smkent/pcb/dev/stackable/power-18650-holder/fab/jlcpcb/power-18650-holder-bom.csv

Comment | Designator | Footprint | LCSC
5K1 | R1,R2 | custom:R_0603_1608Metric_Pad0.98x0.95mm_HandSolder_simple | C25905
JST XH/PH | J1,J2 | custom:Conn_Combo_JST-1x02-XH_PH-THT-pad2gnd
Screw_Terminal_01x02 | J3,J4 | custom:Conn_Combo_TerminalBlock_P3.5-P5.08_1x02_pad2gnd
Battery_Cell | BT1 | custom:BAT-TH_18650-A5BJ001_large_vias
Red | LED1,LED2 | custom:LED_0603_1608Metric_Pad1.05x0.95mm_HandSolder_simple | C2286
