smkent/pcb/pcb/jigs/level-shifter/fab/jlcpcb/level-shifter-bom.csv

Comment | Designator | Footprint | LCSC
Pin headers | J1,J2 | custom:PinHeader_1x06_P2.54mm_Vertical_simple_pad1gnd
2N7002DW | Q1,Q2 | custom:SOT-363_SC-70-6_simple | C5190214
100R | RN3 | Resistor_SMD:R_Array_Convex_4x0603
10K | RN1,RN2 | Resistor_SMD:R_Array_Convex_4x0603
22u | C1,C2 | custom:C_0603_1608Metric_Pad1.08x0.95mm_HandSolder
