smkent/pcb/pcb/jigs/neopixel-micro/fab/jlcpcb/neopixel-micro-bom.csv

Comment | Designator | Footprint | LCSC
10u | C1,C2 | custom:C_0603_1608Metric_Pad1.08x0.95mm_HandSolder
Conn_01x01 | J3,J4 | custom:PinHeader_1x01_P2.54mm_simple
WS2812B-2020 | LED1,LED2,LED3,LED4,LED5,LED6,LED7,LED8 | lcsc:LED-SMD_4P-L2.0-W2.0-BR-1
WS2812B | D1,D2 | custom:LED_WS2812B_PLCC4_5.0x5.0mm_P3.2mm_simple_small_courtyard
Conn_01x02 | J1,J2 | custom:PinHeader_1x02_P2.54mm_Vertical_simple
100R | R1,R2 | Resistor_SMD:R_0603_1608Metric_Pad0.98x0.95mm_HandSolder
