smkent/pcb/pcb/power/microbuck/fab/jlcpcb/microbuck-bom.csv

Comment | Designator | Footprint | LCSC
10K | R0,R1,R3,R4,R6,R7 | Resistor_SMD:R_0603_1608Metric_Pad0.98x0.95mm_HandSolder
0u1 | C3,C6,C7,C10 | custom:C_0603_1608Metric_Pad1.08x0.95mm_HandSolder
TPS563200 | U1,U2 | custom:SOT-23-6_Handsoldering_simple
LED_Small | LED1,LED2 | custom:LED_0603_1608Metric_Pad1.05x0.95mm_HandSolder_simple
56K | R2,R5 | Resistor_SMD:R_0603_1608Metric_Pad0.98x0.95mm_HandSolder
22u | C8,C9,C11,C12 | custom:C_0603_1608Metric_Pad1.08x0.95mm_HandSolder
Pin headers | J1,J2 | custom:PinHeader_1x04_P2.54mm_Vertical_simple_pad3,4gnd
4u7 | L1,L2 | lcsc:IND-SMD_L2.5-W2.0_MHCHL2520
10u | C1,C2,C4,C5 | custom:C_0603_1608Metric_Pad1.08x0.95mm_HandSolder
