smkent/pcb/pcb/stackable3/esp-doorbell-dev/fab/esp-doorbell-dev-schematic.pdf

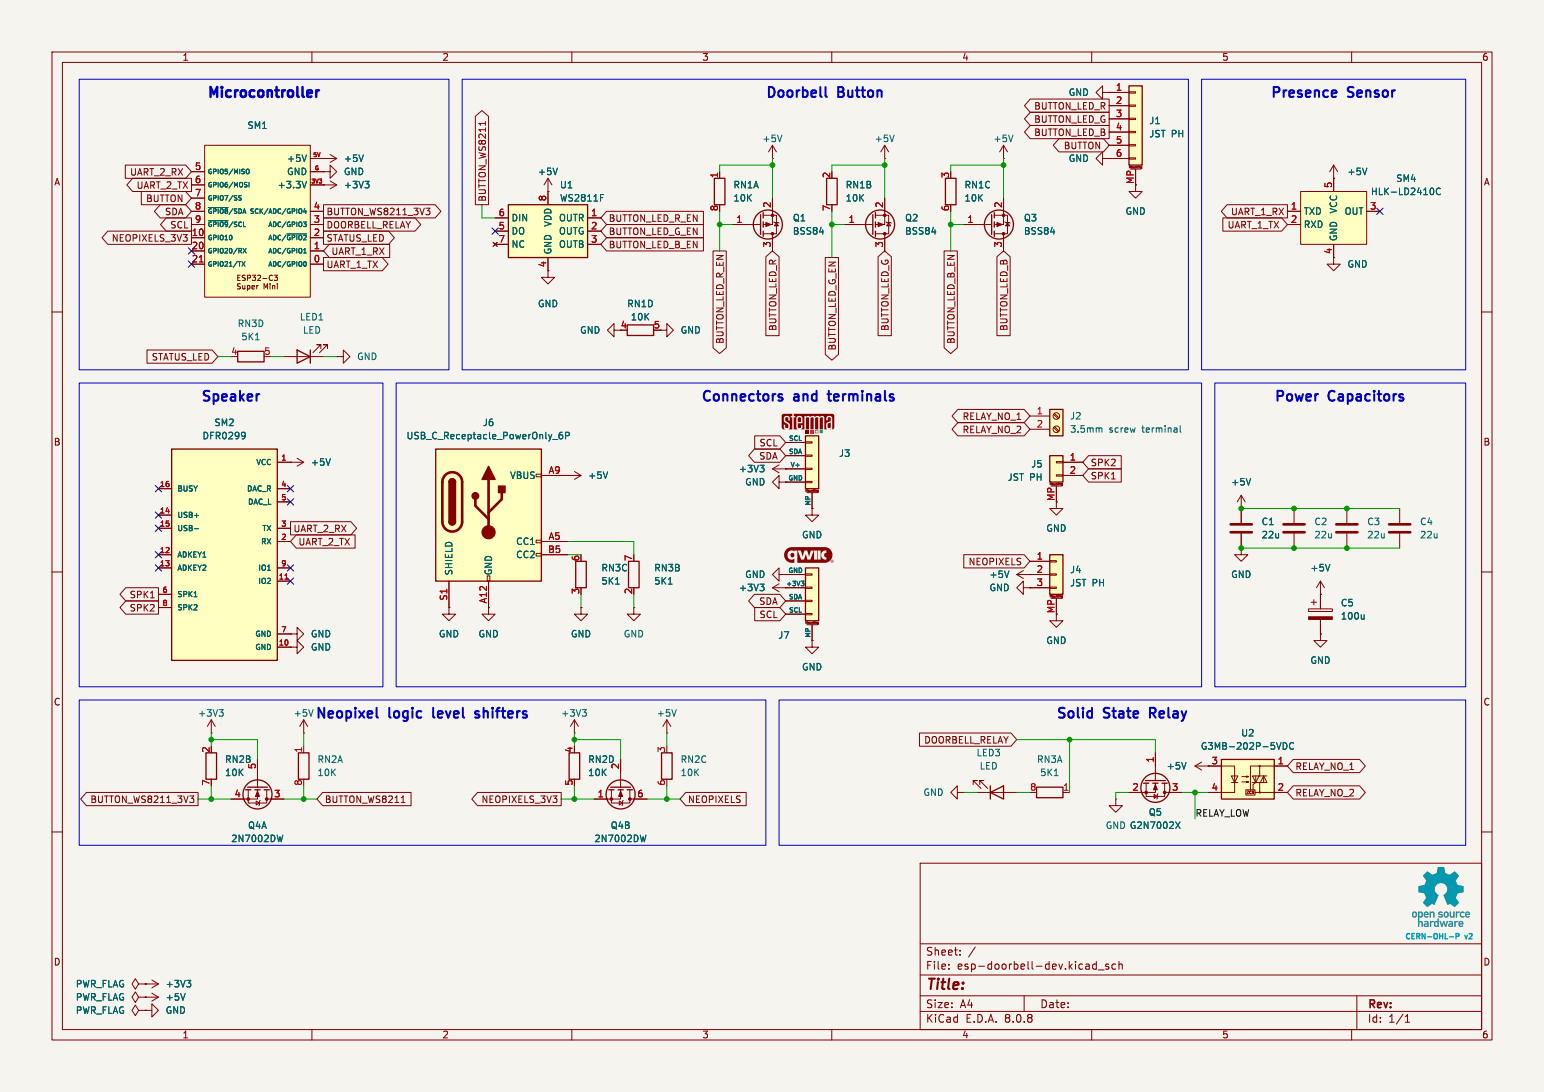
[picture p19: page 1]

4 DO 5 DIN 6 NC 7 VDD

2 3 Q2 BSS84 TXD 1 RXD 2 OUT 3 GND

3.5mm screw terminal Mounting SCL SDA
SCL SDA
+3V3 GND
