smkent/pcb/pcb/stackable3/power-selector-dev/fab/power-selector-dev-schematic.pdf

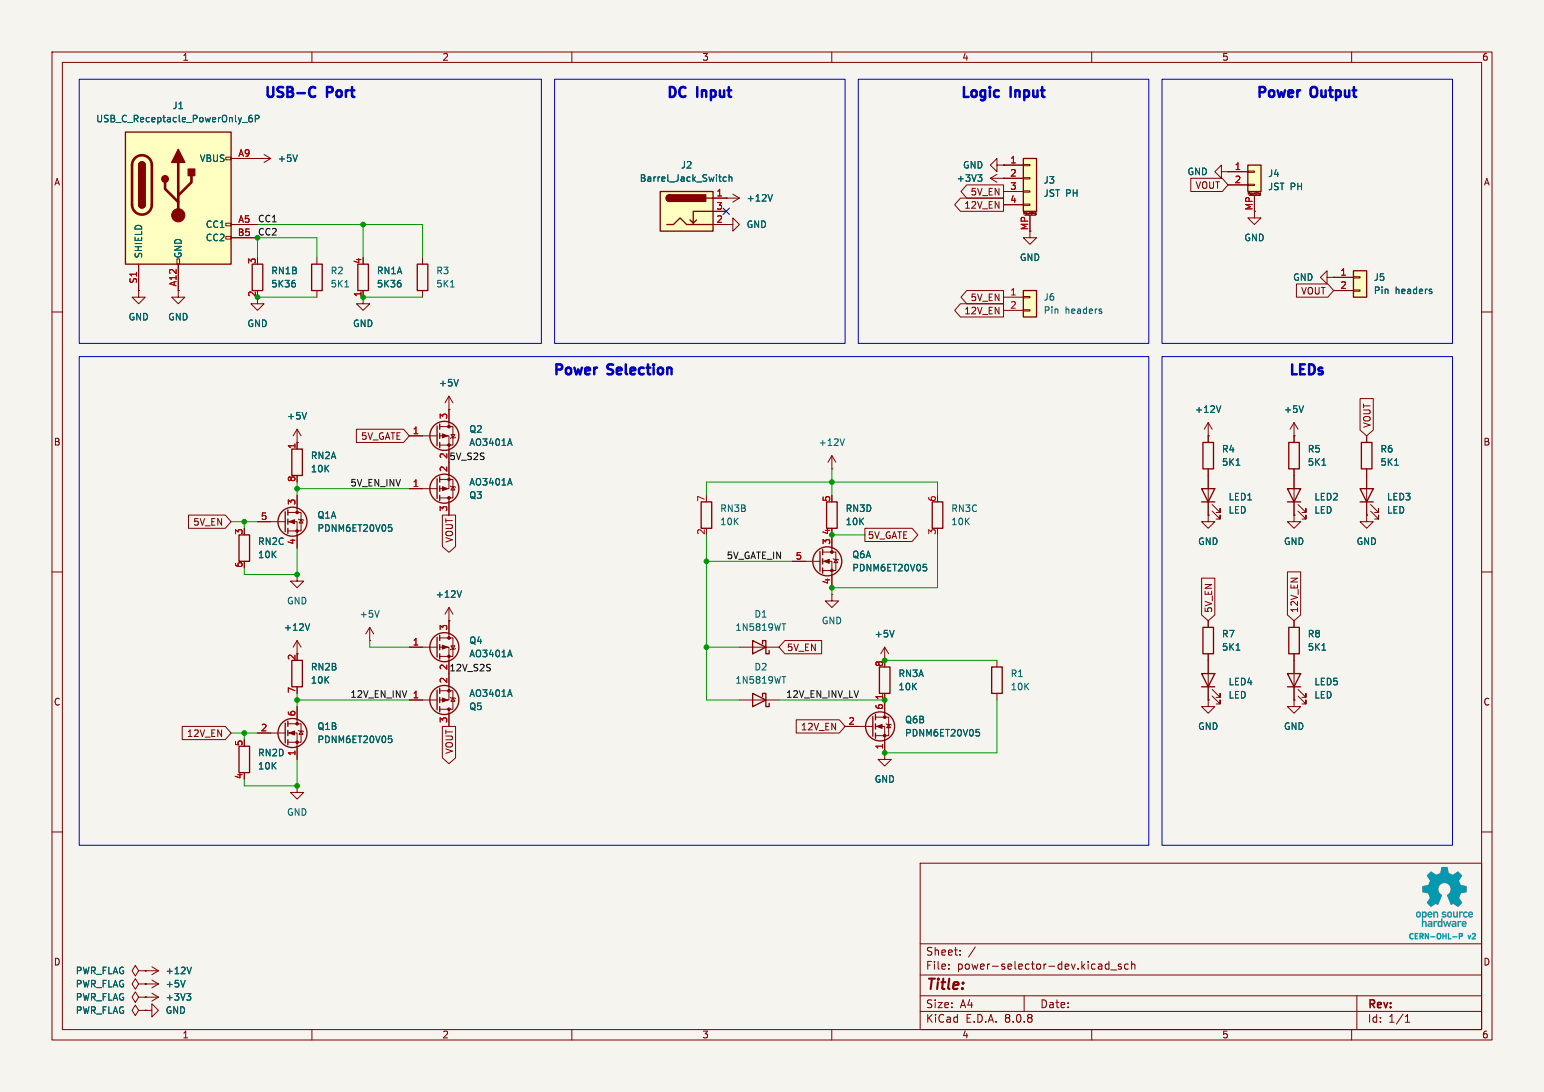
[picture p20: page 1]

Id: 1/1 Title: File: power-selector-dev.kicad_sch Sheet: /
