smkent/pcb/dev/misc/relay-module-5v/fab/relay-module-5v-schematic.pdf

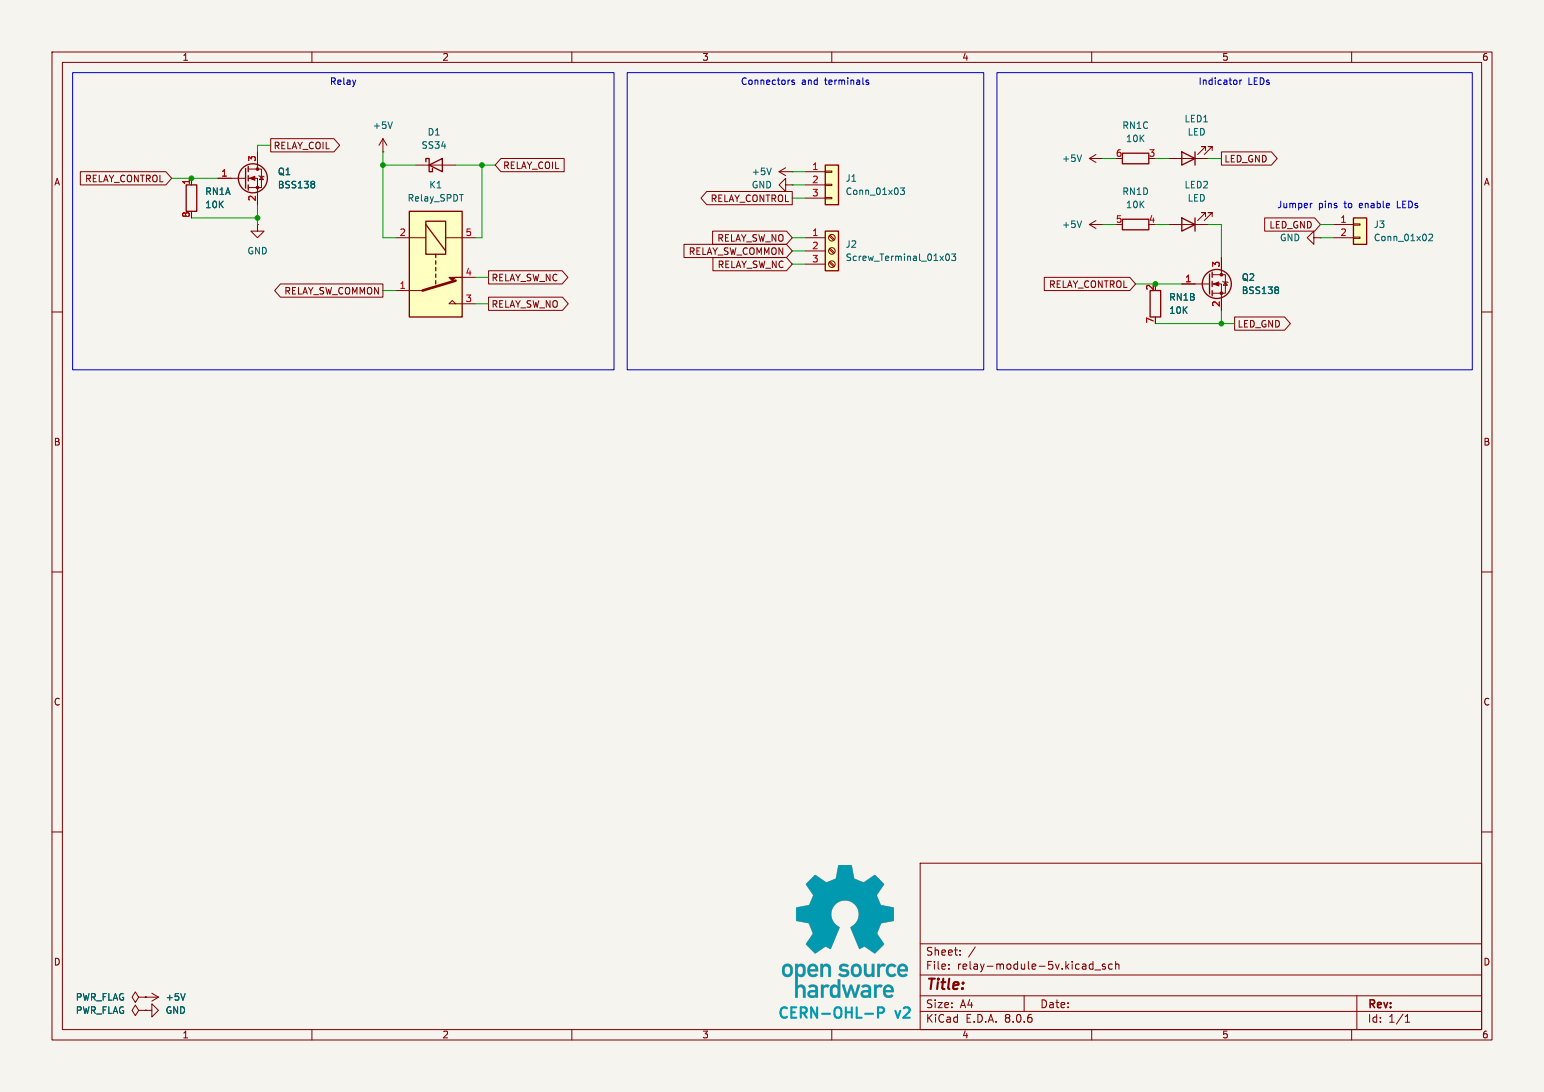
[picture p21: page 1]

Id: 1/1 Title: File: relay-module-5v.kicad_sch Sheet: /
