smkent/pcb/dev/power/battery-eta9740/fab/battery-eta9740-schematic.pdf

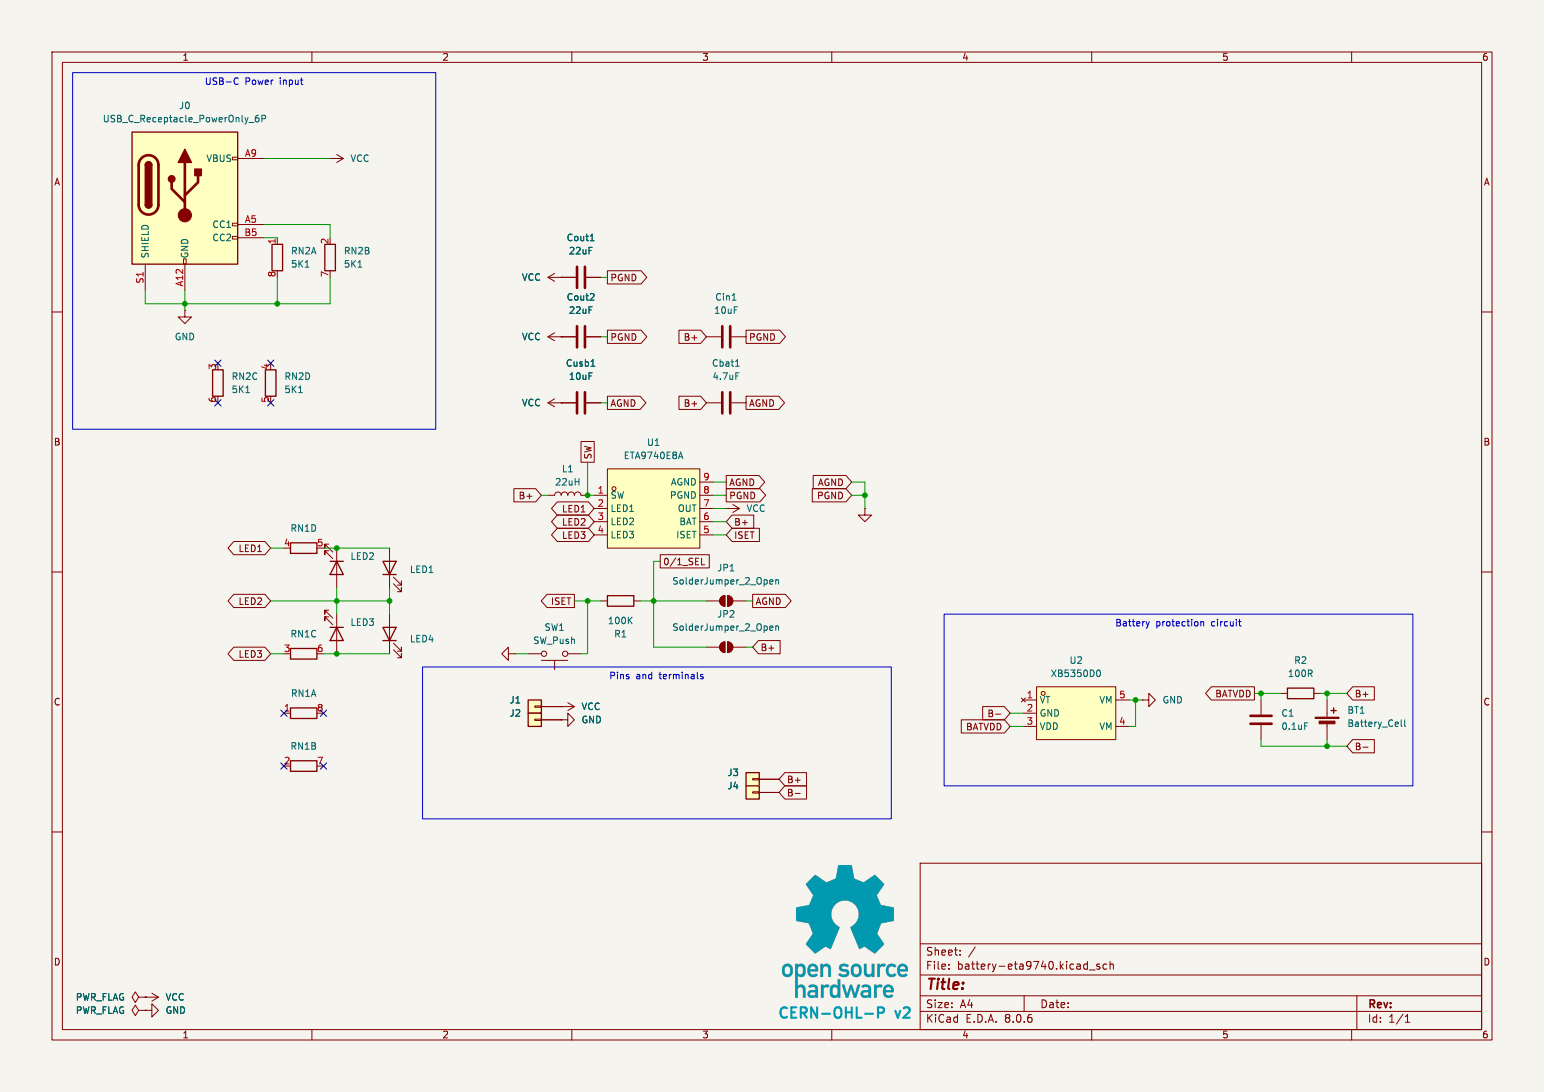
[picture p22: page 1]

Id: 1/1 Title: File: battery-eta9740.kicad_sch Sheet: / PWR_FLAG
