smkent/pcb/dev/power/battery-tp5400/fab/battery-tp5400-schematic.pdf

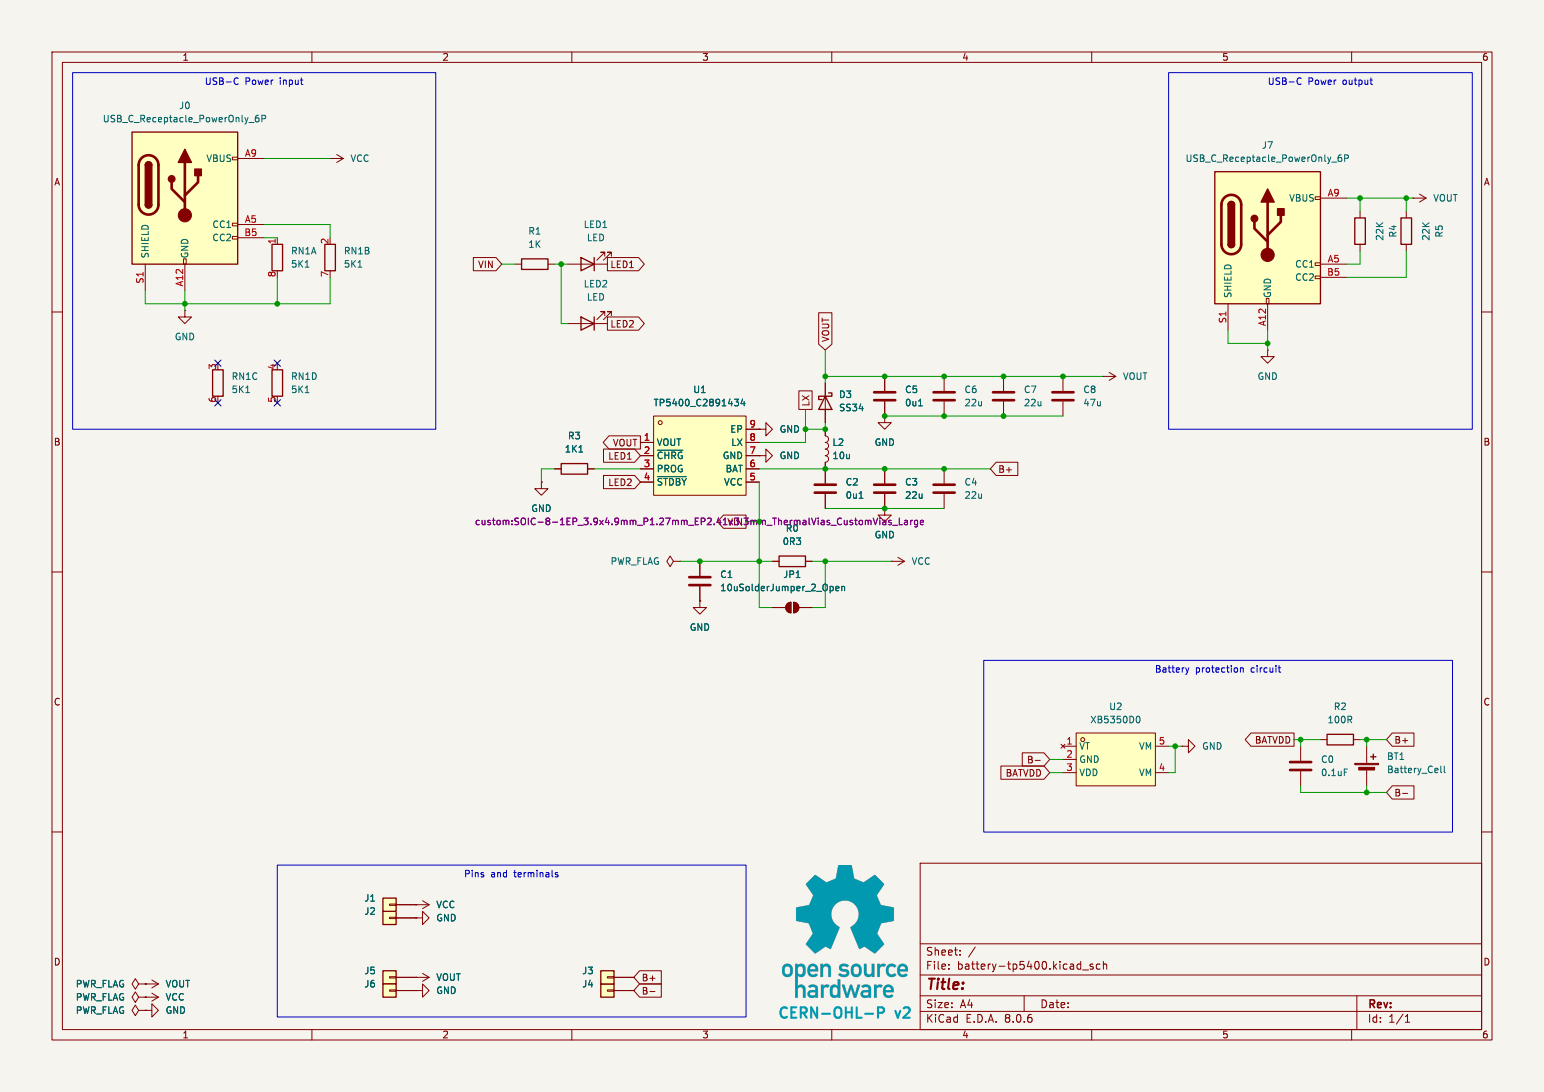
[picture p23: page 1]

Id: 1/1 Title: File: battery-tp5400.kicad_sch Sheet: /
