smkent/pcb/dev/power/boost-mt3608/fab/boost-mt3608-schematic.pdf

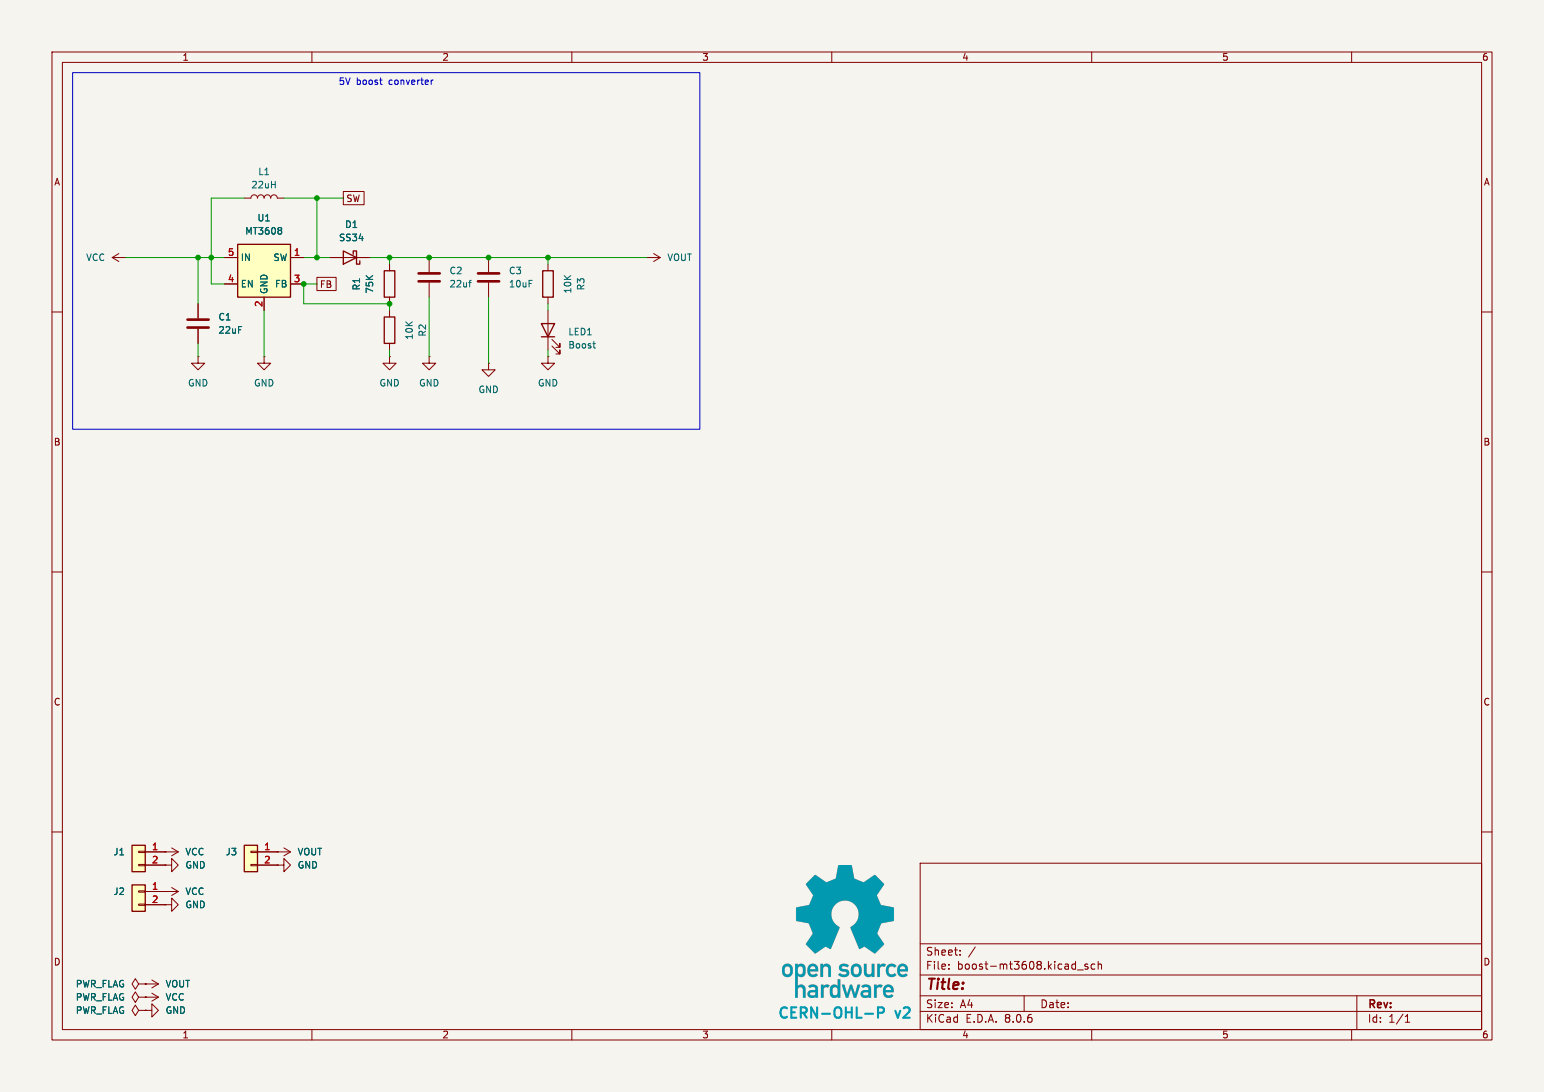
[picture p24: page 1]

Id: 1/1 Title: File: boost-mt3608.kicad_sch Sheet: / VOUT
