smkent/pcb/dev/power/buck-tps54202-compact/fab/buck-tps54202-compact-schematic.pdf

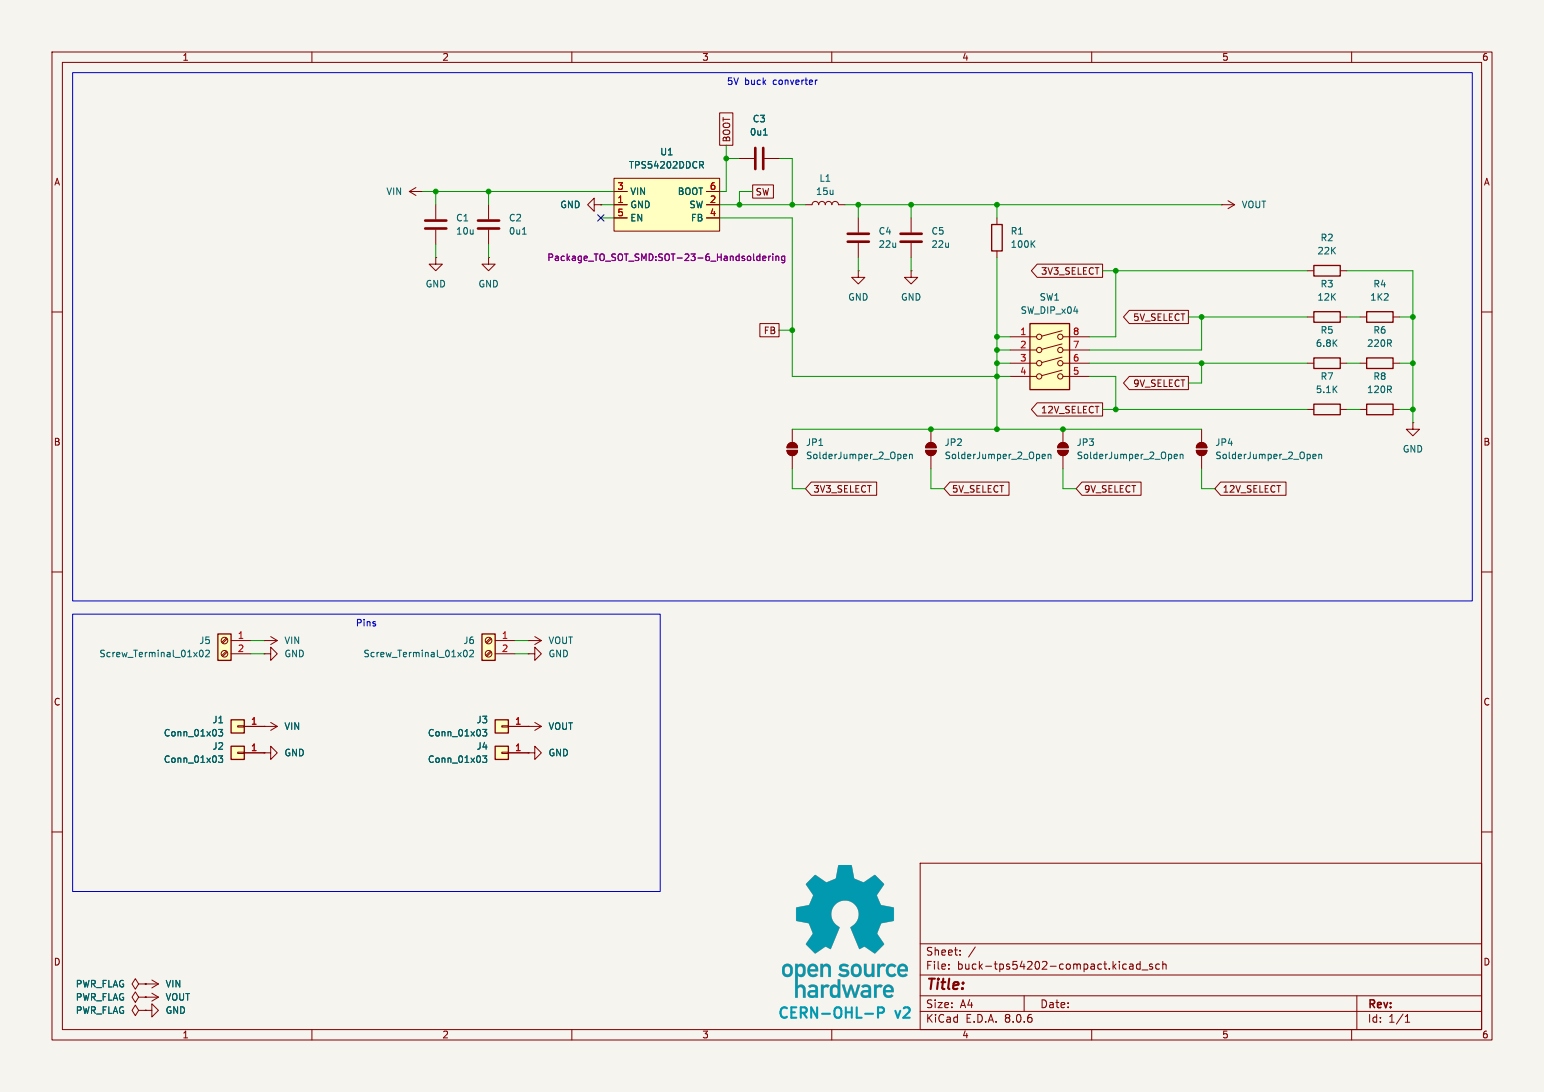
[picture p25: page 1]

Id: 1/1 Title: File: buck-tps54202-compact.kicad_sch Sheet: / GND
