smkent/pcb/dev/power/buck-tps54202/fab/buck-tps54202-schematic.pdf

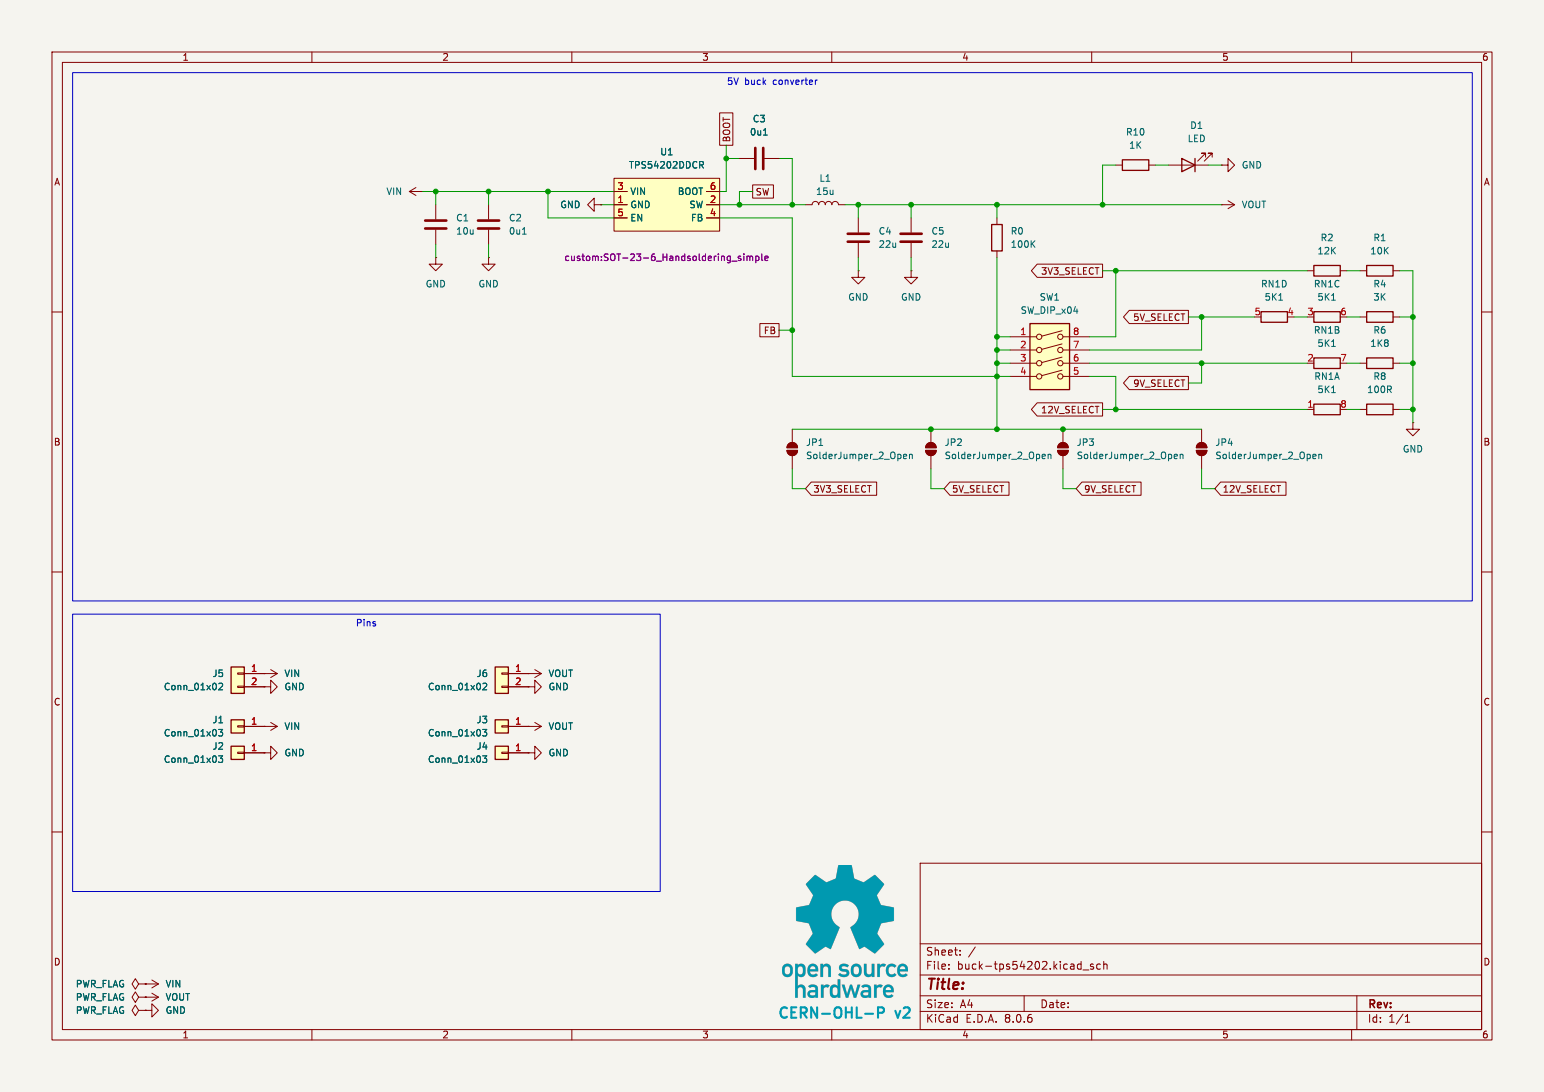
[picture p26: page 1]

Id: 1/1 Title: File: buck-tps54202.kicad_sch Sheet: /
