smkent/pcb/dev/power/ip5209-ups/fab/ip5209-ups-schematic.pdf

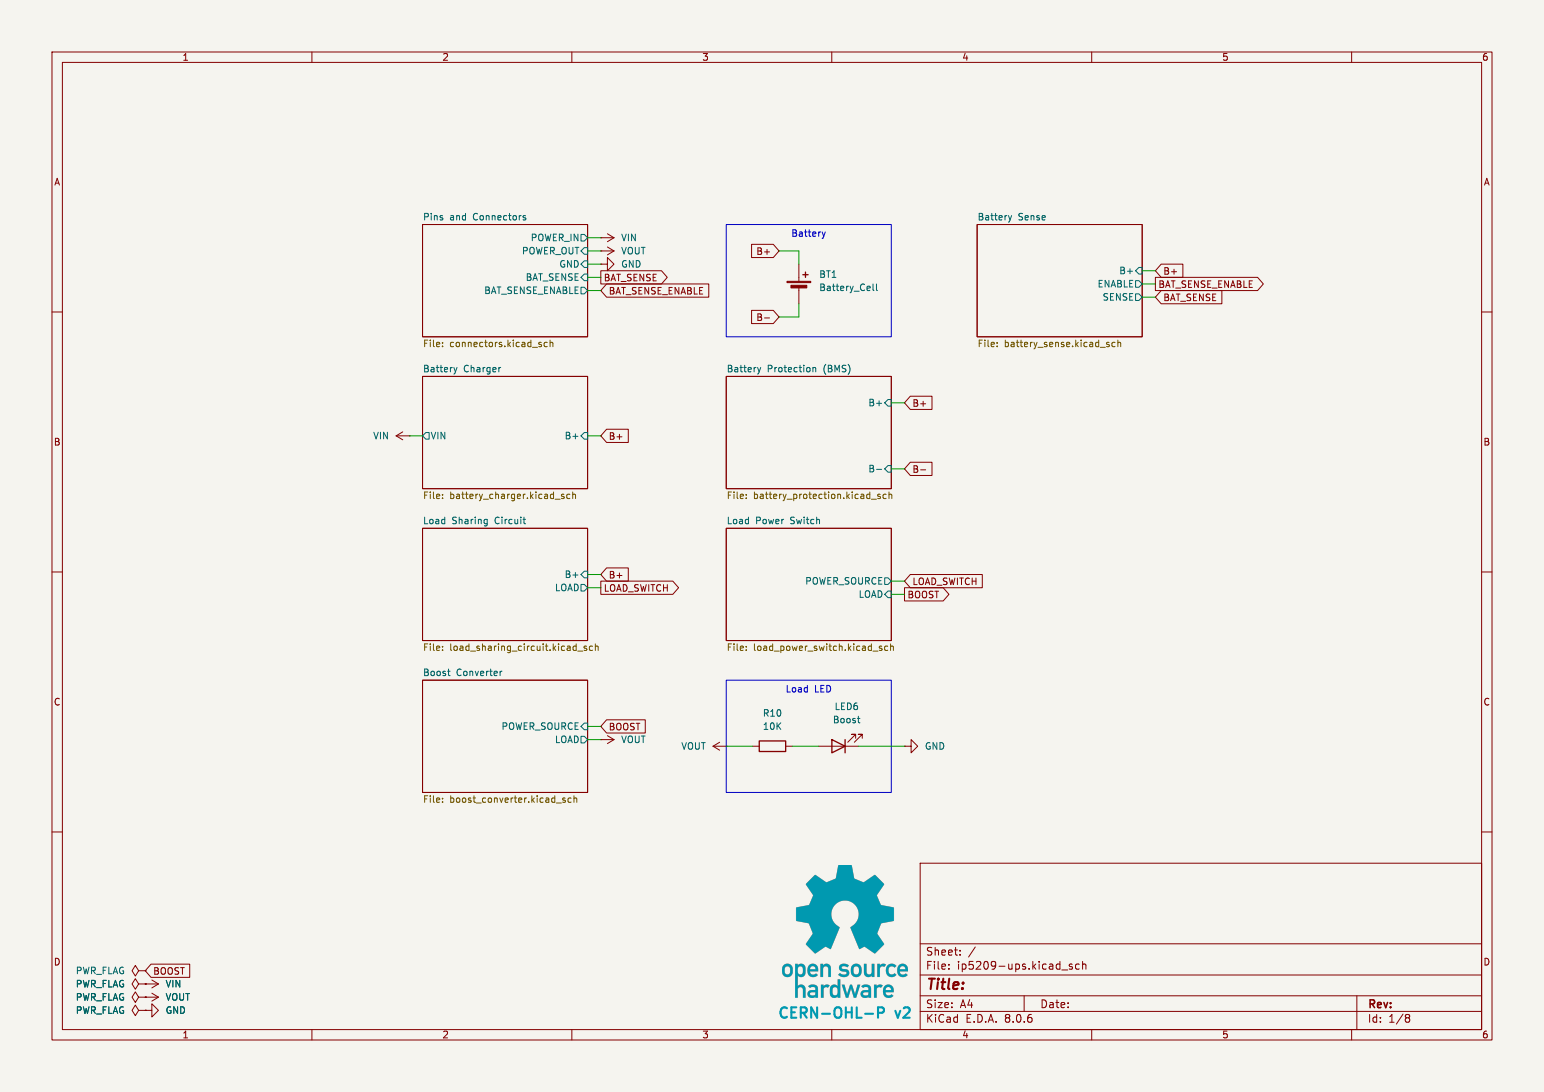
[picture p27: page 1]

Load Sharing Circuit File: load_sharing_circuit.kicad_sch

Id: 1/8 Title: File: ip5209-ups.kicad_sch Sheet: /

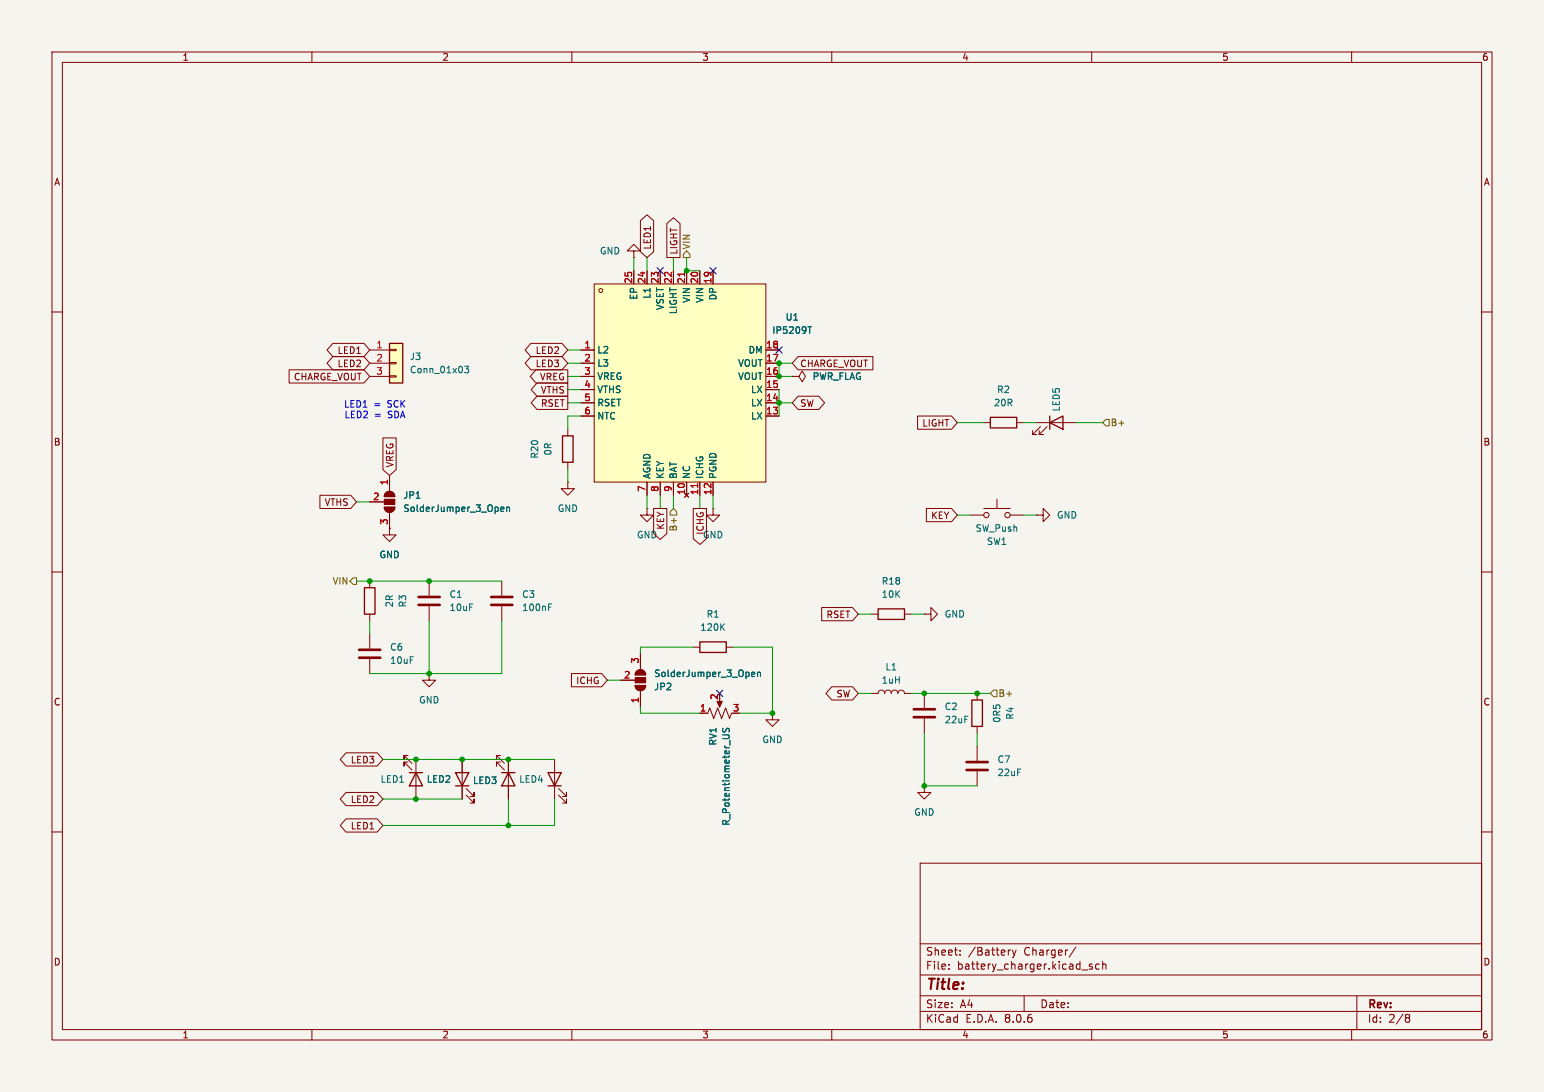
[picture p28: page 2]

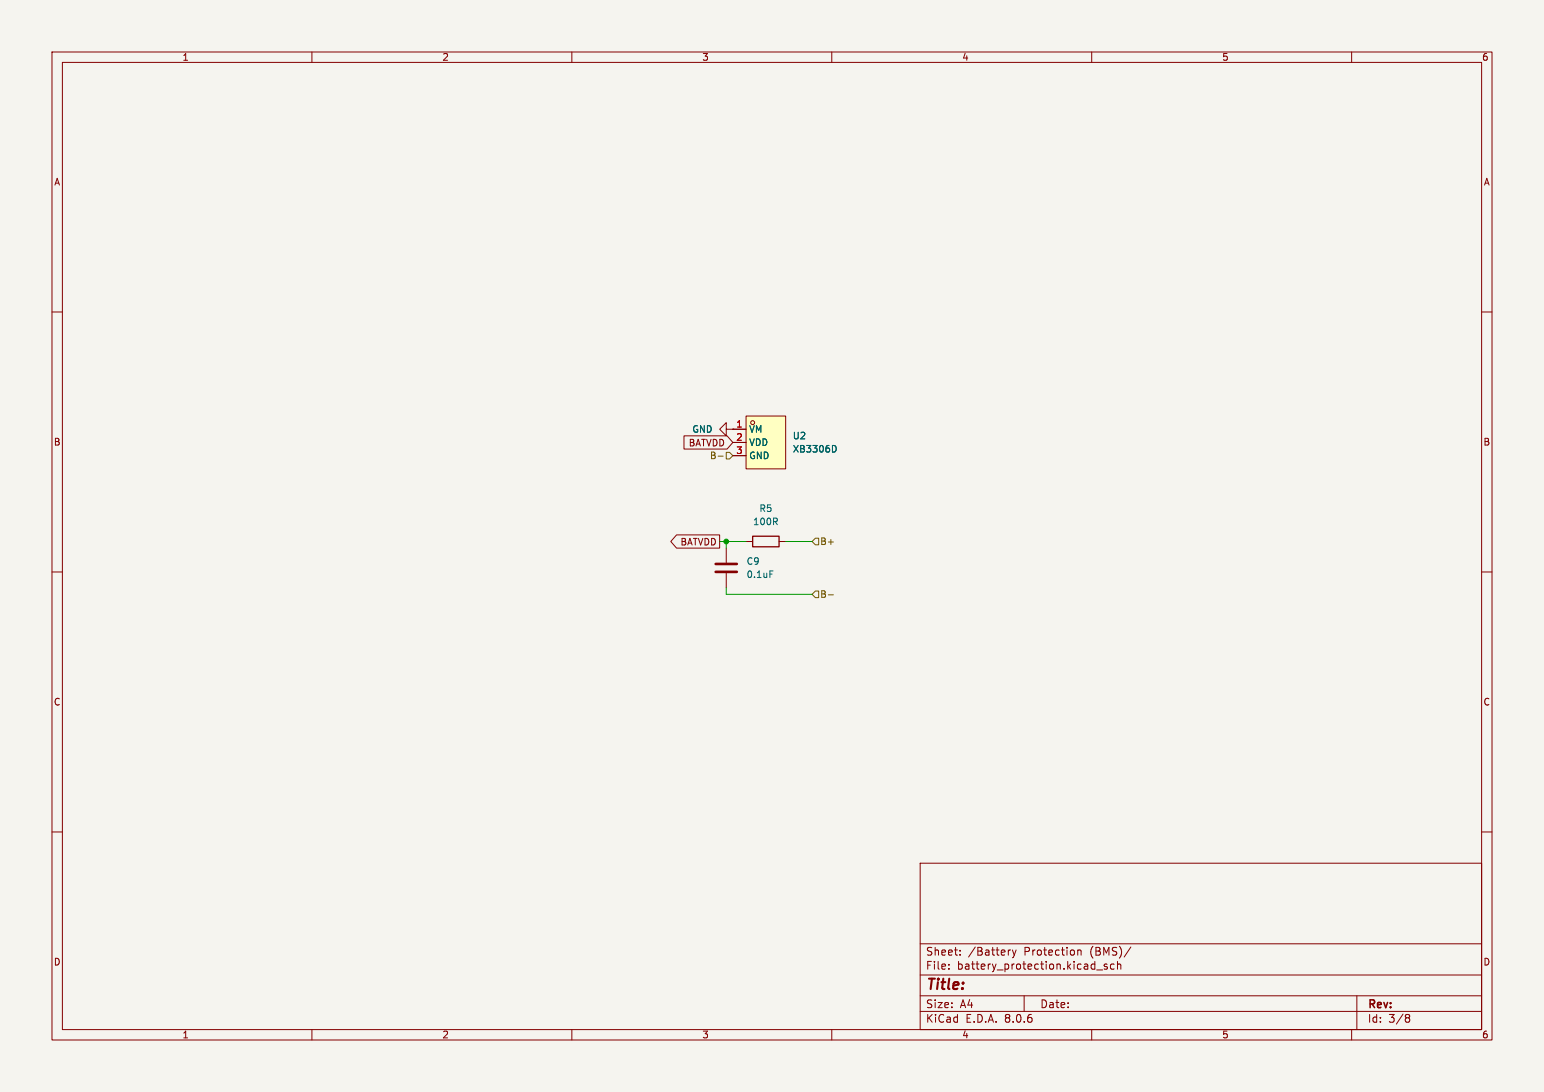
[picture p29: page 3]

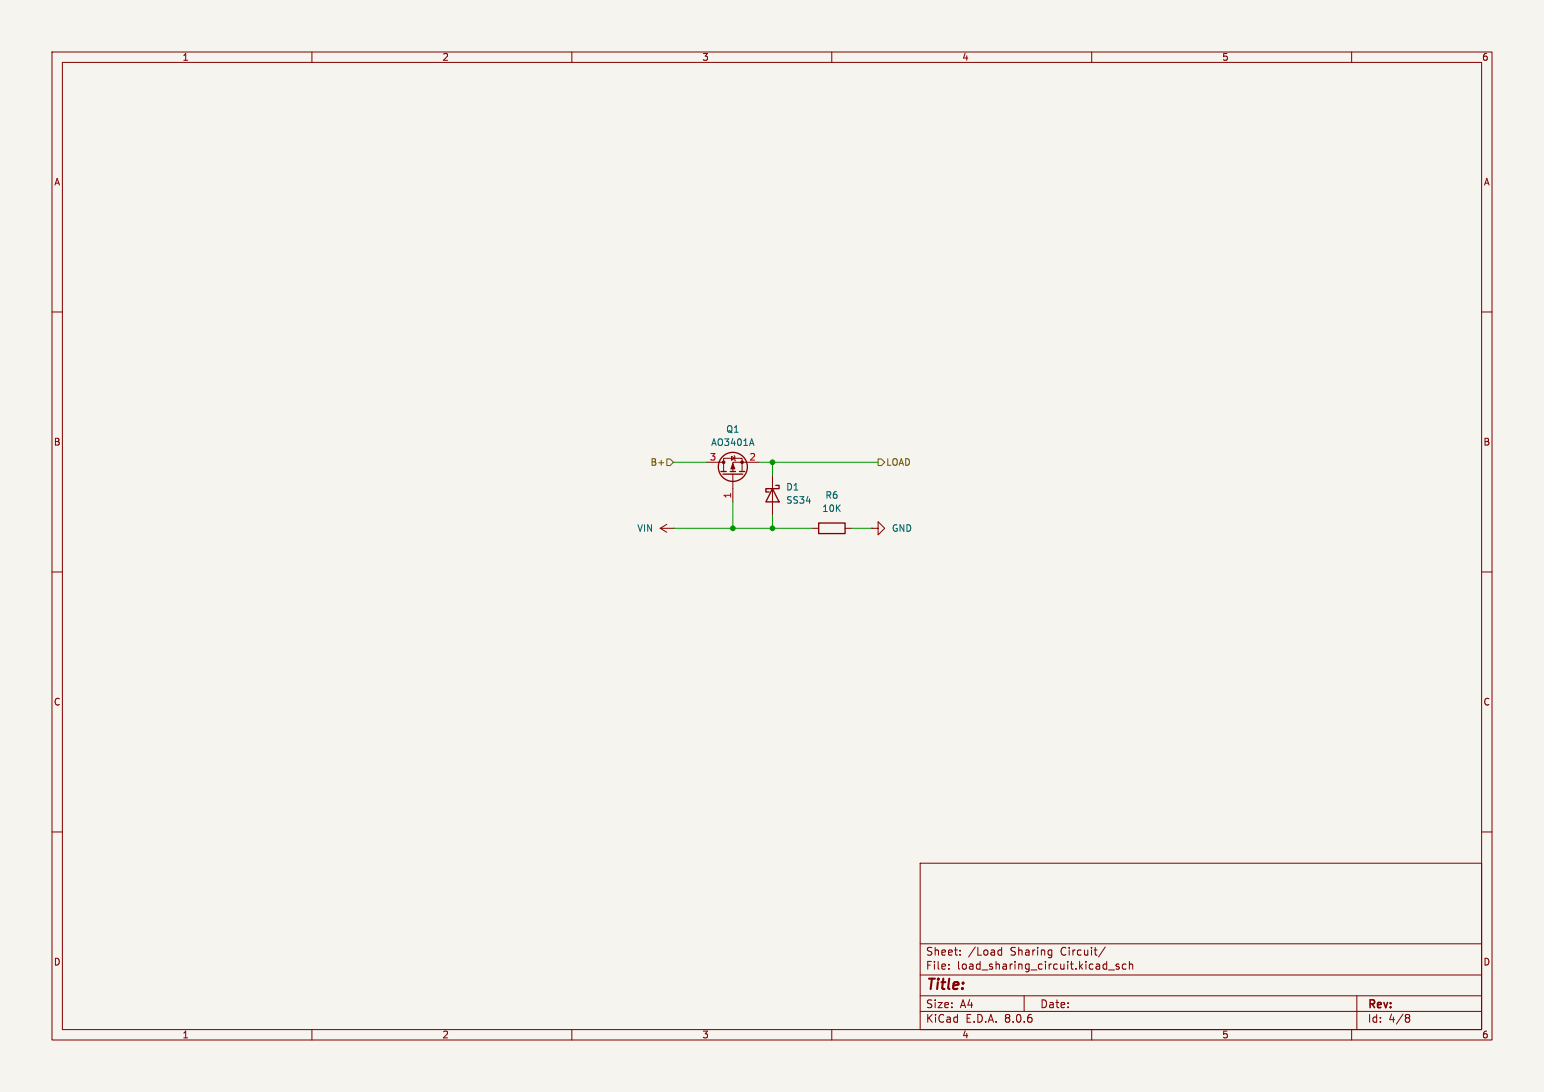
[picture p30: page 4]

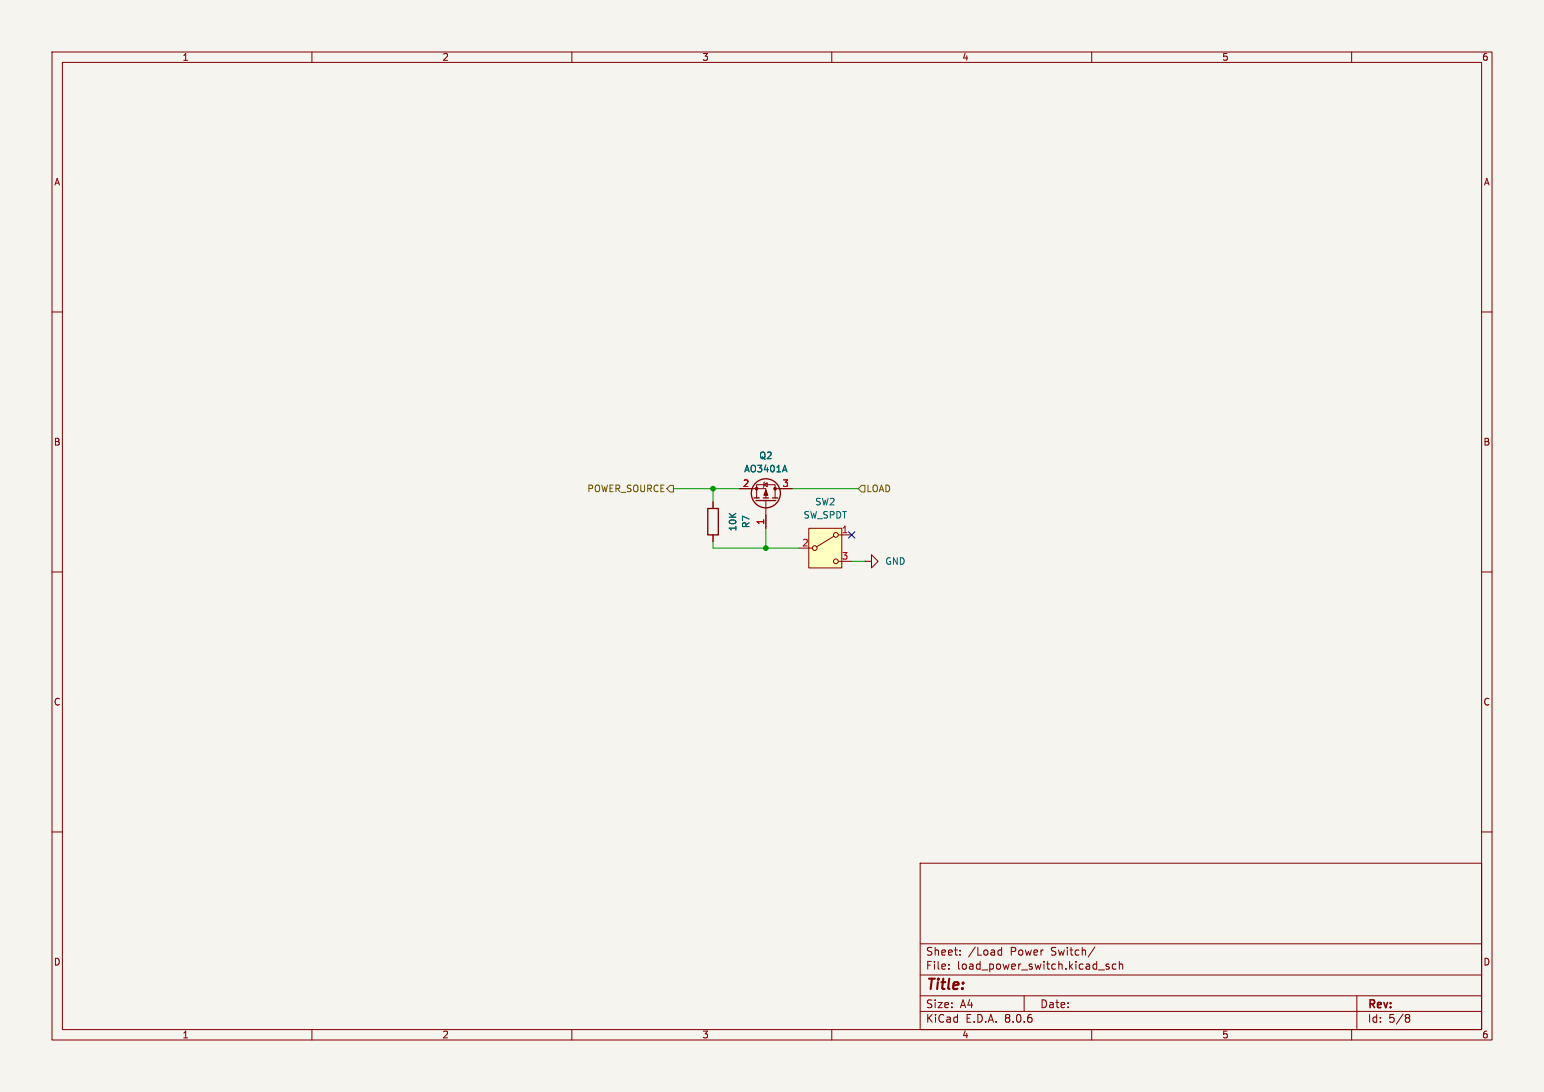
[picture p31: page 5]

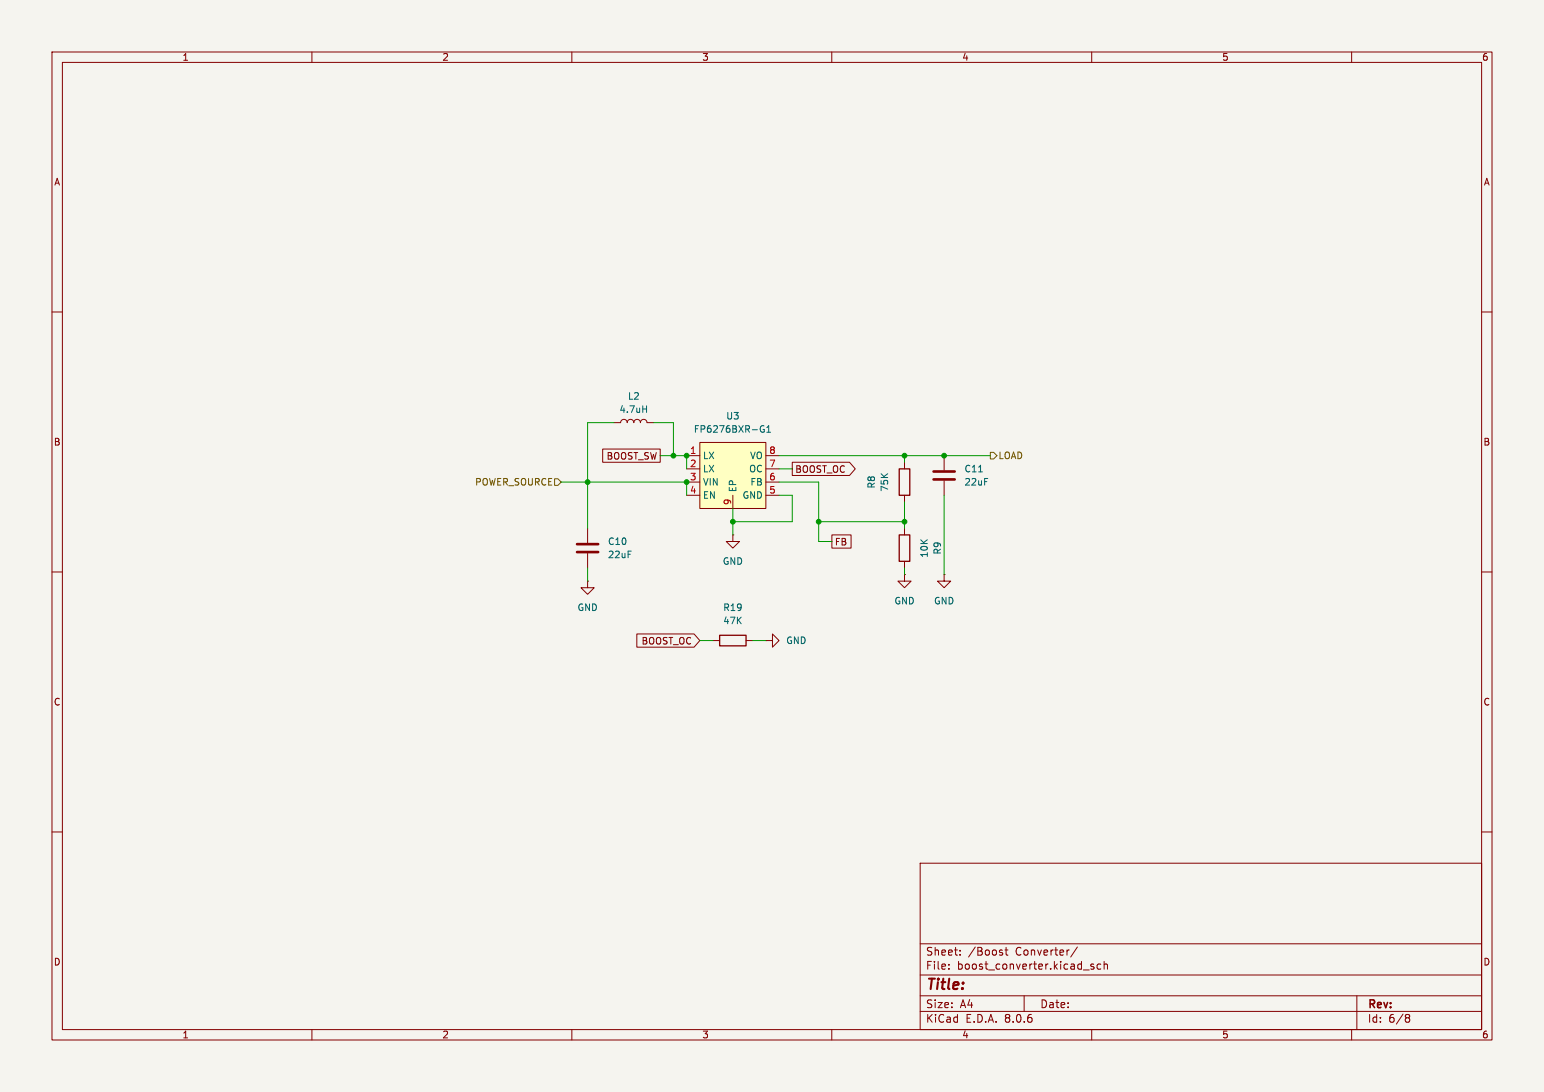
[picture p32: page 6]

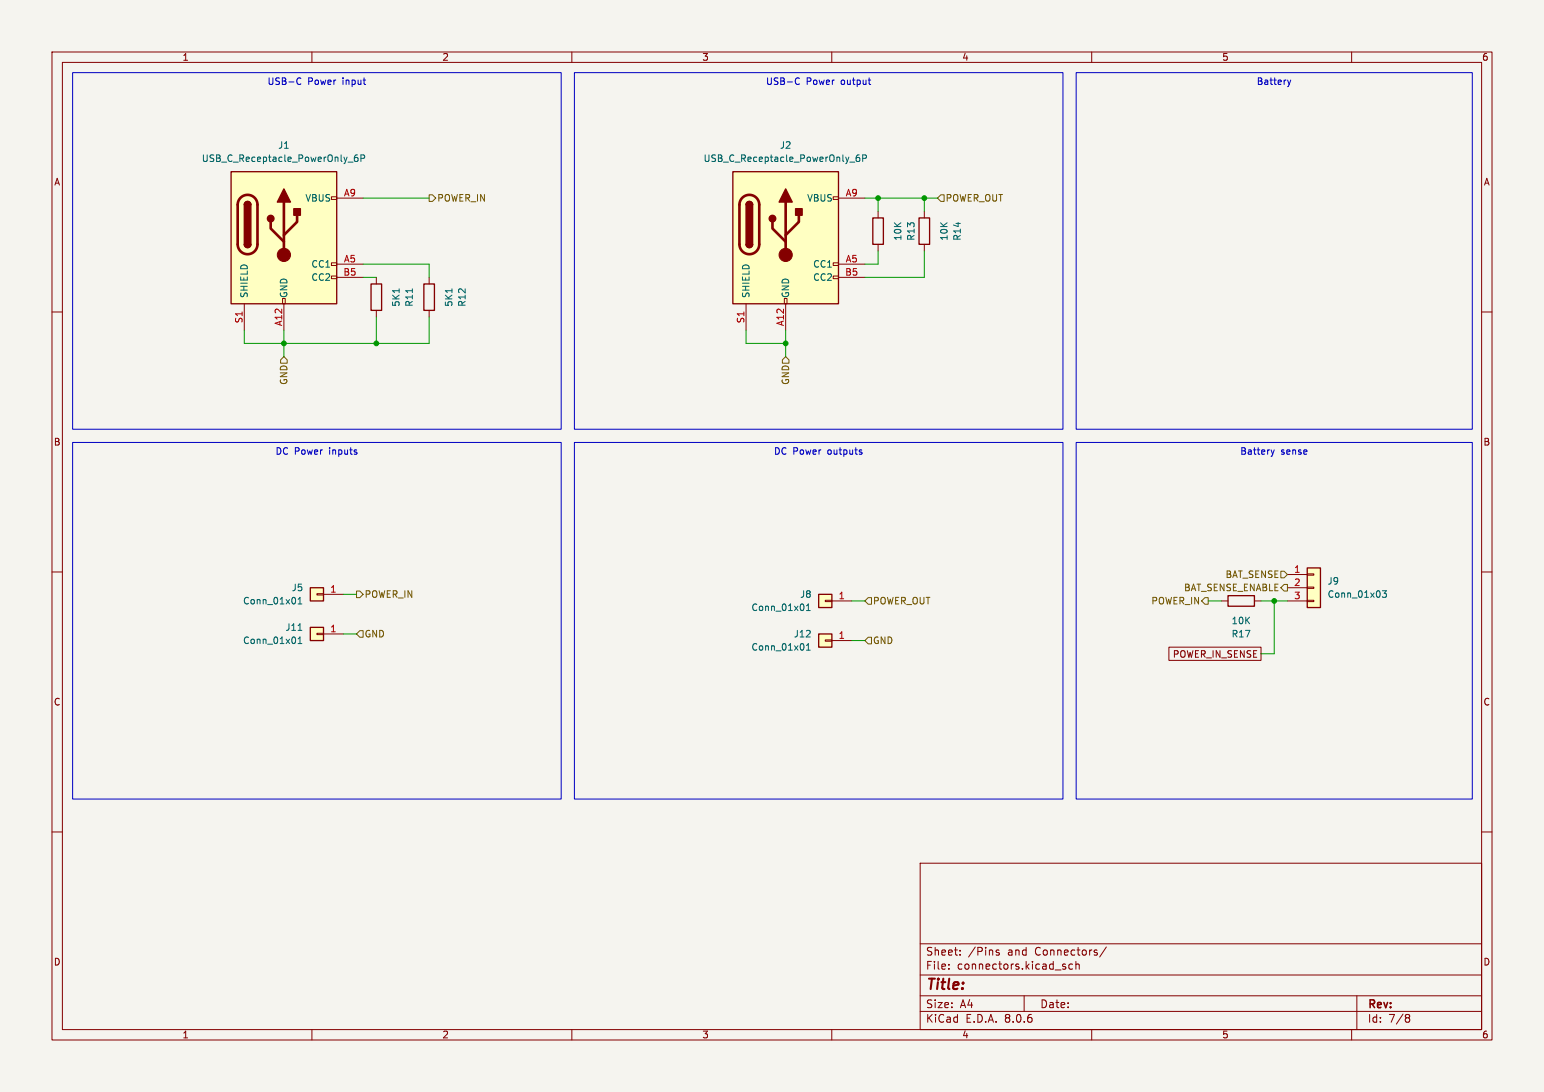
[picture p33: page 7]

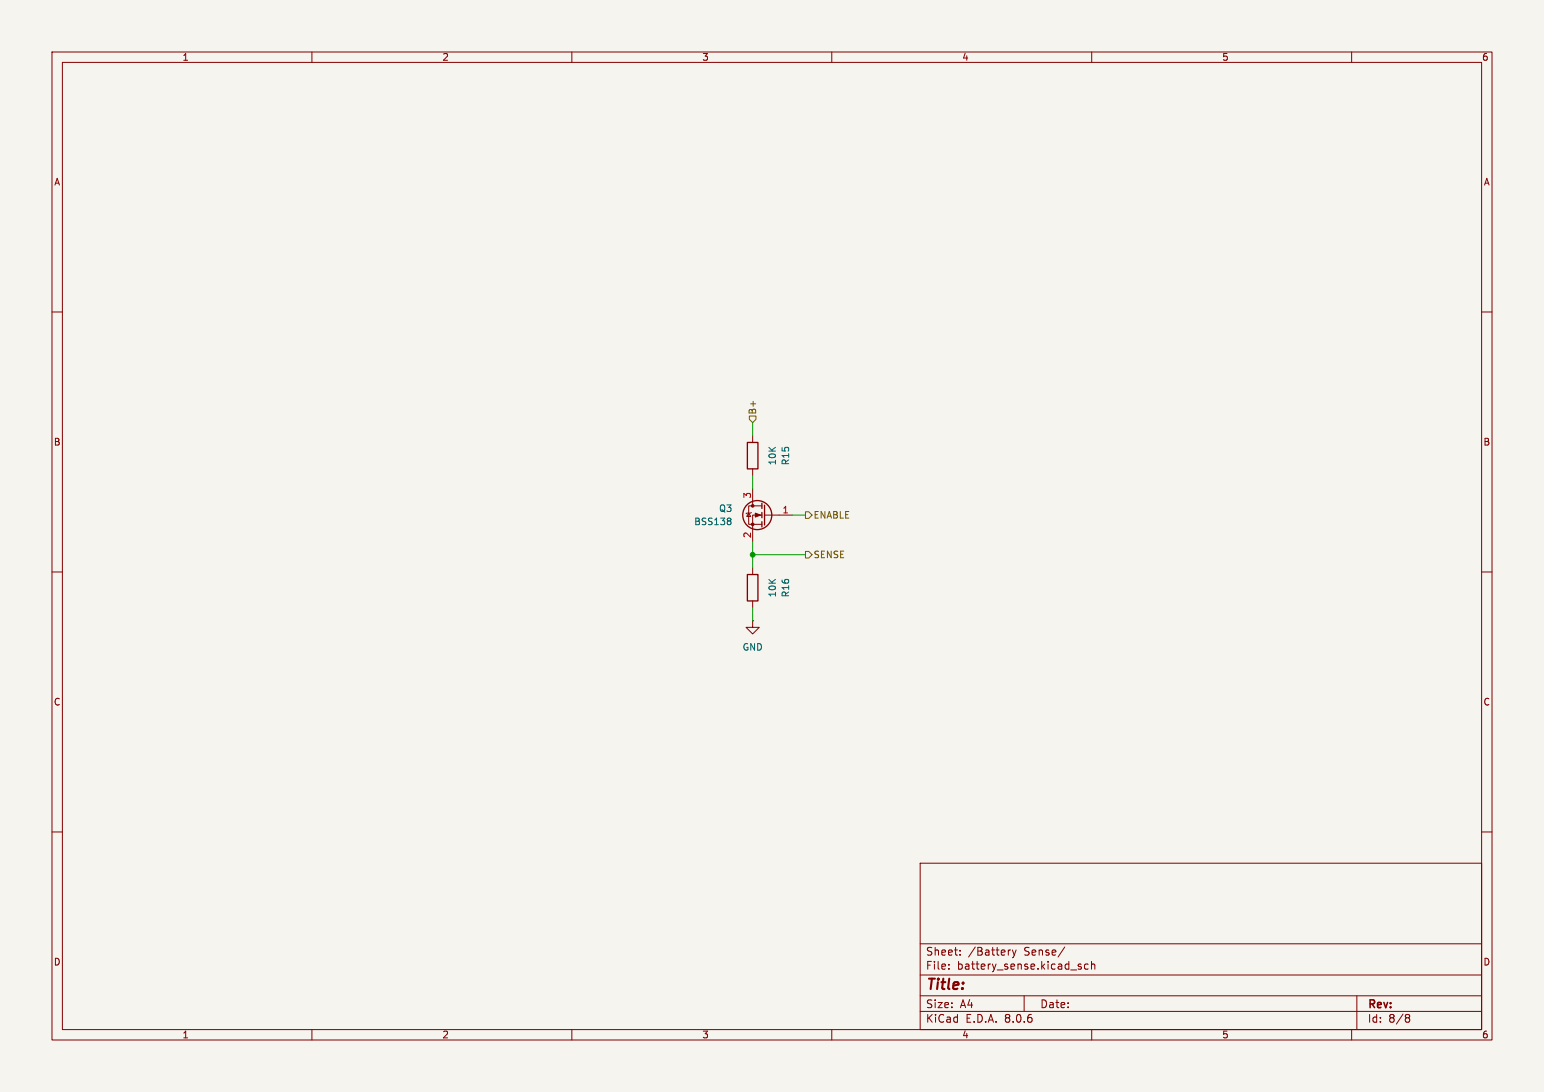
[picture p34: page 8]
