smkent/pcb/dev/power/ip5306-ups/fab/ip5306-ups-schematic.pdf

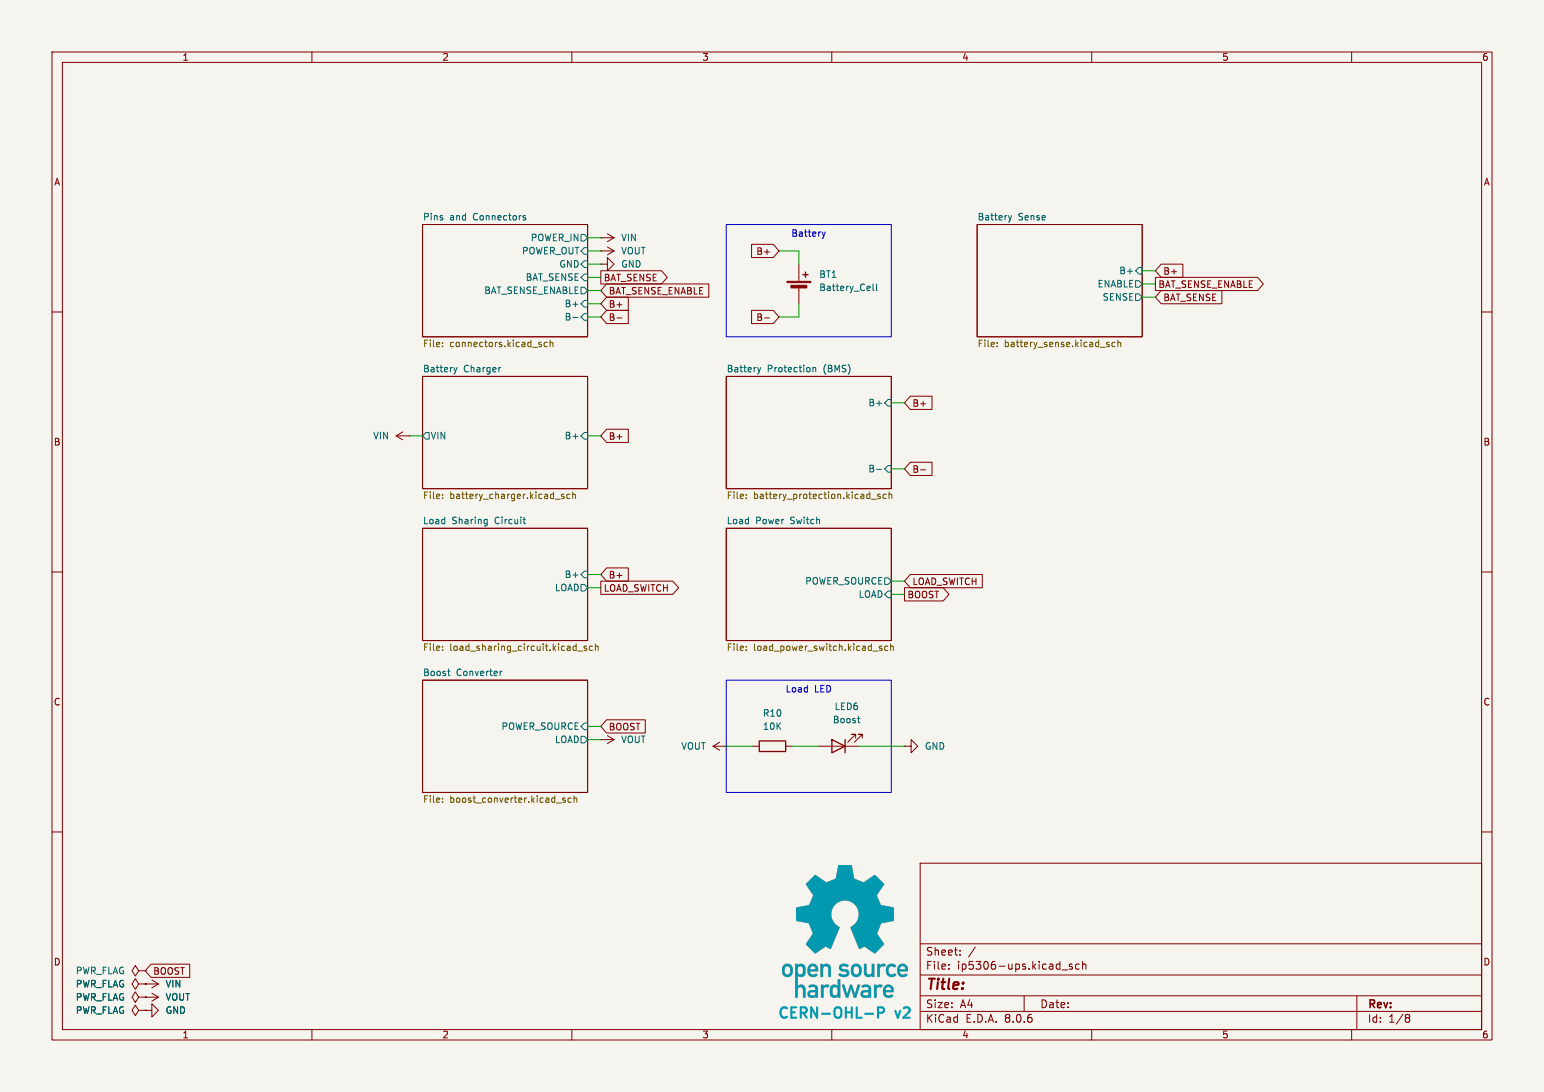
[picture p35: page 1]

Load Power Switch File: load_power_switch.kicad_sch POWER_SOURCE

Id: 1/8 Title: File: ip5306-ups.kicad_sch Sheet: /

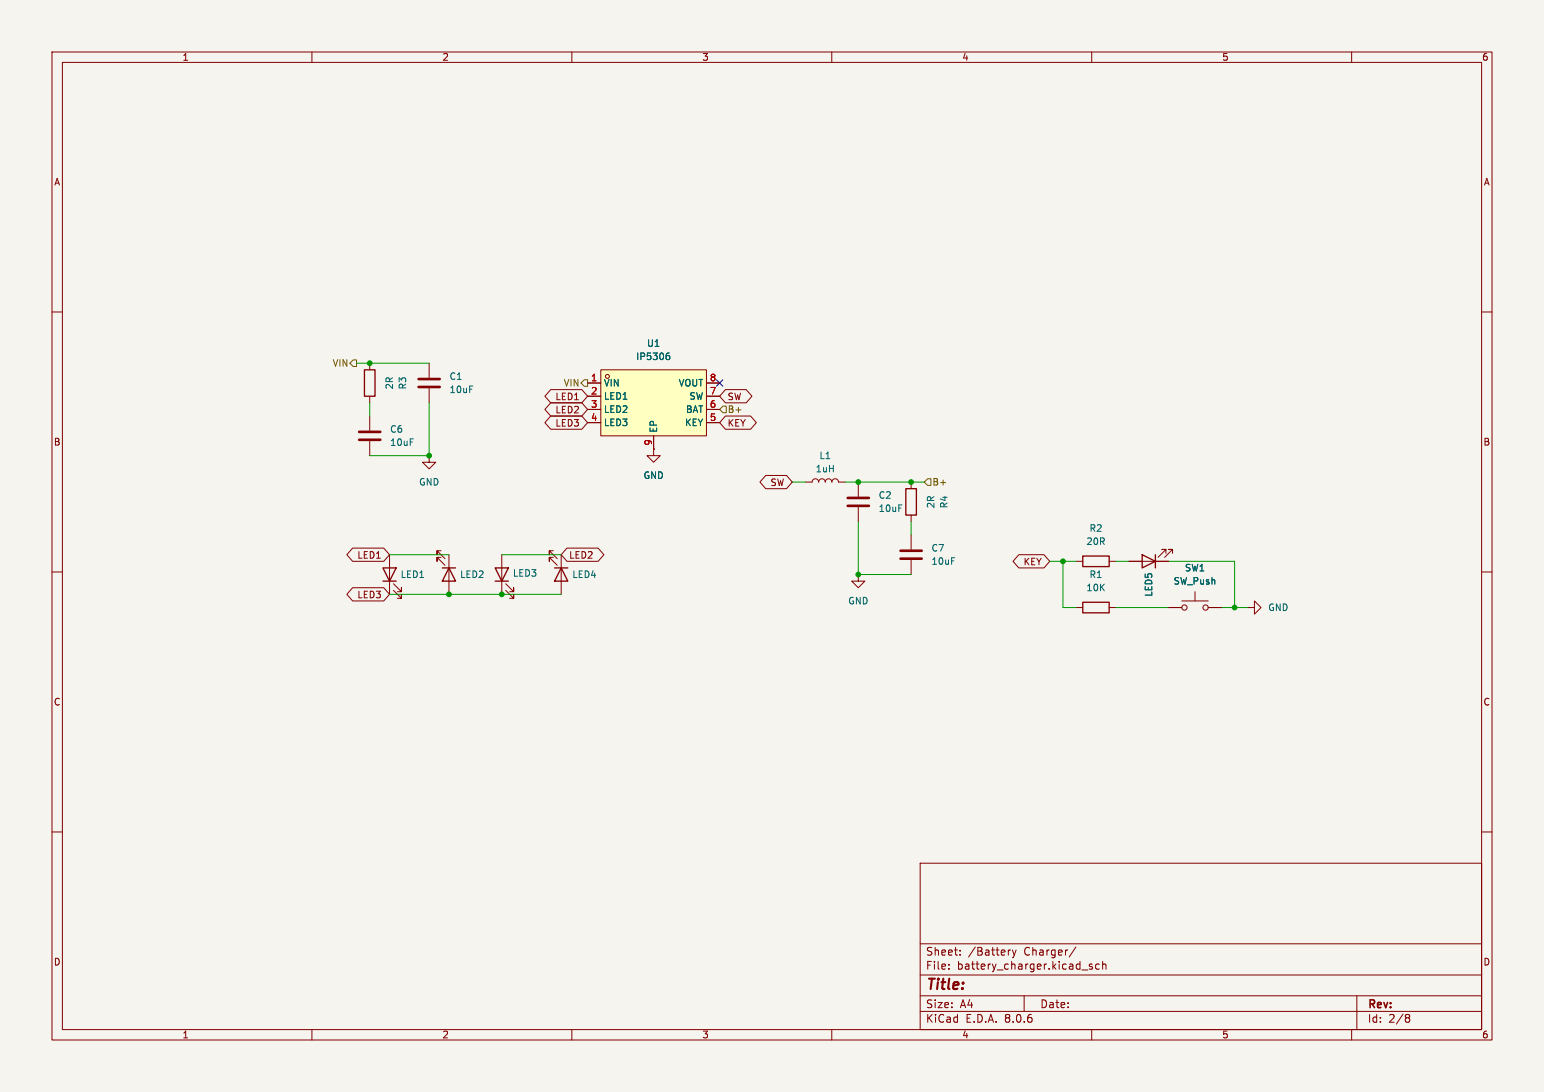
[picture p36: page 2]

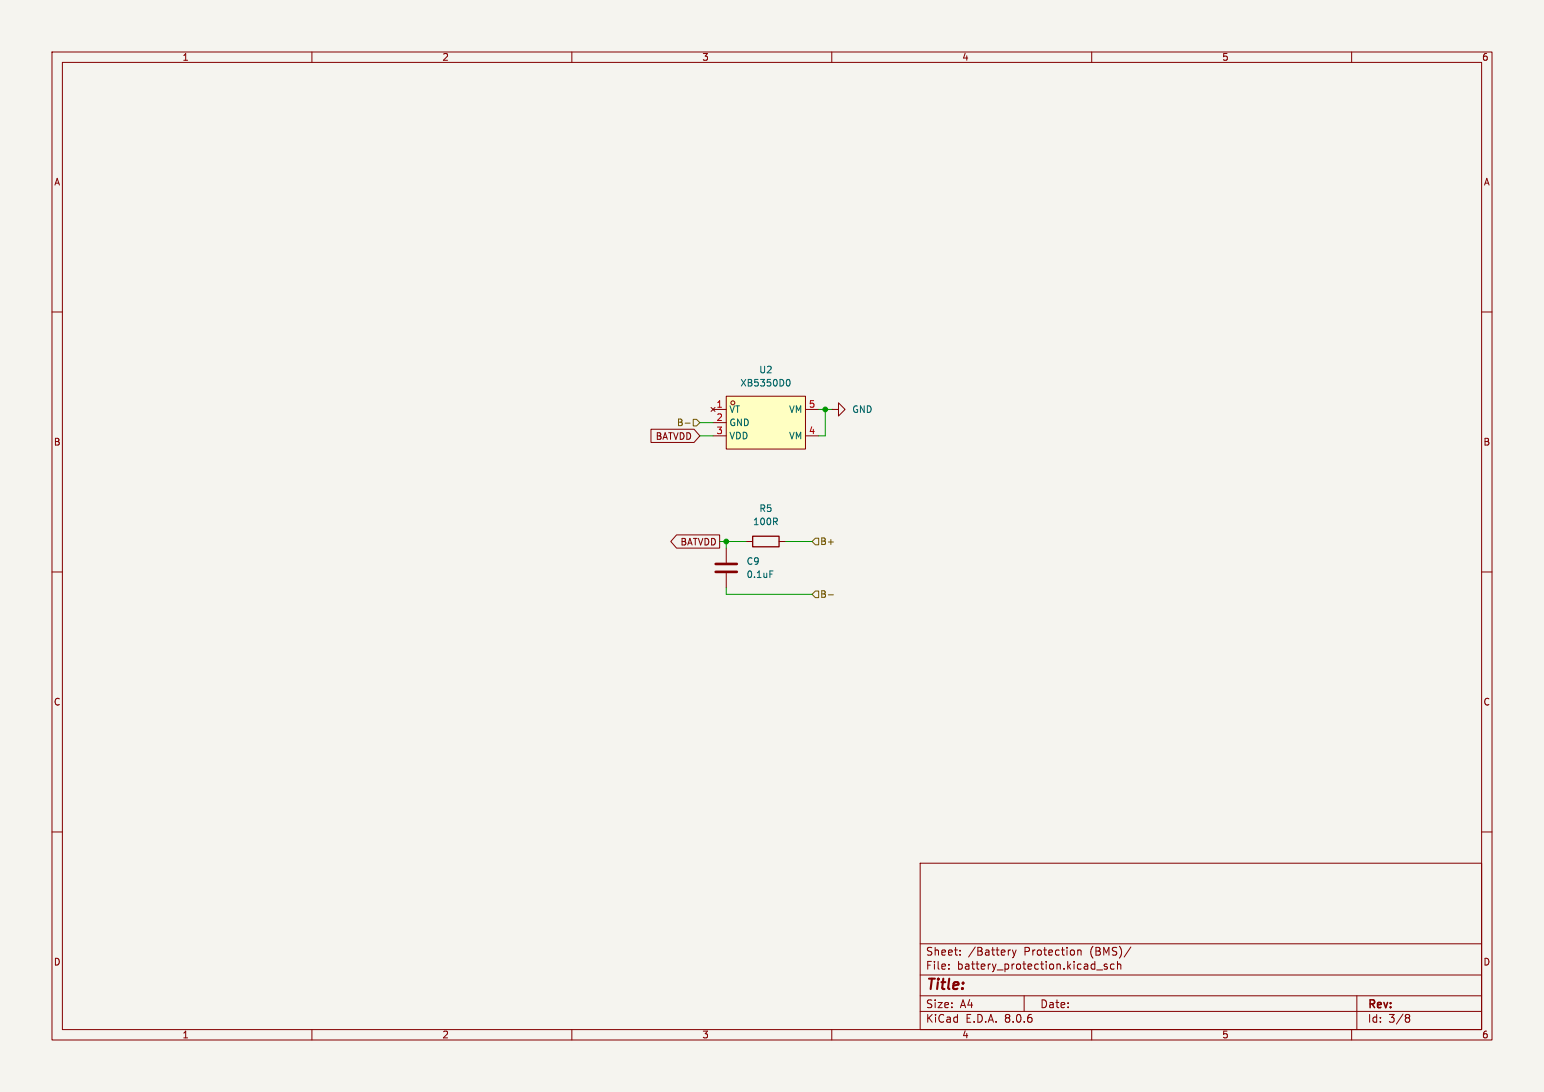
[picture p37: page 3]



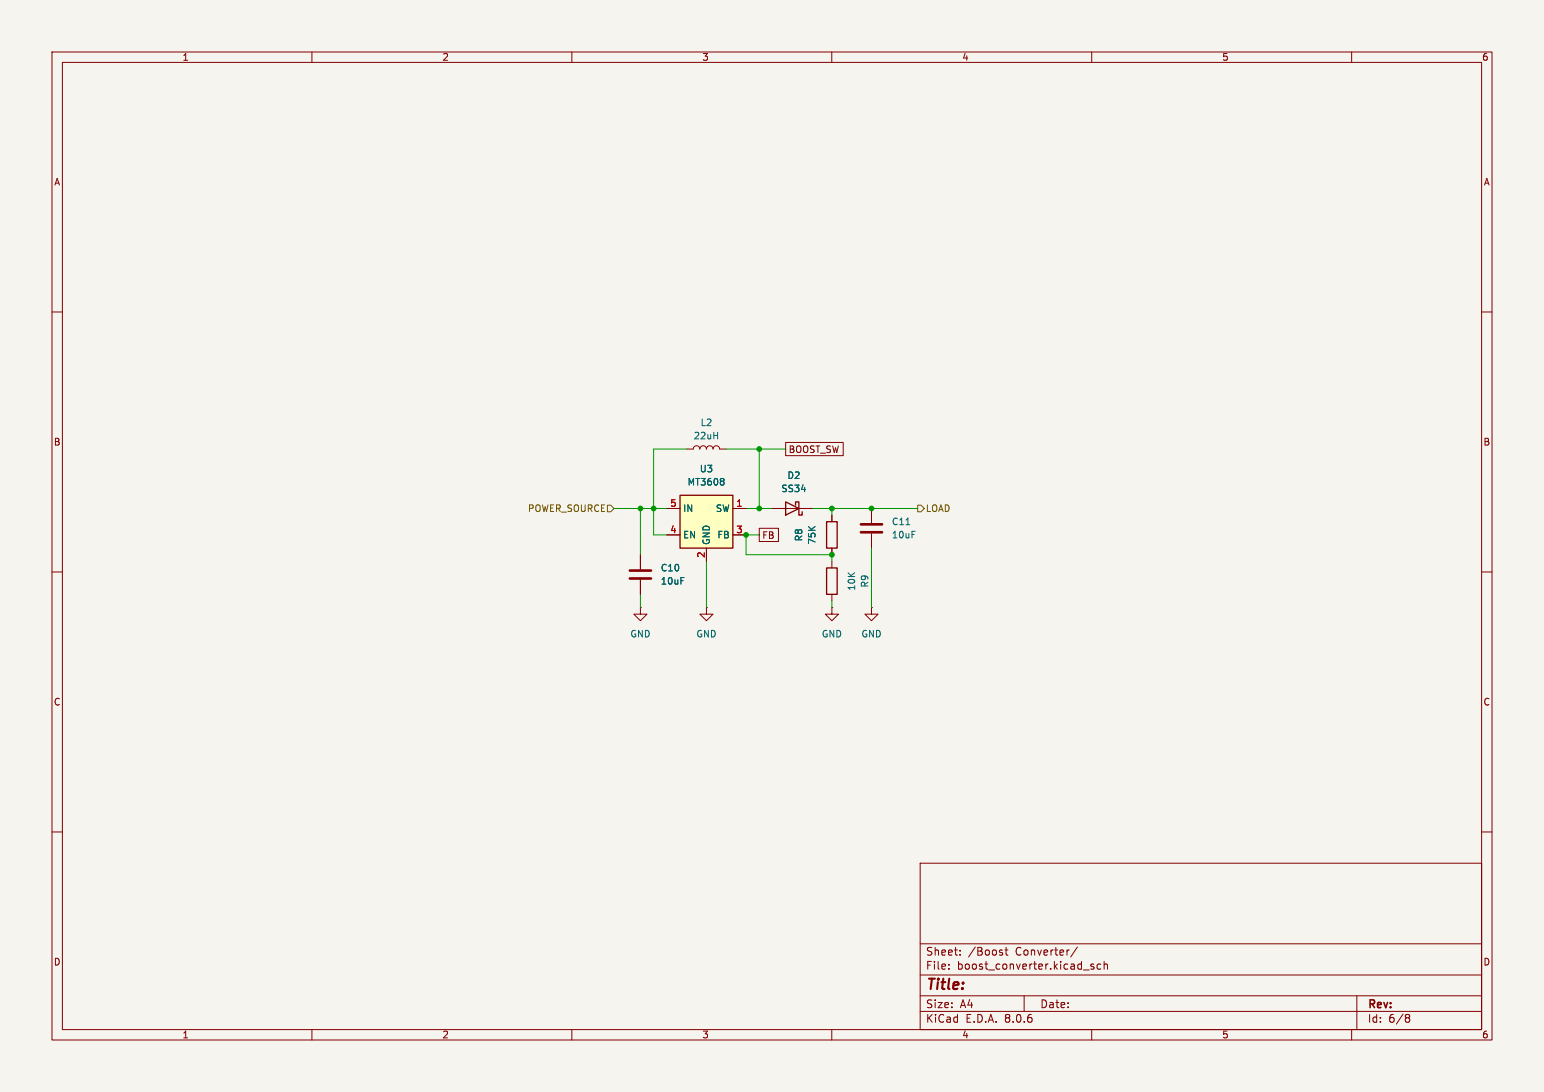
[picture p38: page 6]

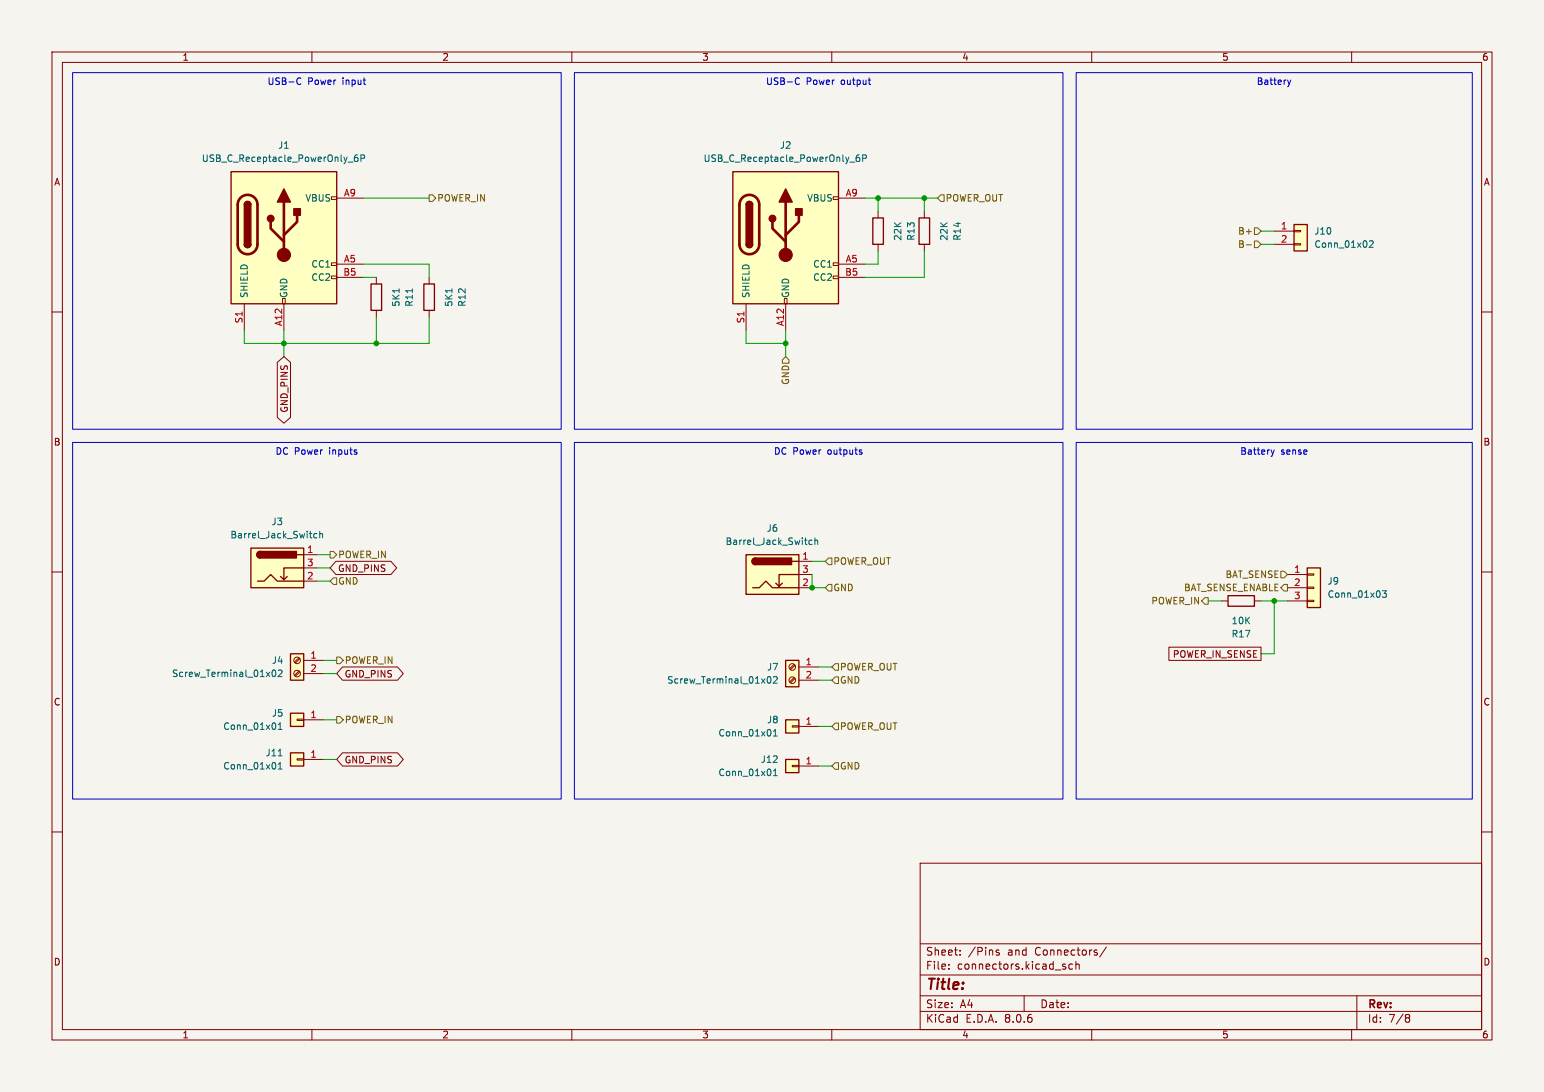
[picture p39: page 7]

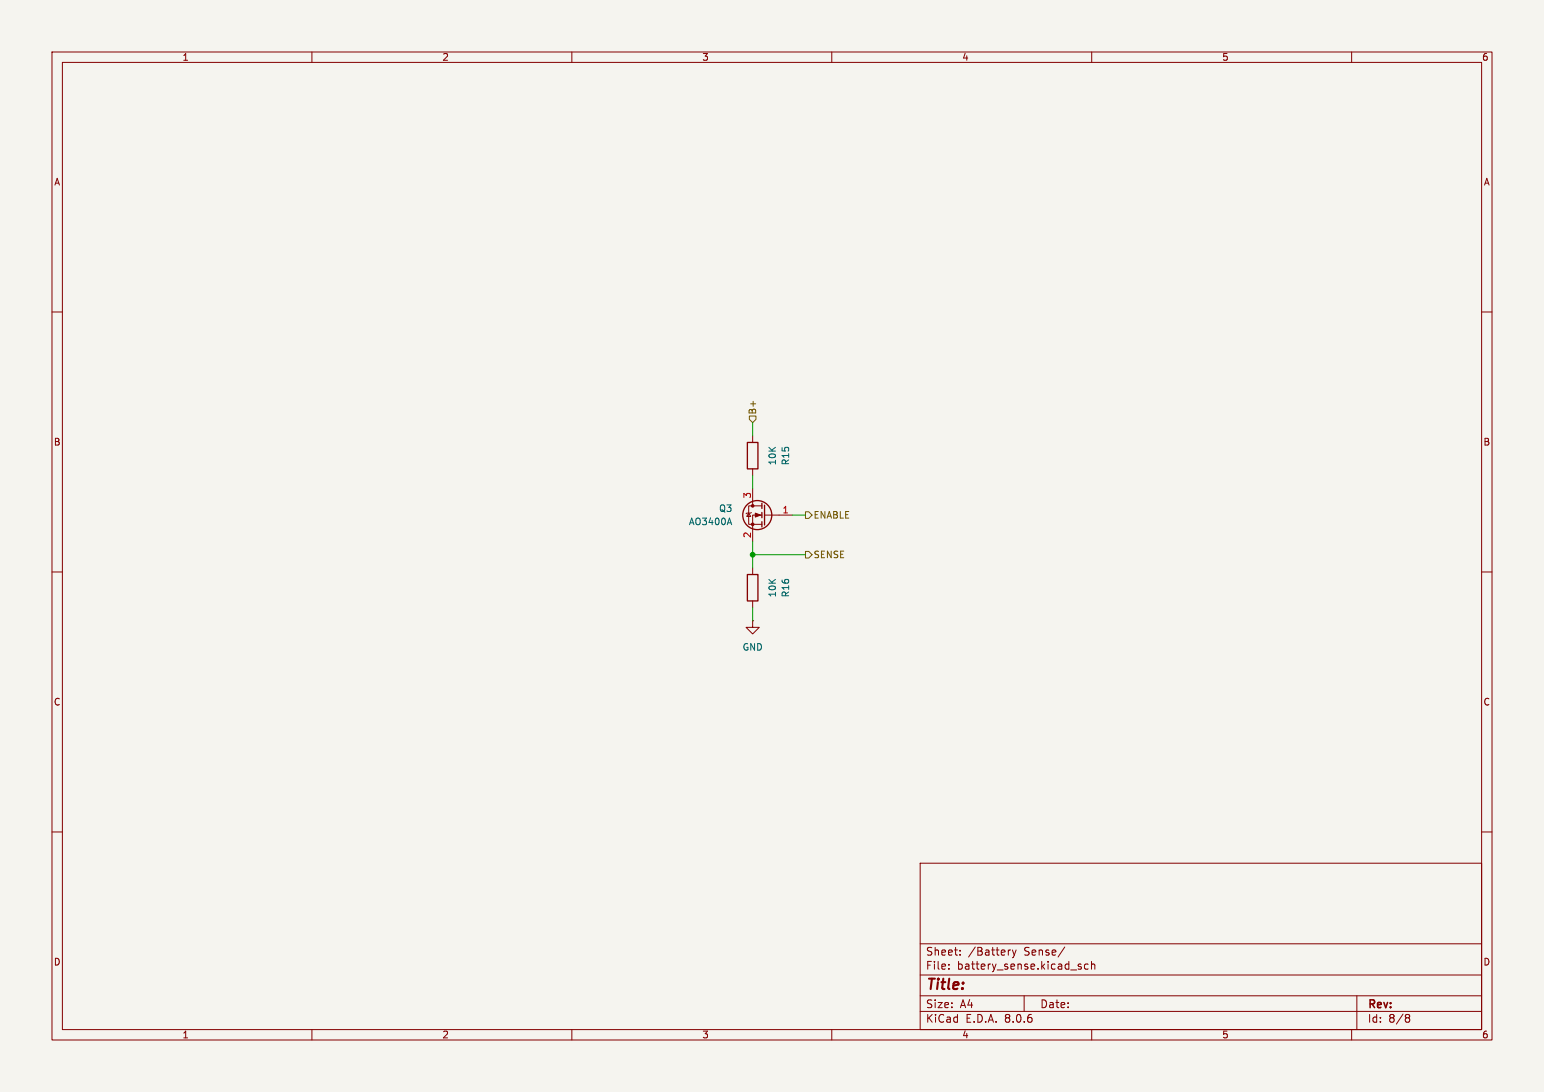
[picture p40: page 8]
