smkent/pcb/dev/power/tp4056-ls-boost/fab/tp4056-ls-boost-schematic.pdf

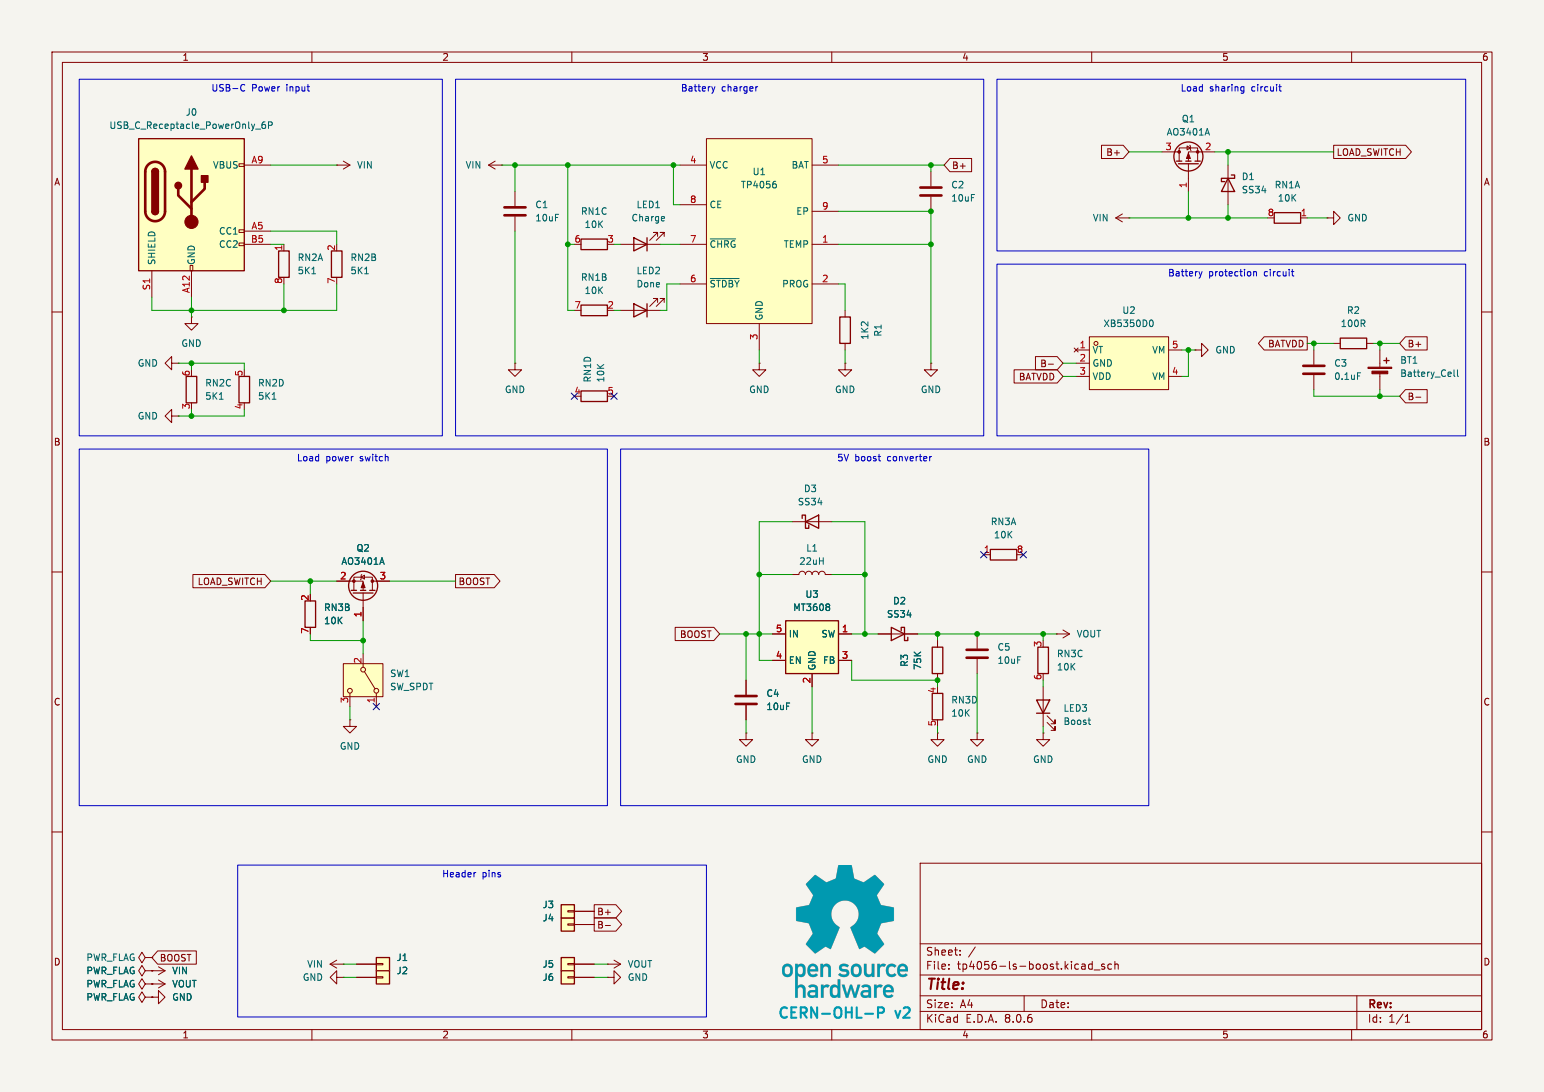
[picture p41: page 1]

Load sharing circuit 5V boost converter C4

3 VCC 4 BAT 5 ~{STDBY} 6 ~{CHRG} 7 CE 8 EP 9 U1 TP4056 GND R1 1K2 GND GND

Id: 1/1 Title: File: tp4056-ls-boost.kicad_sch Sheet: /
