smkent/pcb/dev/power/tp4056-ls/fab/tp4056-ls-schematic.pdf

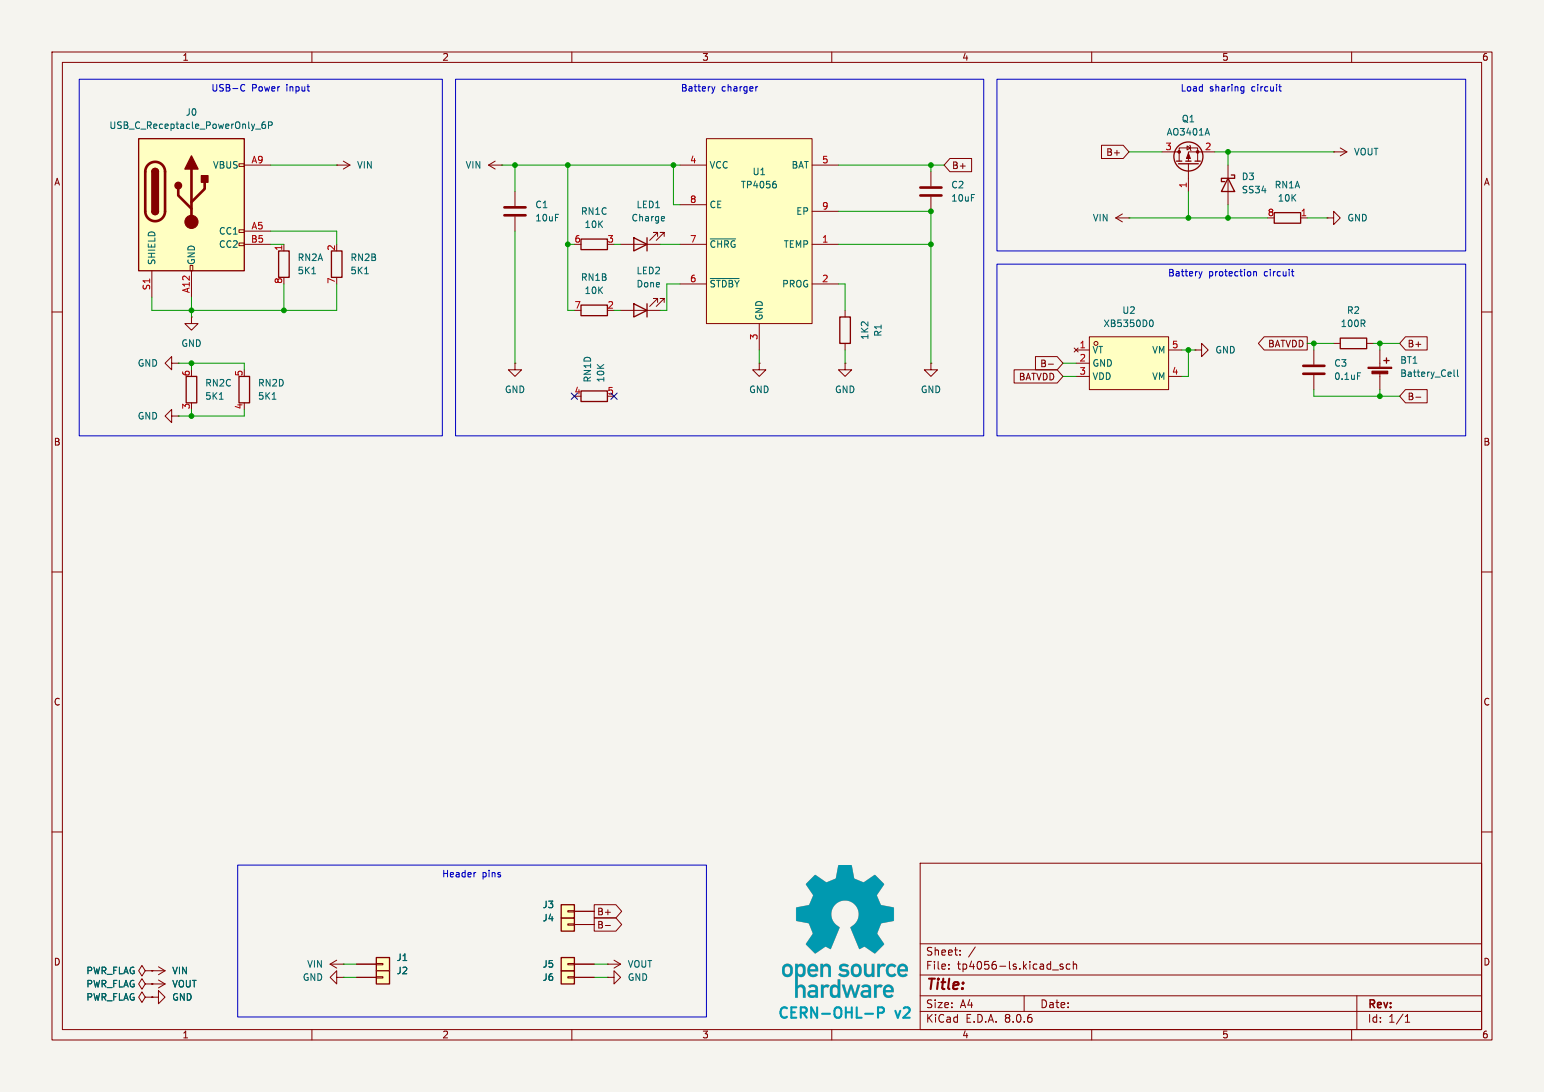
[picture p42: page 1]

3 VCC 4 BAT 5 ~{STDBY} 6 ~{CHRG} 7 CE 8 EP 9 U1 TP4056

Id: 1/1 Title: File: tp4056-ls.kicad_sch Sheet: /
