smkent/pcb/dev/stackable/esp-sensors/fab/esp-sensors-schematic.pdf

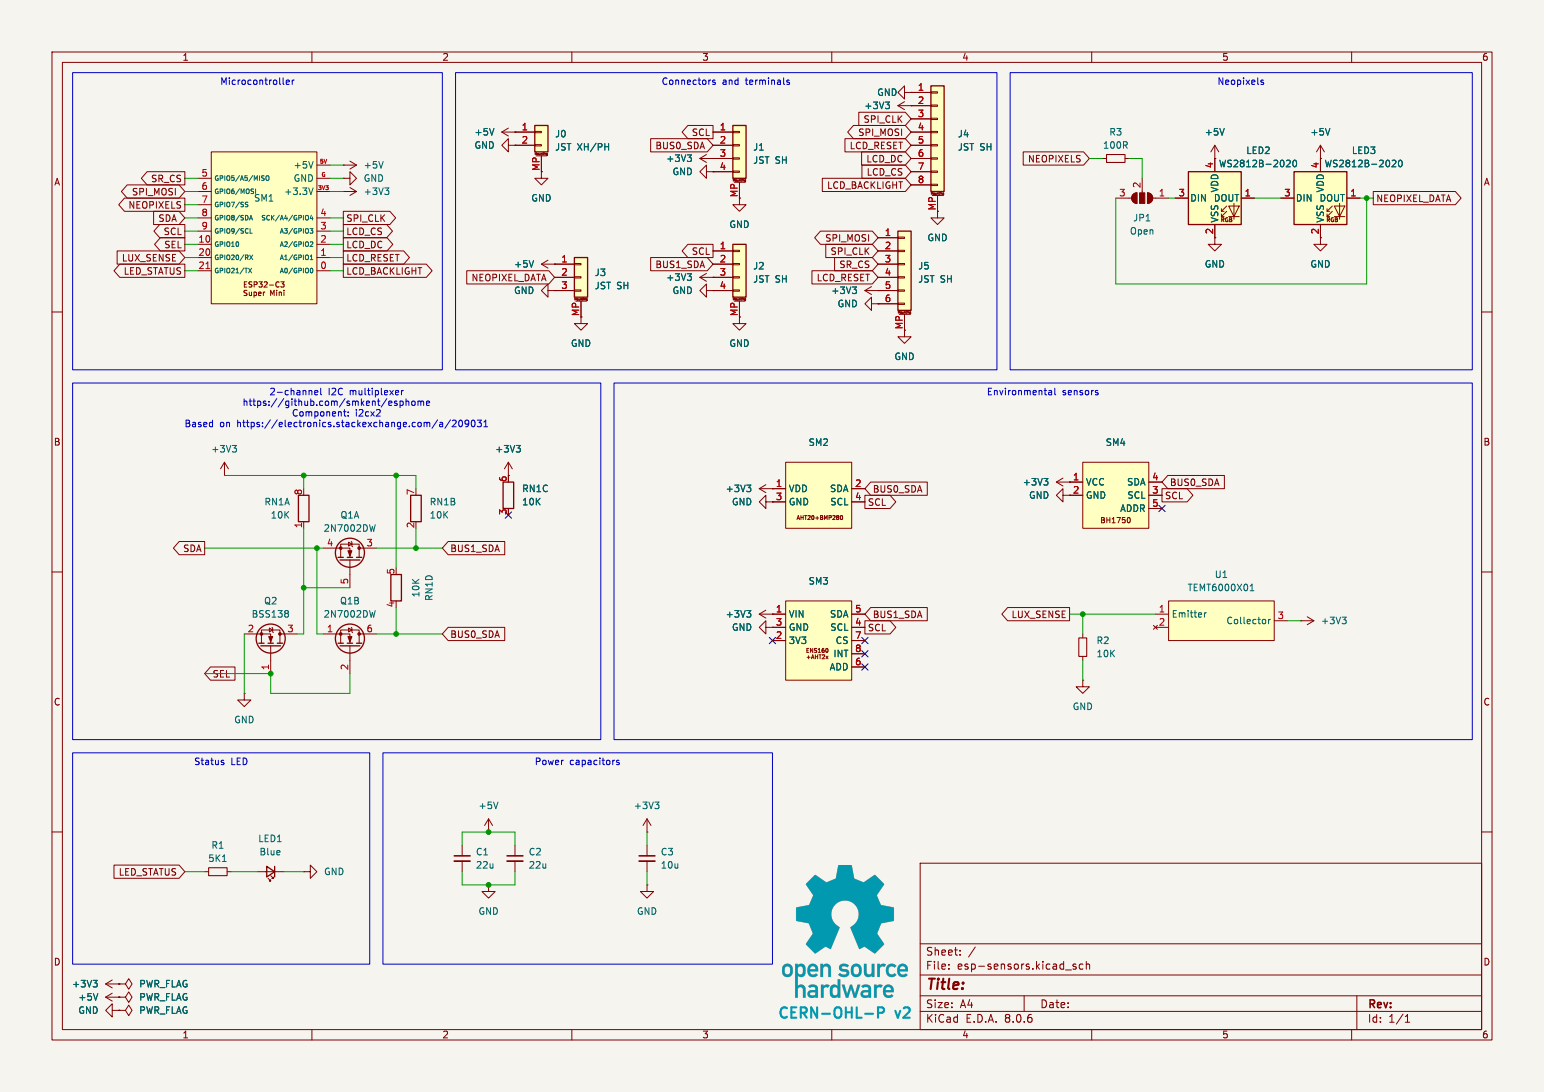
[picture p43: page 1]

Id: 1/1 Title: File: esp-sensors.kicad_sch Sheet: /
