smkent/pcb/dev/stackable/power-18650-holder/fab/power-18650-holder-schematic.pdf

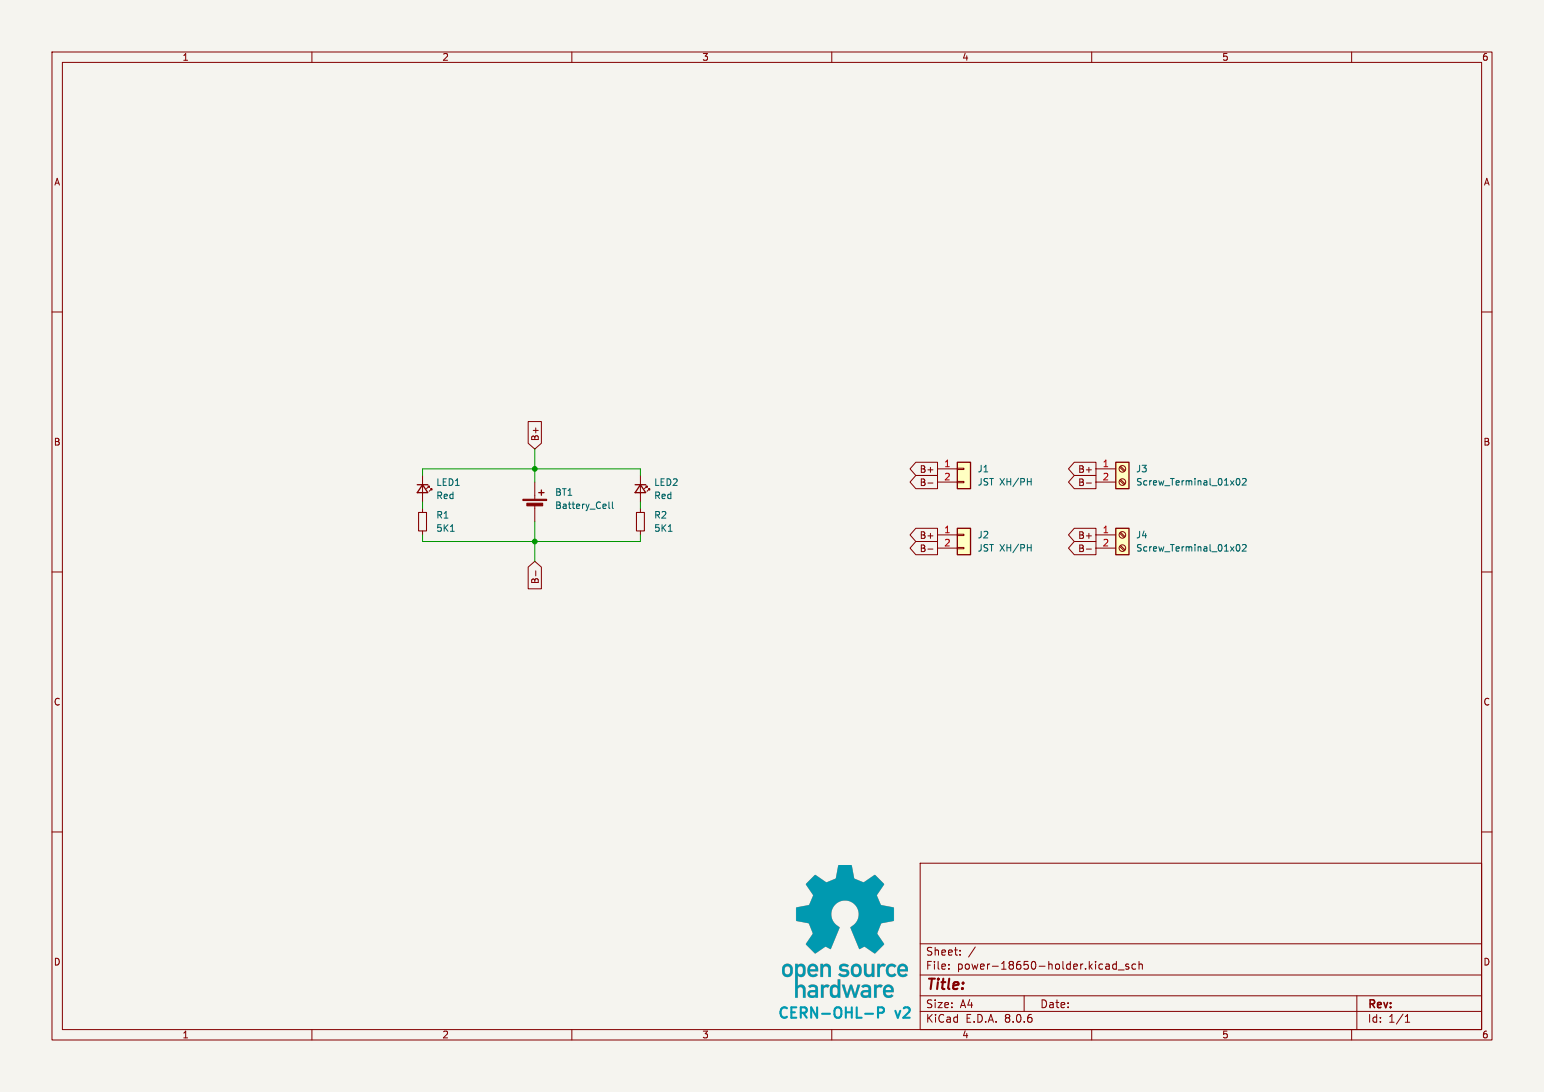
[picture p44: page 1]

Id: 1/1 Title: File: power-18650-holder.kicad_sch Sheet: /
