smkent/pcb/dev/stackable/power-eta6003-5v-ups/fab/power-eta6003-5v-ups-schematic.pdf

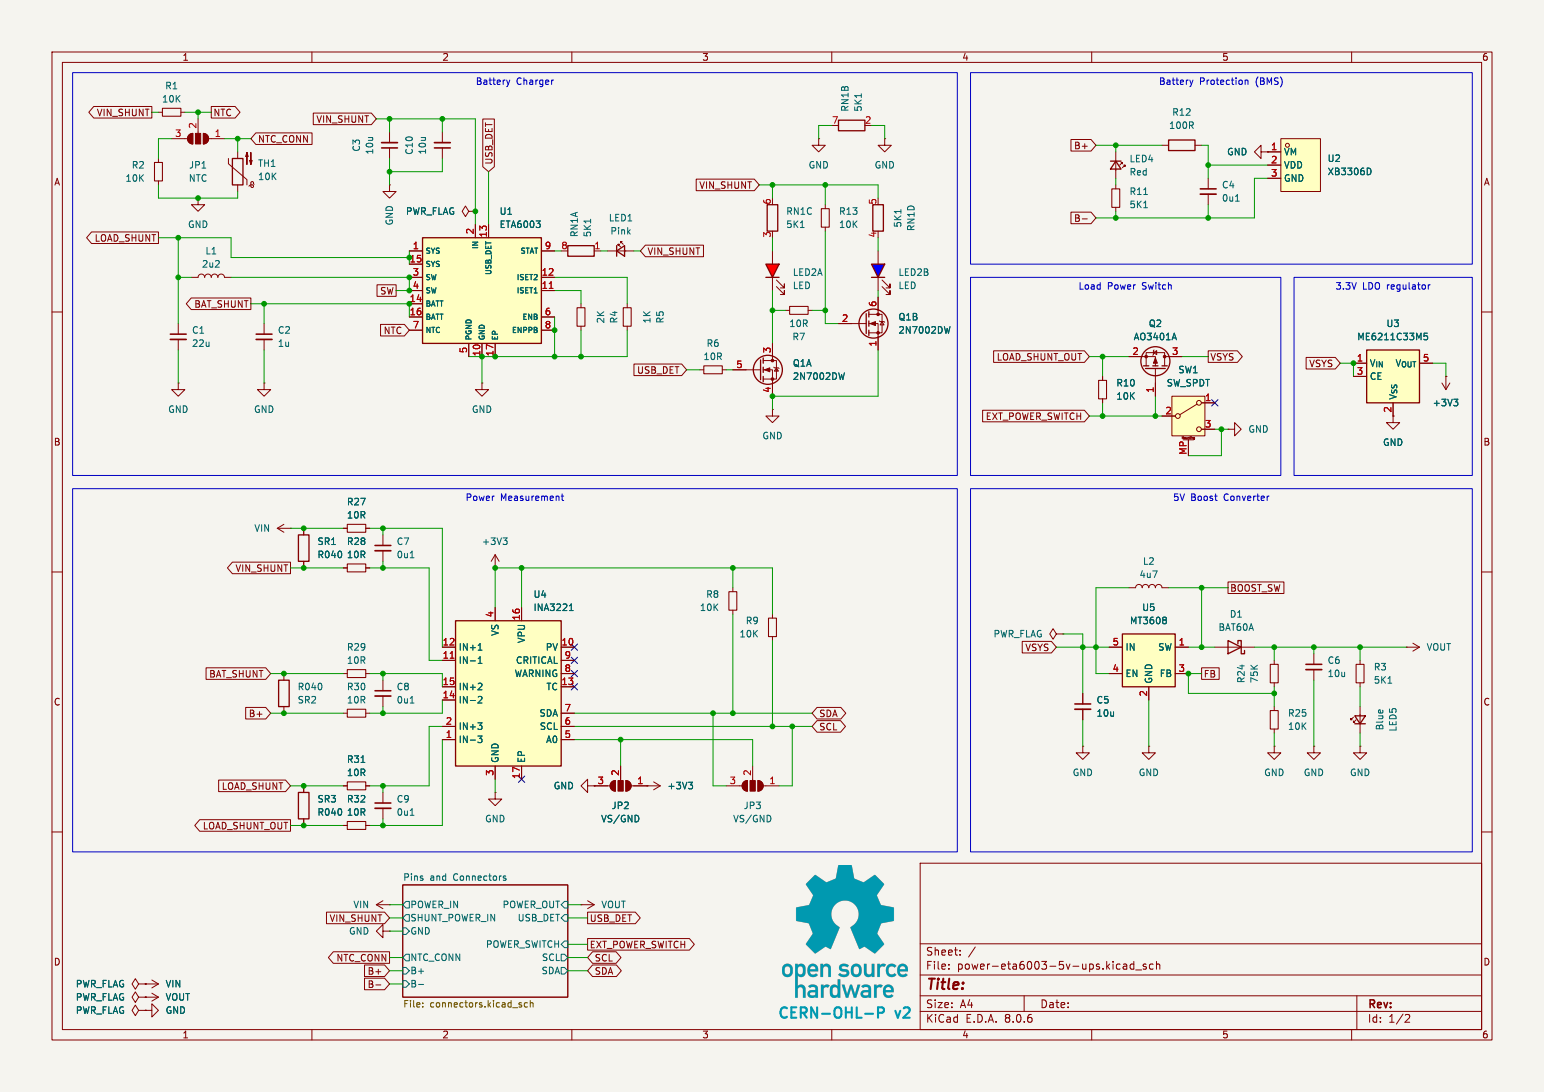
[picture p45: page 1]

VM 1 VDD 2 GND 3 GND Q1B

4 A0 5 SCL 6 SDA 7 WARNING 8 CRITICAL 9 R28

4 A0 5 SCL 6 SDA 7 WARNING 8 CRITICAL 9 U4

Pins and Connectors File: connectors.kicad_sch

Id: 1/2 Title: File: power-eta6003-5v-ups.kicad_sch Sheet: / POWER_OUT GND

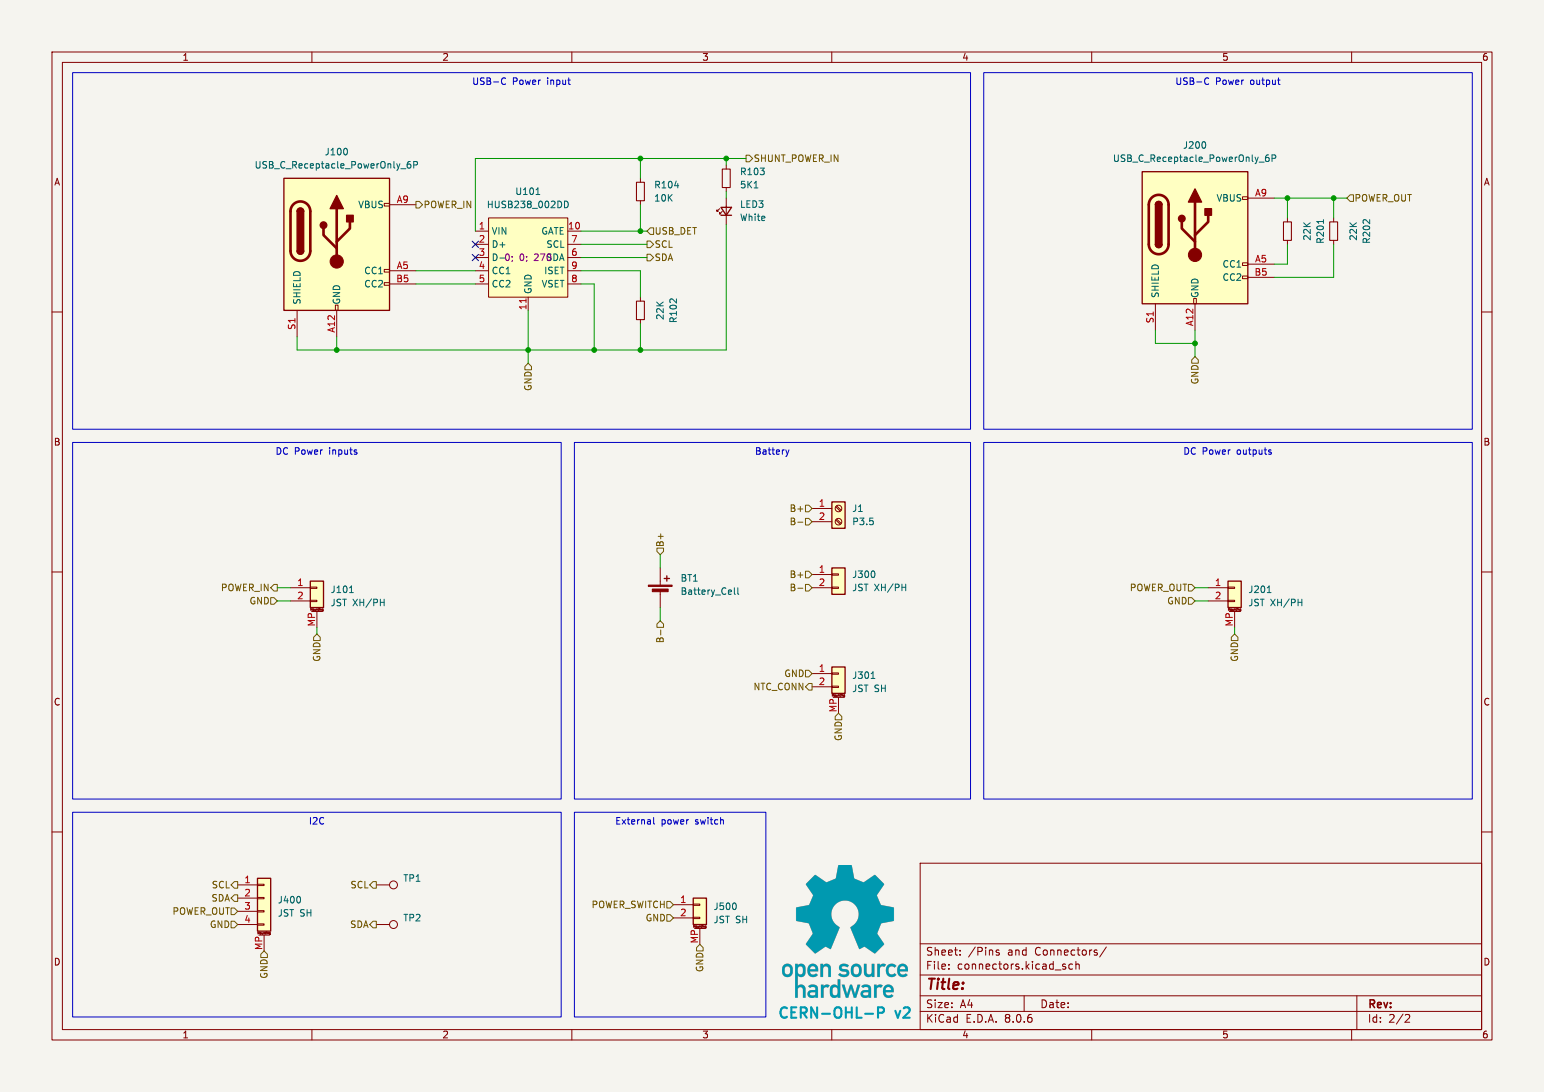
[picture p46: page 2]

USB-C Power output Battery
