smkent/pcb/dev/stackable/relay-module-5v-half/fab/relay-module-5v-half-schematic.pdf

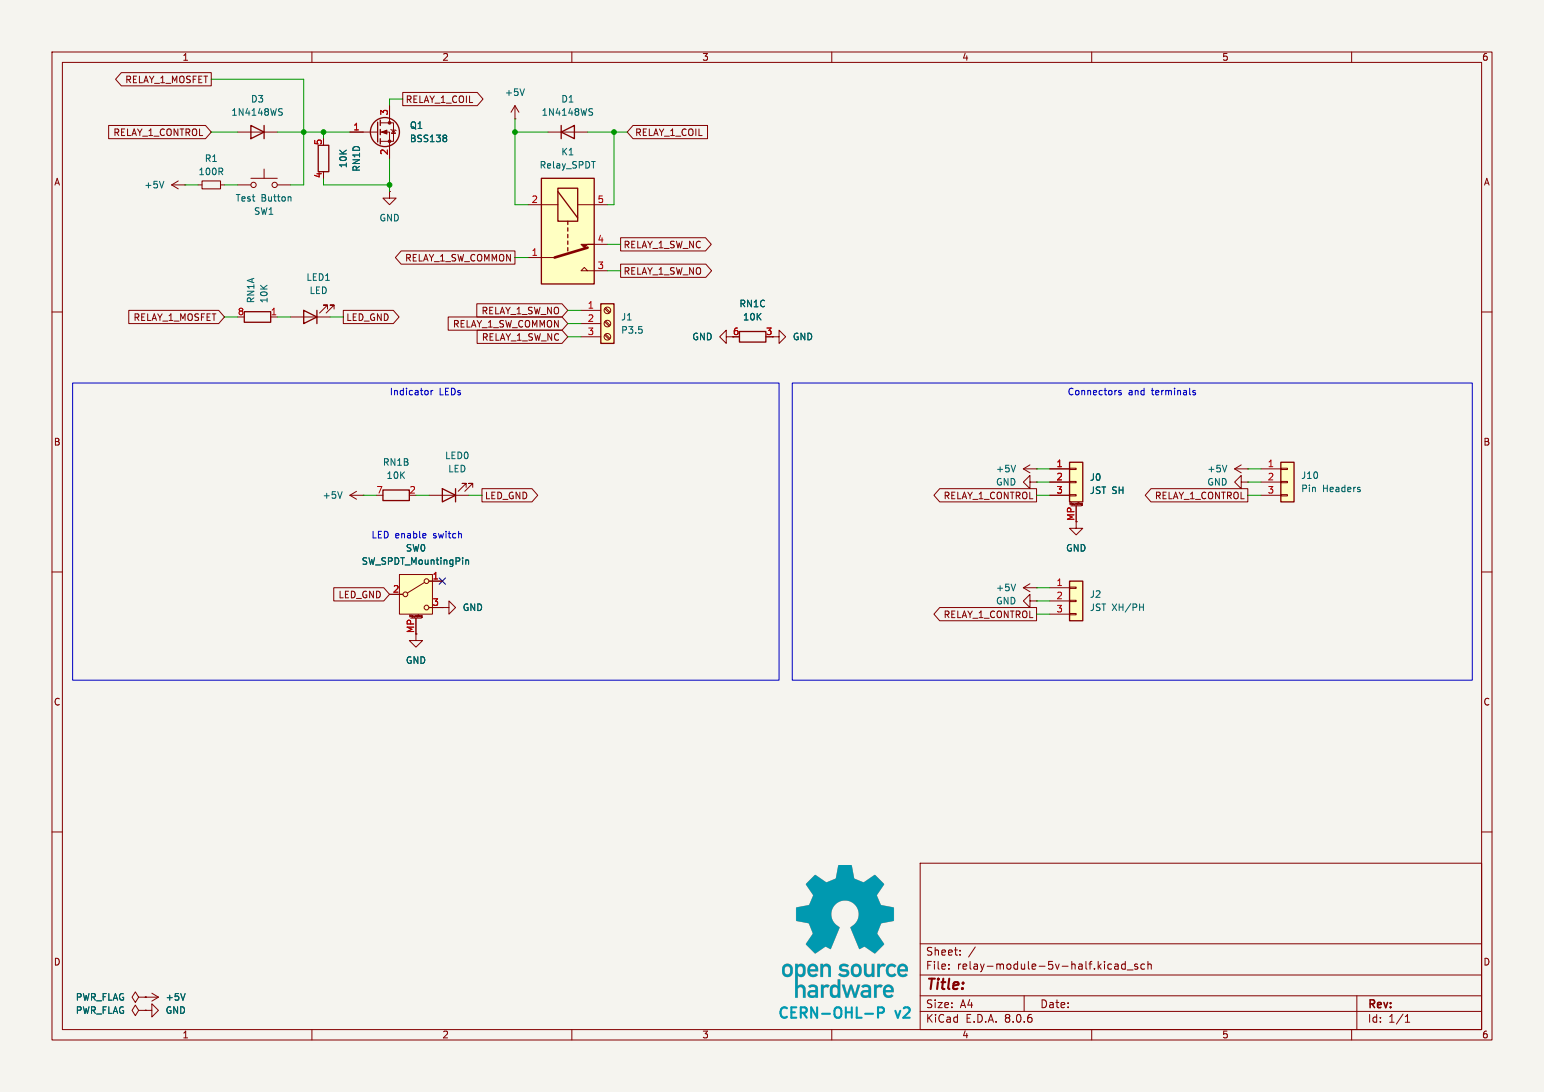
[picture p47: page 1]

JST XH/PH GND
