smkent/pcb/dev/stackable/shift-register-ring/fab/shift-register-ring-schematic.pdf

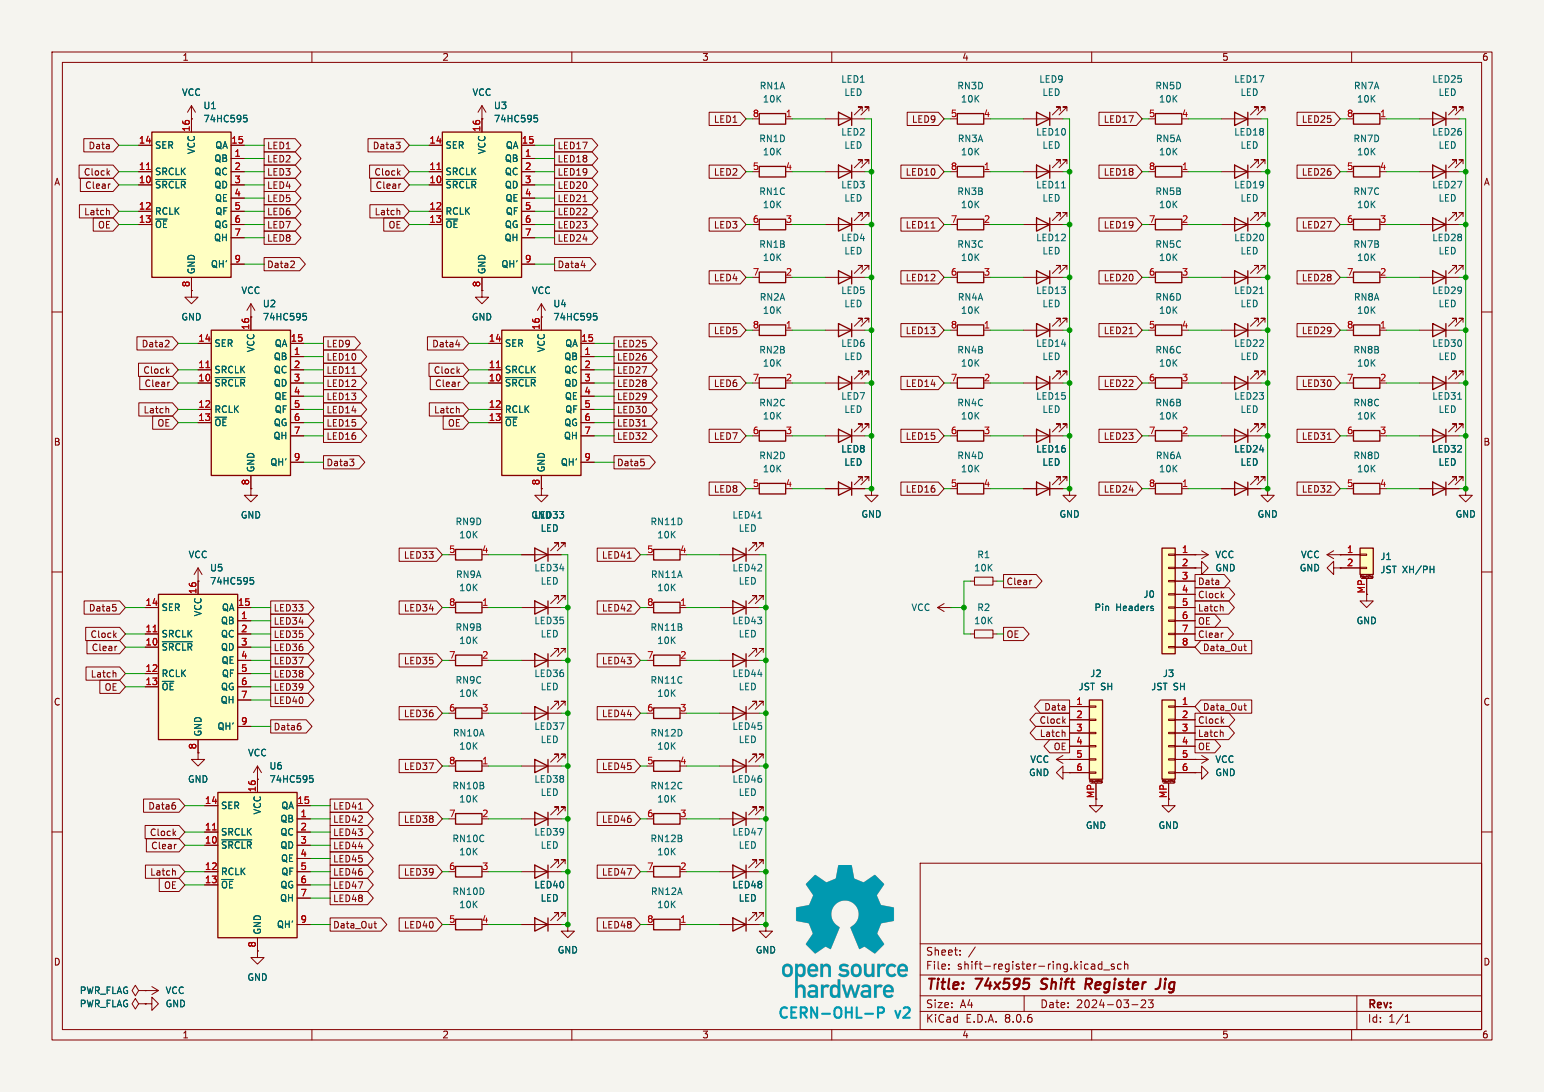
[picture p48: page 1]

JST XH/PH GND GND GND

2 MP GND GND GND

File: shift-register-ring.kicad_sch Sheet: /
