smkent/pcb/pcb/esphome/garage-door-control/fab/garage-door-control-schematic.pdf

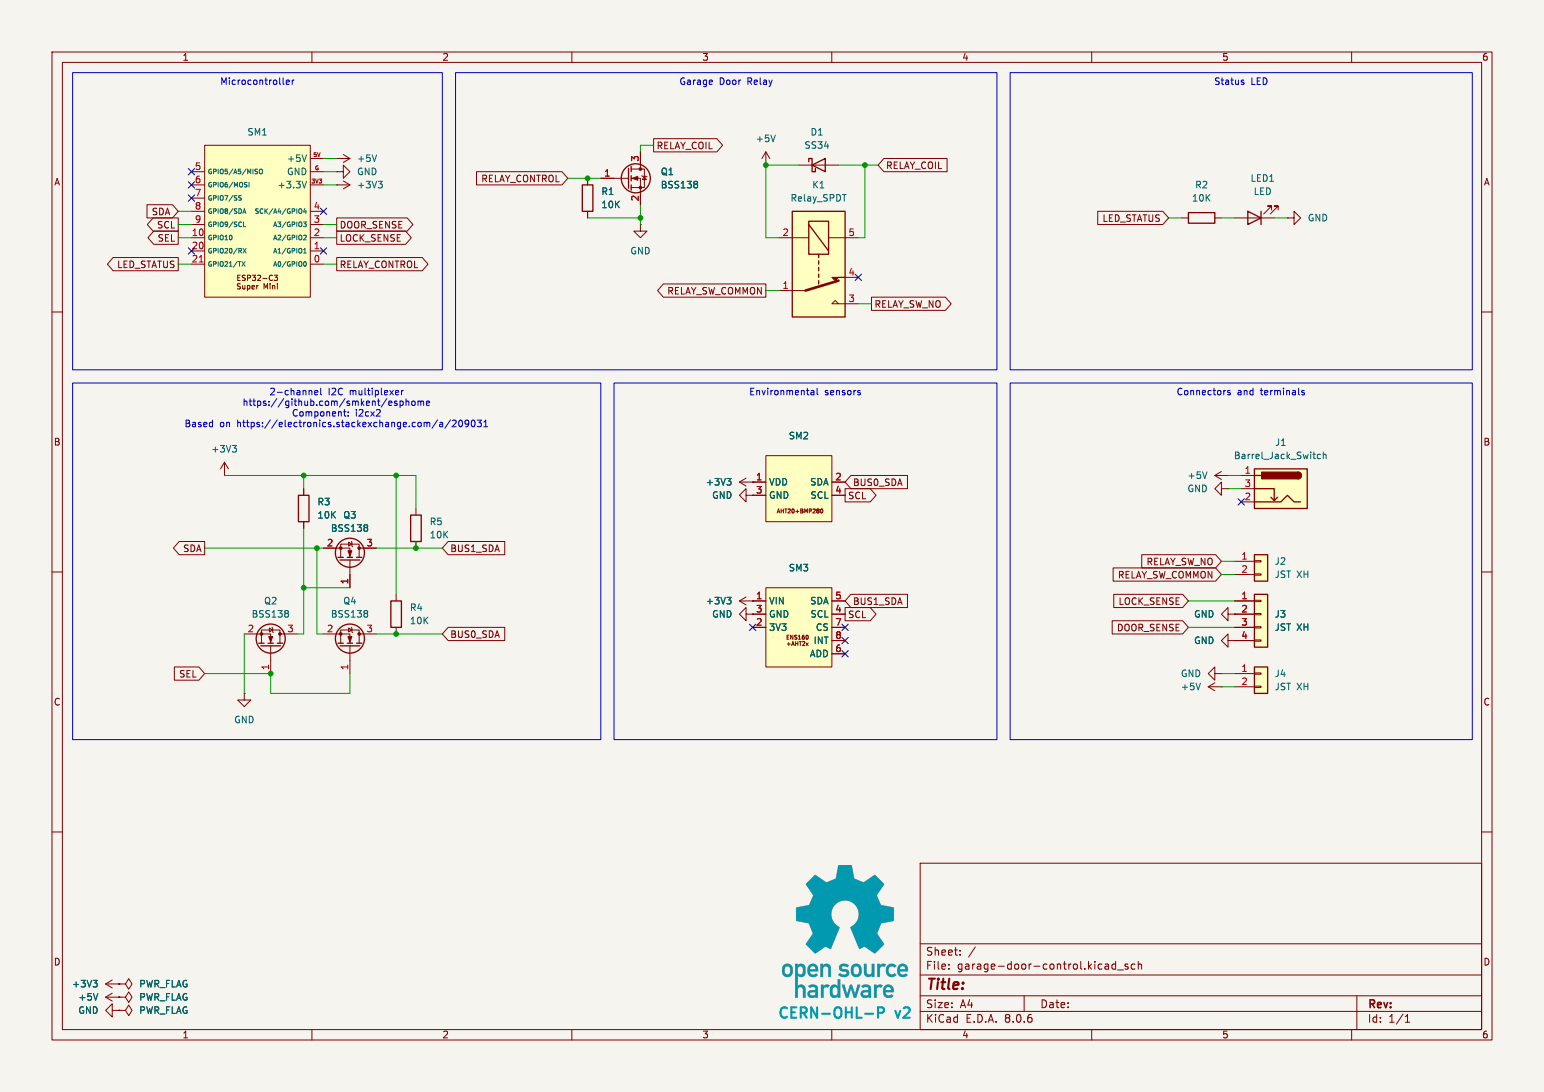
[picture p49: page 1]

https://github.com/smkent/esphome

Id: 1/1 Title: File: garage-door-control.kicad_sch Sheet: / PWR_FLAG
