smkent/pcb/pcb/jigs/breadboard-power-microcontroller/fab/breadboard-power-microcontroller-schematic.pdf

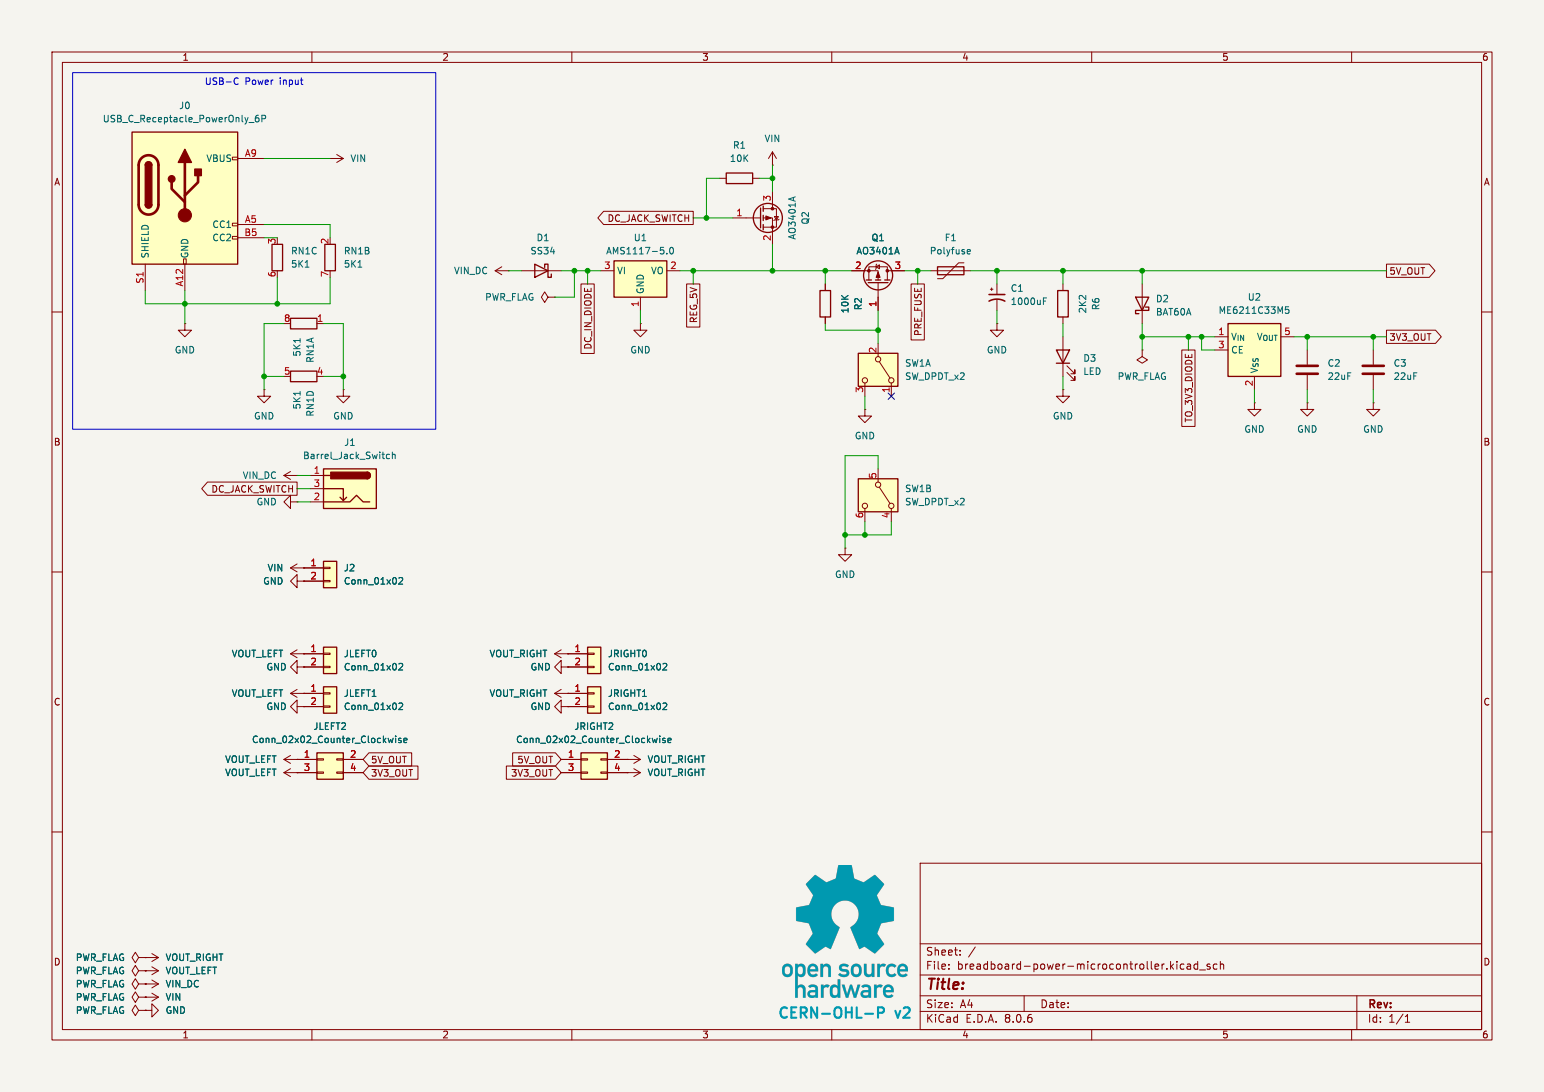
[picture p50: page 1]

Id: 1/1 Title: File: breadboard-power-microcontroller.kicad_sch Sheet: /
