smkent/pcb/pcb/jigs/breadboard-power/fab/breadboard-power-schematic.pdf

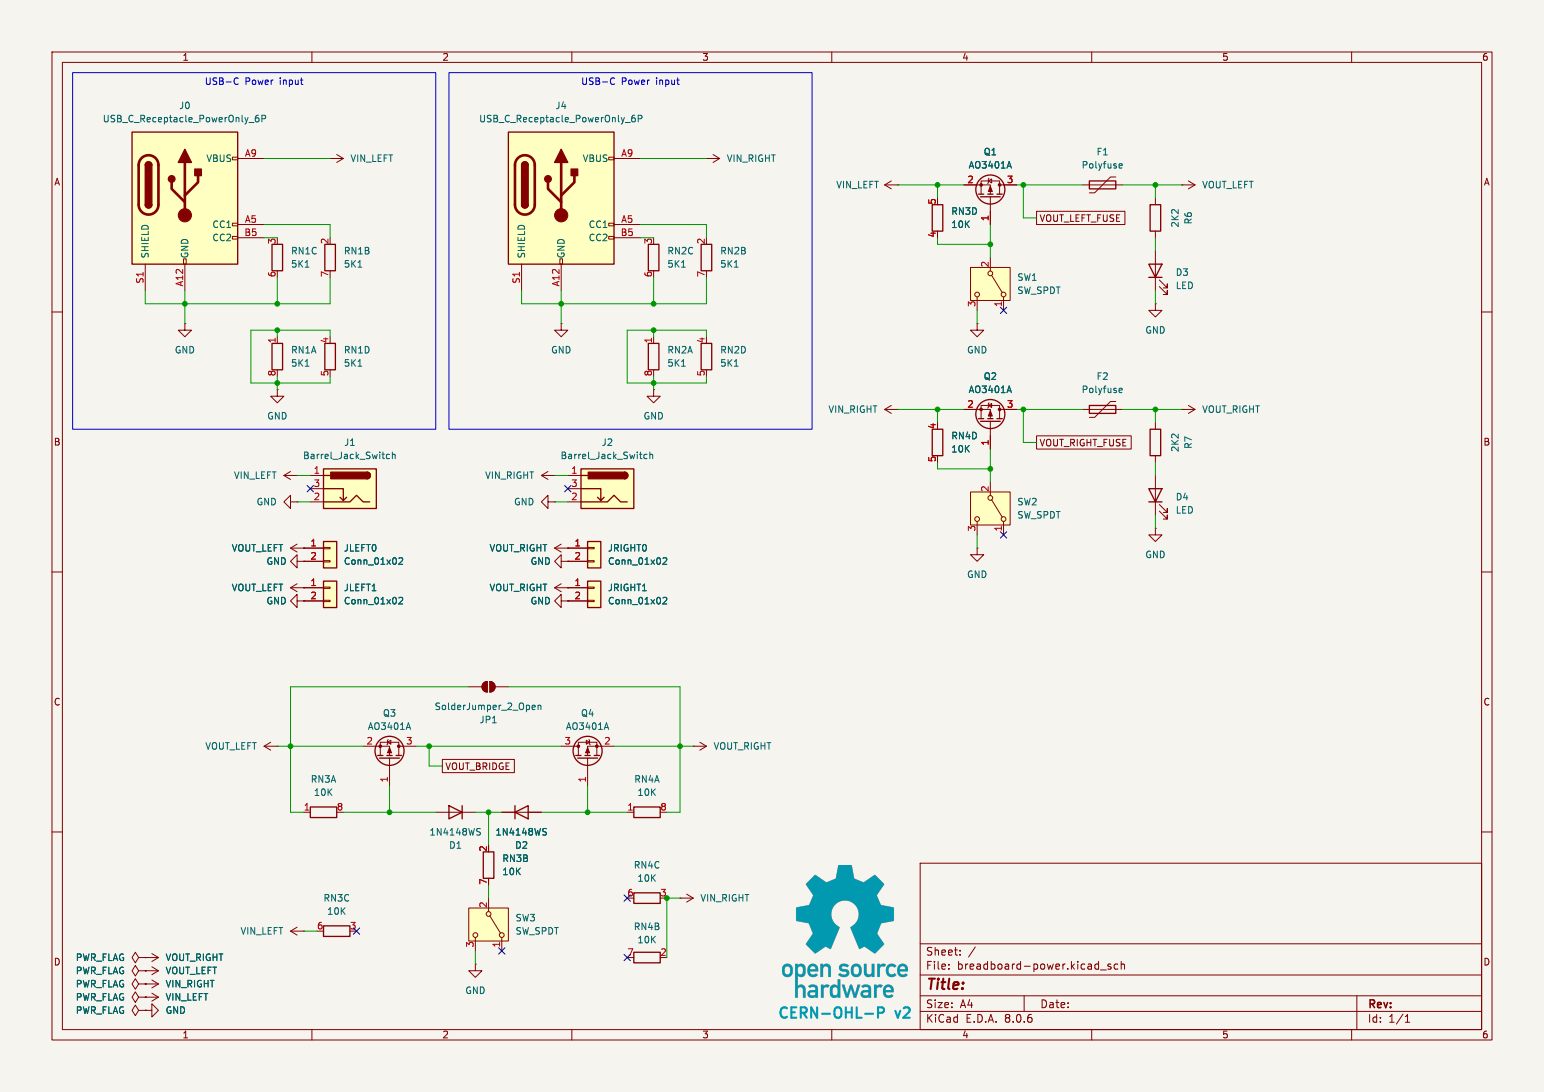
[picture p51: page 1]

Id: 1/1 Title: File: breadboard-power.kicad_sch Sheet: /
