smkent/pcb/pcb/jigs/dip-adapters/fab/dip-adapters-schematic.pdf

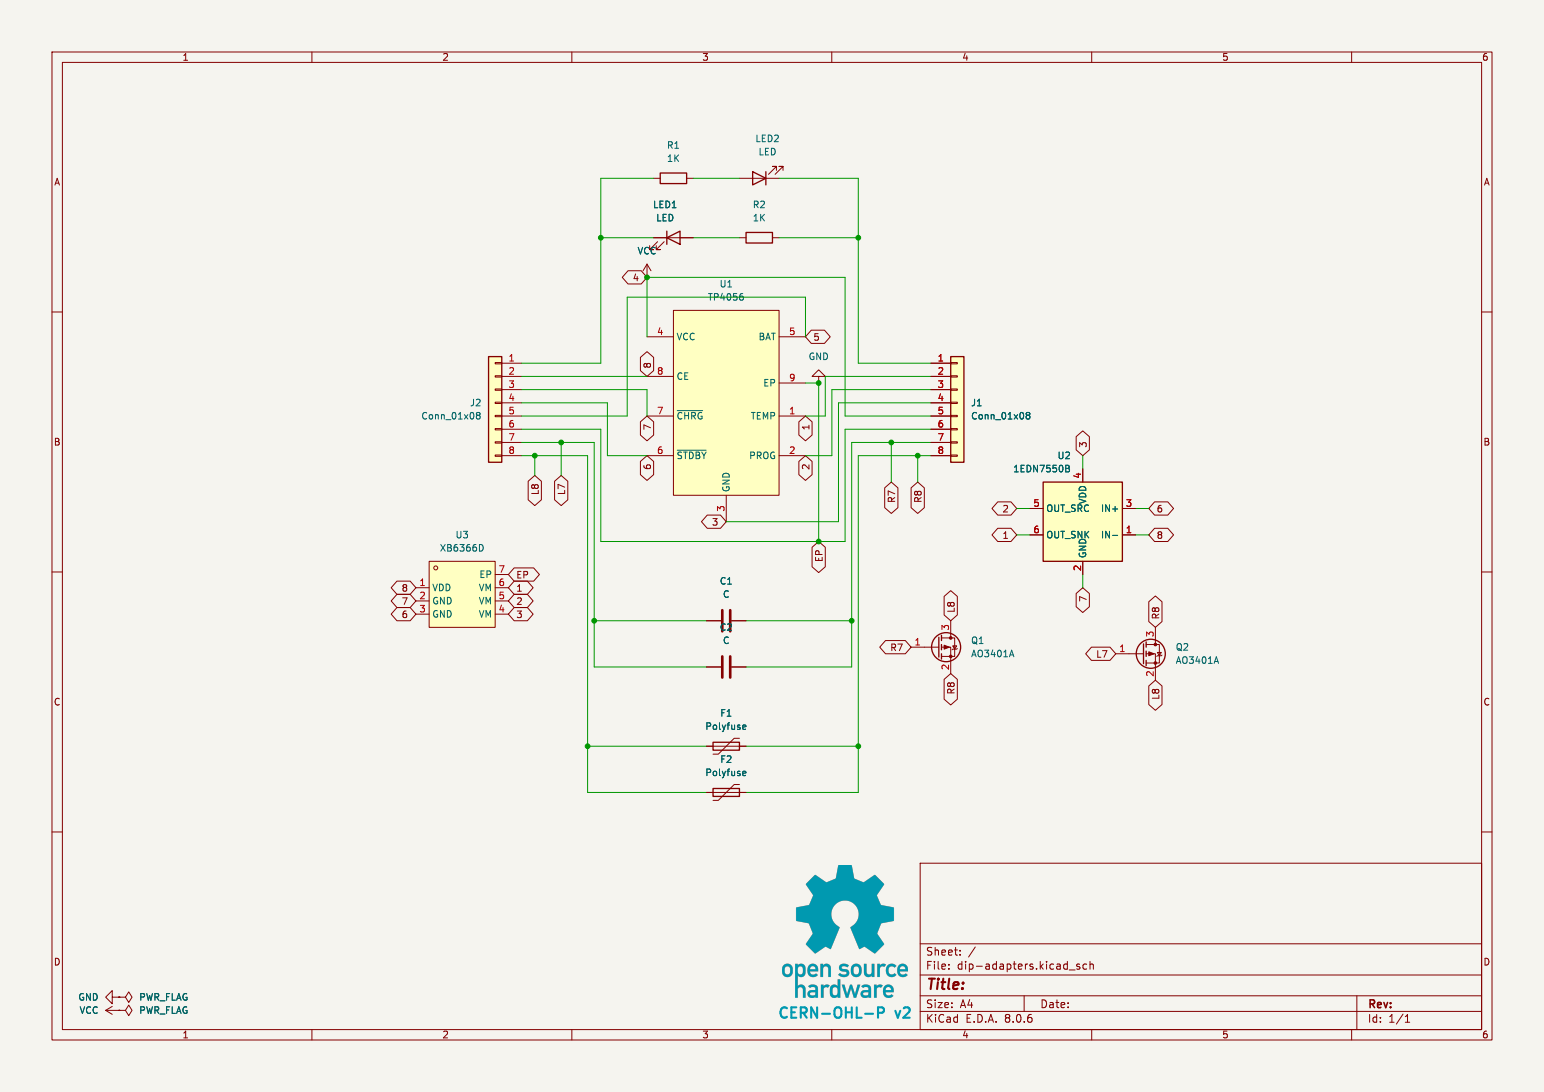
[picture p52: page 1]

3 VCC 4 BAT 5 ~{STDBY} 6 ~{CHRG} 7 CE 8 EP 9 U1 TP4056 VDD 1 GND 2 GND 3 VM 4 VM 5 VM 6 EP 7 U3 XB6366D

Id: 1/1 Title: File: dip-adapters.kicad_sch Sheet: /
