smkent/pcb/pcb/jigs/esp-doorbell-button/fab/esp-doorbell-button-schematic.pdf

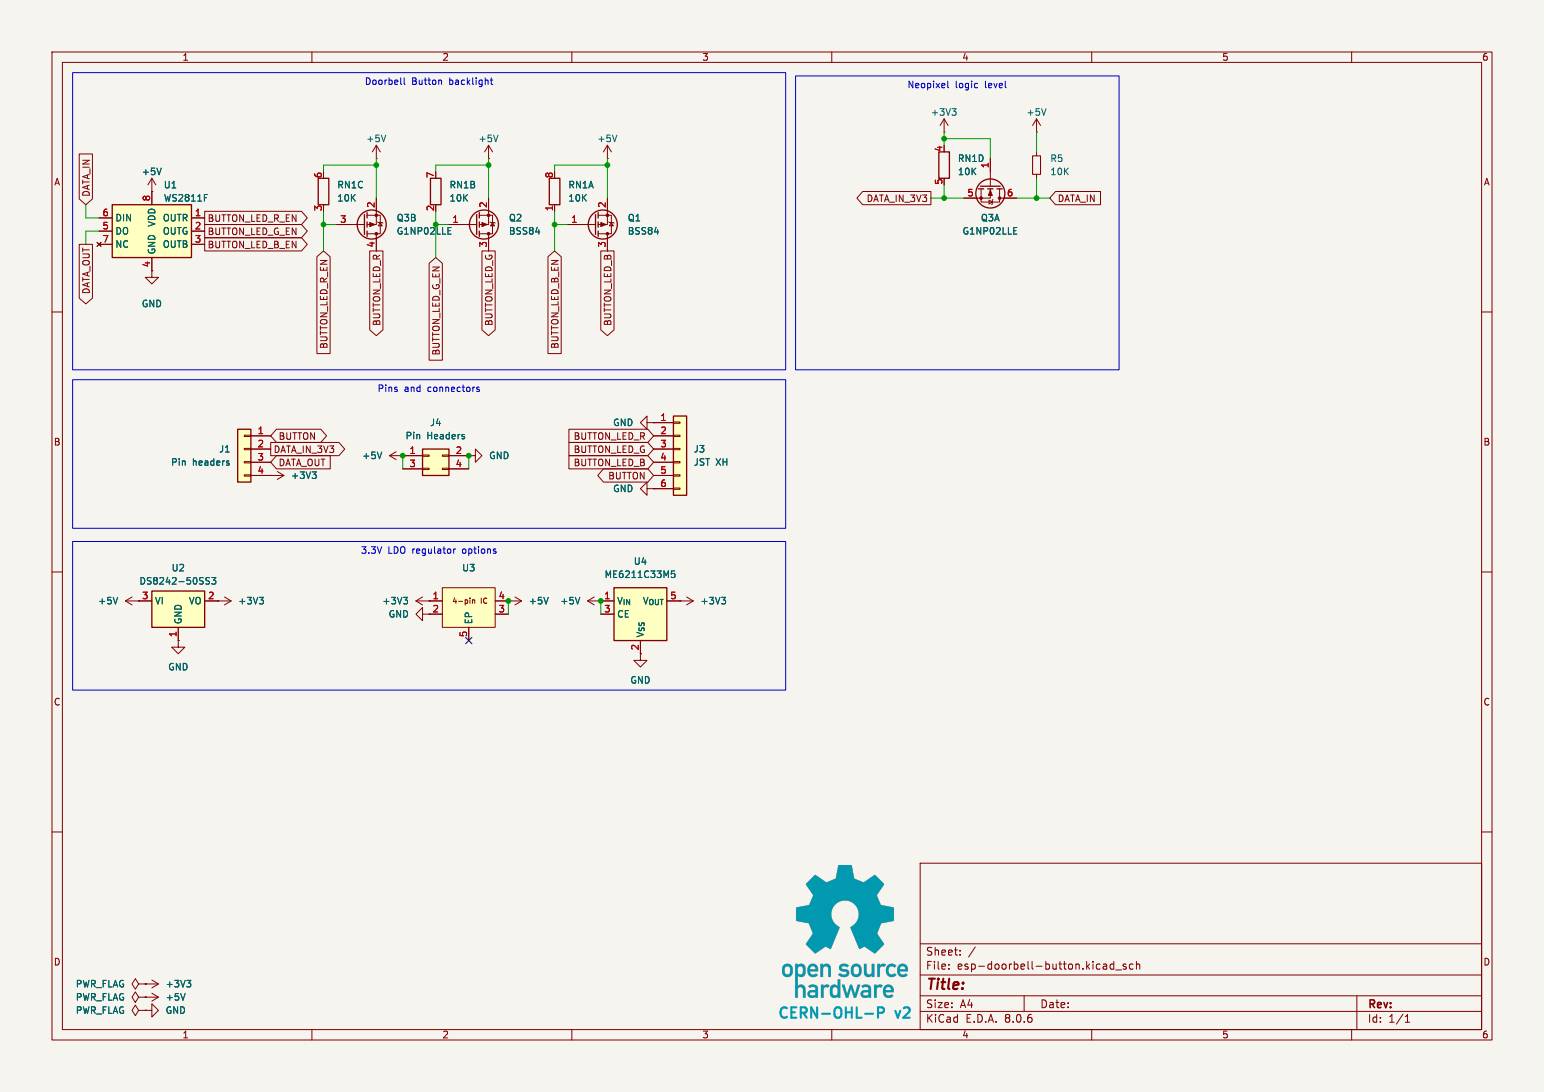
[picture p53: page 1]

4 DO 5 DIN 6 NC 7 VDD

Id: 1/1 Title: File: esp-doorbell-button.kicad_sch Sheet: /
