smkent/pcb/pcb/jigs/led-jig/fab/led-jig-schematic.pdf

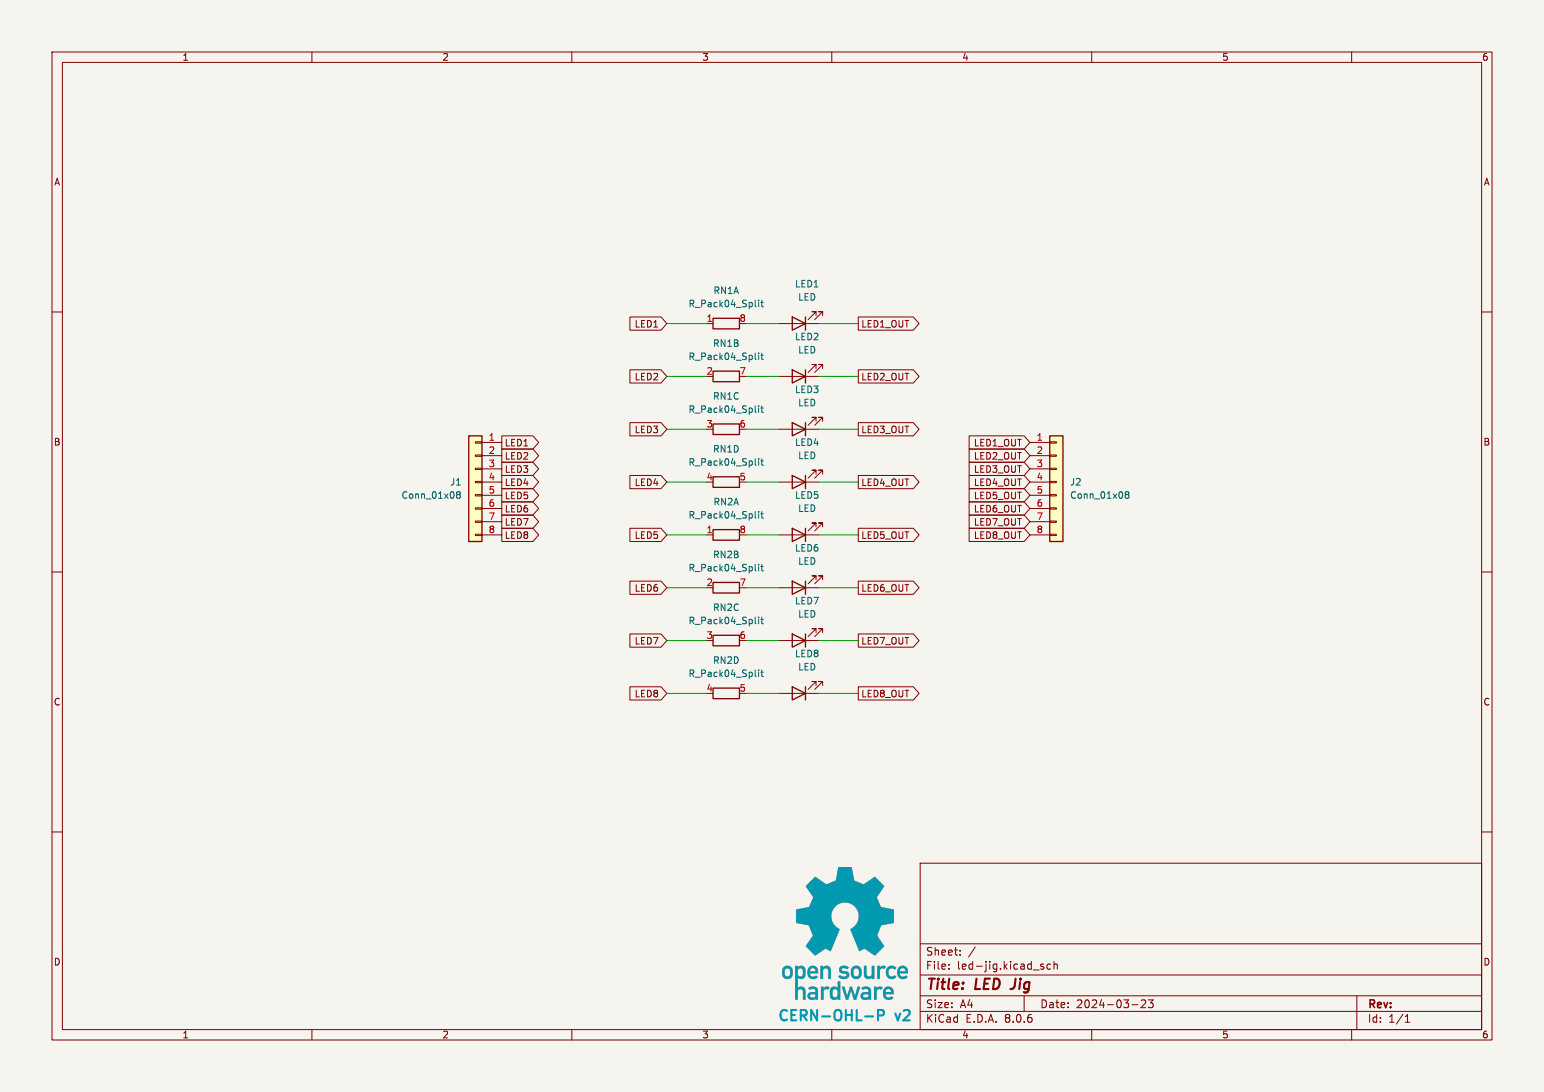
[picture p54: page 1]

File: led-jig.kicad_sch Sheet: /
Id: 1/1 Title: LED Jig
