smkent/pcb/pcb/jigs/led-micro/fab/led-micro-schematic.pdf

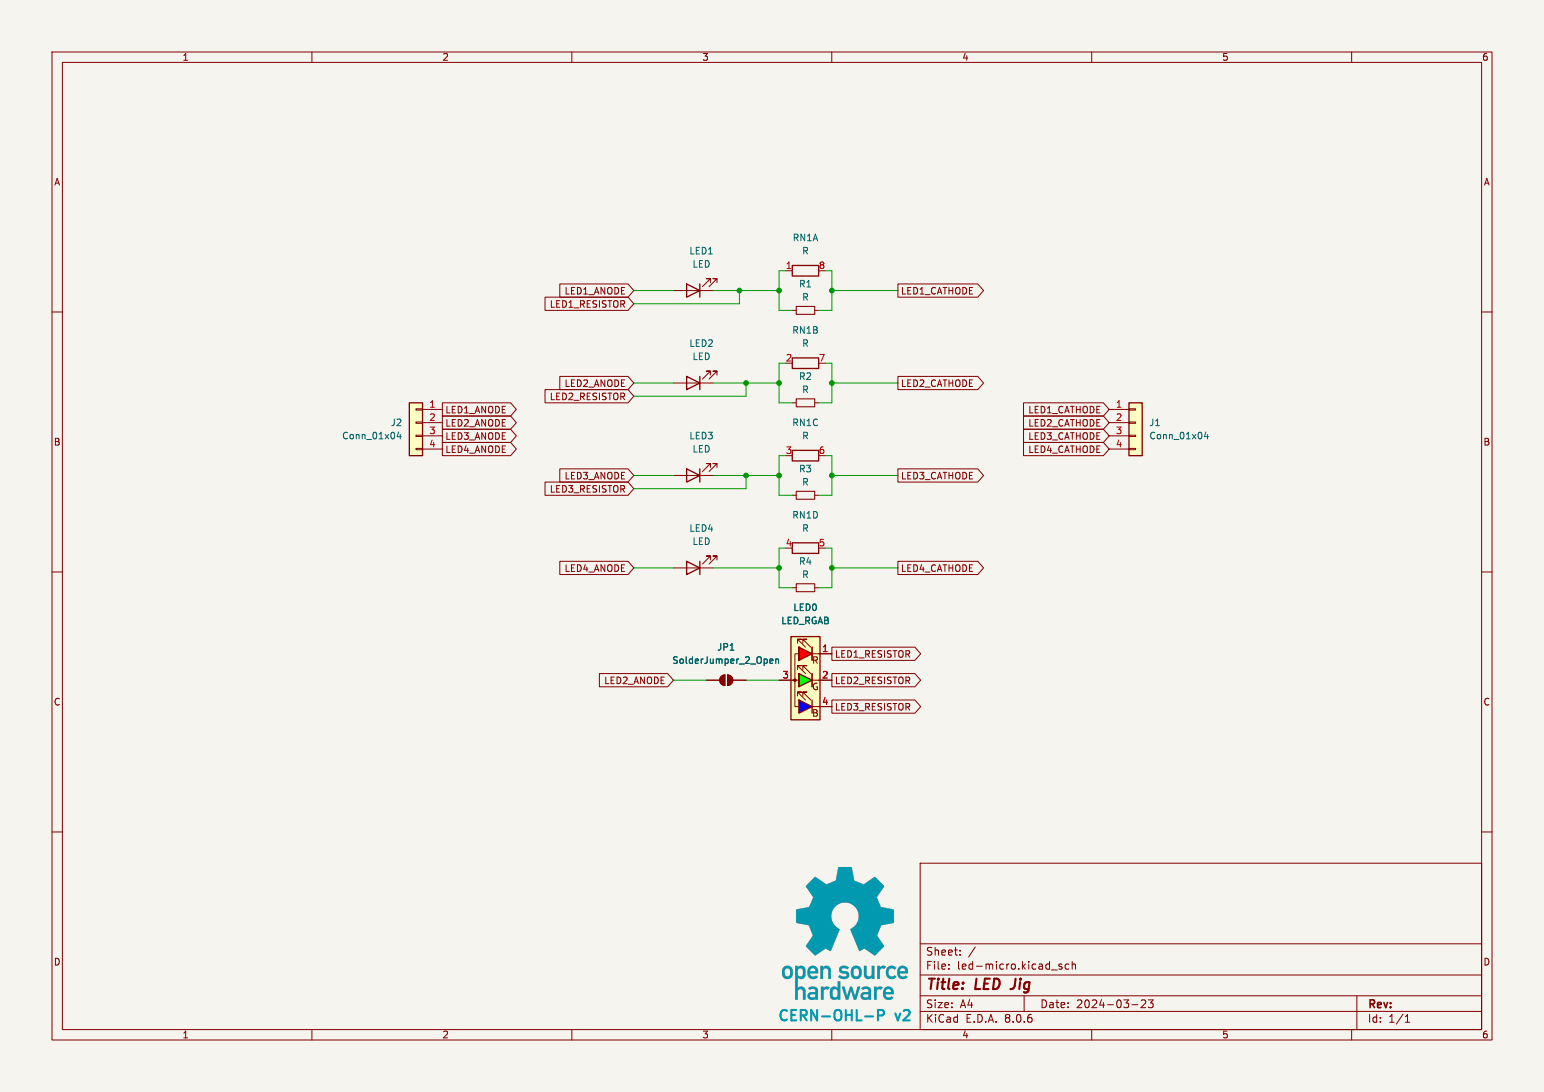
[picture p55: page 1]

File: led-micro.kicad_sch Sheet: /
Id: 1/1 Title: LED Jig
