smkent/pcb/pcb/jigs/level-shifter/fab/level-shifter-schematic.pdf

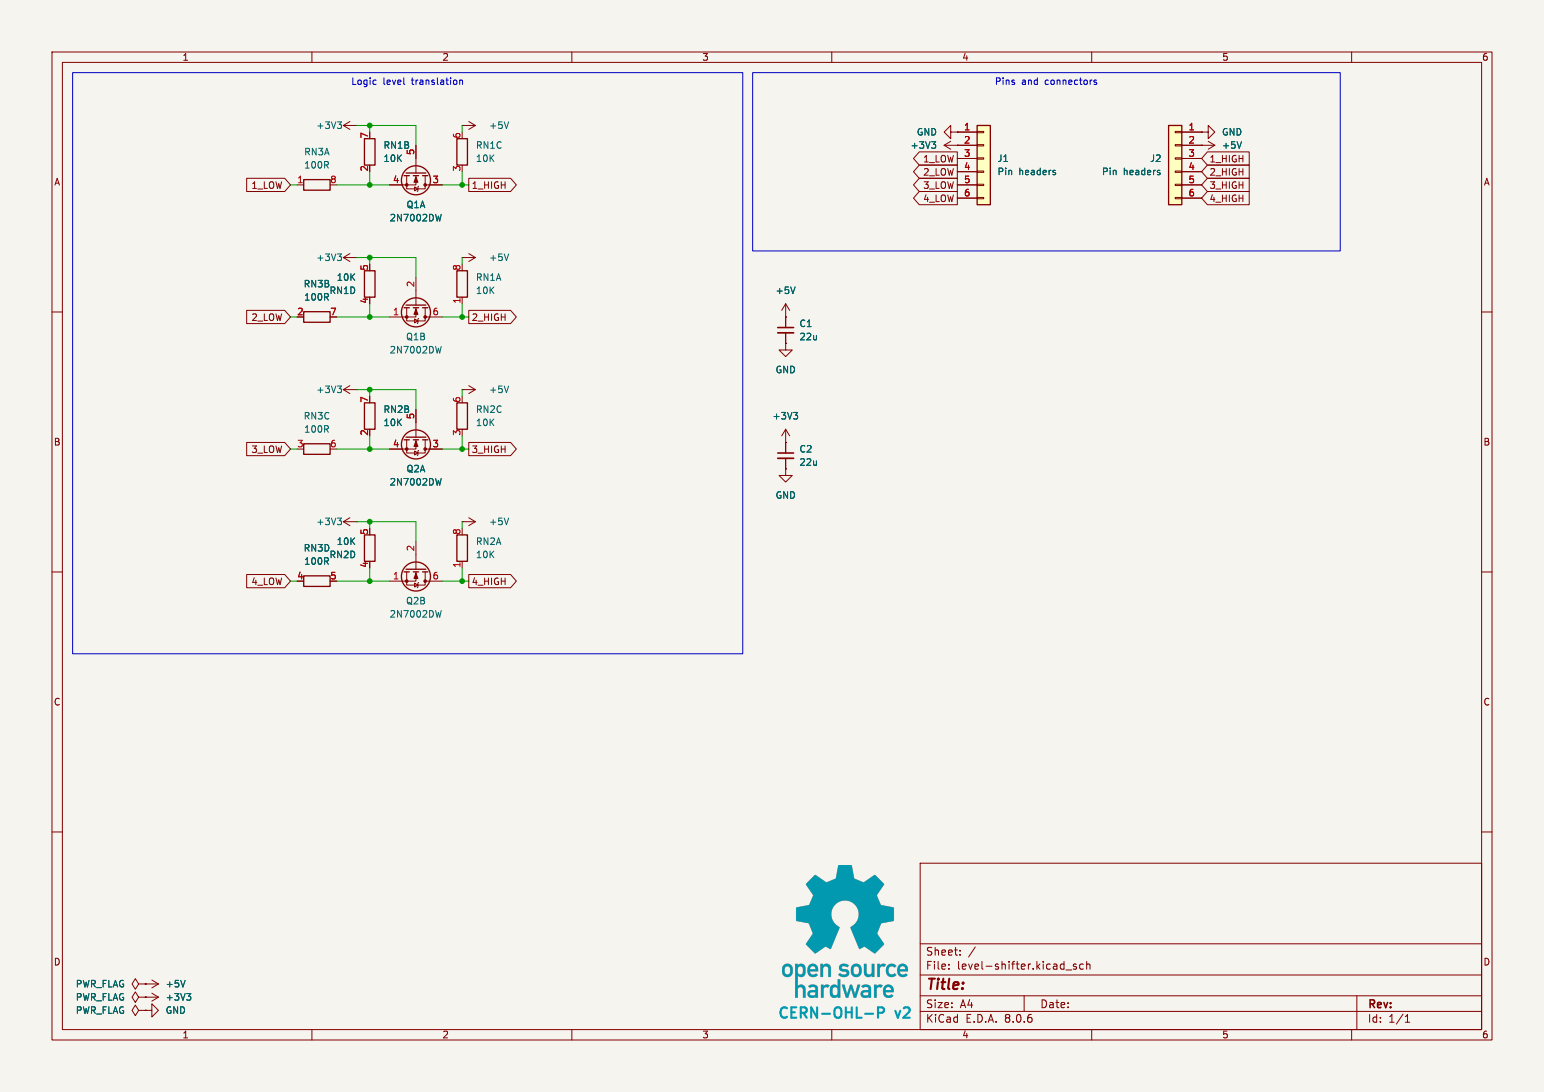
[picture p56: page 1]

Id: 1/1 Title: File: level-shifter.kicad_sch Sheet: /
