smkent/pcb/pcb/jigs/logic-led-jig/fab/logic-led-jig-schematic.pdf

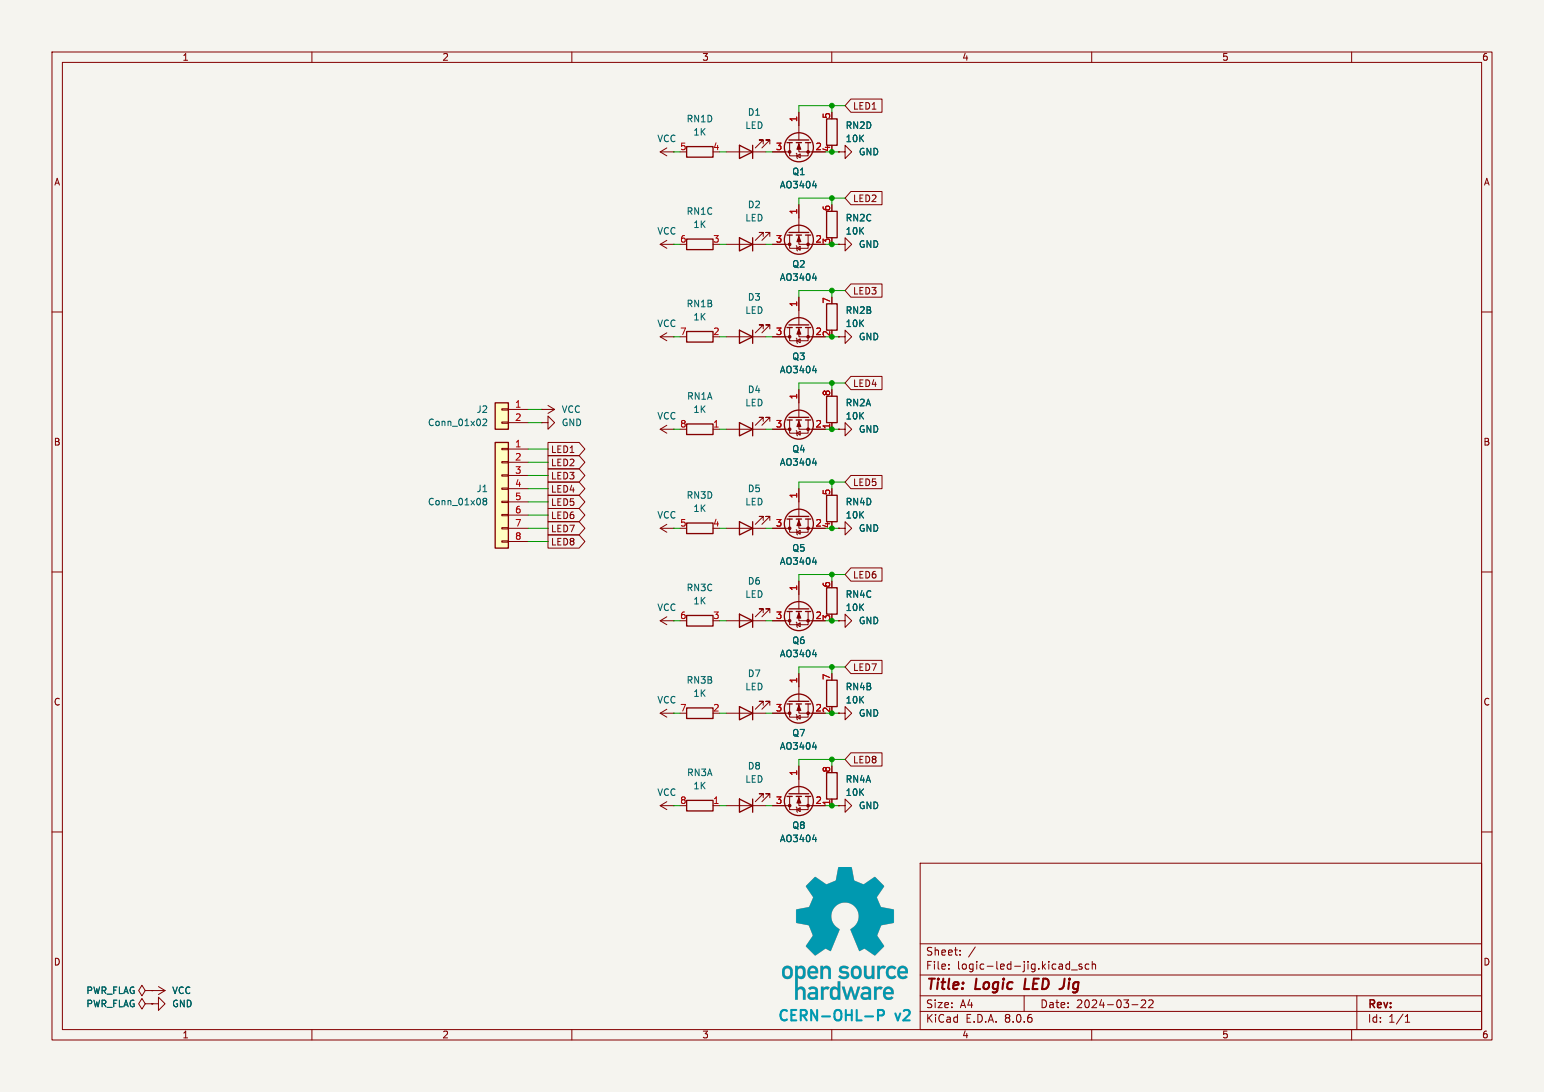
[picture p57: page 1]

Id: 1/1 Title: Logic LED Jig
