smkent/pcb/pcb/jigs/neopixel-micro/fab/neopixel-micro-schematic.pdf

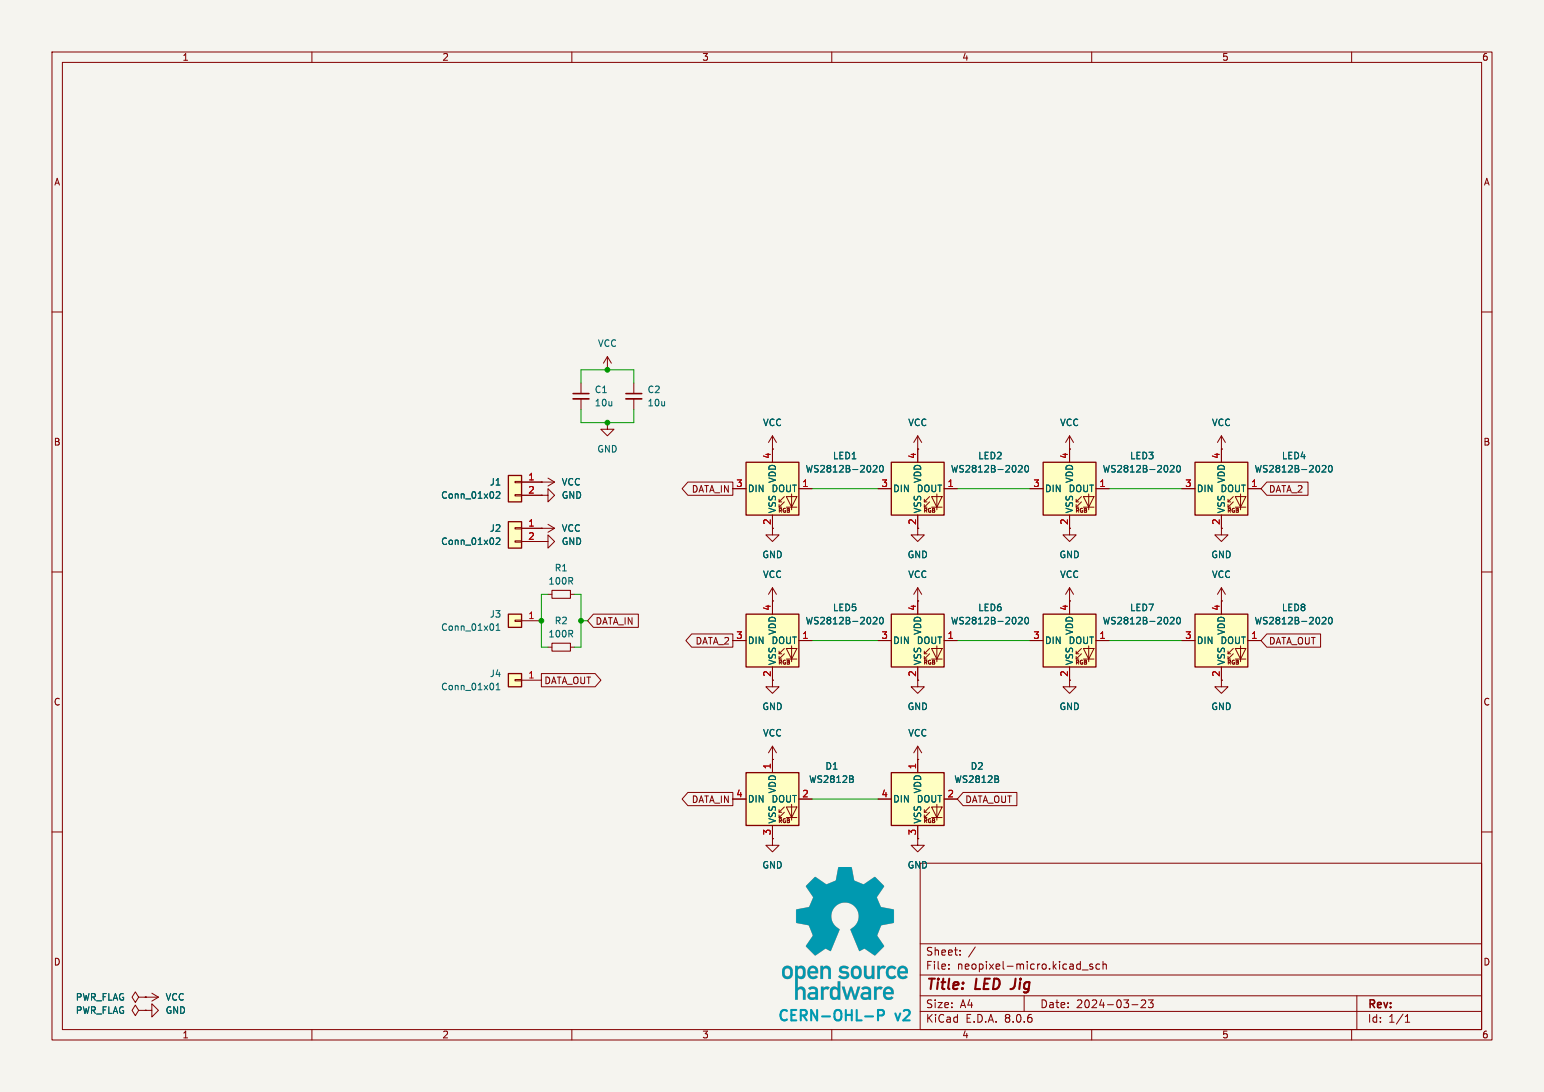
[picture p58: page 1]

File: neopixel-micro.kicad_sch Sheet: / GND

Id: 1/1 Title: LED Jig
