smkent/pcb/pcb/jigs/reflow-mini/fab/reflow-mini-schematic.pdf

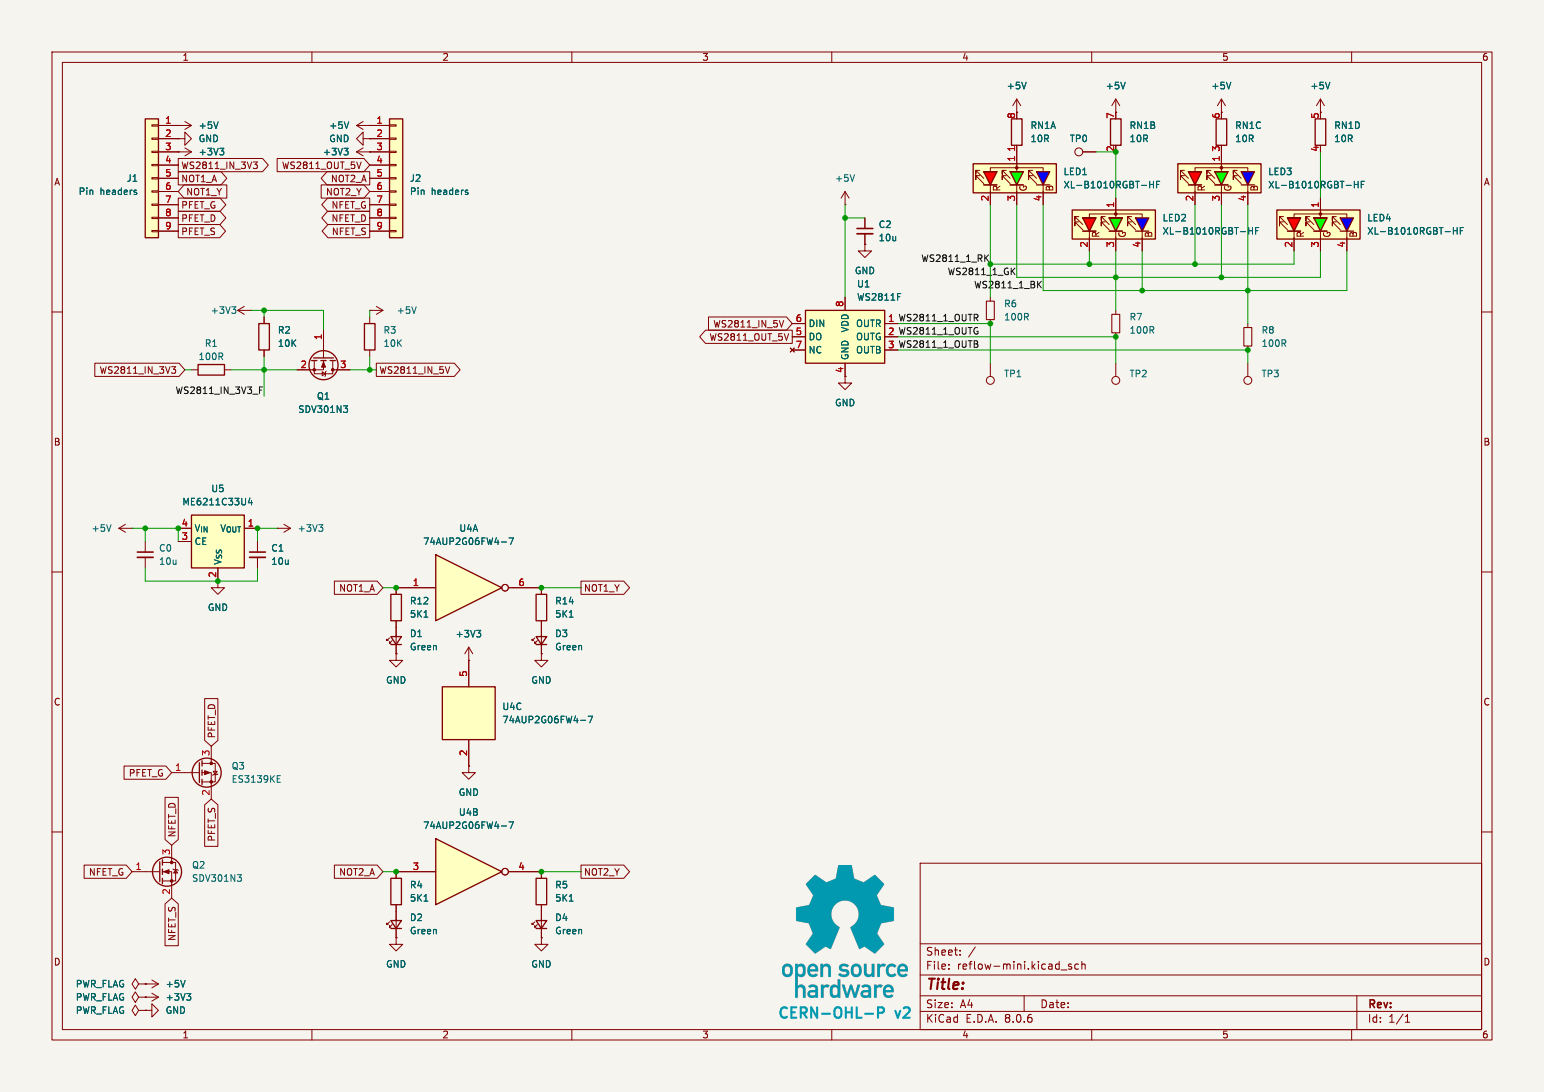
[picture p59: page 1]

4 DO 5 DIN 6 NC 7 VDD

Id: 1/1 Title: File: reflow-mini.kicad_sch Sheet: / R4
