smkent/pcb/pcb/jigs/shift-register-jig/fab/shift-register-jig-schematic.pdf

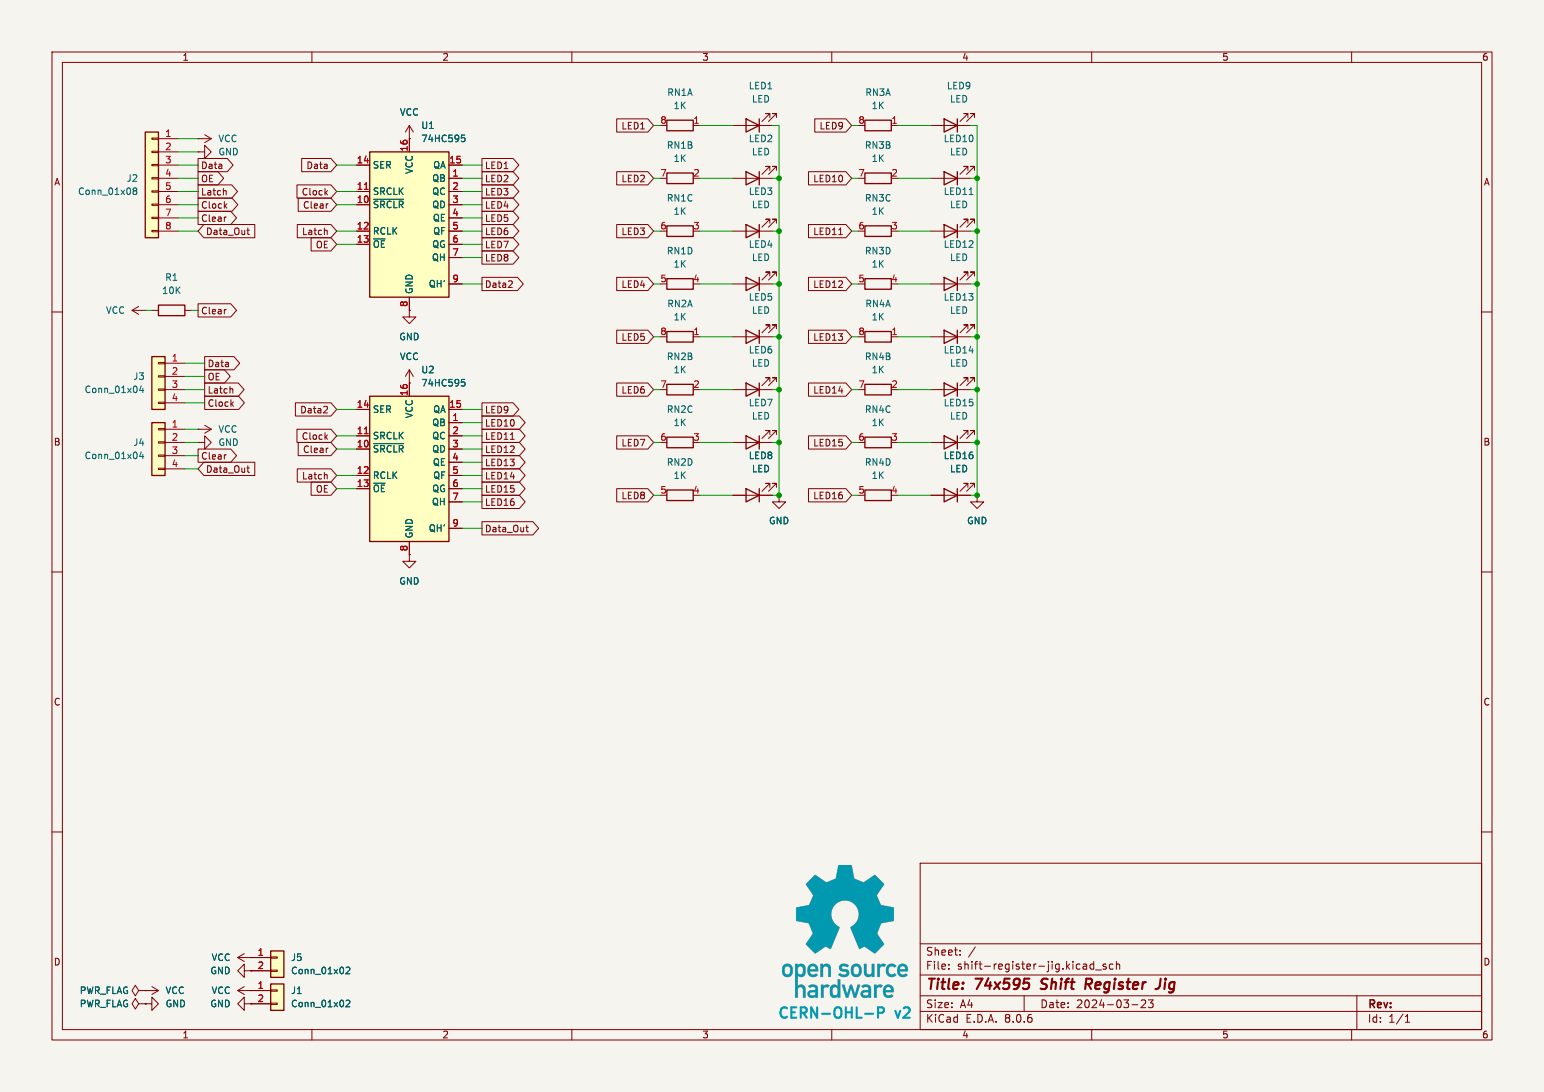
[picture p60: page 1]

8 QH' 9 VCC GND GND

File: shift-register-jig.kicad_sch Sheet: / PWR_FLAG
