smkent/pcb/pcb/misc/gr6408/fab/gr6408-schematic.pdf

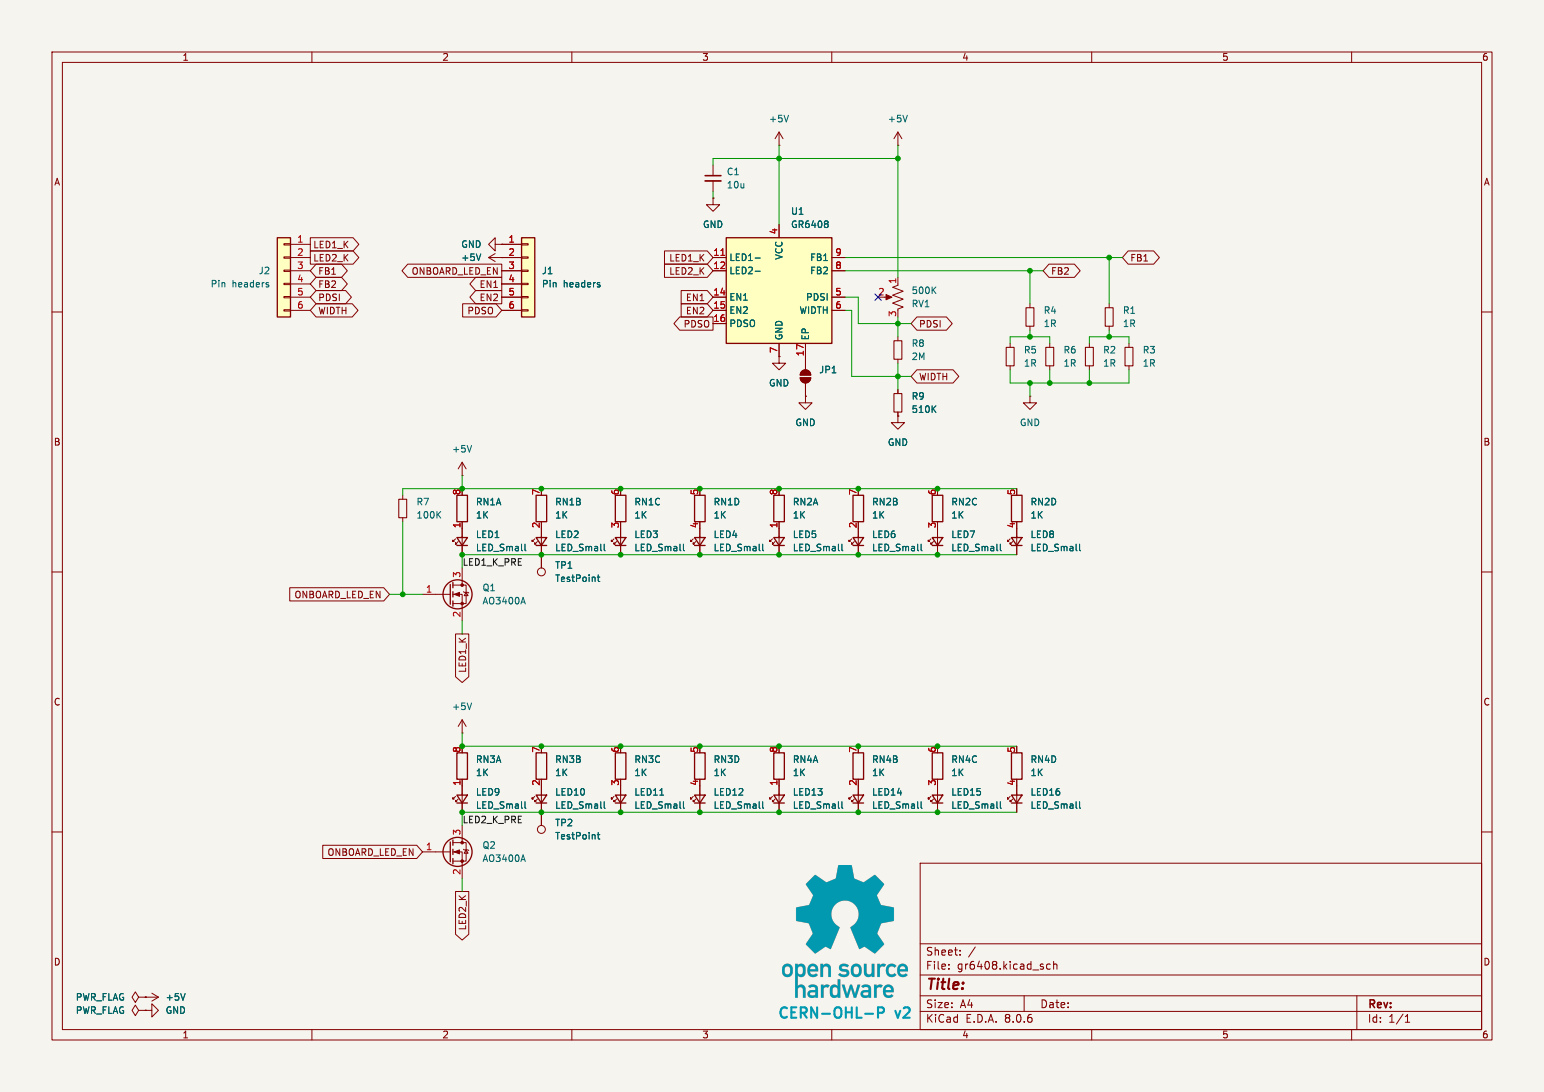
[picture p61: page 1]

Id: 1/1 Title: File: gr6408.kicad_sch Sheet: /
