smkent/pcb/pcb/misc/usb-pd-decoy-husb238/fab/usb-pd-decoy-husb238-schematic.pdf

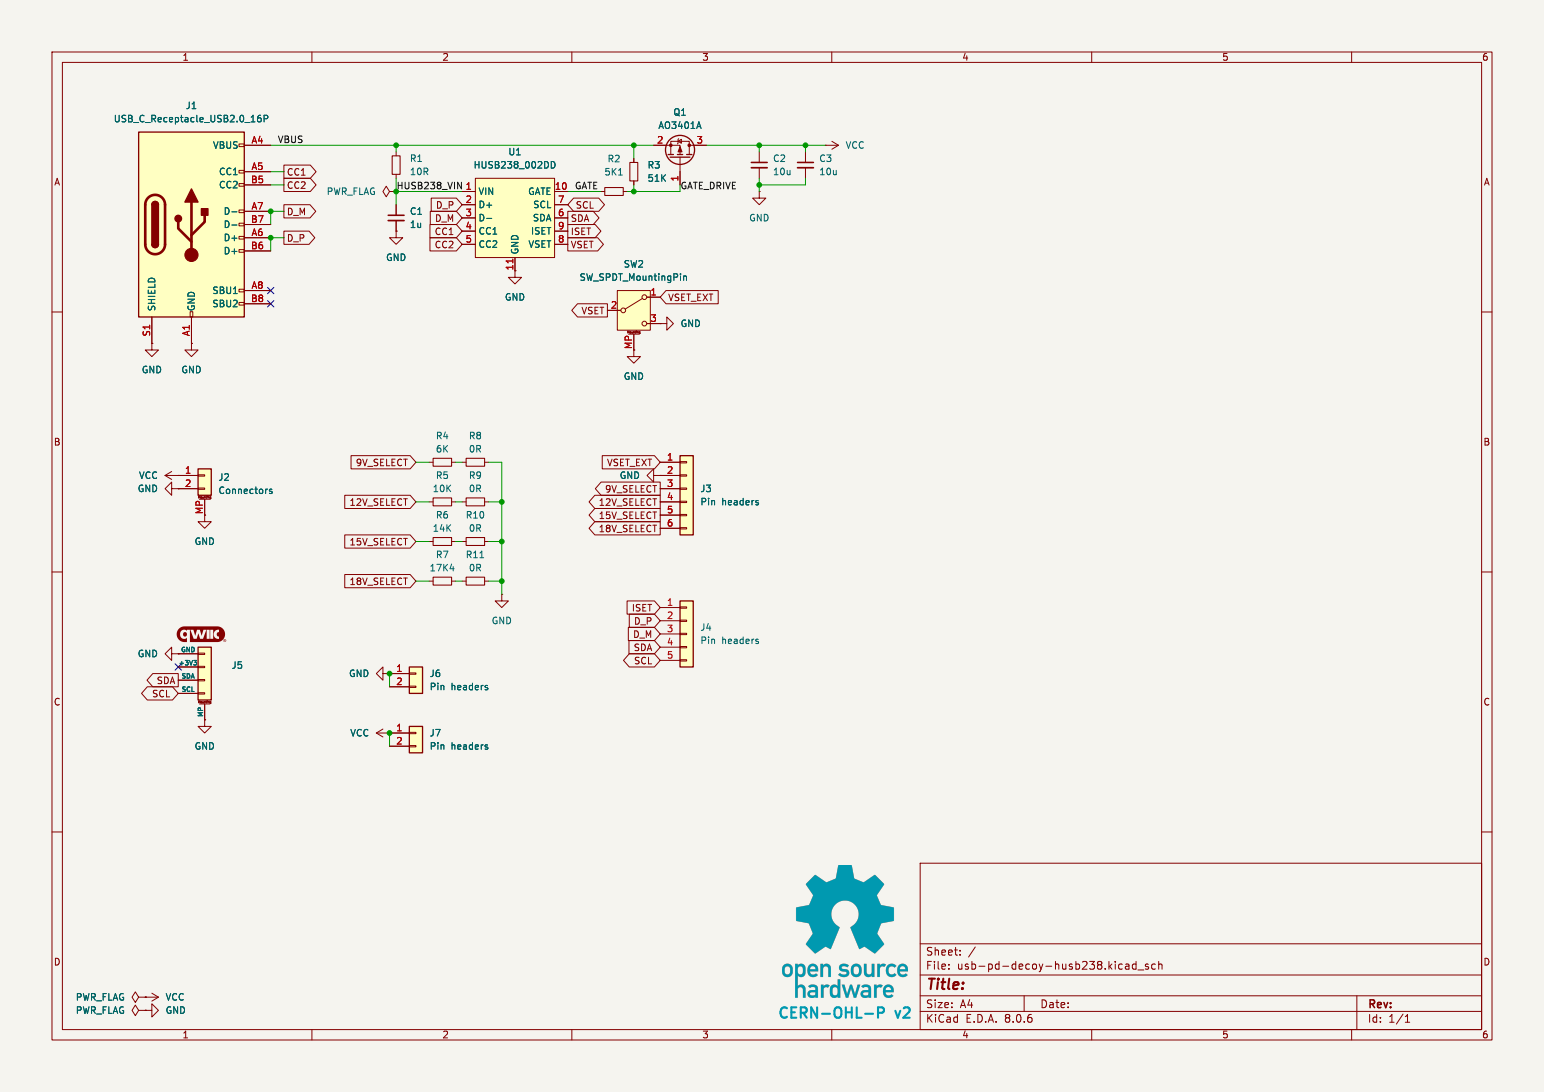
[picture p62: page 1]

Id: 1/1 Title: File: usb-pd-decoy-husb238.kicad_sch Sheet: /
