smkent/pcb/pcb/power/buck-tps563201/fab/buck-tps563201-schematic.pdf

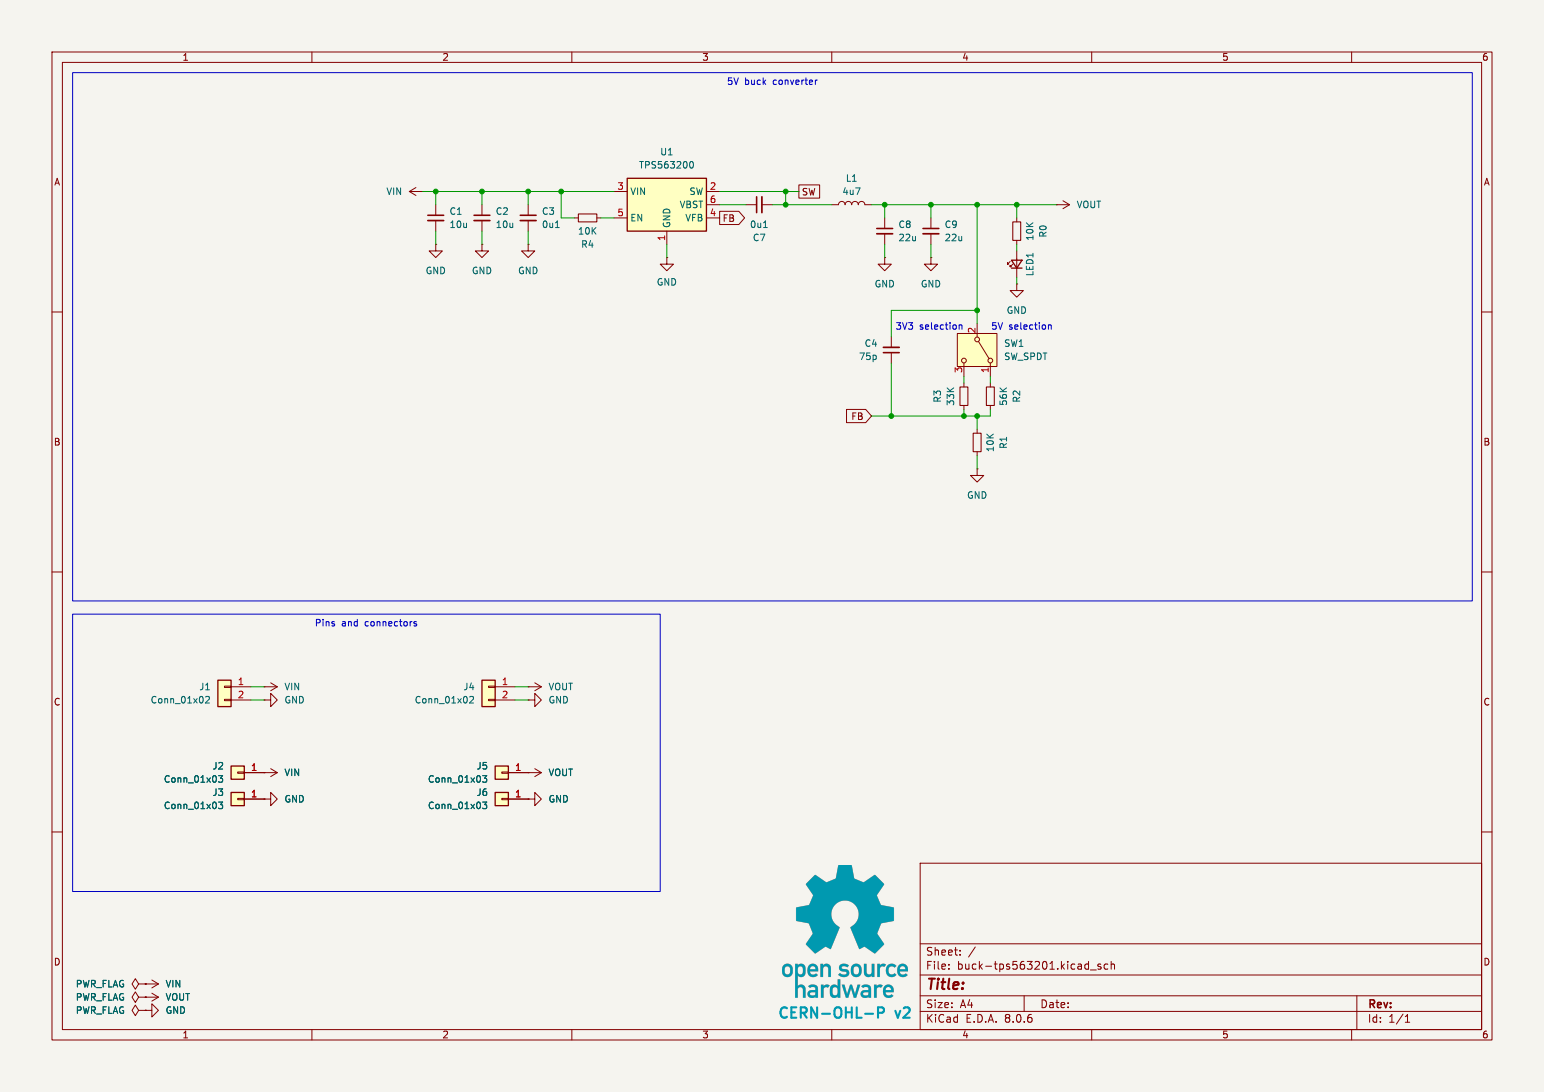
[picture p63: page 1]

1 SW 2 VIN 3 VFB 4 EN 5 VBST 6 U1 TPS563200 VIN

3V3 selection Pins and connectors

Id: 1/1 Title: File: buck-tps563201.kicad_sch Sheet: /
