smkent/pcb/pcb/power/eta6003/fab/eta6003-schematic.pdf

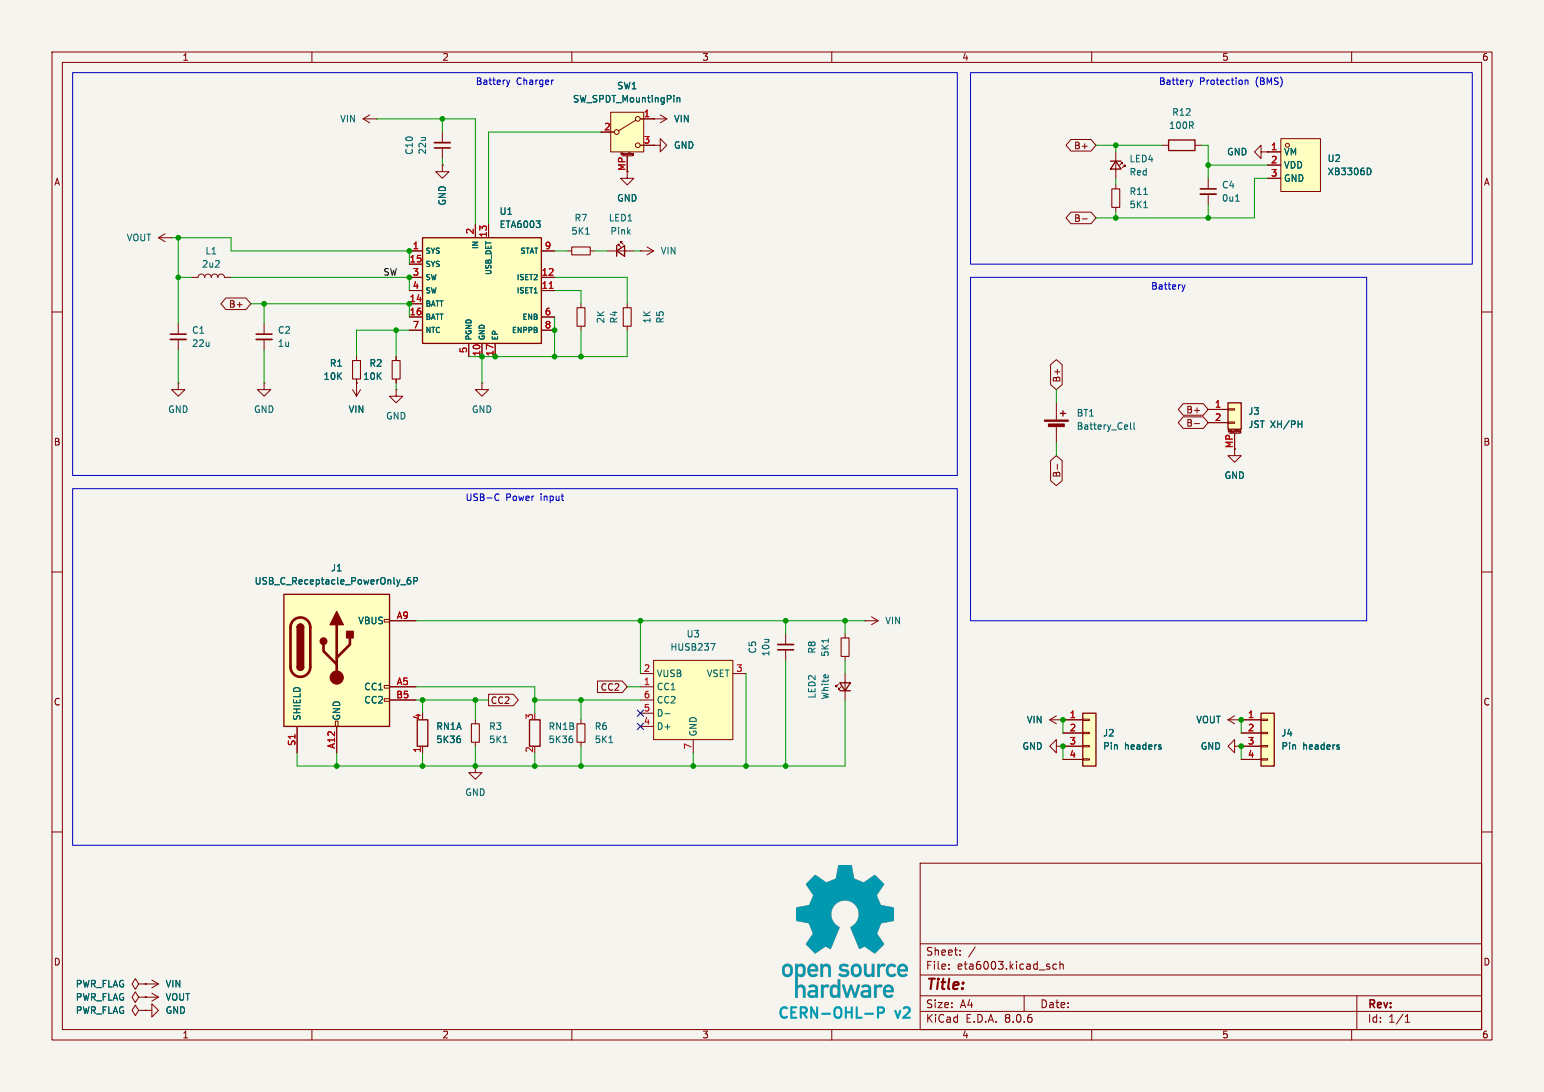
[picture p64: page 1]

Battery USB-C Power input

Id: 1/1 Title: File: eta6003.kicad_sch Sheet: /
