smkent/pcb/pcb/power/max17048/fab/max17048-schematic.pdf

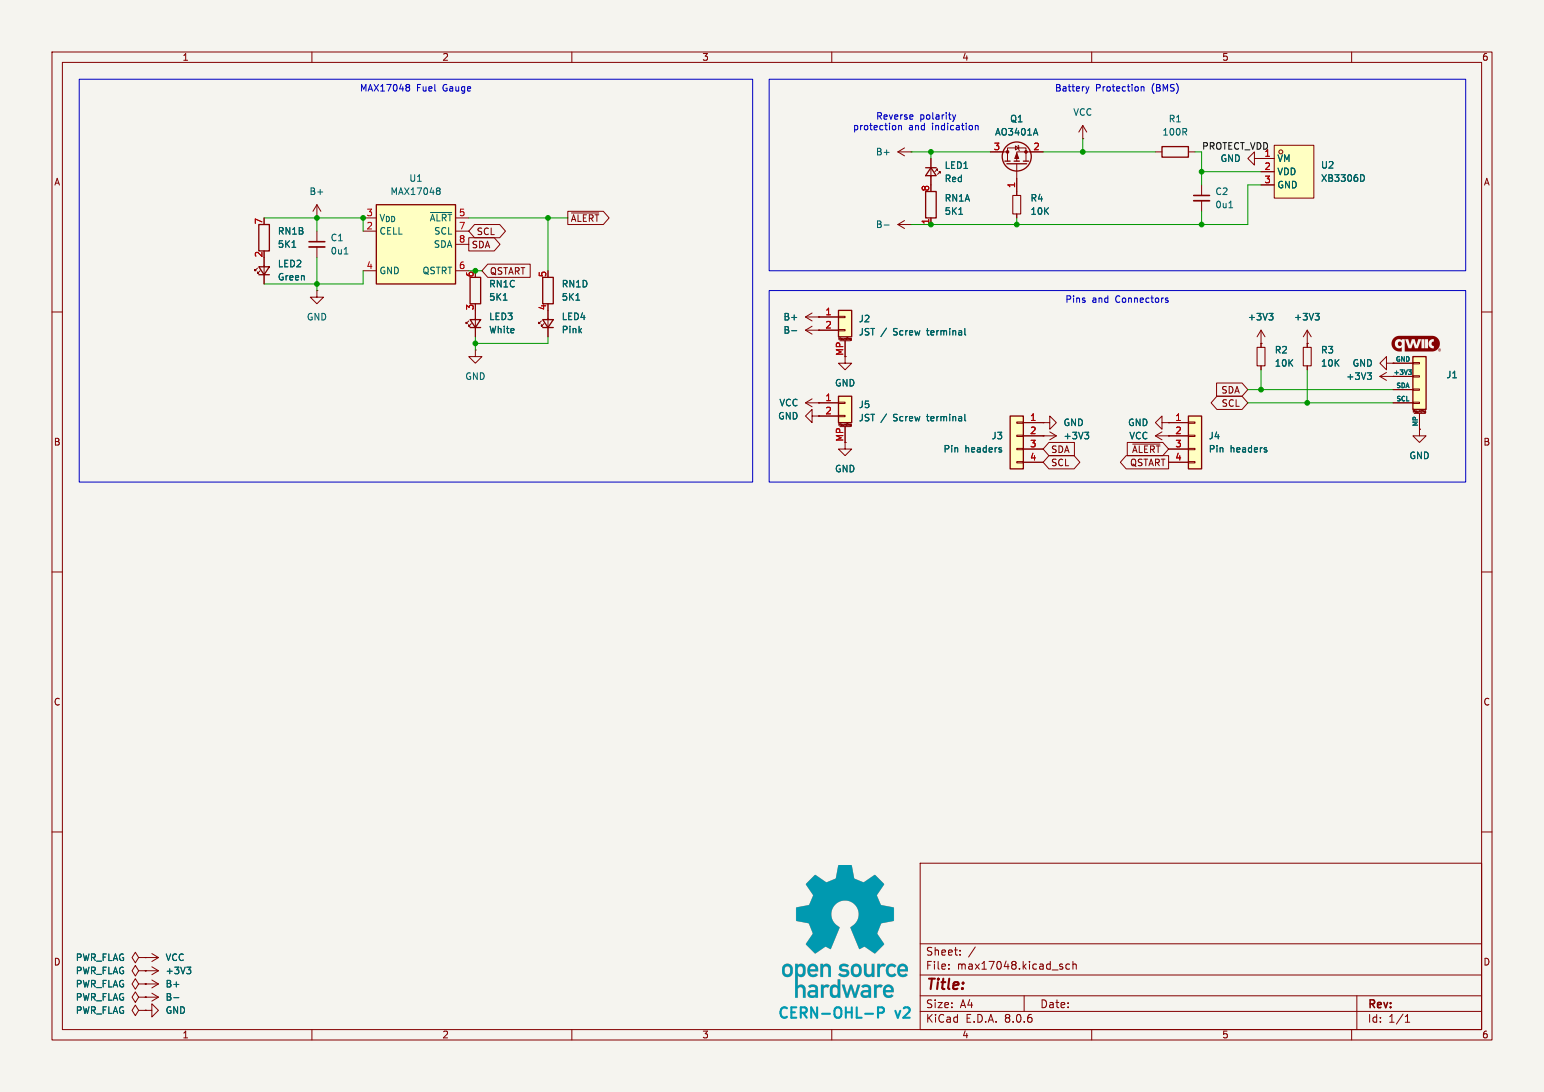
[picture p65: page 1]

Id: 1/1 Title: File: max17048.kicad_sch Sheet: /
