smkent/pcb/pcb/power/microbuck/fab/microbuck-schematic.pdf

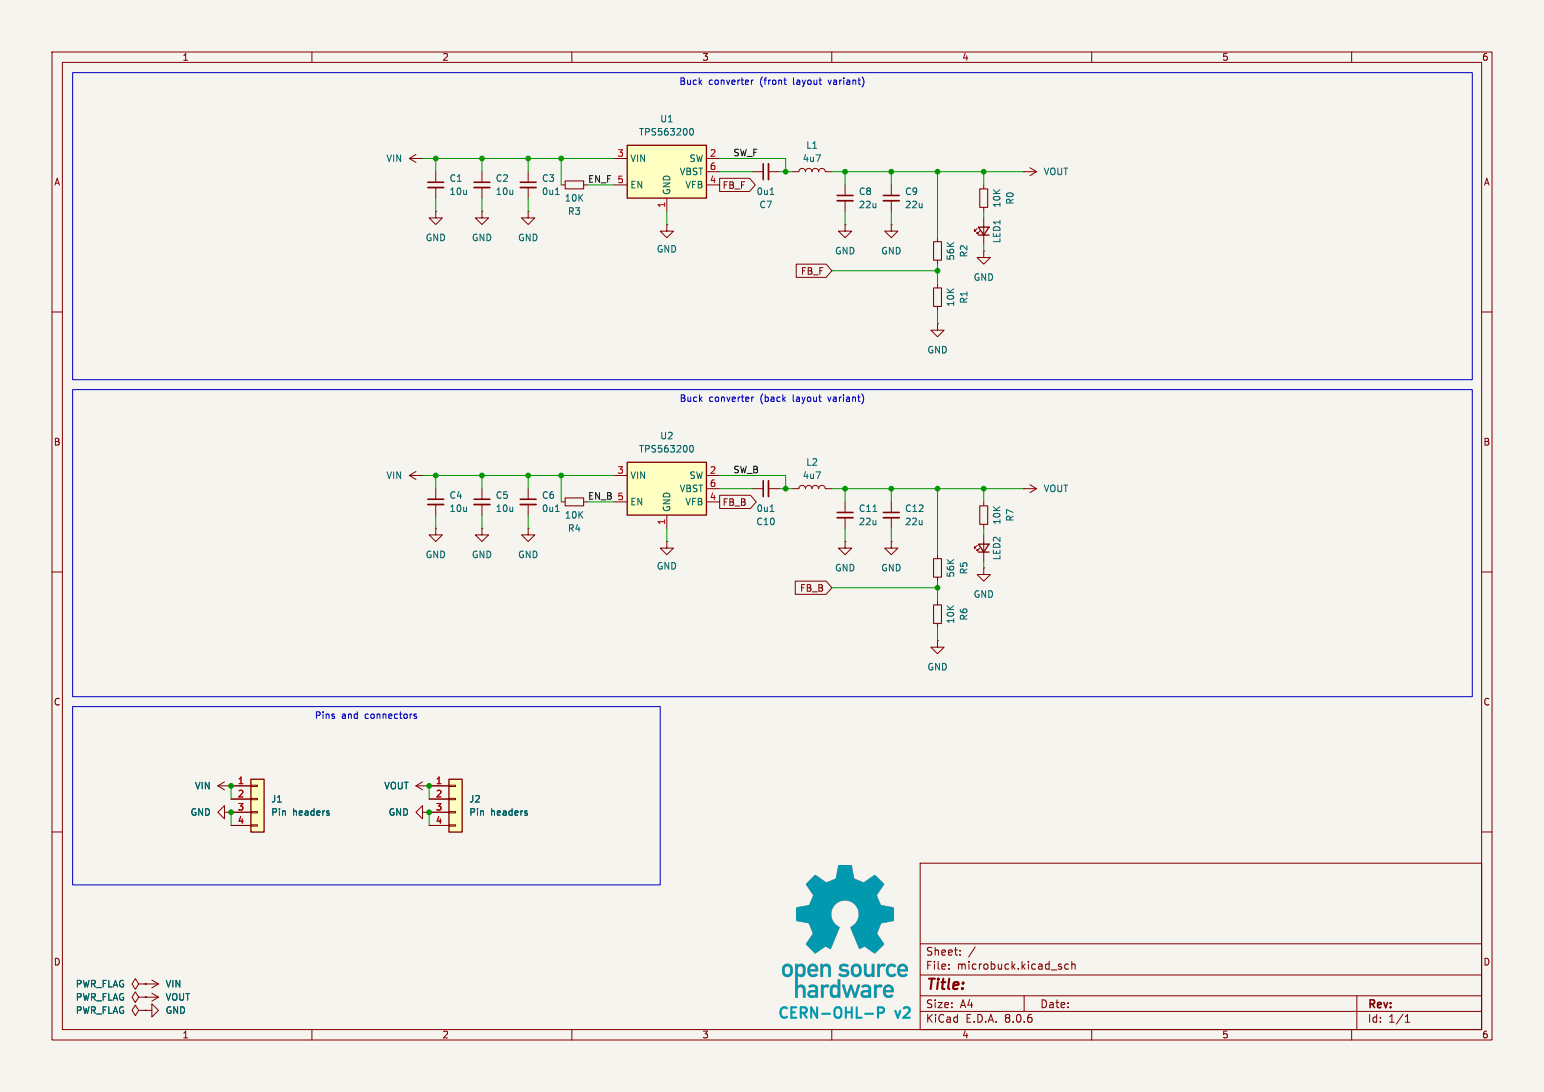
[picture p66: page 1]

1 SW 2 VIN 3 VFB 4 EN 5 VBST 6 U1 TPS563200 GND

1 SW 2 VIN 3 VFB 4 EN 5 VBST 6 U2 TPS563200 GND GND GND
