smkent/pcb/pcb/stackable2/esp-lcd-dev/fab/esp-lcd-dev-schematic.pdf

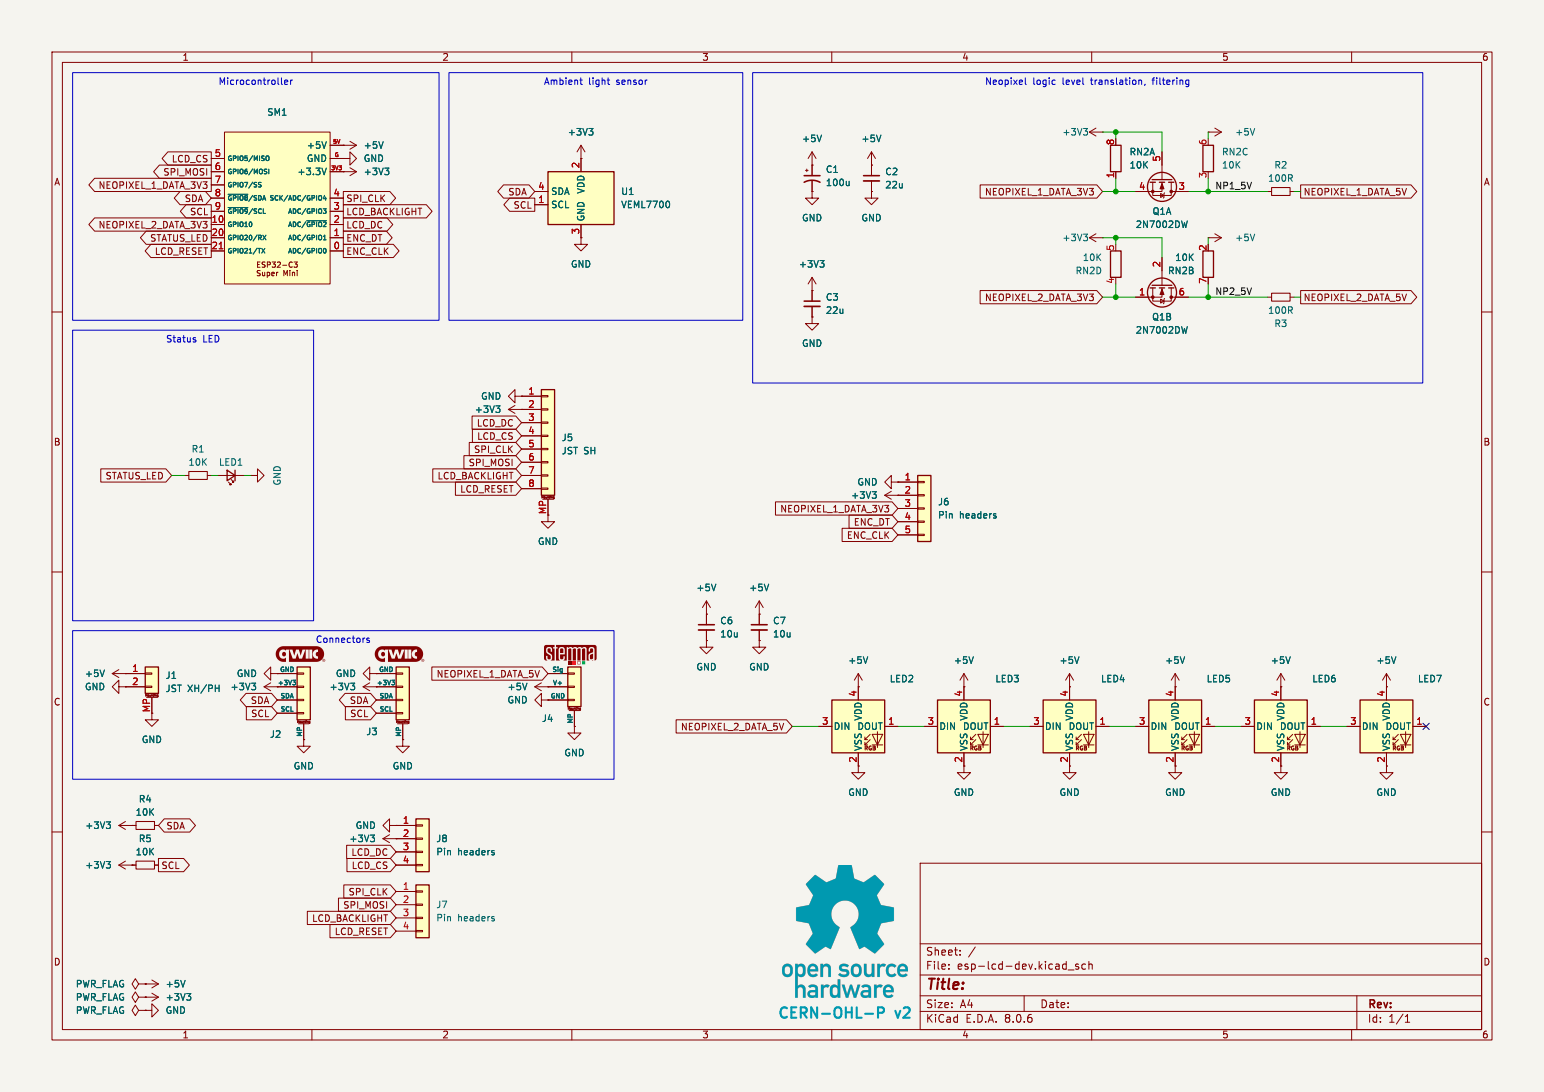
[picture p67: page 1]

10u GND GND
Sig V+ GND MP GND
