smkent/pcb/pcb/stackable2/lcd-round/fab/lcd-round-schematic.pdf

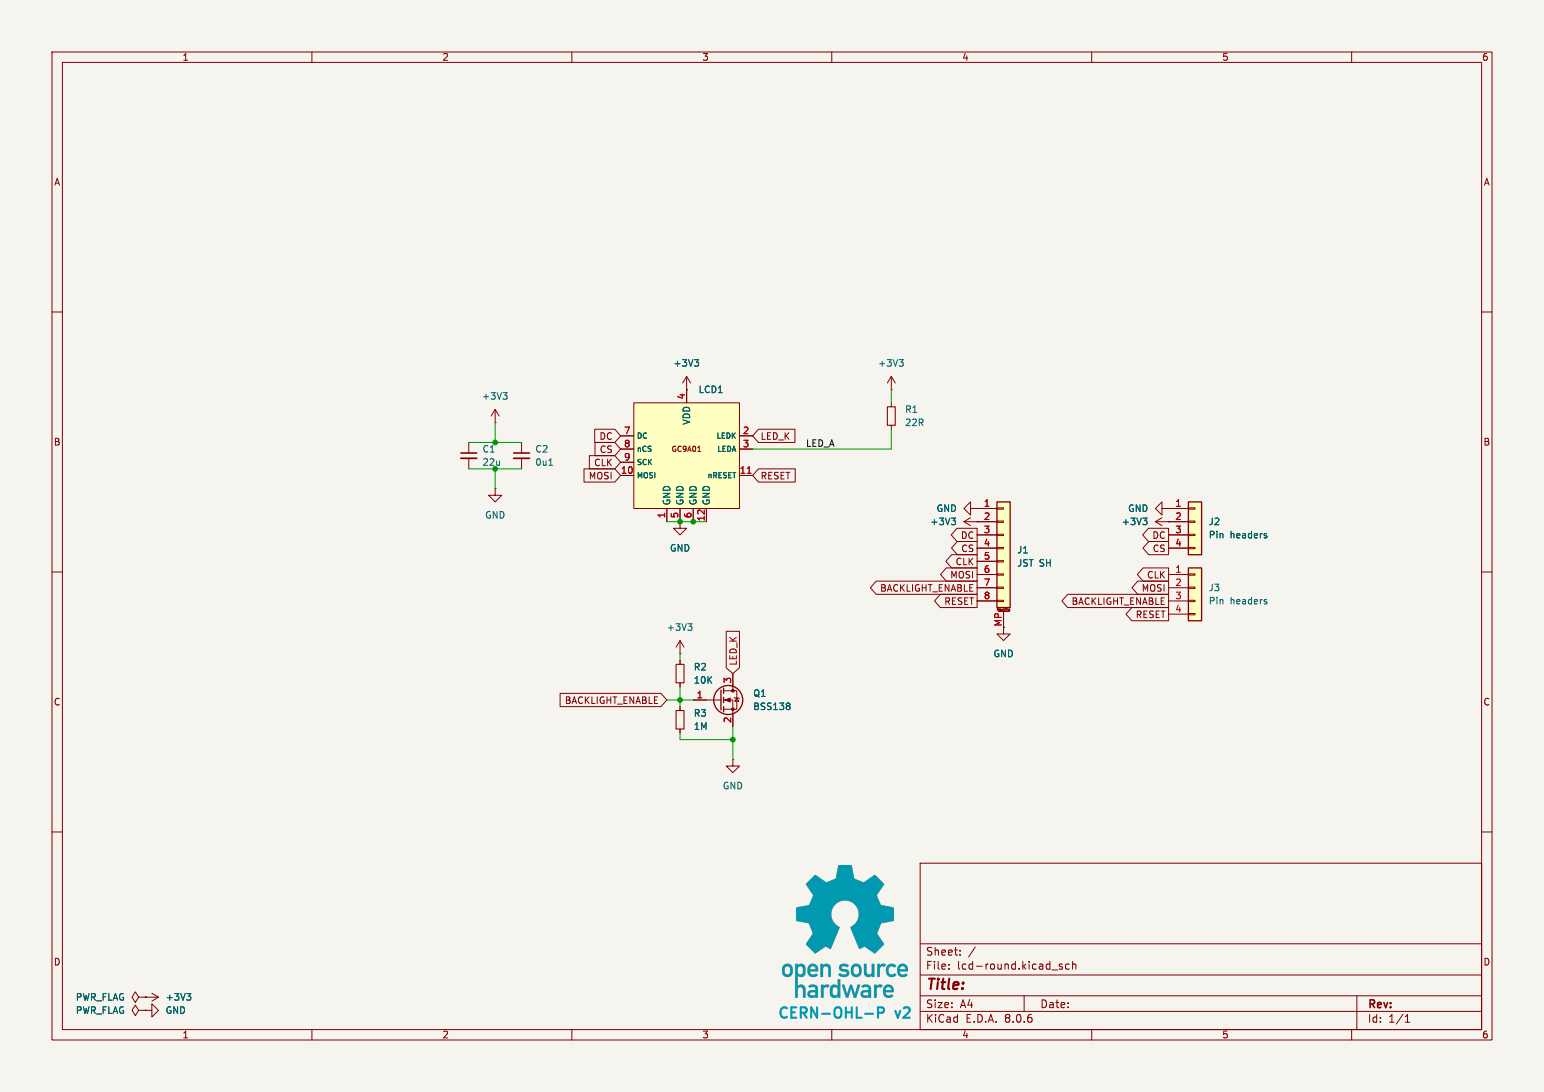
[picture p68: page 1]

Id: 1/1 Title: File: lcd-round.kicad_sch Sheet: / GND
