smkent/pcb/pcb/jigs/555-timer/fab/555-timer-schematic.pdf

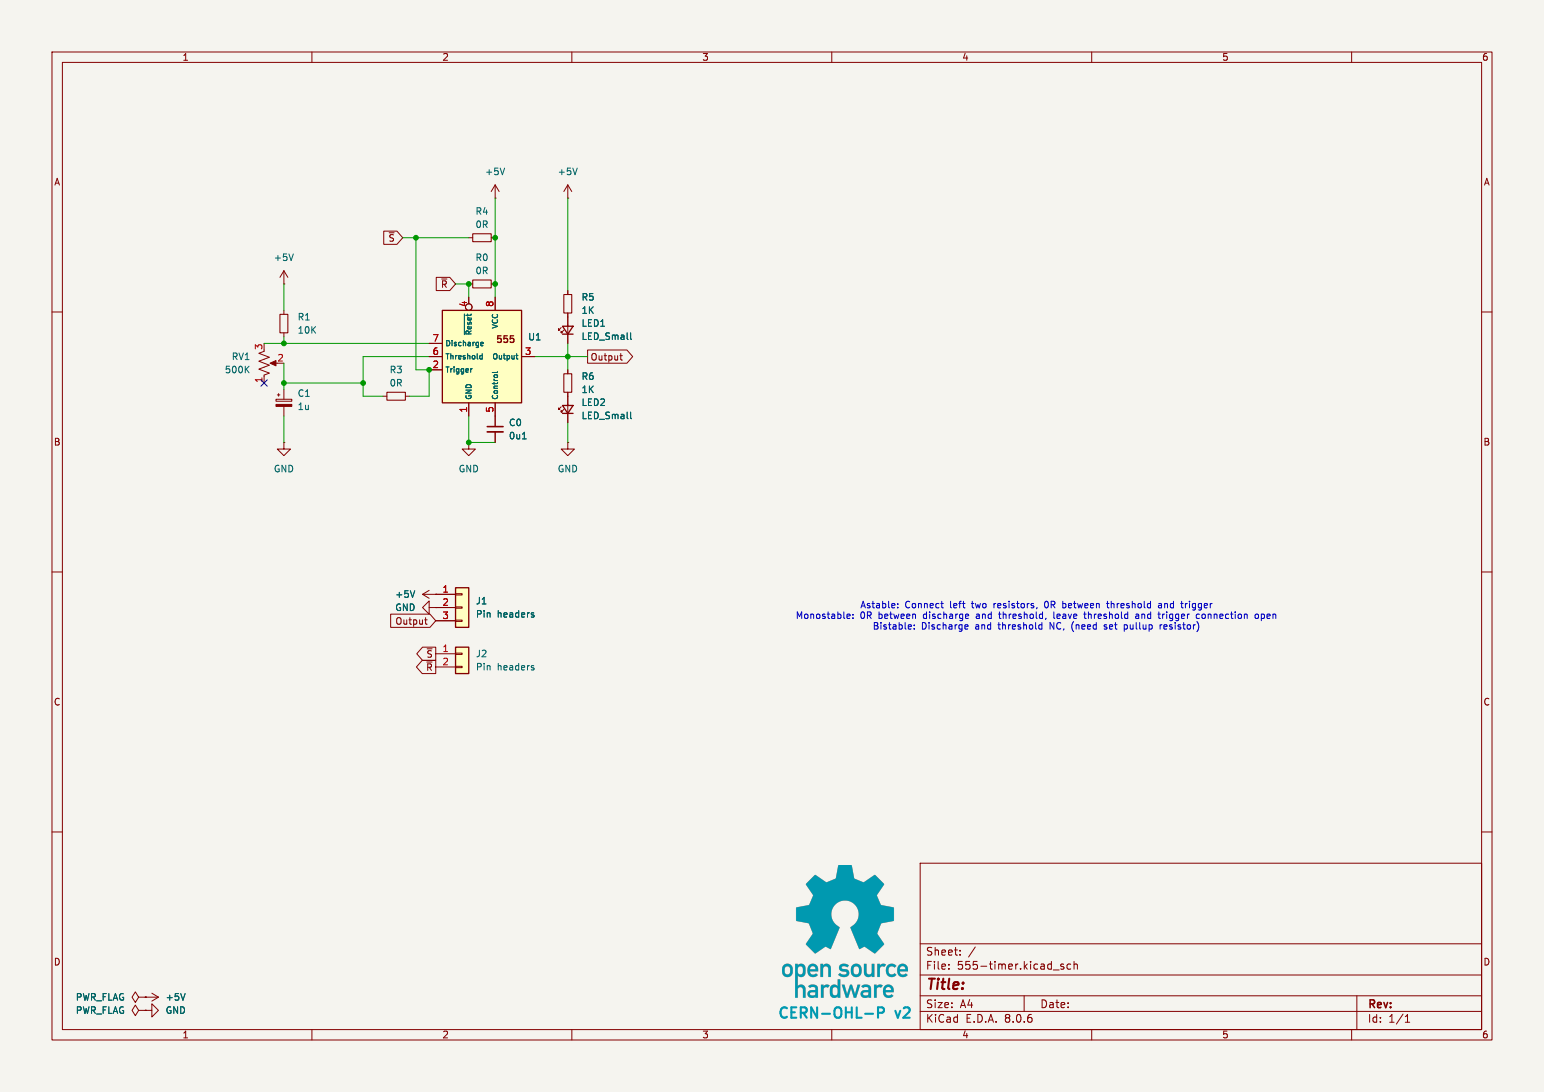
[picture p70: page 1]
