smkent/pcb/dev/power/tp4056-5v-ups/fab/tp4056-5v-ups-schematic.pdf

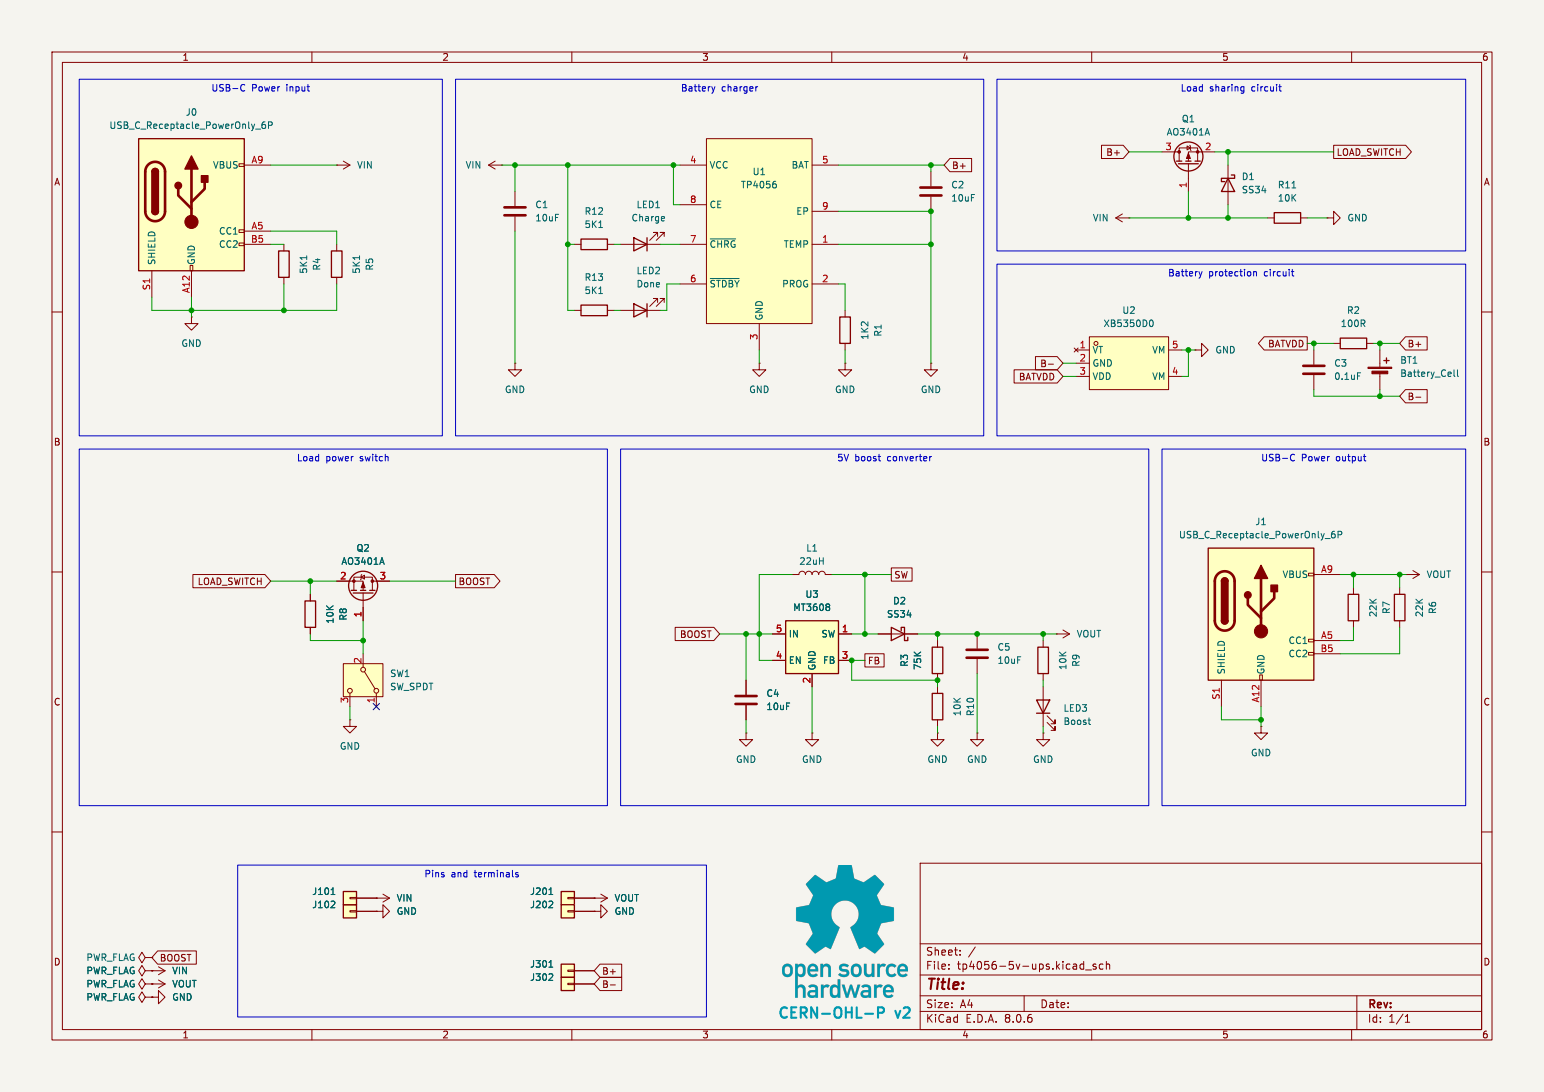
[picture p71: page 1]

3 VCC 4 BAT 5 ~{STDBY} 6 ~{CHRG} 7 CE 8 EP 9 U1 TP4056
