smkent/pcb/dev/stackable/relay-module-5v-x2/fab/relay-module-5v-x2-schematic.pdf

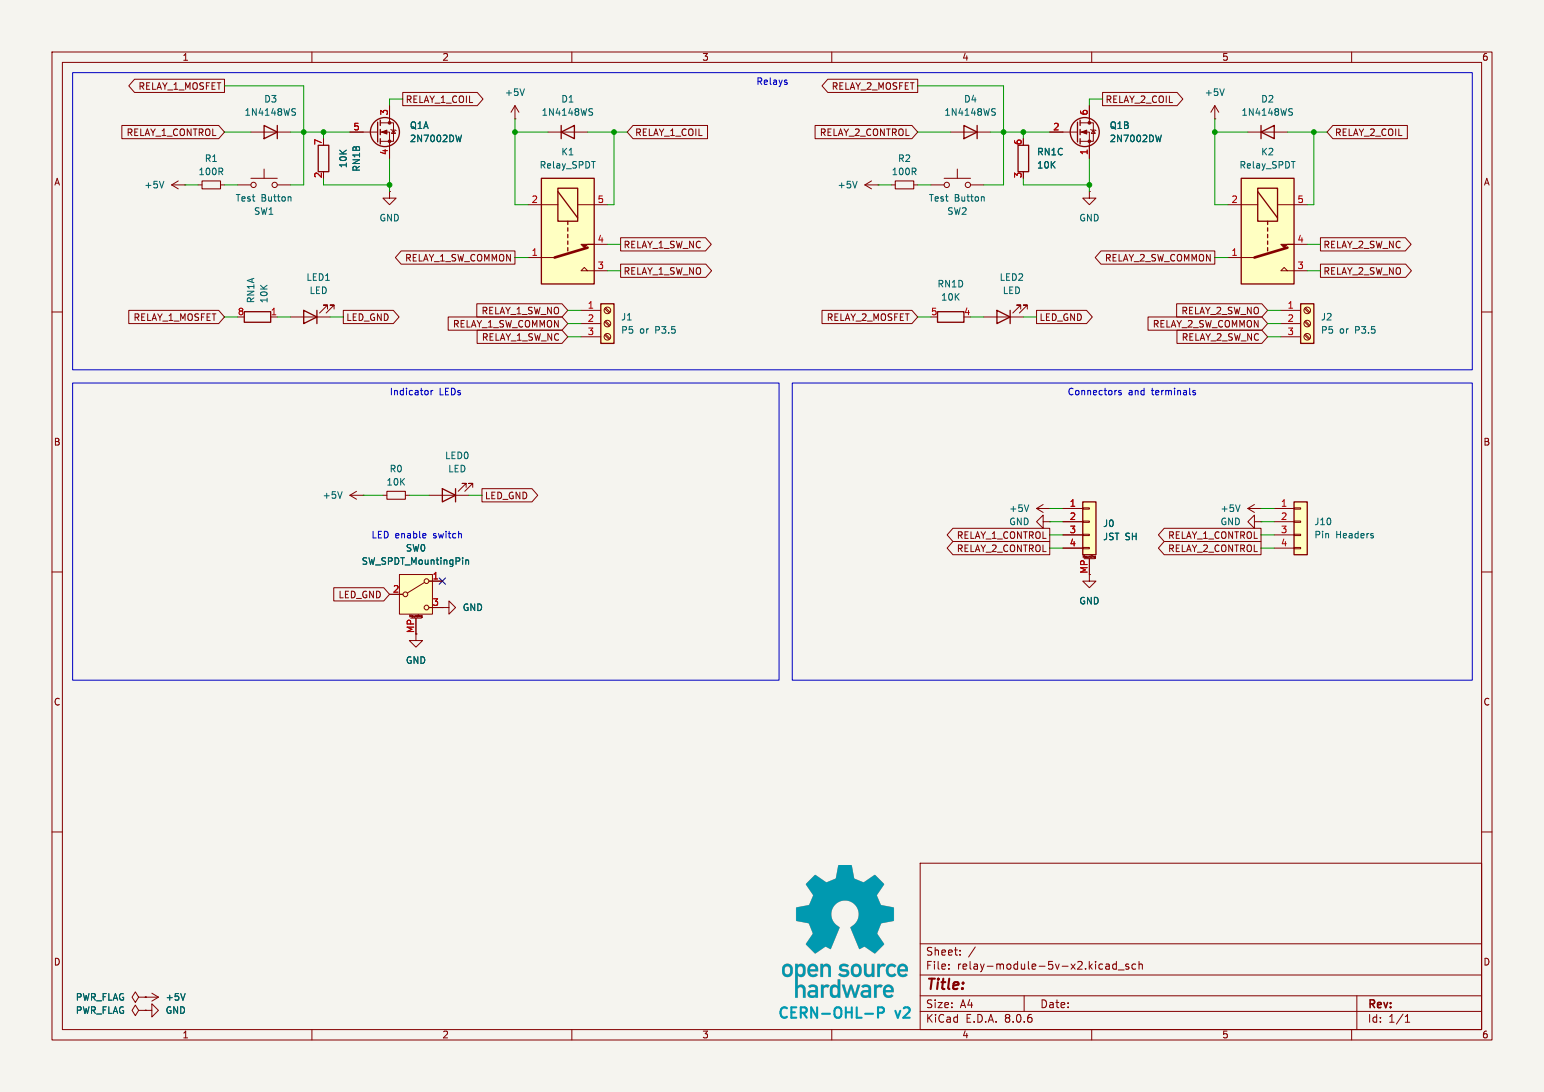
[picture p72: page 1]
