smkent/pcb/pcb/jigs/smd-mosfet/fab/smd-mosfet-schematic.pdf

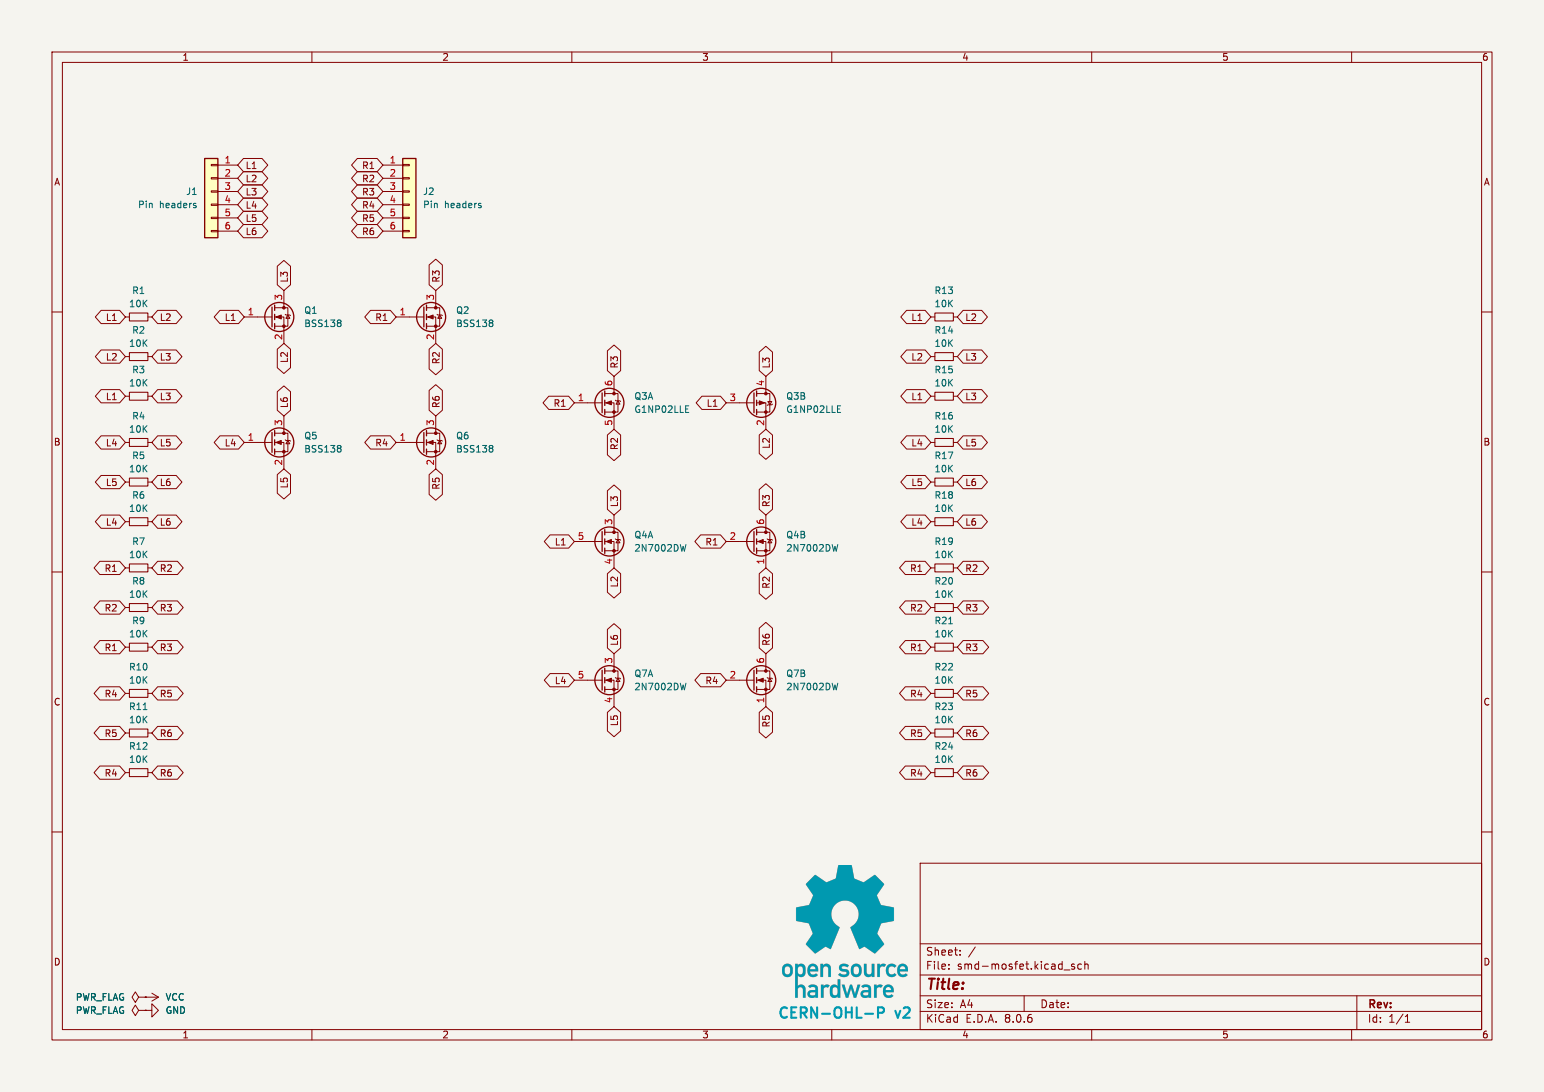
[picture p73: page 1]
