smkent/pcb/pcb/misc/usb-pd-decoy-husb237/fab/usb-pd-decoy-husb237-schematic.pdf

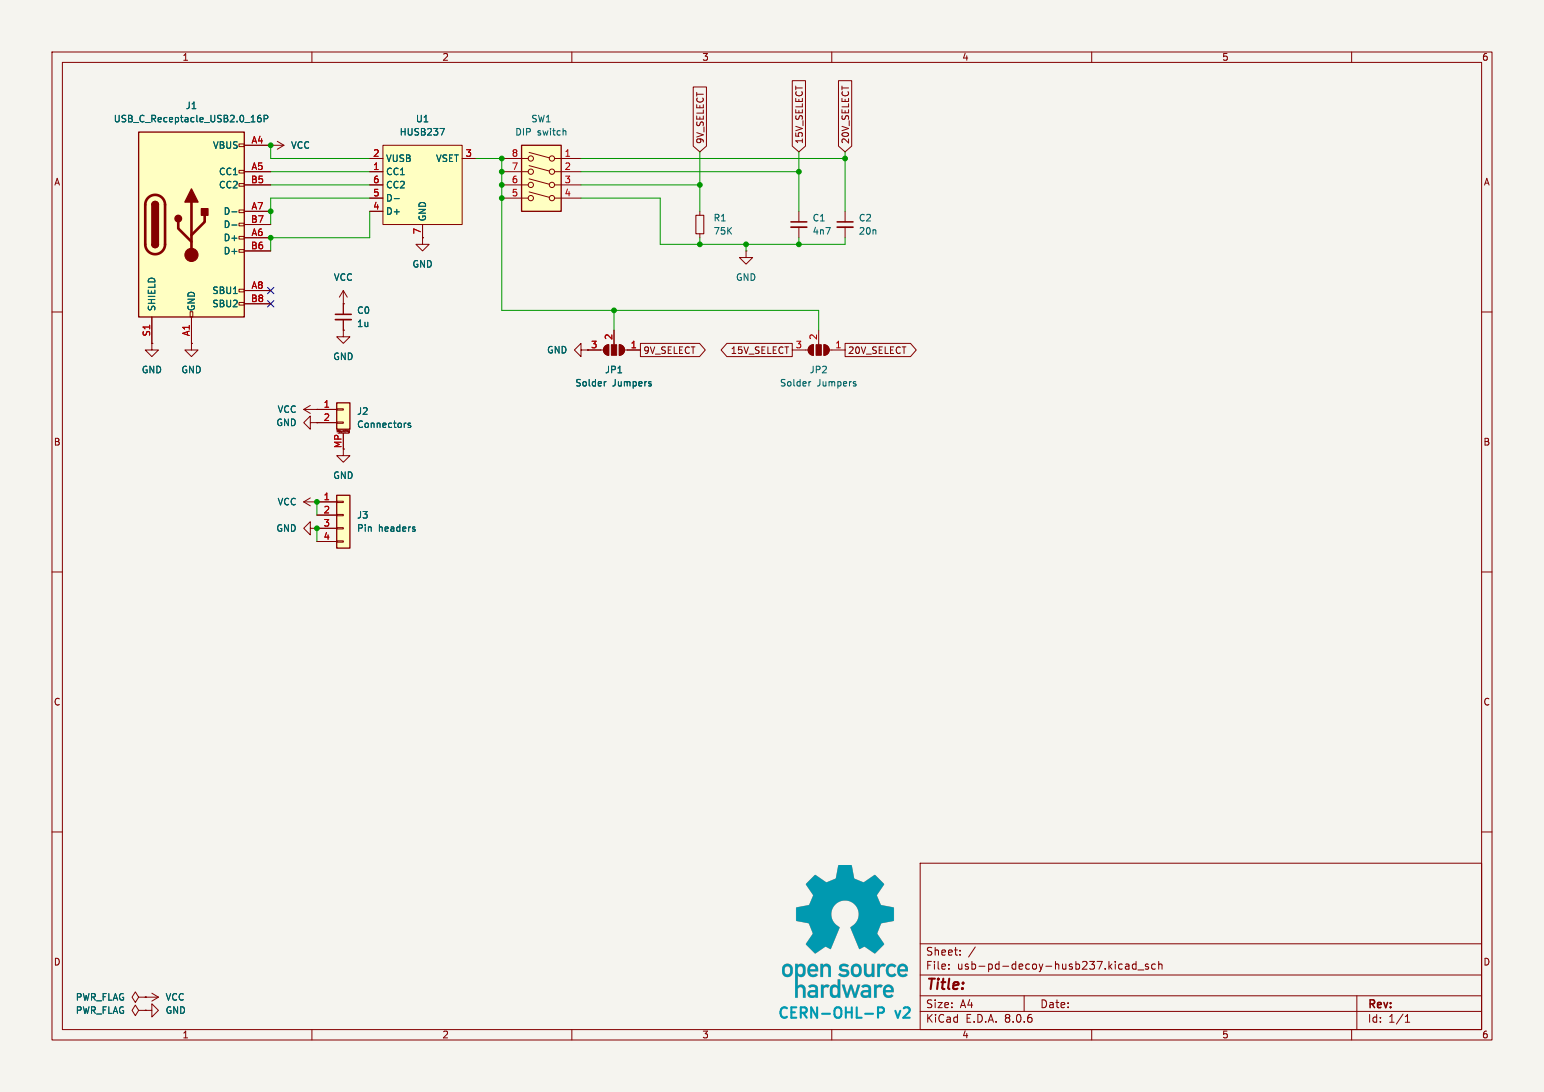
[picture p74: page 1]
