smkent/pcb/pcb/power/eta-buck/fab/eta-buck-schematic.pdf

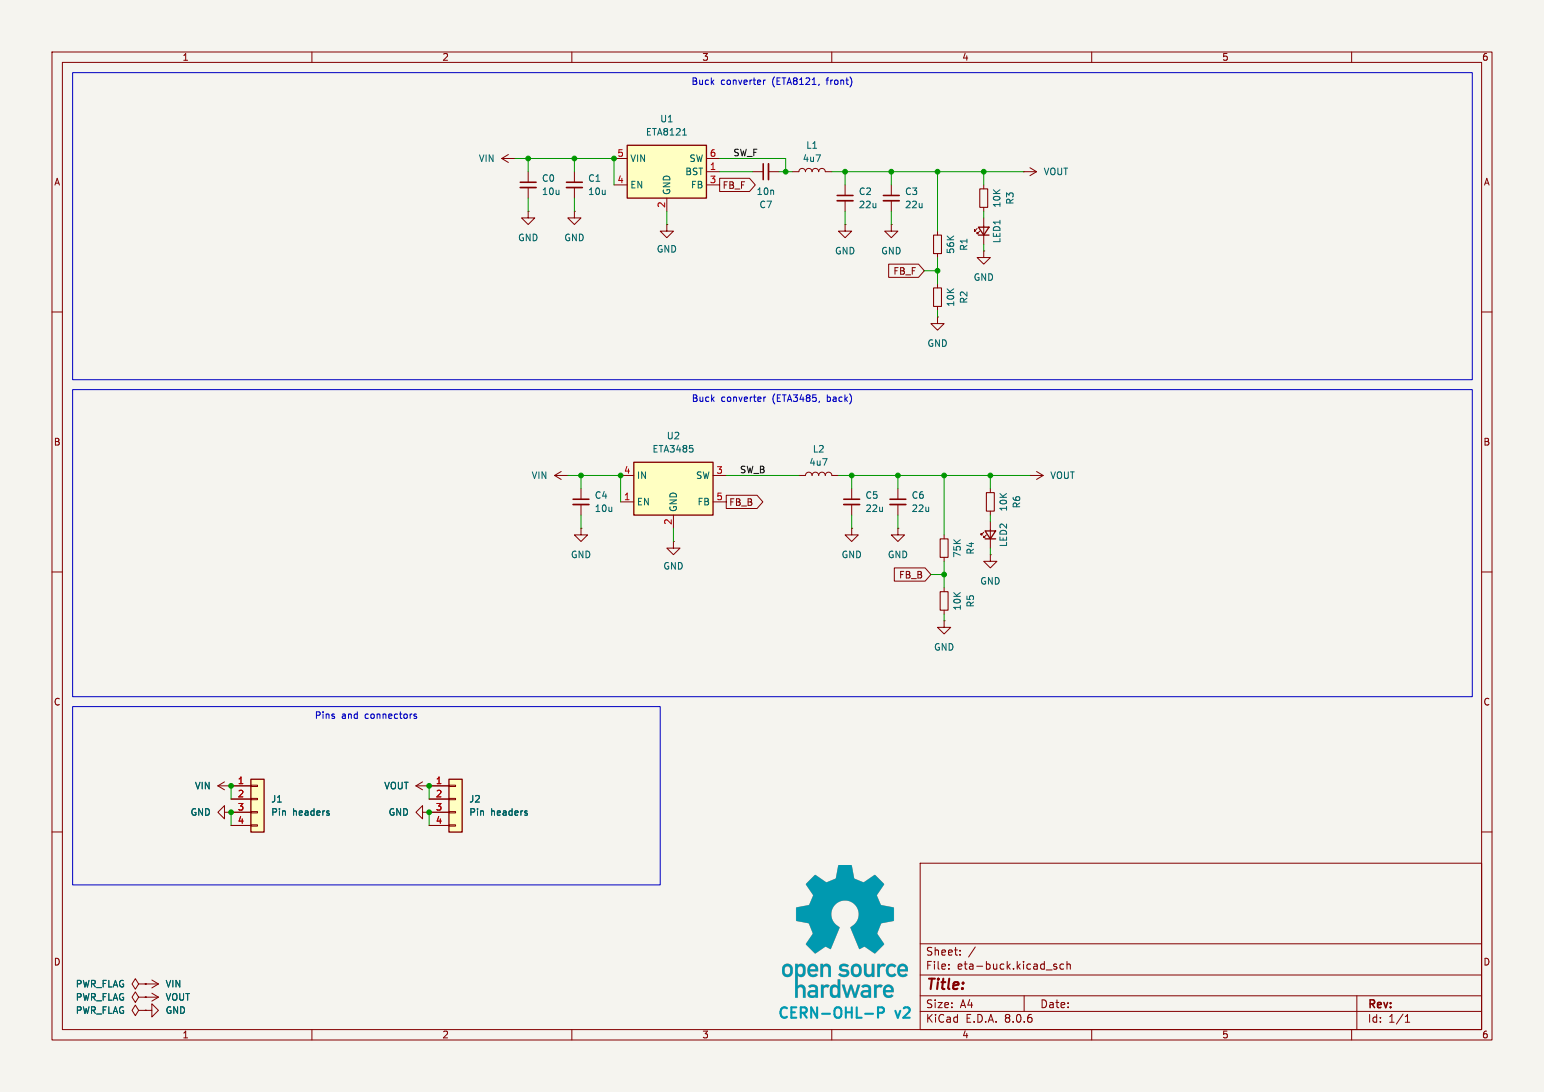
[picture p75: page 1]

2 FB 3 EN 4 VIN 5 SW 6 U1 ETA8121 R2 10K
