smkent/pcb/pcb/power/microboost/fab/microboost-schematic.pdf

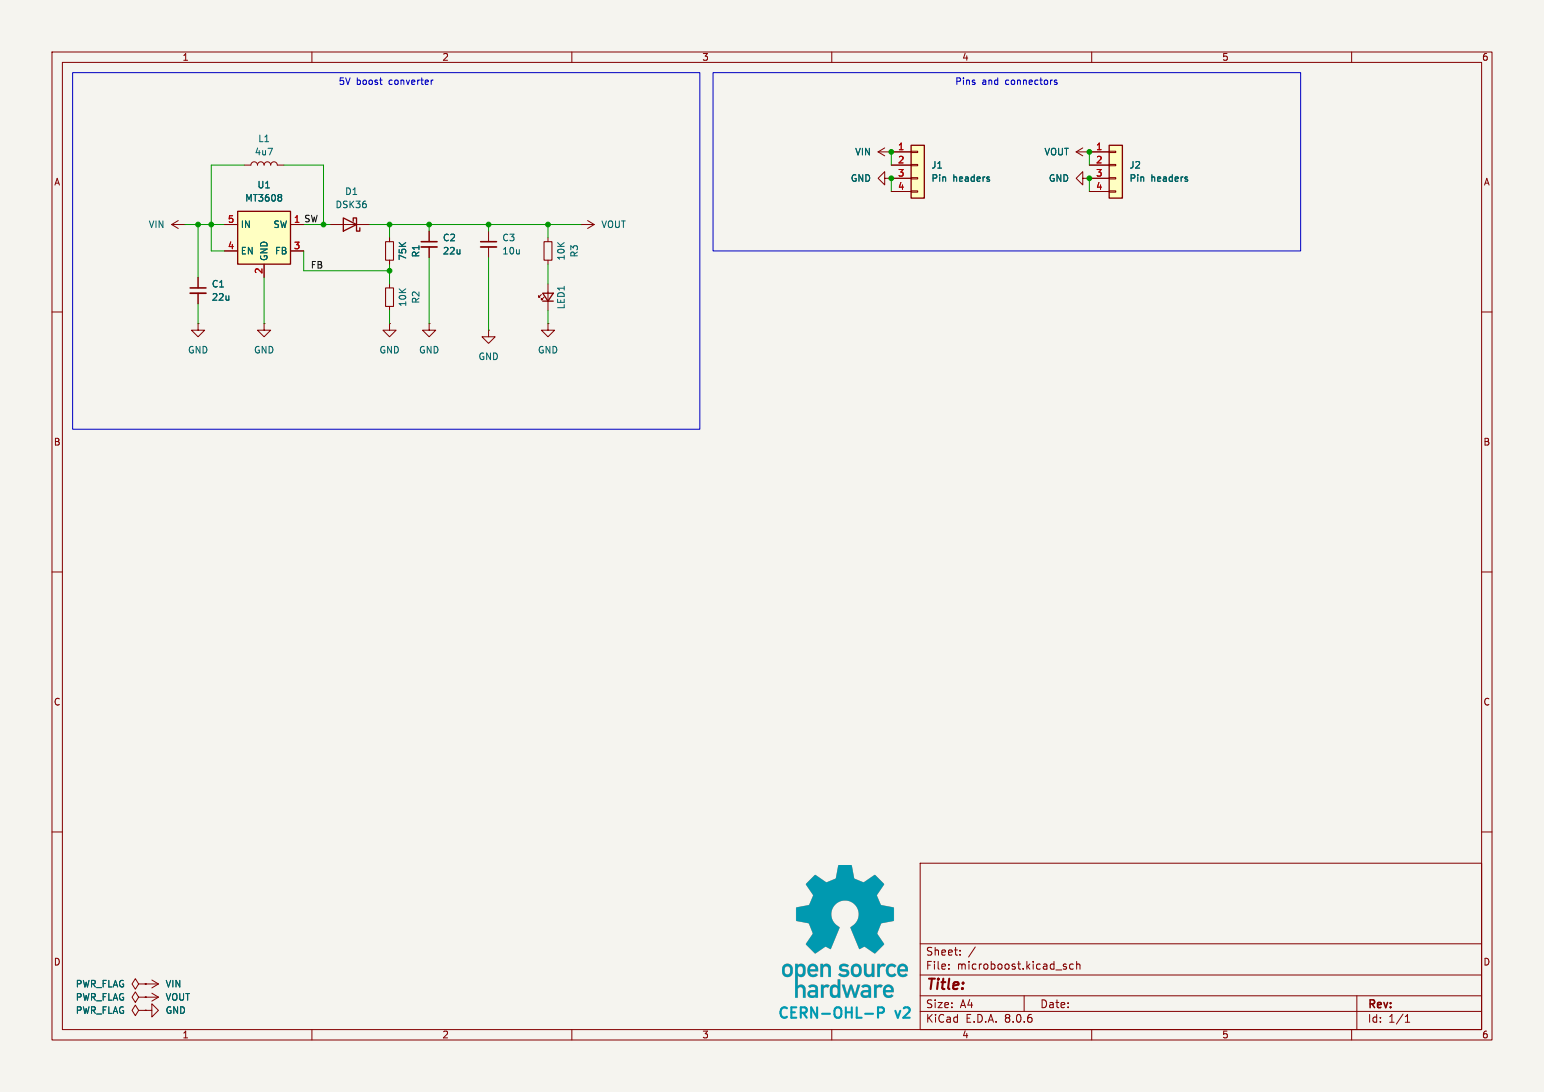
[picture p76: page 1]
