smkent/pcb/pcb-archived/stackable2/esp-neopixel-driver/fab/esp-neopixel-driver-schematic.pdf

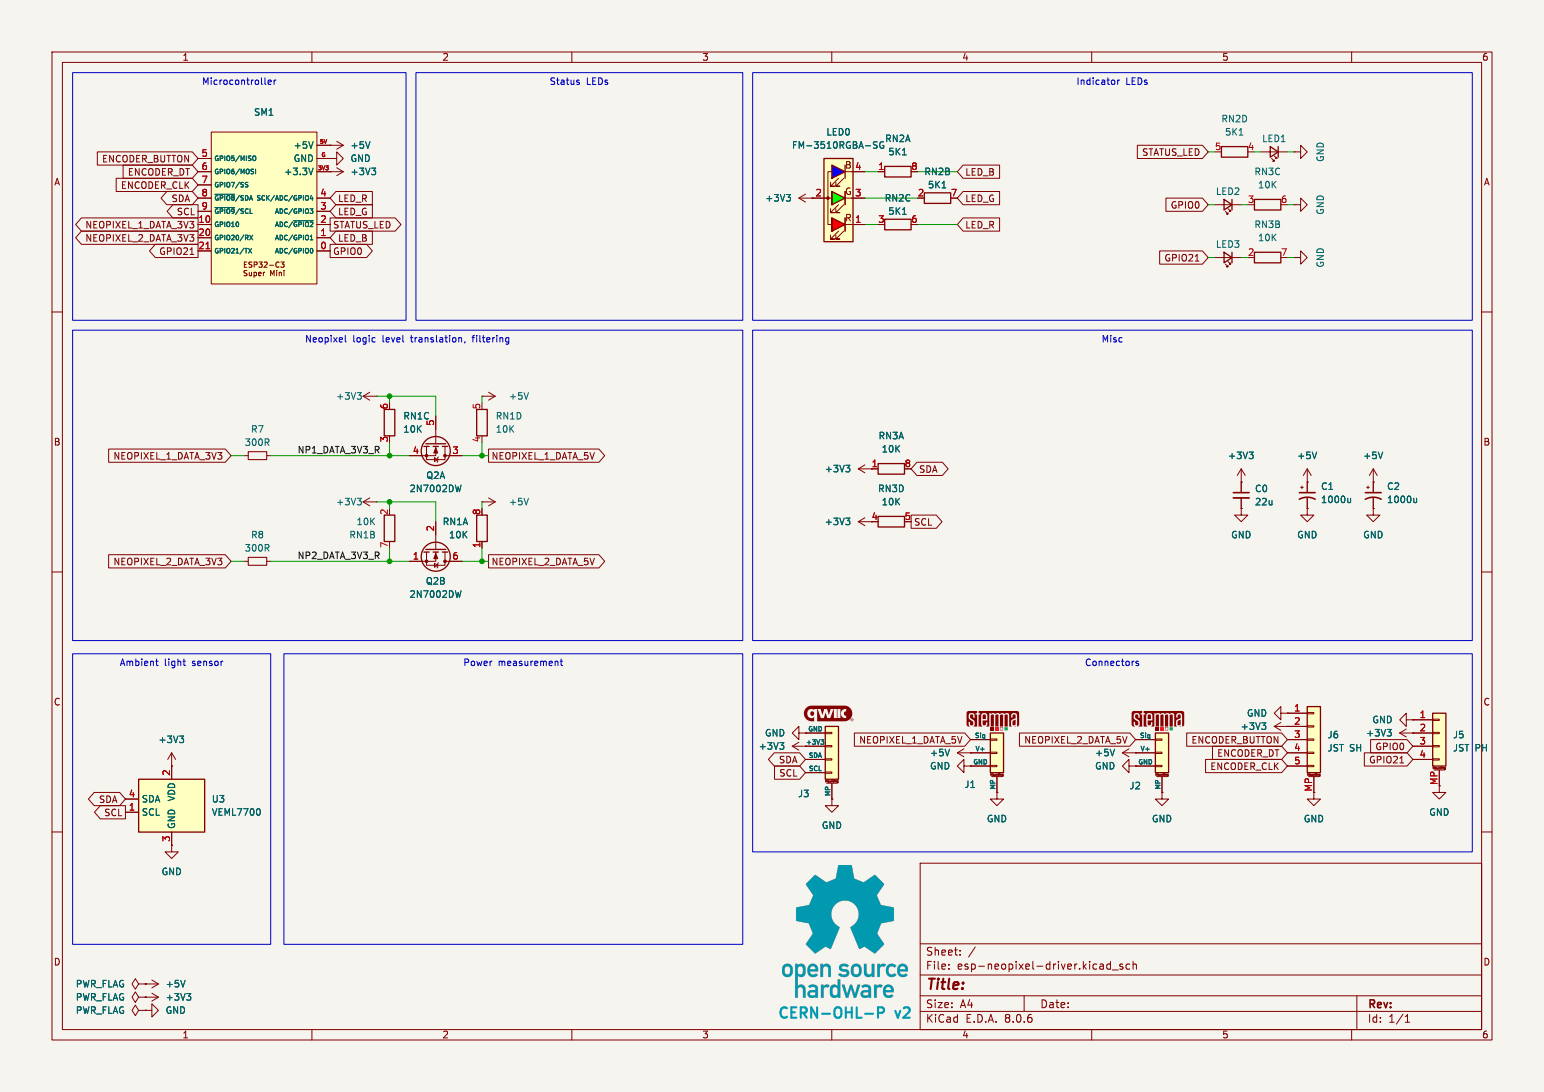
[picture p77: page 1]

Id: 1/1 Title: File: esp-neopixel-driver.kicad_sch Sheet: /
