smkent/pcb/pcb-archived/stackable2/esp-rgb-driver/fab/esp-rgb-driver-schematic.pdf

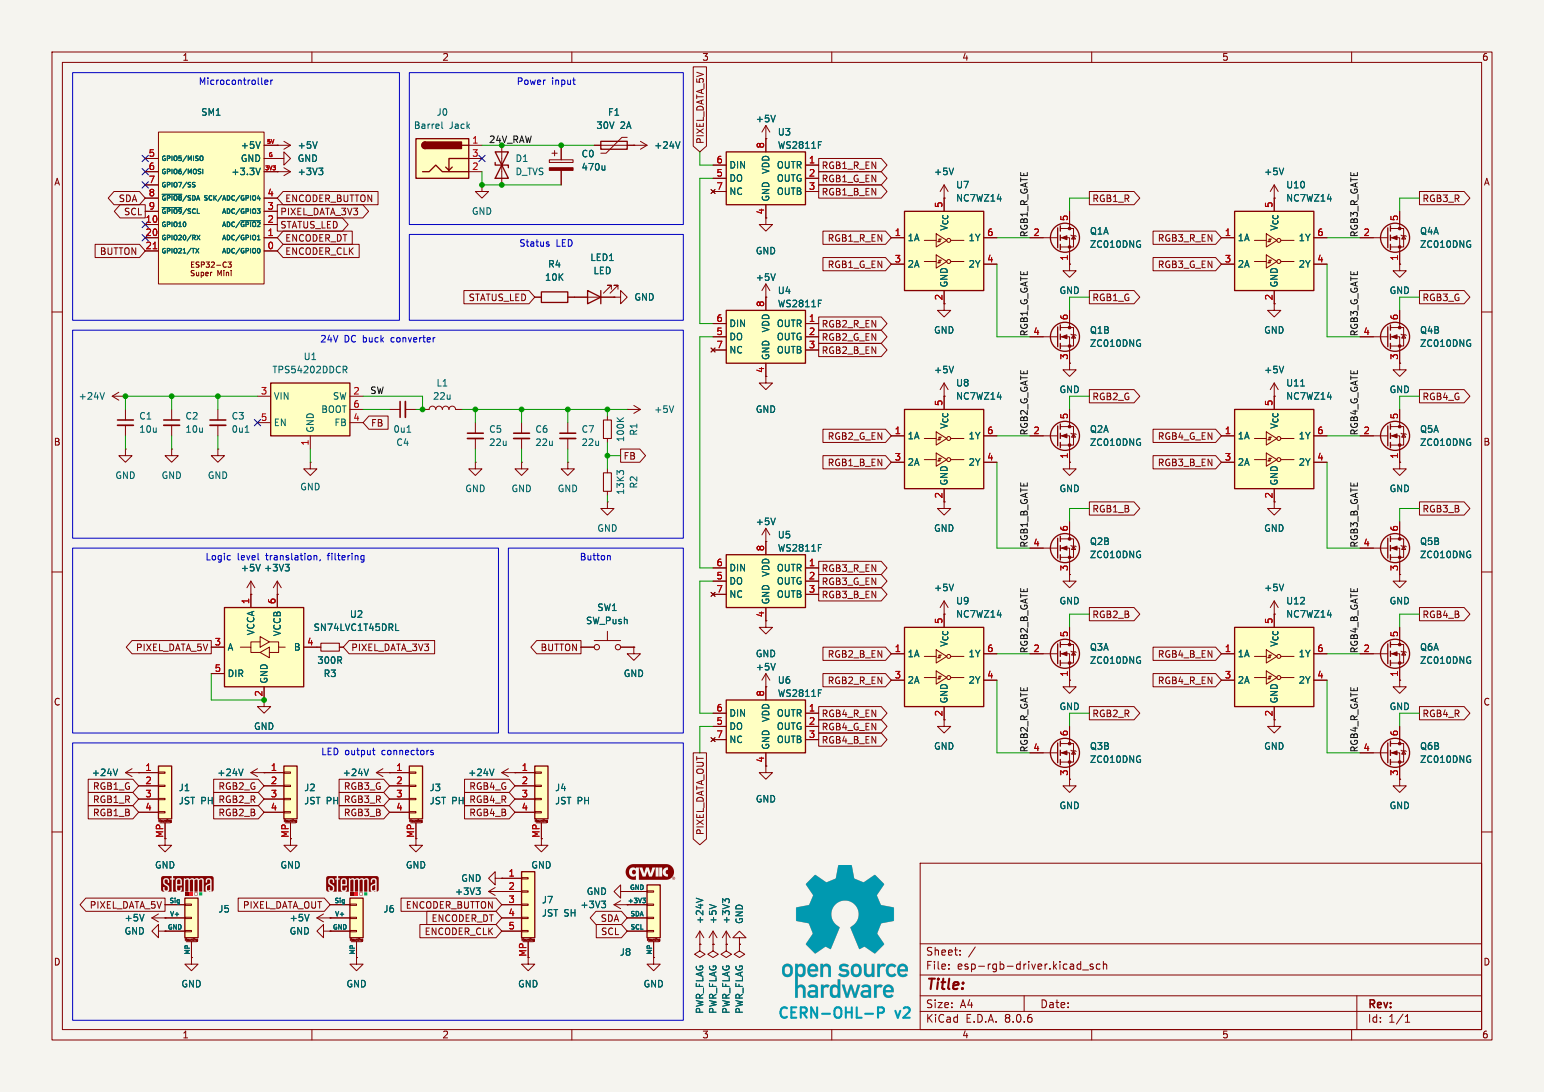
[picture p78: page 1]

4 DO 5 DIN 6 NC 7 VDD

1 SW 2 VIN 3 FB 4 EN 5 BOOT 6 U1 TPS54202DDCR GND

U5 WS2811F OUTR 1 OUTG 2 OUTB 3 GND

8 GND
+5V OUTR 1 OUTG 2 OUTB 3 GND

+5V U6 WS2811F OUTR 1 OUTG 2 OUTB 3 GND

Sig V+ GND MP GND

Id: 1/1 Title: File: esp-rgb-driver.kicad_sch Sheet: /
