smkent/pcb/pcb-archived/stackable2/esp-cwww/fab/esp-cwww-schematic.pdf

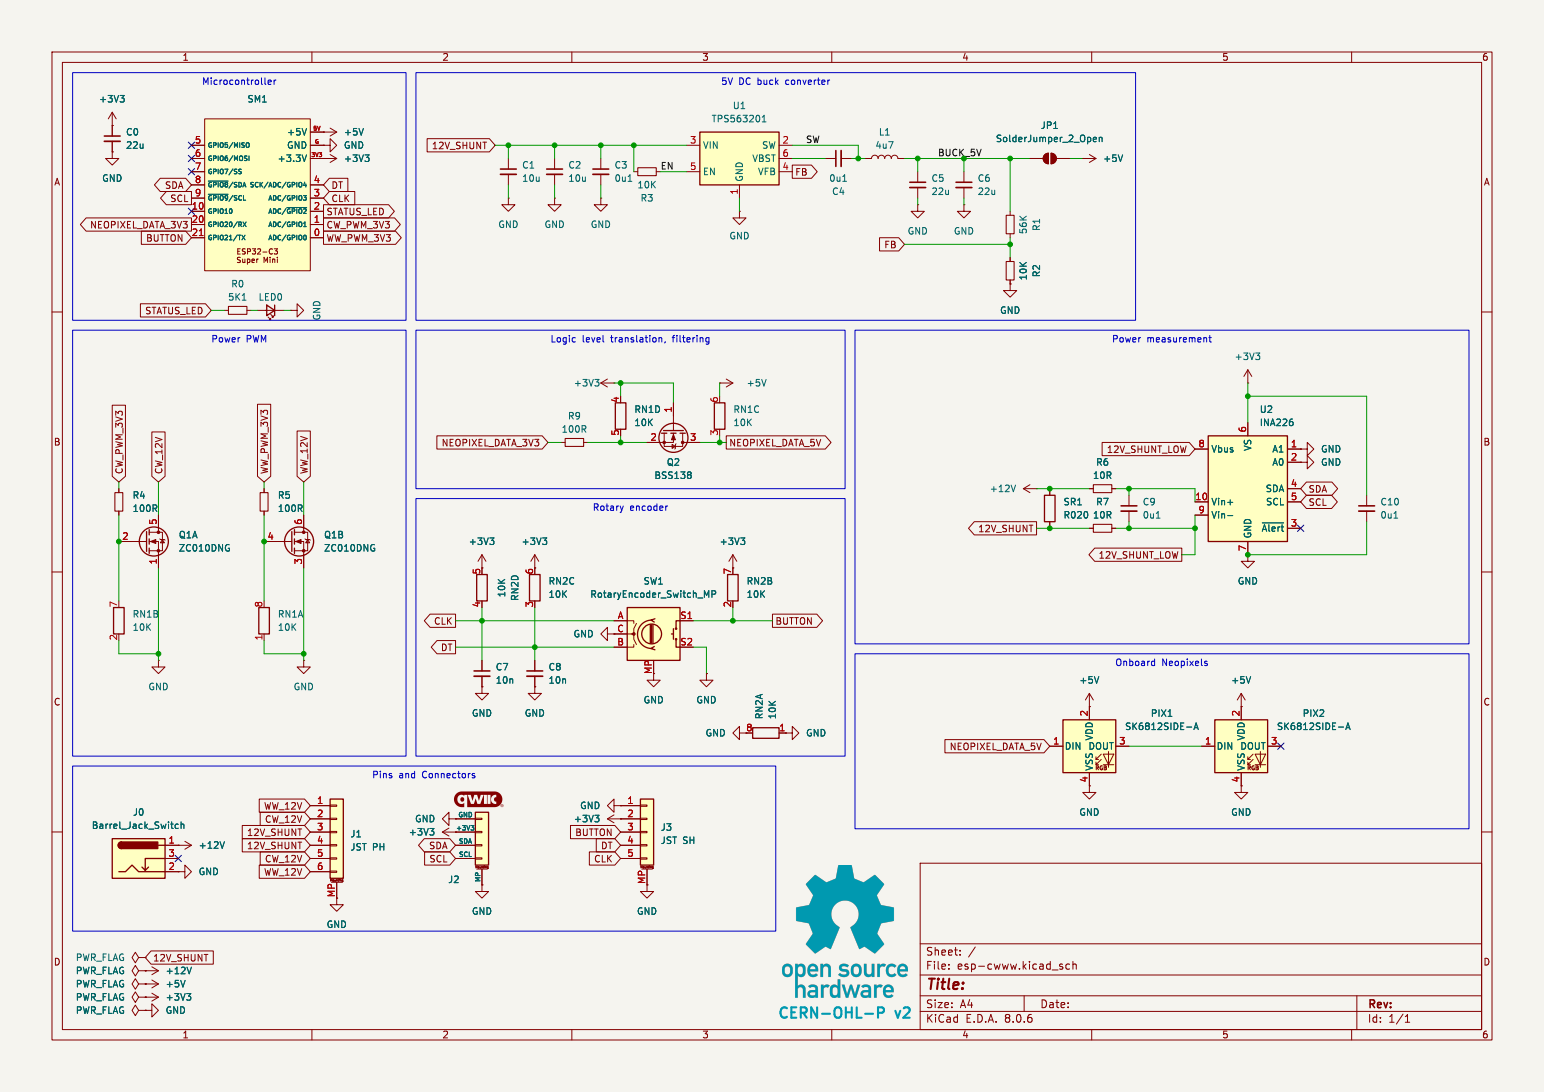
[picture p79: page 1]

1 SW 2 VIN 3 VFB 4 EN 5 VBST 6 U1 TPS563201 C3
