smkent/pcb/pcb-archived/stackable2/esp-rgb-driver/esp-rgb-driver.kicad_pcb

## KiCad design pcb-archived/stackable2/esp-rgb-driver/esp-rgb-driver.kicad_pcb (2025-01-20, an earlier design)

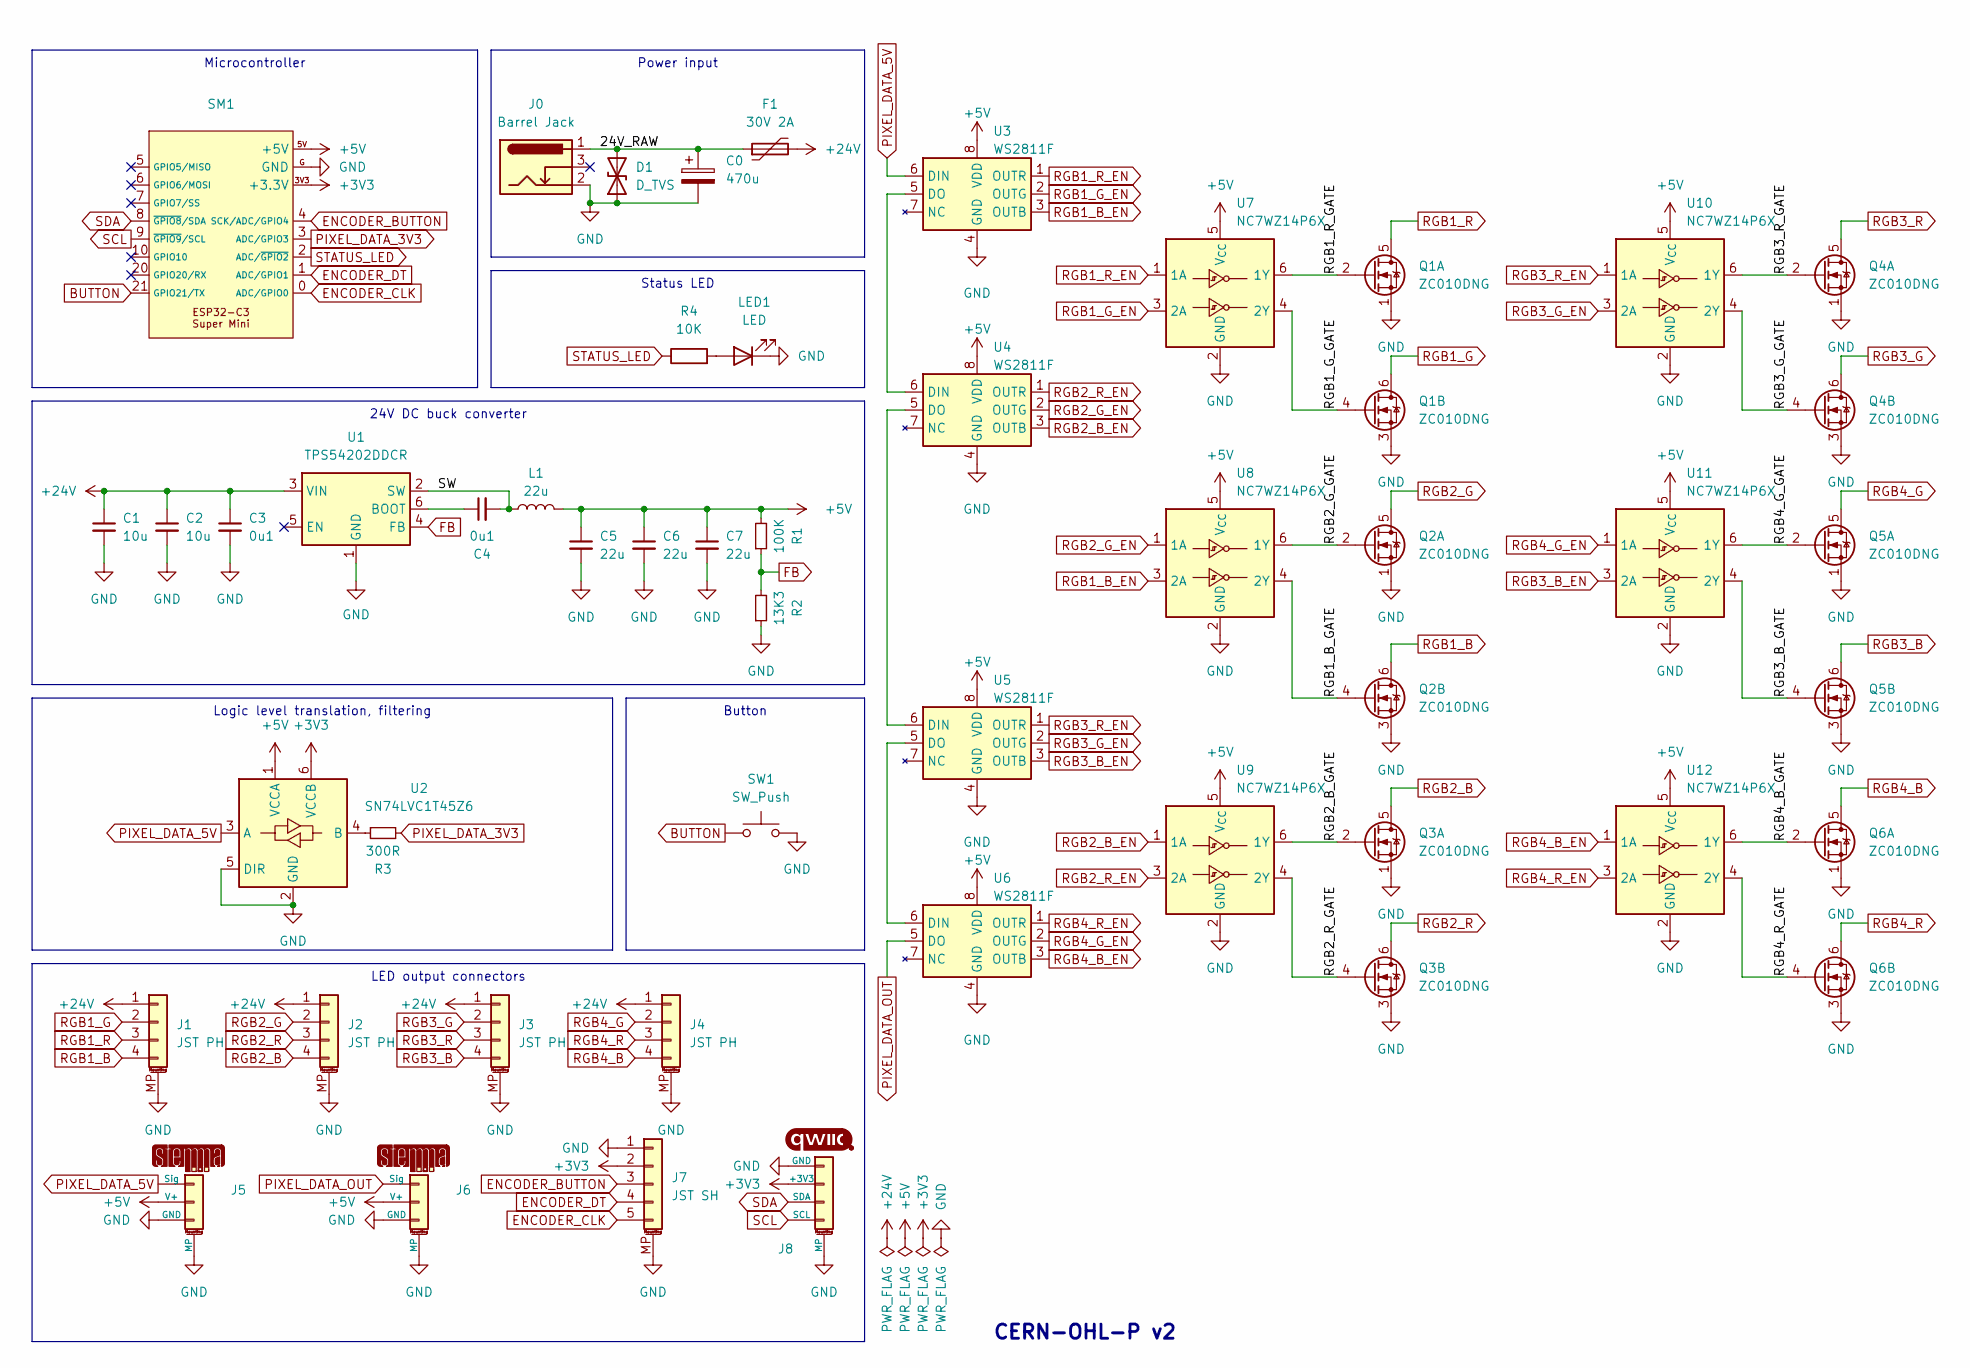
[picture p117: schematic esp-rgb-driver.kicad_sch]

Parts:
C0: 470u; CP_Elec_8x10
C1, C2: 10u; C_0603_1608Metric_Pad1.08x0.95mm_HandSolder
C3, C4: 0u1; C_0402_1005Metric
C5, C6, C7: 22u; C_0805_2012Metric_Pad1.18x1.45mm_HandSolder
D1: D_TVS; D_SOD-123F
F1: 30V 2A; Fuse_1812_4532Metric
J0: Barrel Jack; BarrelJack_DC-050_SMT_Horizontal
J1, J2, J3, J4: JST PH; JST_PH_S4B-PH-SM4-TB_1x04-1MP_P2.00mm_Horizontal
J5, J6: STEMMA-Signal; STEMMA-Signal-SMD-horizontal
J7: JST SH; JST_SH_SM05B-SRSS-TB_1x05-1MP_P1.00mm_Horizontal
J8: Qwiic; Qwiic-SMD-horizontal-logo
L1: 22u; L_Power_7.0x6.6mm_0630
LED1: LED; LED_0402_1005Metric
Q1, Q2, Q3, Q4, Q5, Q6: ZC010DNG; PDFN-8_L3.2-W3.1-P0.65-LS3.4-BL-EP2; LCSC Part C36499170
R1: 100K; R_0603_1608Metric_Pad0.98x0.95mm_HandSolder
R2: 13K3; R_0603_1608Metric_Pad0.98x0.95mm_HandSolder
R3: 300R; R_0402_1005Metric
R4: 10K; R_0402_1005Metric
SM1: ESP32-C3-Super-Mini-Castellated-SMD-only
SW1: SW_Push; SW_SPST_PTS647_Sx50
U1: TPS54202DDCR; SOT-23-6; LCSC Part C191884
U2: SN74LVC1T45Z6; SOT-563; LCSC Part C441819
U3, U4, U5, U6: WS2811F; FSOP-8_3.3x1.7mm_P0.80mm; LCSC Part C5446692
U7, U8, U9, U10, U11, U12: NC7WZ14P6X; SOT-363_SC-70-6_HandSolder; LCSC Part C5207816

Connections:
+3V3: J7.2, J8.2 (+3V3), SM1.3V3 (+3.3V), U2.6 (VCCB)
+5V: C5.1, C6.1, C7.1, J5.2 (V+), J6.2 (V+), L1.2, R1.2, SM1.5V (+5V), U2.1 (VCCA), U3.8 (VDD), U4.8 (VDD), U5.8 (VDD), U6.8 (VDD), U7.5 (V_{CC}), U8.5 (V_{CC}), U9.5 (V_{CC}), U10.5 (V_{CC}), U11.5 (V_{CC}), U12.5 (V_{CC})
+24V: C1.1, C2.1, C3.1, F1.2, J1.1, J2.1, J3.1, J4.1, U1.3 (VIN)
/24V_RAW: C0.1, D1.2 (A2), F1.1, J0.1
/RGB1_B_GATE: Q2.4 (G), U8.4 (2Y)
/RGB1_G_GATE: Q1.4 (G), U7.4 (2Y)
/RGB1_R_GATE: Q1.2 (G), U7.6 (1Y)
/RGB2_B_GATE: Q3.2 (G), U9.6 (1Y)
/RGB2_G_GATE: Q2.2 (G), U8.6 (1Y)
/RGB2_R_GATE: Q3.4 (G), U9.4 (2Y)
/RGB3_B_GATE: Q5.4 (G), U11.4 (2Y)
/RGB3_G_GATE: Q4.4 (G), U10.4 (2Y)
/RGB3_R_GATE: Q4.2 (G), U10.6 (1Y)
/RGB4_B_GATE: Q6.2 (G), U12.6 (1Y)
/RGB4_G_GATE: Q5.2 (G), U11.6 (1Y)
/RGB4_R_GATE: Q6.4 (G), U12.4 (2Y)
/SW: C4.2, L1.1, U1.2 (SW)
BUTTON: SM1.21 (GPIO21/TX), SW1.1
ENCODER_BUTTON: J7.3, SM1.4 (SCK/ADC/GPIO4)
ENCODER_CLK: J7.5, SM1.0 (ADC/GPIO0)
ENCODER_DT: J7.4, SM1.1 (ADC/GPIO1)
FB: R1.1, R2.2, U1.4 (FB)
GND: C0.2, C1.2, C2.2, C3.2, C5.2, C6.2, C7.2, D1.1 (A1), J0.2, J1.MP (MountPin), J2.MP (MountPin), J3.MP (MountPin), J4.MP (MountPin), J5.3 (GND), J5.MP, J6.3 (GND), J6.MP, J7.1, J7.MP (MountPin), J8.1 (GND), J8.MP, LED1.1 (K), Q1.1 (S), Q1.3 (S), Q2.1 (S), Q2.3 (S), Q3.1 (S), Q3.3 (S), Q4.1 (S), Q4.3 (S), Q5.1 (S), Q5.3 (S), Q6.1 (S), Q6.3 (S), R2.1, SM1.G (GND), SW1.2, U1.1 (GND), U2.2 (GND), U2.5 (DIR), U3.4 (GND), U4.4 (GND), U5.4 (GND), U6.4 (GND), U7.2 (GND), U8.2 (GND), U9.2 (GND), U10.2 (GND), U11.2 (GND), U12.2 (GND)
unnamed: LED1.2 (A), R4.2
unnamed: C4.1, U1.6 (BOOT)
unnamed: R3.1, U2.4 (B)
unnamed: U3.5 (DO), U4.6 (DIN)
unnamed: U4.5 (DO), U5.6 (DIN)
unnamed: U5.5 (DO), U6.6 (DIN)
PIXEL_DATA_3V3: R3.2, SM1.3 (ADC/GPIO3)
PIXEL_DATA_5V: J5.1 (Sig), U2.3 (A), U3.6 (DIN)
PIXEL_DATA_OUT: J6.1 (Sig), U6.5 (DO)
RGB1_B: J1.4, Q2.6 (D)
RGB1_B_EN: U3.3 (OUTB), U8.3 (2A)
RGB1_G: J1.2, Q1.6 (D)
RGB1_G_EN: U3.2 (OUTG), U7.3 (2A)
RGB1_R: J1.3, Q1.5 (D)
RGB1_R_EN: U3.1 (OUTR), U7.1 (1A)
RGB2_B: J2.4, Q3.5 (D)
RGB2_B_EN: U4.3 (OUTB), U9.1 (1A)
RGB2_G: J2.2, Q2.5 (D)
RGB2_G_EN: U4.2 (OUTG), U8.1 (1A)
RGB2_R: J2.3, Q3.6 (D)
RGB2_R_EN: U4.1 (OUTR), U9.3 (2A)
RGB3_B: J3.4, Q5.6 (D)
RGB3_B_EN: U5.3 (OUTB), U11.3 (2A)
RGB3_G: J3.2, Q4.6 (D)
RGB3_G_EN: U5.2 (OUTG), U10.3 (2A)
RGB3_R: J3.3, Q4.5 (D)
RGB3_R_EN: U5.1 (OUTR), U10.1 (1A)
RGB4_B: J4.4, Q6.5 (D)
RGB4_B_EN: U6.3 (OUTB), U12.1 (1A)
RGB4_G: J4.2, Q5.5 (D)
RGB4_G_EN: U6.2 (OUTG), U11.1 (1A)
RGB4_R: J4.3, Q6.6 (D)
RGB4_R_EN: U6.1 (OUTR), U12.3 (2A)
SCL: J8.4 (SCL), SM1.9 (~GPIO9/SCL)
SDA: J8.3 (SDA), SM1.8 (~GPIO8/SDA)
STATUS_LED: R4.1, SM1.2 (ADC/~GPIO2)

Notes on the sheet:
24V DC buck converter
Status LED
Button
Microcontroller
Logic level translation, filtering
LED output connectors
Power input
CERN-OHL-P v2

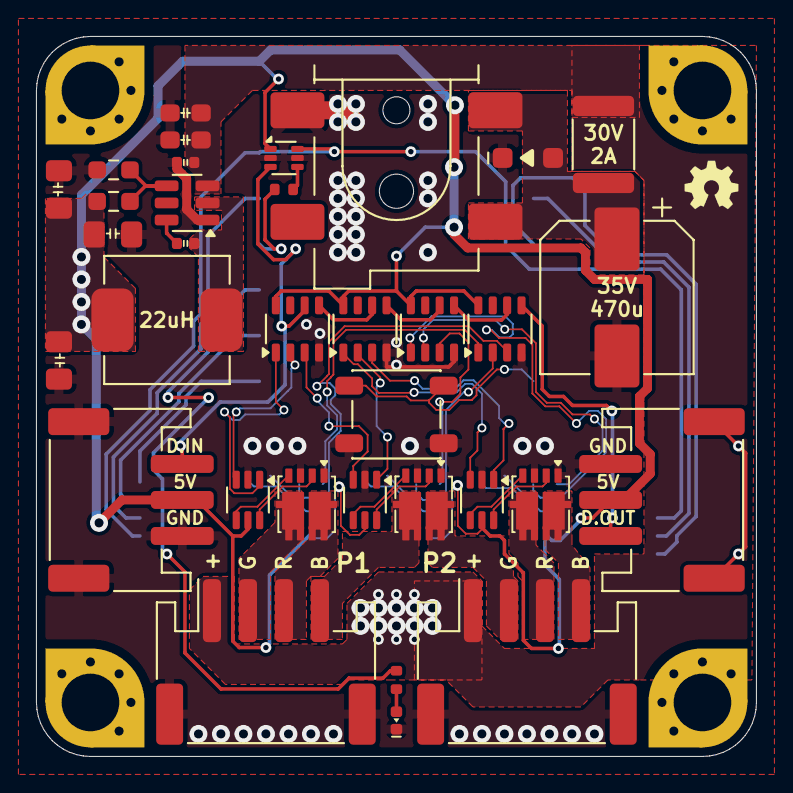
[picture p118: board pcb-archived/stackable2/esp-rgb-driver/esp-rgb-driver.kicad_pcb from above]

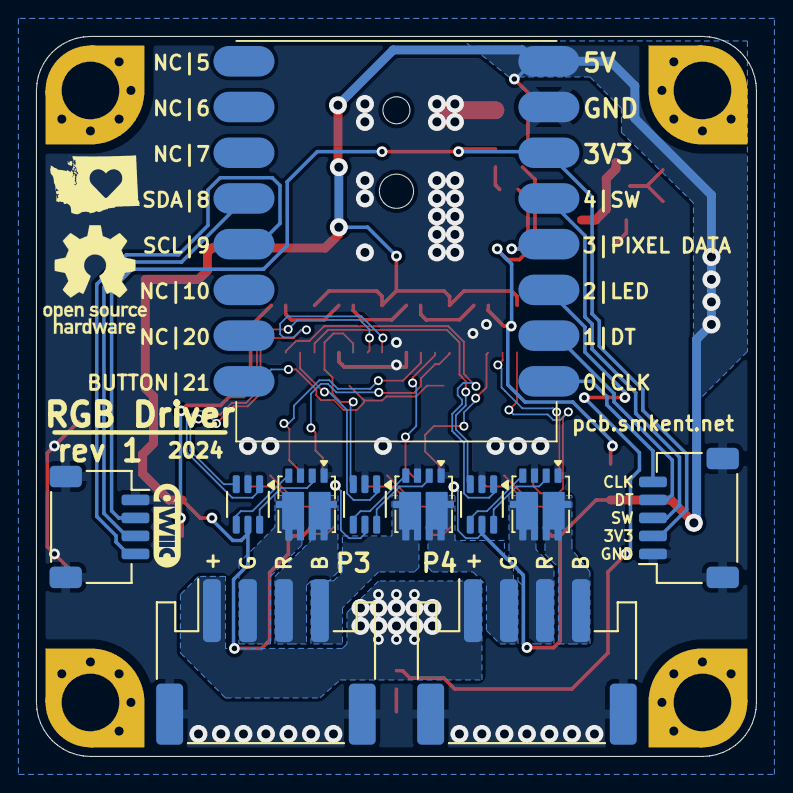
[picture p119: board pcb-archived/stackable2/esp-rgb-driver/esp-rgb-driver.kicad_pcb from below]

Board: 2 copper layers, 40.0 x 40.0 mm, 45 parts (11 on the bottom side), 59 nets.
