smkent/pcb/pcb-archived/stackable2/lcd-round/lcd-round.kicad_pcb

## KiCad design pcb-archived/stackable2/lcd-round/lcd-round.kicad_pcb (2025-02-08, an earlier design)

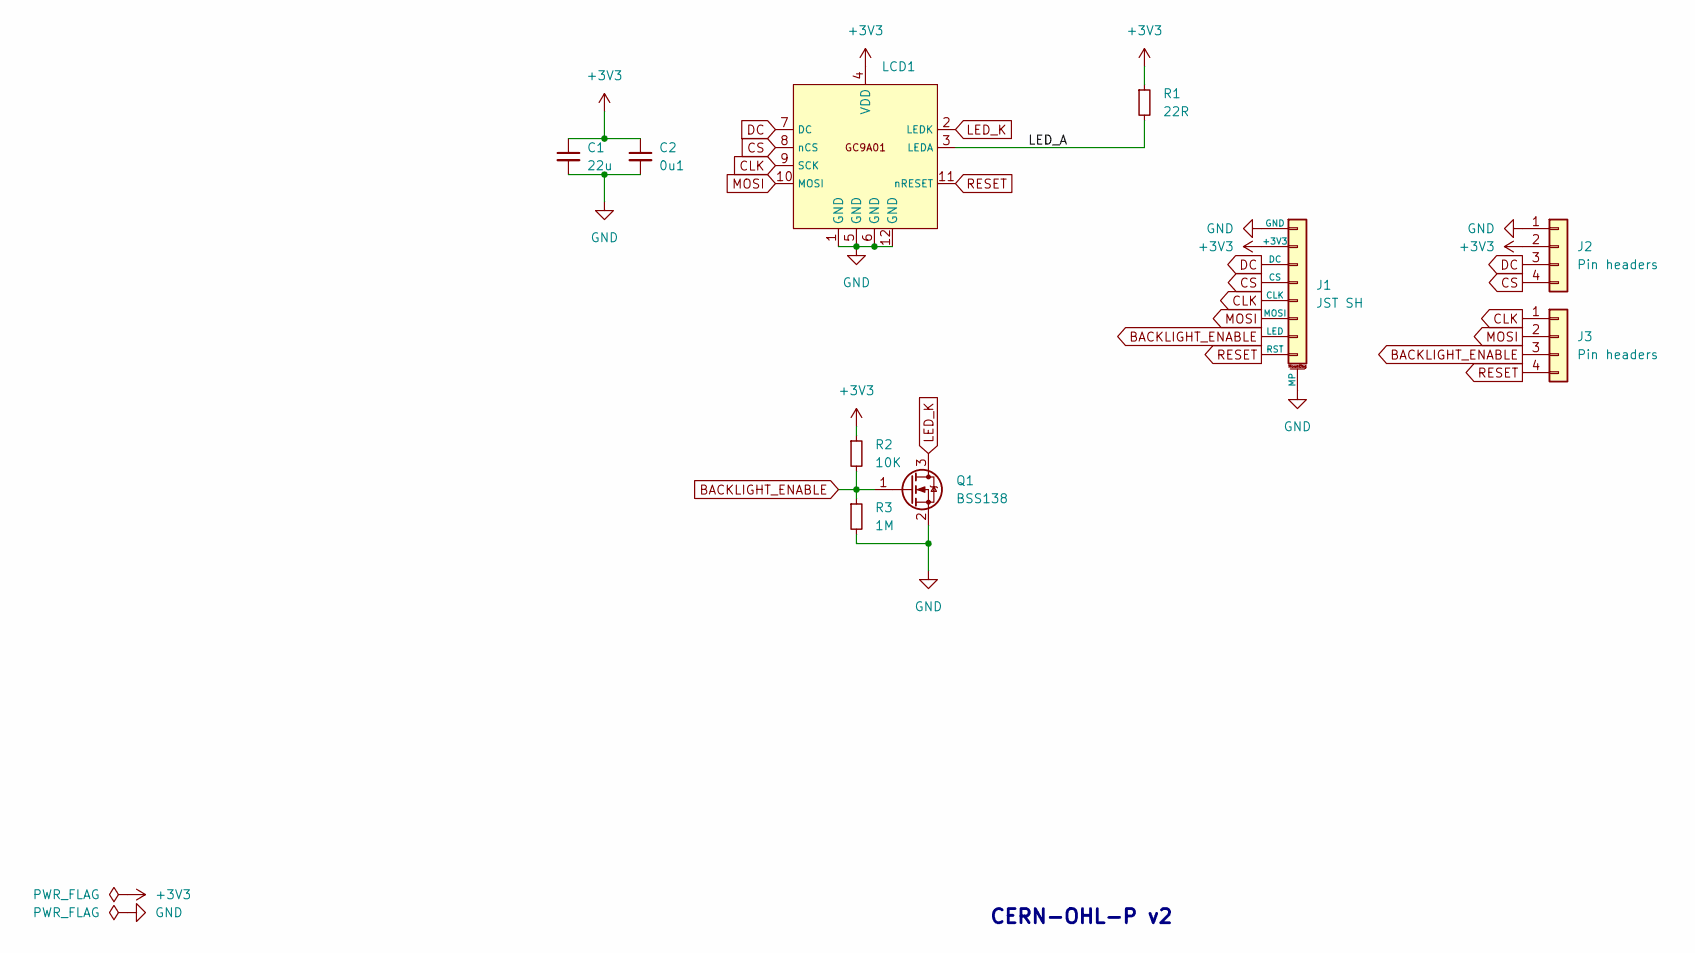
[picture p120: schematic lcd-round.kicad_sch]

Parts:
C1: 22u; C_0603_1608Metric_Pad1.08x0.95mm_HandSolder
C2: 0u1; C_0603_1608Metric_Pad1.08x0.95mm_HandSolder
J1: JST SH; JST_SH_SM08B-SRSS-TB_1x08-1MP_P1.00mm_Horizontal; LCSC Part C7433429
J2: Pin headers; PinHeader_1x04_P2.54mm_Vertical_SMD_Pin1Right
J3: Pin headers; PinHeader_1x04_P2.54mm_Vertical_SMD_Pin1Left
LCD1: GC9A01; GC9A01-screen-connector-pads
Q1: BSS138; SOT-23
R1: 22R; R_0603_1608Metric_Pad0.98x0.95mm_HandSolder
R2: 10K; R_0603_1608Metric_Pad0.98x0.95mm_HandSolder
R3: 1M; R_0603_1608Metric_Pad0.98x0.95mm_HandSolder

Connections:
+3V3: C1.1, C2.1, J1.2 (+3V3), J2.2, LCD1.4 (VDD), R1.1, R2.1
/LED_A: LCD1.3 (LEDA), R1.2
BACKLIGHT_ENABLE: J1.7 (LED), J3.3, Q1.1 (G), R2.2, R3.1
CLK: J1.5 (CLK), J3.1, LCD1.9 (SCK)
CS: J1.4 (CS), J2.4, LCD1.8 (nCS)
DC: J1.3 (DC), J2.3, LCD1.7 (DC)
GND: C1.2, C2.2, J1.1 (GND), J1.MP, J2.1, LCD1.1 (GND), LCD1.5 (GND), LCD1.6 (GND), LCD1.12 (GND), Q1.2 (S), R3.2
LED_K: LCD1.2 (LEDK), Q1.3 (D)
MOSI: J1.6 (MOSI), J3.2, LCD1.10 (MOSI)
RESET: J1.8 (RST), J3.4, LCD1.11 (nRESET)

Notes on the sheet:
CERN-OHL-P v2

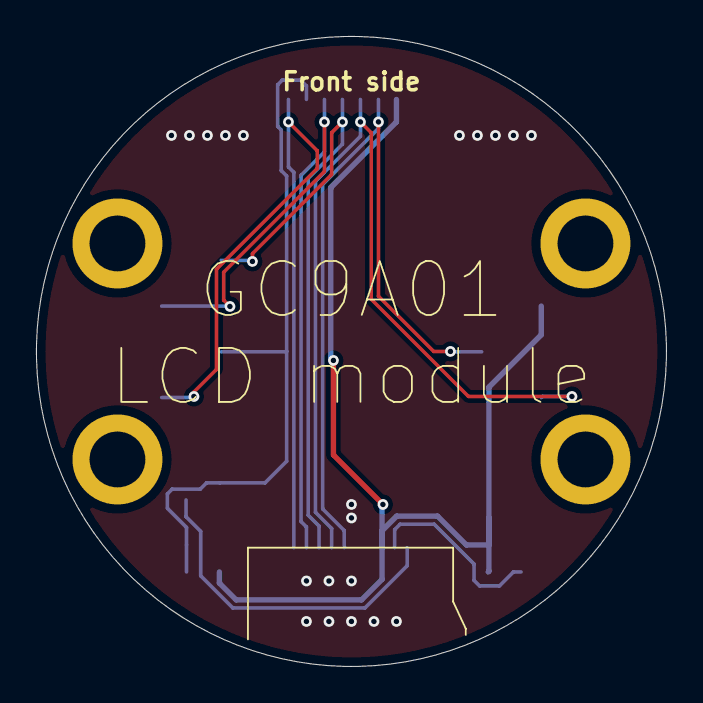
[picture p121: board lcd-round.kicad_pcb from above]

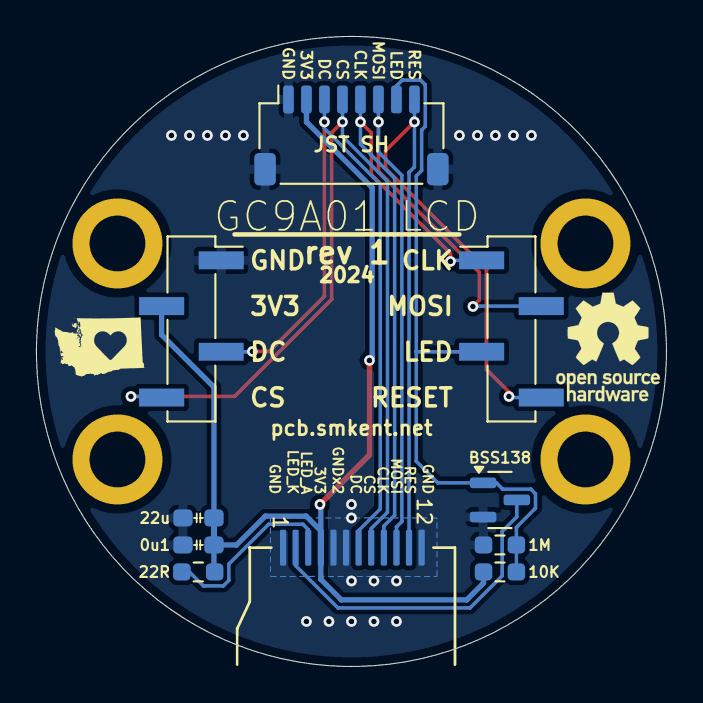
[picture p122: board lcd-round.kicad_pcb from below]

Board: 2 copper layers, 35.0 x 35.0 mm, 10 parts (10 on the bottom side), 10 nets.
