smkent/pcb/pcb/stackable3/quad-level-shifter-gt0104sc/quad-level-shifter-gt0104sc.kicad_pcb

## KiCad design pcb/stackable3/quad-level-shifter-gt0104sc/quad-level-shifter-gt0104sc.kicad_pcb (2025-03-15)

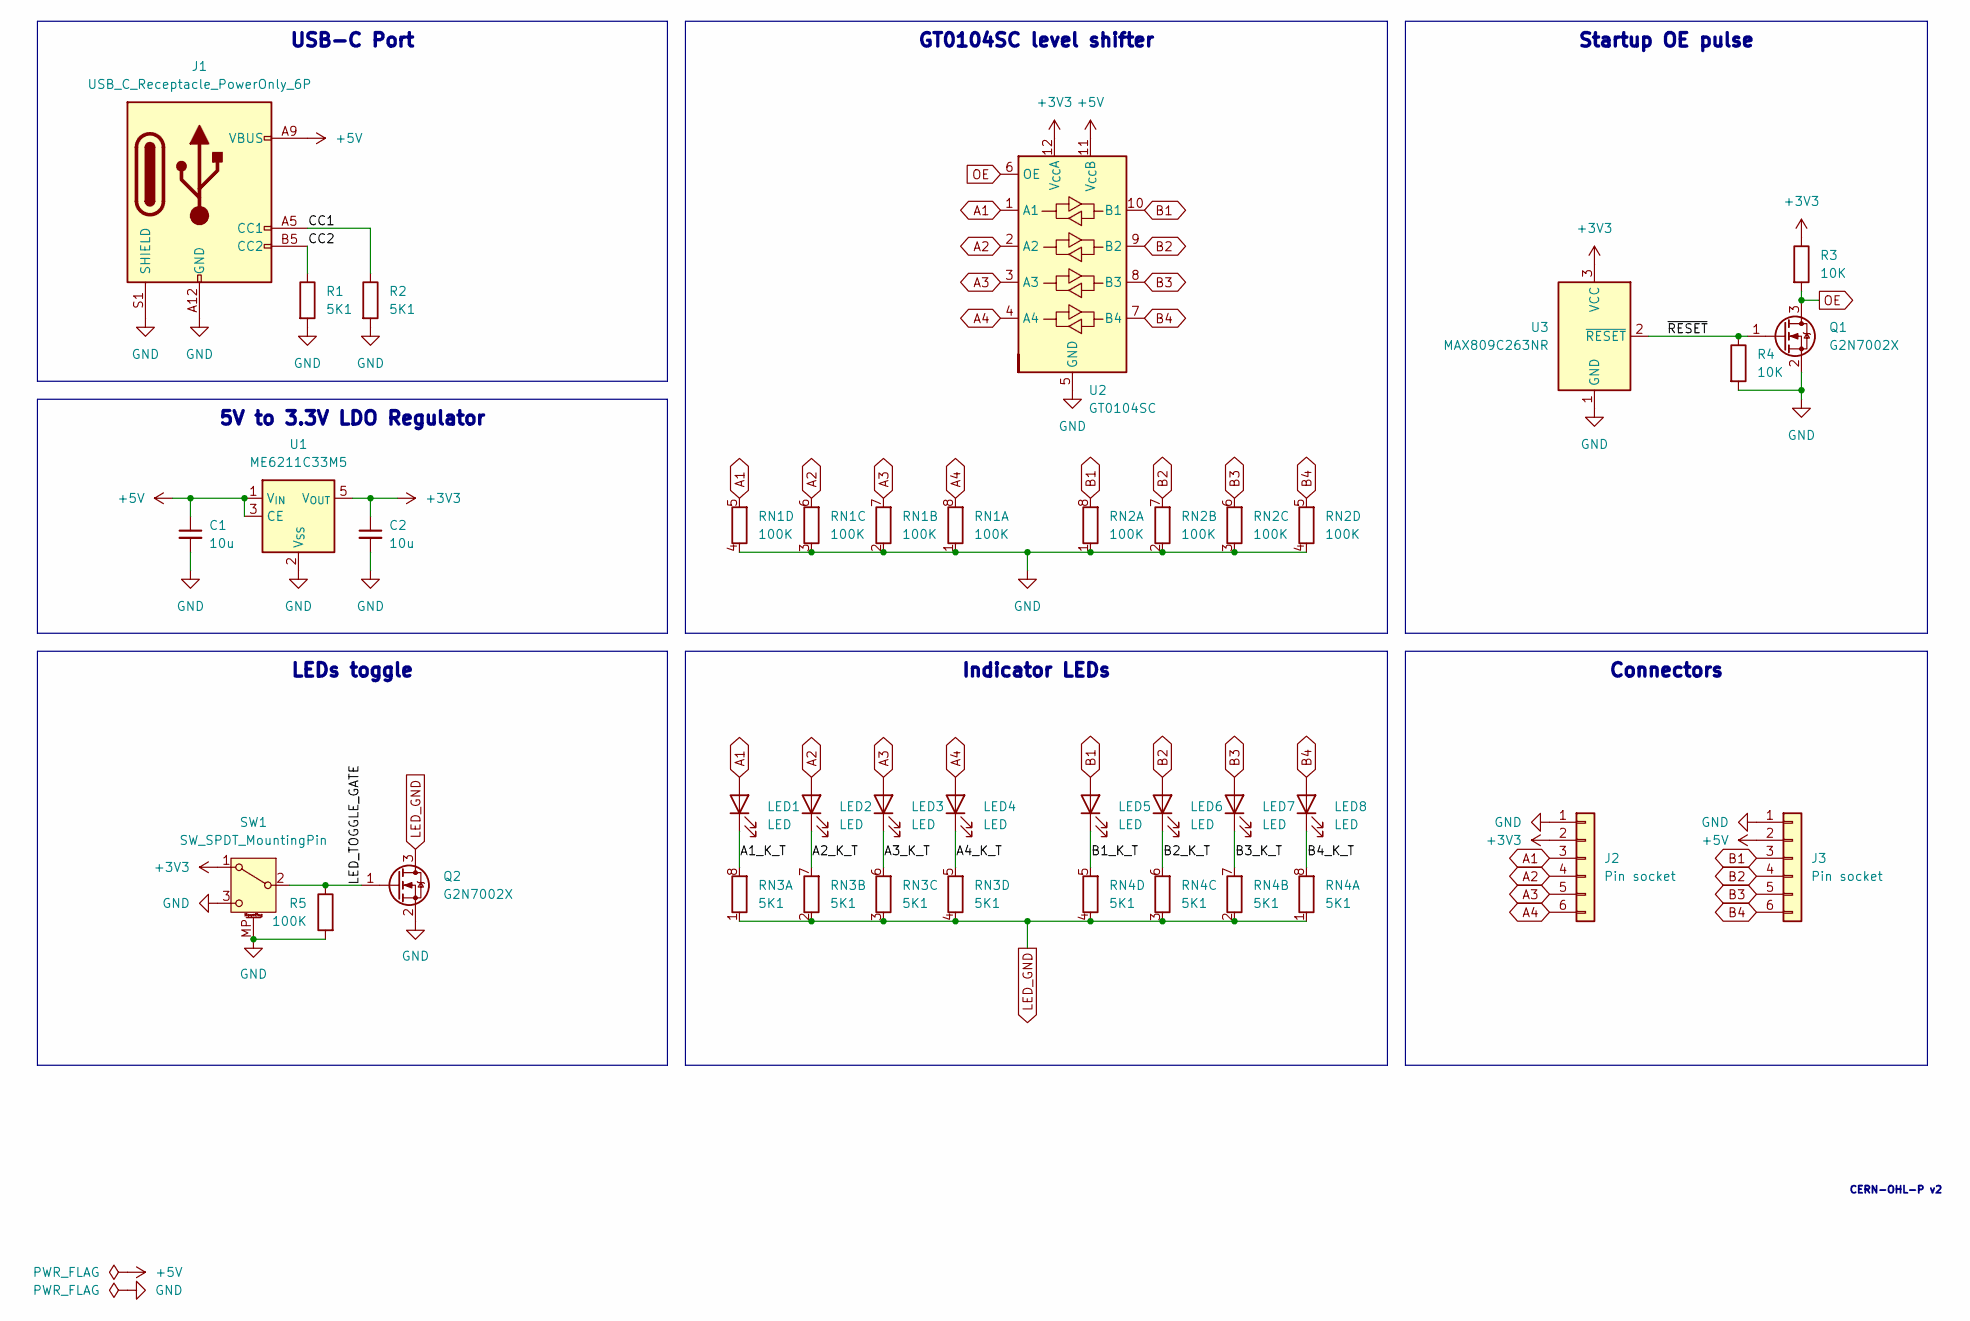
[picture p123: schematic quad-level-shifter-gt0104sc.kicad_sch]

Parts:
C1, C2: 10u; C_0402_1005Metric; LCSC Part C315248
J1: USB_C_Receptacle_PowerOnly_6P; USB_C_Receptacle_GCT_USB4125-xx-x_6P_TopMnt_Horizontal_Hand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; LCSC Part C2927029
J2, J3: Pin socket; PinSocket_1x06_P2.54mm_Vertical
LED1, LED2, LED3, LED4, LED5, LED6, LED7, LED8: LED; LED_0603_1608Metric
Q1, Q2: G2N7002X; SOT-523; LCSC Part C5258971
R1, R2: 5K1; R_0603_1608Metric; LCSC Part C23186
R3, R4: 10K; R_0402_1005Metric; LCSC Part C25744
R5: 100K; R_0402_1005Metric; LCSC Part C25741
RN1, RN2: 100K; R_Array_Convex_4x0402_HandSolder; LCSC Part C326786
RN3, RN4: 5K1; R_Array_Convex_4x0402_HandSolder; LCSC Part C425290
SW1: SW_SPDT_MountingPin; SW_SPDT_PCM12; LCSC Part C319020
U1: ME6211C33M5; SOT-23-5; LCSC Part C82942
U2: GT0104SC; QFN-12-1EP_2x2mm_P0.4mm_EP1.1x1.1mm; LCSC Part C22356898
U3: MAX809C263NR; SOT-23; LCSC Part C5223646

Connections:
+3V3: C2.1, J2.2, R3.1, SW1.1 (A), U1.5 (V_{OUT}), U2.12 (V_{CC}A), U3.3 (VCC)
+5V: C1.1, J1.A9 (VBUS), J1.B9 (VBUS), J3.2, U1.1 (V_{IN}), U1.3 (CE), U2.11 (V_{CC}B)
/A1_K_T: LED1.1 (K), RN3.8 (R1.2)
/A2_K_T: LED2.1 (K), RN3.7 (R2.2)
/A3_K_T: LED3.1 (K), RN3.6 (R3.2)
/A4_K_T: LED4.1 (K), RN3.5 (R4.2)
/B1_K_T: LED5.1 (K), RN4.5 (R4.2)
/B2_K_T: LED6.1 (K), RN4.6 (R3.2)
/B3_K_T: LED7.1 (K), RN4.7 (R2.2)
/B4_K_T: LED8.1 (K), RN4.8 (R1.2)
/CC1: J1.A5 (CC1), R2.1
/CC2: J1.B5 (CC2), R1.1
/LED_TOGGLE_GATE: Q2.1 (G), R5.1, SW1.2 (B)
/~RESET: Q1.1 (G), R4.1, U3.2 (~RESET)
A1: J2.3, LED1.2 (A), RN1.5 (R4.2), U2.1 (A1)
A2: J2.4, LED2.2 (A), RN1.6 (R3.2), U2.2 (A2)
A3: J2.5, LED3.2 (A), RN1.7 (R2.2), U2.3 (A3)
A4: J2.6, LED4.2 (A), RN1.8 (R1.2), U2.4 (A4)
B1: J3.3, LED5.2 (A), RN2.8 (R1.2), U2.10 (B1)
B2: J3.4, LED6.2 (A), RN2.7 (R2.2), U2.9 (B2)
B3: J3.5, LED7.2 (A), RN2.6 (R3.2), U2.8 (B3)
B4: J3.6, LED8.2 (A), RN2.5 (R4.2), U2.7 (B4)
GND: C1.2, C2.2, J1.A12 (GND), J1.B12 (GND), J1.S1 (SHIELD), J2.1, J3.1, Q1.2 (S), Q2.2 (S), R1.2, R2.2, R4.2, R5.2, RN1.1 (R1.1), RN1.2 (R2.1), RN1.3 (R3.1), RN1.4 (R4.1), RN2.1 (R1.1), RN2.2 (R2.1), RN2.3 (R3.1), RN2.4 (R4.1), SW1.3 (C), SW1.MP (MountPin), U1.2 (V_{SS}), U2.5 (GND), U2.13 (Pad), U3.1 (GND)
LED_GND: Q2.3 (D), RN3.1 (R1.1), RN3.2 (R2.1), RN3.3 (R3.1), RN3.4 (R4.1), RN4.1 (R1.1), RN4.2 (R2.1), RN4.3 (R3.1), RN4.4 (R4.1)
OE: Q1.3 (D), R3.2, U2.6 (OE)

Notes on the sheet:
Connectors
Indicator LEDs
GT0104SC level shifter
5V to 3.3V LDO Regulator
Startup OE pulse
LEDs toggle
USB-C Port
CERN-OHL-P v2

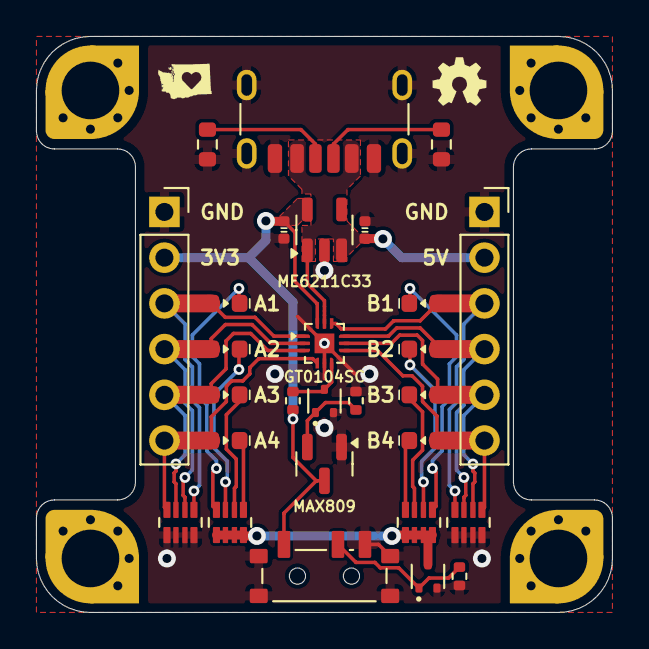
[picture p124: board quad-level-shifter-gt0104sc.kicad_pcb from above]

Board: 2 copper layers, 32.0 x 32.0 mm, 28 parts (0 on the bottom side), 25 nets.
