smkent/pcb/pcb/stackable3/shift-registers-74hc165/shift-registers-74hc165.kicad_pcb

## KiCad design pcb/stackable3/shift-registers-74hc165/shift-registers-74hc165.kicad_pcb (2025-03-08)

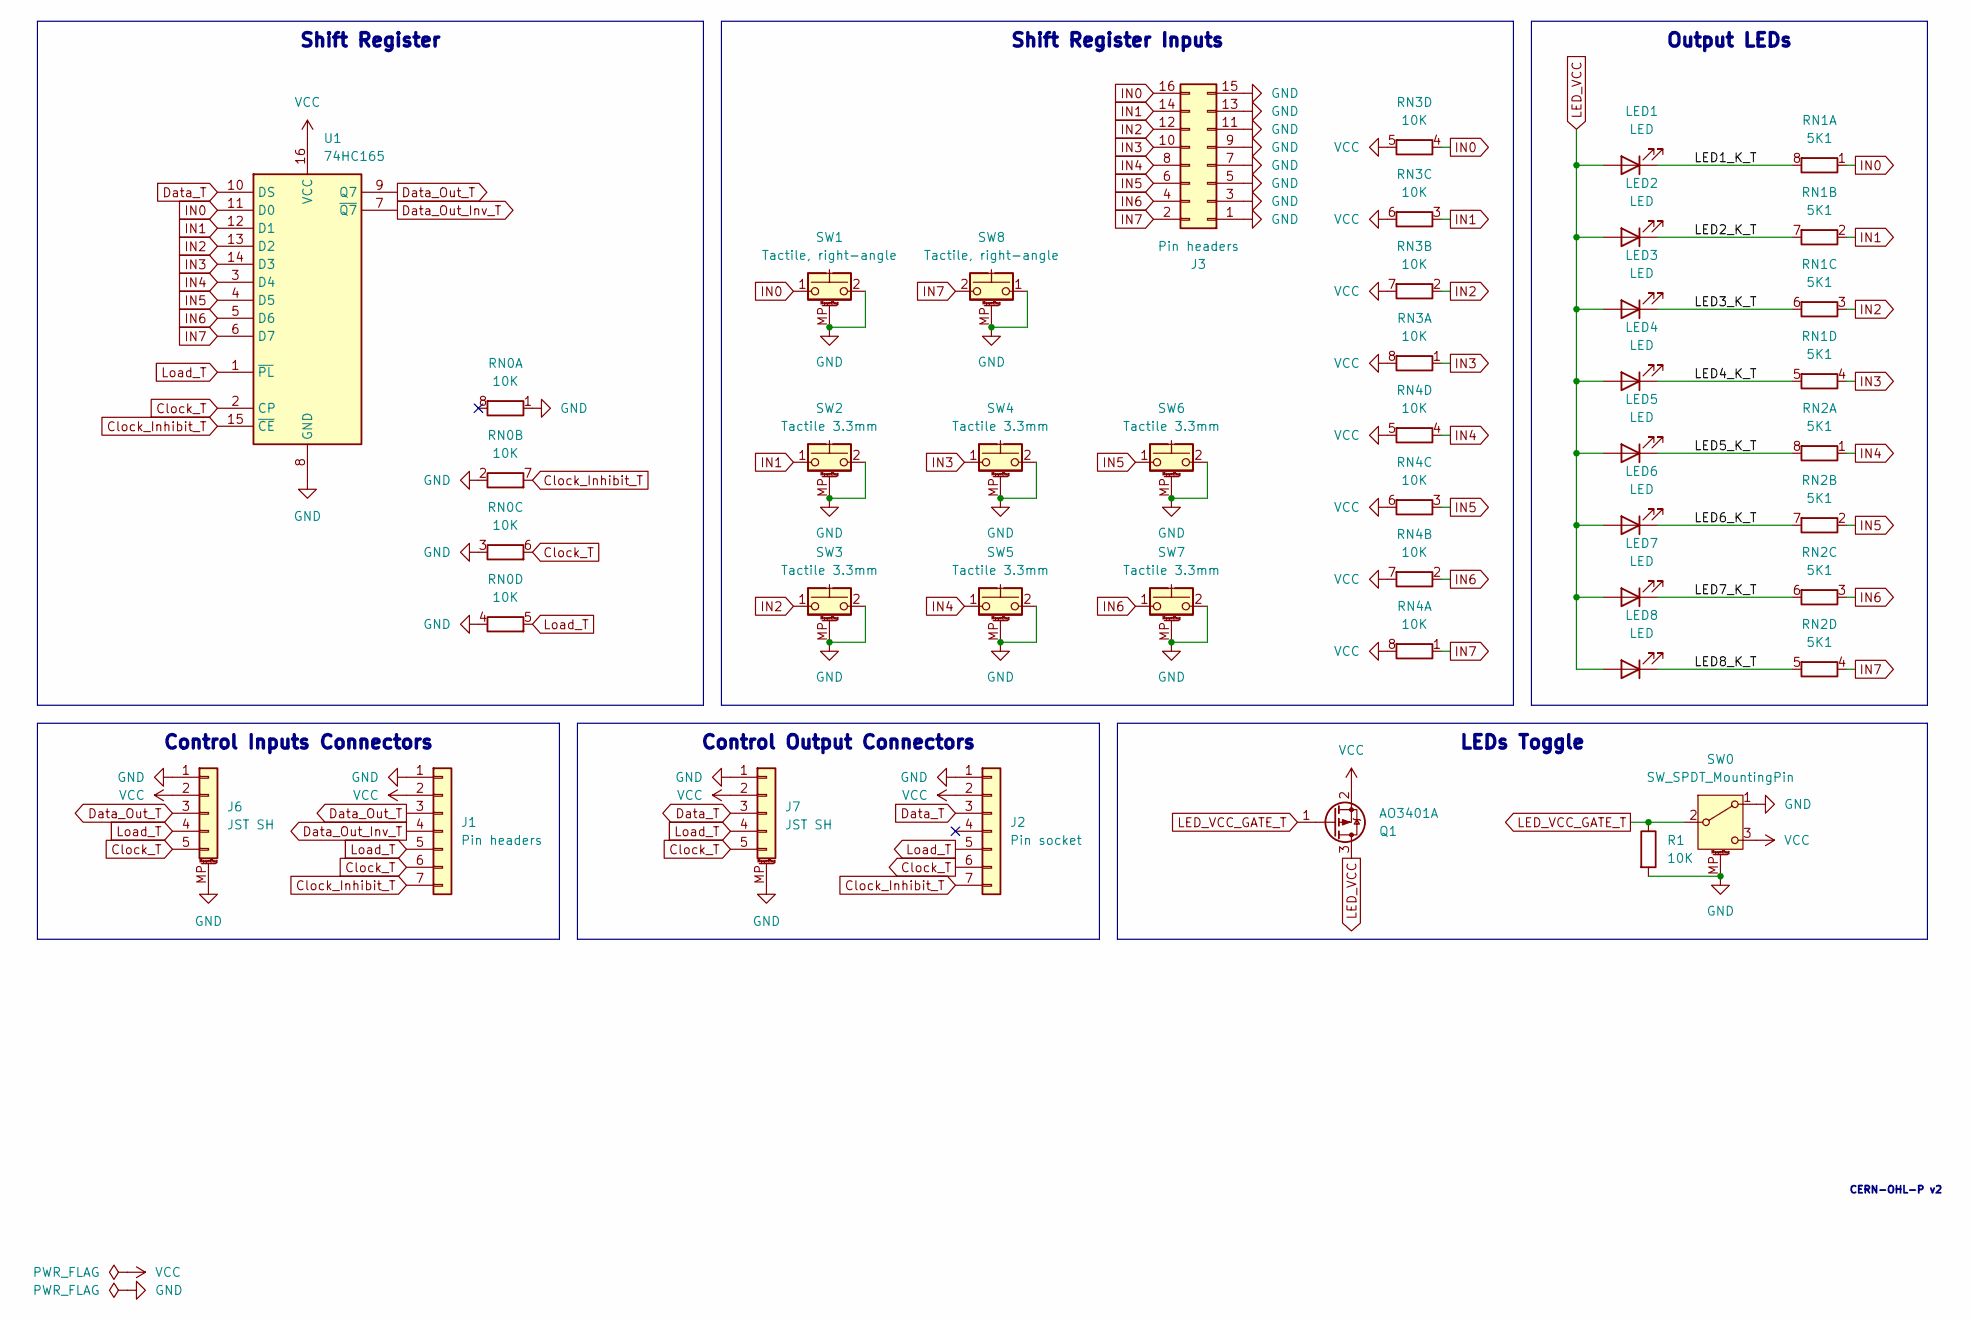
[picture p125: schematic shift-registers-74hc165.kicad_sch]

Parts:
J1: Pin headers; PinHeader_1x07_P2.54mm_Horizontal
J2: Pin socket; PinSocket_1x07_P2.54mm_Horizontal
J3: Pin headers; PinHeader_2x08_P2.54mm_Vertical
J6, J7: JST SH; JST_SH_SM05B-SRSS-TB_1x05-1MP_P1.00mm_Horizontal; LCSC Part C7433426
LED1, LED2, LED3, LED4, LED5, LED6, LED7, LED8: LED; LED_0402_1005Metric
Q1: AO3401A; SOT-23
R1: 10K; R_0402_1005Metric
RN0: 10K; R_Array_Convex_4x0603_HandSolder; LCSC Part C110924
RN1, RN2: 5K1; R_Array_Convex_4x0402; LCSC Part C425290
RN3, RN4: 10K; R_Array_Convex_4x0402; LCSC Part C7422173
SW0: SW_SPDT_MountingPin; SW_SPDT_PCM12; LCSC Part C319020
SW1, SW8: Tactile, right-angle; SW_Push_1P1T-MP_NO_4.6x3mm_Horizontal; LCSC Part C2888932
SW2, SW3, SW4, SW5, SW6, SW7: Tactile 3.3mm; SW_Push_1P1T_NO_3.3x3.3mm_MP
U1: 74HC165; SO-16_3.9x9.9mm_P1.27mm

Connections:
/LED1_K_T: LED1.1 (K), RN1.8 (R1.2)
/LED2_K_T: LED2.1 (K), RN1.7 (R2.2)
/LED3_K_T: LED3.1 (K), RN1.6 (R3.2)
/LED4_K_T: LED4.1 (K), RN1.5 (R4.2)
/LED5_K_T: LED5.1 (K), RN2.8 (R1.2)
/LED6_K_T: LED6.1 (K), RN2.7 (R2.2)
/LED7_K_T: LED7.1 (K), RN2.6 (R3.2)
/LED8_K_T: LED8.1 (K), RN2.5 (R4.2)
Clock_Inhibit_T: J1.7, J2.7, RN0.7 (R2.2), U1.15 (~CE)
Clock_T: J1.6, J2.6, J6.5, J7.5, RN0.6 (R3.2), U1.2 (CP)
Data_Out_Inv_T: J1.4, U1.7 (~Q7)
Data_Out_T: J1.3, J6.3, U1.9 (Q7)
Data_T: J2.3, J7.3, U1.10 (DS)
GND: J1.1, J2.1, J3.1, J3.3, J3.5, J3.7, J3.9, J3.11, J3.13, J3.15, J6.1, J6.MP (MountPin), J7.1, J7.MP (MountPin), R1.2, RN0.1 (R1.1), RN0.2 (R2.1), RN0.3 (R3.1), RN0.4 (R4.1), SW0.1 (A), SW0.MP (MountPin), SW1.2, SW1.MP (MountPin), SW2.2, SW2.MP (MountPin), SW3.2, SW3.MP (MountPin), SW4.2, SW4.MP (MountPin), SW5.2, SW5.MP (MountPin), SW6.2, SW6.MP (MountPin), SW7.2, SW7.MP (MountPin), SW8.1, SW8.MP (MountPin), U1.8 (GND)
IN0: J3.16, RN1.1 (R1.1), RN3.4 (R4.1), SW1.1, U1.11 (D0)
IN1: J3.14, RN1.2 (R2.1), RN3.3 (R3.1), SW2.1, U1.12 (D1)
IN2: J3.12, RN1.3 (R3.1), RN3.2 (R2.1), SW3.1, U1.13 (D2)
IN3: J3.10, RN1.4 (R4.1), RN3.1 (R1.1), SW4.1, U1.14 (D3)
IN4: J3.8, RN2.1 (R1.1), RN4.4 (R4.1), SW5.1, U1.3 (D4)
IN5: J3.6, RN2.2 (R2.1), RN4.3 (R3.1), SW6.1, U1.4 (D5)
IN6: J3.4, RN2.3 (R3.1), RN4.2 (R2.1), SW7.1, U1.5 (D6)
IN7: J3.2, RN2.4 (R4.1), RN4.1 (R1.1), SW8.2, U1.6 (D7)
LED_VCC: LED1.2 (A), LED2.2 (A), LED3.2 (A), LED4.2 (A), LED5.2 (A), LED6.2 (A), LED7.2 (A), LED8.2 (A), Q1.3 (D)
LED_VCC_GATE_T: Q1.1 (G), R1.1, SW0.2 (B)
Load_T: J1.5, J2.5, J6.4, J7.4, RN0.5 (R4.2), U1.1 (~PL)
VCC: J1.2, J2.2, J6.2, J7.2, Q1.2 (S), RN3.5 (R4.2), RN3.6 (R3.2), RN3.7 (R2.2), RN3.8 (R1.2), RN4.5 (R4.2), RN4.6 (R3.2), RN4.7 (R2.2), RN4.8 (R1.2), SW0.3 (C), U1.16 (VCC)

Notes on the sheet:
Control Inputs Connectors
Control Output Connectors
Output LEDs
Shift Register
Shift Register Inputs
LEDs Toggle
CERN-OHL-P v2

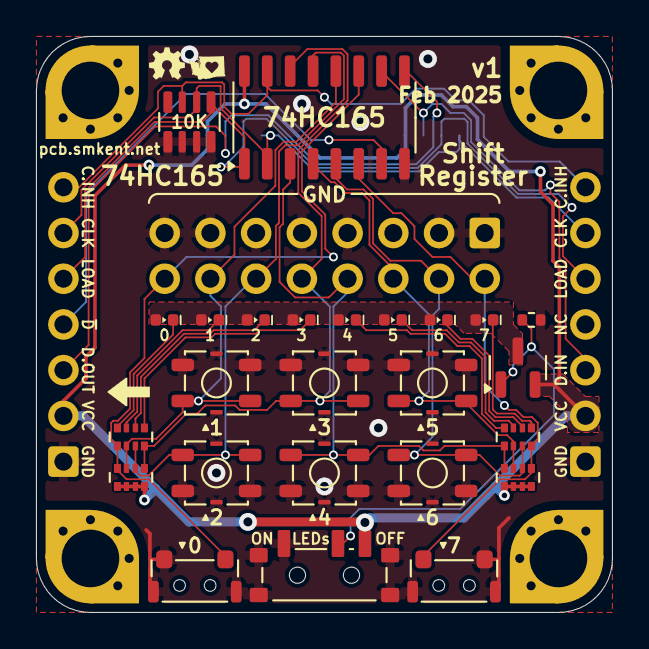
[picture p126: board shift-registers-74hc165.kicad_pcb from above]

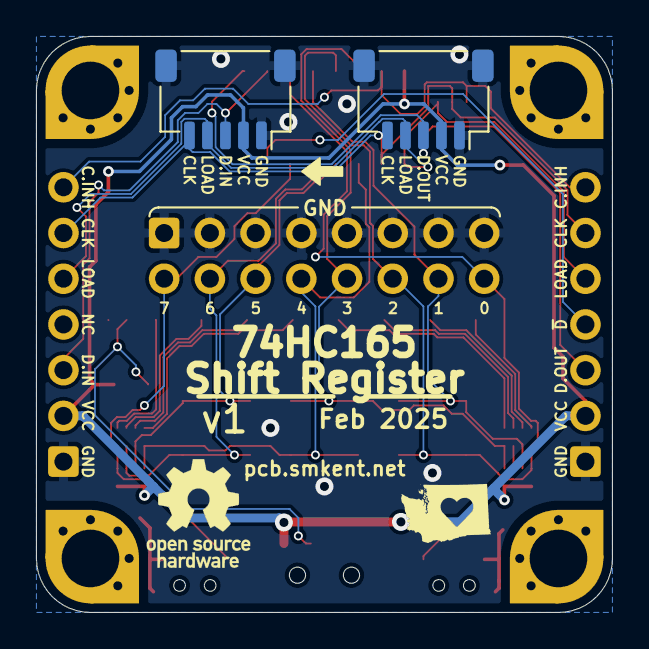
[picture p127: board shift-registers-74hc165.kicad_pcb from below]

Board: 2 copper layers, 32.0 x 32.0 mm, 30 parts (2 on the bottom side), 26 nets.
