smkent/pcb/pcb/stackable3/esp-neopixel-driver/esp-neopixel-driver.kicad_pcb

## KiCad design pcb/stackable3/esp-neopixel-driver/esp-neopixel-driver.kicad_pcb (2025-03-08)

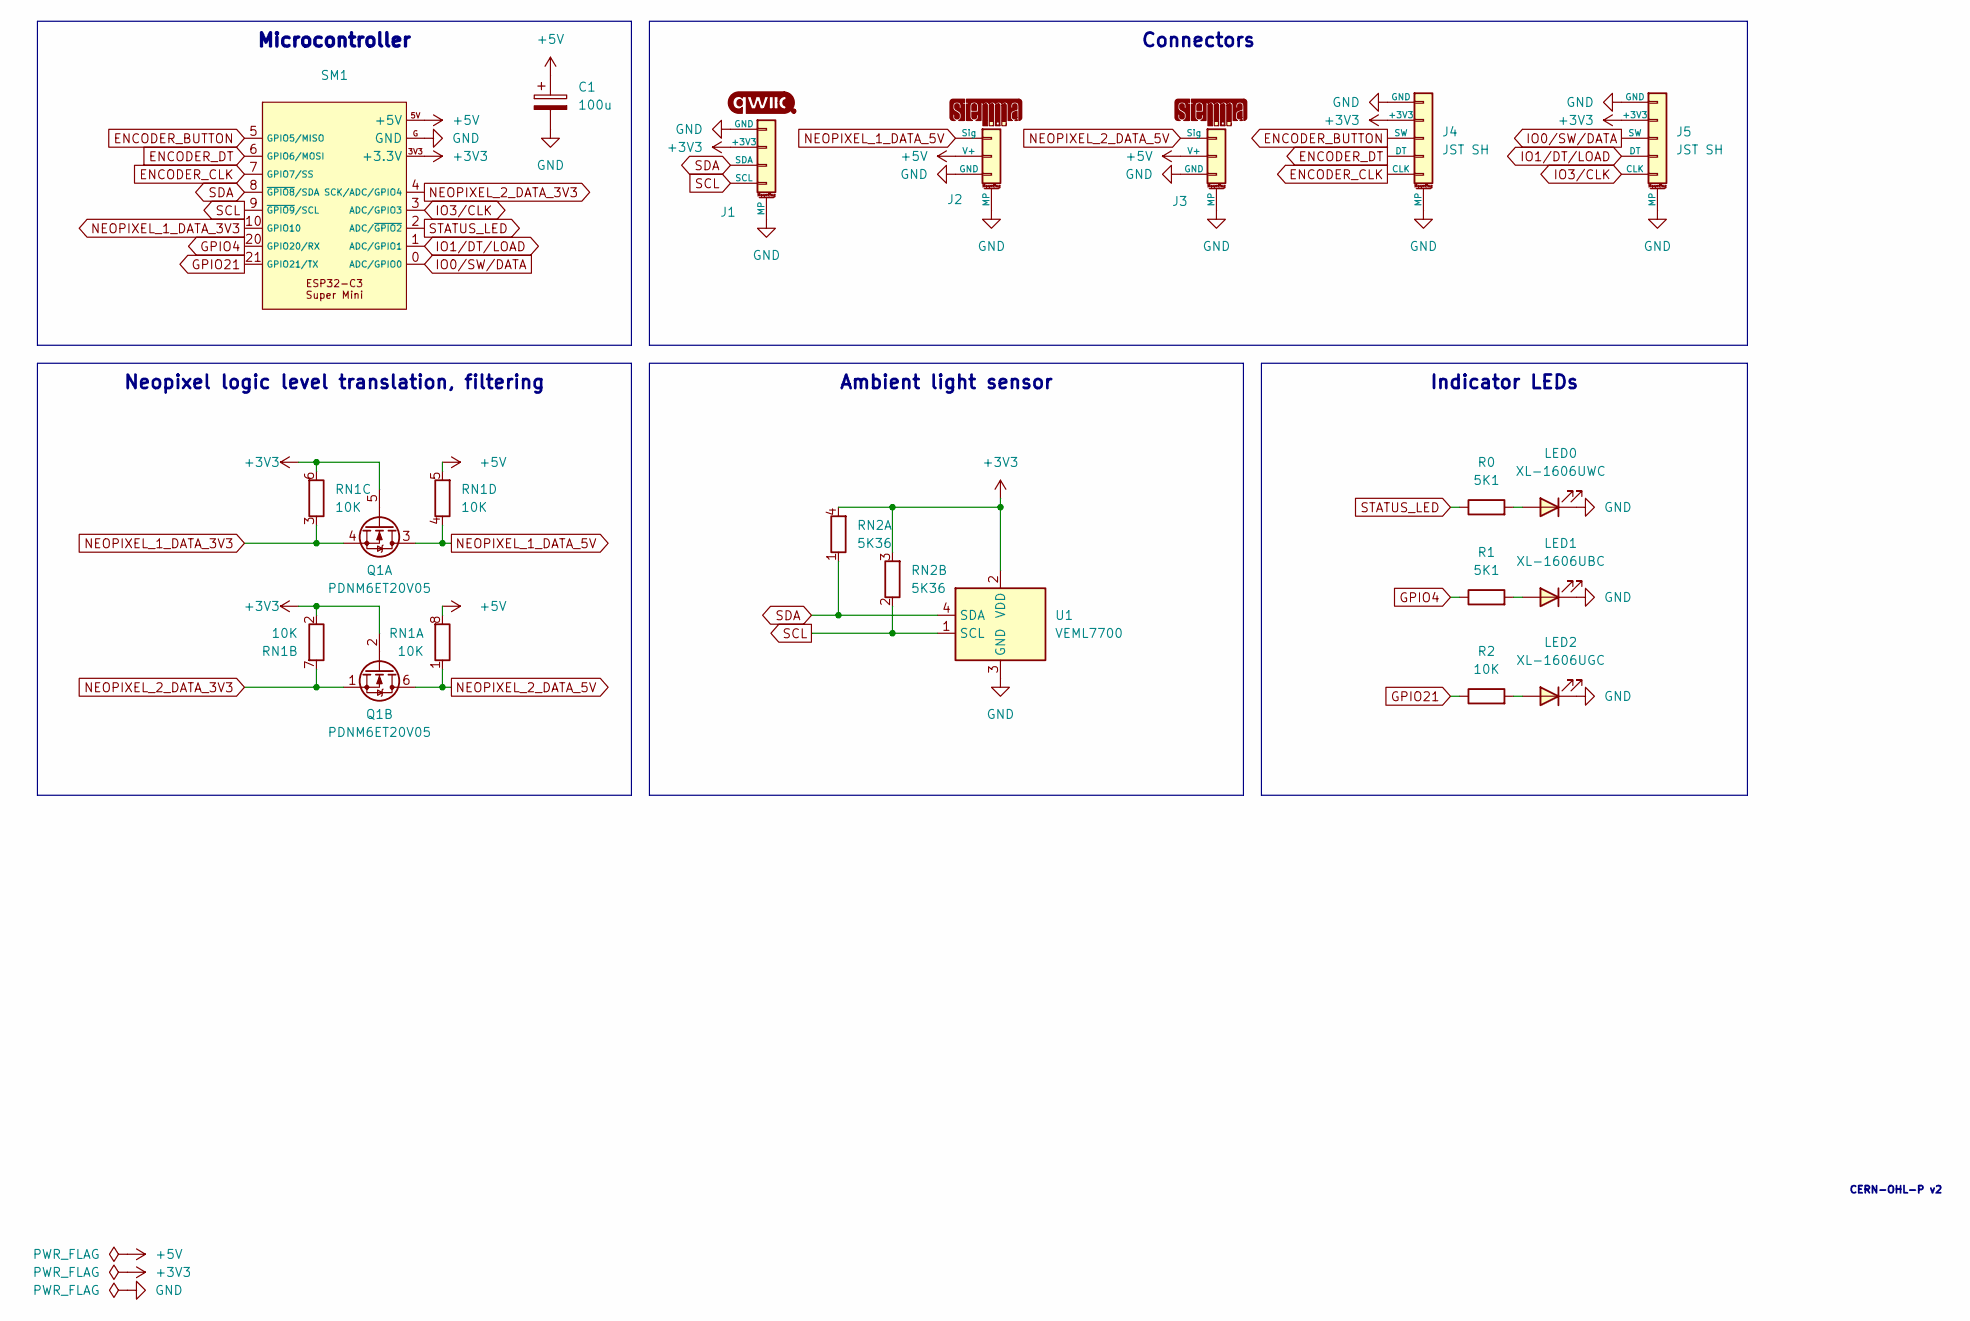
[picture p128: schematic esp-neopixel-driver.kicad_sch]

Parts:
C1: 100u; CP_Elec_5x5.4; LCSC Part C4054379
J1: Qwiic; Qwiic-SMD-horizontal-logo; LCSC Part C19270571
J2, J3: STEMMA-Signal; STEMMA-Signal-SMD-horizontal; LCSC Part C5372880
J4, J5: JST SH; JST_SH_SM05B-SRSS-TB_1x05-1MP_P1.00mm_Horizontal; LCSC Part C7433426
LED0: XL-1606UWC; LED_SideEmitter_1.7x1.1mm; LCSC Part C965866
LED1: XL-1606UBC; LED_SideEmitter_1.7x1.1mm; LCSC Part C965865
LED2: XL-1606UGC; LED_SideEmitter_1.7x1.1mm; LCSC Part C965863
Q1: PDNM6ET20V05; SOT-563; LCSC Part C918811
R0, R1: 5K1; R_0402_1005Metric; LCSC Part C25905
R2: 10K; R_0402_1005Metric; LCSC Part C25744
RN1: 10K; R_Array_Convex_4x0402; LCSC Part C7422173
RN2: 5K36; R_Array_Convex_2x0402; LCSC Part C425352
SM1: ESP32-C3-Super-Mini-Castellated-SMD-only
U1: VEML7700; Sensor_VEML7700-TR; LCSC Part C504893

Connections:
+3V3: J1.2 (+3V3), J4.2 (+3V3), J5.2 (+3V3), Q1.2 (G), Q1.5 (G), RN1.2 (R2.1), RN1.6 (R3.2), RN2.3 (R2.2), RN2.4 (R1.2), SM1.3V3 (+3.3V), U1.2 (VDD)
+5V: C1.1, J2.2 (V+), J3.2 (V+), RN1.5 (R4.2), RN1.8 (R1.2), SM1.5V (+5V)
ENCODER_BUTTON: J4.3 (SW), SM1.5 (GPIO5/MISO)
ENCODER_CLK: J4.5 (CLK), SM1.7 (GPIO7/SS)
ENCODER_DT: J4.4 (DT), SM1.6 (GPIO6/MOSI)
GND: C1.2, J1.1 (GND), J1.MP, J2.3 (GND), J2.MP, J3.3 (GND), J3.MP, J4.1 (GND), J4.MP, J5.1 (GND), J5.MP, LED0.1 (K), LED1.1 (K), LED2.1 (K), SM1.G (GND), U1.3 (GND)
GPIO4: R1.1, SM1.20 (GPIO20/RX)
GPIO21: R2.1, SM1.21 (GPIO21/TX)
IO0/SW/DATA: J5.3 (SW), SM1.0 (ADC/GPIO0)
IO1/DT/LOAD: J5.4 (DT), SM1.1 (ADC/GPIO1)
IO3/CLK: J5.5 (CLK), SM1.3 (ADC/GPIO3)
NEOPIXEL_1_DATA_3V3: Q1.4 (S), RN1.3 (R3.1), SM1.10 (GPIO10)
NEOPIXEL_1_DATA_5V: J2.1 (Sig), Q1.3 (D), RN1.4 (R4.1)
NEOPIXEL_2_DATA_3V3: Q1.1 (S), RN1.7 (R2.2), SM1.4 (SCK/ADC/GPIO4)
NEOPIXEL_2_DATA_5V: J3.1 (Sig), Q1.6 (D), RN1.1 (R1.1)
unnamed: LED0.2 (A), R0.2
unnamed: LED1.2 (A), R1.2
unnamed: LED2.2 (A), R2.2
SCL: J1.4 (SCL), RN2.2 (R2.1), SM1.9 (~GPIO9/SCL), U1.1 (SCL)
SDA: J1.3 (SDA), RN2.1 (R1.1), SM1.8 (~GPIO8/SDA), U1.4 (SDA)
STATUS_LED: R0.1, SM1.2 (ADC/~GPIO2)

Notes on the sheet:
Ambient light sensor
Connectors
Neopixel logic level translation, filtering
Indicator LEDs
Microcontroller
CERN-OHL-P v2

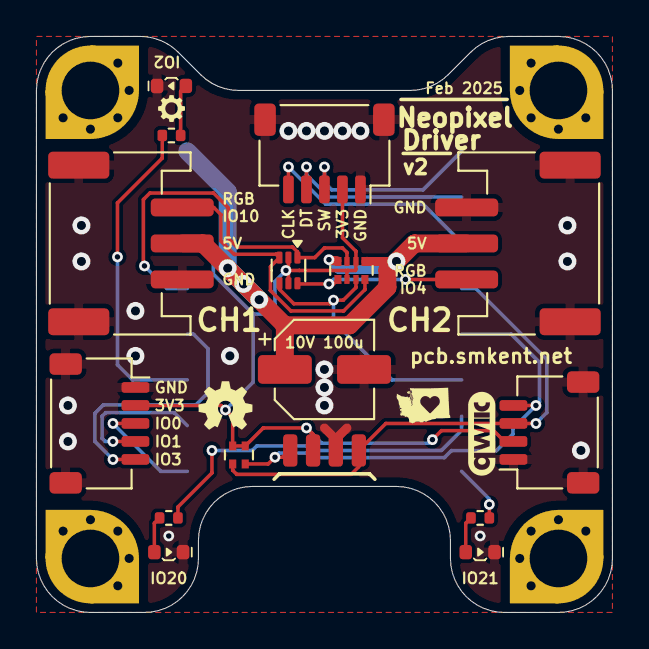
[picture p129: board pcb/stackable3/esp-neopixel-driver/esp-neopixel-driver.kicad_pcb from above]

Board: 2 copper layers, 32.0 x 32.0 mm, 17 parts (1 on the bottom side), 21 nets.
