smkent/pcb/pcb/stackable3/shift-registers-74hc595/shift-registers-74hc595.kicad_pcb

## KiCad design pcb/stackable3/shift-registers-74hc595/shift-registers-74hc595.kicad_pcb (2025-02-14)

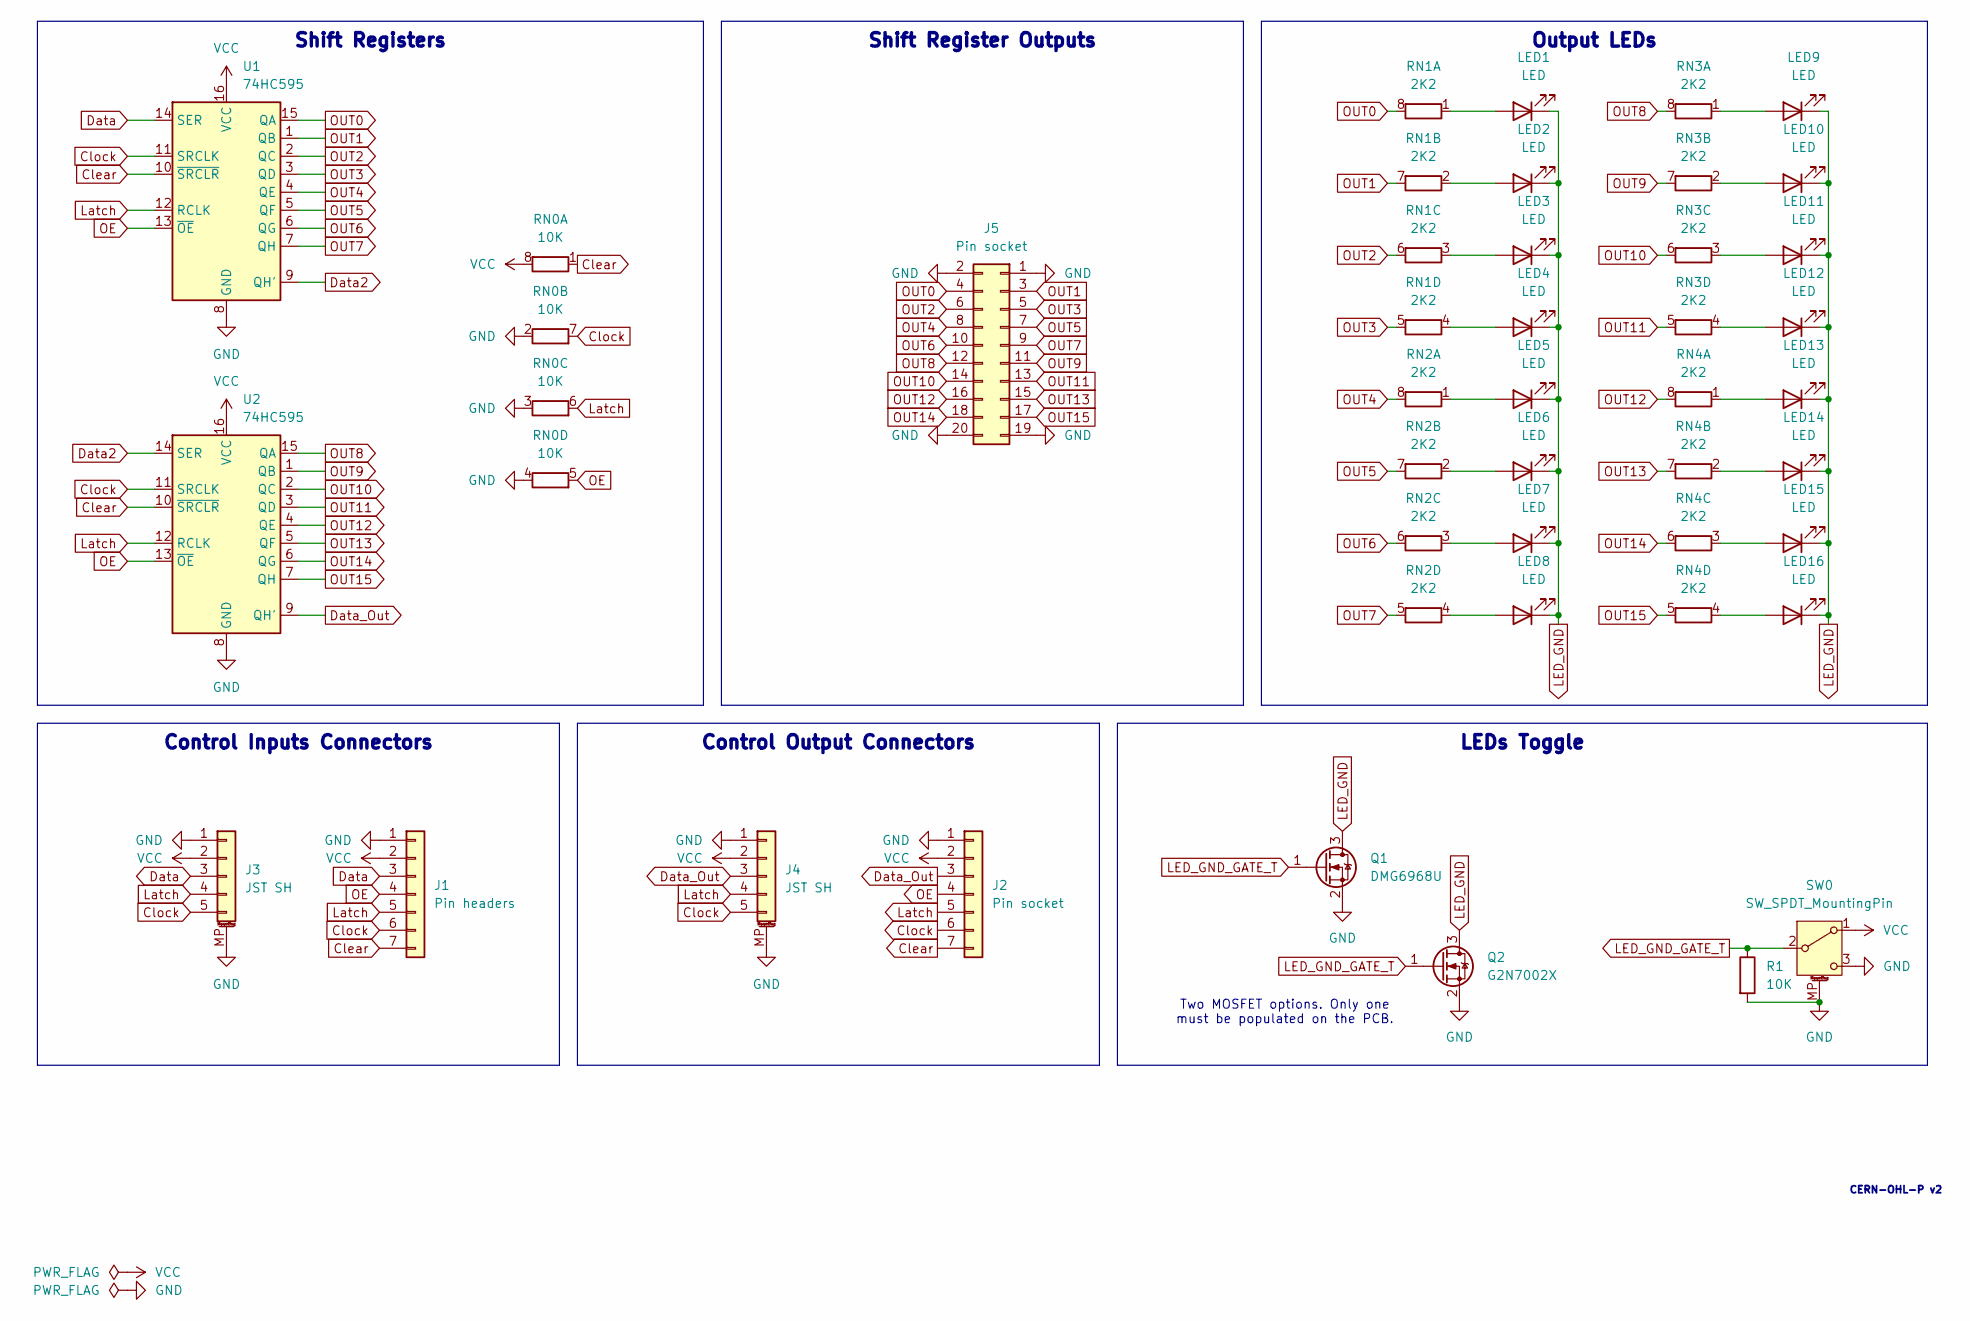
[picture p130: schematic shift-registers-74hc595.kicad_sch, Shift Registers 74HC595]

Parts:
J1: Pin headers; PinHeader_1x07_P2.54mm_Horizontal
J2: Pin socket; PinSocket_1x07_P2.54mm_Horizontal
J3, J4: JST SH; JST_SH_SM05B-SRSS-TB_1x05-1MP_P1.00mm_Horizontal; LCSC Part C7433426
J5: Pin socket; PinHeader_2x10_P2.54mm_Vertical
LED1, LED2, LED3, LED4, LED5, LED6, LED7, LED8, LED9, LED10, LED11, LED12, LED13, LED14, LED15, LED16: LED; LED_0603_1608Metric
Q1: DMG6968U; SOT-23; LCSC Part C150759
Q2: G2N7002X; SOT-523; LCSC Part C5258971
R1: 10K; R_0402_1005Metric
RN0: 10K; R_Array_Convex_4x0402; LCSC Part C110924
RN1, RN2, RN3, RN4: 2K2; R_Array_Convex_4x0603_HandSolder
SW0: SW_SPDT_MountingPin; SW_SPDT_PCM12; LCSC Part C319020
U1, U2: 74HC595; SOIC-16_3.9x9.9mm_P1.27mm

Connections:
Clear: J1.7, J2.7, RN0.1 (R1.1), U1.10 (~SRCLR), U2.10 (~SRCLR)
Clock: J1.6, J2.6, J3.5, J4.5, RN0.7 (R2.2), U1.11 (SRCLK), U2.11 (SRCLK)
Data: J1.3, J3.3, U1.14 (SER)
Data2: U1.9 (QH'), U2.14 (SER)
Data_Out: J2.3, J4.3, U2.9 (QH')
GND: J1.1, J2.1, J3.1, J3.MP (MountPin), J4.1, J4.MP (MountPin), J5.1, J5.2, J5.19, J5.20, Q1.2 (S), Q2.2 (S), R1.2, RN0.2 (R2.1), RN0.3 (R3.1), RN0.4 (R4.1), SW0.3 (C), SW0.MP (MountPin), U1.8 (GND), U2.8 (GND)
LED_GND: LED1.1 (K), LED2.1 (K), LED3.1 (K), LED4.1 (K), LED5.1 (K), LED6.1 (K), LED7.1 (K), LED8.1 (K), LED9.1 (K), LED10.1 (K), LED11.1 (K), LED12.1 (K), LED13.1 (K), LED14.1 (K), LED15.1 (K), LED16.1 (K), Q1.3 (D), Q2.3 (D)
LED_GND_GATE_T: Q1.1 (G), Q2.1 (G), R1.1, SW0.2 (B)
Latch: J1.5, J2.5, J3.4, J4.4, RN0.6 (R3.2), U1.12 (RCLK), U2.12 (RCLK)
unnamed: LED1.2 (A), RN1.1 (R1.1)
unnamed: LED2.2 (A), RN1.2 (R2.1)
unnamed: LED3.2 (A), RN1.3 (R3.1)
unnamed: LED4.2 (A), RN1.4 (R4.1)
unnamed: LED5.2 (A), RN2.1 (R1.1)
unnamed: LED6.2 (A), RN2.2 (R2.1)
unnamed: LED7.2 (A), RN2.3 (R3.1)
unnamed: LED8.2 (A), RN2.4 (R4.1)
unnamed: LED9.2 (A), RN3.1 (R1.1)
unnamed: LED10.2 (A), RN3.2 (R2.1)
unnamed: LED11.2 (A), RN3.3 (R3.1)
unnamed: LED12.2 (A), RN3.4 (R4.1)
unnamed: LED13.2 (A), RN4.1 (R1.1)
unnamed: LED14.2 (A), RN4.2 (R2.1)
unnamed: LED15.2 (A), RN4.3 (R3.1)
unnamed: LED16.2 (A), RN4.4 (R4.1)
OE: J1.4, J2.4, RN0.5 (R4.2), U1.13 (~OE), U2.13 (~OE)
OUT0: J5.4, RN1.8 (R1.2), U1.15 (QA)
OUT1: J5.3, RN1.7 (R2.2), U1.1 (QB)
OUT2: J5.6, RN1.6 (R3.2), U1.2 (QC)
OUT3: J5.5, RN1.5 (R4.2), U1.3 (QD)
OUT4: J5.8, RN2.8 (R1.2), U1.4 (QE)
OUT5: J5.7, RN2.7 (R2.2), U1.5 (QF)
OUT6: J5.10, RN2.6 (R3.2), U1.6 (QG)
OUT7: J5.9, RN2.5 (R4.2), U1.7 (QH)
OUT8: J5.12, RN3.8 (R1.2), U2.15 (QA)
OUT9: J5.11, RN3.7 (R2.2), U2.1 (QB)
OUT10: J5.14, RN3.6 (R3.2), U2.2 (QC)
OUT11: J5.13, RN3.5 (R4.2), U2.3 (QD)
OUT12: J5.16, RN4.8 (R1.2), U2.4 (QE)
OUT13: J5.15, RN4.7 (R2.2), U2.5 (QF)
OUT14: J5.18, RN4.6 (R3.2), U2.6 (QG)
OUT15: J5.17, RN4.5 (R4.2), U2.7 (QH)
VCC: J1.2, J2.2, J3.2, J4.2, RN0.8 (R1.2), SW0.1 (A), U1.16 (VCC), U2.16 (VCC)

Notes on the sheet:
Output LEDs
Control Inputs Connectors
Shift Registers
Control Output Connectors
LEDs Toggle
Shift Register Outputs
CERN-OHL-P v2
Two MOSFET options. Only one must be populated on the PCB.

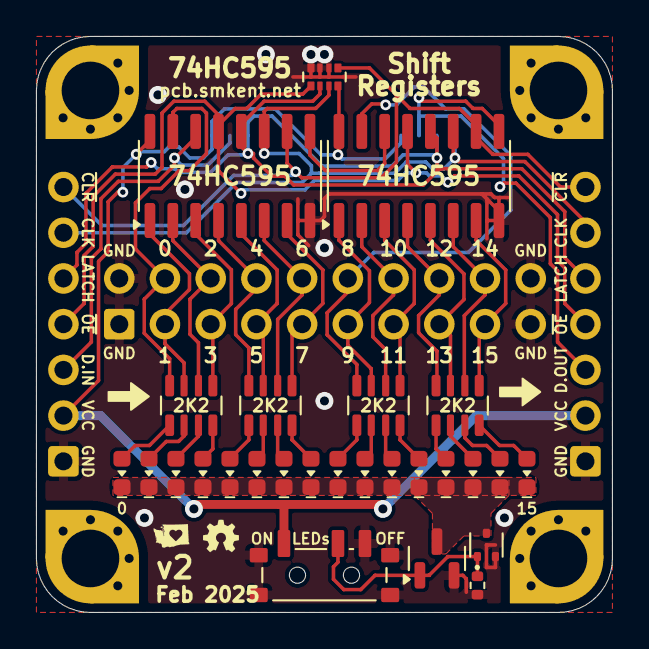
[picture p131: board shift-registers-74hc595.kicad_pcb from above]

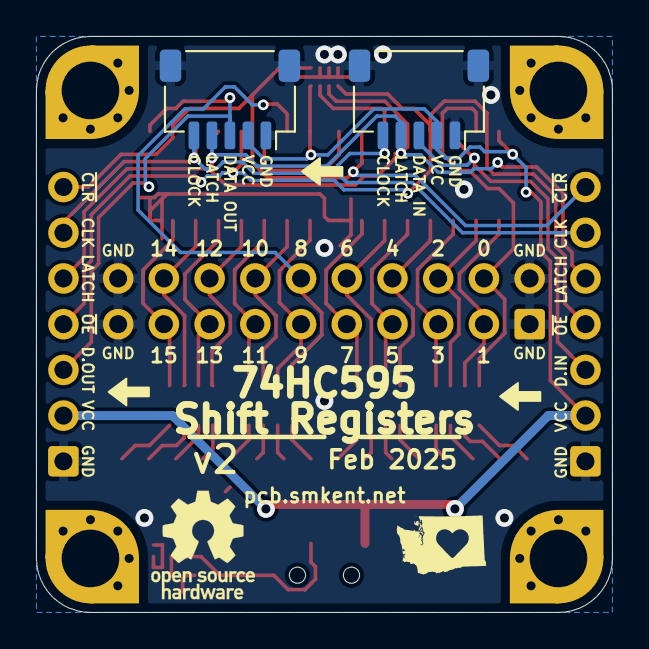
[picture p132: board shift-registers-74hc595.kicad_pcb from below]

Board: 2 copper layers, 32.0 x 32.0 mm, 32 parts (2 on the bottom side), 43 nets.
