smkent/pcb/pcb/stackable3/ir-trx/ir-trx.kicad_pcb

## KiCad design pcb/stackable3/ir-trx/ir-trx.kicad_pcb (2025-02-14)

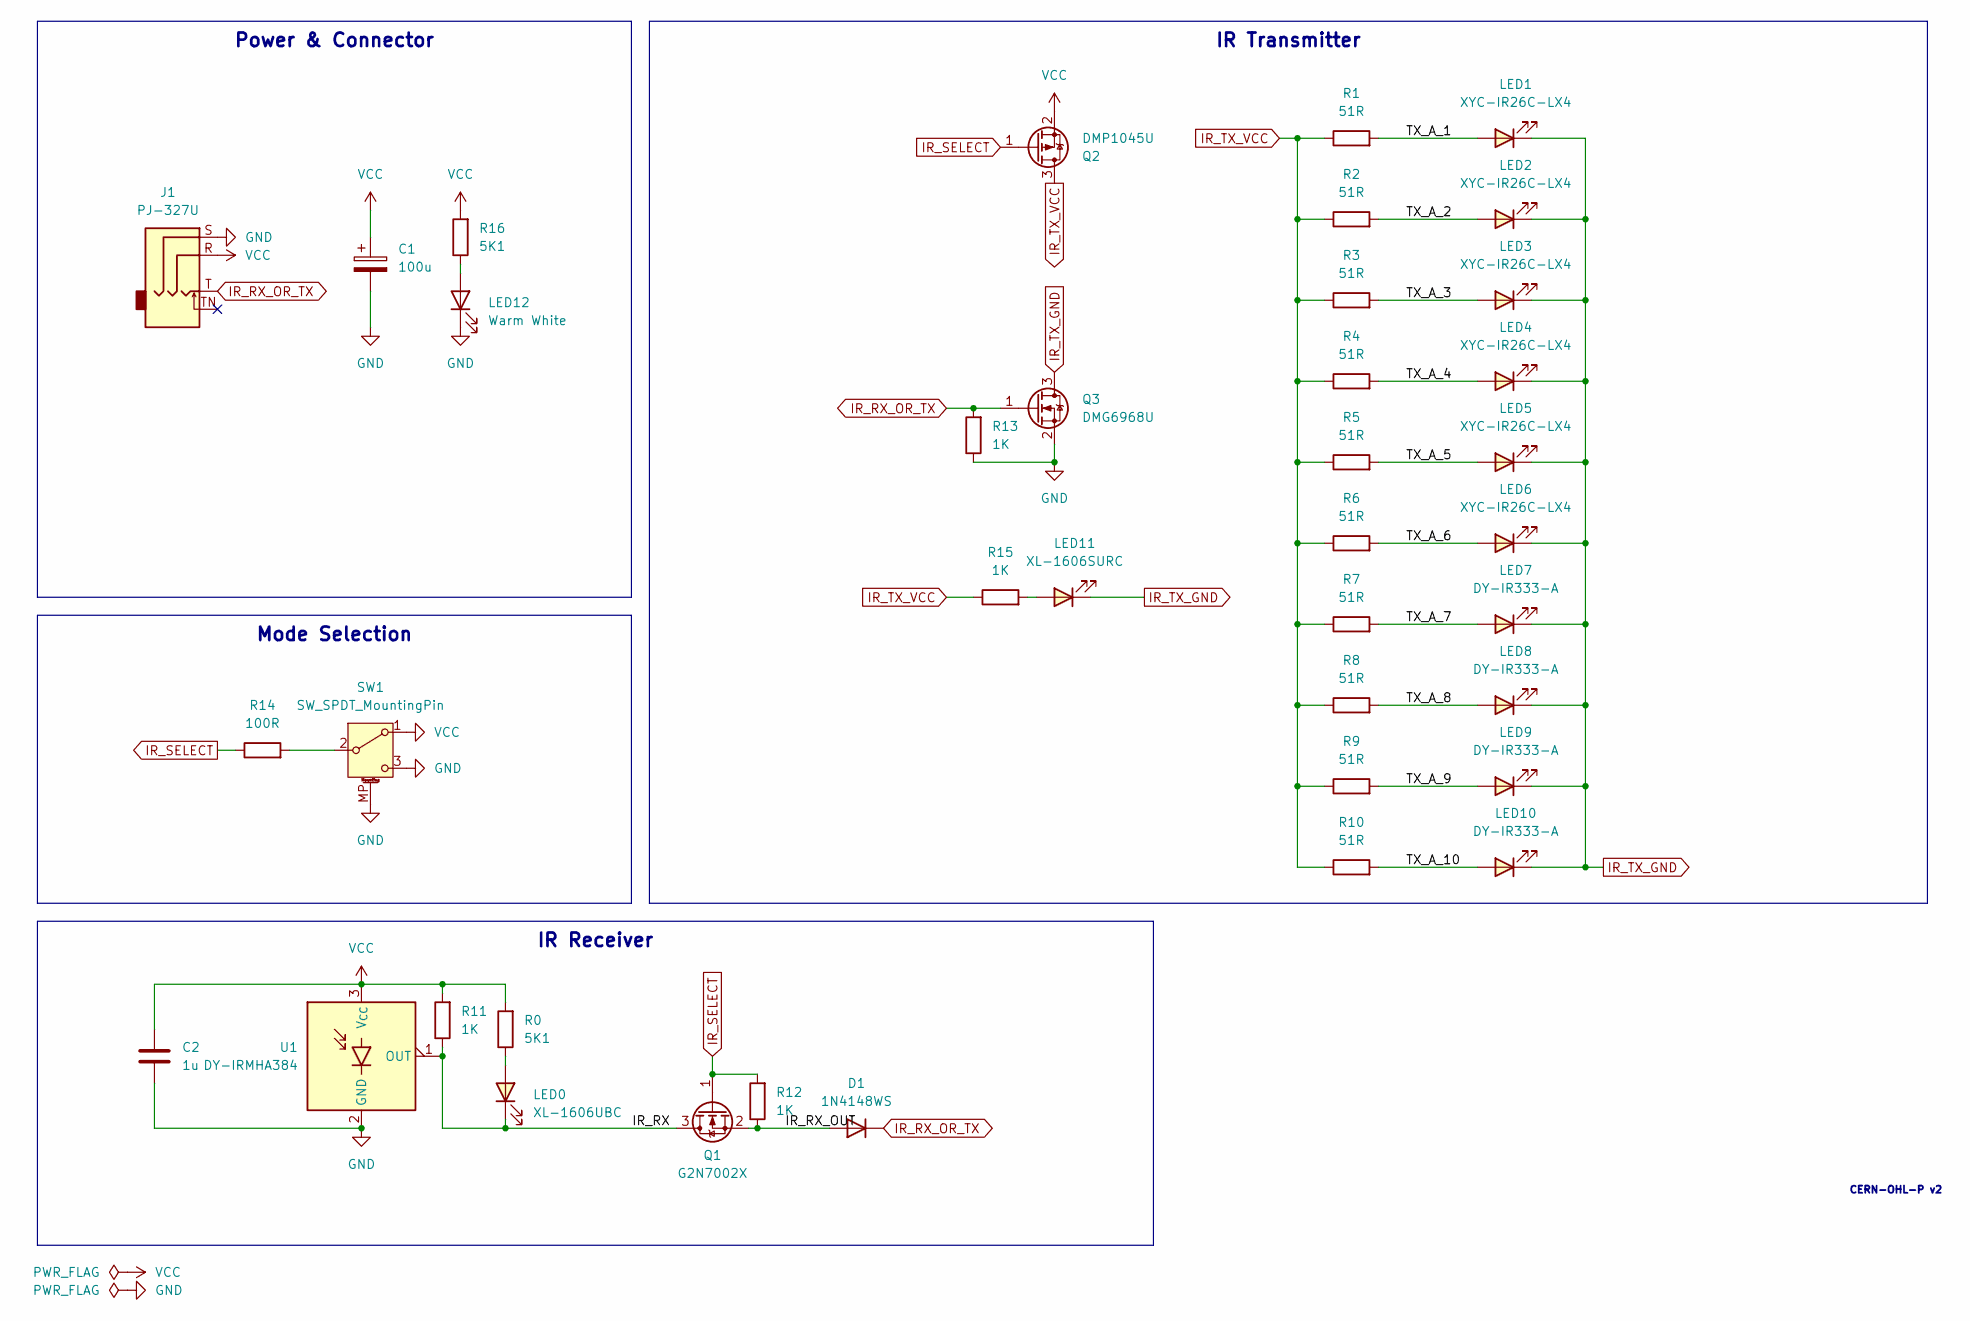
[picture p133: schematic ir-trx.kicad_sch]

Parts:
C1: 100u; CP_Elec_5x5.4
C2: 1u; C_0402_1005Metric
D1: 1N4148WS; D_SOD-323
J1: PJ-327U; Jack_3.5mm_PJ-327U-SMT_Horizontal_EdgeCut; LCSC Part C397453
LED0: XL-1606UBC; LED_SideEmitter_1.7x1.1mm; LCSC Part C965865
LED1, LED2, LED3, LED4, LED5, LED6: XYC-IR26C-LX4; LED_IR_SideEmitter_1206_3216Metric; LCSC Part C396674
LED7, LED8, LED9, LED10: DY-IR333-A; LED_D5.0mm_IRGrey; LCSC Part C396674
LED11: XL-1606SURC; LED_SideEmitter_1.7x1.1mm; LCSC Part C965860
LED12: Warm White; LED_0603_1608Metric
Q1: G2N7002X; SOT-523; LCSC Part C5258971
Q2: DMP1045U; SOT-23; LCSC Part C177033
Q3: DMG6968U; SOT-23; LCSC Part C150759
R0, R16: 5K1; R_0402_1005Metric
R1, R2, R3, R4, R5, R6, R7, R8, R9, R10: 51R; R_1206_3216Metric; LCSC Part C149687
R11, R12, R13, R15: 1K; R_0402_1005Metric
R14: 100R; R_0603_1608Metric
SW1: SW_SPDT_MountingPin; SW_Slide_SPDT_Straight_CK_OS102011MS2Q
U1: DY-IRMHA384; IRM_5.0mmx4.2mm_P1.27mm_Horizontal; LCSC Part C6071554

Connections:
/IR_RX: LED0.1 (K), Q1.3 (D), R11.1, U1.1 (OUT)
/IR_RX_OUT: D1.2 (A), Q1.2 (S), R12.1
/TX_A_1: LED1.2 (A), R1.2
/TX_A_2: LED2.2 (A), R2.2
/TX_A_3: LED3.2 (A), R3.2
/TX_A_4: LED4.2 (A), R4.2
/TX_A_5: LED5.2 (A), R5.2
/TX_A_6: LED6.2 (A), R6.2
/TX_A_7: LED7.2 (A), R7.2
/TX_A_8: LED8.2 (A), R8.2
/TX_A_9: LED9.2 (A), R9.2
/TX_A_10: LED10.2 (A), R10.2
GND: C1.2, C2.2, J1.S, LED12.1 (K), Q3.2 (S), R13.1, SW1.3 (C), SW1.MP (MountPin), U1.2 (GND)
IR_RX_OR_TX: D1.1 (K), J1.T, Q3.1 (G), R13.2
IR_SELECT: Q1.1 (G), Q2.1 (G), R12.2, R14.1
IR_TX_GND: LED1.1 (K), LED2.1 (K), LED3.1 (K), LED4.1 (K), LED5.1 (K), LED6.1 (K), LED7.1 (K), LED8.1 (K), LED9.1 (K), LED10.1 (K), LED11.1 (K), Q3.3 (D)
IR_TX_VCC: Q2.3 (D), R1.1, R2.1, R3.1, R4.1, R5.1, R6.1, R7.1, R8.1, R9.1, R10.1, R15.1
unnamed: LED0.2 (A), R0.1
unnamed: LED11.2 (A), R15.2
unnamed: LED12.2 (A), R16.1
unnamed: R14.2, SW1.2 (B)
VCC: C1.1, C2.1, J1.R, Q2.2 (S), R0.2, R11.2, R16.2, SW1.1 (A), U1.3 (V_{CC})

Notes on the sheet:
Power & Connector
Mode Selection
IR Receiver
IR Transmitter
CERN-OHL-P v2

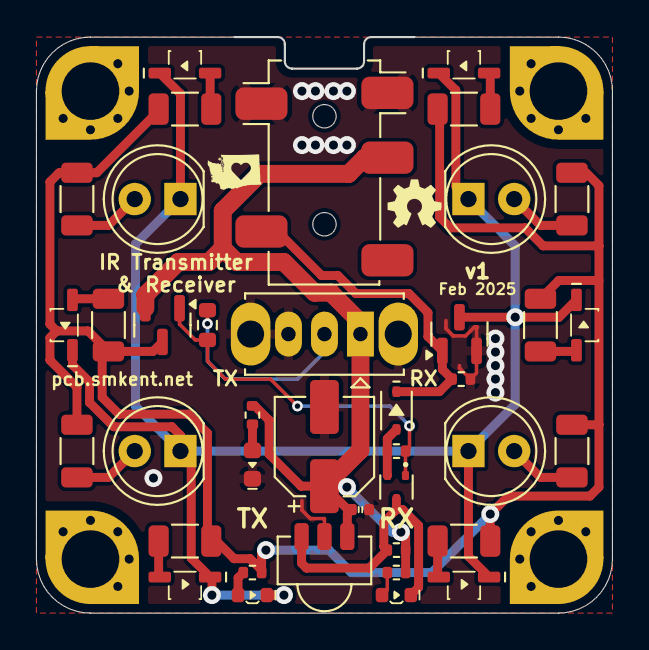
[picture p134: board ir-trx.kicad_pcb from above]

Board: 2 copper layers, 32.0 x 32.0 mm, 39 parts (0 on the bottom side), 22 nets.
