smkent/pcb/pcb/stackable3/power-selector-dev/power-selector-dev.kicad_pcb

## KiCad design pcb/stackable3/power-selector-dev/power-selector-dev.kicad_pcb (2025-02-13)

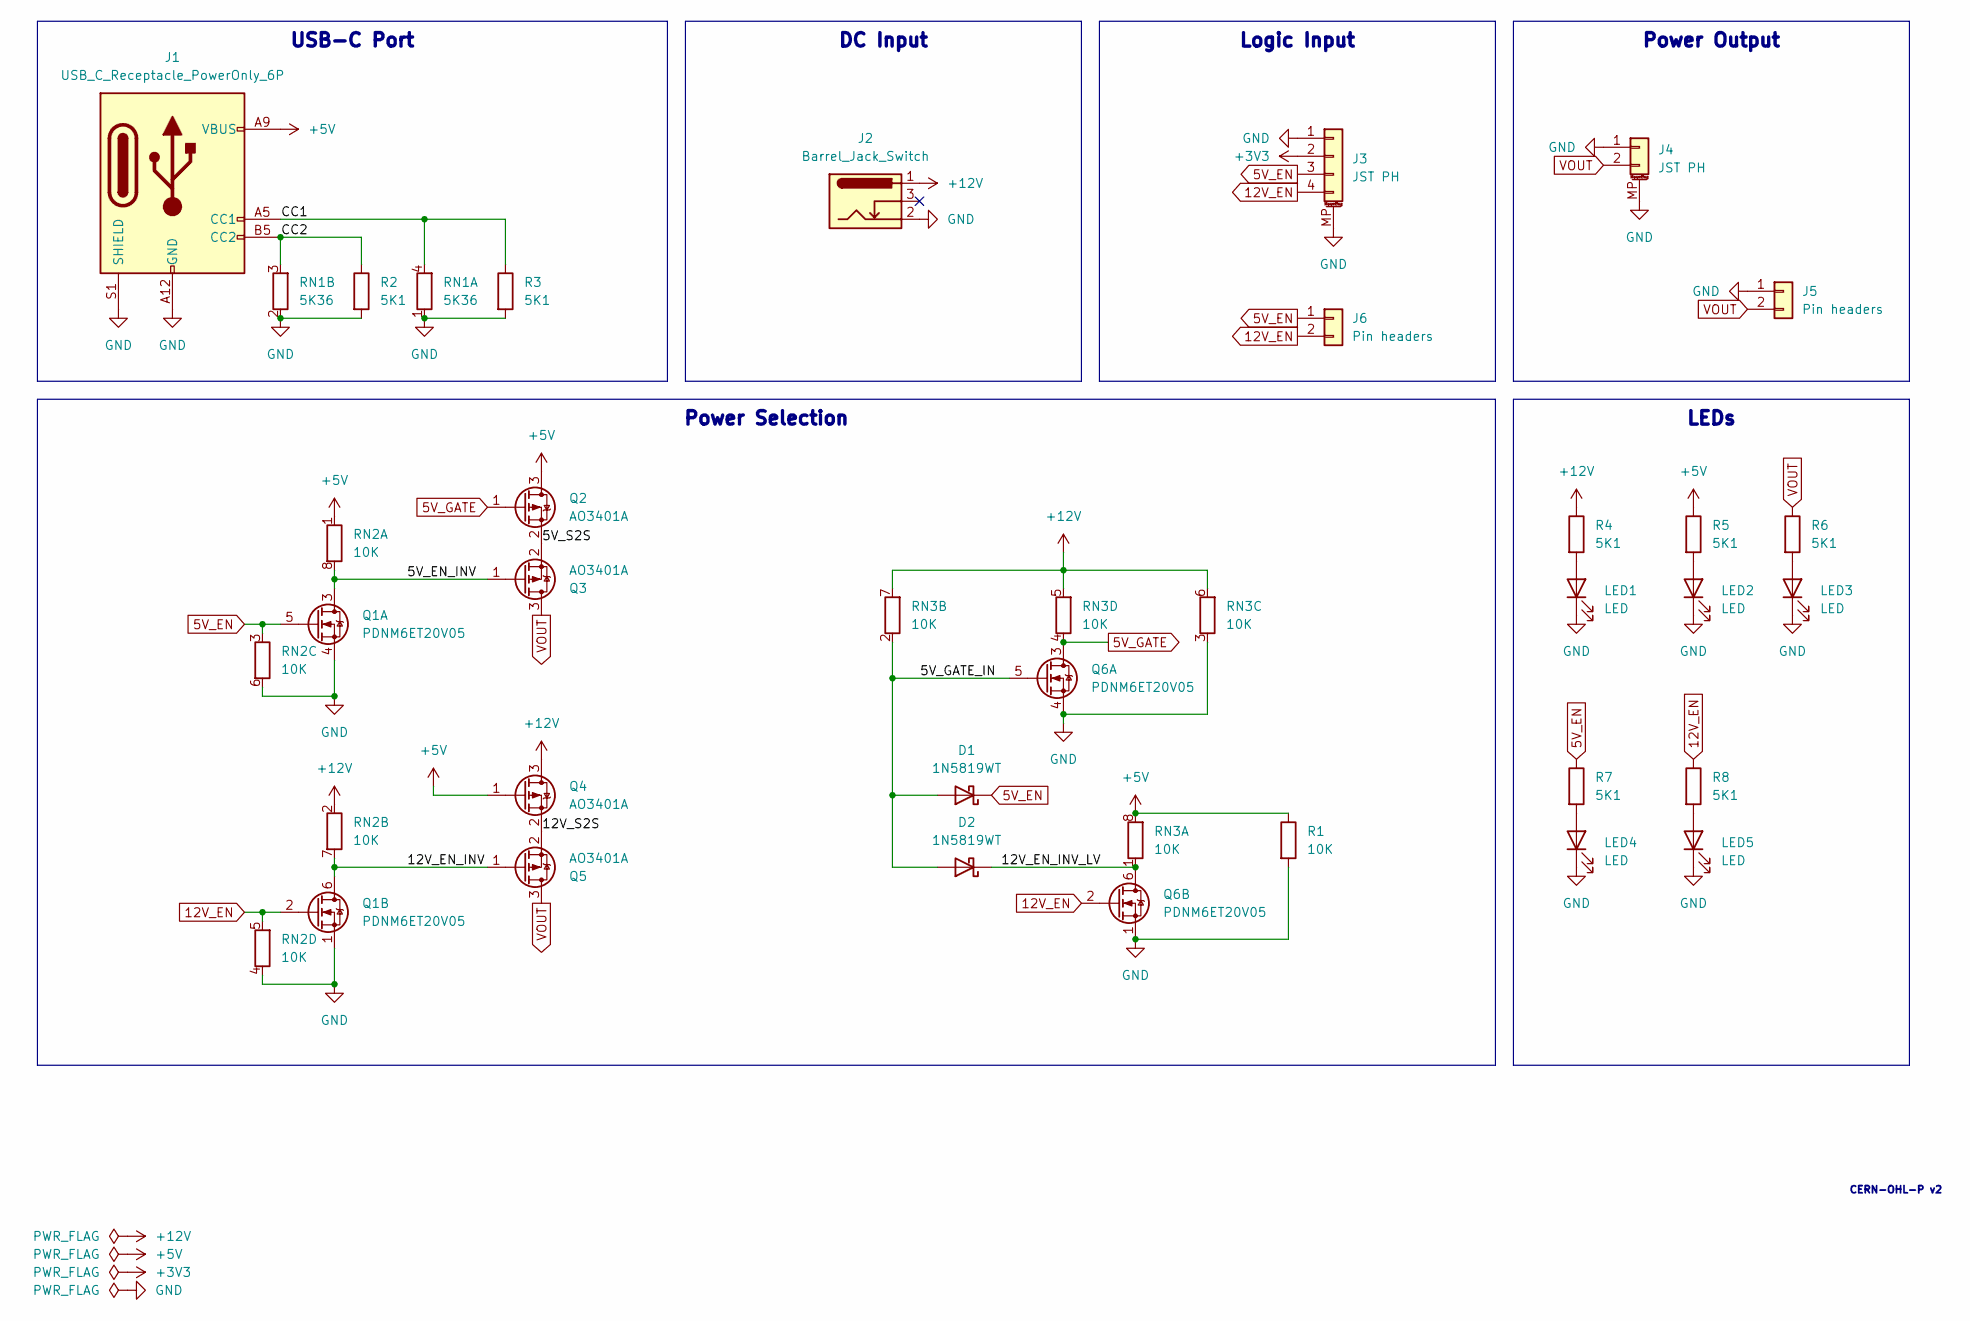
[picture p135: schematic power-selector-dev.kicad_sch]

Parts:
D1, D2: 1N5819WT; D_SOD-523; LCSC Part C20754784
J1: USB_C_Receptacle_PowerOnly_6P; USB_C_Receptacle_GCT_USB4125-xx-x_6P_TopMnt_Horizontal_Hand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; LCSC Part C2927029
J2: Barrel_Jack_Switch; BarrelJack_DC-050_SMT_Horizontal
J3: JST PH; JST_PH_S4B-PH-SM4-TB_1x04-1MP_P2.00mm_Horizontal
J4: JST PH; JST_PH_S2B-PH-SM4-TB_1x02-1MP_P2.00mm_Horizontal
J5, J6: Pin headers; PinHeader_1x02_P2.54mm_Vertical_simple
LED1, LED2, LED3, LED4, LED5: LED; LED_0603_1608Metric
Q1, Q6: PDNM6ET20V05; SOT-563; LCSC Part C918811
Q2, Q3, Q4, Q5: AO3401A; SOT-23
R1: 10K; R_0402_1005Metric
R2, R3, R4, R5, R6: 5K1; R_0603_1608Metric
R7, R8: 5K1; R_0402_1005Metric
RN1: 5K36; R_Array_Convex_2x0402
RN2, RN3: 10K; R_Array_Convex_4x0402

Connections:
5V_EN: D1.1 (K), J3.3, J6.1, Q1.5 (G), R7.1, RN2.3 (R3.1)
5V_GATE: Q2.1 (G), Q6.3 (D), RN3.4 (R4.1)
12V_EN: J3.4, J6.2, Q1.2 (G), Q6.2 (G), R8.1, RN2.5 (R4.2)
+3V3: J3.2
+5V: J1.A9 (VBUS), J1.B9 (VBUS), Q2.3 (D), Q4.1 (G), R1.1, R5.1, RN2.1 (R1.1), RN3.8 (R1.2)
+12V: J2.1, Q4.3 (D), R4.1, RN2.2 (R2.1), RN3.5 (R4.2), RN3.6 (R3.2), RN3.7 (R2.2)
/5V_EN_INV: Q1.3 (D), Q3.1 (G), RN2.8 (R1.2)
/5V_GATE_IN: D1.2 (A), D2.2 (A), Q6.5 (G), RN3.2 (R2.1)
/5V_S2S: Q2.2 (S), Q3.2 (S)
/12V_EN_INV: Q1.6 (D), Q5.1 (G), RN2.7 (R2.2)
/12V_EN_INV_LV: D2.1 (K), Q6.6 (D), RN3.1 (R1.1)
/12V_S2S: Q4.2 (S), Q5.2 (S)
/CC1: J1.A5 (CC1), R3.1, RN1.4 (R1.2)
/CC2: J1.B5 (CC2), R2.1, RN1.3 (R2.2)
GND: J1.A12 (GND), J1.B12 (GND), J1.S1 (SHIELD), J2.2, J3.1, J3.MP (MountPin), J4.1, J4.MP (MountPin), J5.1, LED1.1 (K), LED2.1 (K), LED3.1 (K), LED4.1 (K), LED5.1 (K), Q1.1 (S), Q1.4 (S), Q6.1 (S), Q6.4 (S), R1.2, R2.2, R3.2, RN1.1 (R1.1), RN1.2 (R2.1), RN2.4 (R4.1), RN2.6 (R3.2), RN3.3 (R3.1)
unnamed: LED1.2 (A), R4.2
unnamed: LED2.2 (A), R5.2
unnamed: LED3.2 (A), R6.2
unnamed: LED4.2 (A), R7.2
unnamed: LED5.2 (A), R8.2
VOUT: J4.2, J5.2, Q3.3 (D), Q5.3 (D), R6.1

Notes on the sheet:
Logic Input
DC Input
Power Output
USB-C Port
Power Selection
LEDs
CERN-OHL-P v2

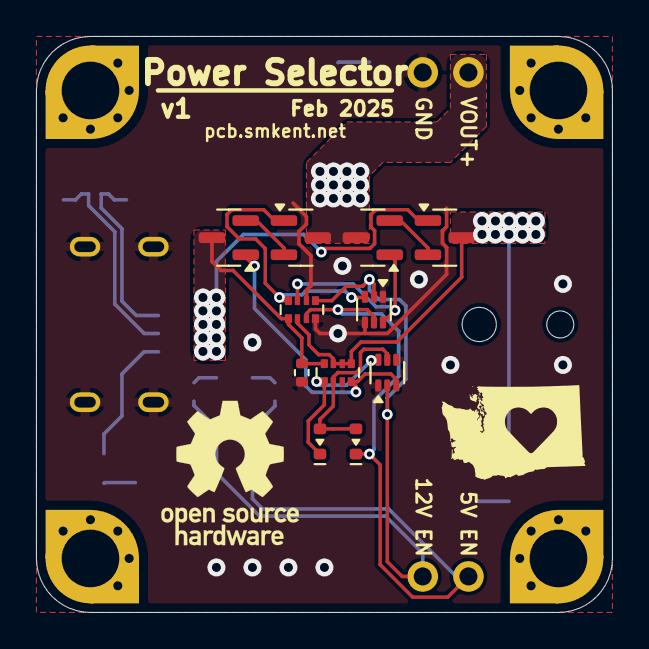
[picture p136: board power-selector-dev.kicad_pcb from above]

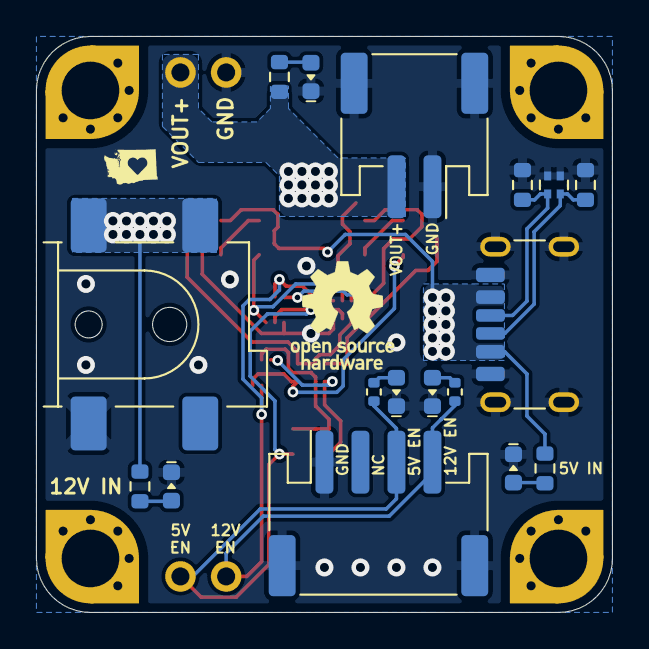
[picture p137: board power-selector-dev.kicad_pcb from below]

Board: 2 copper layers, 32.0 x 32.0 mm, 30 parts (19 on the bottom side), 20 nets.
