smkent/pcb/pcb/stackable3/esp-doorbell-dev/esp-doorbell-dev.kicad_pcb

## KiCad design pcb/stackable3/esp-doorbell-dev/esp-doorbell-dev.kicad_pcb (2025-02-11)

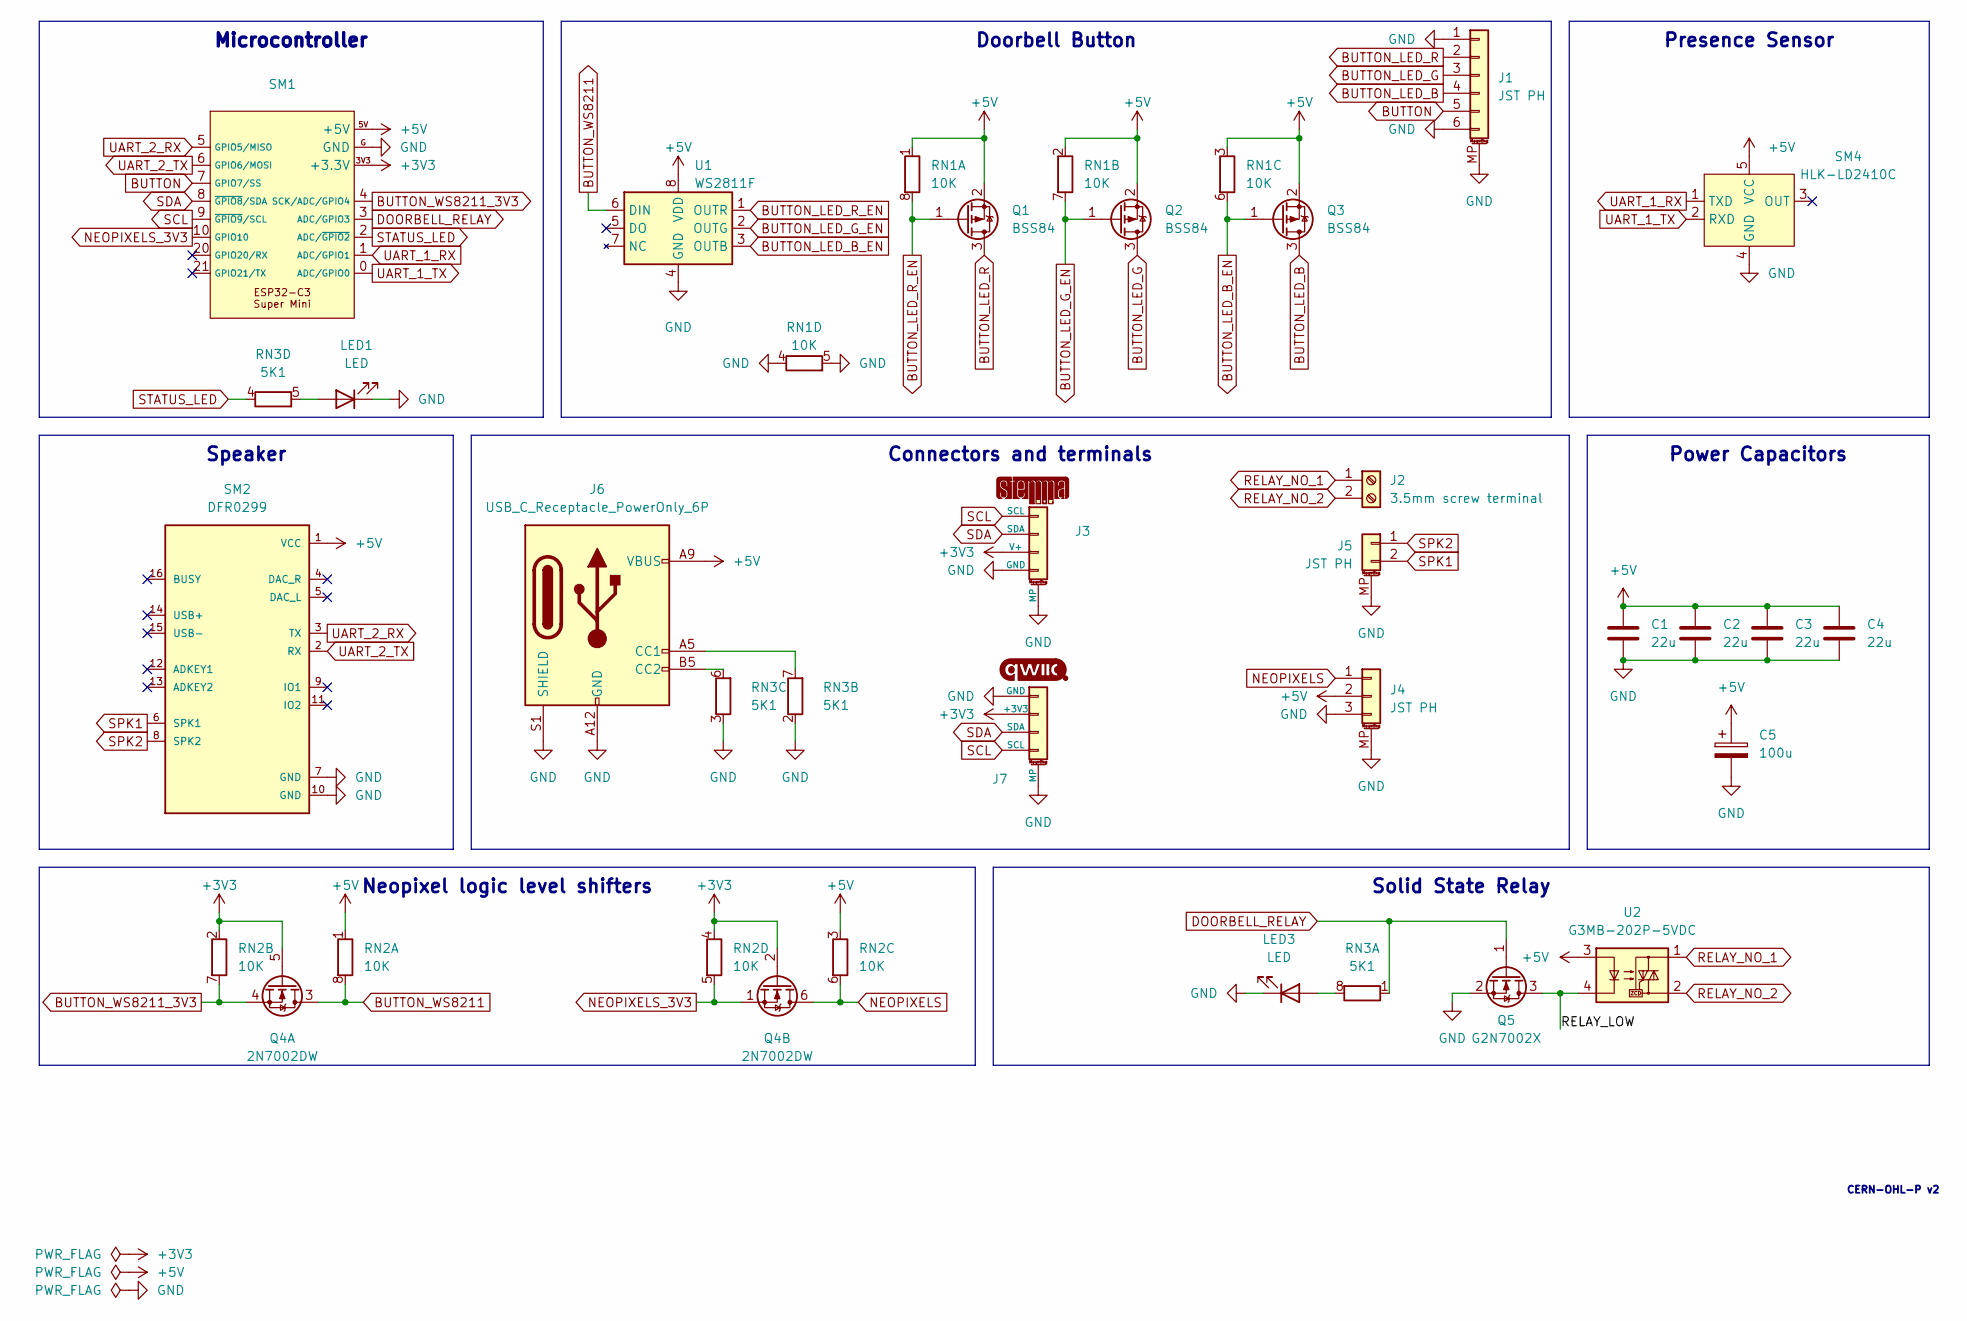
[picture p138: schematic esp-doorbell-dev.kicad_sch]

Parts:
C1, C2, C3, C4: 22u; C_0603_1608Metric
C5: 100u; CP_Elec_5x5.4; LCSC Part C4054379
J1: JST PH; JST_PH_S6B-PH-SM4-TB_1x06-1MP_P2.00mm_Horizontal
J2: 3.5mm screw terminal; TerminalBlock_Phoenix_PT-1,5-2-3.5-H_1x02_P3.50mm_Horizontal
J3: STEMMA; STEMMA-I2C-SMD-horizontal
J4: JST PH; STEMMA-Signal-SMD-horizontal
J5: JST PH; JST_PH_S2B-PH-SM4-TB_1x02-1MP_P2.00mm_Horizontal
J6: USB_C_Receptacle_PowerOnly_6P; USB_C_Receptacle_GCT_USB4125-xx-x_6P_TopMnt_Horizontal_Hand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; LCSC Part C2927029
J7: Qwiic; Qwiic-SMD-horizontal-logo; LCSC Part C19270571
LED1, LED3: LED; LED_0603_1608Metric_Pad1.05x0.95mm_HandSolder_simple
Q1, Q2, Q3: BSS84; SOT-23
Q4: 2N7002DW; SOT-363_SC-70-6_HandSolder; LCSC Part C5190214
Q5: G2N7002X; SOT-523; LCSC Part C5258971
RN1, RN2: 10K; R_Array_Convex_4x0603_HandSolder
RN3: 5K1; R_Array_Convex_4x0603_HandSolder
SM1: ESP32-C3-Super-Mini-Pins
SM2: DFR0299; DFPlayer-Mini-DFR0299-module
SM4: HLK-LD2410C; HLK-LD2410C-module; LCSC Part C19723500
U1: WS2811F; FSOP-8_3.3x1.7mm_P0.80mm; LCSC Part C5446692
U2: G3MB-202P-5VDC; Relay_G3MB-202P

Connections:
+3V3: J3.3 (V+), J7.2 (+3V3), Q4.2 (G), Q4.5 (G), RN2.2 (R2.1), RN2.4 (R4.1), SM1.3V3 (+3.3V)
+5V: C1.1, C2.1, C3.1, C4.1, C5.1, J4.2, J6.A9 (VBUS), J6.B9 (VBUS), Q1.2 (S), Q2.2 (S), Q3.2 (S), RN1.1 (R1.1), RN1.2 (R2.1), RN1.3 (R3.1), RN2.1 (R1.1), RN2.3 (R3.1), SM1.5V (+5V), SM2.1 (VCC), SM4.5 (VCC), U1.8 (VDD), U2.3
/RELAY_LOW: Q5.3 (D), U2.4
BUTTON: J1.5, SM1.7 (GPIO7/SS)
BUTTON_LED_B: J1.4, Q3.3 (D)
BUTTON_LED_B_EN: Q3.1 (G), RN1.6 (R3.2), U1.3 (OUTB)
BUTTON_LED_G: J1.3, Q2.3 (D)
BUTTON_LED_G_EN: Q2.1 (G), RN1.7 (R2.2), U1.2 (OUTG)
BUTTON_LED_R: J1.2, Q1.3 (D)
BUTTON_LED_R_EN: Q1.1 (G), RN1.8 (R1.2), U1.1 (OUTR)
BUTTON_WS8211: Q4.3 (D), RN2.8 (R1.2), U1.6 (DIN)
BUTTON_WS8211_3V3: Q4.4 (S), RN2.7 (R2.2), SM1.4 (SCK/ADC/GPIO4)
DOORBELL_RELAY: Q5.1 (G), RN3.1 (R1.1), SM1.3 (ADC/GPIO3)
GND: C1.2, C2.2, C3.2, C4.2, C5.2, J1.1, J1.6, J1.MP (MountPin), J3.4 (GND), J3.MP, J4.3, J4.MP (MountPin), J5.MP (MountPin), J6.A12 (GND), J6.B12 (GND), J6.S1 (SHIELD), J7.1 (GND), J7.MP, LED1.1 (K), LED3.1 (K), Q5.2 (S), RN1.4 (R4.1), RN1.5 (R4.2), RN3.2 (R2.1), RN3.3 (R3.1), SM1.G (GND), SM2.7 (GND), SM2.10 (GND), SM4.4 (GND), U1.4 (GND)
NEOPIXELS: J4.1, Q4.6 (D), RN2.6 (R3.2)
NEOPIXELS_3V3: Q4.1 (S), RN2.5 (R4.2), SM1.10 (GPIO10)
unnamed: J6.A5 (CC1), RN3.7 (R2.2)
unnamed: J6.B5 (CC2), RN3.6 (R3.2)
unnamed: LED1.2 (A), RN3.5 (R4.2)
unnamed: LED3.2 (A), RN3.8 (R1.2)
RELAY_NO_1: J2.1, U2.1
RELAY_NO_2: J2.2, U2.2
SCL: J3.1 (SCL), J7.4 (SCL), SM1.9 (~GPIO9/SCL)
SDA: J3.2 (SDA), J7.3 (SDA), SM1.8 (~GPIO8/SDA)
SPK1: J5.2, SM2.6 (SPK1)
SPK2: J5.1, SM2.8 (SPK2)
STATUS_LED: RN3.4 (R4.1), SM1.2 (ADC/~GPIO2)
UART_1_RX: SM1.1 (ADC/GPIO1), SM4.1 (TXD)
UART_1_TX: SM1.0 (ADC/GPIO0), SM4.2 (RXD)
UART_2_RX: SM1.5 (GPIO5/MISO), SM2.3 (TX)
UART_2_TX: SM1.6 (GPIO6/MOSI), SM2.2 (RX)

Notes on the sheet:
Microcontroller
Doorbell Button
Presence Sensor
Power Capacitors
Solid State Relay
Speaker
Neopixel logic level shifters
Connectors and terminals
CERN-OHL-P v2

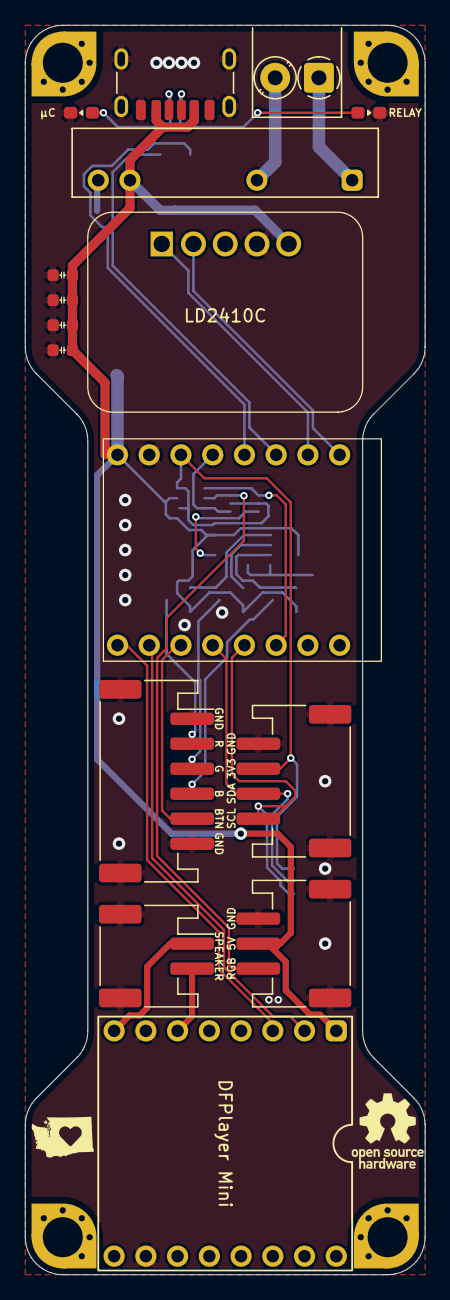
[picture p139: board esp-doorbell-dev.kicad_pcb from above]

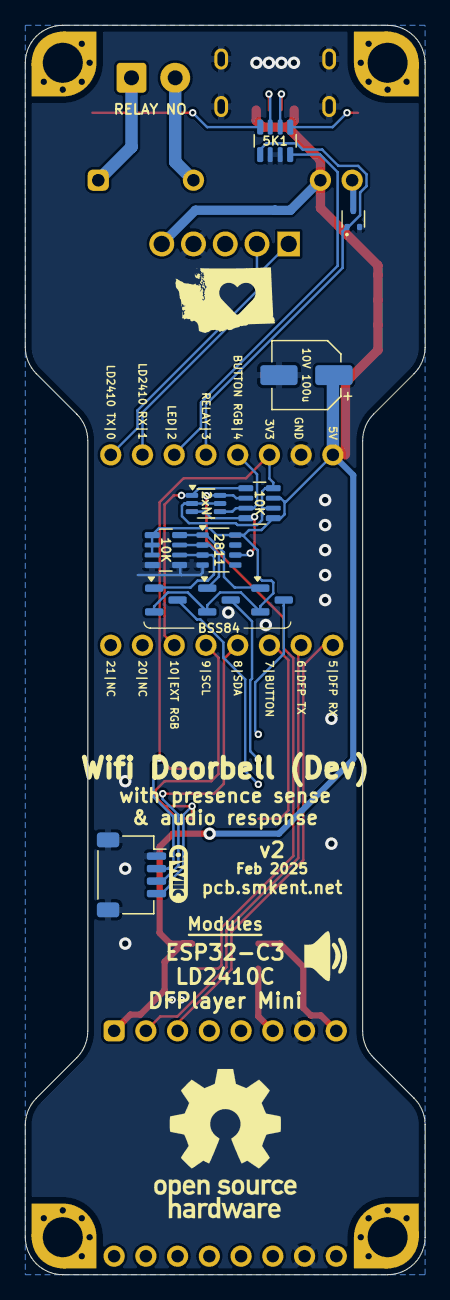
[picture p140: board esp-doorbell-dev.kicad_pcb from below]

Board: 2 copper layers, 32.0 x 100.0 mm, 27 parts (11 on the bottom side), 31 nets.
