smkent/pcb/pcb/jigs/neopixel-micro/neopixel-micro.kicad_pcb

## KiCad design pcb/jigs/neopixel-micro/neopixel-micro.kicad_pcb (2025-02-08)

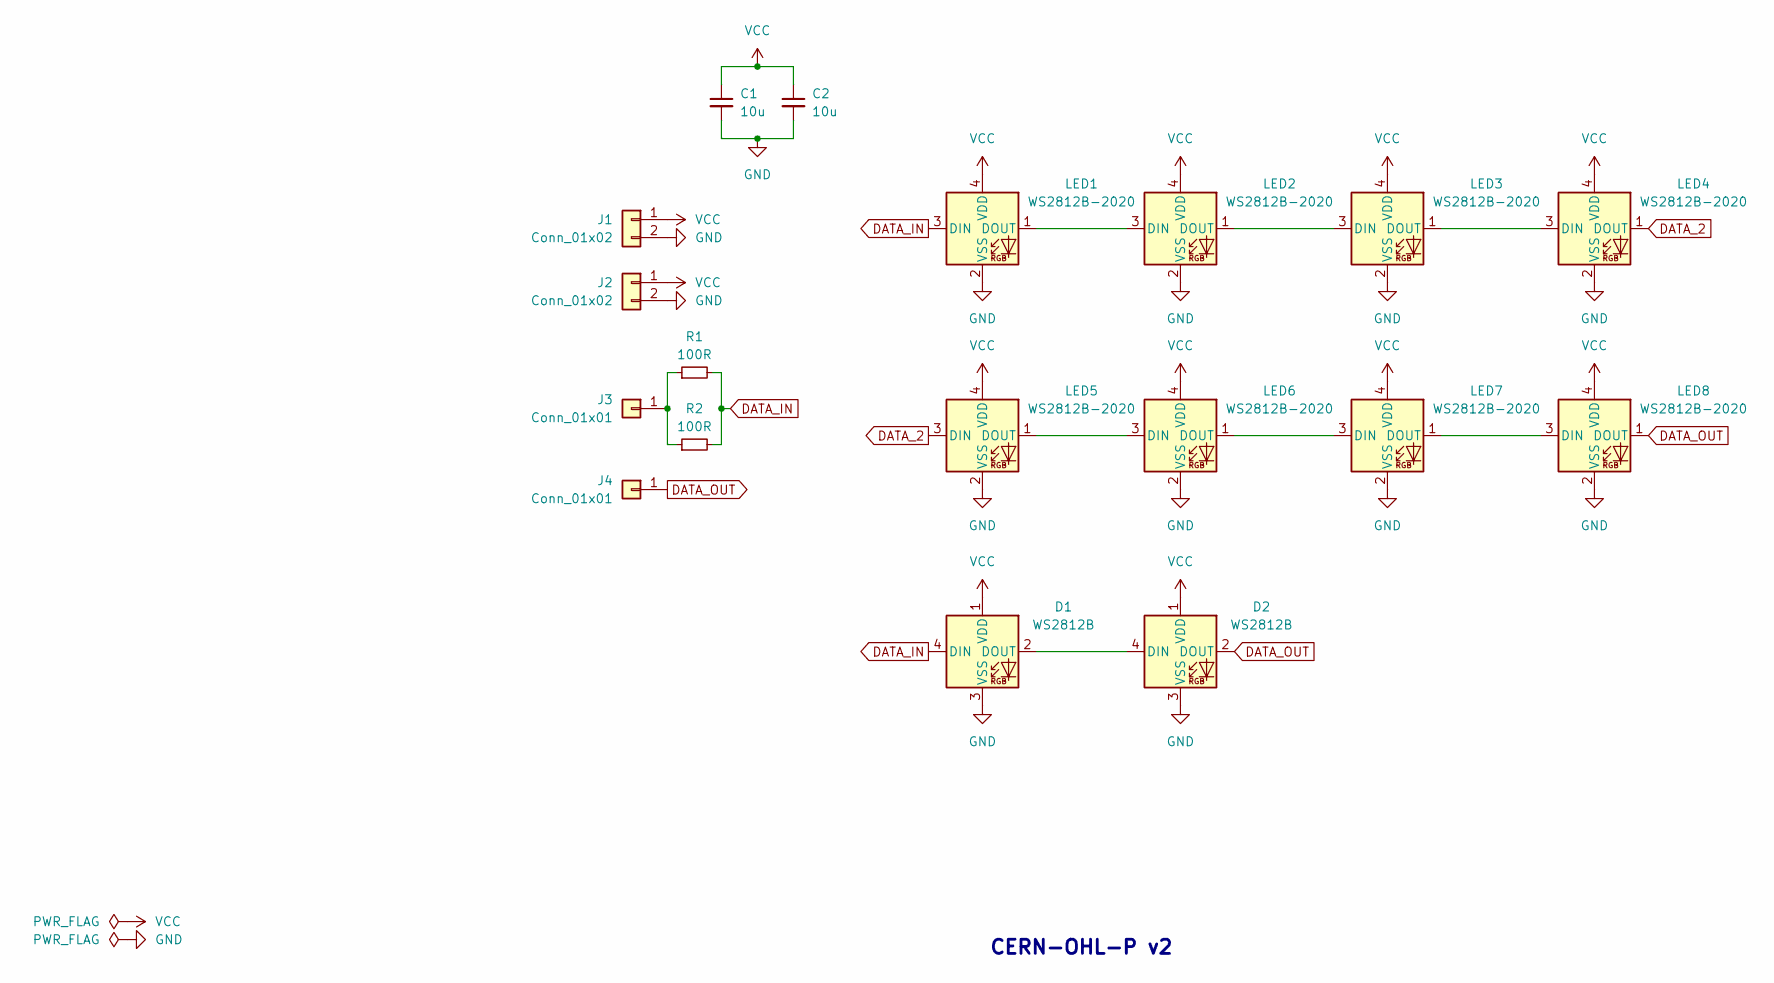
[picture p141: schematic neopixel-micro.kicad_sch, LED Jig]

Parts:
C1, C2: 10u; C_0603_1608Metric_Pad1.08x0.95mm_HandSolder
D1, D2: WS2812B; LED_WS2812B_PLCC4_5.0x5.0mm_P3.2mm
J1, J2: Conn_01x02; PinHeader_1x02_P2.54mm_Vertical_simple
J3, J4: Conn_01x01; PinHeader_1x01_P2.54mm_simple
LED1, LED2, LED3, LED4, LED5, LED6, LED7, LED8: WS2812B-2020; LED_WS2812B-2020_PLCC4_2.0x2.0mm_HandSolder
R1, R2: 100R; R_0603_1608Metric_Pad0.98x0.95mm_HandSolder

Connections:
DATA_2: LED4.1 (DOUT), LED5.3 (DIN)
DATA_IN: D1.4 (DIN), LED1.3 (DIN), R1.2, R2.2
DATA_OUT: D2.2 (DOUT), J4.1, LED8.1 (DOUT)
GND: C1.2, C2.2, D1.3 (VSS), D2.3 (VSS), J1.2, J2.2, LED1.2 (VSS), LED2.2 (VSS), LED3.2 (VSS), LED4.2 (VSS), LED5.2 (VSS), LED6.2 (VSS), LED7.2 (VSS), LED8.2 (VSS)
unnamed: D1.2 (DOUT), D2.4 (DIN)
unnamed: J3.1, R1.1, R2.1
unnamed: LED1.1 (DOUT), LED2.3 (DIN)
unnamed: LED2.1 (DOUT), LED3.3 (DIN)
unnamed: LED3.1 (DOUT), LED4.3 (DIN)
unnamed: LED5.1 (DOUT), LED6.3 (DIN)
unnamed: LED6.1 (DOUT), LED7.3 (DIN)
unnamed: LED7.1 (DOUT), LED8.3 (DIN)
VCC: C1.1, C2.1, D1.1 (VDD), D2.1 (VDD), J1.1, J2.1, LED1.4 (VDD), LED2.4 (VDD), LED3.4 (VDD), LED4.4 (VDD), LED5.4 (VDD), LED6.4 (VDD), LED7.4 (VDD), LED8.4 (VDD)

Notes on the sheet:
CERN-OHL-P v2

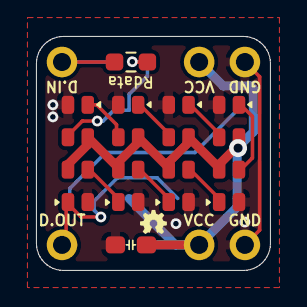
[picture p142: board neopixel-micro.kicad_pcb from above]

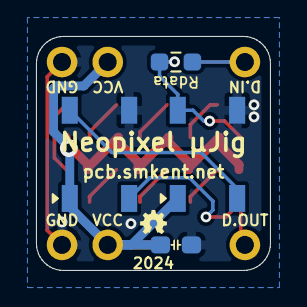
[picture p143: board neopixel-micro.kicad_pcb from below]

Board: 2 copper layers, 13.0 x 13.0 mm, 18 parts (8 on the bottom side), 13 nets.
