smkent/pcb/pcb/jigs/led-micro/led-micro.kicad_pcb

## KiCad design pcb/jigs/led-micro/led-micro.kicad_pcb (2025-02-08)

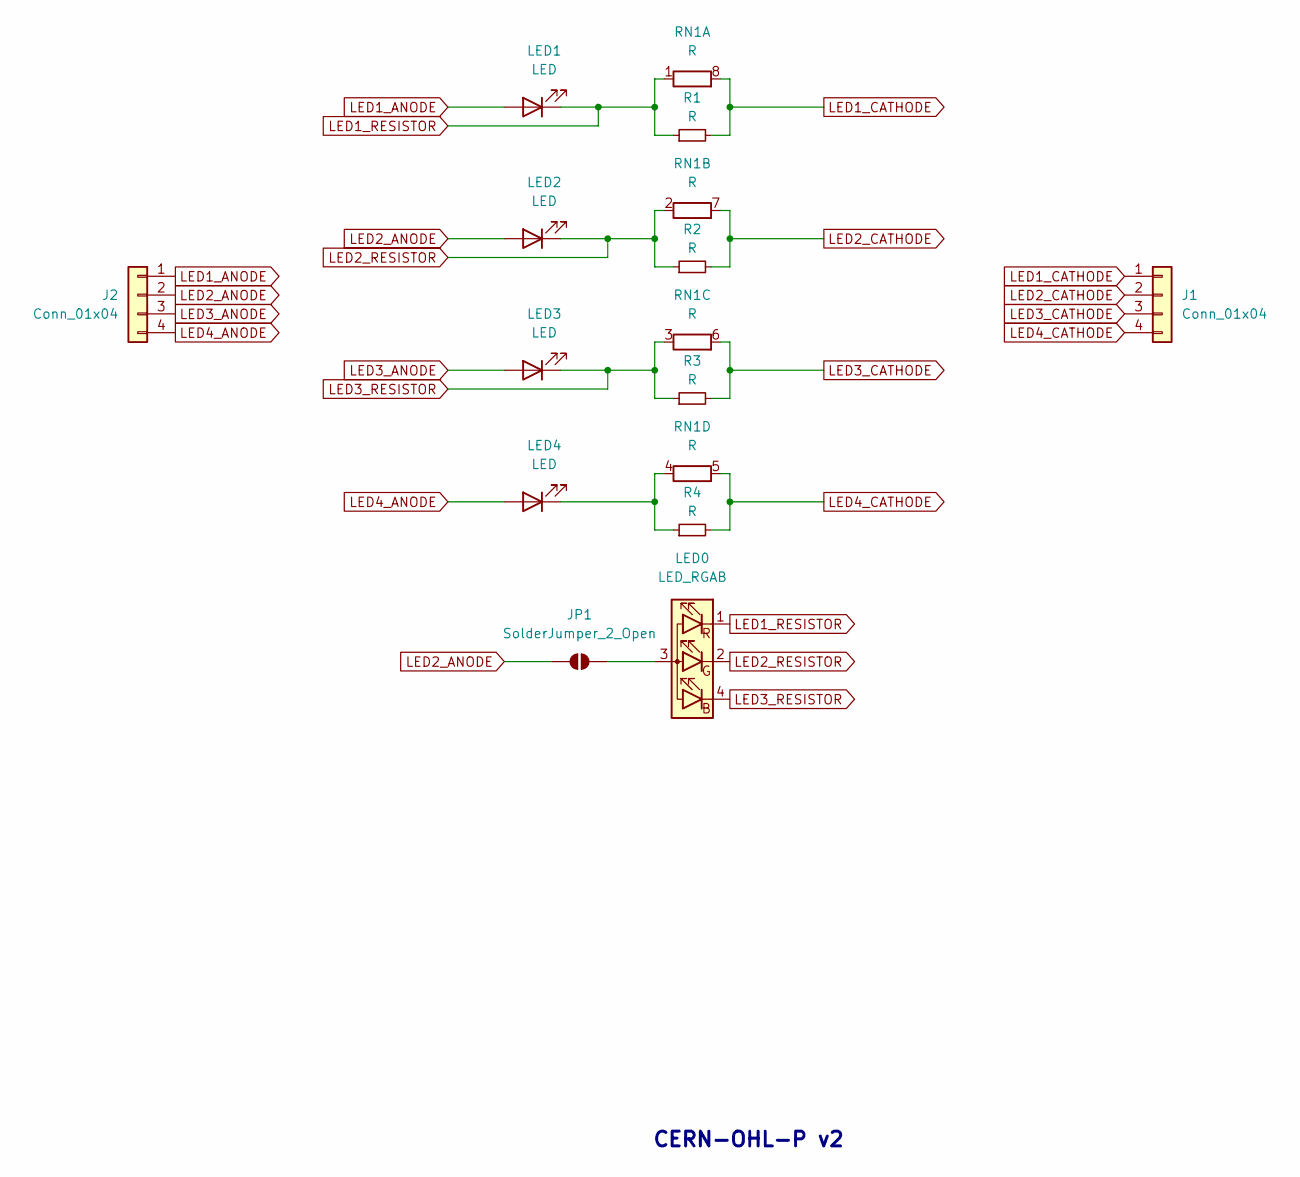
[picture p144: schematic led-micro.kicad_sch, LED Jig]

Parts:
J1, J2: Conn_01x04; PinHeader_1x04_P2.54mm_Vertical_simple
JP1: SolderJumper_2_Open; SolderJumper-2_P1.3mm_Open_TrianglePad1.0x1.5mm
LED0: LED_RGAB; LED_RGB_XL-2012RGBC_2.0x1.2mm_HandSolder; LCSC Part C965848
LED1, LED2, LED3, LED4: LED; LED_0805_2012Metric_Pad1.15x1.40mm_HandSolder_simple
R1, R2, R3, R4: R; R_0805_2012Metric_Pad1.20x1.40mm_HandSolder
RN1: R; R_Array_Convex_4x0603

Connections:
LED1_ANODE: J2.1, LED1.2 (A)
LED1_CATHODE: J1.1, R1.2, RN1.8 (R1.2)
LED1_RESISTOR: LED0.1 (RK), LED1.1 (K), R1.1, RN1.1 (R1.1)
LED2_ANODE: J2.2, JP1.1 (A), LED2.2 (A)
LED2_CATHODE: J1.2, R2.2, RN1.7 (R2.2)
LED2_RESISTOR: LED0.2 (GK), LED2.1 (K), R2.1, RN1.2 (R2.1)
LED3_ANODE: J2.3, LED3.2 (A)
LED3_CATHODE: J1.3, R3.2, RN1.6 (R3.2)
LED3_RESISTOR: LED0.4 (BK), LED3.1 (K), R3.1, RN1.3 (R3.1)
LED4_ANODE: J2.4, LED4.2 (A)
LED4_CATHODE: J1.4, R4.2, RN1.5 (R4.2)
unnamed: JP1.2 (B), LED0.3 (A)
unnamed: LED4.1 (K), R4.1, RN1.4 (R4.1)

Notes on the sheet:
CERN-OHL-P v2

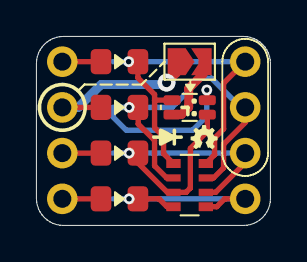
[picture p145: board led-micro.kicad_pcb from above]

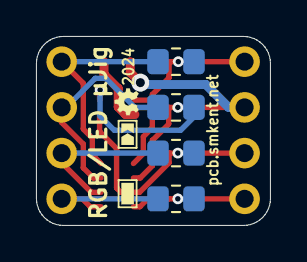
[picture p146: board led-micro.kicad_pcb from below]

Board: 2 copper layers, 13.0 x 10.5 mm, 13 parts (6 on the bottom side), 13 nets.
