smkent/pcb/pcb/jigs/reflow-mini/reflow-mini.kicad_pcb

## KiCad design pcb/jigs/reflow-mini/reflow-mini.kicad_pcb (2025-02-08)

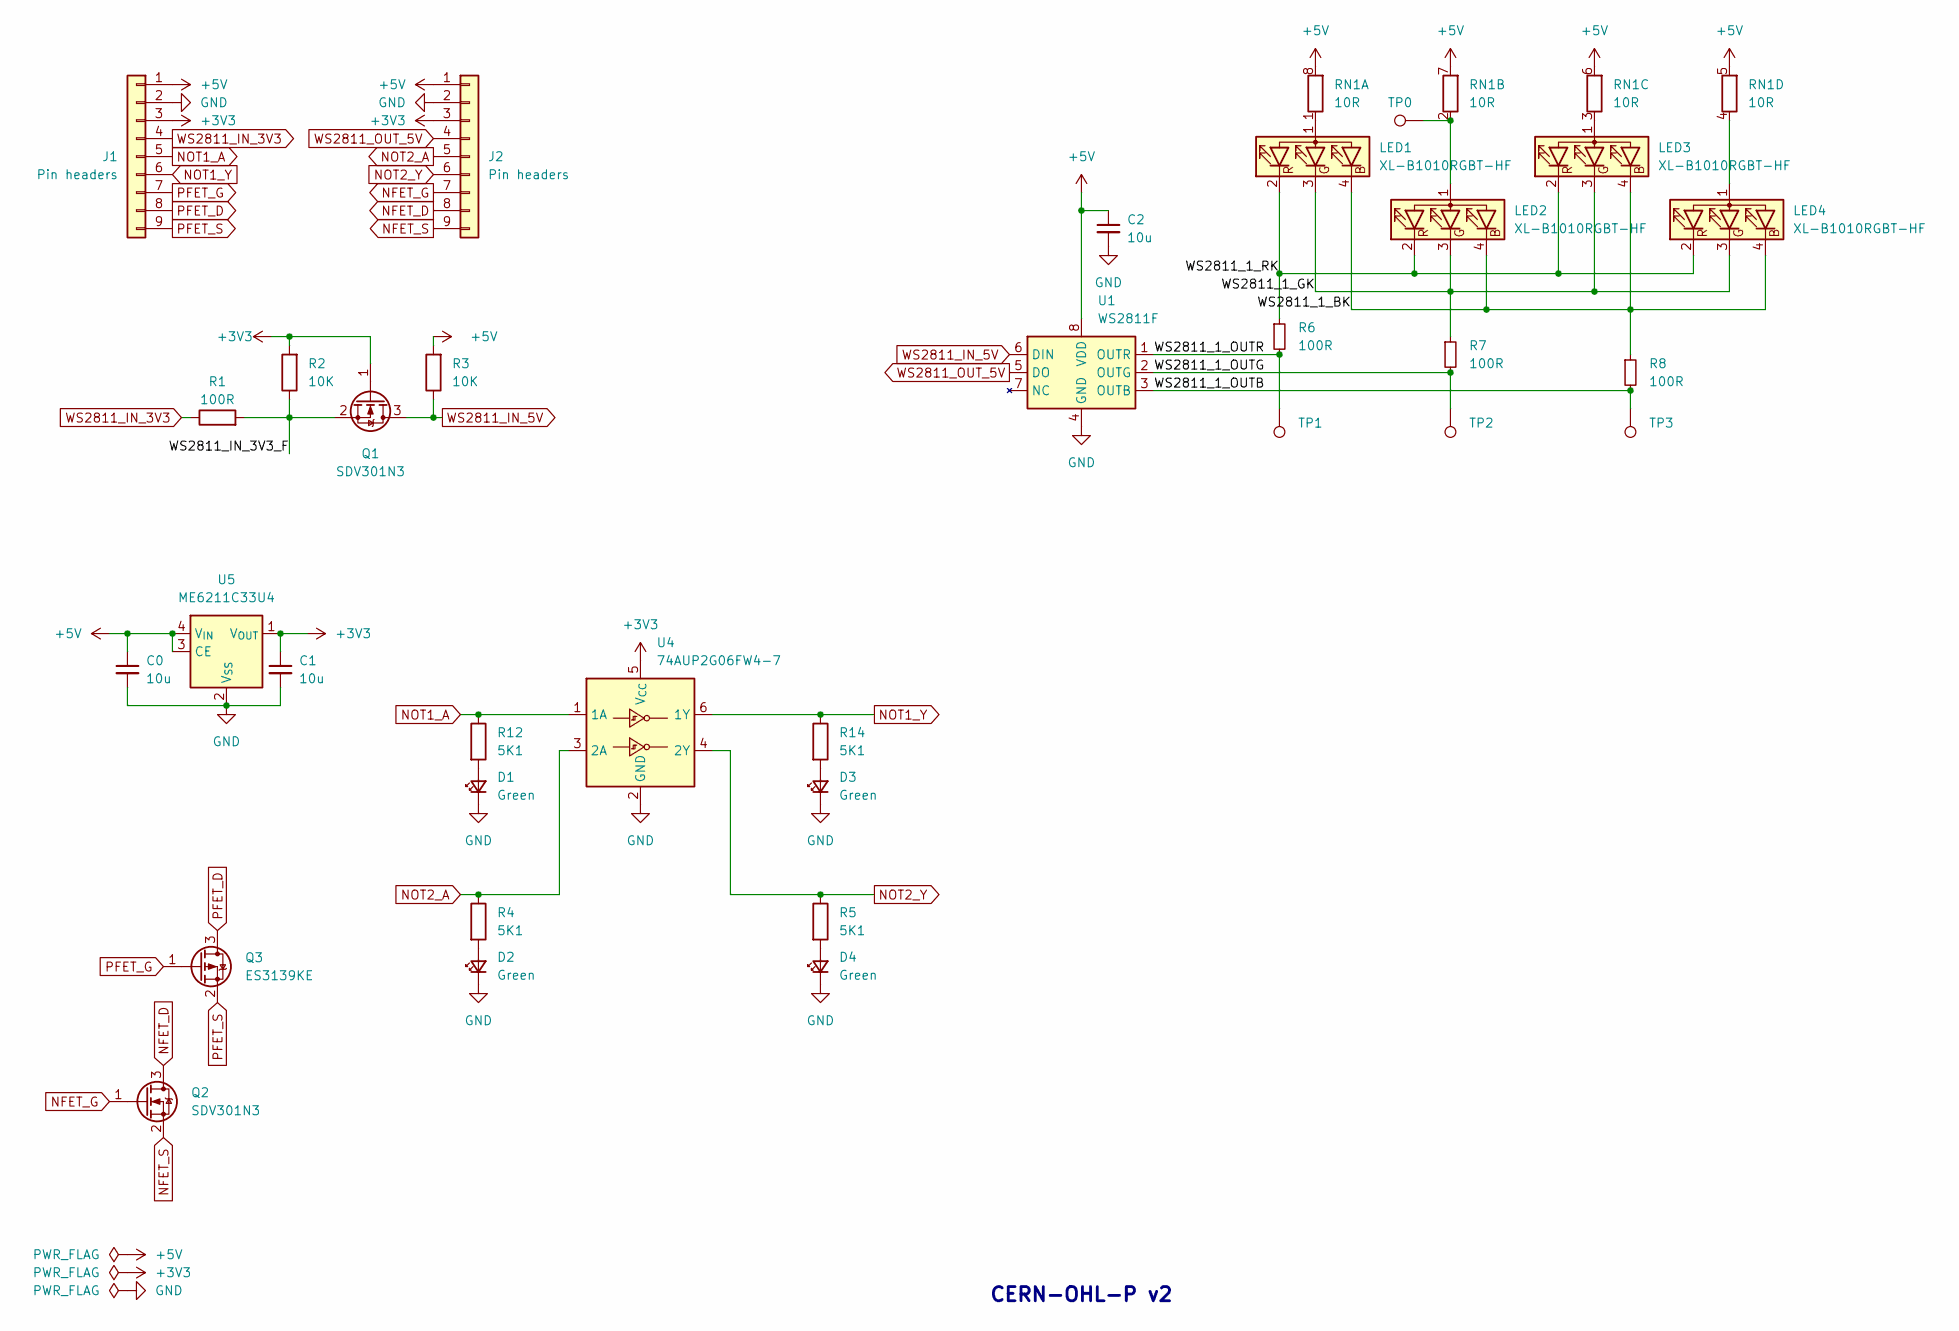
[picture p147: schematic reflow-mini.kicad_sch]

Parts:
C0, C1, C2: 10u; C_0402_1005Metric
D1, D2, D3, D4: Green; LED_0402_1005Metric
J1, J2: Pin headers; PinHeader_1x09_P2.54mm_Vertical_simple
LED1, LED2, LED3, LED4: XL-B1010RGBT-HF; LED_RGB_XL-B1010RGBT-HF_1.0x1.0mm; LCSC Part C22464515
Q1, Q2: SDV301N3; DFN1006-3; LCSC Part C5334596
Q3: ES3139KE; DFN1006-3; LCSC Part C7527987
R1: 100R; R_0402_1005Metric
R2, R3: 10K; R_0402_1005Metric
R4, R5, R12, R14: 5K1; R_0402_1005Metric
R6, R7, R8: 100R; R_0603_1608Metric
RN1: 10R; R_Array_Convex_4x0603
TP0, TP1, TP2, TP3: TestPoint; TestPoint_Pad_D1.0mm
U1: WS2811F; FSOP-8_3.3x1.7mm_P0.80mm; LCSC Part C5446692
U4: 74AUP2G06FW4-7; X2-DFN1010-6_L1.0-W1.0-P0.35-BL; LCSC Part C842402
U5: ME6211C33U4; UDFN-4-1EP_1x1mm_P0.65mm_EP0.48x0.48mm; LCSC Part C428904

Connections:
+3V3: C1.1, J1.3, J2.3, Q1.1 (G), R2.2, U4.5 (V_{CC}), U5.1 (V_{OUT})
+5V: C0.1, C2.1, J1.1, J2.1, R3.2, RN1.5 (R4.2), RN1.6 (R3.2), RN1.7 (R2.2), RN1.8 (R1.2), U1.8 (VDD), U5.3 (CE), U5.4 (V_{IN})
/WS2811_1_BK: LED1.4 (BK), LED2.4 (BK), LED3.4 (BK), LED4.4 (BK), R8.1
/WS2811_1_GK: LED1.3 (GK), LED2.3 (GK), LED3.3 (GK), LED4.3 (GK), R7.1
/WS2811_1_OUTB: R8.2, TP3.1, U1.3 (OUTB)
/WS2811_1_OUTG: R7.2, TP2.1, U1.2 (OUTG)
/WS2811_1_OUTR: R6.2, TP1.1, U1.1 (OUTR)
/WS2811_1_RK: LED1.2 (RK), LED2.2 (RK), LED3.2 (RK), LED4.2 (RK), R6.1
/WS2811_IN_3V3_F: Q1.2 (S), R1.2, R2.1
GND: C0.2, C1.2, C2.2, D1.1 (K), D2.1 (K), D3.1 (K), D4.1 (K), J1.2, J2.2, U1.4 (GND), U4.2 (GND), U5.2 (V_{SS})
NFET_D: J2.8, Q2.3 (D)
NFET_G: J2.7, Q2.1 (G)
NFET_S: J2.9, Q2.2 (S)
NOT1_A: J1.5, R12.1, U4.1 (1A)
NOT1_Y: J1.6, R14.1, U4.6 (1Y)
NOT2_A: J2.5, R4.1, U4.3 (2A)
NOT2_Y: J2.6, R5.1, U4.4 (2Y)
unnamed: D1.2 (A), R12.2
unnamed: D2.2 (A), R4.2
unnamed: D3.2 (A), R14.2
unnamed: D4.2 (A), R5.2
unnamed: LED1.1 (A), RN1.1 (R1.1)
unnamed: LED2.1 (A), RN1.2 (R2.1), TP0.1
unnamed: LED3.1 (A), RN1.3 (R3.1)
unnamed: LED4.1 (A), RN1.4 (R4.1)
PFET_D: J1.8, Q3.3 (D)
PFET_G: J1.7, Q3.1 (G)
PFET_S: J1.9, Q3.2 (S)
WS2811_IN_3V3: J1.4, R1.1
WS2811_IN_5V: Q1.3 (D), R3.1, U1.6 (DIN)
WS2811_OUT_5V: J2.4, U1.5 (DO)

Notes on the sheet:
CERN-OHL-P v2

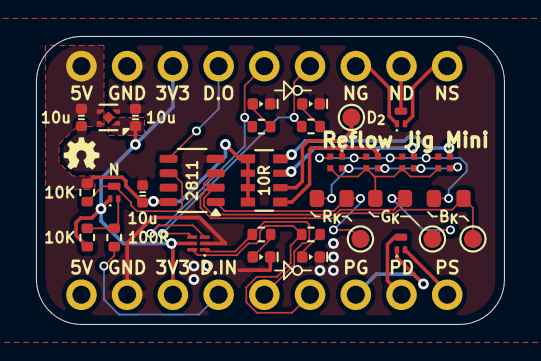
[picture p148: board reflow-mini.kicad_pcb from above]

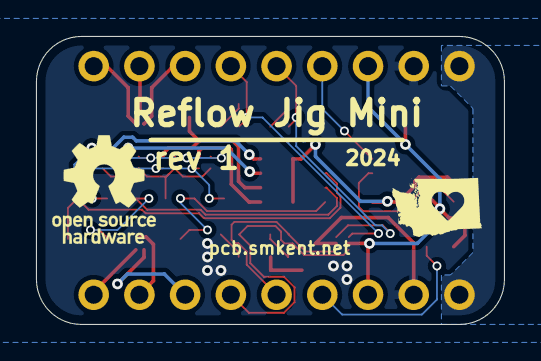
[picture p149: board reflow-mini.kicad_pcb from below]

Board: 2 copper layers, 26.0 x 16.0 mm, 34 parts (2 on the bottom side), 31 nets.
