smkent/pcb/pcb/power/microboost/microboost.kicad_pcb

## KiCad design pcb/power/microboost/microboost.kicad_pcb (2025-02-08)

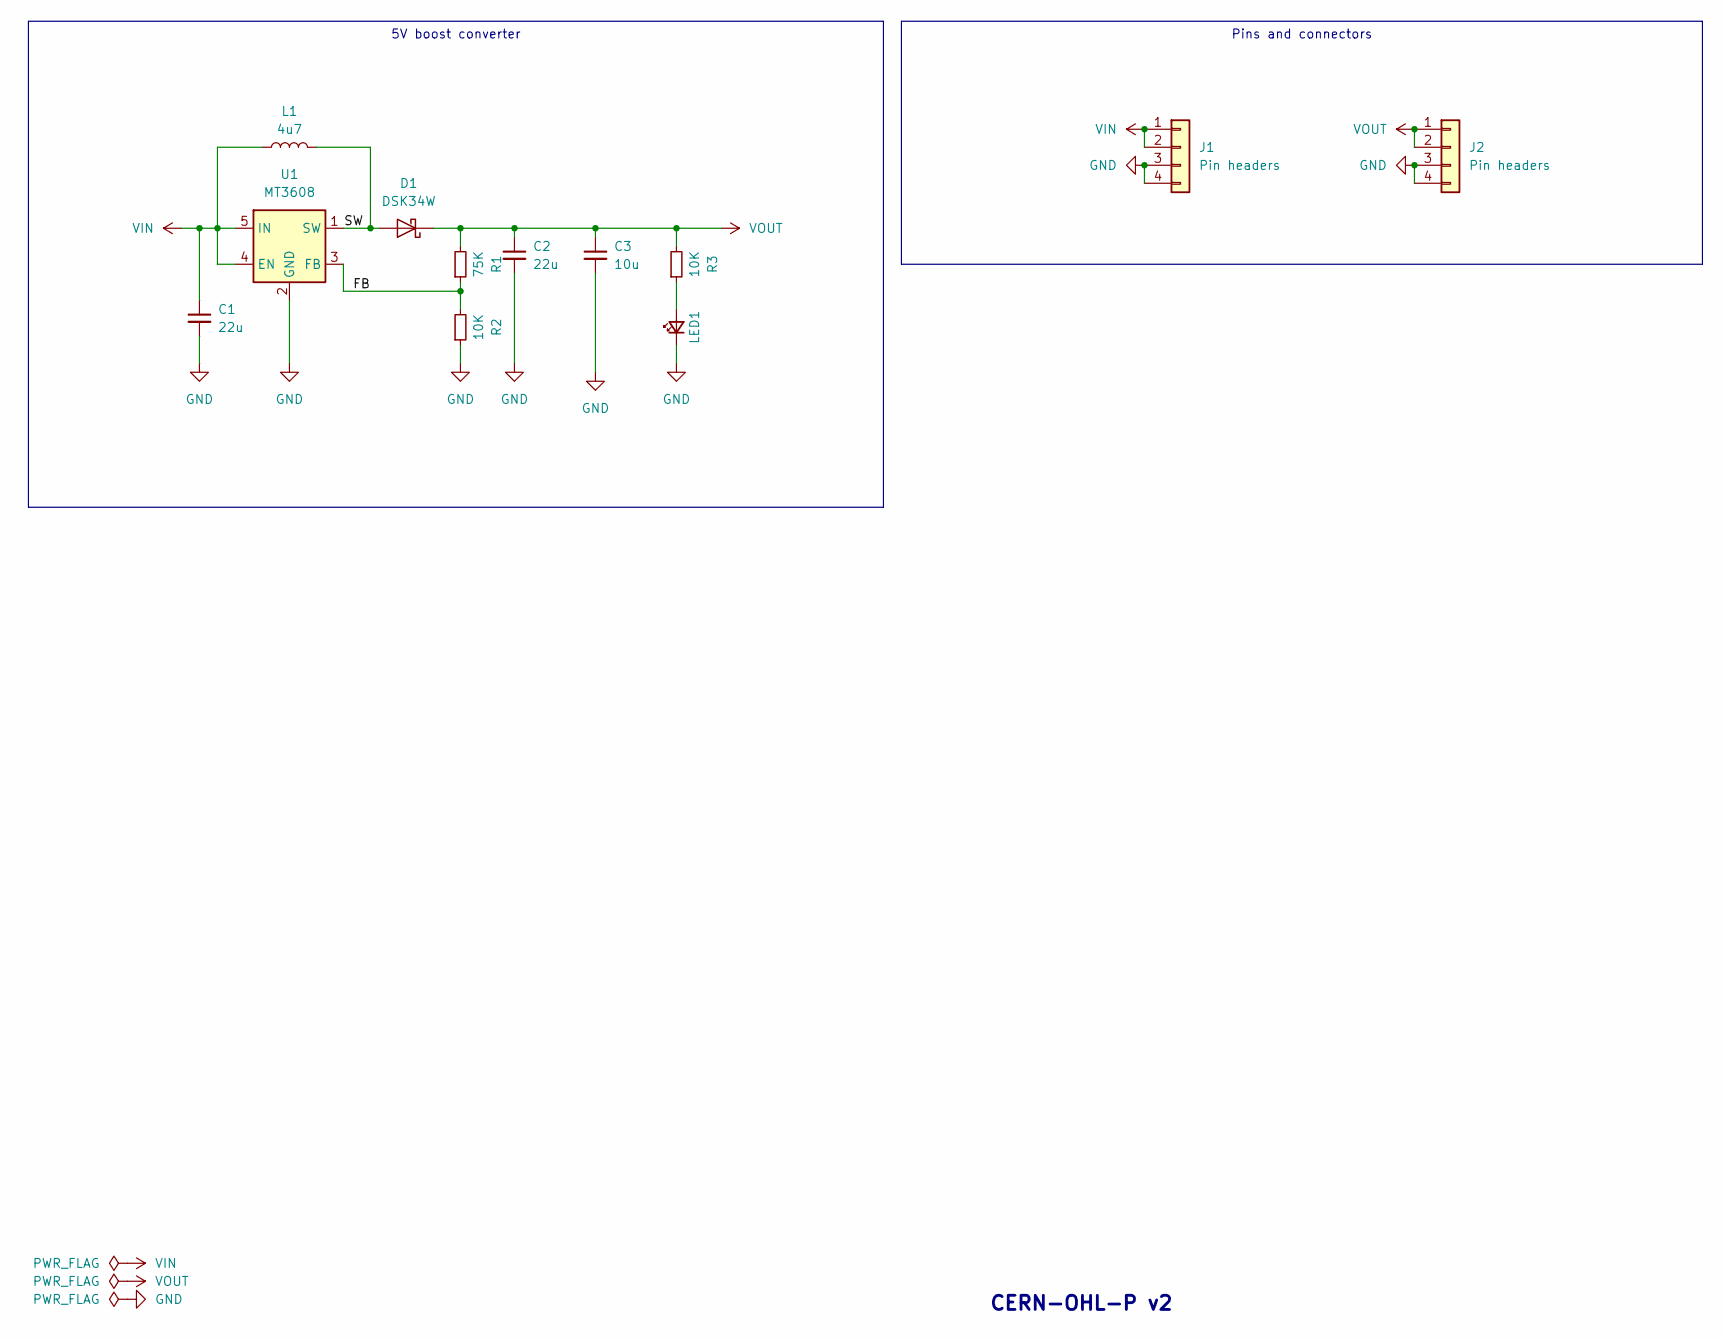
[picture p150: schematic microboost.kicad_sch]

Parts:
C1, C2: 22u; C_0805_2012Metric_Pad1.18x1.45mm_HandSolder
C3: 10u; C_0603_1608Metric_Pad1.08x0.95mm_HandSolder
D1: DSK34W; D_SOD-123F; LCSC Part C3014041
J1, J2: Pin headers; PinHeader_1x04_P2.54mm_Vertical_simple_pad3,4gnd
L1: 4u7; L_1008_2520Metric
LED1: LED_Small; LED_0603_1608Metric_Pad1.05x0.95mm_HandSolder_simple
R1: 75K; R_0603_1608Metric_Pad0.98x0.95mm_HandSolder
R2, R3: 10K; R_0603_1608Metric_Pad0.98x0.95mm_HandSolder
U1: MT3608; SOT-23-6; LCSC Part C84817

Connections:
/FB: R1.1, R2.2, U1.3 (FB)
/SW: D1.2 (A), L1.2, U1.1 (SW)
GND: C1.2, C2.2, C3.2, J1.3, J1.4, J2.3, J2.4, LED1.1 (K), R2.1, U1.2 (GND)
unnamed: LED1.2 (A), R3.1
VIN: C1.1, J1.1, J1.2, L1.1, U1.4 (EN), U1.5 (IN)
VOUT: C2.1, C3.1, D1.1 (K), J2.1, J2.2, R1.2, R3.2

Notes on the sheet:
Pins and connectors
5V boost converter
CERN-OHL-P v2
