smkent/pcb/pcb/power/microboost/microboost.kicad_pcb

## KiCad design pcb/power/microboost/microboost.kicad_pcb (continued)

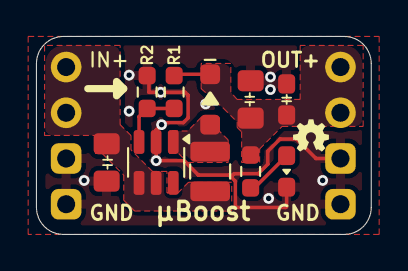
[picture p151: board microboost.kicad_pcb from above]

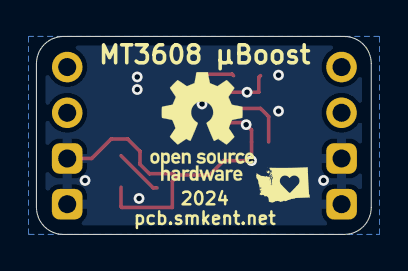
[picture p152: board microboost.kicad_pcb from below]

Board: 2 copper layers, 18.6 x 11.0 mm, 12 parts (2 on the bottom side), 6 nets.
