smkent/pcb/pcb/jigs/breadboard-power-microcontroller/breadboard-power-microcontroller.kicad_pcb

## KiCad design pcb/jigs/breadboard-power-microcontroller/breadboard-power-microcontroller.kicad_pcb (2025-02-08)

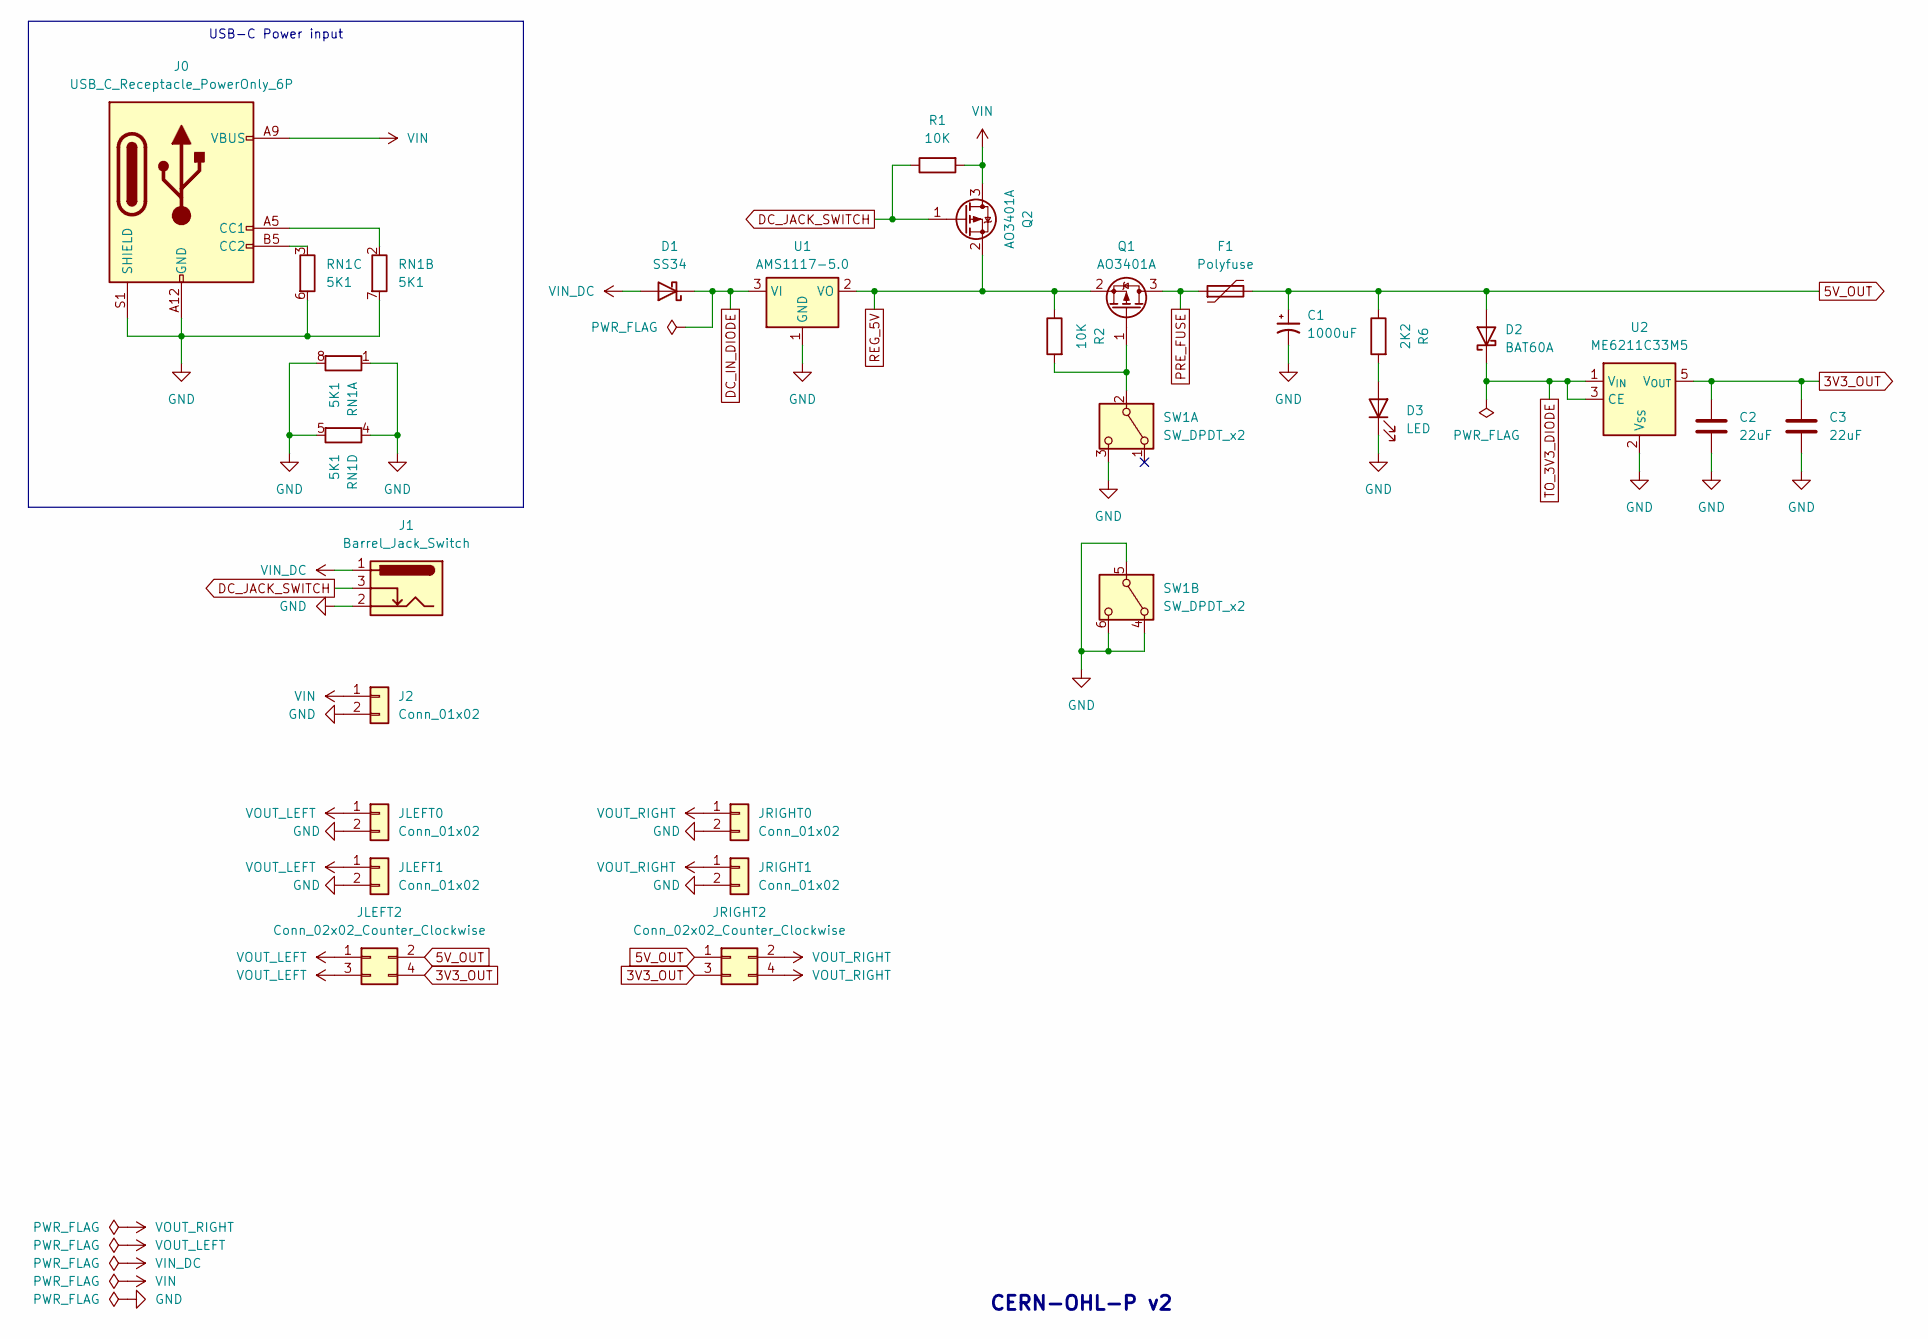
[picture p153: schematic breadboard-power-microcontroller.kicad_sch]

Parts:
C1: 1000uF; CP_Elec_8x10.5
C2, C3: 22uF; C_0805_2012Metric_Pad1.18x1.45mm_HandSolder
D1: SS34; D_SMA
D2: BAT60A; D_SOD-323_HandSoldering
D3: LED; LED_0805_2012Metric_Pad1.15x1.40mm_HandSolder_simple
F1: Polyfuse; Fuse_1206_3216Metric
J0: USB_C_Receptacle_PowerOnly_6P; USB_C_Receptacle_GCT_USB4125-xx-x_6P_TopMnt_Horizontal_Hand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
J1: Barrel_Jack_Switch; BarrelJack_DC-050_SMT_Horizontal
J2: Conn_01x02; JST_XH_S2B-XH-2AW_1x02_P2.50mm_TH-or-SMD_pad2gnd_trim
JLEFT0, JLEFT1: Conn_01x02; PinHeader_1x02_P2.54mm_Vertical_simple_pad2gnd
JLEFT2: Conn_02x02_Counter_Clockwise; PinHeader_2x02_P2.54mm_Vertical_simple
JRIGHT0, JRIGHT1: Conn_01x02; PinHeader_1x02_P2.54mm_Vertical_simple_pad2gnd
JRIGHT2: Conn_02x02_Counter_Clockwise; PinHeader_2x02_P2.54mm_Vertical_simple
Q1, Q2: AO3401A; SOT-23; LCSC Part C15127
R1, R2: 10K; R_0805_2012Metric_Pad1.20x1.40mm_HandSolder
R6: 2K2; R_0805_2012Metric_Pad1.20x1.40mm_HandSolder
RN1: 5K1; R_Array_Convex_4x0603
SW1: SW_DPDT_x2; SW_Push_DPDT_Toggle_7.0x7.0mm_THT
U1: AMS1117-5.0; SOT-223-3_TabPin2
U2: ME6211C33M5; SOT-23-5

Connections:
3V3_OUT: C2.1, C3.1, JLEFT2.4, JRIGHT2.3, U2.5 (V_{OUT})
5V_OUT: C1.1, D2.2 (A), F1.2, JLEFT2.2, JRIGHT2.1, R6.1
DC_IN_DIODE: D1.1 (K), U1.3 (VI)
DC_JACK_SWITCH: J1.3, Q2.1 (G), R1.1
GND: C1.2, C2.2, C3.2, D3.1 (K), J0.A12 (GND), J0.B12 (GND), J0.S1 (SHIELD), J1.2, J2.2, JLEFT0.2, JLEFT1.2, JRIGHT0.2, JRIGHT1.2, RN1.1 (R1.1), RN1.4 (R4.1), RN1.5 (R4.2), RN1.6 (R3.2), RN1.7 (R2.2), RN1.8 (R1.2), SW1.3 (C), SW1.4 (A), SW1.5 (B), SW1.6 (C), U1.1 (GND), U2.2 (V_{SS})
unnamed: D3.2 (A), R6.2
unnamed: J0.A5 (CC1), RN1.2 (R2.1)
unnamed: J0.B5 (CC2), RN1.3 (R3.1)
unnamed: Q1.1 (G), R2.2, SW1.2 (B)
PRE_FUSE: F1.1, Q1.3 (D)
REG_5V: Q1.2 (S), Q2.2 (S), R2.1, U1.2 (VO)
TO_3V3_DIODE: D2.1 (K), U2.1 (V_{IN}), U2.3 (CE)
VIN: J0.A9 (VBUS), J0.B9 (VBUS), J2.1, Q2.3 (D), R1.2
VIN_DC: D1.2 (A), J1.1
VOUT_LEFT: JLEFT0.1, JLEFT1.1, JLEFT2.1, JLEFT2.3
VOUT_RIGHT: JRIGHT0.1, JRIGHT1.1, JRIGHT2.2, JRIGHT2.4

Notes on the sheet:
USB-C Power input
CERN-OHL-P v2

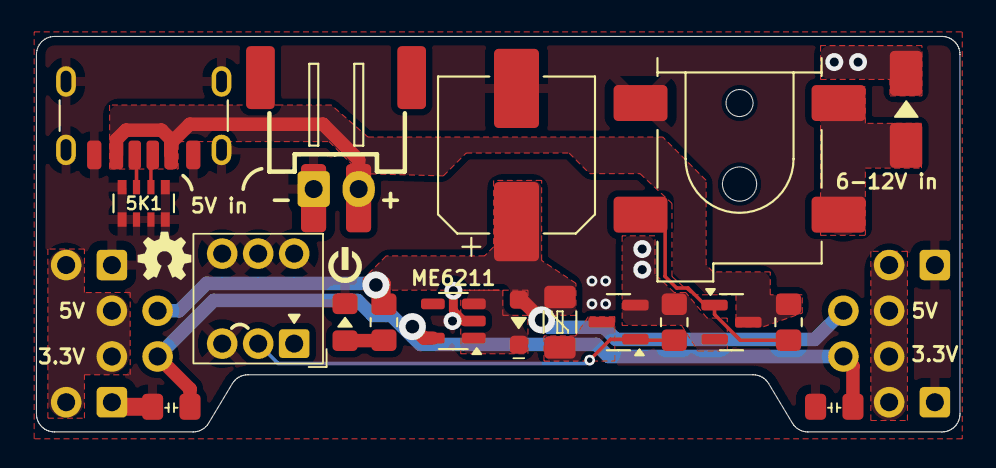
[picture p154: board breadboard-power-microcontroller.kicad_pcb from above]

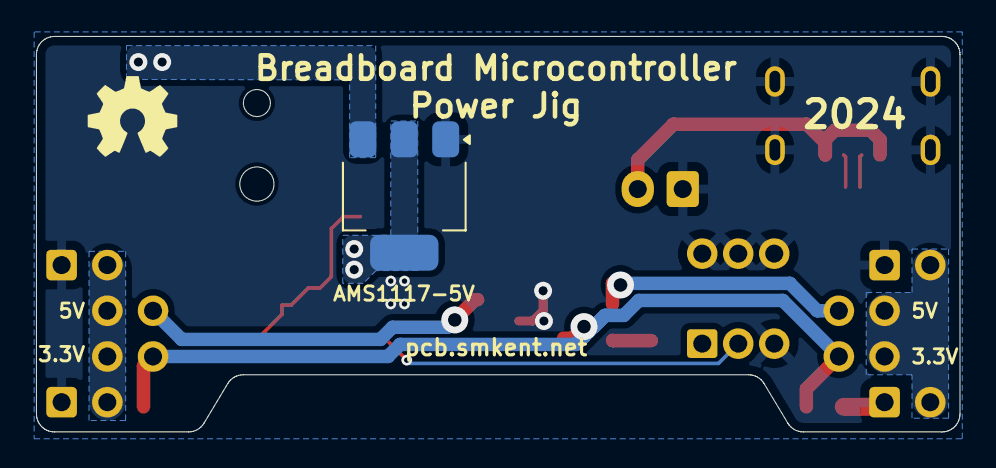
[picture p155: board breadboard-power-microcontroller.kicad_pcb from below]

Board: 2 copper layers, 51.3 x 22.0 mm, 25 parts (5 on the bottom side), 16 nets.
