smkent/pcb/pcb/jigs/breadboard-power/breadboard-power.kicad_pcb

## KiCad design pcb/jigs/breadboard-power/breadboard-power.kicad_pcb (2025-02-08)

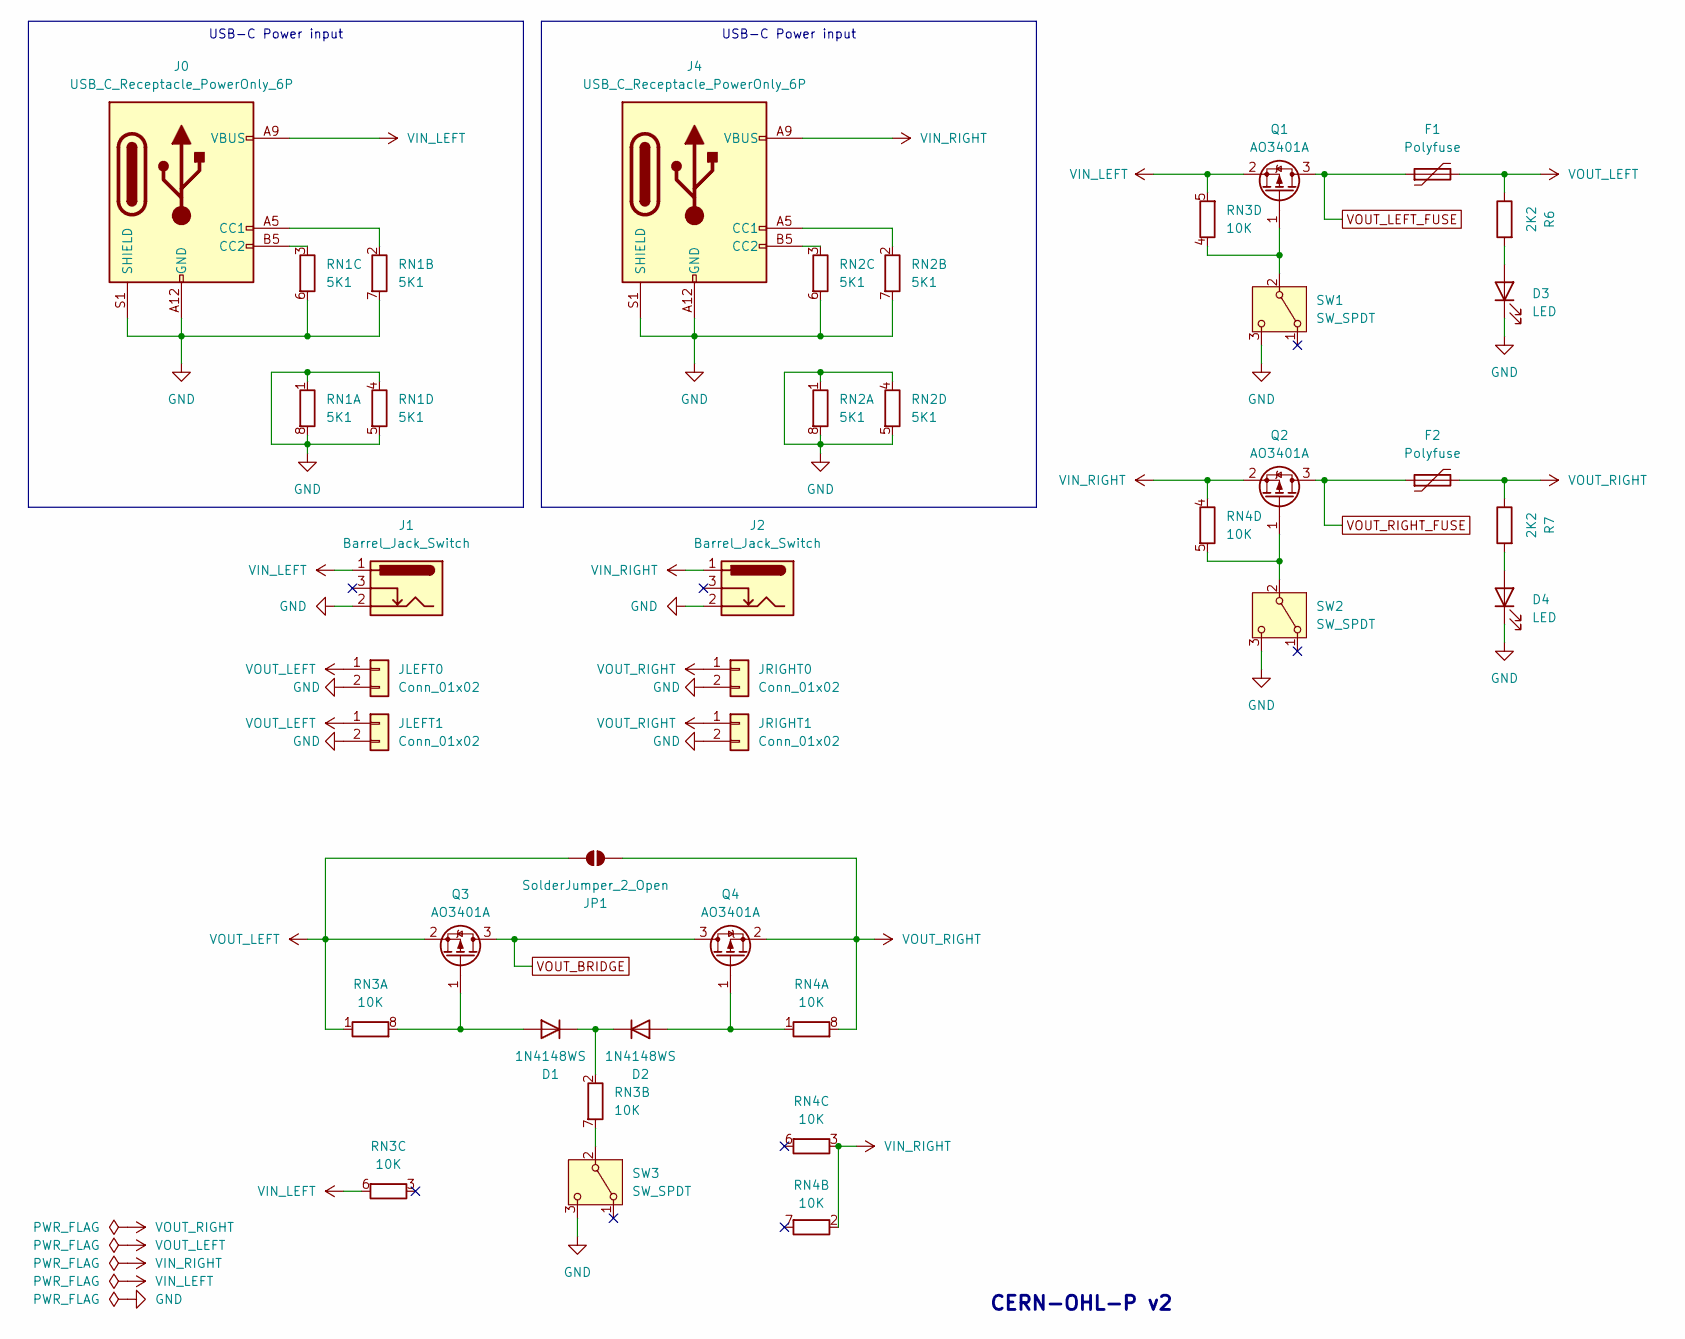
[picture p156: schematic breadboard-power.kicad_sch]

Parts:
D1, D2: 1N4148WS; D_SOD-323_HandSoldering
D3, D4: LED; LED_0805_2012Metric_Pad1.15x1.40mm_HandSolder_simple
F1, F2: Polyfuse; Fuse_1206_3216Metric
J0, J4: USB_C_Receptacle_PowerOnly_6P; USB_C_Receptacle_GCT_USB4125-xx-x_6P_TopMnt_Horizontal_Hand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
J1, J2: Barrel_Jack_Switch; Conn_Combo_DC-050_TerminalBlock_JST-XH-2P-horizontal-TH-or-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
JLEFT0, JLEFT1: Conn_01x02; PinHeader_1x02_P2.54mm_Vertical_simple_pad2gnd
JP1: SolderJumper_2_Open; SolderJumper-2_P1.3mm_Open_RoundedPad1.0x1.5mm_simple
JRIGHT0, JRIGHT1: Conn_01x02; PinHeader_1x02_P2.54mm_Vertical_simple_pad2gnd
Q1, Q2, Q3, Q4: AO3401A; SOT-23; LCSC Part C15127
R6, R7: 2K2; R_0805_2012Metric_Pad1.20x1.40mm_HandSolder
RN1, RN2: 5K1; R_Array_Convex_4x0603
RN3, RN4: 10K; R_Array_Convex_4x0603
SW1, SW2: SW_SPDT; SW_Slide-03_SPDT_P2.50mm_THT; LCSC Part C2998803
SW3: SW_SPDT; SW_SPDT_PCM12; LCSC Part C2998803

Connections:
GND: D3.1 (K), D4.1 (K), J0.A12 (GND), J0.B12 (GND), J0.S1 (SHIELD), J1.2, J2.2, J4.A12 (GND), J4.B12 (GND), J4.S1 (SHIELD), JLEFT0.2, JLEFT1.2, JRIGHT0.2, JRIGHT1.2, RN1.1 (R1.1), RN1.4 (R4.1), RN1.5 (R4.2), RN1.6 (R3.2), RN1.7 (R2.2), RN1.8 (R1.2), RN2.1 (R1.1), RN2.4 (R4.1), RN2.5 (R4.2), RN2.6 (R3.2), RN2.7 (R2.2), RN2.8 (R1.2), SW1.3 (C), SW2.3 (C), SW3.3 (C)
unnamed: D1.2 (A), Q3.1 (G), RN3.8 (R1.2)
unnamed: D1.1 (K), D2.1 (K), RN3.2 (R2.1)
unnamed: D2.2 (A), Q4.1 (G), RN4.1 (R1.1)
unnamed: D3.2 (A), R6.2
unnamed: D4.2 (A), R7.2
unnamed: J0.A5 (CC1), RN1.2 (R2.1)
unnamed: J0.B5 (CC2), RN1.3 (R3.1)
unnamed: J4.A5 (CC1), RN2.2 (R2.1)
unnamed: J4.B5 (CC2), RN2.3 (R3.1)
unnamed: Q1.1 (G), RN3.4 (R4.1), SW1.2 (B)
unnamed: Q2.1 (G), RN4.5 (R4.2), SW2.2 (B)
unnamed: RN3.7 (R2.2), SW3.2 (B)
VIN_LEFT: J0.A9 (VBUS), J0.B9 (VBUS), J1.1, Q1.2 (S), RN3.5 (R4.2), RN3.6 (R3.2)
VIN_RIGHT: J2.1, J4.A9 (VBUS), J4.B9 (VBUS), Q2.2 (S), RN4.2 (R2.1), RN4.3 (R3.1), RN4.4 (R4.1)
VOUT_BRIDGE: Q3.3 (D), Q4.3 (D)
VOUT_LEFT: F1.2, JLEFT0.1, JLEFT1.1, JP1.1 (A), Q3.2 (S), R6.1, RN3.1 (R1.1)
VOUT_LEFT_FUSE: F1.1, Q1.3 (D)
VOUT_RIGHT: F2.2, JP1.2 (B), JRIGHT0.1, JRIGHT1.1, Q4.2 (S), R7.1, RN4.8 (R1.2)
VOUT_RIGHT_FUSE: F2.1, Q2.3 (D)

Notes on the sheet:
USB-C Power input
CERN-OHL-P v2

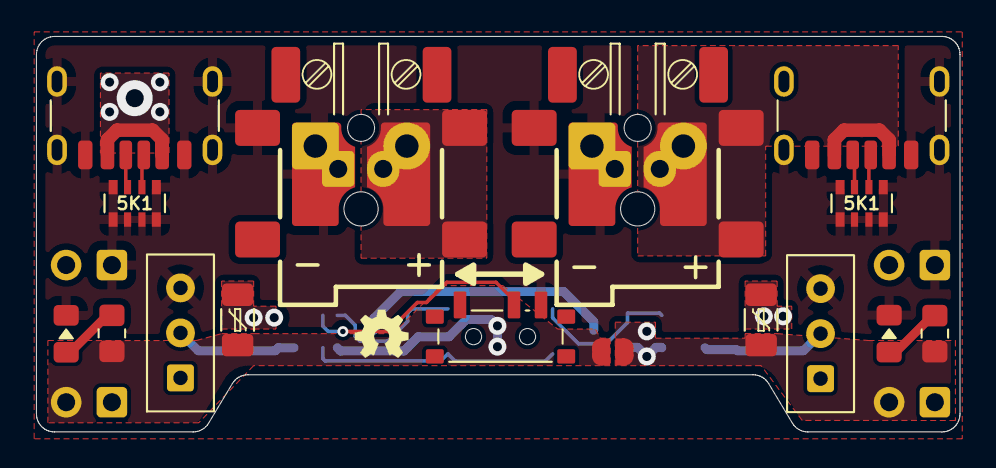
[picture p157: board breadboard-power.kicad_pcb from above]

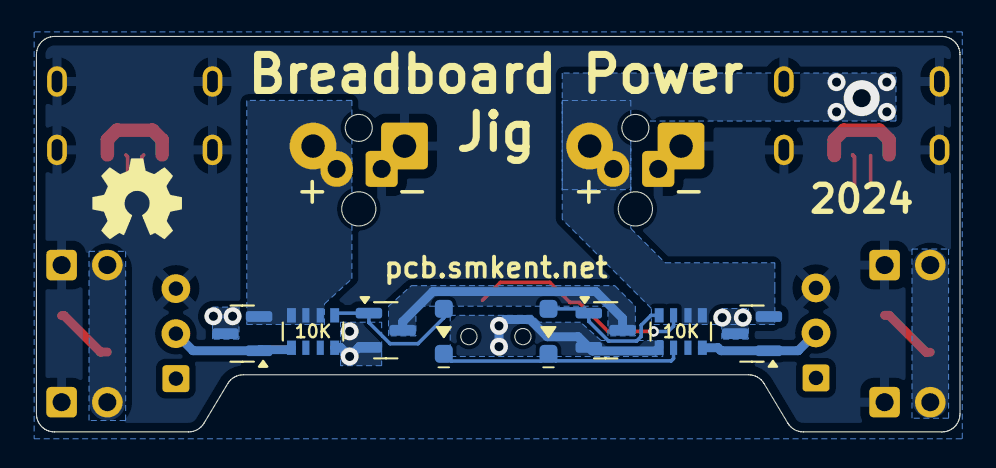
[picture p158: board breadboard-power.kicad_pcb from below]

Board: 2 copper layers, 51.3 x 22.0 mm, 28 parts (12 on the bottom side), 20 nets.
