smkent/pcb/pcb/misc/usb-pd-decoy-husb237/usb-pd-decoy-husb237.kicad_pcb

## KiCad design pcb/misc/usb-pd-decoy-husb237/usb-pd-decoy-husb237.kicad_pcb (2025-02-08)

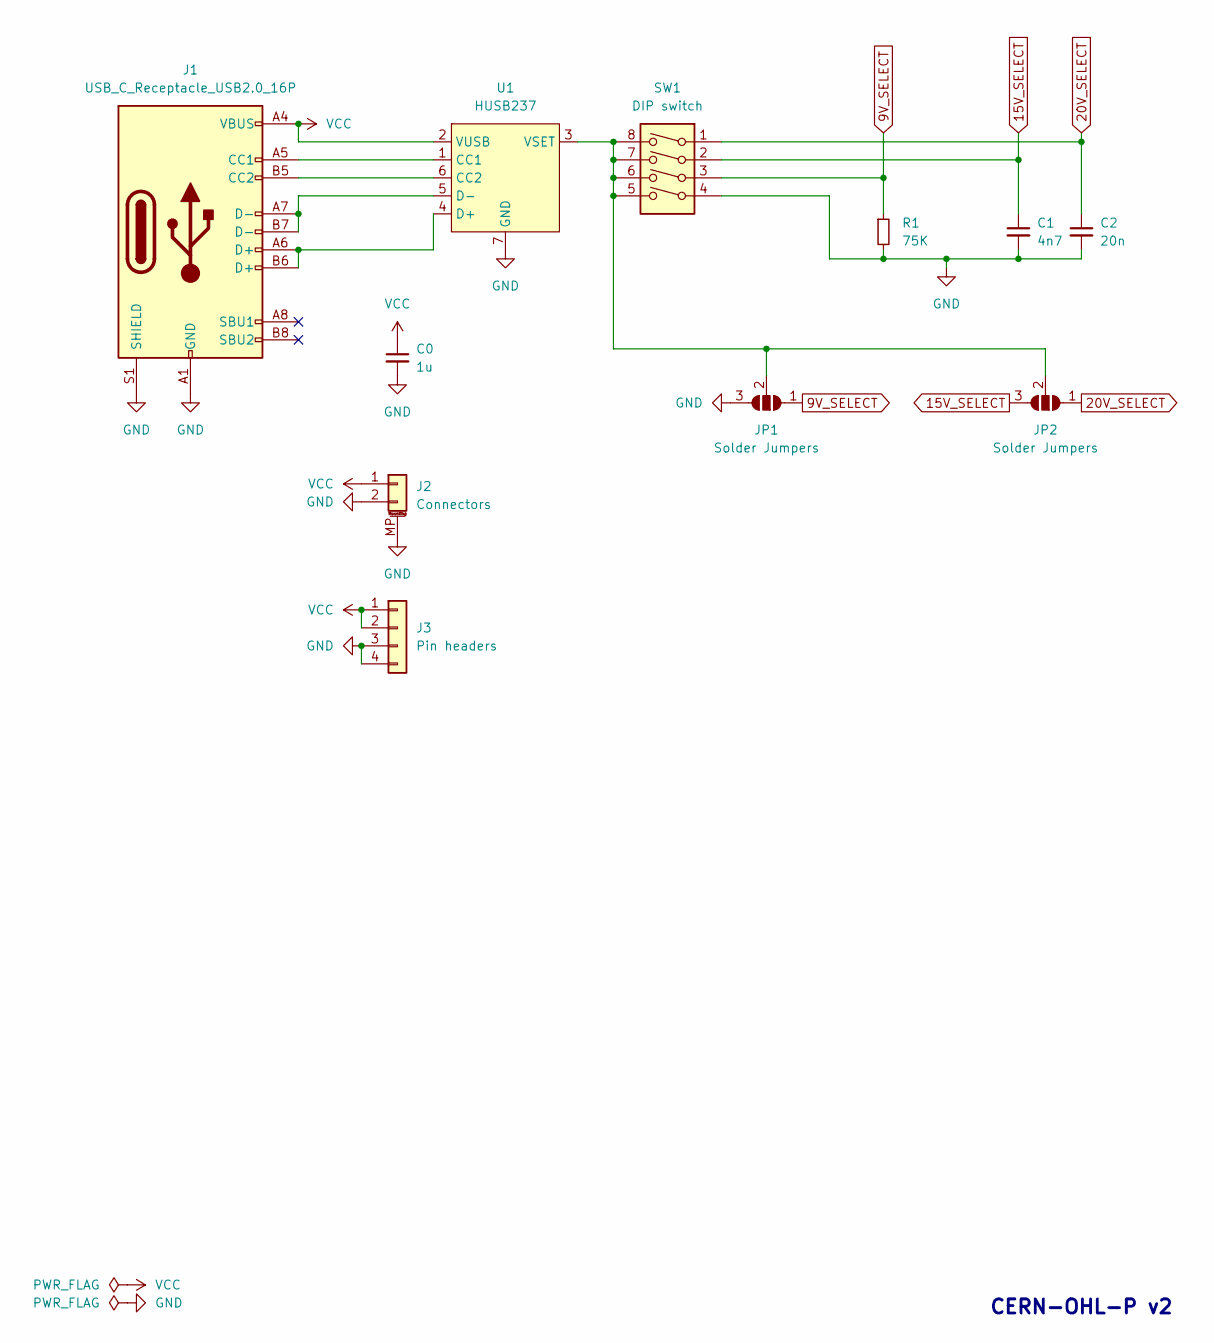
[picture p159: schematic usb-pd-decoy-husb237.kicad_sch]

Parts:
C0: 1u; C_0603_1608Metric_Pad1.08x0.95mm_HandSolder
C1: 4n7; C_0603_1608Metric_Pad1.08x0.95mm_HandSolder
C2: 20n; C_0603_1608Metric_Pad1.08x0.95mm_HandSolder
J1: USB_C_Receptacle_USB2.0_16P; USB_C_Receptacle_GCT_USB4105-xx-A_16P_TopMnt_Horizontal
J2: Connectors; Conn_Combo_TerminalBlock_JST-1x02-XH_PH-pad2gnd
J3: Pin headers; PinHeader_1x04_P2.54mm_Vertical_simple_pad3,4gnd
JP1, JP2: Solder Jumpers; SolderJumper-3_P1.0mm_Open_RoundedPad_simple
R1: 75K; R_0603_1608Metric_Pad0.98x0.95mm_HandSolder
SW1: DIP switch; SW_DIP_SPSTx04_Slide_P1.27mm
U1: HUSB237; DFN-6-1EP_2x2mm_P0.65mm_EP1x1.6mm; LCSC Part C7471904

Connections:
9V_SELECT: JP1.1 (A), R1.1, SW1.3
15V_SELECT: C1.1, JP2.3 (B), SW1.2
20V_SELECT: C2.1, JP2.1 (A), SW1.1
GND: C0.2, C1.2, C2.2, J1.A1 (GND), J1.A12 (GND), J1.B1 (GND), J1.B12 (GND), J1.S1 (SHIELD), J2.2, J2.MP (MountPin), J3.3, J3.4, JP1.3 (B), R1.2, SW1.4, U1.7 (GND)
unnamed: J1.A5 (CC1), U1.1 (CC1)
unnamed: J1.B5 (CC2), U1.6 (CC2)
unnamed: JP1.2 (C), JP2.2 (C), SW1.5, SW1.6, SW1.7, SW1.8, U1.3 (VSET)
unnamed: J1.A6 (D+), J1.B6 (D+), U1.4 (D+)
unnamed: J1.A7 (D-), J1.B7 (D-), U1.5 (D-)
VCC: C0.1, J1.A4 (VBUS), J1.A9 (VBUS), J1.B4 (VBUS), J1.B9 (VBUS), J2.1, J3.1, J3.2, U1.2 (VUSB)

Notes on the sheet:
CERN-OHL-P v2

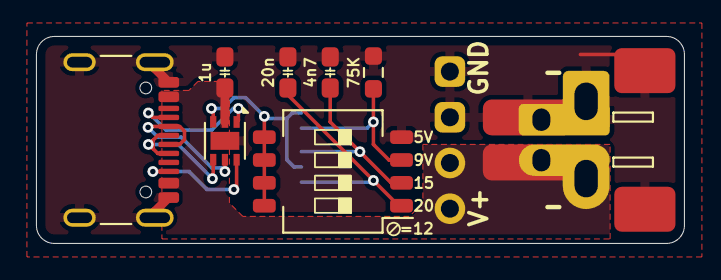
[picture p160: board usb-pd-decoy-husb237.kicad_pcb from above]

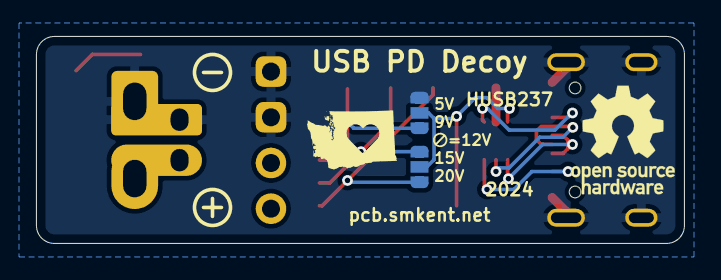
[picture p161: board usb-pd-decoy-husb237.kicad_pcb from below]

Board: 2 copper layers, 36.0 x 11.5 mm, 11 parts (3 on the bottom side), 10 nets.
