smkent/pcb/pcb/power/eta6003/eta6003.kicad_pcb

## KiCad design pcb/power/eta6003/eta6003.kicad_pcb (2025-02-08)

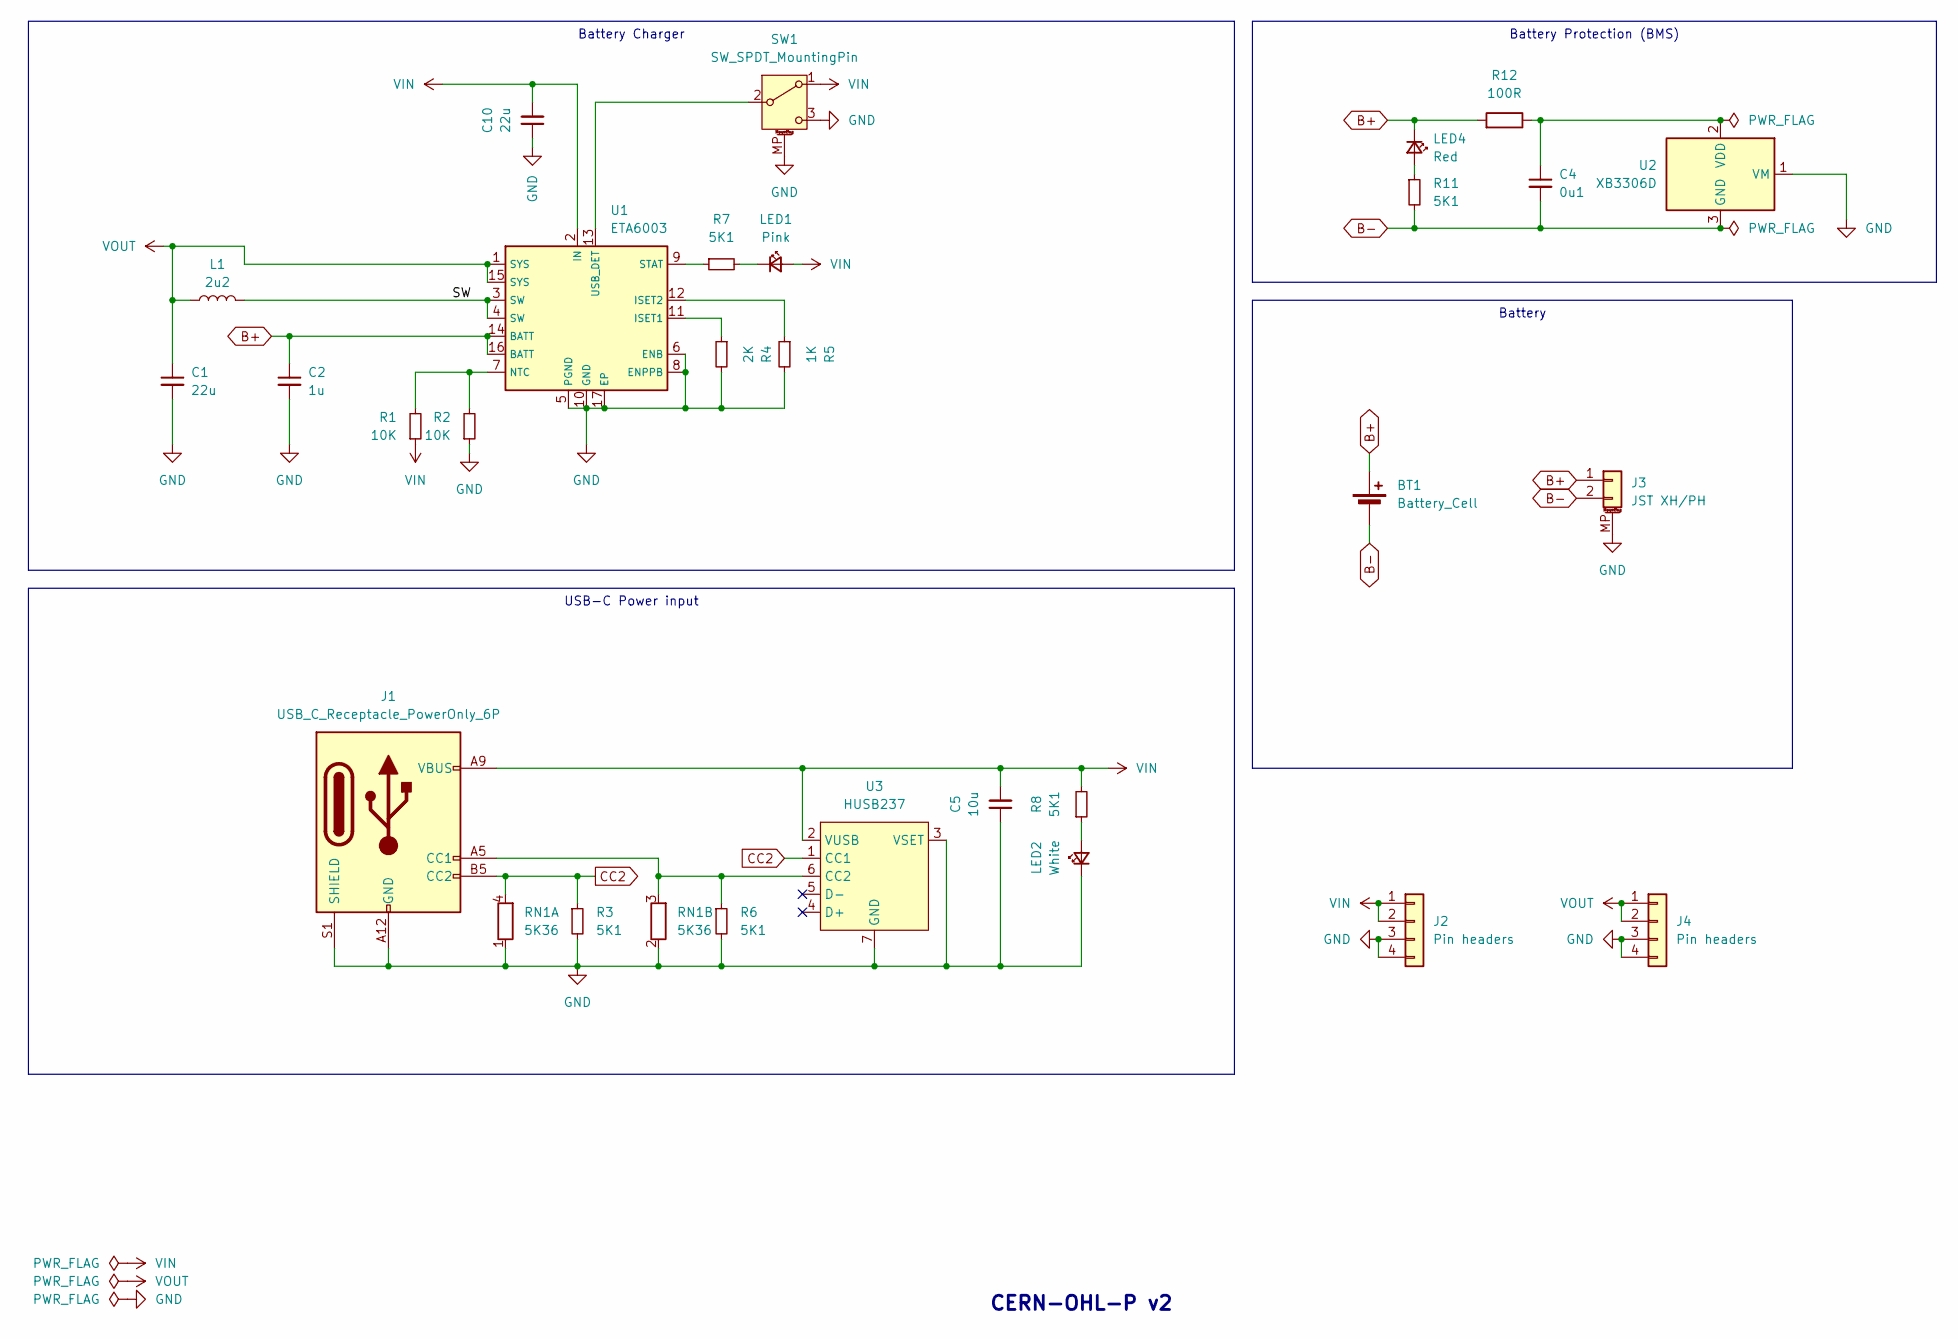
[picture p162: schematic eta6003.kicad_sch]

Parts:
BT1: Battery_Cell; BatteryHolder_1x18650_THT
C1: 22u; C_0603_1608Metric_Pad1.08x0.95mm_HandSolder; LCSC Part C45783
C2: 1u; C_0603_1608Metric_Pad1.08x0.95mm_HandSolder; LCSC Part C52923
C4: 0u1; C_0603_1608Metric_Pad1.08x0.95mm_HandSolder; LCSC Part C1525
C5: 10u; C_0603_1608Metric_Pad1.08x0.95mm_HandSolder; LCSC Part C15850
C10: 22u; C_0805_2012Metric_Pad1.18x1.45mm_HandSolder_wide-center; LCSC Part C15850
J1: USB_C_Receptacle_PowerOnly_6P; USB_C_Receptacle_GCT_USB4125-xx-x_6P_TopMnt_Horizontal_Hand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; LCSC Part C2927029
J2, J4: Pin headers; PinHeader_1x04_P2.54mm_Vertical_simple_pad3,4gnd
J3: JST XH/PH; Conn_Combo_JST-1x02-XH_PH-SMD-alt-pad2gnd
L1: 2u2; L_1008_2520Metric; LCSC Part C5832372
LED1: Pink; LED_0603_1608Metric_Pad1.05x0.95mm_HandSolder_simple
LED2: White; LED_0603_1608Metric_Pad1.05x0.95mm_HandSolder_simple
LED4: Red; LED_0603_1608Metric_Pad1.05x0.95mm_HandSolder_simple; LCSC Part C2286
R1, R2: 10K; R_0603_1608Metric_Pad0.98x0.95mm_HandSolder; LCSC Part C25744
R3, R6, R11: 5K1; R_0603_1608Metric_Pad0.98x0.95mm_HandSolder; LCSC Part C25905
R4: 2K; R_0603_1608Metric_Pad0.98x0.95mm_HandSolder; LCSC Part C22975
R5: 1K; R_0603_1608Metric_Pad0.98x0.95mm_HandSolder; LCSC Part C21190
R7, R8: 5K1; R_0603_1608Metric_Pad0.98x0.95mm_HandSolder; LCSC Part C21190
R12: 100R; R_0603_1608Metric_Pad0.98x0.95mm_HandSolder; LCSC Part C25076
RN1: 5K36; R_Array_Convex_2x0402
SW1: SW_SPDT_MountingPin; SW_SPDT_PCM12
U1: ETA6003; QFN-16-1EP_3x3mm_P0.5mm_EP1.7x1.7mm_ThermalVias_ETA6003; LCSC Part C5455585
U2: XB3306D; SOT-23; LCSC Part C2759992
U3: HUSB237; DFN-6-1EP_2x2mm_P0.65mm_EP1x1.6mm; LCSC Part C7471904

Connections:
/SW: L1.2, U1.3 (SW), U1.4 (SW)
B+: BT1.1 (+), C2.1, J3.1, LED4.1 (K), R12.2, U1.14 (BATT), U1.16 (BATT)
B-: BT1.2 (-), C4.2, J3.2, R11.2, U2.3 (GND)
CC2: J1.B5 (CC2), R3.1, RN1.4 (R1.2), U3.1 (CC1)
GND: C1.2, C2.2, C5.1, C10.1, J1.A12 (GND), J1.B12 (GND), J1.S1 (SHIELD), J2.3, J2.4, J3.MP (MountPin), J4.3, J4.4, LED2.1 (K), R2.1, R3.2, R4.2, R5.2, R6.2, RN1.1 (R1.1), RN1.2 (R2.1), SW1.3 (C), SW1.MP (MountPin), U1.5 (PGND), U1.6 (ENB), U1.8 (ENPPB), U1.10 (GND), U1.17 (EP), U2.1 (VM), U3.3 (VSET), U3.7 (GND)
unnamed: J1.A5 (CC1), R6.1, RN1.3 (R2.2), U3.6 (CC2)
unnamed: LED1.1 (K), R7.2
unnamed: LED2.2 (A), R8.1
unnamed: LED4.2 (A), R11.1
unnamed: SW1.2 (B), U1.13 (USB_DET)
unnamed: R4.1, U1.11 (ISET1)
unnamed: R5.1, U1.12 (ISET2)
unnamed: R1.2, R2.2, U1.7 (NTC)
unnamed: R7.1, U1.9 (STAT)
unnamed: C4.1, R12.1, U2.2 (VDD)
VIN: C5.2, C10.2, J1.A9 (VBUS), J1.B9 (VBUS), J2.1, J2.2, LED1.2 (A), R1.1, R8.2, SW1.1 (A), U1.2 (IN), U3.2 (VUSB)
VOUT: C1.1, J4.1, J4.2, L1.1, U1.1 (SYS), U1.15 (SYS)

Notes on the sheet:
USB-C Power input
Battery Protection (BMS)
Battery Charger
Battery
CERN-OHL-P v2

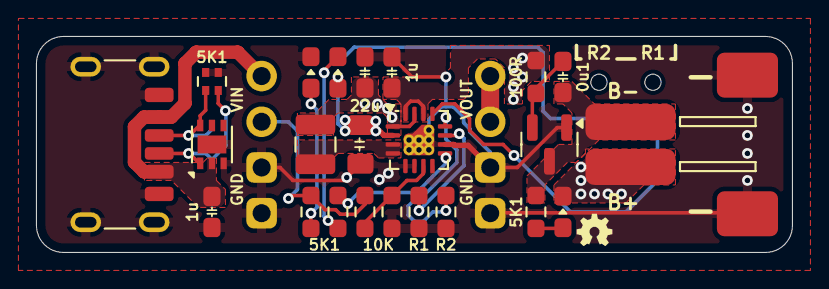
[picture p163: board eta6003.kicad_pcb from above]

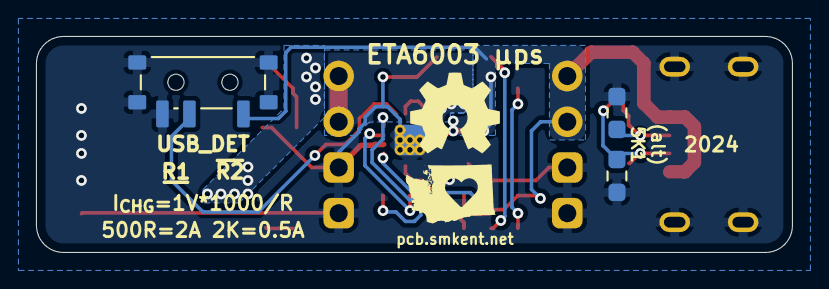
[picture p164: board eta6003.kicad_pcb from below]

Board: 2 copper layers, 42.0 x 12.0 mm, 28 parts (5 on the bottom side), 17 nets.
