smkent/pcb/pcb/power/microbuck/microbuck.kicad_pcb

## KiCad design pcb/power/microbuck/microbuck.kicad_pcb (2025-02-08)

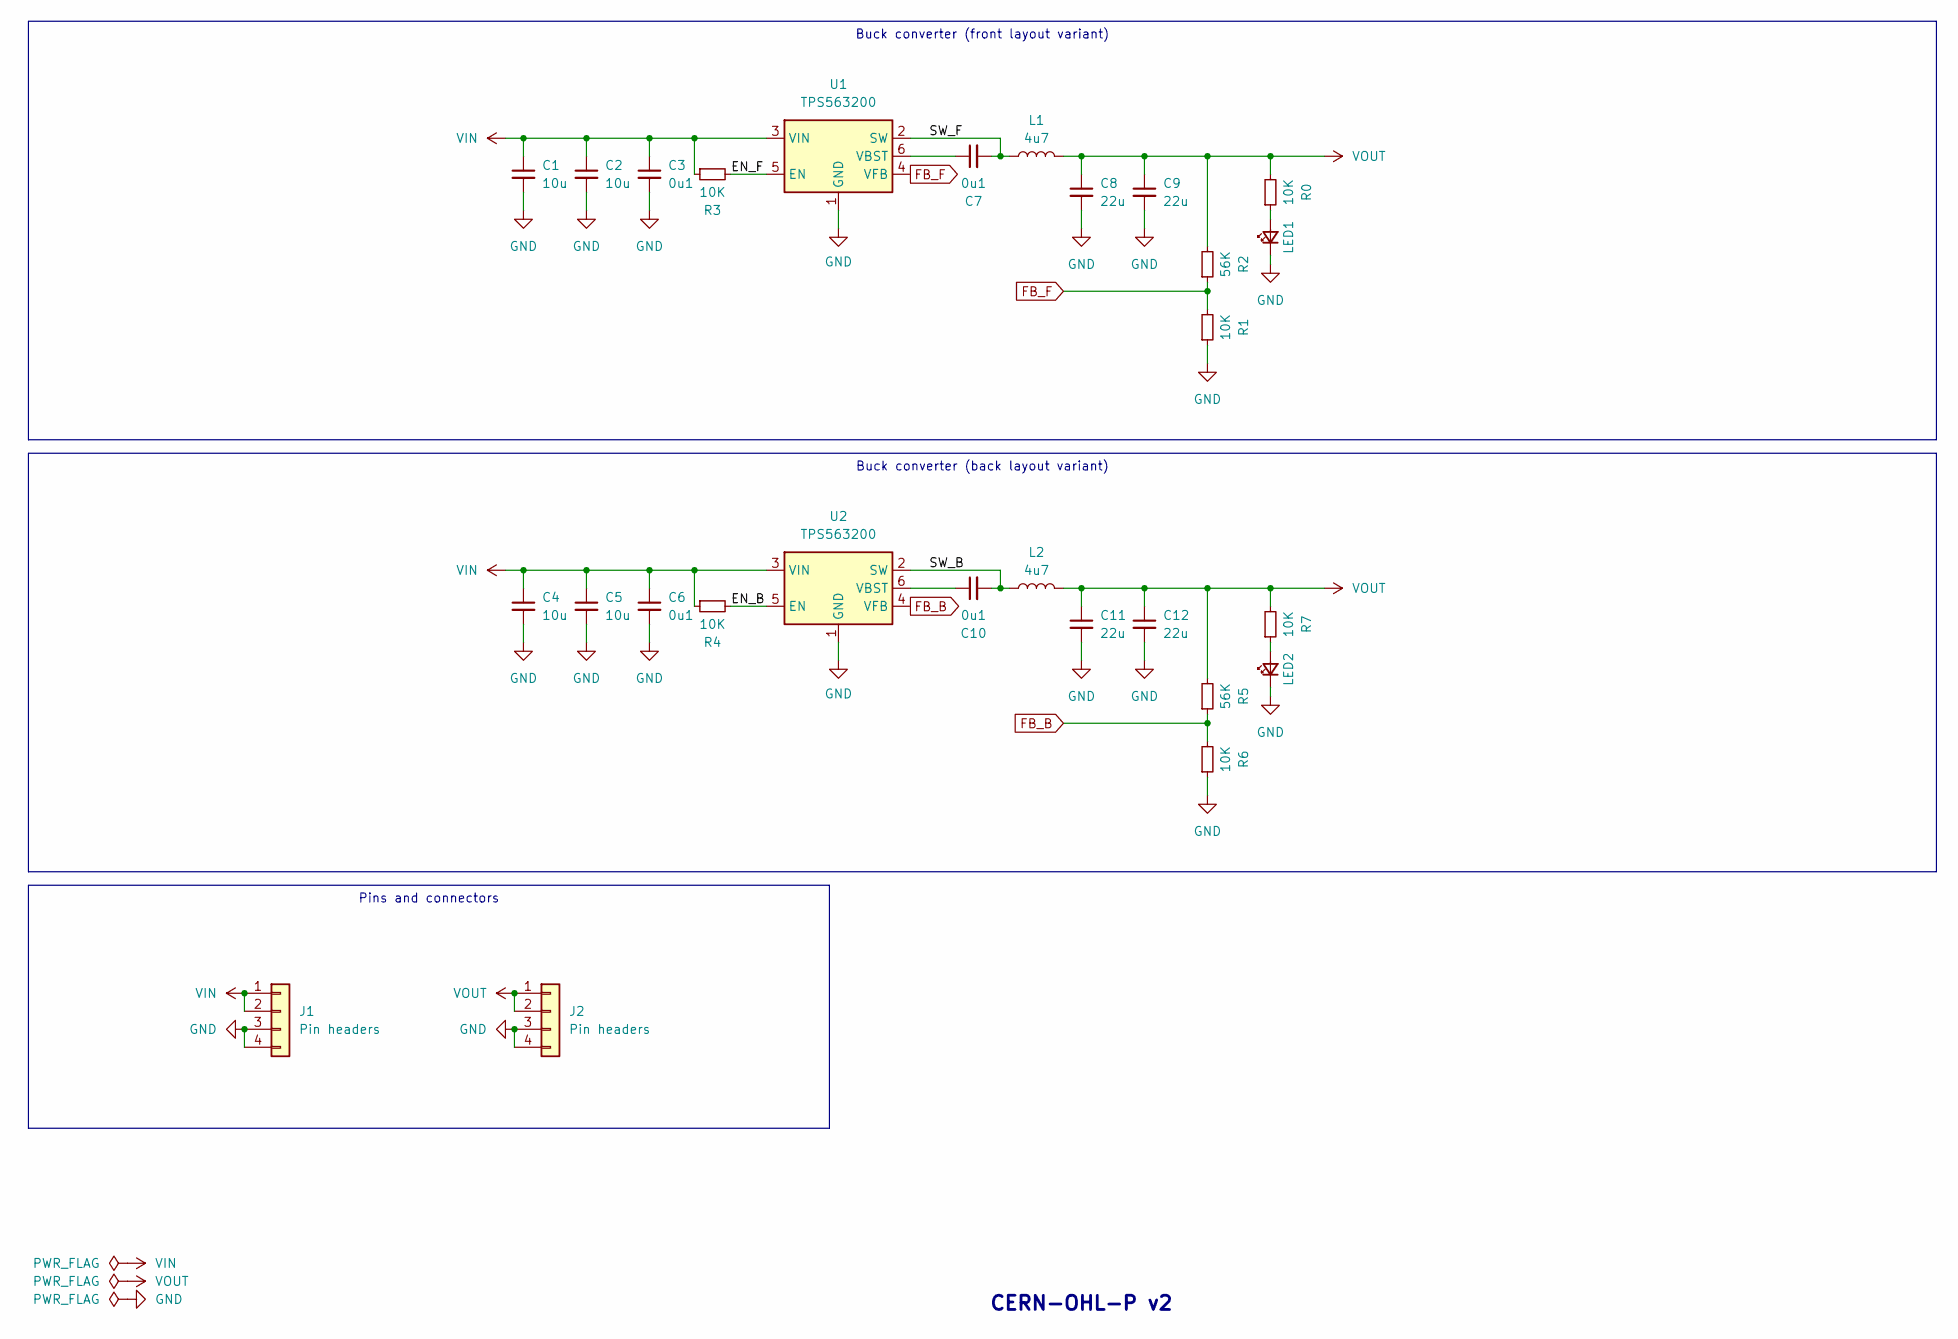
[picture p165: schematic microbuck.kicad_sch]

Parts:
C1, C2, C4, C5: 10u; C_0603_1608Metric_Pad1.08x0.95mm_HandSolder
C3, C6, C7, C10: 0u1; C_0603_1608Metric_Pad1.08x0.95mm_HandSolder
C8, C9, C11, C12: 22u; C_0603_1608Metric_Pad1.08x0.95mm_HandSolder
J1, J2: Pin headers; PinHeader_1x04_P2.54mm_Vertical_simple_pad3,4gnd
L1, L2: 4u7; L_1008_2520Metric
LED1, LED2: LED_Small; LED_0603_1608Metric_Pad1.05x0.95mm_HandSolder_simple
R0, R1, R3, R4, R6, R7: 10K; R_0603_1608Metric_Pad0.98x0.95mm_HandSolder
R2, R5: 56K; R_0603_1608Metric_Pad0.98x0.95mm_HandSolder
U1, U2: TPS563200; SOT-23-6

Connections:
/EN_B: R4.2, U2.5 (EN)
/EN_F: R3.2, U1.5 (EN)
/SW_B: C10.2, L2.1, U2.2 (SW)
/SW_F: C7.2, L1.1, U1.2 (SW)
FB_B: R5.1, R6.2, U2.4 (VFB)
FB_F: R1.2, R2.1, U1.4 (VFB)
GND: C1.2, C2.2, C3.2, C4.2, C5.2, C6.2, C8.2, C9.2, C11.2, C12.2, J1.3, J1.4, J2.3, J2.4, LED1.1 (K), LED2.1 (K), R1.1, R6.1, U1.1 (GND), U2.1 (GND)
unnamed: LED1.2 (A), R0.1
unnamed: LED2.2 (A), R7.1
unnamed: C7.1, U1.6 (VBST)
unnamed: C10.1, U2.6 (VBST)
VIN: C1.1, C2.1, C3.1, C4.1, C5.1, C6.1, J1.1, J1.2, R3.1, R4.1, U1.3 (VIN), U2.3 (VIN)
VOUT: C8.1, C9.1, C11.1, C12.1, J2.1, J2.2, L1.2, L2.2, R0.2, R2.2, R5.2, R7.2

Notes on the sheet:
Pins and connectors
Buck converter (front layout variant)
Buck converter (back layout variant)
CERN-OHL-P v2

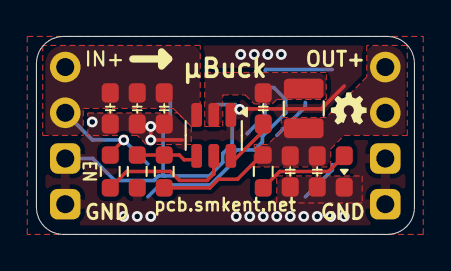
[picture p166: board microbuck.kicad_pcb from above]

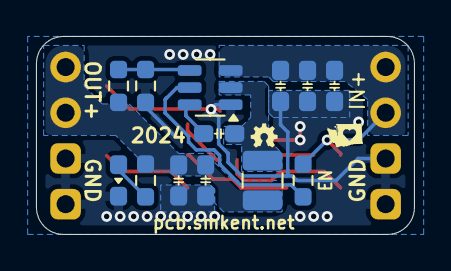
[picture p167: board microbuck.kicad_pcb from below]

Board: 2 copper layers, 21.0 x 11.0 mm, 28 parts (15 on the bottom side), 13 nets.
