smkent/pcb/pcb/jigs/led-jig/led-jig.kicad_pcb

## KiCad design pcb/jigs/led-jig/led-jig.kicad_pcb (2025-02-08)

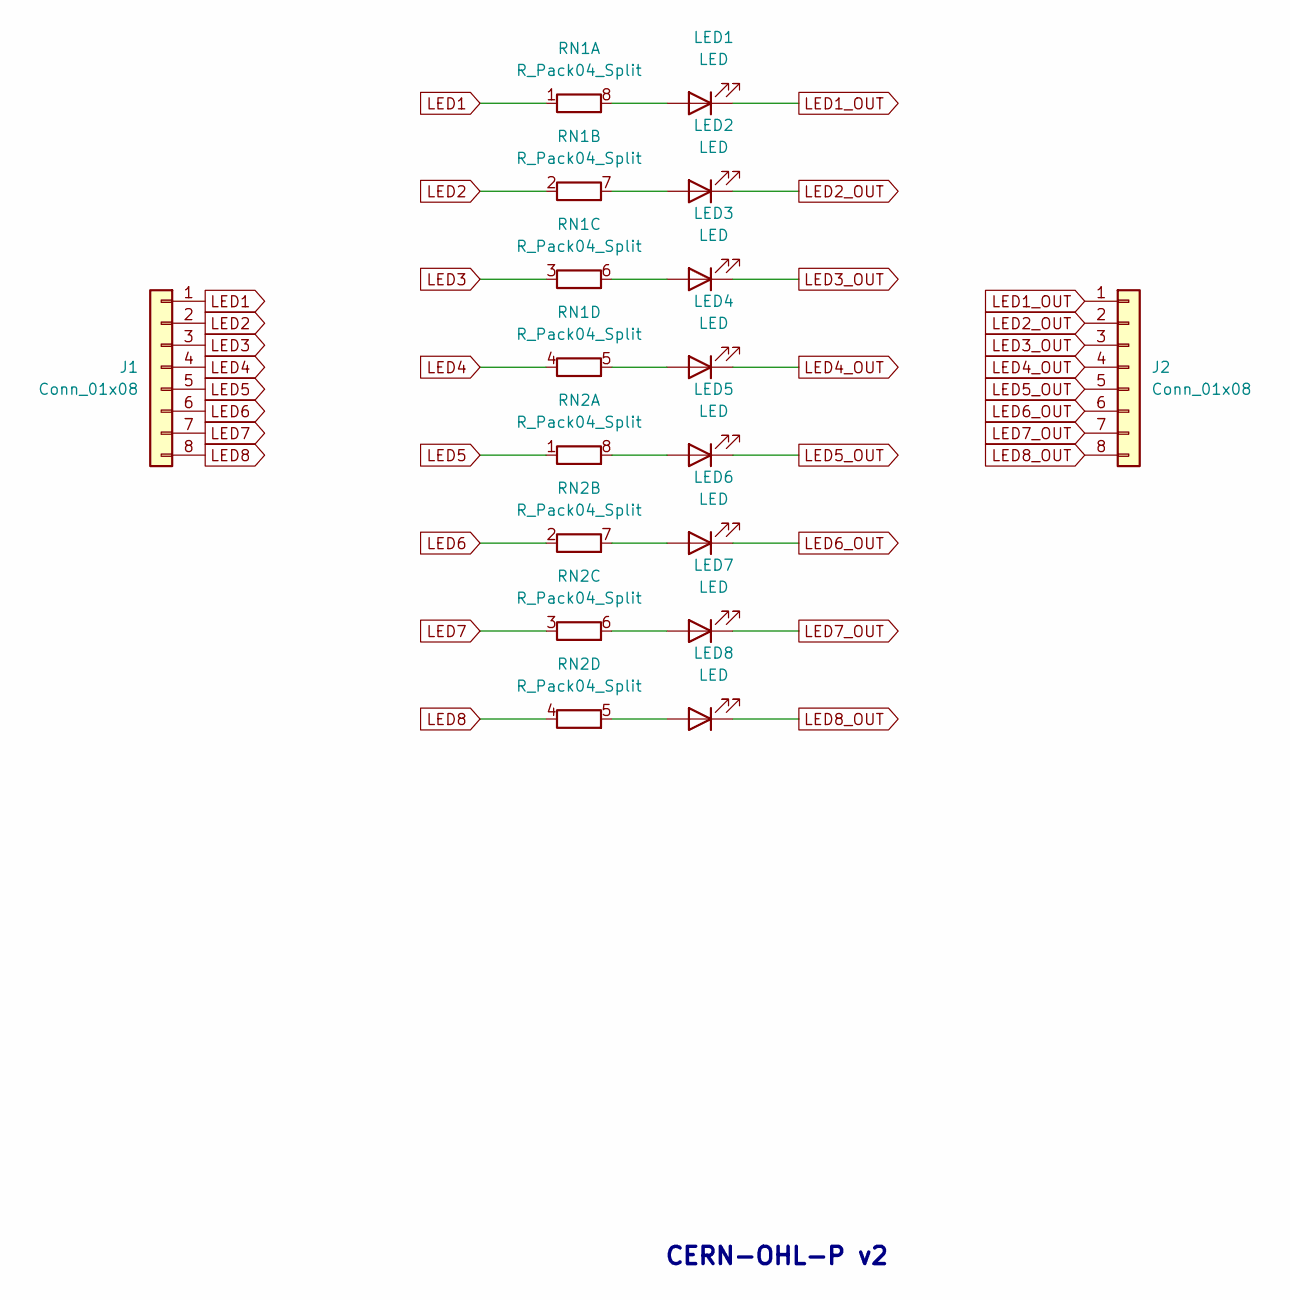
[picture p168: schematic led-jig.kicad_sch, LED Jig]

Parts:
J1, J2: Conn_01x08; PinHeader_1x08_P2.54mm_Vertical_simple
LED1, LED2, LED3, LED4, LED5, LED6, LED7, LED8: LED; LED_0805_2012Metric_Pad1.15x1.40mm_HandSolder_simple
RN1, RN2: R_Pack04_Split; R_Array_Convex_4x0603

Connections:
LED1: J1.1, RN1.1 (R1.1)
LED1_OUT: J2.1, LED1.1 (K)
LED2: J1.2, RN1.2 (R2.1)
LED2_OUT: J2.2, LED2.1 (K)
LED3: J1.3, RN1.3 (R3.1)
LED3_OUT: J2.3, LED3.1 (K)
LED4: J1.4, RN1.4 (R4.1)
LED4_OUT: J2.4, LED4.1 (K)
LED5: J1.5, RN2.1 (R1.1)
LED5_OUT: J2.5, LED5.1 (K)
LED6: J1.6, RN2.2 (R2.1)
LED6_OUT: J2.6, LED6.1 (K)
LED7: J1.7, RN2.3 (R3.1)
LED7_OUT: J2.7, LED7.1 (K)
LED8: J1.8, RN2.4 (R4.1)
LED8_OUT: J2.8, LED8.1 (K)
unnamed: LED1.2 (A), RN1.8 (R1.2)
unnamed: LED2.2 (A), RN1.7 (R2.2)
unnamed: LED3.2 (A), RN1.6 (R3.2)
unnamed: LED4.2 (A), RN1.5 (R4.2)
unnamed: LED5.2 (A), RN2.8 (R1.2)
unnamed: LED6.2 (A), RN2.7 (R2.2)
unnamed: LED7.2 (A), RN2.6 (R3.2)
unnamed: LED8.2 (A), RN2.5 (R4.2)

Notes on the sheet:
CERN-OHL-P v2

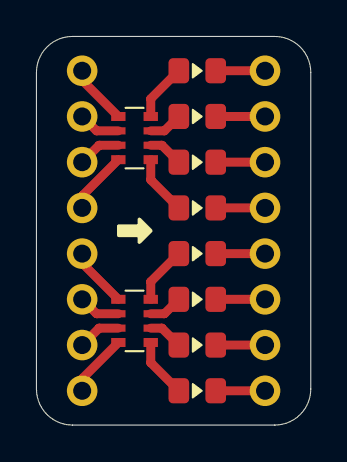
[picture p169: board led-jig.kicad_pcb from above]

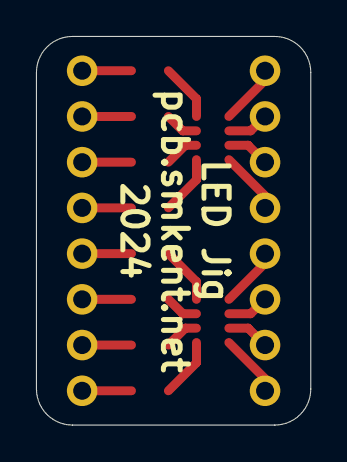
[picture p170: board led-jig.kicad_pcb from below]

Board: 2 copper layers, 15.2 x 21.6 mm, 12 parts (2 on the bottom side), 24 nets.
