smkent/pcb/pcb/misc/usb-pd-decoy-husb238/usb-pd-decoy-husb238.kicad_pcb

## KiCad design pcb/misc/usb-pd-decoy-husb238/usb-pd-decoy-husb238.kicad_pcb (2025-02-08)

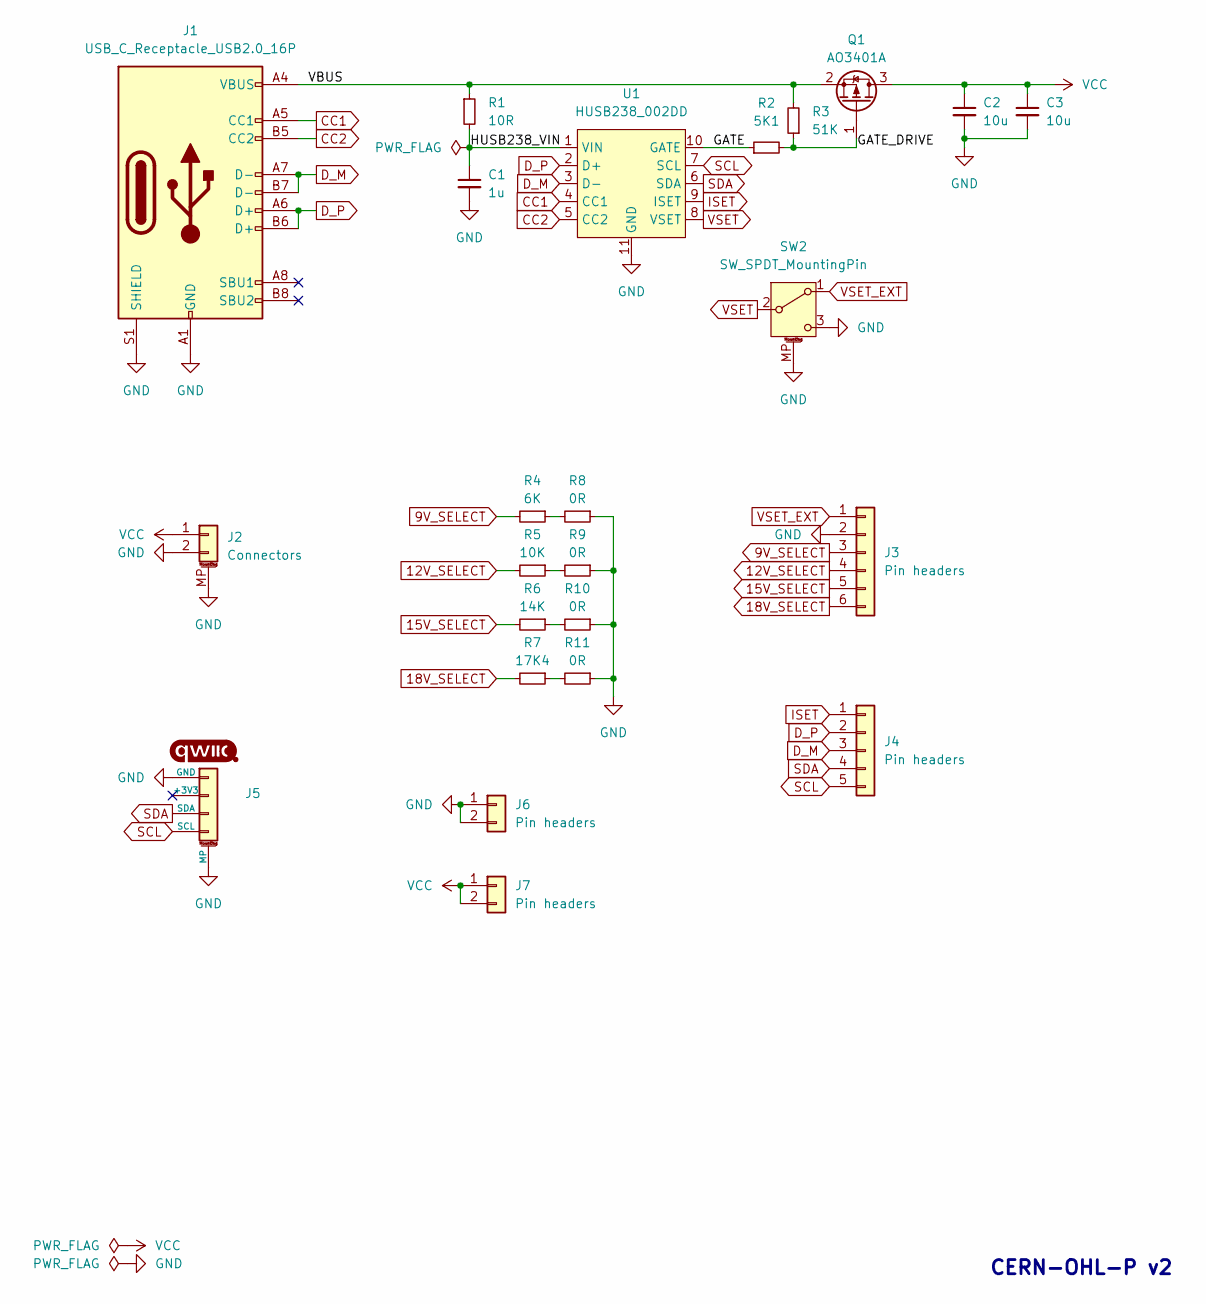
[picture p171: schematic usb-pd-decoy-husb238.kicad_sch]

Parts:
C1: 1u; C_0603_1608Metric
C2, C3: 10u; C_0603_1608Metric
J1: USB_C_Receptacle_USB2.0_16P; USB_C_Receptacle_GCT_USB4105-xx-A_16P_TopMnt_Horizontal
J2: Connectors; Conn_Combo_TerminalBlock_JST-1x02-XH_PH-pad2gnd
J3: Pin headers; PinHeader_1x06_P2.54mm_Vertical_simple
J4: Pin headers; PinHeader_1x05_P2.54mm_Vertical_simple
J5: Qwiic; Qwiic-SMD-horizontal-logo-bottom-pinout
J6, J7: Pin headers; PinHeader_1x02_P2.54mm_Vertical_simple
Q1: AO3401A; SOT-23
R1: 10R; R_0603_1608Metric
R2: 5K1; R_0603_1608Metric
R3: 51K; R_0603_1608Metric
R4: 6K; R_0603_1608Metric
R5: 10K; R_0603_1608Metric
R6: 14K; R_0603_1608Metric
R7: 17K4; R_0603_1608Metric
R8, R9, R10, R11: 0R; R_0603_1608Metric
SW2: SW_SPDT_MountingPin; SW_SPDT_PCM12
U1: HUSB238_002DD; WDFN-10-1EP_3x3mm_P0.5mm_EP1.8x2.5mm; LCSC Part C7471904

Connections:
9V_SELECT: J3.3, R4.2
12V_SELECT: J3.4, R5.2
15V_SELECT: J3.5, R6.2
18V_SELECT: J3.6, R7.2
/GATE: R2.1, U1.10 (GATE)
/GATE_DRIVE: Q1.1 (G), R2.2, R3.1
/HUSB238_VIN: C1.1, R1.2, U1.1 (VIN)
/VBUS: J1.A4 (VBUS), J1.A9 (VBUS), J1.B4 (VBUS), J1.B9 (VBUS), Q1.2 (S), R1.1, R3.2
CC1: J1.A5 (CC1), U1.4 (CC1)
CC2: J1.B5 (CC2), U1.5 (CC2)
D_M: J1.A7 (D-), J1.B7 (D-), J4.3, U1.3 (D-)
D_P: J1.A6 (D+), J1.B6 (D+), J4.2, U1.2 (D+)
GND: C1.2, C2.2, C3.2, J1.A1 (GND), J1.A12 (GND), J1.B1 (GND), J1.B12 (GND), J1.S1 (SHIELD), J2.2, J2.MP (MountPin), J3.2, J5.1 (GND), J5.MP, J6.1, J6.2, R8.1, R9.1, R10.1, R11.1, SW2.3 (C), SW2.MP (MountPin), U1.11 (GND)
ISET: J4.1, U1.9 (ISET)
unnamed: R4.1, R8.2
unnamed: R5.1, R9.2
unnamed: R6.1, R10.2
unnamed: R7.1, R11.2
SCL: J4.5, J5.4 (SCL), U1.7 (SCL)
SDA: J4.4, J5.3 (SDA), U1.6 (SDA)
VCC: C2.1, C3.1, J2.1, J7.1, J7.2, Q1.3 (D)
VSET: SW2.2 (B), U1.8 (VSET)
VSET_EXT: J3.1, SW2.1 (A)

Notes on the sheet:
CERN-OHL-P v2

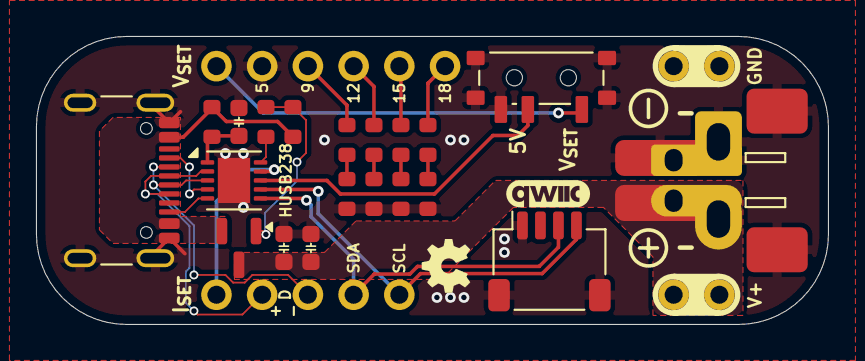
[picture p172: board usb-pd-decoy-husb238.kicad_pcb from above]

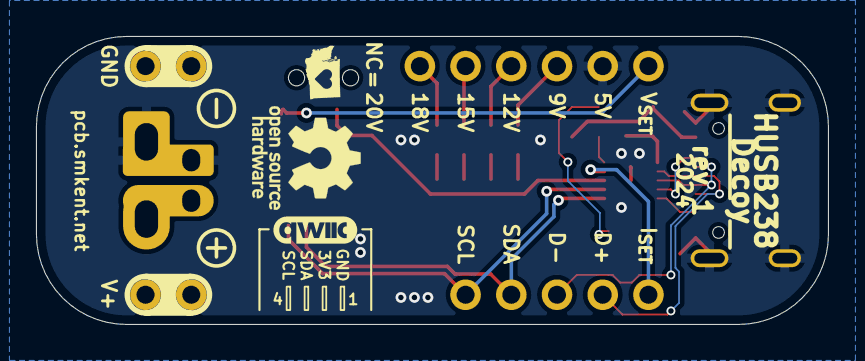
[picture p173: board usb-pd-decoy-husb238.kicad_pcb from below]

Board: 2 copper layers, 44.0 x 16.0 mm, 24 parts (4 on the bottom side), 23 nets.
