smkent/pcb/pcb/power/max17048/max17048.kicad_pcb

## KiCad design pcb/power/max17048/max17048.kicad_pcb (2025-02-08)

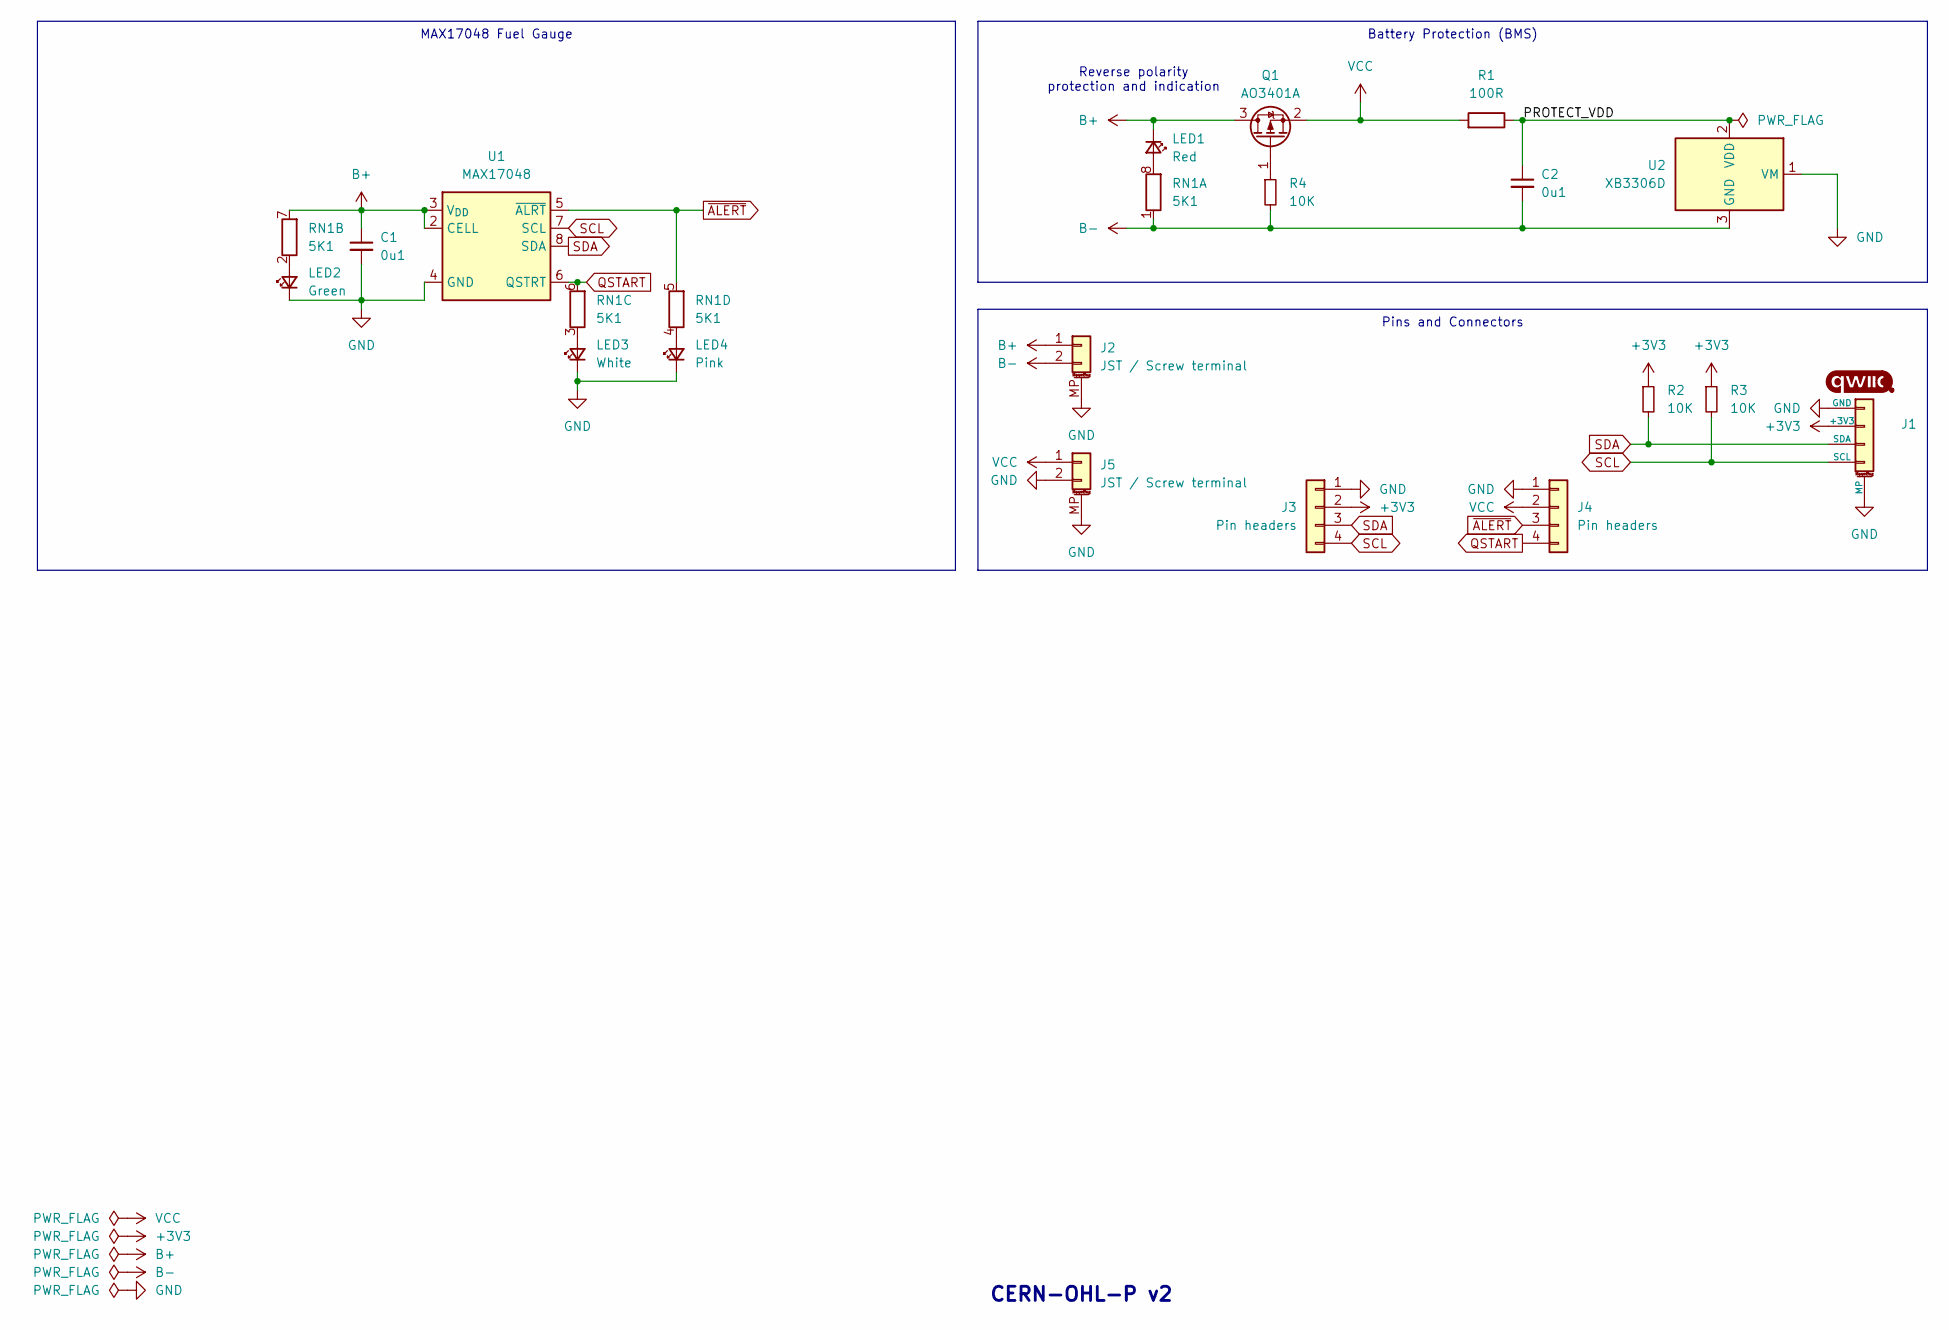
[picture p174: schematic max17048.kicad_sch]

Parts:
C1, C2: 0u1; C_0603_1608Metric
J1: Qwiic; Qwiic-SMD-horizontal-logo-bottom-pinout
J2, J5: JST / Screw terminal; Conn_Combo_TerminalBlock_JST-1x02-XH_PH-pad2gnd
J3, J4: Pin headers; PinHeader_1x04_P2.54mm_Vertical_simple
LED1: Red; LED_0603_1608Metric_Pad1.05x0.95mm_HandSolder_simple; LCSC Part C2286
LED2: Green; LED_0603_1608Metric_Pad1.05x0.95mm_HandSolder_simple; LCSC Part C2286
LED3: White; LED_0603_1608Metric_Pad1.05x0.95mm_HandSolder_simple; LCSC Part C2286
LED4: Pink; LED_0603_1608Metric_Pad1.05x0.95mm_HandSolder_simple; LCSC Part C2286
Q1: AO3401A; SOT-23
R1: 100R; R_0603_1608Metric; LCSC Part C25076
R2, R3, R4: 10K; R_0603_1608Metric
RN1: 5K1; R_Array_Convex_4x0603
U1: MAX17048; TDFN-8-1EP_2x2mm_P0.5mm_EP0.8x1.2mm; LCSC Part C2682616
U2: XB3306D; SOT-23; LCSC Part C2759992

Connections:
+3V3: J1.2 (+3V3), J3.2, R2.1, R3.1
/PROTECT_VDD: C2.1, R1.1, U2.2 (VDD)
B+: C1.1, J2.1, LED1.1 (K), Q1.3 (D), RN1.7 (R2.2), U1.2 (CELL), U1.3 (V_{DD})
B-: C2.2, J2.2, R4.2, RN1.1 (R1.1), U2.3 (GND)
GND: C1.2, J1.1 (GND), J1.MP, J2.MP (MountPin), J3.1, J4.1, J5.2, J5.MP (MountPin), LED2.1 (K), LED3.1 (K), LED4.1 (K), U1.1 (CTG), U1.4 (GND), U1.9 (EP), U2.1 (VM)
unnamed: LED1.2 (A), RN1.8 (R1.2)
unnamed: LED2.2 (A), RN1.2 (R2.1)
unnamed: LED3.2 (A), RN1.3 (R3.1)
unnamed: LED4.2 (A), RN1.4 (R4.1)
unnamed: Q1.1 (G), R4.1
QSTART: J4.4, RN1.6 (R3.2), U1.6 (QSTRT)
SCL: J1.4 (SCL), J3.4, R3.2, U1.7 (SCL)
SDA: J1.3 (SDA), J3.3, R2.2, U1.8 (SDA)
VCC: J4.2, J5.1, Q1.2 (S), R1.2
~ALERT: J4.3, RN1.5 (R4.2), U1.5 (~ALRT)

Notes on the sheet:
MAX17048 Fuel Gauge
Pins and Connectors
Battery Protection (BMS)
CERN-OHL-P v2
Reverse polarity protection and indication

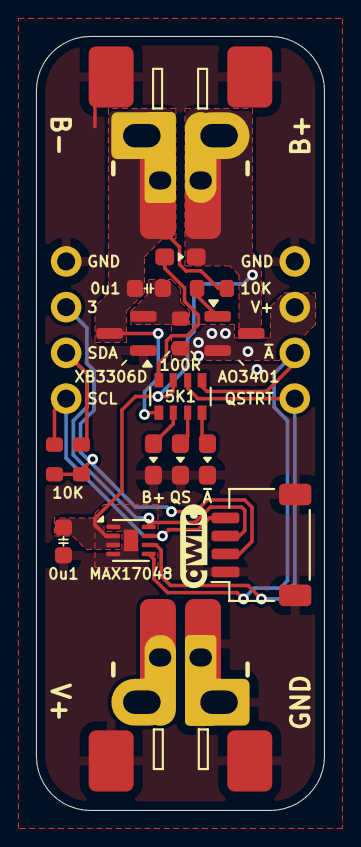
[picture p175: board max17048.kicad_pcb from above]

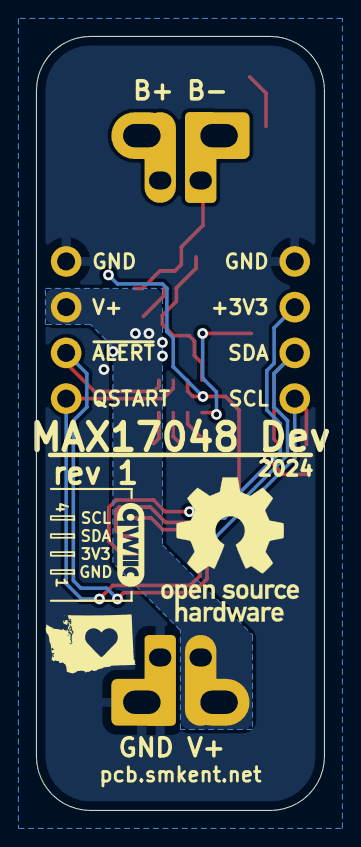
[picture p176: board max17048.kicad_pcb from below]

Board: 2 copper layers, 16.0 x 43.0 mm, 19 parts (2 on the bottom side), 15 nets.
