smkent/pcb/pcb/jigs/smd-mosfet/smd-mosfet.kicad_pcb

## KiCad design pcb/jigs/smd-mosfet/smd-mosfet.kicad_pcb (2025-02-08)

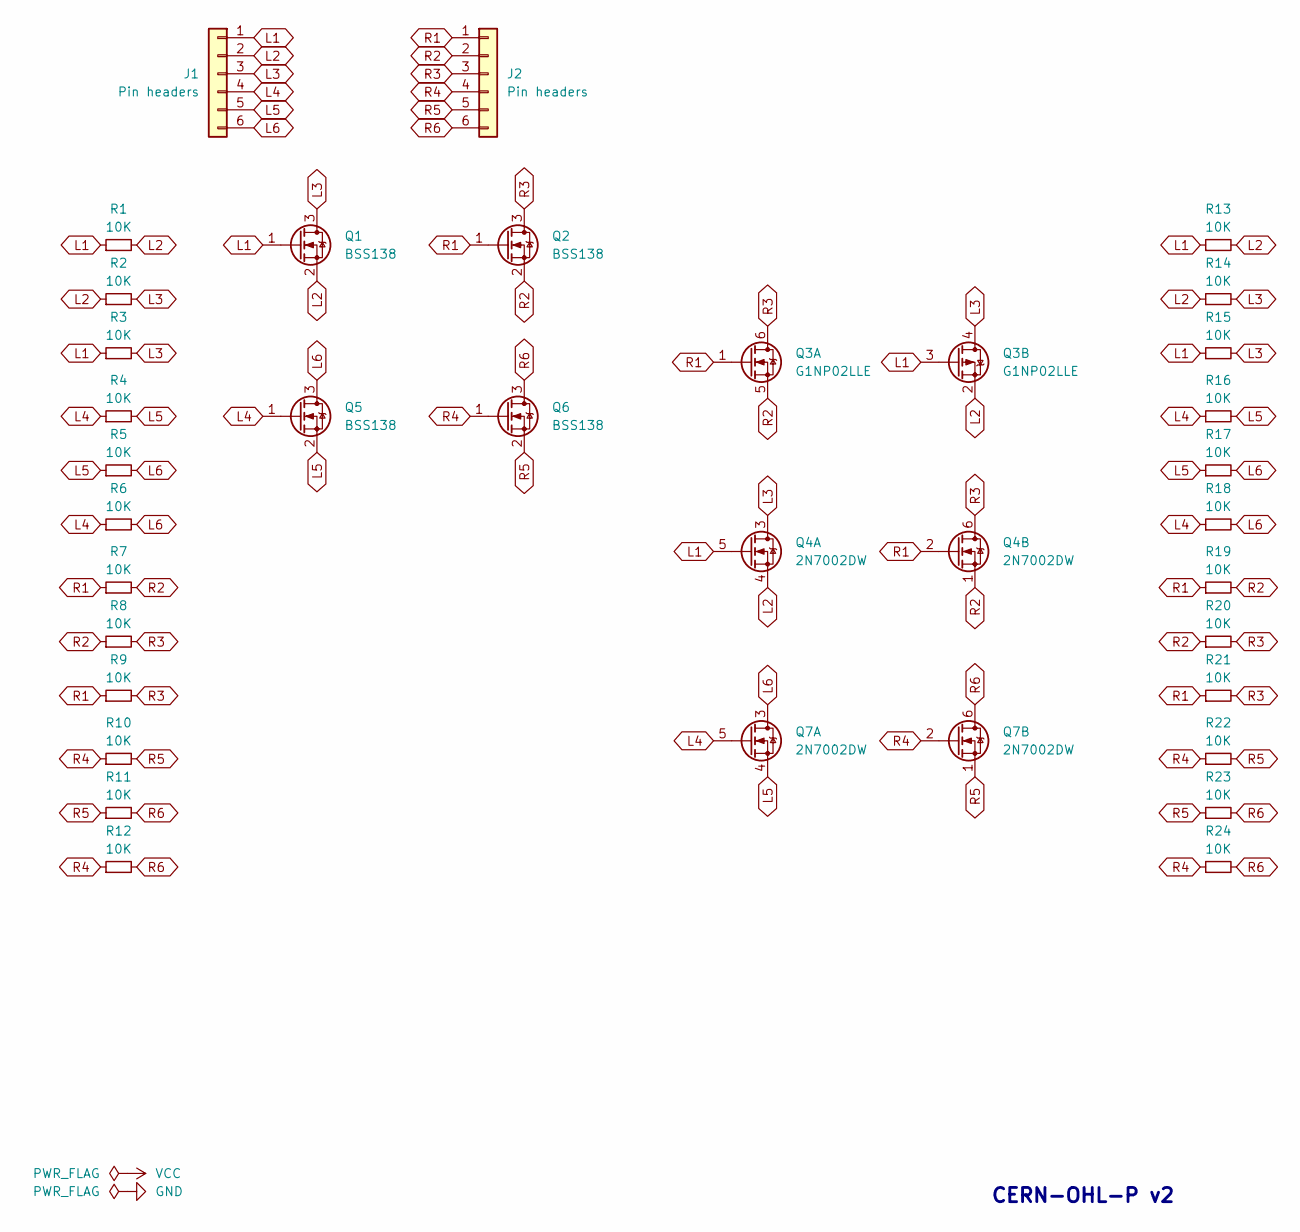
[picture p177: schematic smd-mosfet.kicad_sch]

Parts:
J1, J2: Pin headers; PinHeader_1x06_P2.54mm_Vertical_slim_simple
Q1, Q2, Q5, Q6: BSS138; SOT-23_mosfet
Q3: G1NP02LLE; SOT-23-6_G1NP02LLE_mosfet; LCSC Part C7465318
Q4, Q7: 2N7002DW; SOT-363_SC-70-6_mosfet; LCSC Part C5190214
R1, R2, R3, R4, R5, R6, R7, R8, R9, R10, R11, R12, R13, R14, R15, R16, R17, R18, R19, R20, R21, R22, R23, R24: 10K; R_0603_1608Metric_Pad0.98x0.95mm_HandSolder_simple

Connections:
L1: J1.1, Q1.1 (G), Q3.3 (G), Q4.5 (G), R1.1, R3.1, R13.1, R15.1
L2: J1.2, Q1.2 (S), Q3.2 (S), Q4.4 (S), R1.2, R2.1, R13.2, R14.1
L3: J1.3, Q1.3 (D), Q3.4 (D), Q4.3 (D), R2.2, R3.2, R14.2, R15.2
L4: J1.4, Q5.1 (G), Q7.5 (G), R4.1, R6.1, R16.1, R18.1
L5: J1.5, Q5.2 (S), Q7.4 (S), R4.2, R5.1, R16.2, R17.1
L6: J1.6, Q5.3 (D), Q7.3 (D), R5.2, R6.2, R17.2, R18.2
R1: J2.1, Q2.1 (G), Q3.1 (G), Q4.2 (G), R7.1, R9.1, R19.1, R21.1
R2: J2.2, Q2.2 (S), Q3.5 (S), Q4.1 (S), R7.2, R8.1, R19.2, R20.1
R3: J2.3, Q2.3 (D), Q3.6 (D), Q4.6 (D), R8.2, R9.2, R20.2, R21.2
R4: J2.4, Q6.1 (G), Q7.2 (G), R10.1, R12.1, R22.1, R24.1
R5: J2.5, Q6.2 (S), Q7.1 (S), R10.2, R11.1, R22.2, R23.1
R6: J2.6, Q6.3 (D), Q7.6 (D), R11.2, R12.2, R23.2, R24.2

Notes on the sheet:
CERN-OHL-P v2

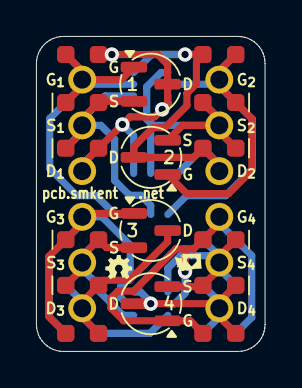
[picture p178: board smd-mosfet.kicad_pcb from above]

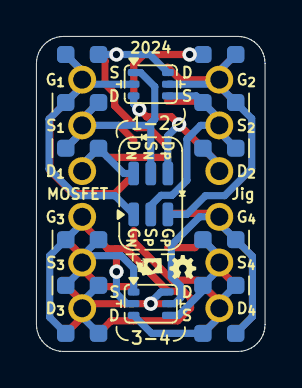
[picture p179: board smd-mosfet.kicad_pcb from below]

Board: 2 copper layers, 12.7 x 17.5 mm, 33 parts (17 on the bottom side), 12 nets.
