smkent/pcb/pcb/jigs/logic-led-jig/logic-led-jig.kicad_pcb

## KiCad design pcb/jigs/logic-led-jig/logic-led-jig.kicad_pcb (2025-02-08)

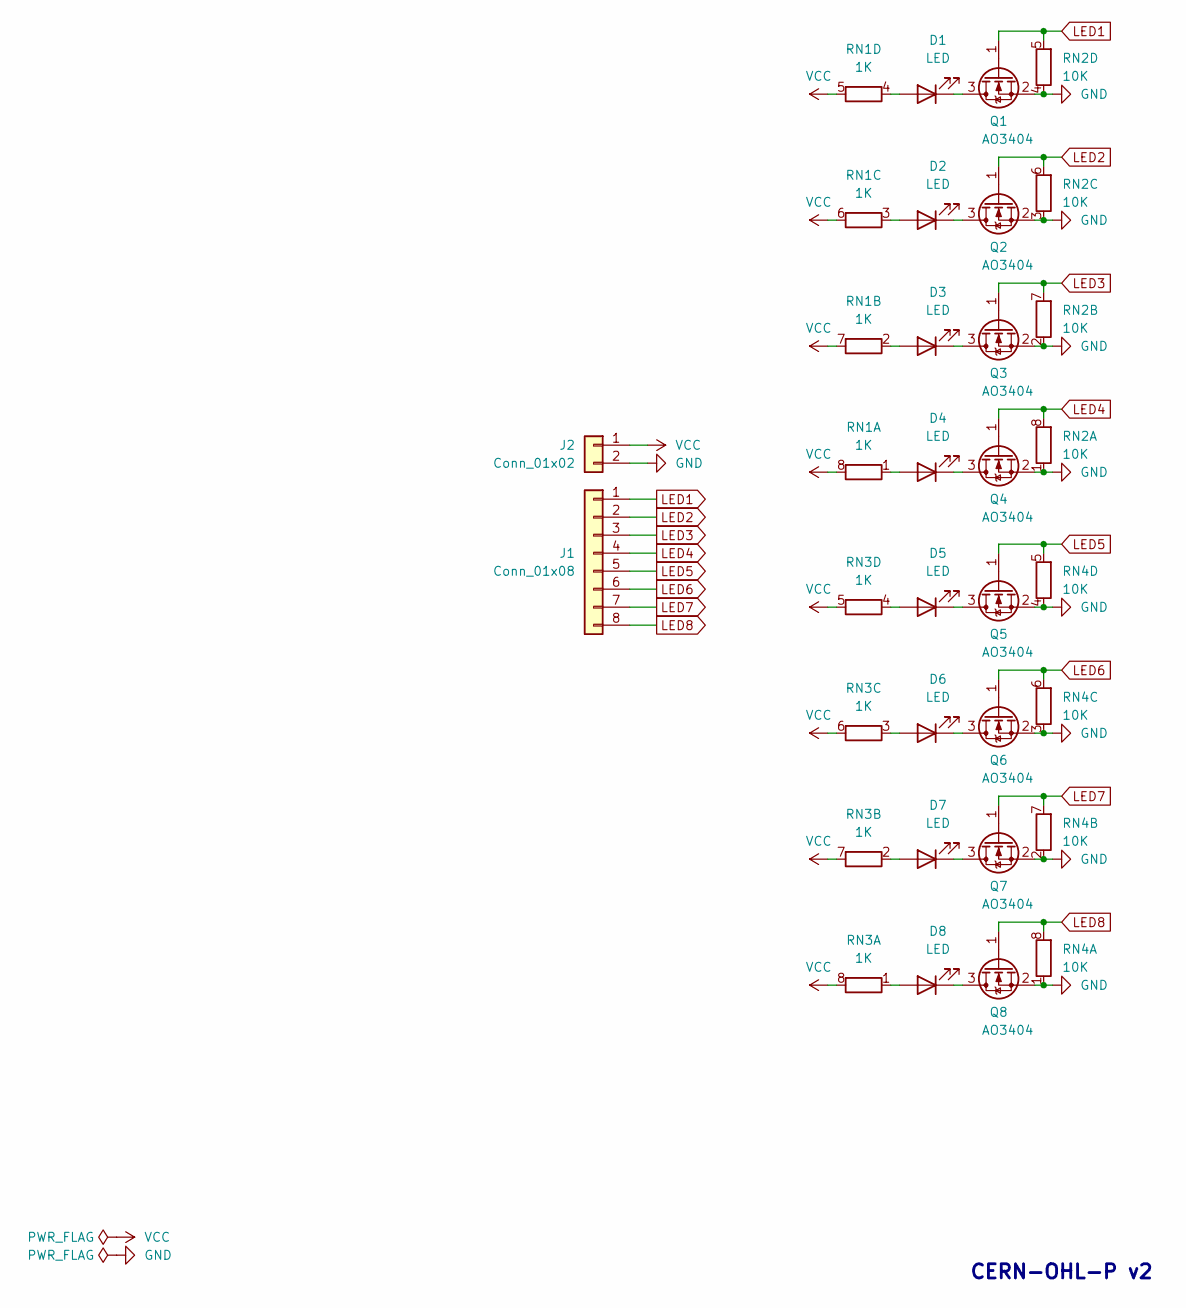
[picture p180: schematic logic-led-jig.kicad_sch, Logic LED Jig]

Parts:
D1, D2, D3, D4, D5, D6, D7, D8: LED; LED_0805_2012Metric
J1: Conn_01x08; PinHeader_1x08_P2.54mm_Vertical_simple
J2: Conn_01x02; PinHeader_1x02_P2.54mm_Vertical_simple_pad2gnd
Q1, Q2, Q3, Q4, Q5, Q6, Q7, Q8: AO3404; SOT-23
RN1, RN3: 1K; R_Array_Convex_4x0603
RN2, RN4: 10K; R_Array_Convex_4x0603

Connections:
GND: J2.2, Q1.2 (S), Q2.2 (S), Q3.2 (S), Q4.2 (S), Q5.2 (S), Q6.2 (S), Q7.2 (S), Q8.2 (S), RN2.1 (R1.1), RN2.2 (R2.1), RN2.3 (R3.1), RN2.4 (R4.1), RN4.1 (R1.1), RN4.2 (R2.1), RN4.3 (R3.1), RN4.4 (R4.1)
LED1: J1.1, Q1.1 (G), RN2.5 (R4.2)
LED2: J1.2, Q2.1 (G), RN2.6 (R3.2)
LED3: J1.3, Q3.1 (G), RN2.7 (R2.2)
LED4: J1.4, Q4.1 (G), RN2.8 (R1.2)
LED5: J1.5, Q5.1 (G), RN4.5 (R4.2)
LED6: J1.6, Q6.1 (G), RN4.6 (R3.2)
LED7: J1.7, Q7.1 (G), RN4.7 (R2.2)
LED8: J1.8, Q8.1 (G), RN4.8 (R1.2)
unnamed: D1.2 (A), RN1.4 (R4.1)
unnamed: D1.1 (K), Q1.3 (D)
unnamed: D2.2 (A), RN1.3 (R3.1)
unnamed: D2.1 (K), Q2.3 (D)
unnamed: D3.2 (A), RN1.2 (R2.1)
unnamed: D3.1 (K), Q3.3 (D)
unnamed: D4.2 (A), RN1.1 (R1.1)
unnamed: D4.1 (K), Q4.3 (D)
unnamed: D5.2 (A), RN3.4 (R4.1)
unnamed: D5.1 (K), Q5.3 (D)
unnamed: D6.2 (A), RN3.3 (R3.1)
unnamed: D6.1 (K), Q6.3 (D)
unnamed: D7.2 (A), RN3.2 (R2.1)
unnamed: D7.1 (K), Q7.3 (D)
unnamed: D8.2 (A), RN3.1 (R1.1)
unnamed: D8.1 (K), Q8.3 (D)
VCC: J2.1, RN1.5 (R4.2), RN1.6 (R3.2), RN1.7 (R2.2), RN1.8 (R1.2), RN3.5 (R4.2), RN3.6 (R3.2), RN3.7 (R2.2), RN3.8 (R1.2)

Notes on the sheet:
CERN-OHL-P v2

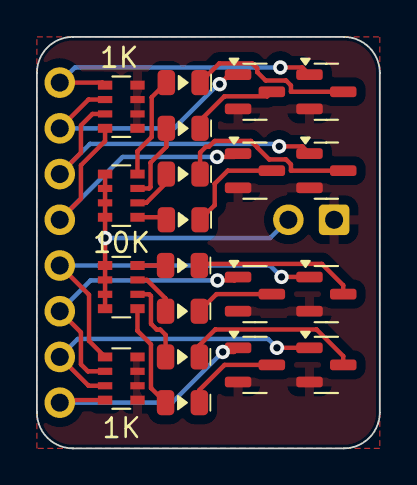
[picture p181: board logic-led-jig.kicad_pcb from above]

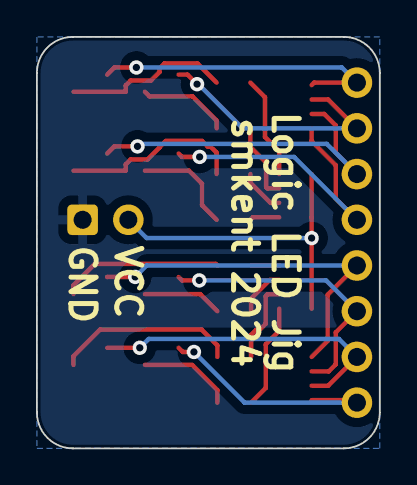
[picture p182: board logic-led-jig.kicad_pcb from below]

Board: 2 copper layers, 19.1 x 22.9 mm, 22 parts (2 on the bottom side), 26 nets.
