smkent/pcb/pcb/jigs/level-shifter/level-shifter.kicad_pcb

## KiCad design pcb/jigs/level-shifter/level-shifter.kicad_pcb (2025-02-08)

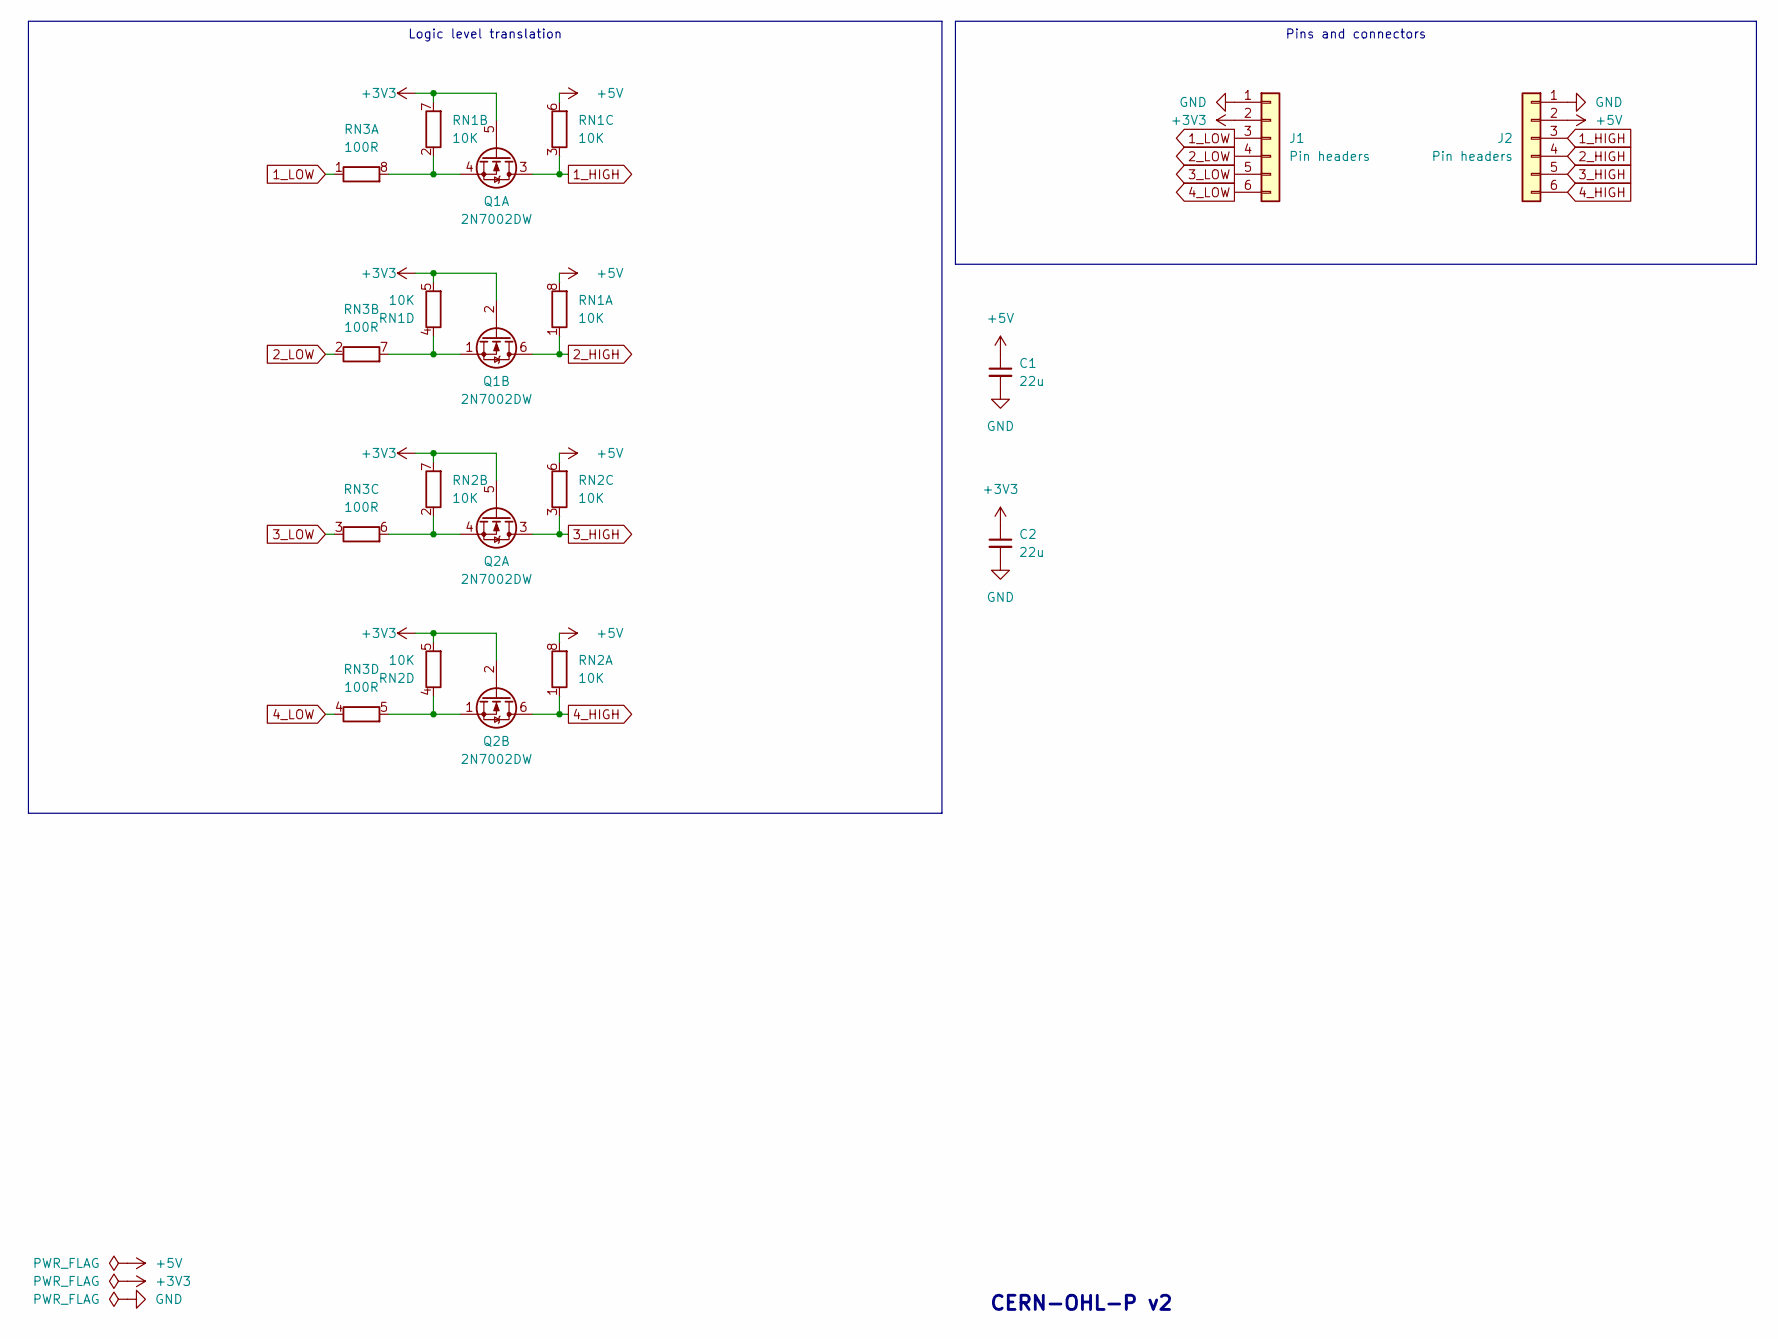
[picture p183: schematic level-shifter.kicad_sch]

Parts:
C1, C2: 22u; C_0603_1608Metric_Pad1.08x0.95mm_HandSolder
J1, J2: Pin headers; PinHeader_1x06_P2.54mm_Vertical_simple_pad1gnd
Q1, Q2: 2N7002DW; SOT-363_SC-70-6; LCSC Part C5190214
RN1, RN2: 10K; R_Array_Convex_4x0603
RN3: 100R; R_Array_Convex_4x0603

Connections:
1_HIGH: J2.3, Q1.3 (D), RN1.3 (R3.1)
1_LOW: J1.3, RN3.1 (R1.1)
2_HIGH: J2.4, Q1.6 (D), RN1.1 (R1.1)
2_LOW: J1.4, RN3.2 (R2.1)
3_HIGH: J2.5, Q2.3 (D), RN2.3 (R3.1)
3_LOW: J1.5, RN3.3 (R3.1)
4_HIGH: J2.6, Q2.6 (D), RN2.1 (R1.1)
4_LOW: J1.6, RN3.4 (R4.1)
+3V3: C2.1, J1.2, Q1.2 (G), Q1.5 (G), Q2.2 (G), Q2.5 (G), RN1.5 (R4.2), RN1.7 (R2.2), RN2.5 (R4.2), RN2.7 (R2.2)
+5V: C1.1, J2.2, RN1.6 (R3.2), RN1.8 (R1.2), RN2.6 (R3.2), RN2.8 (R1.2)
GND: C1.2, C2.2, J1.1, J2.1
unnamed: Q1.4 (S), RN1.2 (R2.1), RN3.8 (R1.2)
unnamed: Q1.1 (S), RN1.4 (R4.1), RN3.7 (R2.2)
unnamed: Q2.4 (S), RN2.2 (R2.1), RN3.6 (R3.2)
unnamed: Q2.1 (S), RN2.4 (R4.1), RN3.5 (R4.2)

Notes on the sheet:
Pins and connectors
Logic level translation
CERN-OHL-P v2

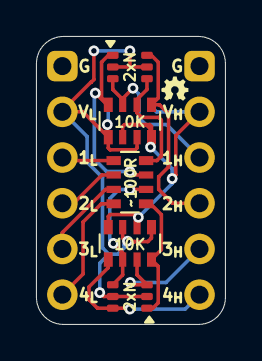
[picture p184: board level-shifter.kicad_pcb from above]

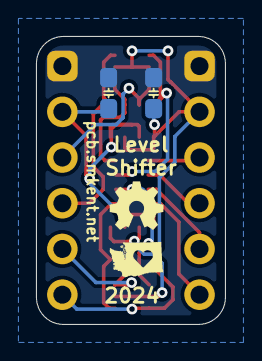
[picture p185: board level-shifter.kicad_pcb from below]

Board: 2 copper layers, 10.5 x 16.0 mm, 9 parts (4 on the bottom side), 15 nets.
