smkent/pcb/dev-boards/breadboard-power/breadboard-power.kicad_sch

## KiCad design dev-boards/breadboard-power/breadboard-power.kicad_sch (2024-08-13)

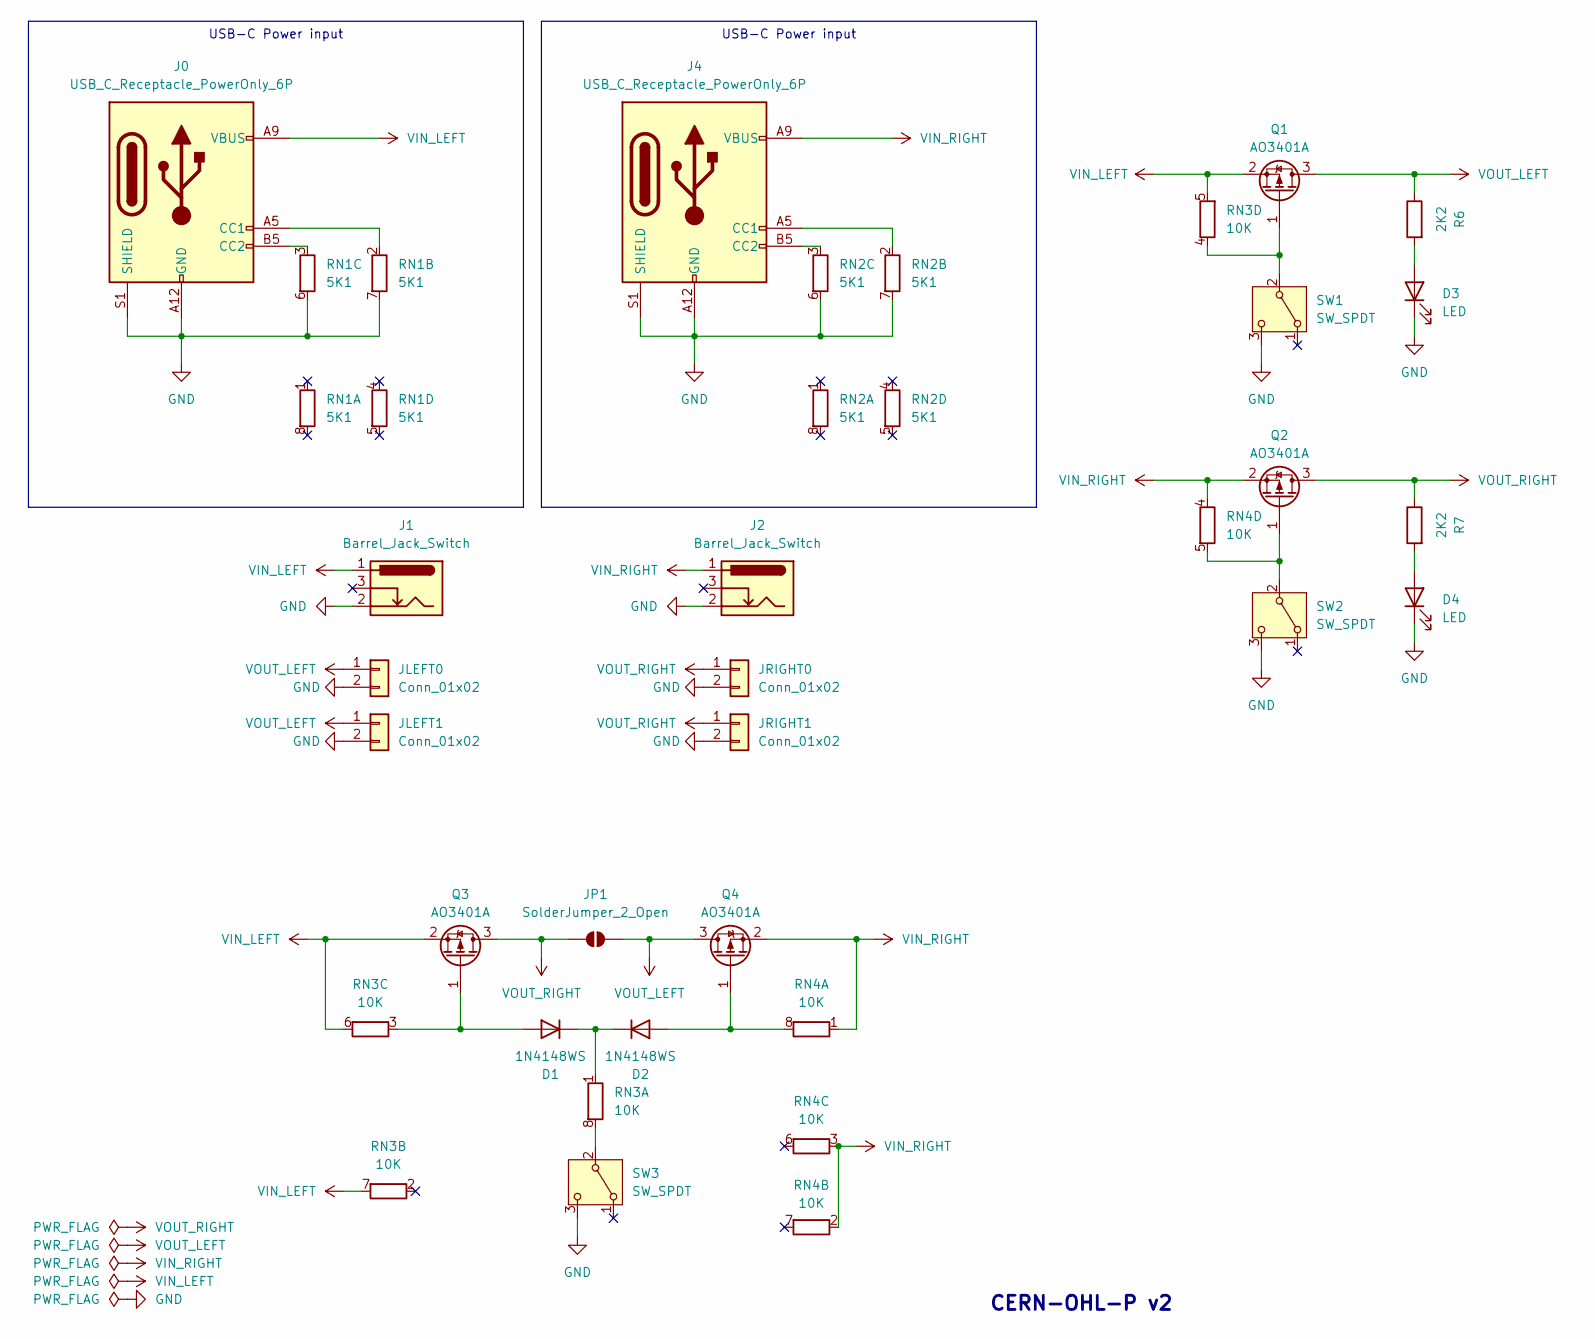
[picture p186: schematic breadboard-power.kicad_sch]

Parts:
D1, D2: 1N4148WS; D_SOD-323_HandSoldering_simple
D3, D4: LED; LED_0805_2012Metric_Pad1.15x1.40mm_HandSolder_simple
J0, J4: USB_C_Receptacle_PowerOnly_6P; USB_C_Receptacle_GCT_USB4125-xx-x_6P_TopMnt_Horizontal_hand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
J1, J2: Barrel_Jack_Switch; Conn_Combo_DC-050_TerminalBlock_JST-XH-2P-horizontal
JLEFT0, JLEFT1: Conn_01x02; PinHeader_1x02_P2.54mm_Vertical_simple_pad2gnd
JP1: SolderJumper_2_Open; SolderJumper-2_P1.3mm_Open_RoundedPad1.0x1.5mm_simple
JRIGHT0, JRIGHT1: Conn_01x02; PinHeader_1x02_P2.54mm_Vertical_simple_pad2gnd
Q1, Q2, Q3, Q4: AO3401A; SOT-23; LCSC Part C15127
R6, R7: 2K2; R_0805_2012Metric_Pad1.20x1.40mm_HandSolder
RN1, RN2: 5K1; R_Array_Convex_4x0603
RN3, RN4: 10K; R_Array_Convex_4x0603
SW1, SW2: SW_SPDT; SW-TH_DEALON_SS-12D01-GX_simple; LCSC Part C2998803
SW3: SW_SPDT; SW-SMD_3P-P1.50_L2.7-W6.6; LCSC Part C2998803

Connections:
GND: D3.1 (K), D4.1 (K), J0.A12 (GND), J0.B12 (GND), J0.S1 (SHIELD), J1.2, J2.2, J4.A12 (GND), J4.B12 (GND), J4.S1 (SHIELD), JLEFT0.2, JLEFT1.2, JRIGHT0.2, JRIGHT1.2, RN1.6 (R3.2), RN1.7 (R2.2), RN2.6 (R3.2), RN2.7 (R2.2), SW1.3 (C), SW2.3 (C), SW3.3 (C)
unnamed: D1.1 (K), D2.1 (K), RN3.1 (R1.1)
unnamed: D1.2 (A), Q3.1 (G), RN3.3 (R3.1)
unnamed: D2.2 (A), Q4.1 (G), RN4.8 (R1.2)
unnamed: D3.2 (A), R6.2
unnamed: D4.2 (A), R7.2
unnamed: J0.A5 (CC1), RN1.2 (R2.1)
unnamed: J0.B5 (CC2), RN1.3 (R3.1)
unnamed: J4.A5 (CC1), RN2.2 (R2.1)
unnamed: J4.B5 (CC2), RN2.3 (R3.1)
unnamed: Q1.1 (G), RN3.4 (R4.1), SW1.2 (B)
unnamed: Q2.1 (G), RN4.5 (R4.2), SW2.2 (B)
unnamed: RN3.8 (R1.2), SW3.2 (B)
VIN_LEFT: J0.A9 (VBUS), J0.B9 (VBUS), J1.1, Q1.2 (S), Q3.2 (S), RN3.5 (R4.2), RN3.6 (R3.2), RN3.7 (R2.2)
VIN_RIGHT: J2.1, J4.A9 (VBUS), J4.B9 (VBUS), Q2.2 (S), Q4.2 (S), RN4.1 (R1.1), RN4.2 (R2.1), RN4.3 (R3.1), RN4.4 (R4.1)
VOUT_LEFT: JLEFT0.1, JLEFT1.1, JP1.2 (B), Q1.3 (D), Q4.3 (D), R6.1
VOUT_RIGHT: JP1.1 (A), JRIGHT0.1, JRIGHT1.1, Q2.3 (D), Q3.3 (D), R7.1

Notes on the sheet:
USB-C Power input
CERN-OHL-P v2
