smkent/pcb/pcb-stackable-dev/power-eta6003-5v-ups/power-dev-eta6003-ups.kicad_sch

## KiCad design pcb-stackable-dev/power-eta6003-5v-ups/power-dev-eta6003-ups.kicad_sch (2024-09-13)

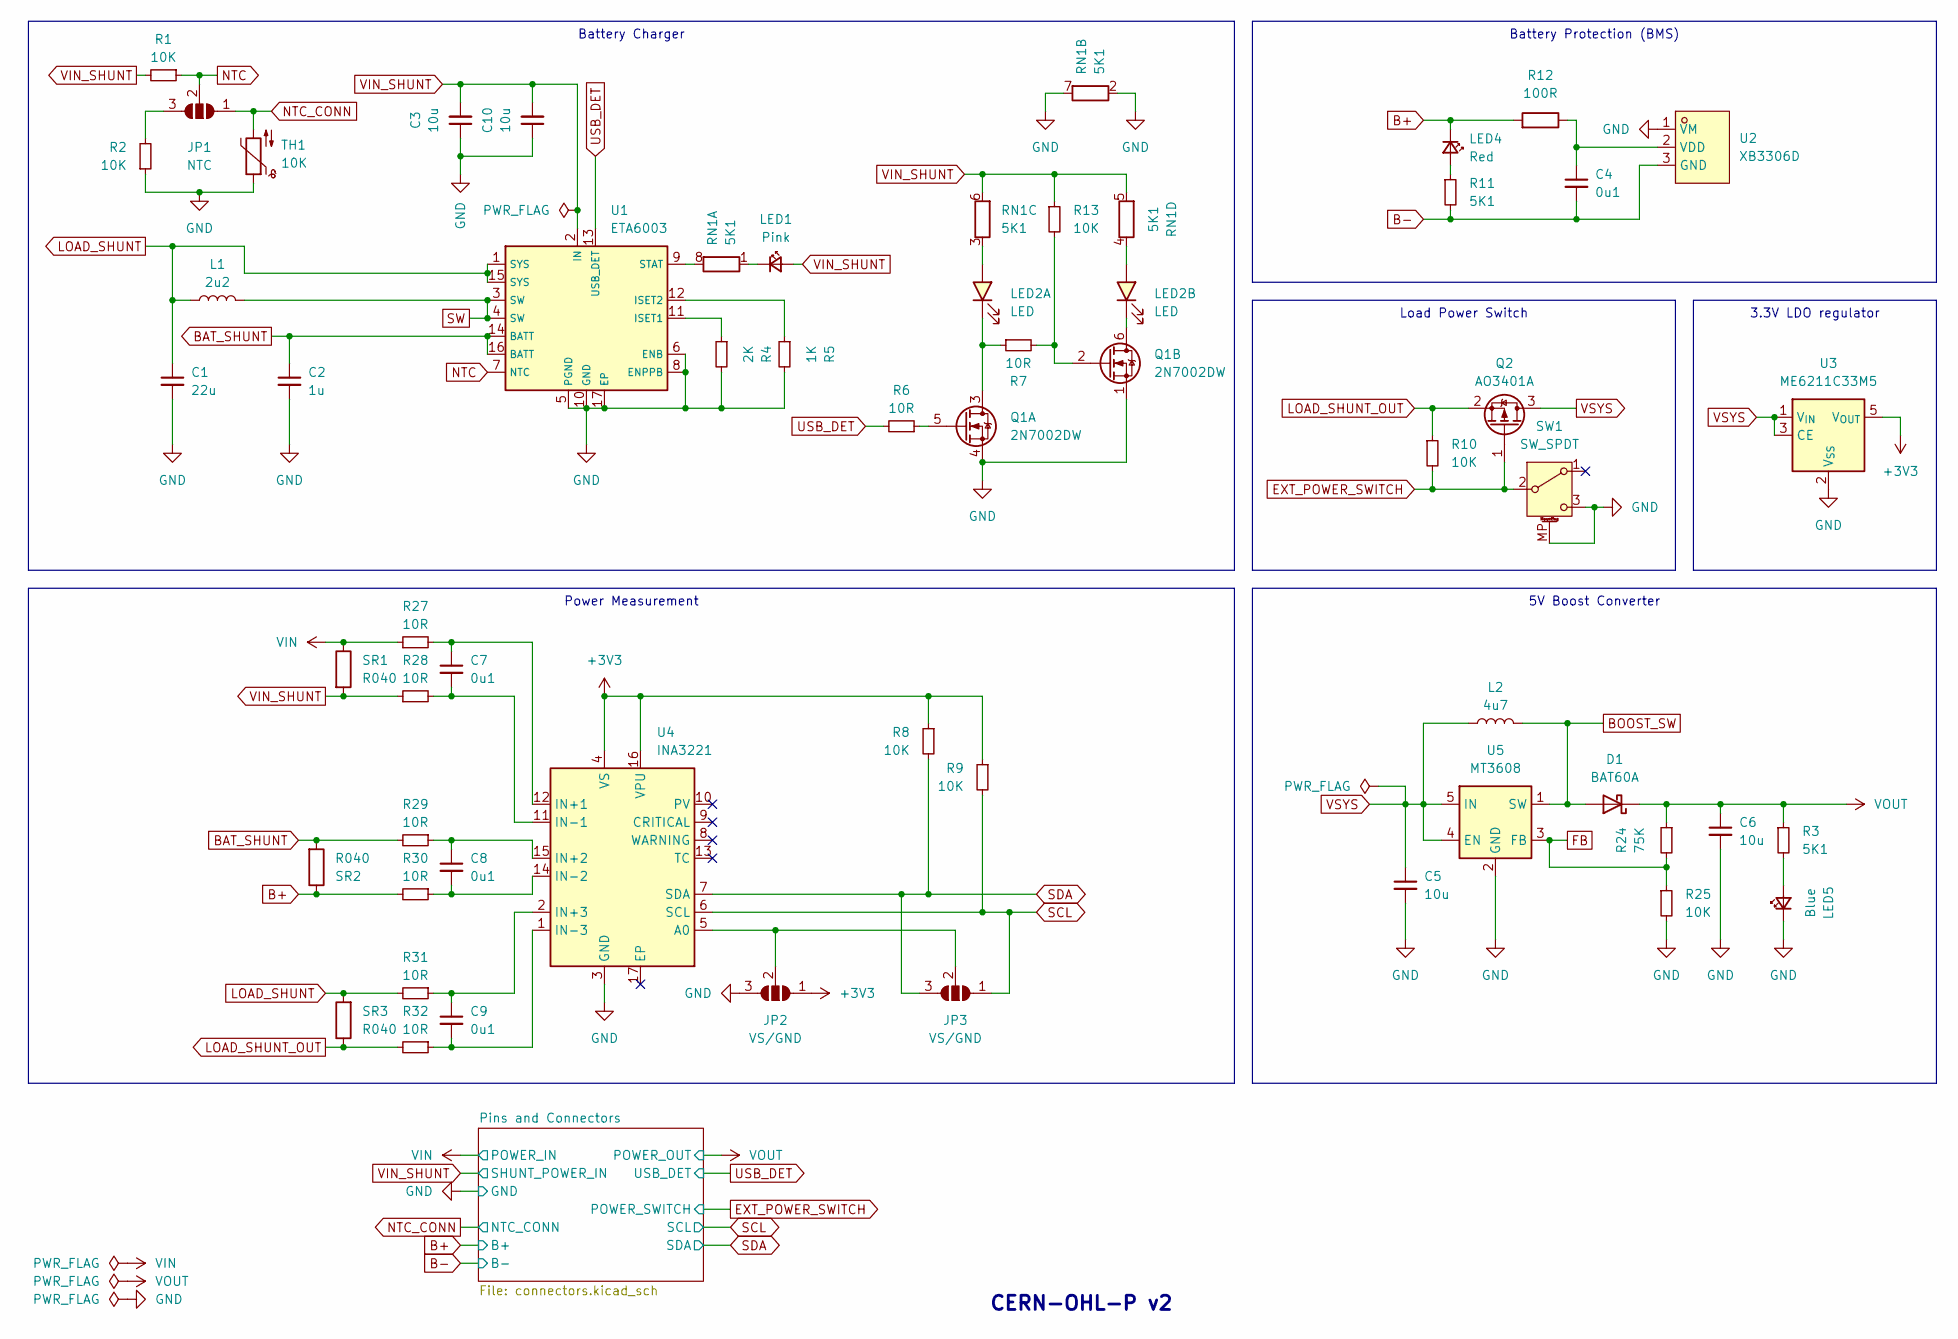
[picture p187: schematic power-dev-eta6003-ups.kicad_sch]

Parts:
C1: 22u; C_0805_2012Metric_Pad1.18x1.45mm_HandSolder; LCSC Part C45783
C2: 1u; C_0402_1005Metric_simple; LCSC Part C52923
C3: 10u; C_0805_2012Metric_Pad1.18x1.45mm_wide-center_HandSolder; LCSC Part C15850
C4, C7, C8, C9: 0u1; C_0402_1005Metric_simple; LCSC Part C1525
C5, C6: 10u; C_0603_1608Metric_Pad1.08x0.95mm_HandSolder; LCSC Part C19702
C10: 10u; C_0805_2012Metric_Pad1.18x1.45mm_HandSolder; LCSC Part C15850
D1: BAT60A; D_SOD-323_HandSoldering_simple; LCSC Part C7502695
JP1: NTC; SolderJumper-3_P1.3mm_Open_RoundedPad1.0x1.5mm
JP2, JP3: VS/GND; SolderJumper-3_P1.0mm_Open_RoundedPad_simple
L1: 2u2; L_1210_3225Metric_Pad1.42x2.65mm_HandSolder; LCSC Part C5832372
L2: 4u7; Inductor_Multi_7.0x6.6_1210; LCSC Part C5307631
LED1: Pink; LED_0603_1608Metric_Pad1.05x0.95mm_HandSolder_simple
LED2: LED; LED-ARRAY-SMD_4P-L2.0-W1.3-RD; LCSC Part C375547
LED4: Red; LED_0603_1608Metric_Pad1.05x0.95mm_HandSolder_simple; LCSC Part C2286
LED5: Blue; LED_0603_1608Metric_Pad1.05x0.95mm_HandSolder_simple
Q1: 2N7002DW; SOT-23-6_trimmed-pads_simple; LCSC Part C5190214
Q2: AO3401A; SOT-23_simple; LCSC Part C15127
R1, R2, R8, R9, R10, R13, R25: 10K; R_0402_1005Metric_simple; LCSC Part C25744
R3, R11: 5K1; R_0402_1005Metric_simple; LCSC Part C25905
R4: 2K; R_0603_1608Metric_Pad0.98x0.95mm_HandSolder; LCSC Part C22975
R5: 1K; R_0603_1608Metric_Pad0.98x0.95mm_HandSolder; LCSC Part C21190
R6, R7, R27, R28, R29, R30, R31, R32: 10R; R_0402_1005Metric_simple; LCSC Part C25077
R12: 100R; R_0402_1005Metric_simple; LCSC Part C25076
R24: 75K; R_0402_1005Metric_simple; LCSC Part C25798
RN1: 5K1; R_Array_Convex_4x0402; LCSC Part C2991336
SR1, SR2, SR3: R040; R_2512_6332Metric_Pad1.40x3.35mm_HandSolder; LCSC Part C2985725
SW1: SW_SPDT; SW-SMD_3P-P1.50_L2.7-W6.6; LCSC Part C319020
TH1: 10K; JST_SH_SM02B-SRSS-TB_1x02-1MP_P1.00mm_Horizontal
U1: ETA6003; ETA6003_QFN-16-1EP_3x3mm_P0.5mm_EP1.7x1.7mm_ThermalVias; LCSC Part C5455585
U2: XB3306D; SOT-23_simple; LCSC Part C2759992
U3: ME6211C33M5; SOT-23-5_simple; LCSC Part C82942
U4: INA3221; Texas_RGV0016A_VQFN-16-1EP_4x4mm_P0.65mm_EP2.1x2.1mm_Therma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; LCSC Part C181255
U5: MT3608; SOT-23-6_Handsoldering_simple; LCSC Part C84817

Connections:
+3V3: JP2.1 (A), R8.1, R9.1, U3.5 (V_{OUT}), U4.4 (VS), U4.16 (VPU)
B+: LED4.1 (K), R12.2, R30.2, SR2.1
B-: C4.2, R11.2, U2.3 (GND)
BAT_SHUNT: C2.1, R29.2, SR2.2, U1.14 (BATT), U1.16 (BATT)
BOOST_SW: D1.2 (A), L2.2, U5.1 (SW)
EXT_POWER_SWITCH: Q2.1 (G), R10.2, SW1.2 (B)
FB: R24.2, R25.1, U5.3 (FB)
GND: C1.2, C2.2, C3.1, C5.2, C6.2, C10.1, JP2.3 (B), LED5.1 (K), Q1.1 (S), Q1.4 (S), R2.1, R4.2, R5.2, R25.2, RN1.2 (R2.1), RN1.7 (R2.2), SW1.3 (C), SW1.MP (MountPin), TH1.1, U1.5 (PGND), U1.6 (ENB), U1.8 (ENPPB), U1.10 (GND), U1.17 (EP), U2.1 (VM), U3.2 (V_{SS}), U4.3 (GND), U5.2 (GND)
LOAD_SHUNT: C1.1, L1.1, R31.2, SR3.2, U1.1 (SYS), U1.15 (SYS)
LOAD_SHUNT_OUT: Q2.2 (S), R10.1, R32.2, SR3.1
NTC: JP1.2 (C), R1.1, U1.7 (NTC)
NTC_CONN: JP1.1 (A), TH1.2
unnamed: C4.1, R12.1, U2.2 (VDD)
unnamed: C7.1, R27.2, U4.12 (IN+1)
unnamed: C7.2, R28.2, U4.11 (IN-1)
unnamed: C8.1, R29.1, U4.15 (IN+2)
unnamed: C8.2, R30.1, U4.14 (IN-2)
unnamed: C9.1, R31.1, U4.2 (IN+3)
unnamed: C9.2, R32.1, U4.1 (IN-3)
unnamed: JP1.3 (B), R2.2
unnamed: JP2.2 (C), JP3.2 (C), U4.5 (A0)
unnamed: LED1.1 (K), RN1.1 (R1.1)
unnamed: LED2.1 (RED_A), RN1.3 (R3.1)
unnamed: LED2.2 (RED_K), Q1.3 (D), R7.1
unnamed: LED2.3 (BLUE_A), RN1.4 (R4.1)
unnamed: LED2.4 (BLUE_K), Q1.6 (D)
unnamed: LED4.2 (A), R11.1
unnamed: LED5.2 (A), R3.2
unnamed: Q1.2 (G), R7.2, R13.2
unnamed: Q1.5 (G), R6.1
unnamed: R4.1, U1.11 (ISET1)
unnamed: R5.1, U1.12 (ISET2)
unnamed: RN1.8 (R1.2), U1.9 (STAT)
SCL: JP3.1 (A), R9.2, U4.6 (SCL)
SDA: JP3.3 (B), R8.2, U4.7 (SDA)
SW: L1.2, U1.3 (SW), U1.4 (SW)
USB_DET: R6.2, U1.13 (USB_DET)
VIN: R27.1, SR1.1
VIN_SHUNT: C3.2, C10.2, LED1.2 (A), R1.2, R13.1, R28.1, RN1.5 (R4.2), RN1.6 (R3.2), SR1.2, U1.2 (IN)
VOUT: C6.1, D1.1 (K), R3.1, R24.1
VSYS: C5.1, L2.1, Q2.3 (D), U3.1 (V_{IN}), U3.3 (CE), U5.4 (EN), U5.5 (IN)

Notes on the sheet:
3.3V LDO regulator
5V Boost Converter
Battery Protection (BMS)
Battery Charger
Power Measurement
Load Power Switch
CERN-OHL-P v2
