smkent/pcb/pcb-stackable-dev/relay-module-5v-x2/relay-module-v2.kicad_sch

## KiCad design pcb-stackable-dev/relay-module-5v-x2/relay-module-v2.kicad_sch (2024-09-15)

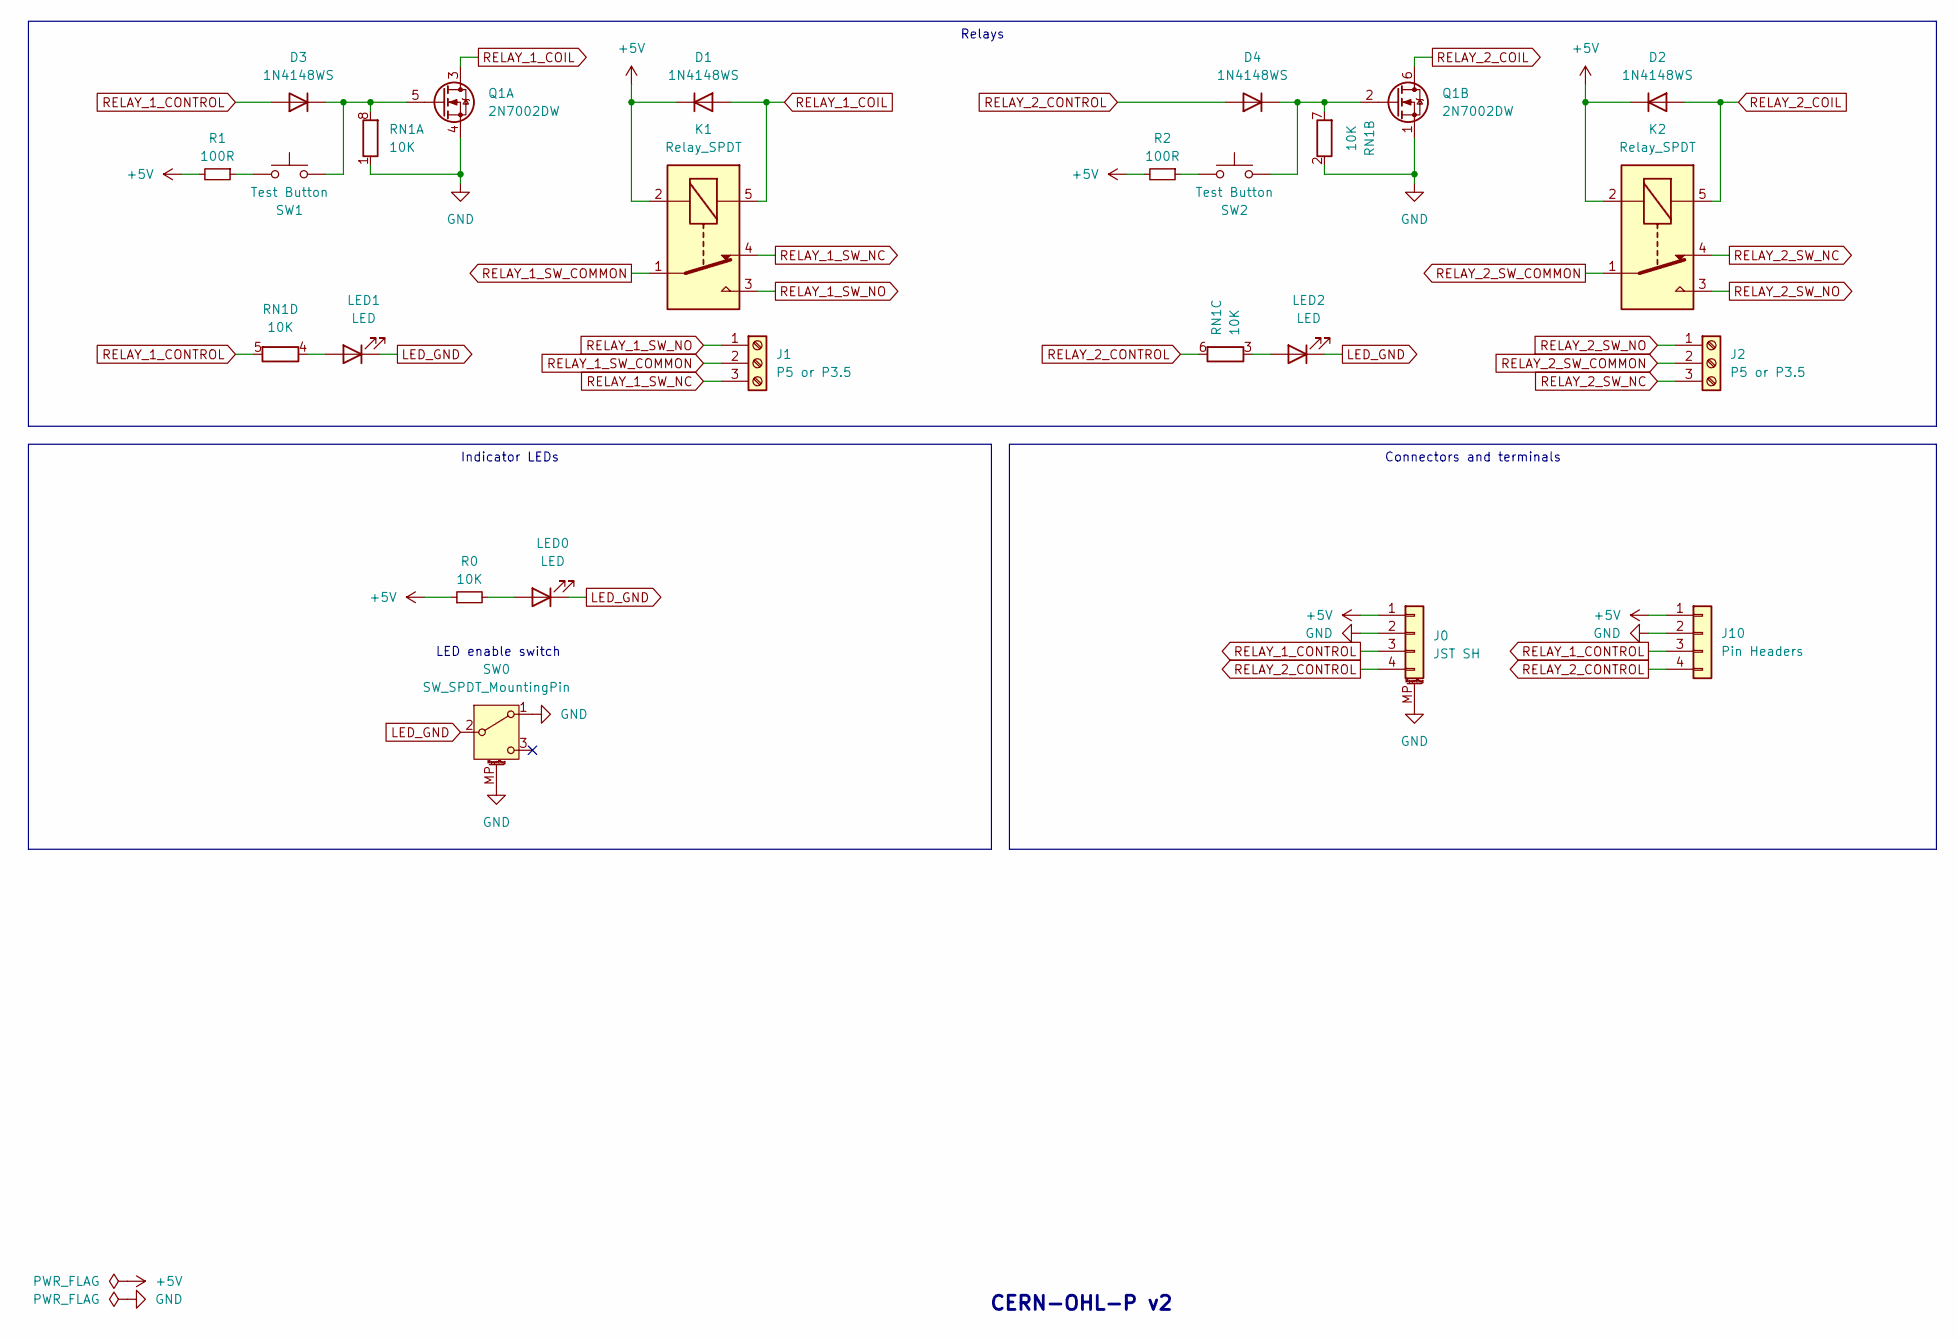
[picture p188: schematic relay-module-v2.kicad_sch]

Parts:
D1, D2, D3, D4: 1N4148WS; D_SOD-323_HandSoldering_simple
J0: JST SH; JST_SH_SM04B-SRSS-TB_1x04-1MP_P1.00mm_Horizontal
J1, J2: P5 or P3.5; Conn_Combo_TerminalBlock_P3.5-P5.08_1x03_pad2gnd
J10: Pin Headers; PinHeader_1x04_P2.54mm_Vertical_simple_pad2gnd
K1, K2: Relay_SPDT; Relay_SPDT_SANYOU_SRD_Series_Form_C
LED0, LED1, LED2: LED; LED_0805_2012Metric_Pad1.15x1.40mm_HandSolder_simple
Q1: 2N7002DW; SOT-23-6; LCSC Part C5190214
R0: 10K; R_0805_2012Metric_Pad1.20x1.40mm_HandSolder
R1, R2: 100R; R_0805_2012Metric_Pad1.20x1.40mm_HandSolder
RN1: 10K; R_Array_Convex_4x0603
SW0: SW_SPDT_MountingPin; SW-SMD_3P-P1.50_L2.7-W6.6
SW1, SW2: Test Button; SW-SMD_BZCN_TSA002A35XXX

Connections:
+5V: D1.1 (K), D2.1 (K), J0.1, J10.1, K1.2, K2.2, R0.1, R1.2, R2.2
GND: J0.2, J0.MP (MountPin), J10.2, Q1.1 (S), Q1.4 (S), RN1.1 (R1.1), RN1.2 (R2.1), SW0.1 (A), SW0.MP (MountPin)
LED_GND: LED0.1 (K), LED1.1 (K), LED2.1 (K), SW0.2 (B)
unnamed: D3.1 (K), Q1.5 (G), RN1.8 (R1.2), SW1.1
unnamed: D4.1 (K), Q1.2 (G), RN1.7 (R2.2), SW2.1
unnamed: LED0.2 (A), R0.2
unnamed: LED1.2 (A), RN1.4 (R4.1)
unnamed: LED2.2 (A), RN1.3 (R3.1)
unnamed: R1.1, SW1.2
unnamed: R2.1, SW2.2
RELAY_1_COIL: D1.2 (A), K1.5, Q1.3 (D)
RELAY_1_CONTROL: D3.2 (A), J0.3, J10.3, RN1.5 (R4.2)
RELAY_1_SW_COMMON: J1.2, K1.1
RELAY_1_SW_NC: J1.3, K1.4
RELAY_1_SW_NO: J1.1, K1.3
RELAY_2_COIL: D2.2 (A), K2.5, Q1.6 (D)
RELAY_2_CONTROL: D4.2 (A), J0.4, J10.4, RN1.6 (R3.2)
RELAY_2_SW_COMMON: J2.2, K2.1
RELAY_2_SW_NC: J2.3, K2.4
RELAY_2_SW_NO: J2.1, K2.3

Notes on the sheet:
Indicator LEDs
Relays
Connectors and terminals
CERN-OHL-P v2
LED enable switch
