smkent/pcb/dev/misc/gr6408/gr6408-dev.kicad_sch

## KiCad design dev/misc/gr6408/gr6408-dev.kicad_sch (2024-10-31)

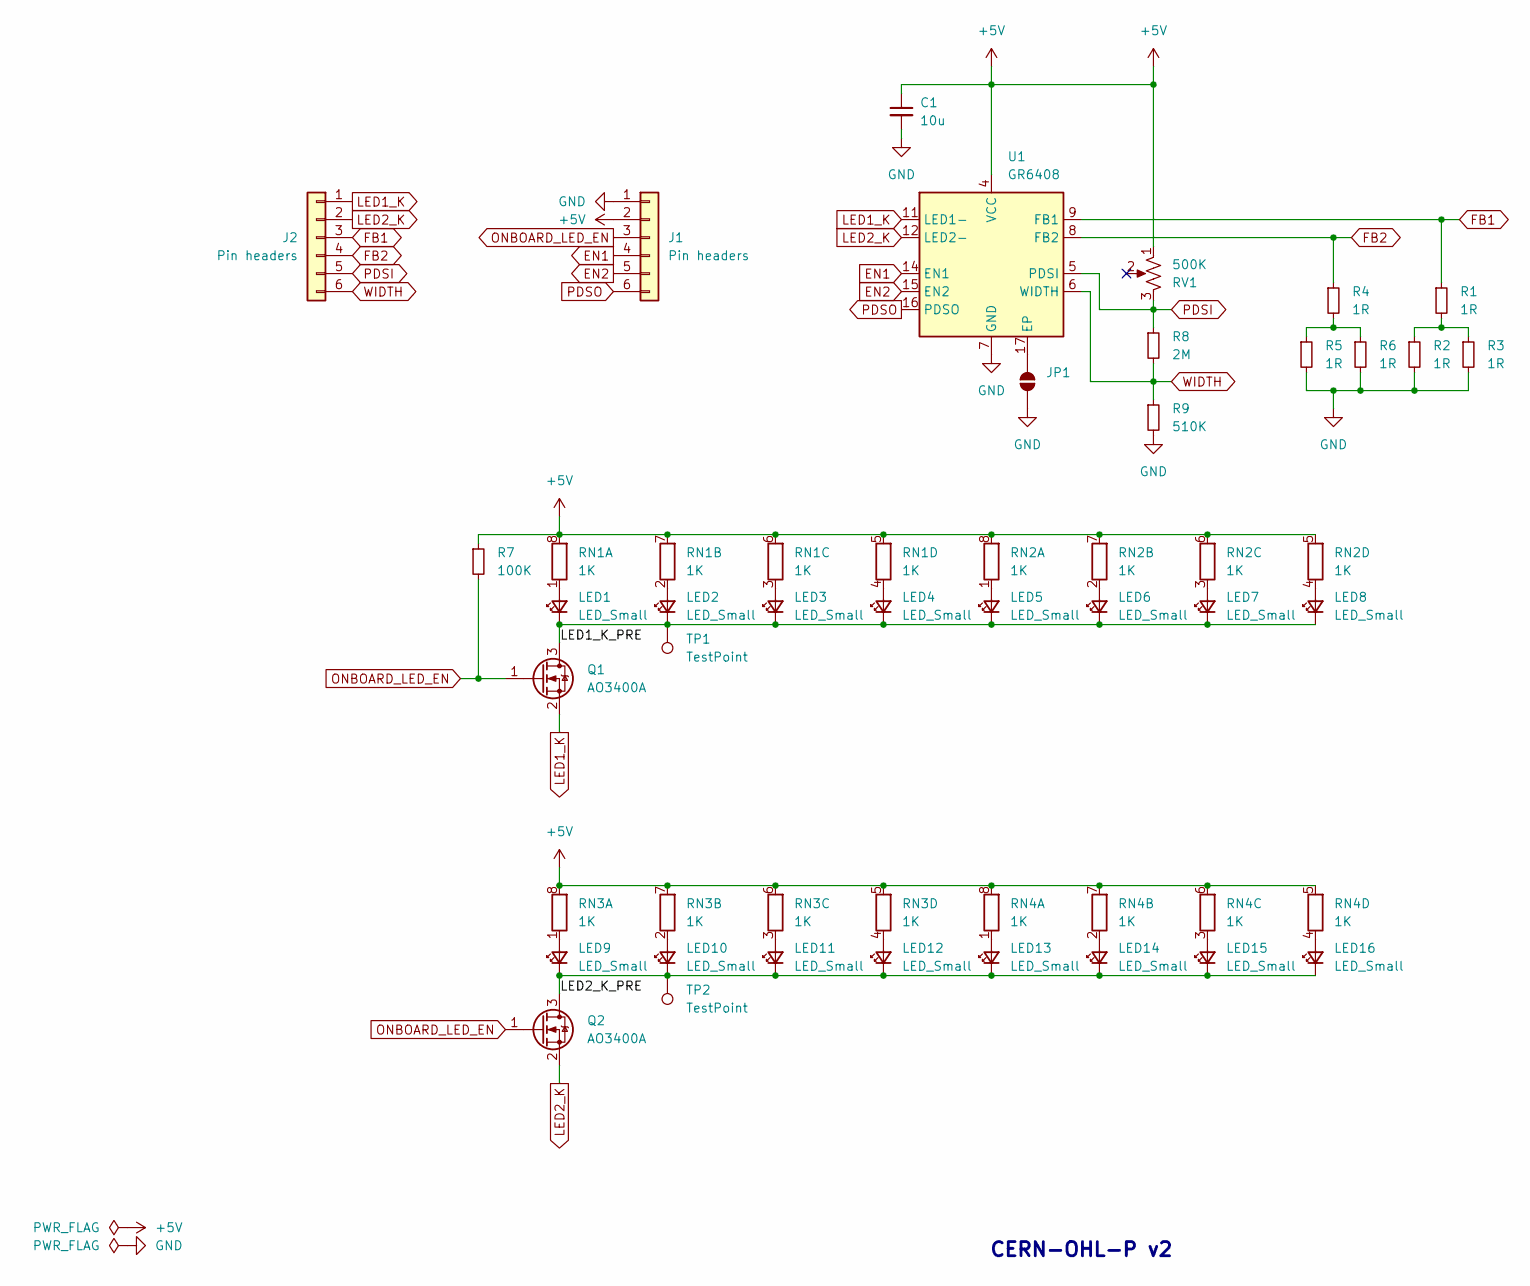
[picture p189: schematic gr6408-dev.kicad_sch]

Parts:
C1: 10u; C_0603_1608Metric
J1: Pin headers; PinHeader_1x06_P2.54mm_Vertical_simple_pad1gnd
J2: Pin headers; PinHeader_1x06_P2.54mm_Vertical_simple
JP1: SolderJumper_2_Open; SolderJumper-2_P1.3mm_Open_RoundedPad1.0x1.5mm
LED1, LED2, LED3, LED4, LED5, LED6, LED7, LED8, LED9, LED10, LED11, LED12, LED13, LED14, LED15, LED16: LED_Small; LED_0402_1005Metric
Q1, Q2: AO3400A; SOT-23
R1, R2, R3, R4, R5, R6: 1R; R_0603_1608Metric_simple
R7: 100K; R_0603_1608Metric_simple
R8: 2M; R_0603_1608Metric_simple
R9: 510K; R_0603_1608Metric_simple
RN1, RN2, RN3, RN4: 1K; R_Array_Convex_4x0603
RV1: 500K; RES-ADJ-SMD_VG039NCH
TP1, TP2: TestPoint; TestPoint_Pad_D1.0mm
U1: GR6408; QFN-16-1EP_4x4mm_P0.65mm_EP2.5x2.5mm; LCSC Part C27975231

Connections:
+5V: C1.1, J1.2, R7.1, RN1.5 (R4.2), RN1.6 (R3.2), RN1.7 (R2.2), RN1.8 (R1.2), RN2.5 (R4.2), RN2.6 (R3.2), RN2.7 (R2.2), RN2.8 (R1.2), RN3.5 (R4.2), RN3.6 (R3.2), RN3.7 (R2.2), RN3.8 (R1.2), RN4.5 (R4.2), RN4.6 (R3.2), RN4.7 (R2.2), RN4.8 (R1.2), RV1.1, U1.4 (VCC)
EN1: J1.4, U1.14 (EN1)
EN2: J1.5, U1.15 (EN2)
FB1: J2.3, R1.1, U1.9 (FB1)
FB2: J2.4, R4.1, U1.8 (FB2)
GND: C1.2, J1.1, JP1.1 (A), R2.2, R3.2, R5.2, R6.2, R9.2, U1.7 (GND)
LED1_K: J2.1, Q1.2 (S), U1.11 (LED1-)
LED1_K_PRE: LED1.1 (K), LED2.1 (K), LED3.1 (K), LED4.1 (K), LED5.1 (K), LED6.1 (K), LED7.1 (K), LED8.1 (K), Q1.3 (D), TP1.1
LED2_K: J2.2, Q2.2 (S), U1.12 (LED2-)
LED2_K_PRE: LED9.1 (K), LED10.1 (K), LED11.1 (K), LED12.1 (K), LED13.1 (K), LED14.1 (K), LED15.1 (K), LED16.1 (K), Q2.3 (D), TP2.1
unnamed: JP1.2 (B), U1.17 (EP)
unnamed: LED1.2 (A), RN1.1 (R1.1)
unnamed: LED2.2 (A), RN1.2 (R2.1)
unnamed: LED3.2 (A), RN1.3 (R3.1)
unnamed: LED4.2 (A), RN1.4 (R4.1)
unnamed: LED5.2 (A), RN2.1 (R1.1)
unnamed: LED6.2 (A), RN2.2 (R2.1)
unnamed: LED7.2 (A), RN2.3 (R3.1)
unnamed: LED8.2 (A), RN2.4 (R4.1)
unnamed: LED9.2 (A), RN3.1 (R1.1)
unnamed: LED10.2 (A), RN3.2 (R2.1)
unnamed: LED11.2 (A), RN3.3 (R3.1)
unnamed: LED12.2 (A), RN3.4 (R4.1)
unnamed: LED13.2 (A), RN4.1 (R1.1)
unnamed: LED14.2 (A), RN4.2 (R2.1)
unnamed: LED15.2 (A), RN4.3 (R3.1)
unnamed: LED16.2 (A), RN4.4 (R4.1)
unnamed: R1.2, R2.1, R3.1
unnamed: R4.2, R5.1, R6.1
ONBOARD_LED_EN: J1.3, Q1.1 (G), Q2.1 (G), R7.2
PDSI: J2.5, R8.1, RV1.3, U1.5 (PDSI)
PDSO: J1.6, U1.16 (PDSO)
WIDTH: J2.6, R8.2, R9.1, U1.6 (WIDTH)

Notes on the sheet:
CERN-OHL-P v2
