smkent/pcb/dev/misc/relay-module-5v/relay-module-5v.kicad_sch

## KiCad design dev/misc/relay-module-5v/relay-module-5v.kicad_sch (2024-08-27)

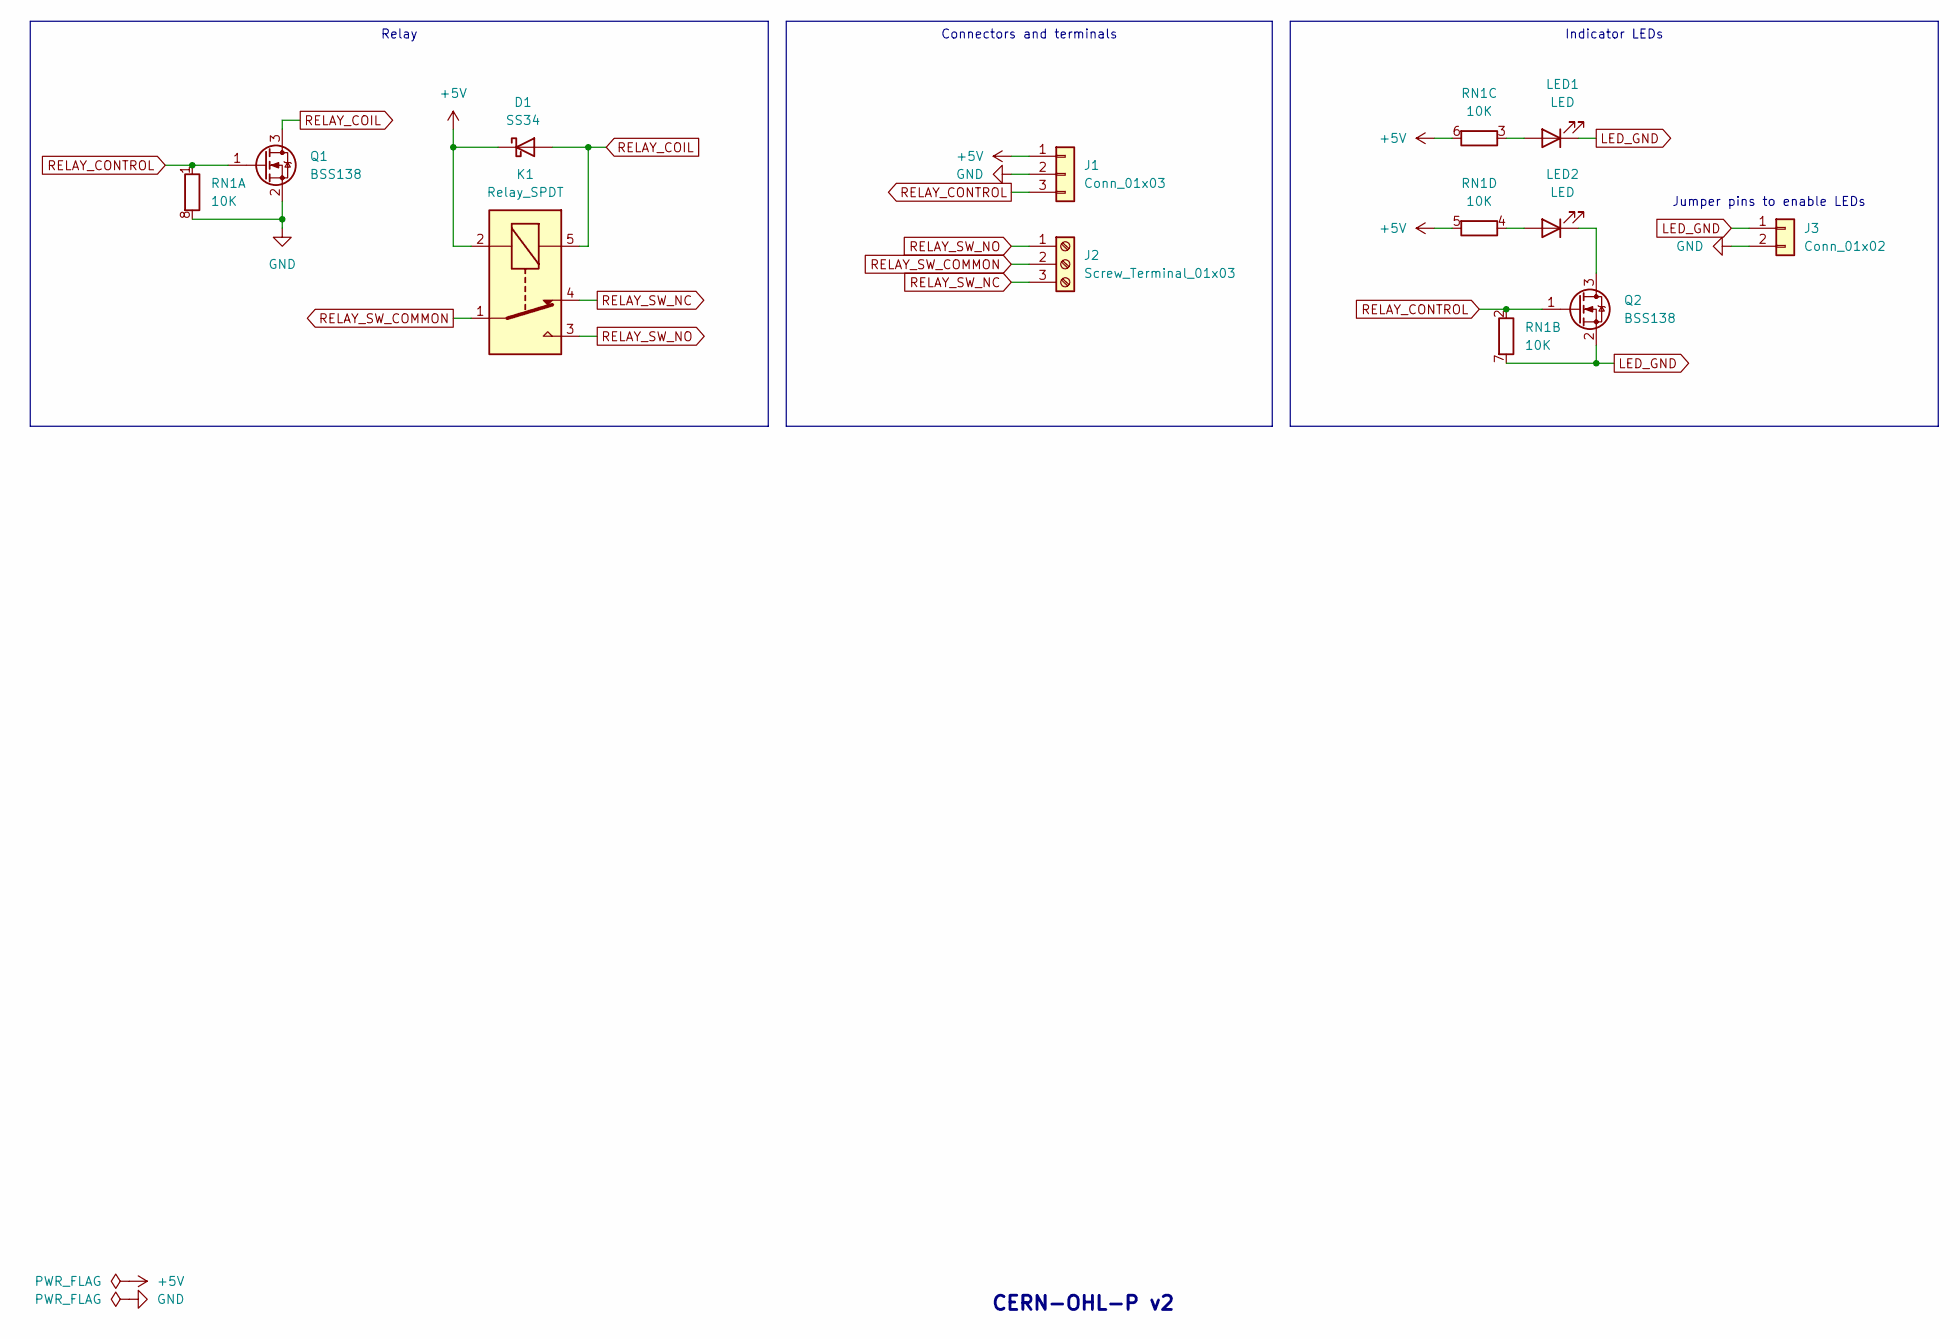
[picture p190: schematic relay-module-5v.kicad_sch]

Parts:
D1: SS34; D_SMA_simple
J1: Conn_01x03; JST_XH_S3B-XH_1x03_P2.50mm_Horizontal_pad2gnd
J2: Screw_Terminal_01x03; TerminalBlock_Phoenix_MKDS-1,5-3_1x03_P5.00mm_Horizontal_si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
J3: Conn_01x02; PinHeader_1x02_P2.54mm_Vertical_simple
K1: Relay_SPDT; Relay_SPDT_SANYOU_SRD_Series_Form_C
LED1, LED2: LED; LED_0805_2012Metric_Pad1.15x1.40mm_HandSolder_simple
Q1, Q2: BSS138; SOT-23
RN1: 10K; R_Array_Convex_4x0603

Connections:
+5V: D1.1 (K), J1.1, K1.2, RN1.5 (R4.2), RN1.6 (R3.2)
GND: J1.2, J3.2, Q1.2 (S), RN1.8 (R1.2)
LED_GND: J3.1, LED1.1 (K), Q2.2 (S), RN1.7 (R2.2)
unnamed: LED1.2 (A), RN1.3 (R3.1)
unnamed: LED2.1 (K), Q2.3 (D)
unnamed: LED2.2 (A), RN1.4 (R4.1)
RELAY_COIL: D1.2 (A), K1.5, Q1.3 (D)
RELAY_CONTROL: J1.3, Q1.1 (G), Q2.1 (G), RN1.1 (R1.1), RN1.2 (R2.1)
RELAY_SW_COMMON: J2.2, K1.1
RELAY_SW_NC: J2.3, K1.4
RELAY_SW_NO: J2.1, K1.3

Notes on the sheet:
Indicator LEDs
Relay
Connectors and terminals
CERN-OHL-P v2
Jumper pins to enable LEDs
