smkent/pcb/dev/power/battery-eta9740/battery-eta9740.kicad_sch

## KiCad design dev/power/battery-eta9740/battery-eta9740.kicad_sch (2024-11-30)

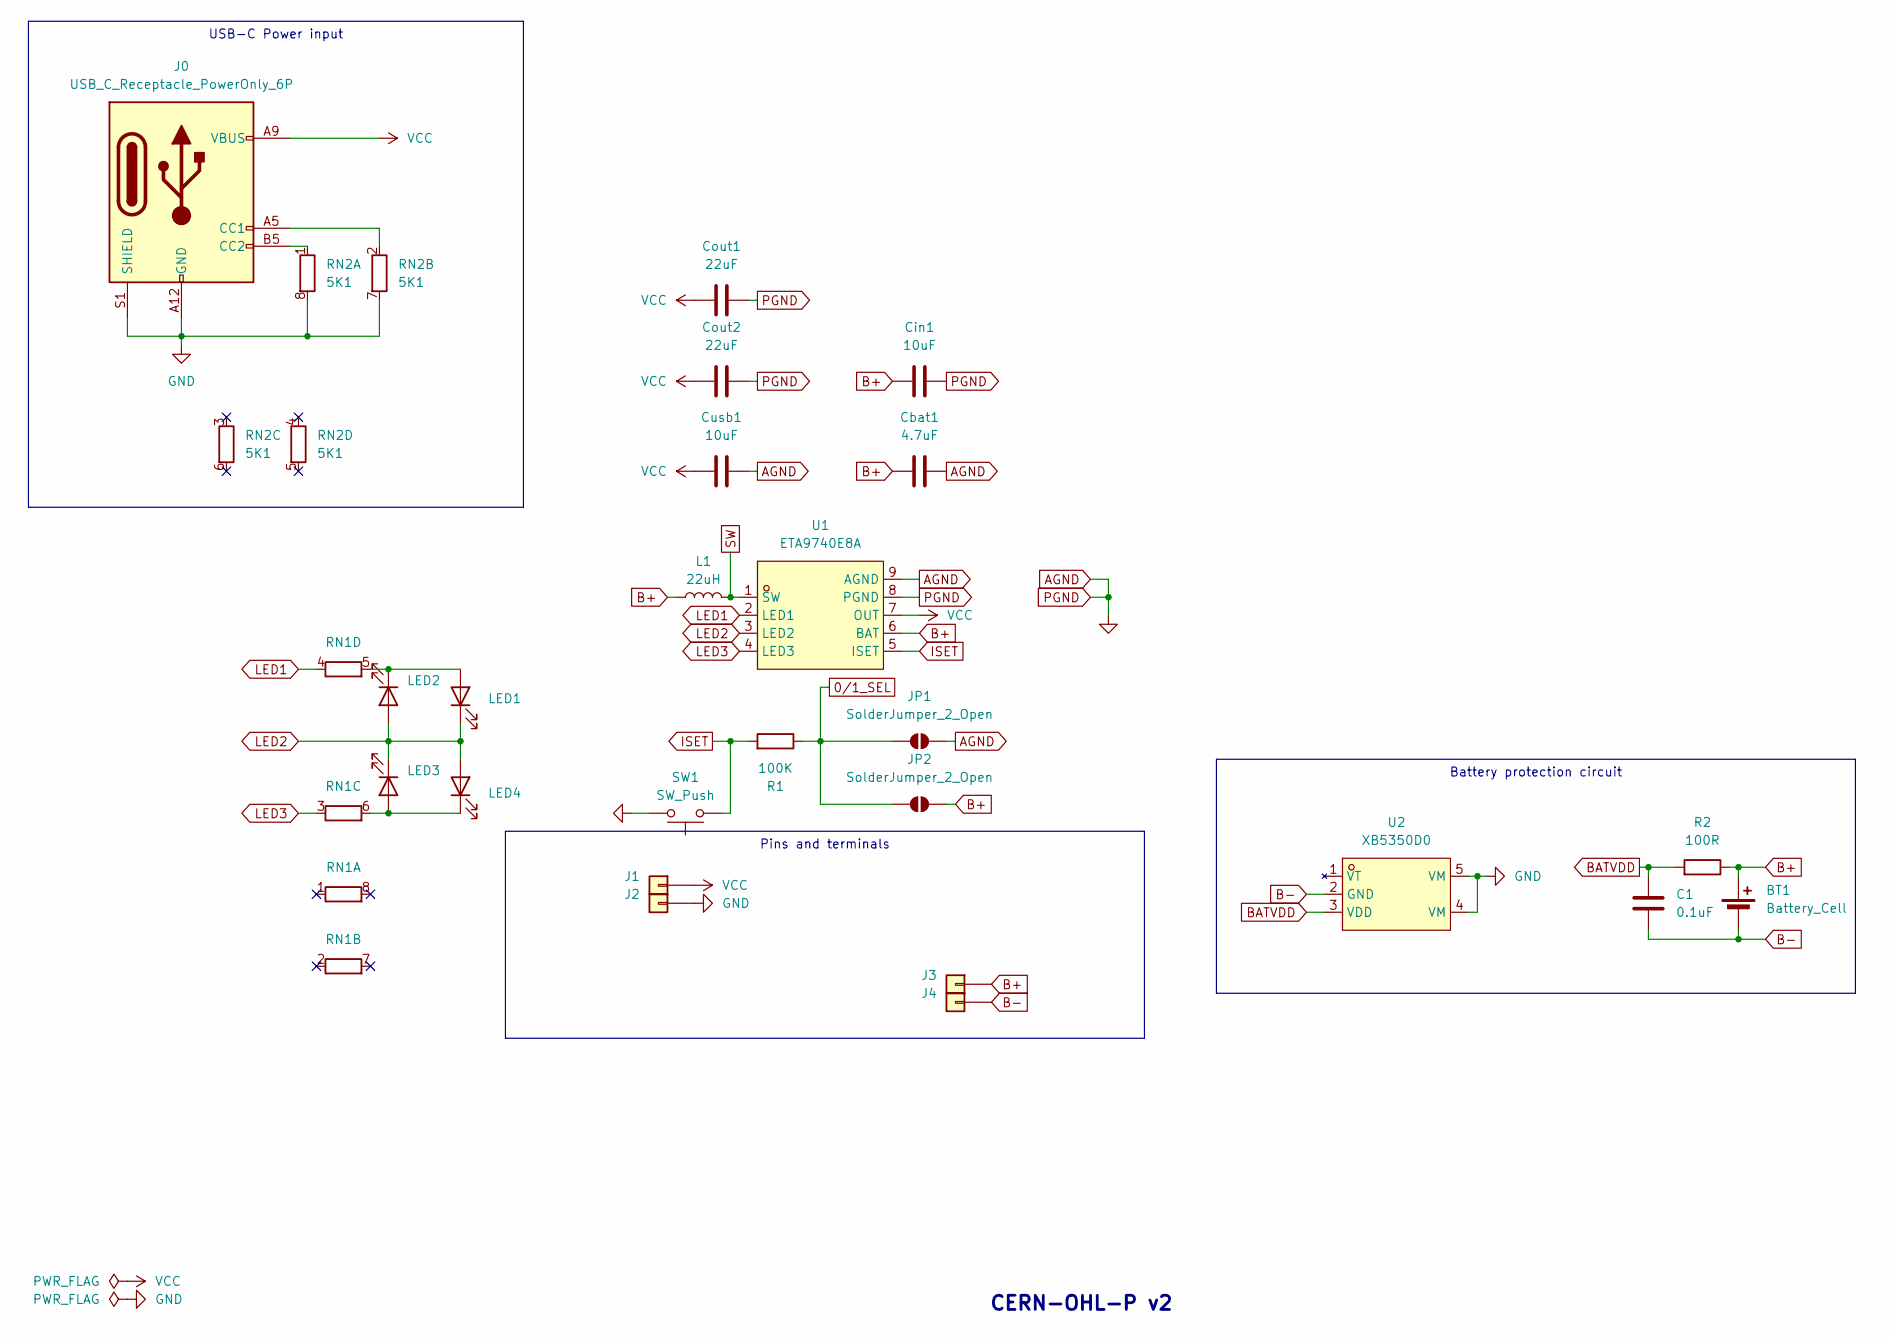
[picture p191: schematic battery-eta9740.kicad_sch]

Parts:
BT1: Battery_Cell; JST_XH_B2B-XH-A_1x02_P2.50mm_Vertical_simple_pad2gnd
C1: 0.1uF; C_0805_2012Metric_Pad1.18x1.45mm_HandSolder; LCSC Part C1525
Cbat1: 4.7uF; C_0805_2012Metric_Pad1.18x1.45mm_HandSolder
Cin1: 10uF; C_0805_2012Metric_Pad1.18x1.45mm_HandSolder
Cout1, Cout2: 22uF; C_0805_2012Metric_Pad1.18x1.45mm_HandSolder
Cusb1: 10uF; C_0805_2012Metric_Pad1.18x1.45mm_HandSolder
J0: USB_C_Receptacle_PowerOnly_6P; USB_C_Receptacle_GCT_USB4125-xx-x_6P_TopMnt_Horizontal_hand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
J1, J3: Conn_01x01; PinHeader_1x01_P2.54mm_simple
J2, J4: Conn_01x01; PinHeader_1x01_P2.54mm_simple_square
JP1, JP2: SolderJumper_2_Open; SolderJumper-2_P1.3mm_Open_RoundedPad1.0x1.5mm
L1: 22uH; Inductor_Multi_7.0x6.6_plus; LCSC Part C5832376
LED1, LED2, LED3, LED4: LED_0805_2012Metric_Pad1.15x1.40mm_HandSolder_simple
R1: 100K; R_0805_2012Metric_Pad1.20x1.40mm_HandSolder; LCSC Part C17379
R2: 100R; R_0805_2012Metric_Pad1.20x1.40mm_HandSolder
RN1: R_Pack04_Split; R_Array_Convex_4x0603
RN2: 5K1; R_Array_Convex_4x0603
SW1: SW_Push; PinHeader_1x02_P2.54mm_Vertical_simple_pad2gnd
U1: ETA9740E8A; SOIC-8-1EP_3.9x4.9mm_P1.27mm_EP2.41x3.3mm_ThermalVias_Custo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; LCSC Part C7465512
U2: XB5350D0; SOT-23-5_simple; JLCPCB_CORRECTION 0; 0; 180

Connections:
0/1_SEL: JP1.2 (B), JP2.1 (A), R1.1
AGND: Cbat1.1, Cin1.1, Cout1.2, Cout2.2, Cusb1.2, J0.A12 (GND), J0.B12 (GND), J0.S1 (SHIELD), J2.1, JP1.1 (A), RN2.7 (R2.2), RN2.8 (R1.2), SW1.2, U1.8 (PGND), U1.9 (AGND), U2.4 (VM), U2.5 (VM)
B+: BT1.1 (+), Cbat1.2, Cin1.2, J3.1, JP2.2 (B), L1.1, R2.1, U1.6 (BAT)
B-: BT1.2 (-), C1.1, J4.1, U2.2 (GND)
BATVDD: C1.2, R2.2, U2.3 (VDD)
ISET: R1.2, SW1.1, U1.5 (ISET)
LED1: RN1.4 (R4.1), U1.2 (LED1)
LED2: LED1.1 (K), LED2.2 (A), LED3.1 (K), LED4.2 (A), U1.3 (LED2)
LED3: RN1.3 (R3.1), U1.4 (LED3)
unnamed: J0.A5 (CC1), RN2.2 (R2.1)
unnamed: J0.B5 (CC2), RN2.1 (R1.1)
unnamed: LED1.2 (A), LED2.1 (K), RN1.5 (R4.2)
unnamed: LED3.2 (A), LED4.1 (K), RN1.6 (R3.2)
SW: L1.2, U1.1 (SW)
VCC: Cout1.1, Cout2.1, Cusb1.1, J0.A9 (VBUS), J0.B9 (VBUS), J1.1, U1.7 (OUT)

Notes on the sheet:
Pins and terminals
USB-C Power input
Battery protection circuit
CERN-OHL-P v2
