smkent/pcb/dev/power/battery-tp5400/battery-tp5400.kicad_sch

## KiCad design dev/power/battery-tp5400/battery-tp5400.kicad_sch (2024-11-30)

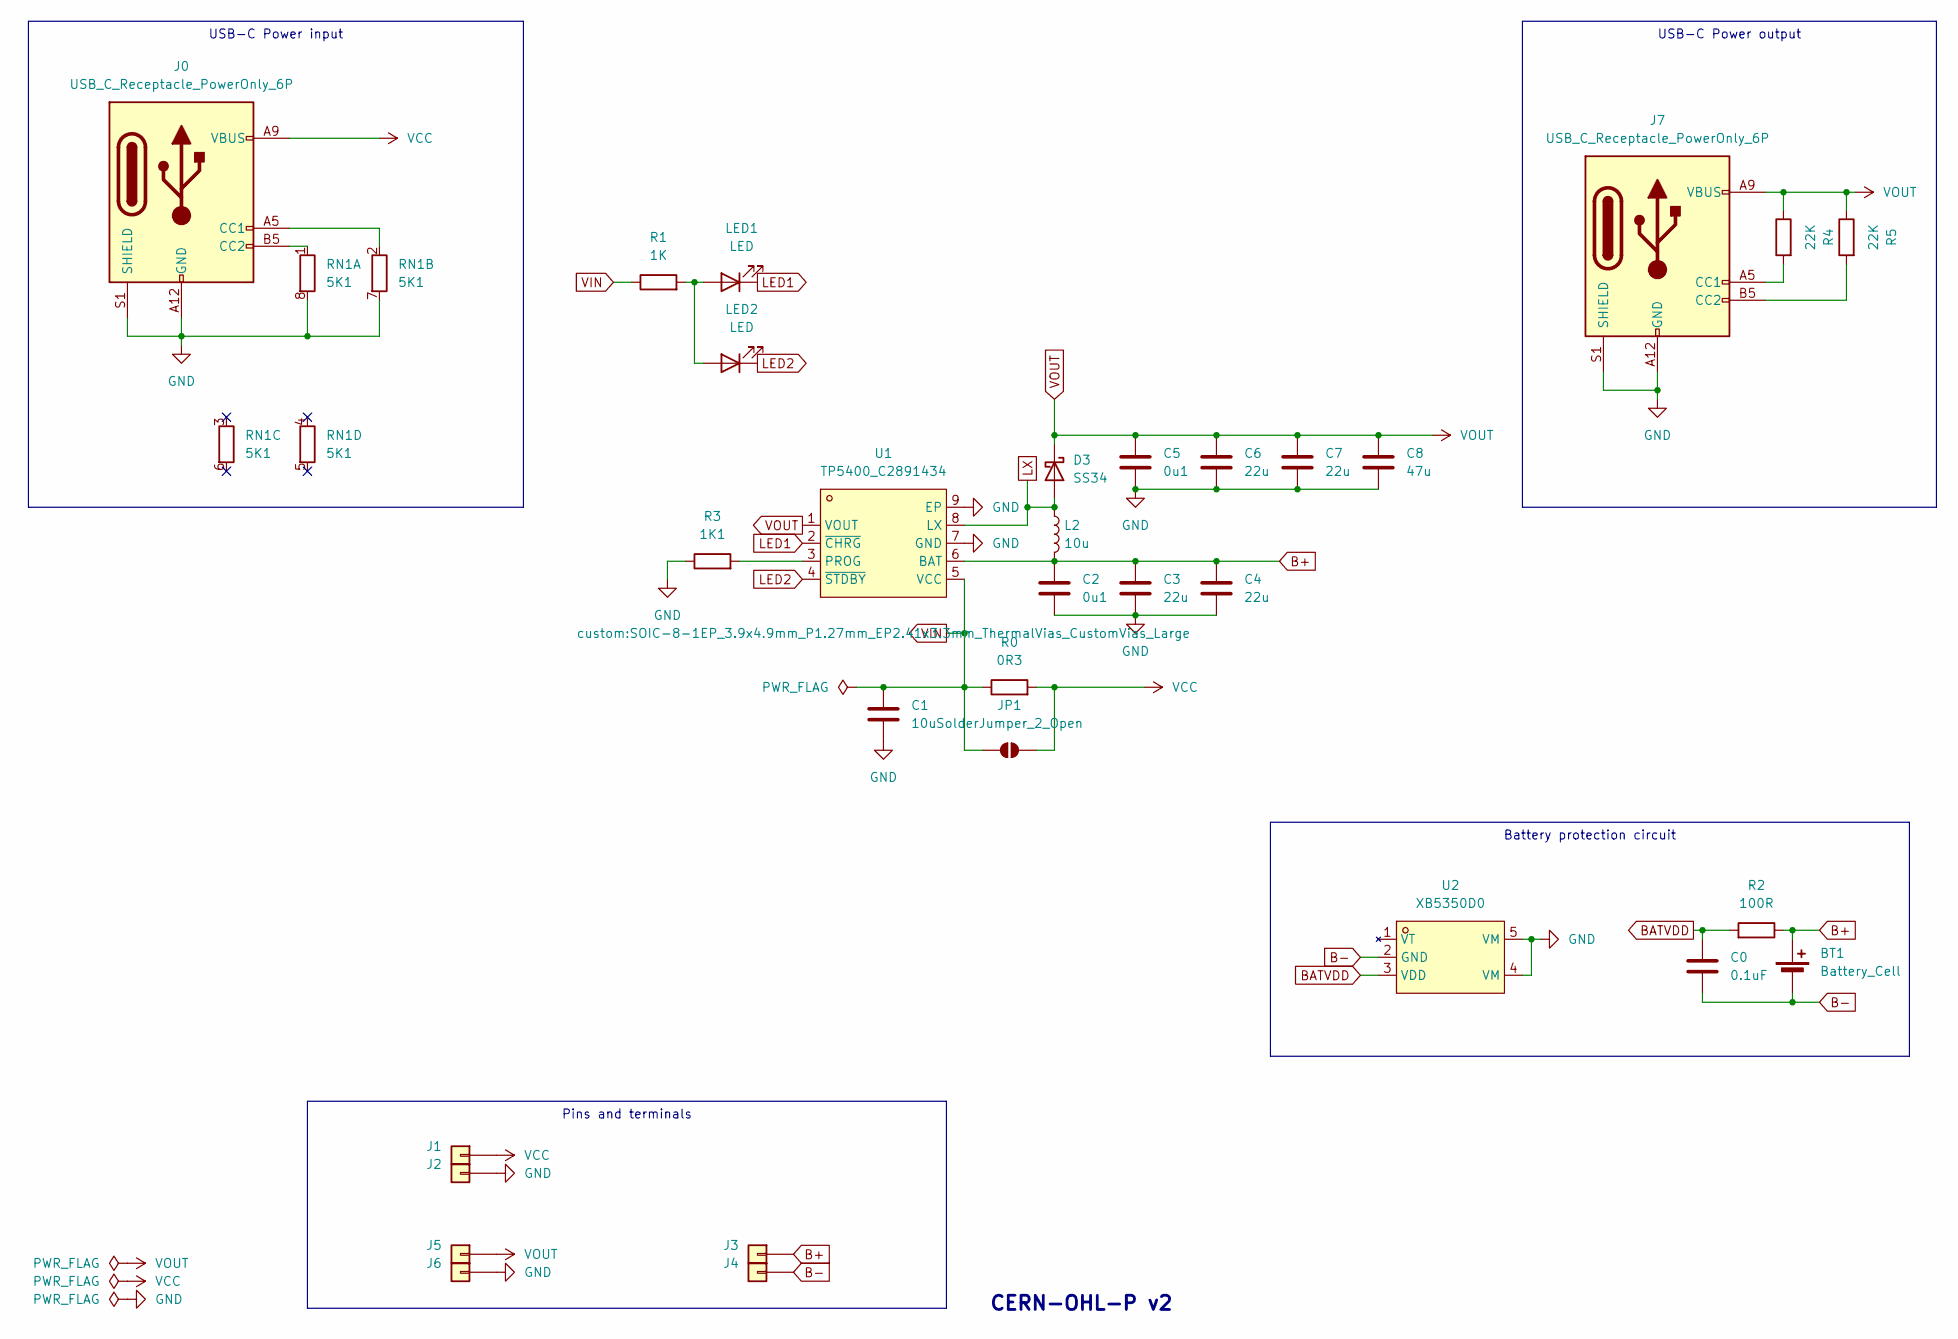
[picture p192: schematic battery-tp5400.kicad_sch]

Parts:
BT1: Battery_Cell; JST_XH_B2B-XH-A_1x02_P2.50mm_Vertical_simple_pad2gnd
C0: 0.1uF; C_0805_2012Metric_Pad1.18x1.45mm_HandSolder; LCSC Part C1525
C1: 10u; C_0805_2012Metric_Pad1.18x1.45mm_HandSolder
C2, C5: 0u1; C_0805_2012Metric_Pad1.18x1.45mm_HandSolder
C3, C4, C6, C7: 22u; C_1206_3216Metric_Pad1.33x1.80mm_HandSolder
C8: 47u; C_1206_3216Metric_Pad1.33x1.80mm_HandSolder
D3: SS34; D_SMA
J0, J7: USB_C_Receptacle_PowerOnly_6P; USB_C_Receptacle_GCT_USB4125-xx-x_6P_TopMnt_Horizontal_hand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
J1, J3, J5: Conn_01x01; PinHeader_1x01_P2.54mm_simple
J2, J4, J6: Conn_01x01; PinHeader_1x01_P2.54mm_simple_square
JP1: SolderJumper_2_Open; SolderJumper-2_P1.3mm_Open_RoundedPad1.0x1.5mm
L2: 10u; Inductor_Multi_7.0x6.6_plus
LED1, LED2: LED; LED_0805_2012Metric_Pad1.15x1.40mm_HandSolder_simple
R0: 0R3; R_0805_2012Metric_Pad1.20x1.40mm_HandSolder
R1: 1K; R_0805_2012Metric_Pad1.20x1.40mm_HandSolder
R2: 100R; R_0805_2012Metric_Pad1.20x1.40mm_HandSolder
R3: 1K1; R_0805_2012Metric_Pad1.20x1.40mm_HandSolder
R4: 22K; R_0805_2012Metric_Pad1.20x1.40mm_HandSolder
R5: 22K; R_0805_2012Metric_Pad1.20x1.40mm_HandSolder; LCSC Part C25768
RN1: 5K1; R_Array_Convex_4x0603
U1: TP5400_C2891434; SOIC-8-1EP_3.9x4.9mm_P1.27mm_EP2.41x3.3mm_ThermalVias_Custo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; LCSC Part C2891434
U2: XB5350D0; SOT-23-5_simple; JLCPCB_CORRECTION 0; 0; 180

Connections:
B+: BT1.1 (+), C2.2, C3.2, C4.2, J3.1, L2.2, R2.1, U1.6 (BAT)
B-: BT1.2 (-), C0.1, J4.1, U2.2 (GND)
BATVDD: C0.2, R2.2, U2.3 (VDD)
GND: C1.1, C2.1, C3.1, C4.1, C5.1, C6.1, C7.1, C8.1, J0.A12 (GND), J0.B12 (GND), J0.S1 (SHIELD), J2.1, J6.1, J7.A12 (GND), J7.B12 (GND), J7.S1 (SHIELD), R3.1, RN1.7 (R2.2), RN1.8 (R1.2), U1.7 (GND), U1.9 (EP), U2.4 (VM), U2.5 (VM)
LED1: LED1.1 (K), U1.2 (~CHRG)
LED2: LED2.1 (K), U1.4 (~STDBY)
LX: D3.2 (A), L2.1, U1.8 (LX)
unnamed: J0.A5 (CC1), RN1.2 (R2.1)
unnamed: J0.B5 (CC2), RN1.1 (R1.1)
unnamed: J7.A5 (CC1), R4.2
unnamed: J7.B5 (CC2), R5.2
unnamed: LED1.2 (A), LED2.2 (A), R1.2
unnamed: R3.2, U1.3 (PROG)
VCC: J0.A9 (VBUS), J0.B9 (VBUS), J1.1, JP1.2 (B), R0.2
VIN: C1.2, JP1.1 (A), R0.1, R1.1, U1.5 (VCC)
VOUT: C5.2, C6.2, C7.2, C8.2, D3.1 (K), J5.1, J7.A9 (VBUS), J7.B9 (VBUS), R4.1, R5.1, U1.1 (VOUT)

Notes on the sheet:
USB-C Power output
Pins and terminals
USB-C Power input
Battery protection circuit
CERN-OHL-P v2
