smkent/pcb/dev/power/boost-mt3608/boost-mt3608.kicad_sch

## KiCad design dev/power/boost-mt3608/boost-mt3608.kicad_sch (2024-05-30)

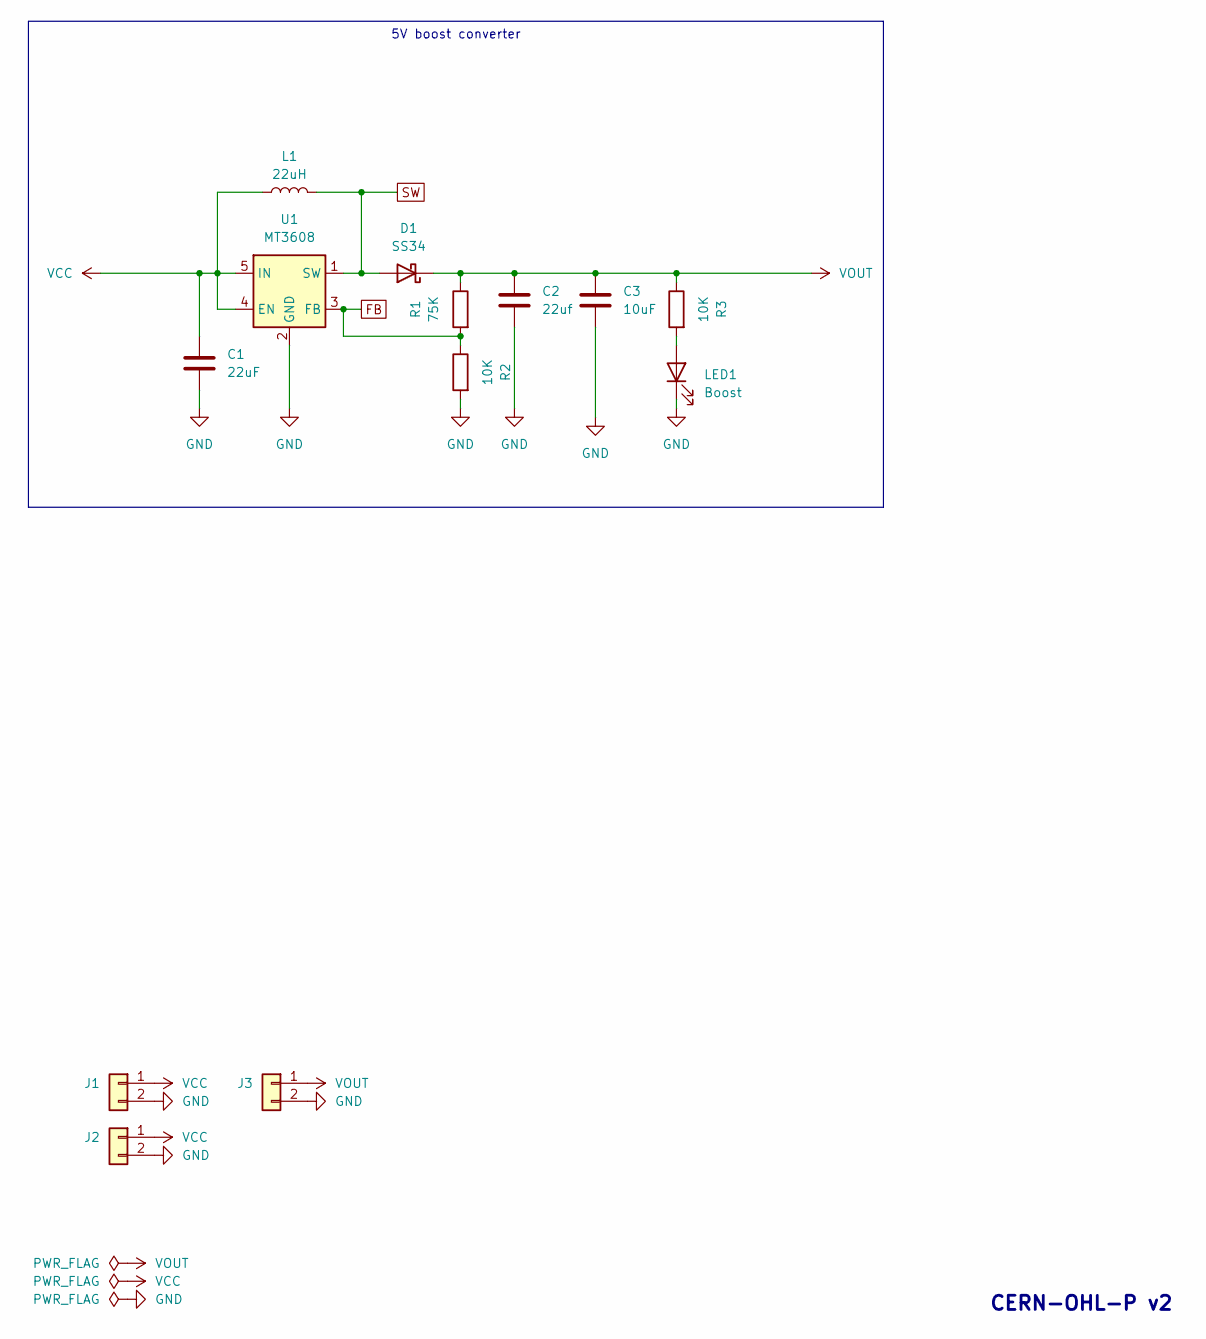
[picture p193: schematic boost-mt3608.kicad_sch]

Parts:
C1: 22uF; C_1206_3216Metric_Pad1.33x1.80mm_HandSolder; LCSC Part C12891
C2: 22uf; C_1206_3216Metric_Pad1.33x1.80mm_HandSolder; LCSC Part C12891
C3: 10uF; C_0805_2012Metric_Pad1.18x1.45mm_HandSolder; LCSC Part C15850
D1: SS34; D_SMA_simple; LCSC Part C8678
J1, J2, J3: Conn_01x02; PinHeader_1x02_P2.54mm_Vertical_simple_pad2gnd
L1: 22uH; Inductor_Multi_5.2x5.7_2x2.5; LCSC Part C5832376
LED1: Boost; LED_0805_2012Metric_Pad1.15x1.40mm_HandSolder_simple
R1: 75K; R_0805_2012Metric_Pad1.20x1.40mm_HandSolder
R2, R3: 10K; R_0805_2012Metric_Pad1.20x1.40mm_HandSolder
U1: MT3608; SOT-23-6; LCSC Part C84817

Connections:
FB: R1.2, R2.1, U1.3 (FB)
GND: C1.2, C2.2, C3.2, J1.2, J2.2, J3.2, LED1.1 (K), R2.2, U1.2 (GND)
unnamed: LED1.2 (A), R3.2
SW: D1.2 (A), L1.2, U1.1 (SW)
VCC: C1.1, J1.1, J2.1, L1.1, U1.4 (EN), U1.5 (IN)
VOUT: C2.1, C3.1, D1.1 (K), J3.1, R1.1, R3.1

Notes on the sheet:
5V boost converter
CERN-OHL-P v2
