smkent/pcb/dev/power/buck-tps54202-compact/buck-tps54202-compact.kicad_sch

## KiCad design dev/power/buck-tps54202-compact/buck-tps54202-compact.kicad_sch (2024-11-30)

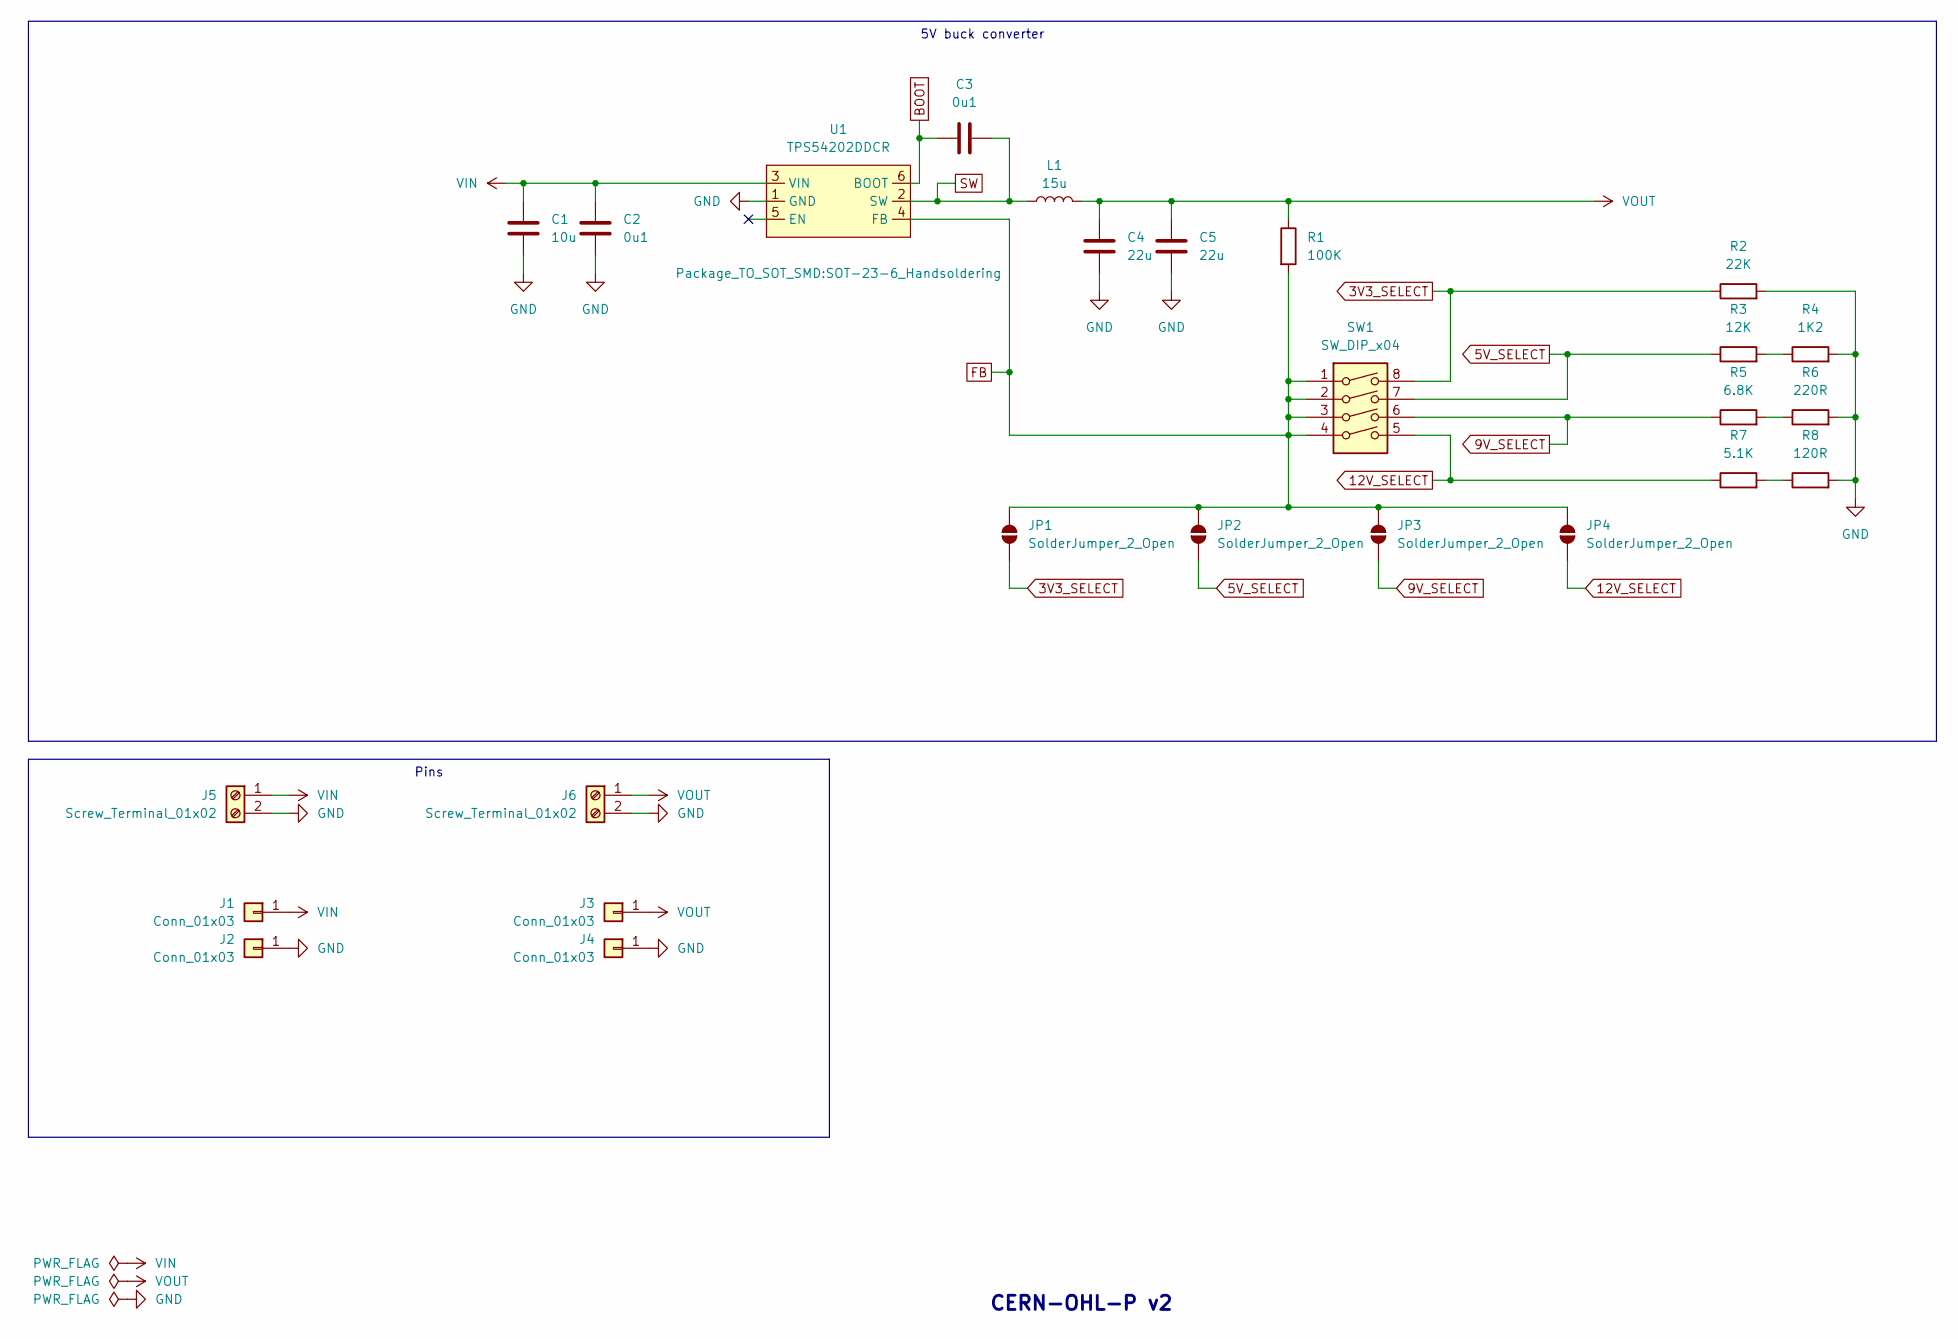
[picture p194: schematic buck-tps54202-compact.kicad_sch]

Parts:
C1: 10u; C_0805_2012Metric_Pad1.18x1.45mm_HandSolder; LCSC Part C440198
C2, C3: 0u1; C_0402_1005Metric; LCSC Part C307331
C4, C5: 22u; C_0805_2012Metric_Pad1.18x1.45mm_HandSolder; LCSC Part C45783
J1, J3: Conn_01x03; PinHeader_1x01_P2.54mm_simple
J2, J4: Conn_01x03; PinHeader_1x01_P2.54mm_simple_square
J5, J6: Screw_Terminal_01x02; TerminalBlock_or_JST_2.54_1x02
JP1, JP2, JP3, JP4: SolderJumper_2_Open; SolderJumper-2_P1.3mm_Open_RoundedPad1.0x1.5mm_simple
L1: 15u; Inductor_Multi_5.2x5.7_2x2.5
R1: 100K; R_0402_1005Metric; LCSC Part C25741
R2: 22K; R_0402_1005Metric; LCSC Part C25768
R3: 12K; R_0402_1005Metric; LCSC Part C25752
R4: 1K2; R_0402_1005Metric; LCSC Part C25862
R5: 6.8K; R_0402_1005Metric; LCSC Part C25917
R6: 220R; R_0402_1005Metric; LCSC Part C25091
R7: 5.1K; R_0402_1005Metric; LCSC Part C25905
R8: 120R; R_0402_1005Metric; LCSC Part C25079
SW1: SW_DIP_x04; SW_DIP_SPSTx04_Slide_P1.27mm_simple
U1: TPS54202DDCR; SOT-23-6_Handsoldering; LCSC Part C191884

Connections:
3V3_SELECT: JP1.1 (A), R2.1, SW1.8
5V_SELECT: JP2.1 (A), R3.1, SW1.7
9V_SELECT: JP3.1 (A), R5.1, SW1.6
12V_SELECT: JP4.1 (A), R7.1, SW1.5
BOOT: C3.1, U1.6 (BOOT)
FB: JP1.2 (B), JP2.2 (B), JP3.2 (B), JP4.2 (B), R1.2, SW1.1, SW1.2, SW1.3, SW1.4, U1.4 (FB)
GND: C1.2, C2.2, C4.2, C5.2, J2.1, J4.1, J5.2, J6.2, R2.2, R4.2, R6.2, R8.2, U1.1 (GND)
unnamed: R3.2, R4.1
unnamed: R5.2, R6.1
unnamed: R7.2, R8.1
SW: C3.2, L1.1, U1.2 (SW)
VIN: C1.1, C2.1, J1.1, J5.1, U1.3 (VIN)
VOUT: C4.1, C5.1, J3.1, J6.1, L1.2, R1.1

Notes on the sheet:
5V buck converter
Pins
CERN-OHL-P v2
