smkent/pcb/dev/power/buck-tps54202/buck-tps54202.kicad_sch

## KiCad design dev/power/buck-tps54202/buck-tps54202.kicad_sch (2024-11-30)

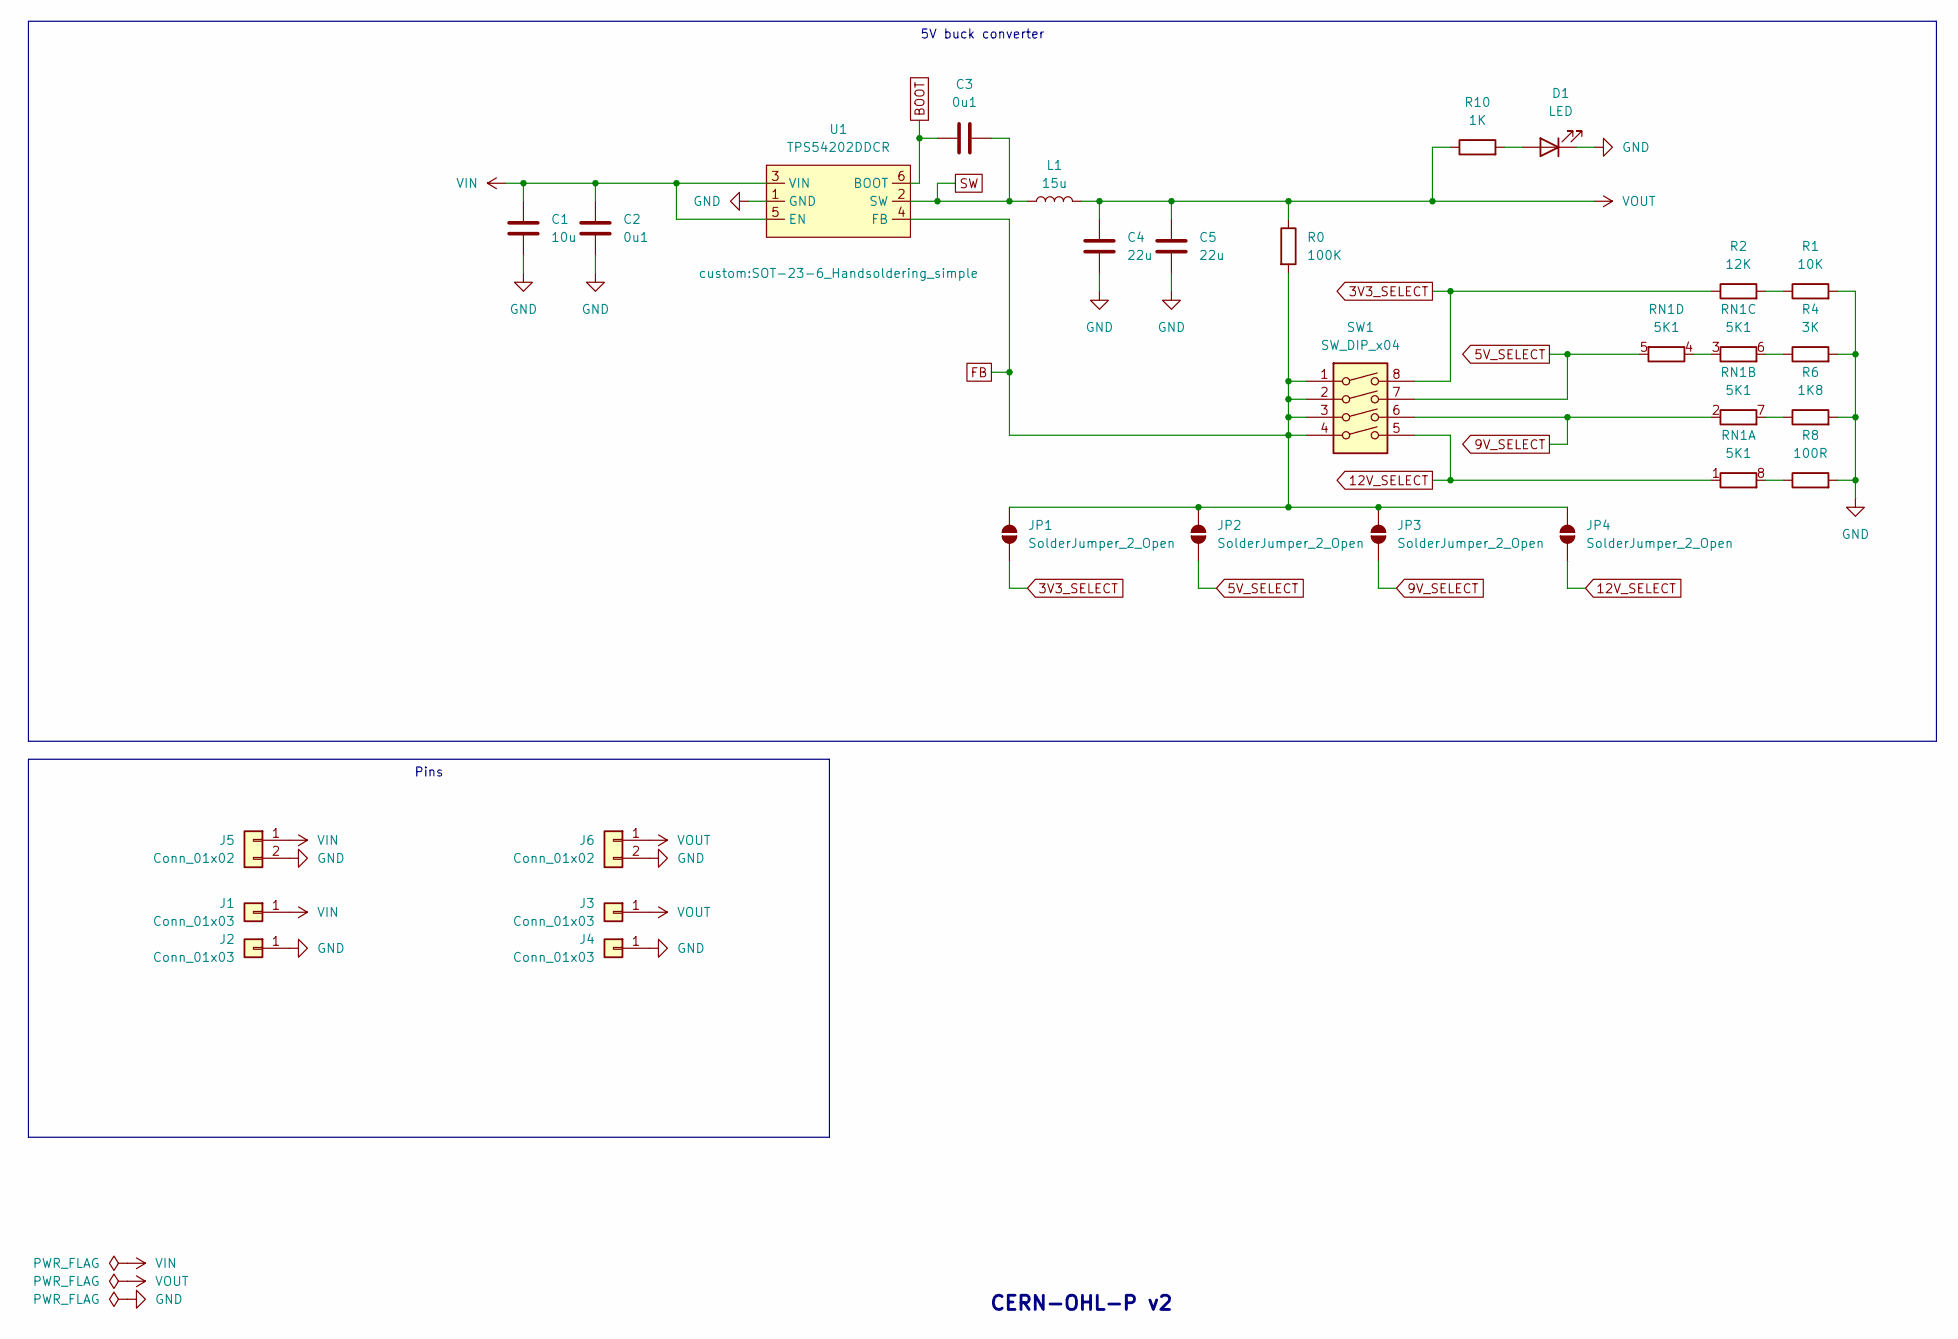
[picture p195: schematic buck-tps54202.kicad_sch]

Parts:
C1: 10u; C_0805_2012Metric_Pad1.18x1.45mm_HandSolder; LCSC Part C440198
C2, C3: 0u1; C_0805_2012Metric_Pad1.18x1.45mm_HandSolder
C4, C5: 22u; C_0805_2012Metric_Pad1.18x1.45mm_HandSolder; LCSC Part C45783
D1: LED; LED_0805_2012Metric_Pad1.15x1.40mm_HandSolder_simple
J1, J3: Conn_01x03; PinHeader_1x01_P2.54mm_simple
J2, J4: Conn_01x03; PinHeader_1x01_P2.54mm_simple_square
J5, J6: Conn_01x02; JST_XH_S2B-XH-2AW_1x02_P2.50mm_pad2gnd_trim2
JP1, JP2, JP3, JP4: SolderJumper_2_Open; SolderJumper-2_P1.3mm_Open_RoundedPad1.0x1.5mm_simple
L1: 15u; Inductor_Multi_7.0x6.6_plus
R0: 100K; R_0805_2012Metric_Pad1.20x1.40mm_HandSolder
R1: 10K; R_0805_2012Metric_Pad1.20x1.40mm_HandSolder
R2: 12K; R_0805_2012Metric_Pad1.20x1.40mm_HandSolder
R4: 3K; R_0805_2012Metric_Pad1.20x1.40mm_HandSolder
R6: 1K8; R_0805_2012Metric_Pad1.20x1.40mm_HandSolder
R8: 100R; R_0805_2012Metric_Pad1.20x1.40mm_HandSolder
R10: 1K; R_0805_2012Metric_Pad1.20x1.40mm_HandSolder
RN1: 5K1; R_Array_Convex_4x0603
SW1: SW_DIP_x04; SW_DIP_SPSTx04_Slide_P1.27mm_simple
U1: TPS54202DDCR; SOT-23-6_Handsoldering_simple; LCSC Part C191884

Connections:
3V3_SELECT: JP1.1 (A), R2.1, SW1.8
5V_SELECT: JP2.1 (A), RN1.5 (R4.2), SW1.7
9V_SELECT: JP3.1 (A), RN1.2 (R2.1), SW1.6
12V_SELECT: JP4.1 (A), RN1.1 (R1.1), SW1.5
BOOT: C3.1, U1.6 (BOOT)
FB: JP1.2 (B), JP2.2 (B), JP3.2 (B), JP4.2 (B), R0.2, SW1.1, SW1.2, SW1.3, SW1.4, U1.4 (FB)
GND: C1.2, C2.2, C4.2, C5.2, D1.1 (K), J2.1, J4.1, J5.2, J6.2, R1.2, R4.2, R6.2, R8.2, U1.1 (GND)
unnamed: D1.2 (A), R10.2
unnamed: R1.1, R2.2
unnamed: R4.1, RN1.6 (R3.2)
unnamed: R6.1, RN1.7 (R2.2)
unnamed: R8.1, RN1.8 (R1.2)
unnamed: RN1.3 (R3.1), RN1.4 (R4.1)
SW: C3.2, L1.1, U1.2 (SW)
VIN: C1.1, C2.1, J1.1, J5.1, U1.3 (VIN), U1.5 (EN)
VOUT: C4.1, C5.1, J3.1, J6.1, L1.2, R0.1, R10.1

Notes on the sheet:
5V buck converter
Pins
CERN-OHL-P v2
