smkent/pcb/dev/power/ip5209-ups/battery_charger.kicad_sch

## KiCad design dev/power/ip5209-ups/battery_charger.kicad_sch (2024-08-23)

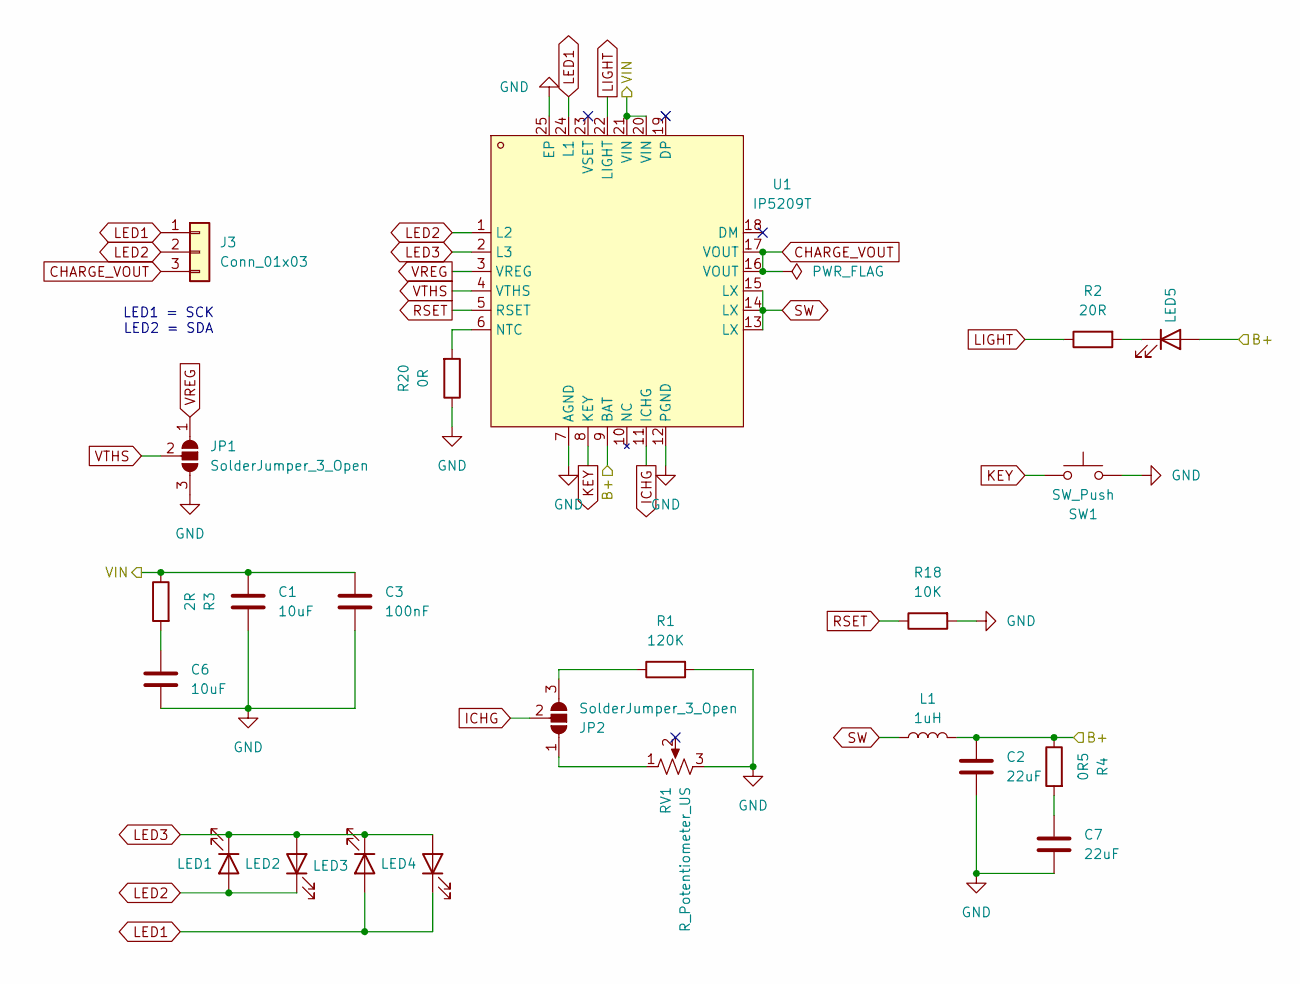
[picture p196: schematic battery_charger.kicad_sch]

Parts:
C1, C6: 10uF; C_0402_1005Metric; LCSC Part C15525
C2, C7: 22uF; C_0603_1608Metric; LCSC Part C59461
C3: 100nF; C_0402_1005Metric; LCSC Part C307331
J3: Conn_01x03; PinHeader_1x03_P2.54mm_Vertical_simple
JP1, JP2: SolderJumper_3_Open; SolderJumper-3_P1.3mm_Open_RoundedPad1.0x1.5mm
L1: 1uH; L_1210_3225Metric; LCSC Part C3002559
LED1, LED2, LED3, LED4: LED_0805_2012Metric_Pad1.15x1.40mm_HandSolder_simple
LED5: LED-SMD_3P-L5.7-W3.0-RD
R1: 120K; R_0805_2012Metric_Pad1.20x1.40mm_HandSolder; LCSC Part C17436
R2: 20R; R_0805_2012Metric_Pad1.20x1.40mm_HandSolder; LCSC Part C17544
R3: 2R; R_0603_1608Metric; LCSC Part C22977
R4: 0R5; R_0805_2012Metric_Pad1.20x1.40mm_HandSolder
R18: 10K; R_0805_2012Metric_Pad1.20x1.40mm_HandSolder
R20: 0R; R_0805_2012Metric_Pad1.20x1.40mm_HandSolder; LCSC Part C17477
RV1: R_Potentiometer_US; RES-ADJ-SMD_VG039NCH
SW1: SW_Push; SW-SMD_BZCN_TSA002A35XXX
U1: IP5209T; QFN-24-1EP_4x4mm_P0.5mm_EP2.6x2.6mm_ThermalVias; LCSC Part C284964

Connections:
B+: C2.1, L1.2, LED5.2 (A), R4.1, U1.9 (BAT)
CHARGE_VOUT: J3.3, U1.16 (VOUT), U1.17 (VOUT)
GND: C1.2, C2.2, C3.2, C6.2, C7.2, JP1.3 (B), R1.2, R18.2, R20.1, RV1.3, SW1.1, U1.7 (AGND), U1.12 (PGND), U1.25 (EP)
ICHG: JP2.2 (C), U1.11 (ICHG)
KEY: SW1.2, U1.8 (KEY)
LED1: J3.1, LED3.2 (A), LED4.1 (K), U1.24 (L1)
LED2: J3.2, LED1.2 (A), LED2.1 (K), U1.1 (L2)
LED3: LED1.1 (K), LED2.2 (A), LED3.1 (K), LED4.2 (A), U1.2 (L3)
LIGHT: R2.1, U1.22 (LIGHT)
unnamed: C6.1, R3.2
unnamed: C7.1, R4.2
unnamed: JP2.1 (A), RV1.1
unnamed: JP2.3 (B), R1.1
unnamed: LED5.1 (K), R2.2
unnamed: R20.2, U1.6 (NTC)
RSET: R18.1, U1.5 (RSET)
SW: L1.1, U1.13 (LX), U1.14 (LX), U1.15 (LX)
VIN: C1.1, C3.1, R3.1, U1.20 (VIN), U1.21 (VIN)
VREG: JP1.1 (A), U1.3 (VREG)
VTHS: JP1.2 (C), U1.4 (VTHS)

Notes on the sheet:
LED1 = SCK LED2 = SDA
