smkent/pcb/dev/power/ip5209-ups/battery_protection.kicad_sch

## KiCad design dev/power/ip5209-ups/battery_protection.kicad_sch (2024-08-23)

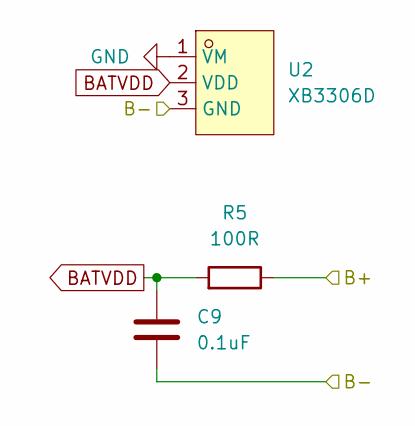
[picture p197: schematic battery_protection.kicad_sch]

Parts:
C9: 0.1uF; C_0402_1005Metric; LCSC Part C1525
R5: 100R; R_0805_2012Metric_Pad1.20x1.40mm_HandSolder; LCSC Part C17408
U2: XB3306D; SOT-23-3; LCSC Part C2759992

Connections:
B+: R5.1
B-: C9.1, U2.3 (GND)
BATVDD: C9.2, R5.2, U2.2 (VDD)
GND: U2.1 (VM)
