smkent/pcb/dev/power/ip5209-ups/battery_sense.kicad_sch

## KiCad design dev/power/ip5209-ups/battery_sense.kicad_sch (2024-08-09)

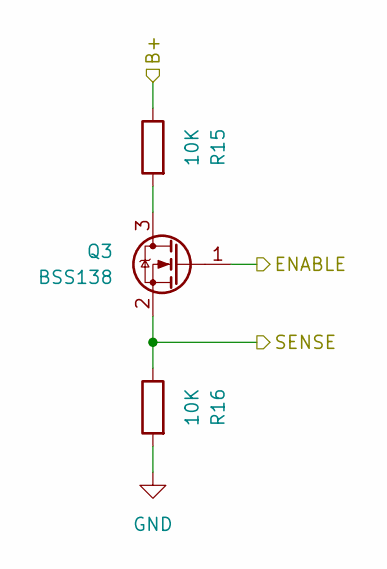
[picture p198: schematic battery_sense.kicad_sch]

Parts:
Q3: BSS138; SOT-23; LCSC Part C7420339
R15, R16: 10K; R_0402_1005Metric; LCSC Part C25744

Connections:
B+: R15.1
ENABLE: Q3.1 (G)
GND: R16.2
unnamed: Q3.3 (D), R15.2
SENSE: Q3.2 (S), R16.1
