smkent/pcb/dev/power/ip5209-ups/boost_converter.kicad_sch

## KiCad design dev/power/ip5209-ups/boost_converter.kicad_sch (2024-08-23)

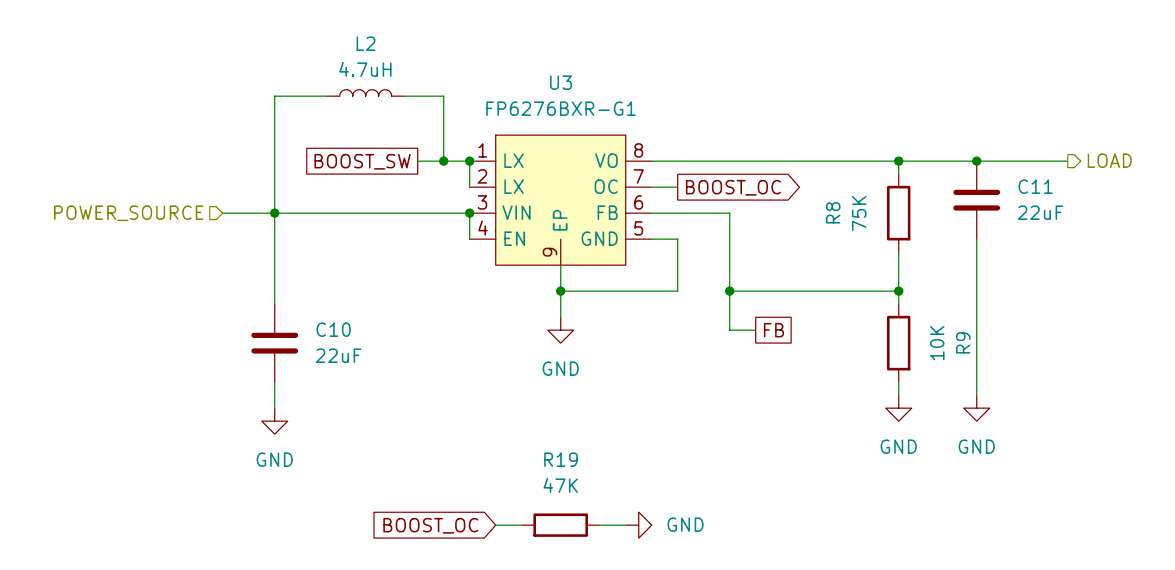
[picture p199: schematic boost_converter.kicad_sch]

Parts:
C10, C11: 22uF; C_0603_1608Metric; LCSC Part C59461
L2: 4.7uH; IND-SMD_L7.0-W6.6; LCSC Part C5307631
R8: 75K; R_0402_1005Metric; LCSC Part C25798
R9: 10K; R_0402_1005Metric; LCSC Part C25744
R19: 47K; R_0805_2012Metric_Pad1.20x1.40mm_HandSolder; LCSC Part C17713
U3: FP6276BXR-G1; SOIC-8-1EP_3.9x4.9mm_P1.27mm_EP2.41x3.3mm_ThermalVias_Custo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; LCSC Part C82652

Connections:
BOOST_OC: R19.2, U3.7 (OC)
BOOST_SW: L2.2, U3.1 (LX), U3.2 (LX)
FB: R8.2, R9.1, U3.6 (FB)
GND: C10.2, C11.2, R9.2, R19.1, U3.5 (GND), U3.9 (EP)
LOAD: C11.1, R8.1, U3.8 (VO)
POWER_SOURCE: C10.1, L2.1, U3.3 (VIN), U3.4 (EN)
