smkent/pcb/dev/power/ip5209-ups/connectors.kicad_sch

## KiCad design dev/power/ip5209-ups/connectors.kicad_sch (2024-08-23)

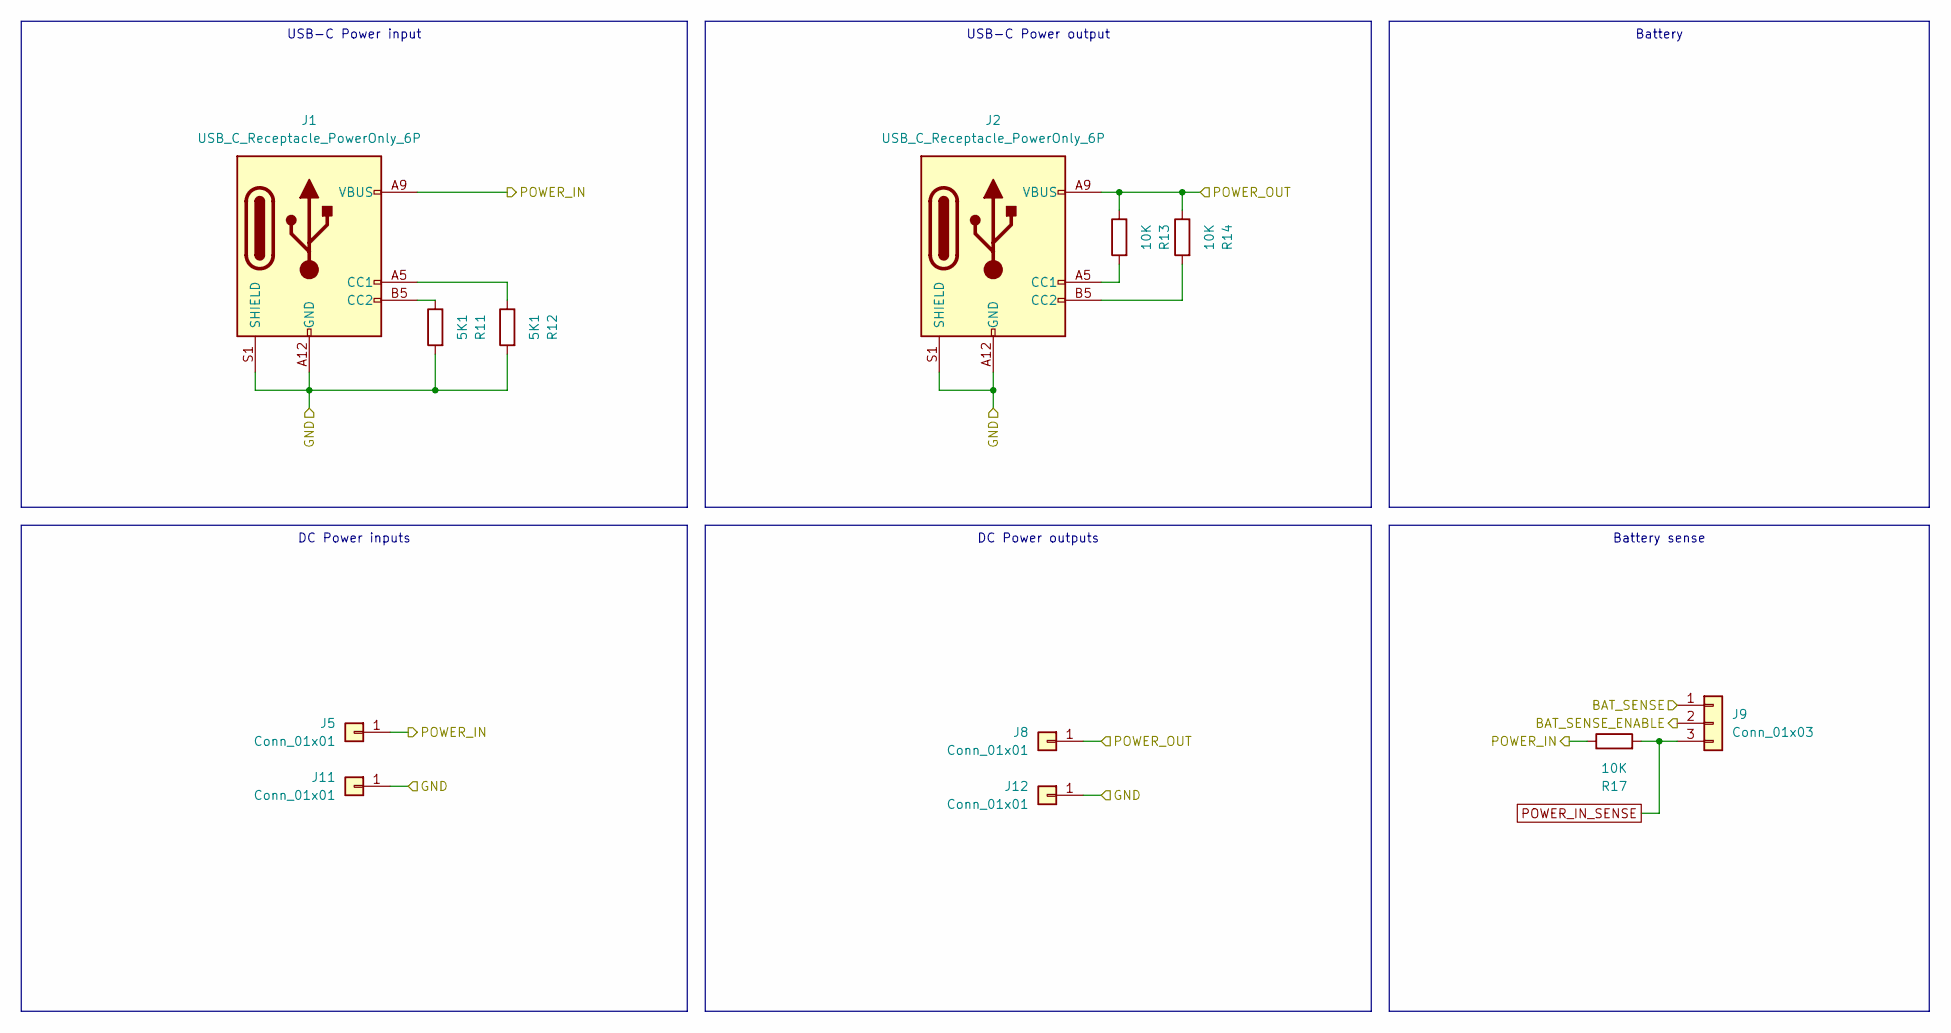
[picture p200: schematic connectors.kicad_sch]

Parts:
J1, J2: USB_C_Receptacle_PowerOnly_6P; USB_C_Receptacle_GCT_USB4125-xx-x_6P_TopMnt_Horizontal_hand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
J5, J8: Conn_01x01; PinHeader_1x01_P2.54mm_simple
J9: Conn_01x03; PinHeader_1x03_P2.54mm_Vertical_simple
J11, J12: Conn_01x01; PinHeader_1x01_P2.54mm_simple_square
R11, R12: 5K1; R_0402_1005Metric; LCSC Part C25905
R13, R14, R17: 10K; R_0402_1005Metric; LCSC Part C25744

Connections:
BAT_SENSE: J9.1
BAT_SENSE_ENABLE: J9.2
GND: J1.A12 (GND), J1.B12 (GND), J1.S1 (SHIELD), J2.A12 (GND), J2.B12 (GND), J2.S1 (SHIELD), J11.1, J12.1, R11.2, R12.2
unnamed: J1.A5 (CC1), R12.1
unnamed: J1.B5 (CC2), R11.1
unnamed: J2.A5 (CC1), R13.2
unnamed: J2.B5 (CC2), R14.2
POWER_IN: J1.A9 (VBUS), J1.B9 (VBUS), J5.1, R17.1
POWER_IN_SENSE: J9.3, R17.2
POWER_OUT: J2.A9 (VBUS), J2.B9 (VBUS), J8.1, R13.1, R14.1

Notes on the sheet:
DC Power outputs
USB-C Power output
DC Power inputs
Battery sense
USB-C Power input
Battery
