smkent/pcb/dev/power/ip5209-ups/ip5209-ups.kicad_sch

## KiCad design dev/power/ip5209-ups/ip5209-ups.kicad_sch (2024-11-30)

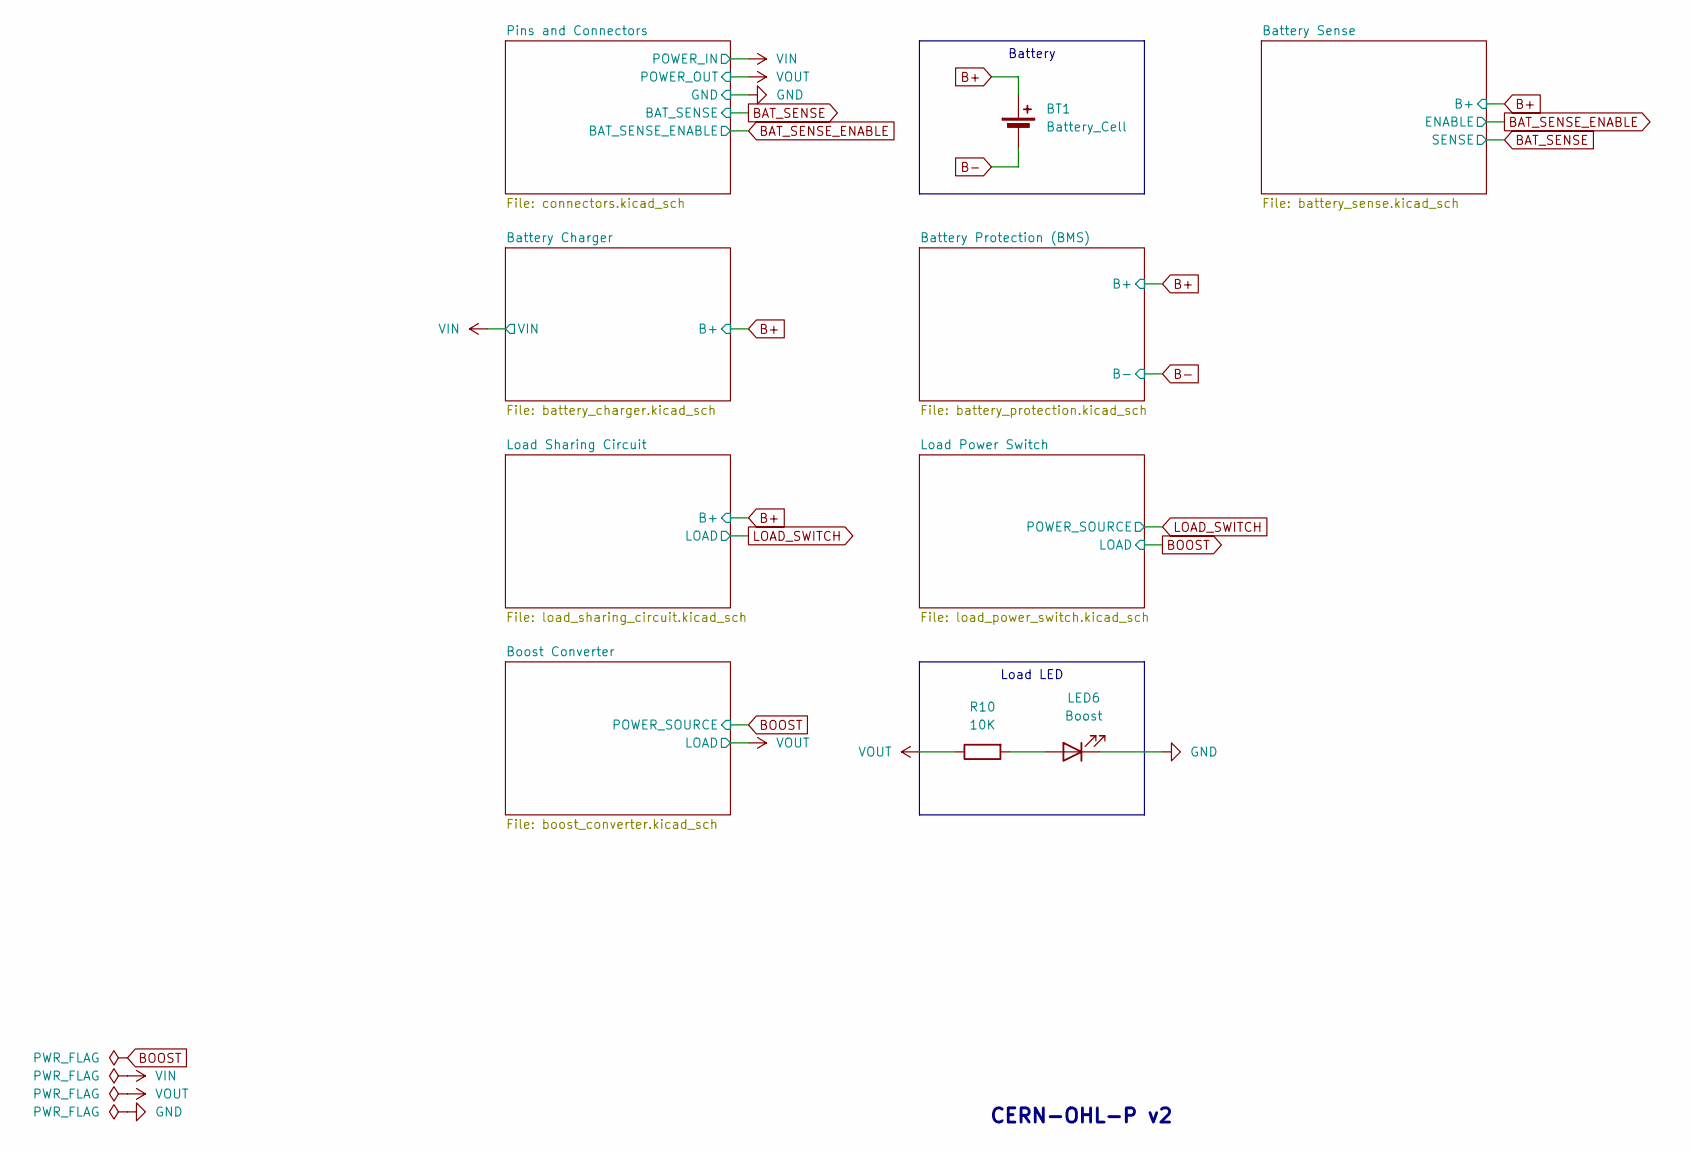
[picture p201: schematic ip5209-ups.kicad_sch]

Parts:
BT1: Battery_Cell; JST_XH_S2B-XH-2AW_1x02_P2.50mm_pad2gnd_trim
LED6: Boost; LED_0805_2012Metric_Pad1.15x1.40mm_HandSolder_simple
R10: 10K; R_0402_1005Metric; LCSC Part C25744

Connections:
B+: BT1.1 (+)
B-: BT1.2 (-)
GND: LED6.1 (K)
unnamed: LED6.2 (A), R10.2
VOUT: R10.1

Notes on the sheet:
Battery
Load LED
CERN-OHL-P v2
