smkent/pcb/dev/power/ip5209-ups/load_power_switch.kicad_sch

## KiCad design dev/power/ip5209-ups/load_power_switch.kicad_sch (2024-08-23)

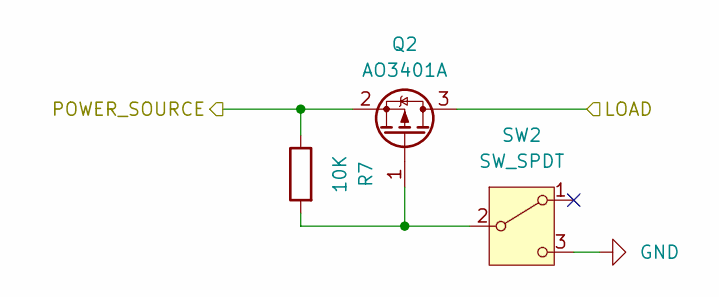
[picture p202: schematic load_power_switch.kicad_sch]

Parts:
Q2: AO3401A; SOT-23; LCSC Part C15127
R7: 10K; R_0402_1005Metric; LCSC Part C25744
SW2: SW_SPDT; SW-SMD_3P-P1.50_L2.7-W6.6; LCSC Part C2998803

Connections:
GND: SW2.3 (C)
LOAD: Q2.3 (D)
unnamed: Q2.1 (G), R7.2, SW2.2 (B)
POWER_SOURCE: Q2.2 (S), R7.1
