smkent/pcb/dev/power/ip5209-ups/load_sharing_circuit.kicad_sch

## KiCad design dev/power/ip5209-ups/load_sharing_circuit.kicad_sch (2024-08-05)

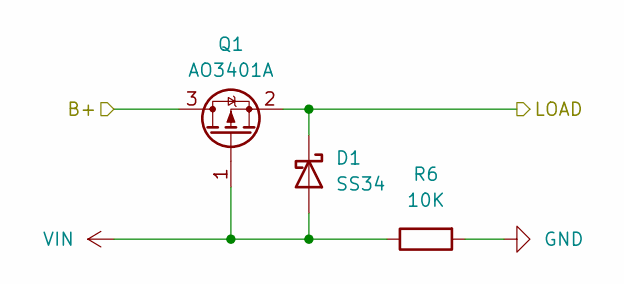
[picture p203: schematic load_sharing_circuit.kicad_sch]

Parts:
D1: SS34; D_SMA_simple; LCSC Part C8678
Q1: AO3401A; SOT-23; LCSC Part C15127
R6: 10K; R_0402_1005Metric; LCSC Part C25744

Connections:
B+: Q1.3 (D)
GND: R6.2
LOAD: D1.1 (K), Q1.2 (S)
VIN: D1.2 (A), Q1.1 (G), R6.1
