smkent/pcb/dev/power/ip5306-ups/battery_charger.kicad_sch

## KiCad design dev/power/ip5306-ups/battery_charger.kicad_sch (2024-08-05)

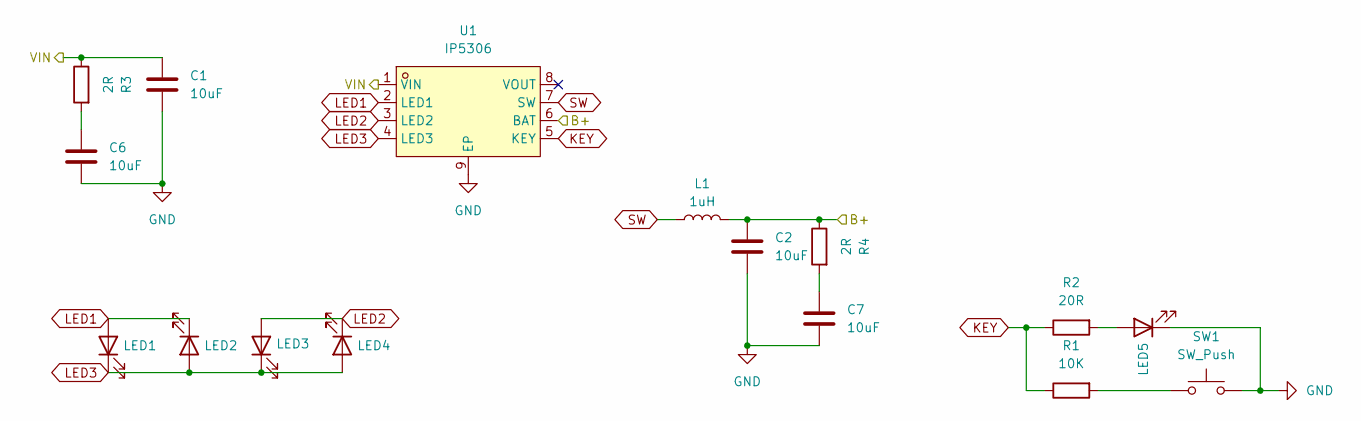
[picture p204: schematic battery_charger.kicad_sch]

Parts:
C1, C2, C6, C7: 10uF; C_0402_1005Metric; LCSC Part C15525
L1: 1uH; Inductor_Multi_7.0x6.6_plus; LCSC Part C5832376
LED1, LED2, LED3, LED4: LED_0805_2012Metric_Pad1.15x1.40mm_HandSolder_simple
LED5: LED-SMD_3P-L5.7-W3.0-RD
R1: 10K; R_0402_1005Metric; LCSC Part C25744
R2: 20R; R_0805_2012Metric_Pad1.20x1.40mm_HandSolder
R3, R4: 2R; R_0402_1005Metric
SW1: SW_Push; Push-Button-SMD-4x4x1.5mm_2P_Large_Pads
U1: IP5306; SOIC-8-1EP_3.9x4.9mm_P1.27mm_EP2.41x3.3mm_ThermalVias_Custo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; LCSC Part C181692

Connections:
B+: C2.1, L1.2, R4.1, U1.6 (BAT)
GND: C1.2, C2.2, C6.2, C7.2, LED5.1 (K), SW1.2, U1.9 (EP)
KEY: R1.1, R2.1, U1.5 (KEY)
LED1: LED1.2 (A), LED2.1 (K), U1.2 (LED1)
LED2: LED3.2 (A), LED4.1 (K), U1.3 (LED2)
LED3: LED1.1 (K), LED2.2 (A), LED3.1 (K), LED4.2 (A), U1.4 (LED3)
unnamed: C6.1, R3.2
unnamed: C7.1, R4.2
unnamed: LED5.2 (A), R2.2
unnamed: R1.2, SW1.1
SW: L1.1, U1.7 (SW)
VIN: C1.1, R3.1, U1.1 (VIN)
