smkent/pcb/dev/power/ip5306-ups/battery_protection.kicad_sch

## KiCad design dev/power/ip5306-ups/battery_protection.kicad_sch (2024-08-05)

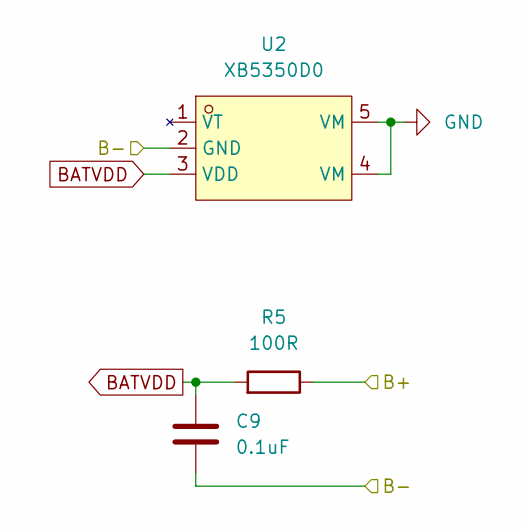
[picture p205: schematic battery_protection.kicad_sch]

Parts:
C9: 0.1uF; C_0402_1005Metric; LCSC Part C1525
R5: 100R; R_0805_2012Metric_Pad1.20x1.40mm_HandSolder; LCSC Part C17408
U2: XB5350D0; SOT-23-5_simple; JLCPCB_CORRECTION 0; 0; 180

Connections:
B+: R5.1
B-: C9.1, U2.2 (GND)
BATVDD: C9.2, R5.2, U2.3 (VDD)
GND: U2.4 (VM), U2.5 (VM)
