smkent/pcb/dev/power/ip5306-ups/battery_sense.kicad_sch

## KiCad design dev/power/ip5306-ups/battery_sense.kicad_sch (2024-08-05)

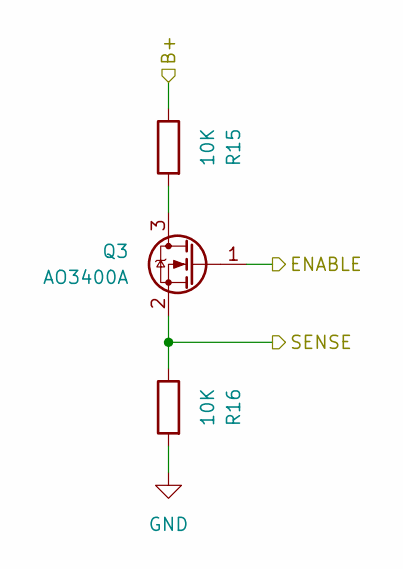
[picture p206: schematic battery_sense.kicad_sch]

Parts:
Q3: AO3400A; SOT-23
R15, R16: 10K; R_0402_1005Metric; LCSC Part C25744

Connections:
B+: R15.1
ENABLE: Q3.1 (G)
GND: R16.2
unnamed: Q3.3 (D), R15.2
SENSE: Q3.2 (S), R16.1
