smkent/pcb/dev/power/ip5306-ups/boost_converter.kicad_sch

## KiCad design dev/power/ip5306-ups/boost_converter.kicad_sch (2024-08-05)

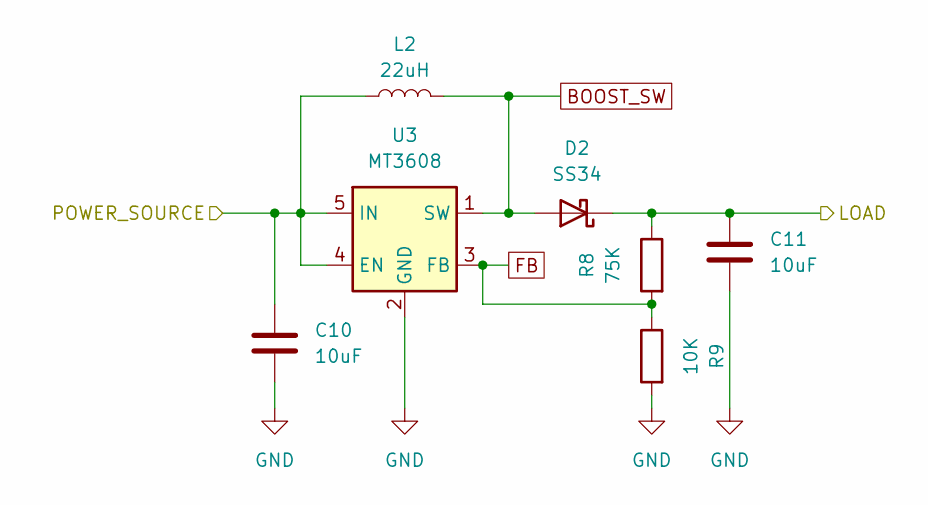
[picture p207: schematic boost_converter.kicad_sch]

Parts:
C10: 10uF; C_0603_1608Metric; LCSC Part C19702
C11: 10uF; C_0402_1005Metric; LCSC Part C15525
D2: SS34; D_SMA_simple; LCSC Part C8678
L2: 22uH; IND-SMD_L7.0-W6.6; LCSC Part C5832376
R8: 75K; R_0402_1005Metric; LCSC Part C25798
R9: 10K; R_0402_1005Metric; LCSC Part C25744
U3: MT3608; SOT-23-6; LCSC Part C84817

Connections:
BOOST_SW: D2.2 (A), L2.2, U3.1 (SW)
FB: R8.2, R9.1, U3.3 (FB)
GND: C10.2, C11.2, R9.2, U3.2 (GND)
LOAD: C11.1, D2.1 (K), R8.1
POWER_SOURCE: C10.1, L2.1, U3.4 (EN), U3.5 (IN)
