smkent/pcb/dev/power/ip5306-ups/connectors.kicad_sch

## KiCad design dev/power/ip5306-ups/connectors.kicad_sch (2024-08-05)

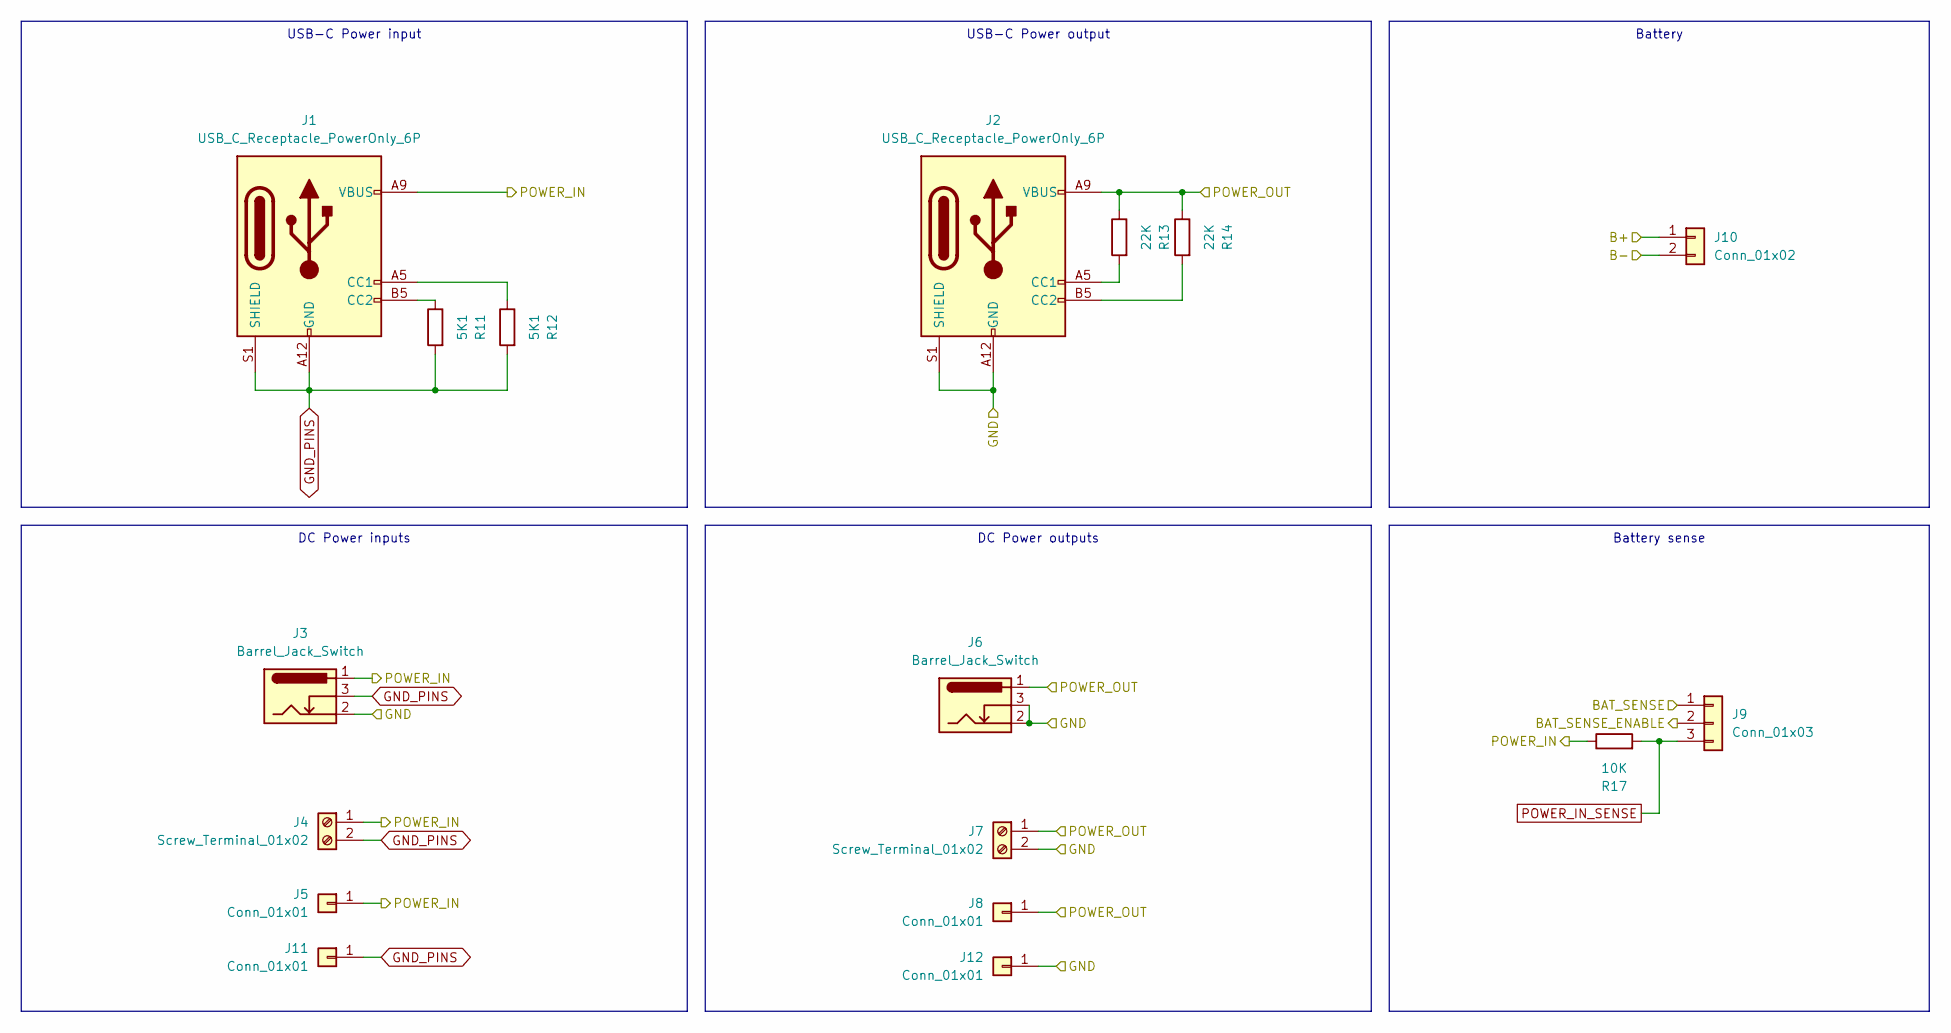
[picture p208: schematic connectors.kicad_sch]

Parts:
J1, J2: USB_C_Receptacle_PowerOnly_6P; USB_C_Receptacle_GCT_USB4125-xx-x_6P_TopMnt_Horizontal_hand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
J3, J6: Barrel_Jack_Switch; DC-IN_DC-050-2.0-BB
J4, J7: Screw_Terminal_01x02; TerminalBlock_Phoenix_MKDS-1,5-2-5.08_1x02_P5.08mm_Horizont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
J5, J8: Conn_01x01; PinHeader_1x01_P2.54mm_simple
J9: Conn_01x03; PinHeader_1x03_P2.54mm_Vertical_simple
J10: Conn_01x02; JST_XH_S2B-XH-2AW_1x02_P2.50mm_pad2gnd
J11, J12: Conn_01x01; PinHeader_1x01_P2.54mm_simple_square
R11, R12: 5K1; R_0402_1005Metric; LCSC Part C25905
R13, R14: 22K; R_0402_1005Metric; LCSC Part C25768
R17: 10K; R_0402_1005Metric; LCSC Part C25744

Connections:
B+: J10.1
B-: J10.2
BAT_SENSE: J9.1
BAT_SENSE_ENABLE: J9.2
GND: J2.A12 (GND), J2.B12 (GND), J2.S1 (SHIELD), J3.2, J6.2, J6.3, J7.2, J12.1
GND_PINS: J1.A12 (GND), J1.B12 (GND), J1.S1 (SHIELD), J3.3, J4.2, J11.1, R11.2, R12.2
unnamed: J1.A5 (CC1), R12.1
unnamed: J1.B5 (CC2), R11.1
unnamed: J2.A5 (CC1), R13.2
unnamed: J2.B5 (CC2), R14.2
POWER_IN: J1.A9 (VBUS), J1.B9 (VBUS), J3.1, J4.1, J5.1, R17.1
POWER_IN_SENSE: J9.3, R17.2
POWER_OUT: J2.A9 (VBUS), J2.B9 (VBUS), J6.1, J7.1, J8.1, R13.1, R14.1

Notes on the sheet:
DC Power outputs
USB-C Power output
DC Power inputs
Battery sense
USB-C Power input
Battery
