smkent/pcb/dev/power/tp4056-5v-ups/tp4056-5v-ups.kicad_sch

## KiCad design dev/power/tp4056-5v-ups/tp4056-5v-ups.kicad_sch (2024-11-30)

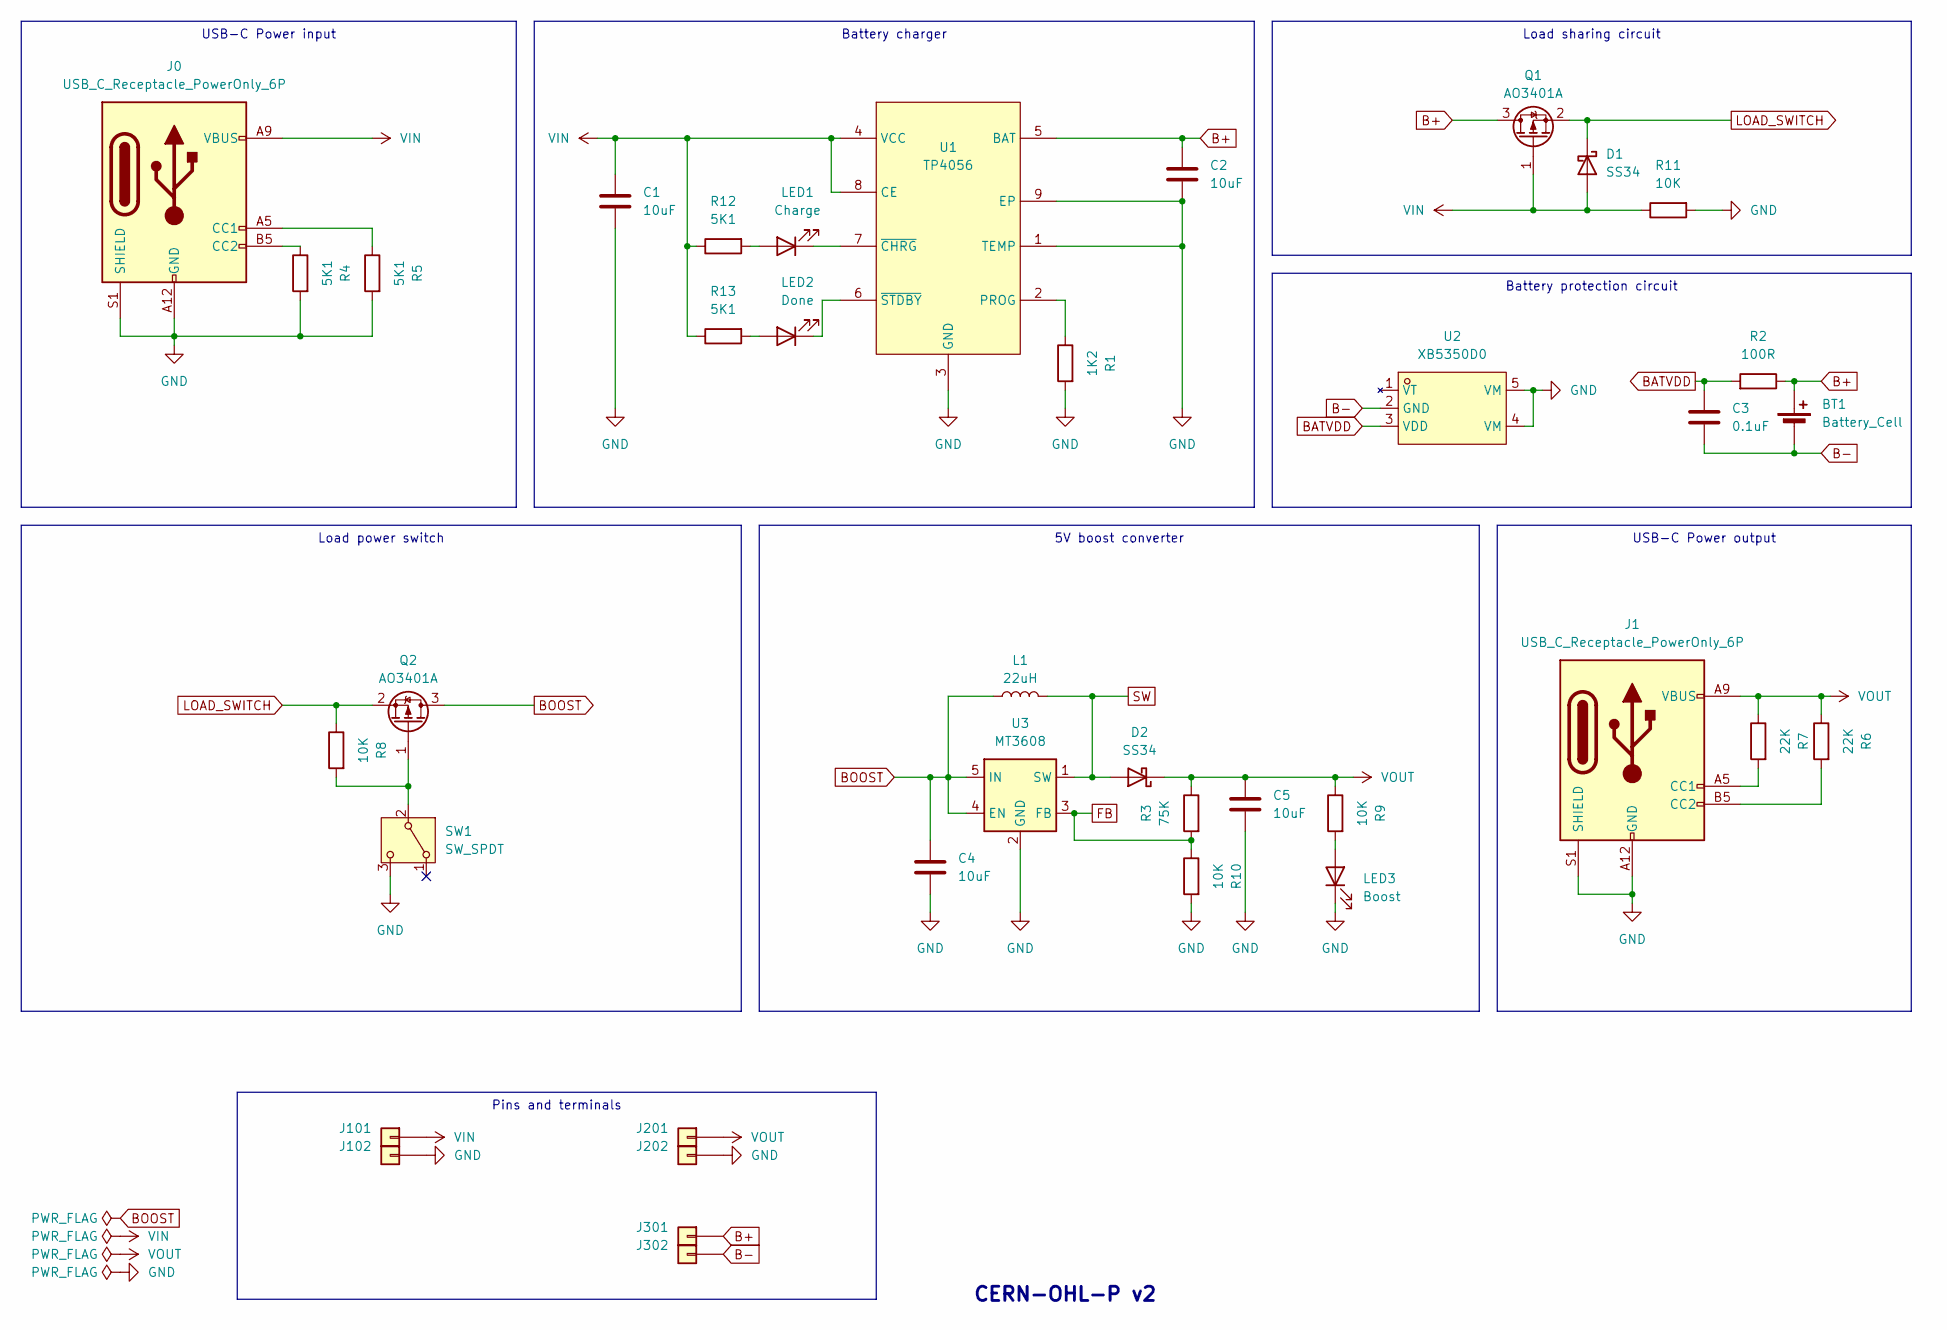
[picture p209: schematic tp4056-5v-ups.kicad_sch]

Parts:
BT1: Battery_Cell; JST_XH_B2B-XH-A_1x02_P2.50mm_Vertical_simple_pad2gnd
C1, C2, C4: 10uF; C_0603_1608Metric; LCSC Part C19702
C3: 0.1uF; C_0402_1005Metric; LCSC Part C1525
C5: 10uF; C_0402_1005Metric; LCSC Part C15525
D1, D2: SS34; D_SMA_simple; LCSC Part C8678
J0, J1: USB_C_Receptacle_PowerOnly_6P; USB_C_Receptacle_GCT_USB4125-xx-x_6P_TopMnt_Horizontal_hand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
J101, J201, J301: Conn_01x01; PinHeader_1x01_P2.54mm_simple
J102, J202, J302: Conn_01x01; PinHeader_1x01_P2.54mm_simple_square
L1: 22uH; IND-SMD_L7.0-W6.6; LCSC Part C5832376
LED1: Charge; LED_0805_2012Metric_Pad1.15x1.40mm_HandSolder_simple
LED2: Done; LED_0805_2012Metric_Pad1.15x1.40mm_HandSolder_simple
LED3: Boost; LED_0805_2012Metric_Pad1.15x1.40mm_HandSolder_simple
Q1, Q2: AO3401A; SOT-23; LCSC Part C15127
R1: 1K2; R_0805_2012Metric_Pad1.20x1.40mm_HandSolder; LCSC Part C17379
R2: 100R; R_0805_2012Metric_Pad1.20x1.40mm_HandSolder; LCSC Part C17408
R3: 75K; R_0402_1005Metric; LCSC Part C25798
R4, R5, R12, R13: 5K1; R_0402_1005Metric; LCSC Part C25905
R6, R7: 22K; R_0402_1005Metric; LCSC Part C25768
R8, R9, R10, R11: 10K; R_0402_1005Metric; LCSC Part C25744
SW1: SW_SPDT; SW-TH_DEALON_SS-12D01-GX_simple; LCSC Part C2998803
U1: TP4056; SOIC-8-1EP_3.9x4.9mm_P1.27mm_EP2.41x3.3mm_ThermalVias_Custo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; JLCPCB_CORRECTION 0; 0; 270
U2: XB5350D0; SOT-23-5_simple; JLCPCB_CORRECTION 0; 0; 180
U3: MT3608; SOT-23-6; LCSC Part C84817

Connections:
B+: BT1.1 (+), C2.2, J301.1, Q1.3 (D), R2.1, U1.5 (BAT)
B-: BT1.2 (-), C3.1, J302.1, U2.2 (GND)
BATVDD: C3.2, R2.2, U2.3 (VDD)
BOOST: C4.1, L1.1, Q2.3 (D), U3.4 (EN), U3.5 (IN)
FB: R3.2, R10.1, U3.3 (FB)
GND: C1.2, C2.1, C4.2, C5.2, J0.A12 (GND), J0.B12 (GND), J0.S1 (SHIELD), J1.A12 (GND), J1.B12 (GND), J1.S1 (SHIELD), J102.1, J202.1, LED3.1 (K), R1.2, R4.2, R5.2, R10.2, R11.2, SW1.3 (C), U1.1 (TEMP), U1.3 (GND), U1.9 (EP), U2.4 (VM), U2.5 (VM), U3.2 (GND)
LOAD_SWITCH: D1.1 (K), Q1.2 (S), Q2.2 (S), R8.1
unnamed: J0.A5 (CC1), R5.1
unnamed: J0.B5 (CC2), R4.1
unnamed: J1.A5 (CC1), R7.2
unnamed: J1.B5 (CC2), R6.2
unnamed: LED1.1 (K), U1.7 (~CHRG)
unnamed: LED1.2 (A), R12.2
unnamed: LED2.1 (K), U1.6 (~STDBY)
unnamed: LED2.2 (A), R13.2
unnamed: LED3.2 (A), R9.2
unnamed: Q2.1 (G), R8.2, SW1.2 (B)
unnamed: R1.1, U1.2 (PROG)
SW: D2.2 (A), L1.2, U3.1 (SW)
VIN: C1.1, D1.2 (A), J0.A9 (VBUS), J0.B9 (VBUS), J101.1, Q1.1 (G), R11.1, R12.1, R13.1, U1.4 (VCC), U1.8 (CE)
VOUT: C5.1, D2.1 (K), J1.A9 (VBUS), J1.B9 (VBUS), J201.1, R3.1, R6.1, R7.1, R9.1

Notes on the sheet:
Pins and terminals
Battery protection circuit
USB-C Power output
USB-C Power input
Load sharing circuit
Load power switch
Battery charger
5V boost converter
CERN-OHL-P v2
