smkent/pcb/dev/power/tp4056-ls/tp4056-ls.kicad_sch

## KiCad design dev/power/tp4056-ls/tp4056-ls.kicad_sch (2024-11-30)

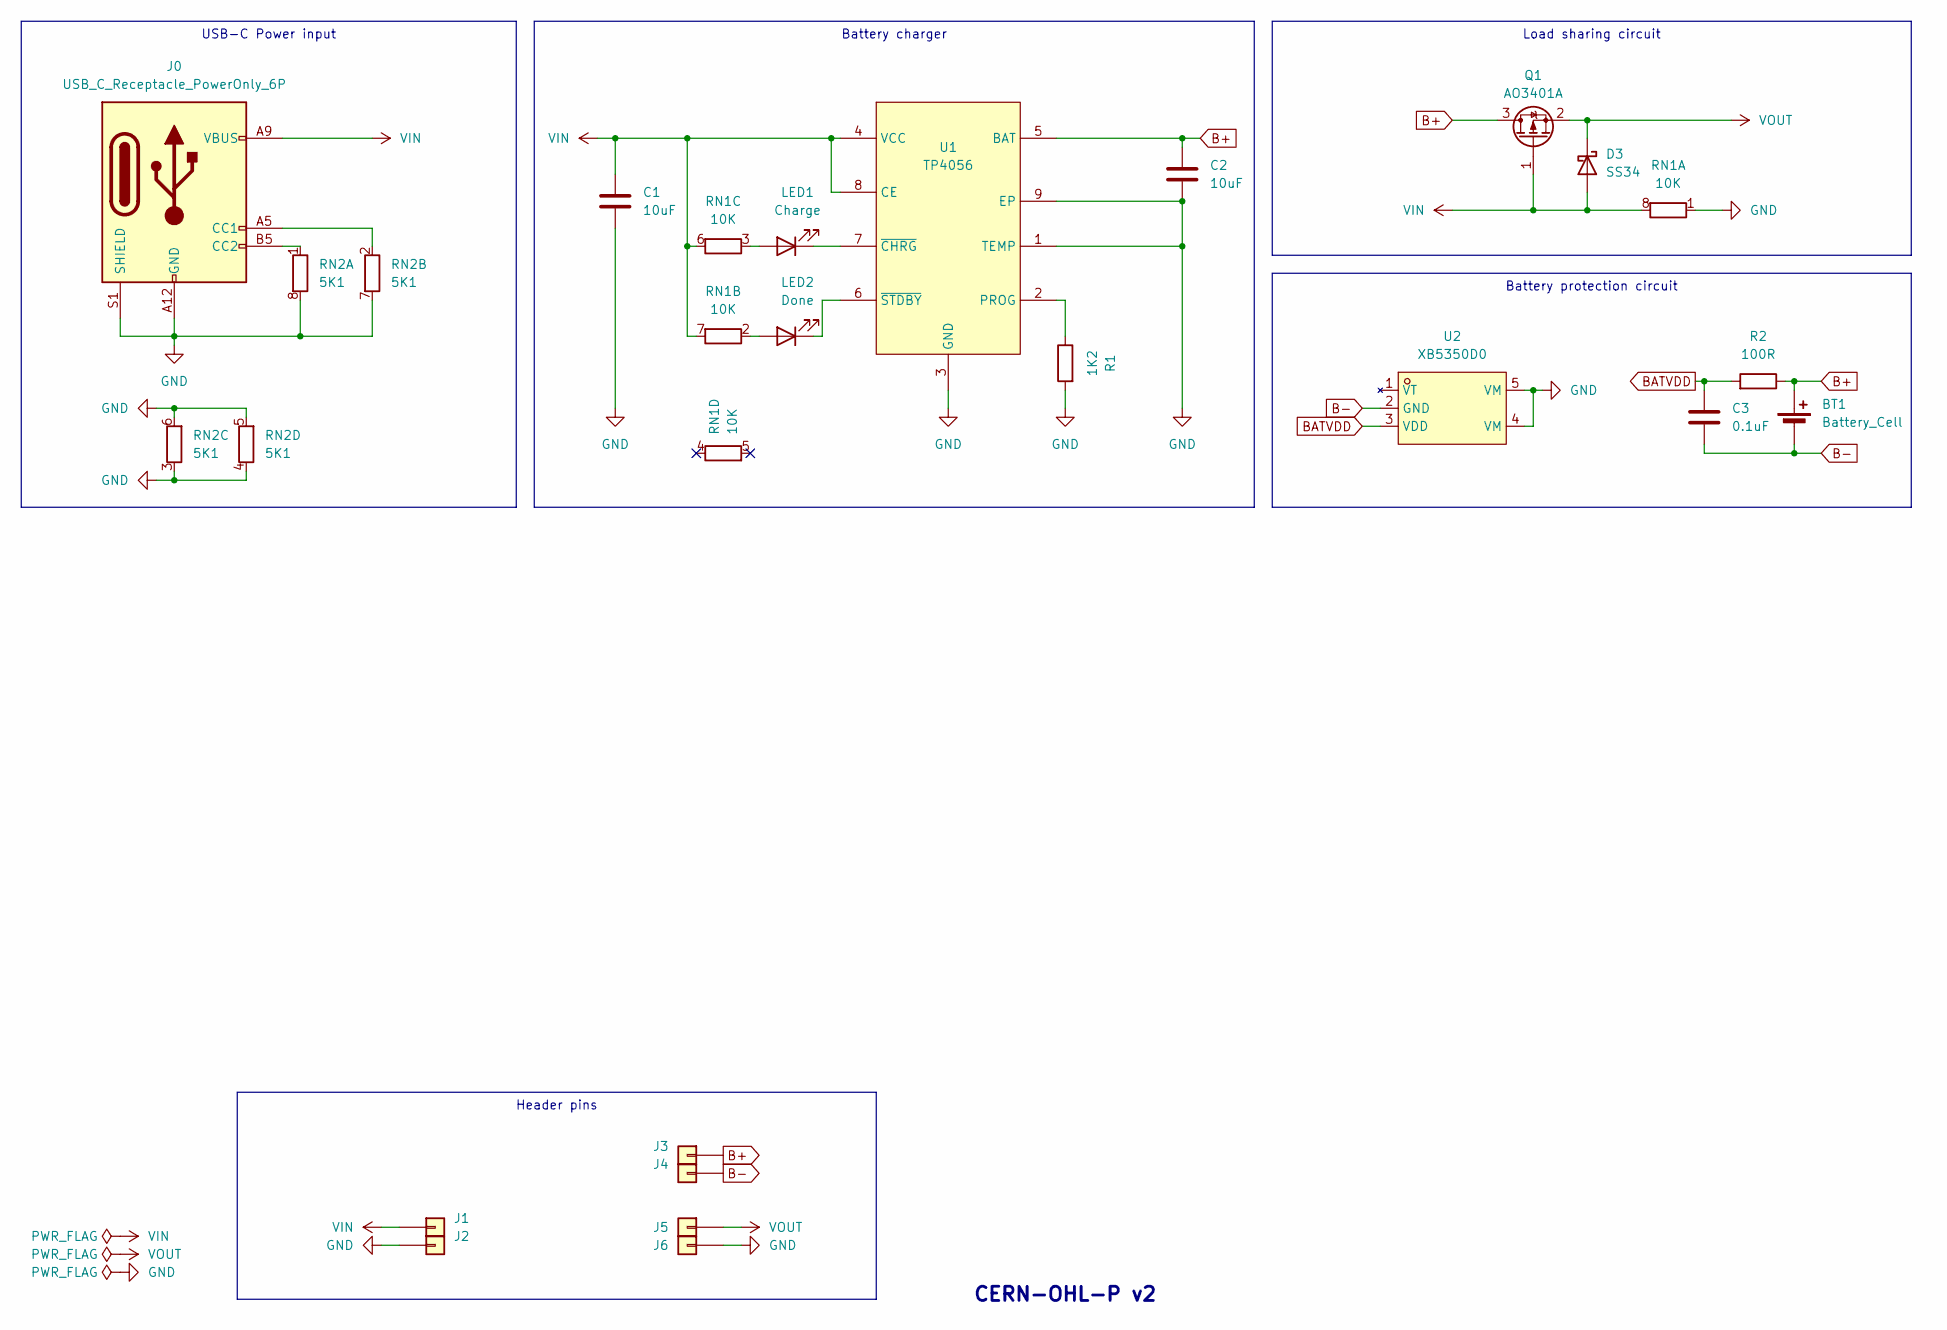
[picture p211: schematic tp4056-ls.kicad_sch]

Parts:
BT1: Battery_Cell; JST_XH_B2B-XH-A_1x02_P2.50mm_Vertical_simple
C1, C2: 10uF; C_0805_2012Metric_Pad1.18x1.45mm_HandSolder; LCSC Part C15850
C3: 0.1uF; C_0805_2012Metric_Pad1.18x1.45mm_HandSolder; LCSC Part C28233
D3: SS34; D_SMA_simple; LCSC Part C8678
J0: USB_C_Receptacle_PowerOnly_6P; USB_C_Receptacle_GCT_USB4125-xx-x_6P_TopMnt_Horizontal_hand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
J1, J3, J5: Conn_01x01; PinHeader_1x01_P2.54mm_simple
J2, J4, J6: Conn_01x01; PinHeader_1x01_P2.54mm_simple_square
LED1: Charge; LED_0805_2012Metric_Pad1.15x1.40mm_HandSolder_simple
LED2: Done; LED_0805_2012Metric_Pad1.15x1.40mm_HandSolder_simple
Q1: AO3401A; SOT-23; LCSC Part C15127
R1: 1K2; R_0805_2012Metric_Pad1.20x1.40mm_HandSolder; LCSC Part C17379
R2: 100R; R_0805_2012Metric_Pad1.20x1.40mm_HandSolder; LCSC Part C17408
RN1: 10K; R_Array_Convex_4x0603; LCSC Part C29718
RN2: 5K1; R_Array_Convex_4x0603
U1: TP4056; SOIC-8-1EP_3.9x4.9mm_P1.27mm_EP2.41x3.3mm_ThermalVias_Custo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; JLCPCB_CORRECTION 0; 0; 270
U2: XB5350D0; SOT-23-5_simple; JLCPCB_CORRECTION 0; 0; 270

Connections:
B+: BT1.1 (+), C2.2, J3.1, Q1.3 (D), R2.1, U1.5 (BAT)
B-: BT1.2 (-), C3.1, J4.1, U2.2 (GND)
BATVDD: C3.2, R2.2, U2.3 (VDD)
GND: C1.2, C2.1, J0.A12 (GND), J0.B12 (GND), J0.S1 (SHIELD), J2.1, J6.1, R1.2, RN1.1 (R1.1), RN2.3 (R3.1), RN2.4 (R4.1), RN2.5 (R4.2), RN2.6 (R3.2), RN2.7 (R2.2), RN2.8 (R1.2), U1.1 (TEMP), U1.3 (GND), U1.9 (EP), U2.4 (VM), U2.5 (VM)
unnamed: J0.A5 (CC1), RN2.2 (R2.1)
unnamed: J0.B5 (CC2), RN2.1 (R1.1)
unnamed: LED1.1 (K), U1.7 (~CHRG)
unnamed: LED1.2 (A), RN1.3 (R3.1)
unnamed: LED2.1 (K), U1.6 (~STDBY)
unnamed: LED2.2 (A), RN1.2 (R2.1)
unnamed: R1.1, U1.2 (PROG)
VIN: C1.1, D3.2 (A), J0.A9 (VBUS), J0.B9 (VBUS), J1.1, Q1.1 (G), RN1.6 (R3.2), RN1.7 (R2.2), RN1.8 (R1.2), U1.4 (VCC), U1.8 (CE)
VOUT: D3.1 (K), J5.1, Q1.2 (S)

Notes on the sheet:
Header pins
Battery protection circuit
USB-C Power input
Load sharing circuit
Battery charger
CERN-OHL-P v2
