smkent/pcb/dev/stackable/esp-sensors/esp-sensors.kicad_sch

## KiCad design dev/stackable/esp-sensors/esp-sensors.kicad_sch (2024-11-30)

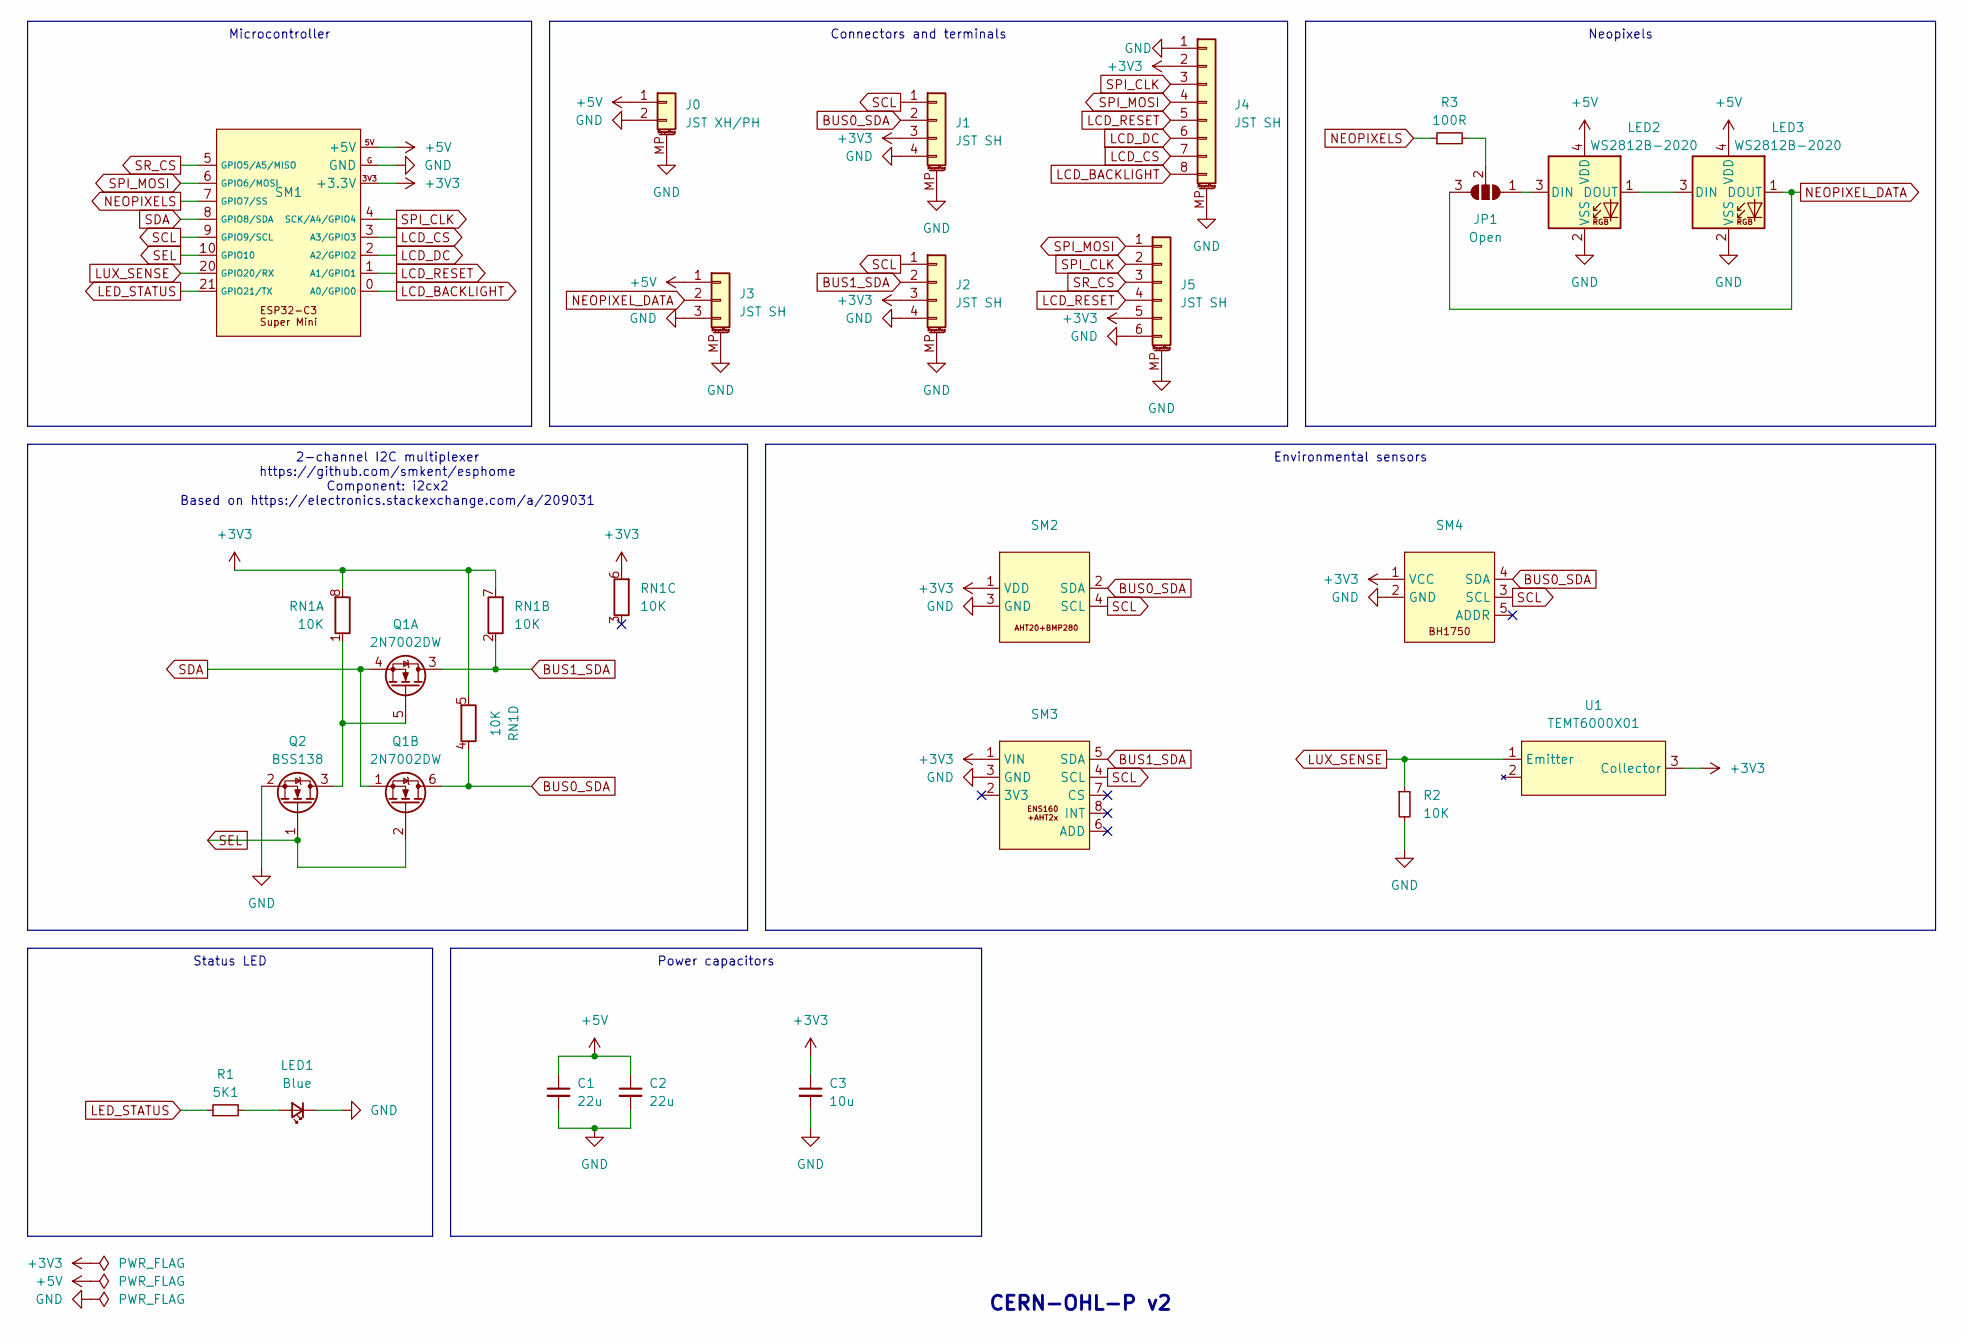
[picture p212: schematic esp-sensors.kicad_sch]

Parts:
C1, C2: 22u; C_0805_2012Metric_Pad1.18x1.45mm_HandSolder
C3: 10u; C_0603_1608Metric_Pad1.08x0.95mm_HandSolder
J0: JST XH/PH; Conn_Combo_JST-1x02-XH_PH-SMD-pad2gnd
J1, J2: JST SH; JST_SH_SM04B-SRSS-TB_1x04-1MP_P1.00mm_Horizontal
J3: JST SH; JST_SH_SM03B-SRSS-TB_1x03-1MP_P1.00mm_Horizontal
J4: JST SH; JST_SH_SM08B-SRSS-TB_1x08-1MP_P1.00mm_Horizontal
J5: JST SH; JST_SH_SM06B-SRSS-TB_1x06-1MP_P1.00mm_Horizontal
JP1: Open; SolderJumper-3_P1.3mm_Open_RoundedPad1.0x1.5mm
LED1: Blue; LED_0603_1608Metric_Pad1.05x0.95mm_HandSolder_simple
LED2, LED3: WS2812B-2020; LED-SMD_4P-L2.0-W2.0-BR-1
Q1: 2N7002DW; SOT-23-6; LCSC Part C5190214
Q2: BSS138; SOT-23
R1: 5K1; R_0603_1608Metric_Pad0.98x0.95mm_HandSolder_simple
R2: 10K; R_0603_1608Metric_Pad0.98x0.95mm_HandSolder_simple
R3: 100R; R_0603_1608Metric_Pad0.98x0.95mm_HandSolder
RN1: 10K; R_Array_Convex_4x0603
SM1: ESP32-C3-Super-Mini-Castellated-SMD
SM2: PinSocket_1x04_P2.54mm_Horizontal_descending_simple
SM3: PinSocket_1x08_P2.54mm_Horizontal_descending_simple
SM4: PinSocket_1x05_P2.54mm_Horizontal_simple
U1: TEMT6000X01; SENSORS-SMD_TEMT6000X01_HandSolder; LCSC Part C94098

Connections:
+3V3: C3.1, J1.3, J2.3, J4.2, J5.5, RN1.5 (R4.2), RN1.6 (R3.2), RN1.7 (R2.2), RN1.8 (R1.2), SM1.3V3 (+3.3V), SM2.1 (VDD), SM3.1 (VIN), SM4.1 (VCC), U1.3 (Collector)
+5V: C1.1, C2.1, J0.1, J3.1, LED2.4 (VDD), LED3.4 (VDD), SM1.5V (+5V)
BUS0_SDA: J1.2, Q1.6 (D), RN1.4 (R4.1), SM2.2 (SDA), SM4.4 (SDA)
BUS1_SDA: J2.2, Q1.3 (D), RN1.2 (R2.1), SM3.5 (SDA)
GND: C1.2, C2.2, C3.2, J0.2, J0.MP (MountPin), J1.4, J1.MP (MountPin), J2.4, J2.MP (MountPin), J3.3, J3.MP (MountPin), J4.1, J4.MP (MountPin), J5.6, J5.MP (MountPin), LED1.1 (K), LED2.2 (VSS), LED3.2 (VSS), Q2.2 (S), R2.2, SM1.G (GND), SM2.3 (GND), SM3.3 (GND), SM4.2 (GND)
LCD_BACKLIGHT: J4.8, SM1.0 (A0/GPIO0)
LCD_CS: J4.7, SM1.3 (A3/GPIO3)
LCD_DC: J4.6, SM1.2 (A2/GPIO2)
LCD_RESET: J4.5, J5.4, SM1.1 (A1/GPIO1)
LED_STATUS: R1.1, SM1.21 (GPIO21/TX)
LUX_SENSE: R2.1, SM1.20 (GPIO20/RX), U1.1 (Emitter)
NEOPIXELS: R3.1, SM1.7 (GPIO7/SS)
NEOPIXEL_DATA: J3.2, JP1.3 (B), LED3.1 (DOUT)
unnamed: JP1.1 (A), LED2.3 (DIN)
unnamed: JP1.2 (C), R3.2
unnamed: LED1.2 (A), R1.2
unnamed: LED2.1 (DOUT), LED3.3 (DIN)
unnamed: Q1.5 (G), Q2.3 (D), RN1.1 (R1.1)
SCL: J1.1, J2.1, SM1.9 (GPIO9/SCL), SM2.4 (SCL), SM3.4 (SCL), SM4.3 (SCL)
SDA: Q1.1 (S), Q1.4 (S), SM1.8 (GPIO8/SDA)
SEL: Q1.2 (G), Q2.1 (G), SM1.10 (GPIO10)
SPI_CLK: J4.3, J5.2, SM1.4 (SCK/A4/GPIO4)
SPI_MOSI: J4.4, J5.1, SM1.6 (GPIO6/MOSI)
SR_CS: J5.3, SM1.5 (GPIO5/A5/MISO)

Notes on the sheet:
2-channel I2C multiplexer https://github.com/smkent/esphome Component: i2cx2 Based on https://electronics.stackexchange.com/a/209031
Environmental sensors
Microcontroller
Power capacitors
Neopixels
Status LED
Connectors and terminals
CERN-OHL-P v2
