smkent/pcb/dev/stackable/power-18650-holder/power-18650-holder.kicad_sch

## KiCad design dev/stackable/power-18650-holder/power-18650-holder.kicad_sch (2024-09-15)

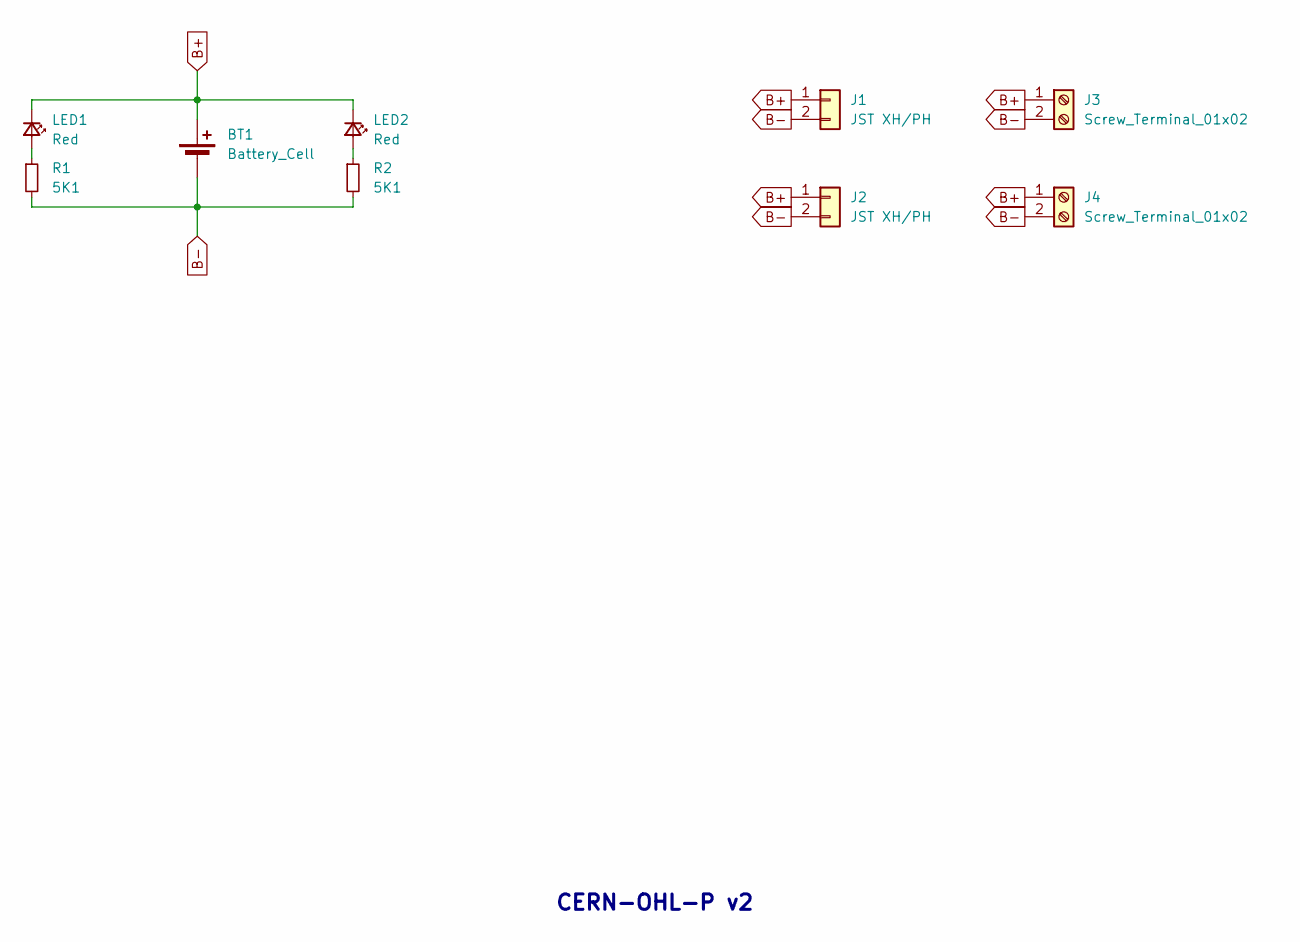
[picture p213: schematic power-18650-holder.kicad_sch]

Parts:
BT1: Battery_Cell; BAT-TH_18650-A5BJ001_large_vias
J1, J2: JST XH/PH; Conn_Combo_JST-1x02-XH_PH-THT-pad2gnd
J3, J4: Screw_Terminal_01x02; Conn_Combo_TerminalBlock_P3.5-P5.08_1x02_pad2gnd
LED1, LED2: Red; LED_0603_1608Metric_Pad1.05x0.95mm_HandSolder_simple; LCSC Part C2286
R1, R2: 5K1; R_0603_1608Metric_Pad0.98x0.95mm_HandSolder_simple; LCSC Part C25905

Connections:
B+: BT1.1 (+), J1.1, J2.1, J3.1, J4.1, LED1.1 (K), LED2.1 (K)
B-: BT1.2 (-), J1.2, J2.2, J3.2, J4.2, R1.2, R2.2
unnamed: LED1.2 (A), R1.1
unnamed: LED2.2 (A), R2.1

Notes on the sheet:
CERN-OHL-P v2
