smkent/pcb/dev/stackable/power-eta6003-5v-ups/connectors.kicad_sch

## KiCad design dev/stackable/power-eta6003-5v-ups/connectors.kicad_sch (2024-11-30)

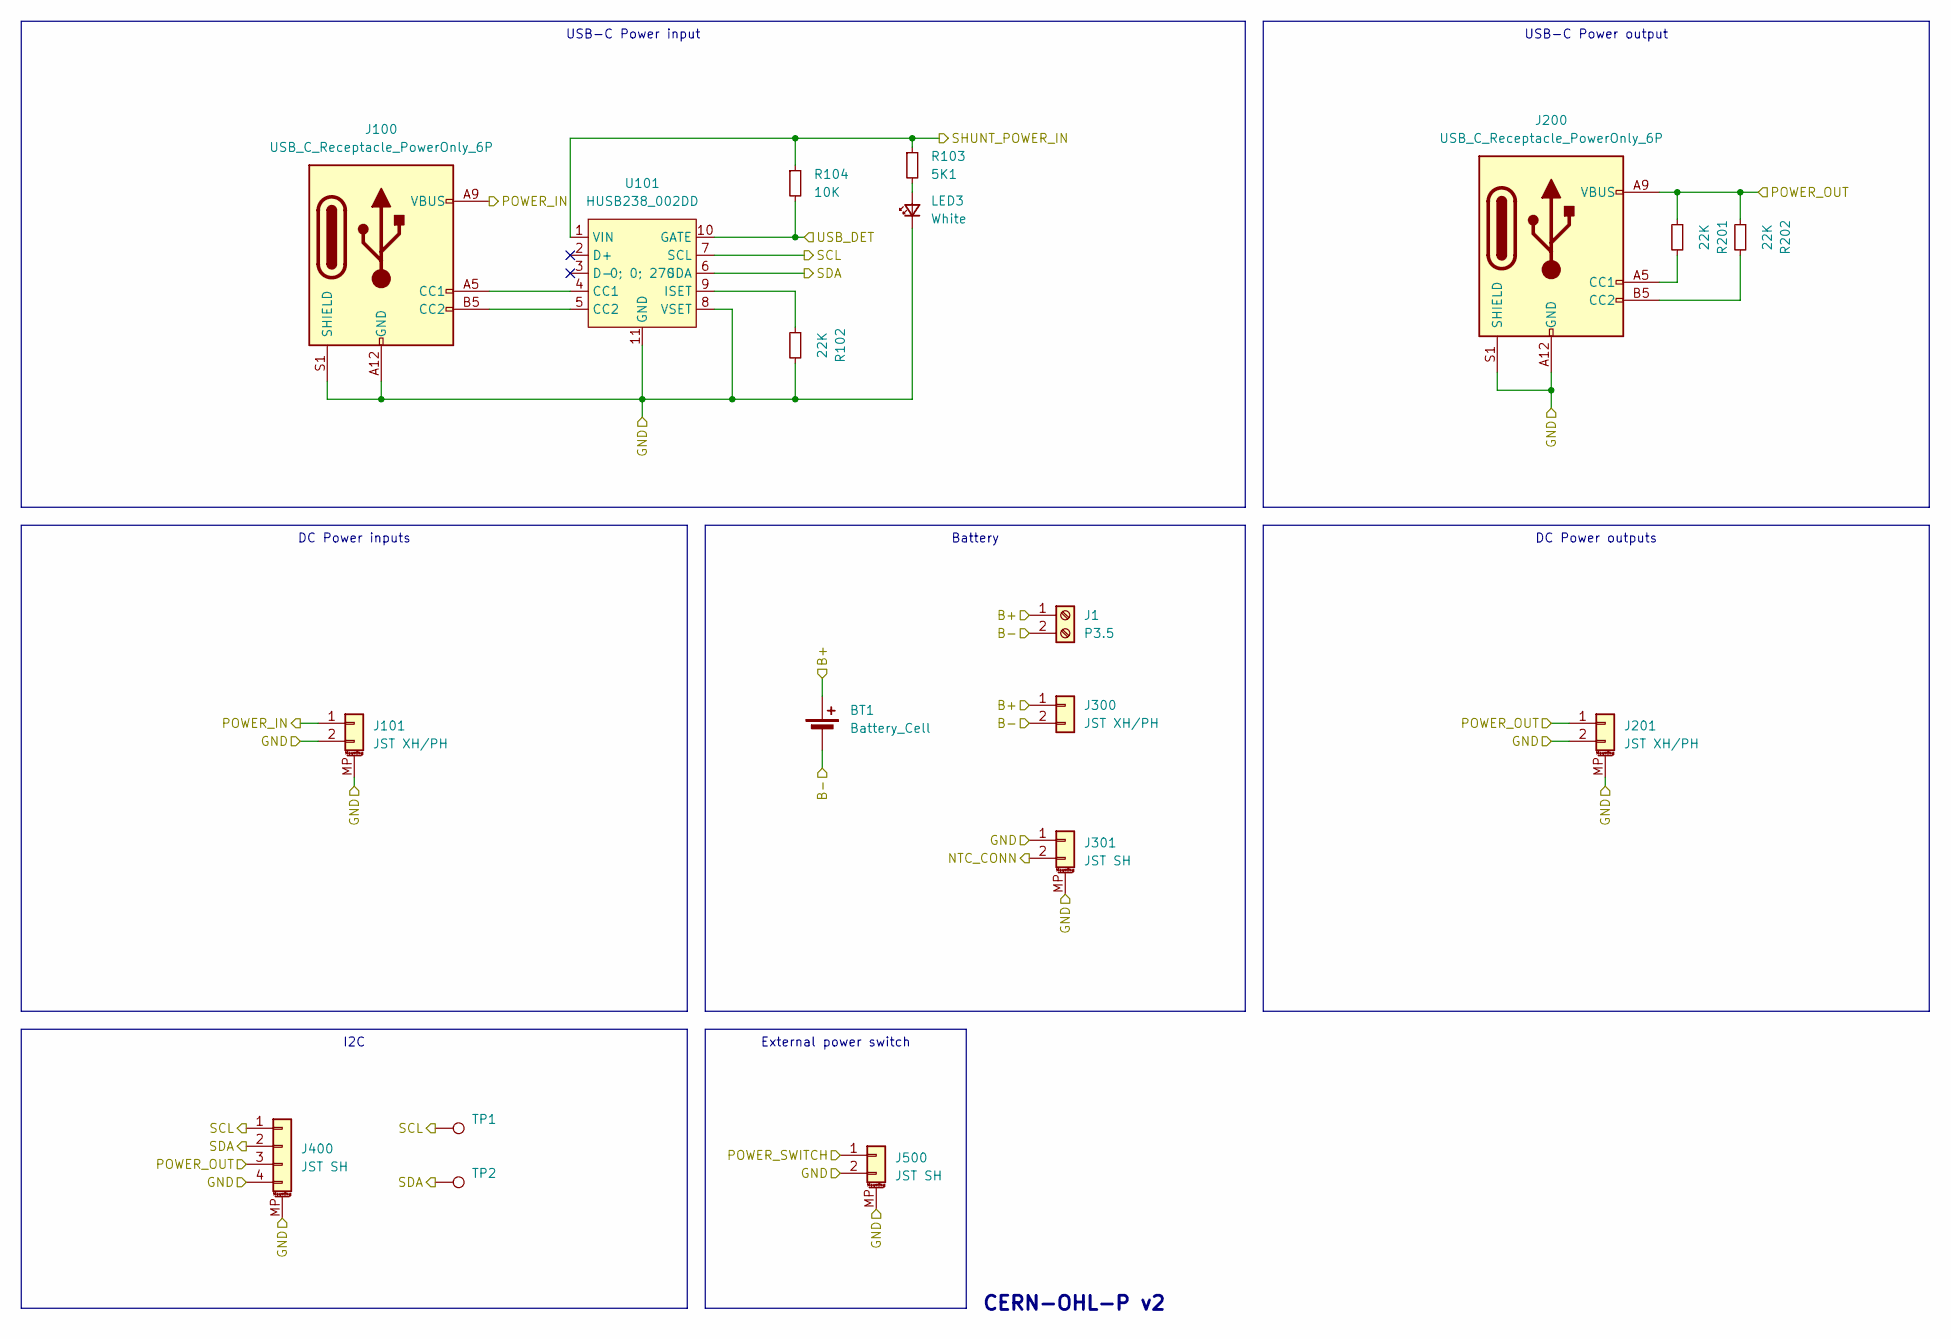
[picture p214: schematic connectors.kicad_sch]

Parts:
BT1: Battery_Cell; BAT-TH_18650-A5BJ001
J1: P3.5; TerminalBlock_Phoenix_PT-1,5-2-3.5-H_1x02_P3.50mm_Horizonta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
J100, J200: USB_C_Receptacle_PowerOnly_6P; USB_C_Receptacle_GCT_USB4125-xx-x_6P_TopMnt_Horizontal_hand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; LCSC Part C2927029
J101, J201: JST XH/PH; Conn_Combo_JST-1x02-XH_PH-SMD-alt-pad2gnd
J300: JST XH/PH; Conn_Combo_JST-1x02-XH_PH-THT-pad2gnd
J301, J500: JST SH; JST_SH_SM02B-SRSS-TB_1x02-1MP_P1.00mm_Horizontal; LCSC Part C7433423
J400: JST SH; JST_SH_SM04B-SRSS-TB_1x04-1MP_P1.00mm_Horizontal; LCSC Part C7433425
LED3: White; LED_0603_1608Metric_Pad1.05x0.95mm_HandSolder_simple
R102, R201, R202: 22K; R_0603_1608Metric_Pad0.98x0.95mm_HandSolder; LCSC Part C31850
R103: 5K1; R_0402_1005Metric_simple; LCSC Part C25905
R104: 10K; R_0402_1005Metric_simple; LCSC Part C25744
TP1, TP2: TestPoint_Pad_D1.5mm
U101: HUSB238_002DD; WDFN-10-1EP_3x3mm_P0.5mm_EP1.8x2.5mm_ThermalVias_half; LCSC Part C7471904

Connections:
B+: BT1.1 (+), J1.1, J300.1
B-: BT1.2 (-), J1.2, J300.2
GND: J100.A12 (GND), J100.B12 (GND), J100.S1 (SHIELD), J101.2, J101.MP (MountPin), J200.A12 (GND), J200.B12 (GND), J200.S1 (SHIELD), J201.2, J201.MP (MountPin), J301.1, J301.MP (MountPin), J400.4, J400.MP (MountPin), J500.2, J500.MP (MountPin), LED3.1 (K), R102.2, U101.8 (VSET), U101.11 (GND)
NTC_CONN: J301.2
unnamed: J100.A5 (CC1), U101.4 (CC1)
unnamed: J100.B5 (CC2), U101.5 (CC2)
unnamed: J200.A5 (CC1), R201.2
unnamed: J200.B5 (CC2), R202.2
unnamed: LED3.2 (A), R103.2
unnamed: R102.1, U101.9 (ISET)
POWER_IN: J100.A9 (VBUS), J100.B9 (VBUS), J101.1
POWER_OUT: J200.A9 (VBUS), J200.B9 (VBUS), J201.1, J400.3, R201.1, R202.1
POWER_SWITCH: J500.1
SCL: J400.1, TP1.1, U101.7 (SCL)
SDA: J400.2, TP2.1, U101.6 (SDA)
SHUNT_POWER_IN: R103.1, R104.1, U101.1 (VIN)
USB_DET: R104.2, U101.10 (GATE)

Notes on the sheet:
DC Power outputs
USB-C Power output
DC Power inputs
I2C
USB-C Power input
Battery
External power switch
CERN-OHL-P v2
