smkent/pcb/dev/stackable/relay-module-5v-half/relay-module-5v-half.kicad_sch

## KiCad design dev/stackable/relay-module-5v-half/relay-module-5v-half.kicad_sch (2024-11-30)

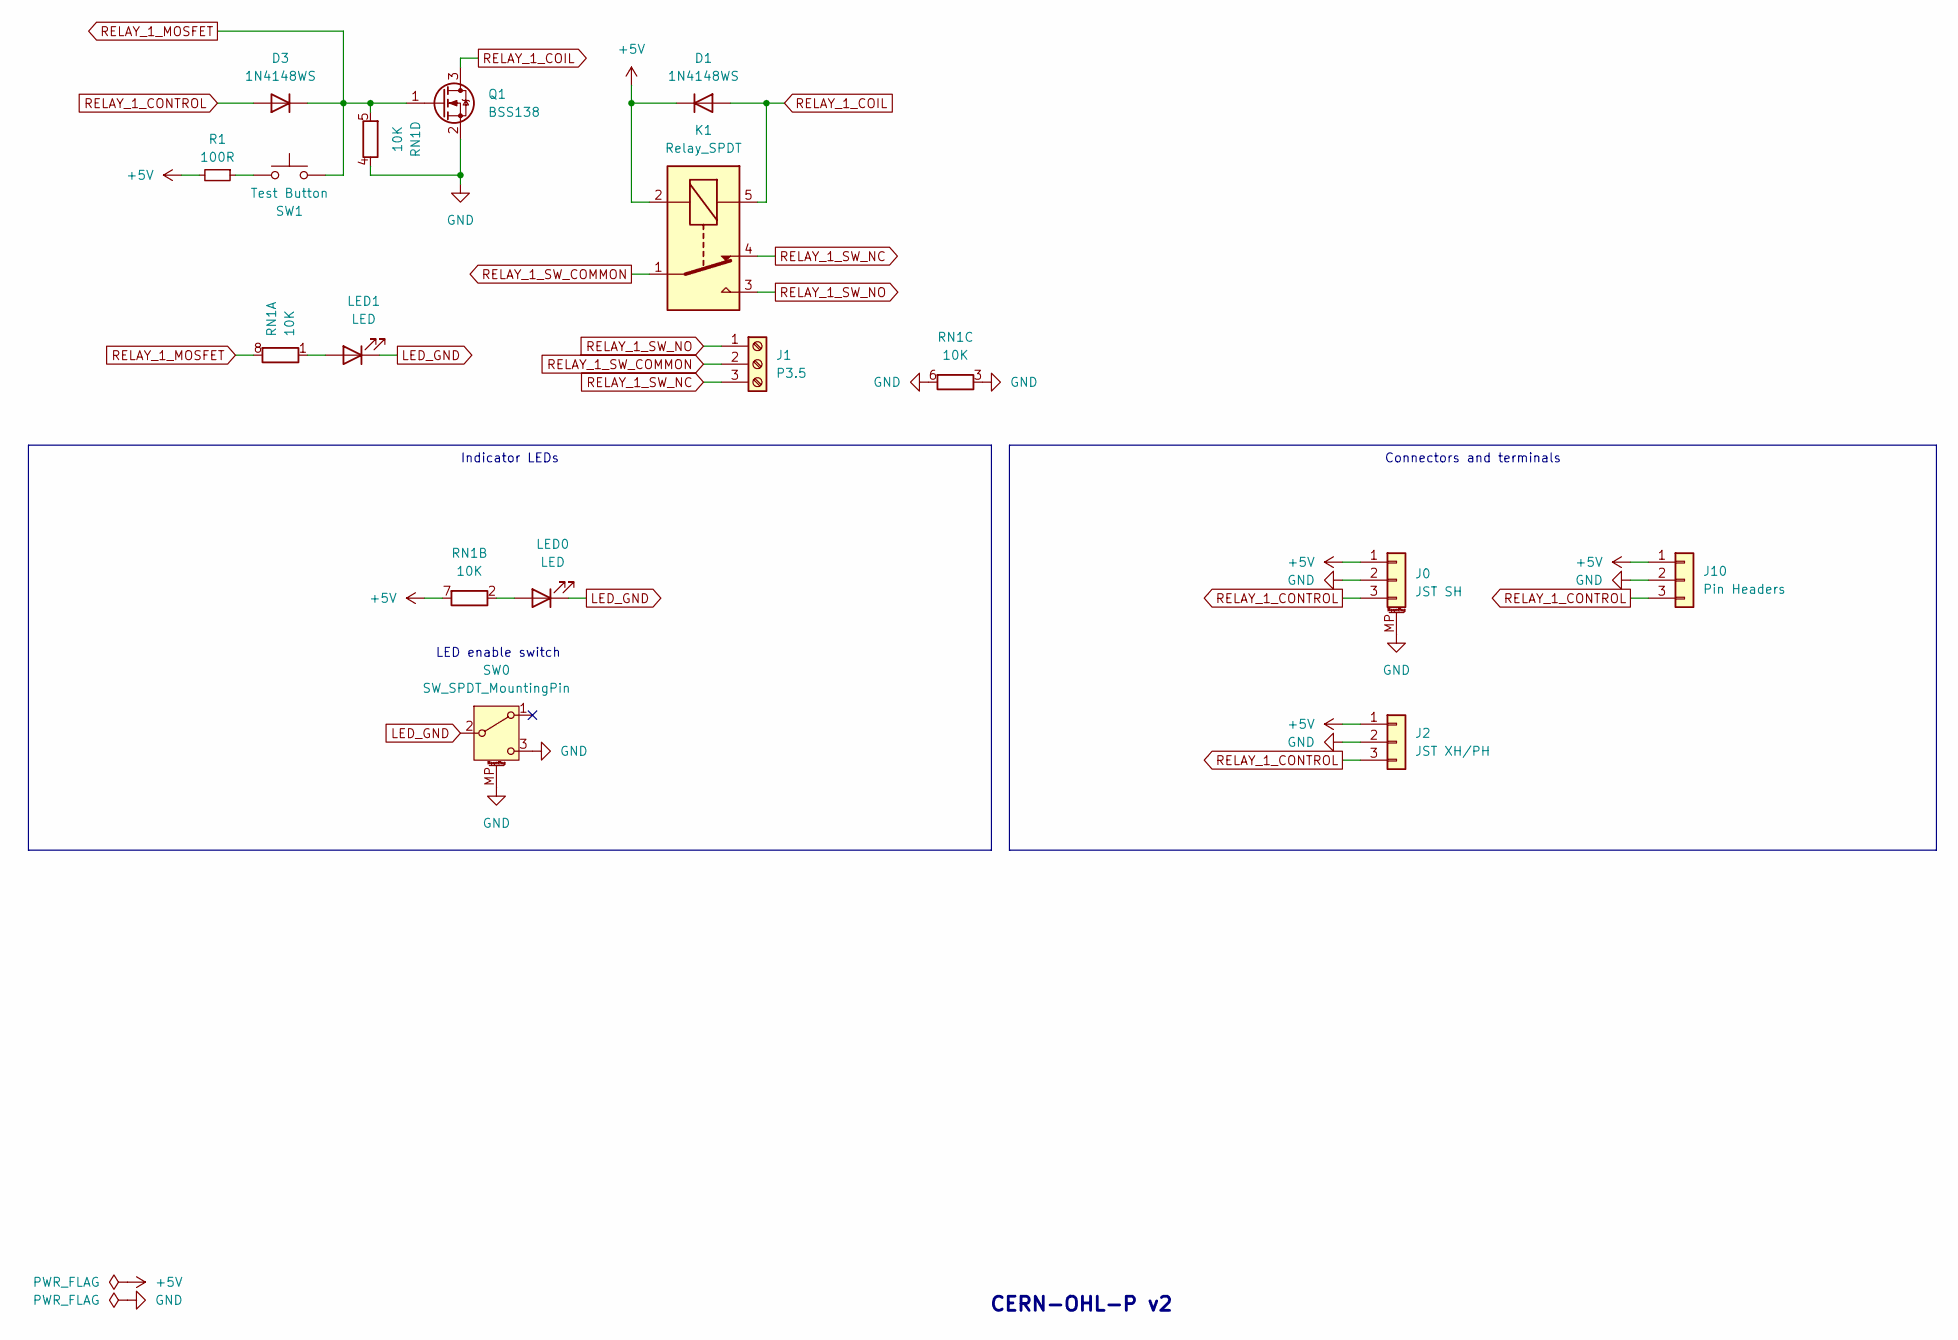
[picture p215: schematic relay-module-5v-half.kicad_sch]

Parts:
D1, D3: 1N4148WS; D_SOD-323_HandSoldering_simple
J0: JST SH; JST_SH_SM03B-SRSS-TB_1x03-1MP_P1.00mm_Horizontal
J1: P3.5; Conn_Combo_TerminalBlock_P3.5_JST-XH_PH_1x03
J2: JST XH/PH; Conn_Combo_JST-1x03-XH_PH-THT_pad2gnd
J10: Pin Headers; PinHeader_1x03_P2.54mm_Vertical_simple_pad2gnd
K1: Relay_SPDT; Relay_SPDT_SANYOU_SRD_Series_Form_C
LED0, LED1: LED; LED_0805_2012Metric_Pad1.15x1.40mm_HandSolder_simple
Q1: BSS138; SOT-23_simple
R1: 100R; R_0805_2012Metric_Pad1.20x1.40mm_HandSolder
RN1: 10K; R_Array_Convex_4x0603
SW0: SW_SPDT_MountingPin; SW-SMD_3P-P1.50_L2.7-W6.6
SW1: Test Button; SW-SMD_BZCN_TSA002A35XXX

Connections:
+5V: D1.1 (K), J0.1, J2.1, J10.1, K1.2, R1.2, RN1.7 (R2.2)
GND: J0.2, J0.MP (MountPin), J2.2, J10.2, Q1.2 (S), RN1.3 (R3.1), RN1.4 (R4.1), RN1.6 (R3.2), SW0.3 (C), SW0.MP (MountPin)
LED_GND: LED0.1 (K), LED1.1 (K), SW0.2 (B)
unnamed: LED0.2 (A), RN1.2 (R2.1)
unnamed: LED1.2 (A), RN1.1 (R1.1)
unnamed: R1.1, SW1.2
RELAY_1_COIL: D1.2 (A), K1.5, Q1.3 (D)
RELAY_1_CONTROL: D3.2 (A), J0.3, J2.3, J10.3
RELAY_1_MOSFET: D3.1 (K), Q1.1 (G), RN1.5 (R4.2), RN1.8 (R1.2), SW1.1
RELAY_1_SW_COMMON: J1.2, K1.1
RELAY_1_SW_NC: J1.3, K1.4
RELAY_1_SW_NO: J1.1, K1.3

Notes on the sheet:
Indicator LEDs
Connectors and terminals
CERN-OHL-P v2
LED enable switch
