smkent/pcb/dev/stackable/shift-register-ring/shift-register-ring.kicad_sch

## KiCad design dev/stackable/shift-register-ring/shift-register-ring.kicad_sch (2024-11-30)

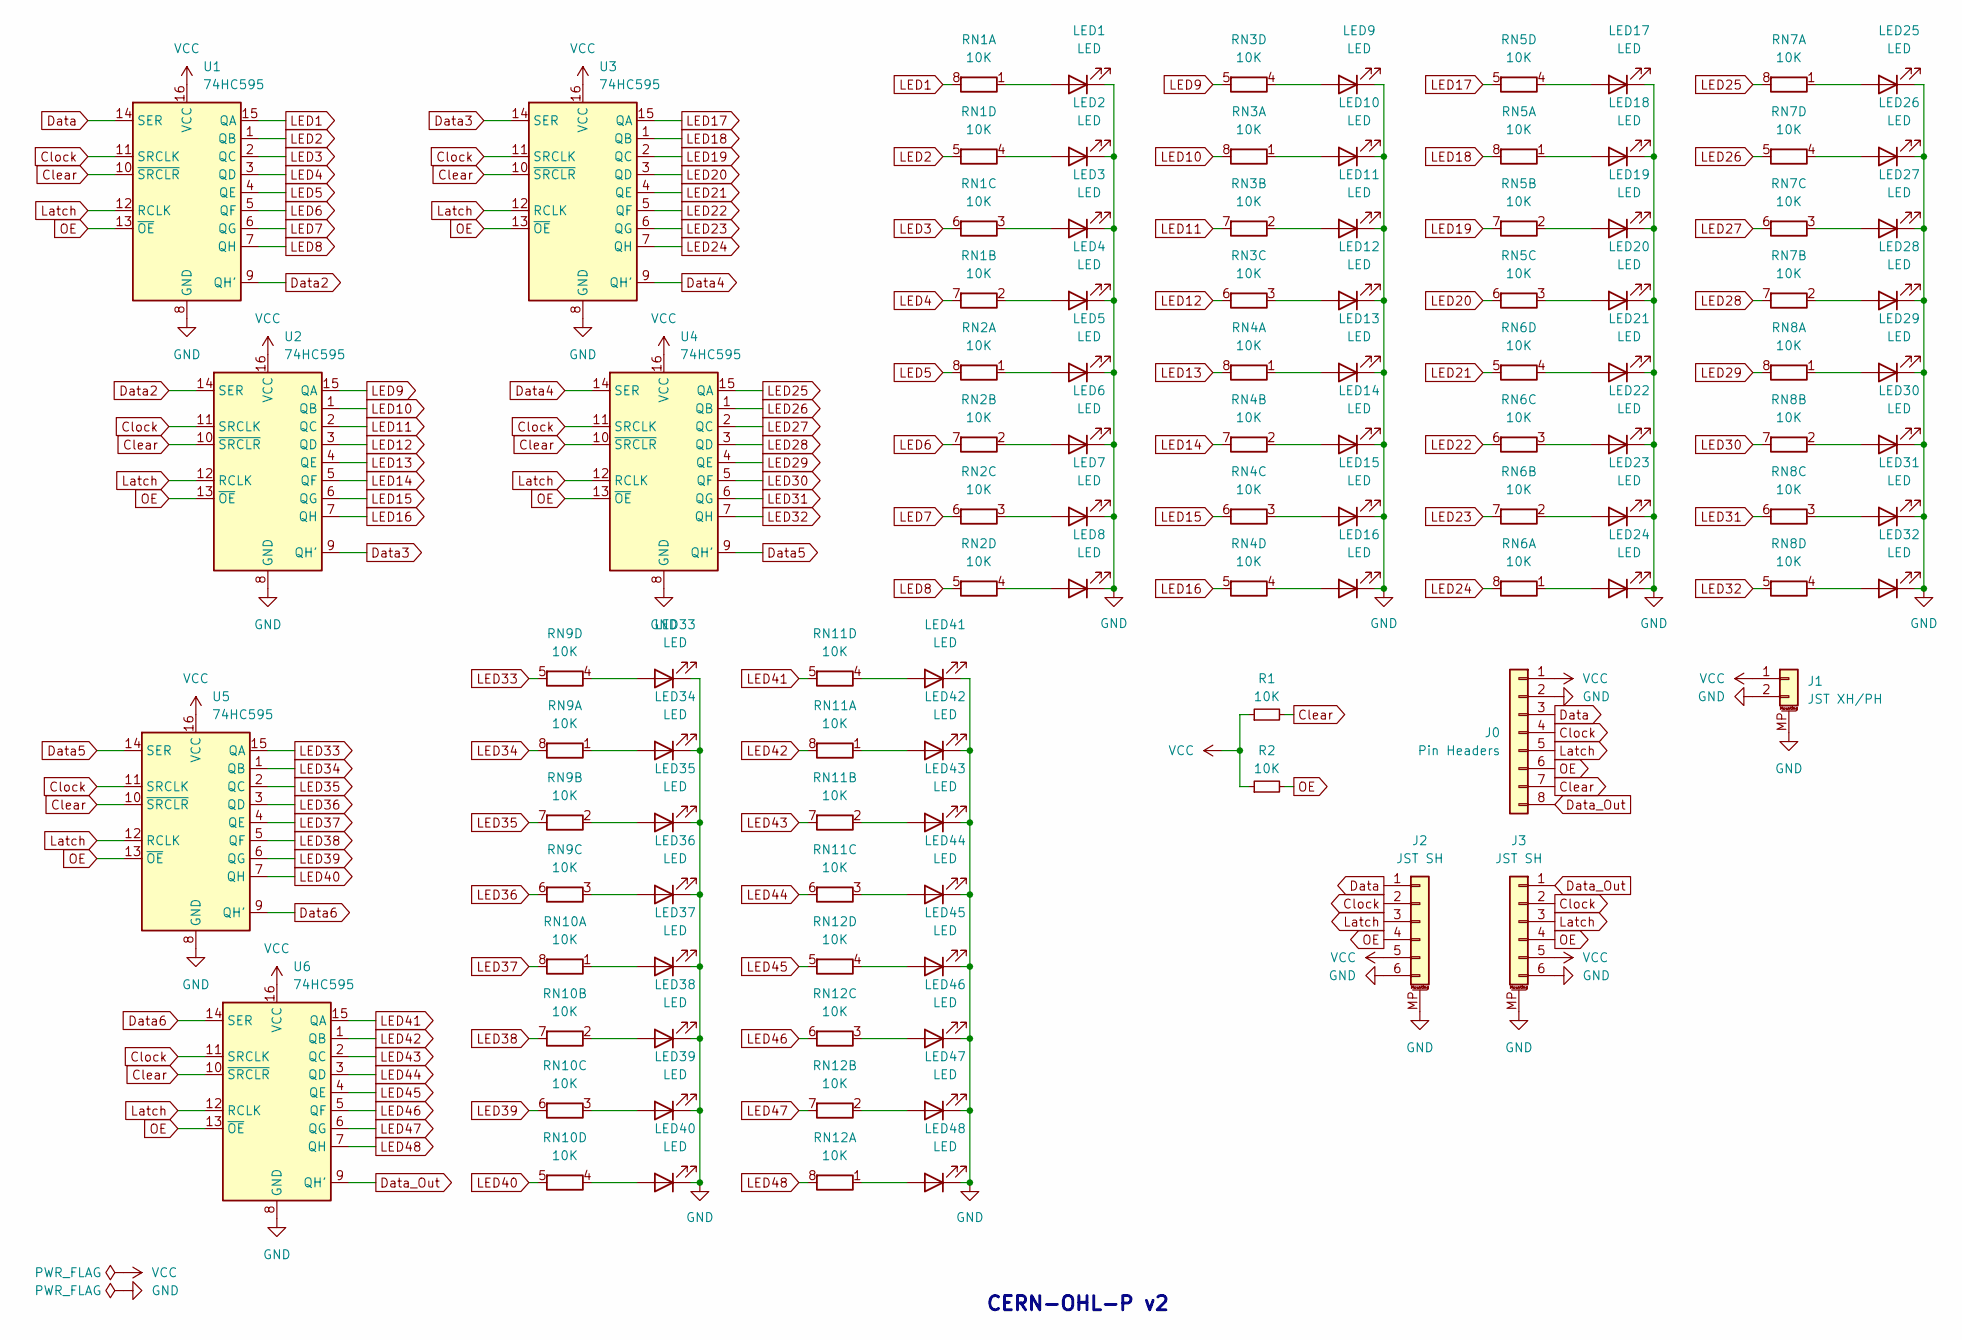
[picture p216: schematic shift-register-ring.kicad_sch]

Parts:
J0: Pin Headers; PinHeader_1x08_P2.54mm_Vertical_simple_pad2gnd
J1: JST XH/PH; Conn_Combo_JST-1x02-XH_PH-SMD-pad2gnd
J2, J3: JST SH; JST_SH_SM06B-SRSS-TB_1x06-1MP_P1.00mm_Horizontal
LED1, LED2, LED3, LED4, LED5, LED6, LED7, LED8, LED9, LED10, LED11, LED12, LED13, LED14, LED15, LED16, LED17, LED18, LED19, LED20, LED21, LED22, LED23, LED24, LED25, LED26, LED27, LED28, LED29, LED30, LED31, LED32, LED33, LED34, LED35, LED36, LED37, LED38, LED39, LED40, LED41, LED42, LED43, LED44, LED45, LED46, LED47, LED48: LED; LED_0603_1608Metric_Pad1.05x0.95mm_HandSolder_simple
R1, R2: 10K; R_0603_1608Metric_Pad0.98x0.95mm_HandSolder
RN1, RN2, RN3, RN4, RN5, RN6, RN7, RN8, RN9, RN10, RN11, RN12: 10K; R_Array_Convex_4x0603
U1, U2, U3, U4, U5, U6: 74HC595; SOIC-16_3.9x9.9mm_P1.27mm

Connections:
Clear: J0.7, R1.2, U1.10 (~SRCLR), U2.10 (~SRCLR), U3.10 (~SRCLR), U4.10 (~SRCLR), U5.10 (~SRCLR), U6.10 (~SRCLR)
Clock: J0.4, J2.2, J3.2, U1.11 (SRCLK), U2.11 (SRCLK), U3.11 (SRCLK), U4.11 (SRCLK), U5.11 (SRCLK), U6.11 (SRCLK)
Data: J0.3, J2.1, U1.14 (SER)
Data2: U1.9 (QH'), U2.14 (SER)
Data3: U2.9 (QH'), U3.14 (SER)
Data4: U3.9 (QH'), U4.14 (SER)
Data5: U4.9 (QH'), U5.14 (SER)
Data6: U5.9 (QH'), U6.14 (SER)
Data_Out: J0.8, J3.1, U6.9 (QH')
GND: J0.2, J1.2, J1.MP (MountPin), J2.6, J2.MP (MountPin), J3.6, J3.MP (MountPin), LED1.1 (K), LED2.1 (K), LED3.1 (K), LED4.1 (K), LED5.1 (K), LED6.1 (K), LED7.1 (K), LED8.1 (K), LED9.1 (K), LED10.1 (K), LED11.1 (K), LED12.1 (K), LED13.1 (K), LED14.1 (K), LED15.1 (K), LED16.1 (K), LED17.1 (K), LED18.1 (K), LED19.1 (K), LED20.1 (K), LED21.1 (K), LED22.1 (K), LED23.1 (K), LED24.1 (K), LED25.1 (K), LED26.1 (K), LED27.1 (K), LED28.1 (K), LED29.1 (K), LED30.1 (K), LED31.1 (K), LED32.1 (K), LED33.1 (K), LED34.1 (K), LED35.1 (K), LED36.1 (K), LED37.1 (K), LED38.1 (K), LED39.1 (K), LED40.1 (K), LED41.1 (K), LED42.1 (K), LED43.1 (K), LED44.1 (K), LED45.1 (K), LED46.1 (K), LED47.1 (K), LED48.1 (K), U1.8 (GND), U2.8 (GND), U3.8 (GND), U4.8 (GND), U5.8 (GND), U6.8 (GND)
LED1: RN1.8 (R1.2), U1.15 (QA)
LED2: RN1.5 (R4.2), U1.1 (QB)
LED3: RN1.6 (R3.2), U1.2 (QC)
LED4: RN1.7 (R2.2), U1.3 (QD)
LED5: RN2.8 (R1.2), U1.4 (QE)
LED6: RN2.7 (R2.2), U1.5 (QF)
LED7: RN2.6 (R3.2), U1.6 (QG)
LED8: RN2.5 (R4.2), U1.7 (QH)
LED9: RN3.5 (R4.2), U2.15 (QA)
LED10: RN3.8 (R1.2), U2.1 (QB)
LED11: RN3.7 (R2.2), U2.2 (QC)
LED12: RN3.6 (R3.2), U2.3 (QD)
LED13: RN4.8 (R1.2), U2.4 (QE)
LED14: RN4.7 (R2.2), U2.5 (QF)
LED15: RN4.6 (R3.2), U2.6 (QG)
LED16: RN4.5 (R4.2), U2.7 (QH)
LED17: RN5.5 (R4.2), U3.15 (QA)
LED18: RN5.8 (R1.2), U3.1 (QB)
LED19: RN5.7 (R2.2), U3.2 (QC)
LED20: RN5.6 (R3.2), U3.3 (QD)
LED21: RN6.5 (R4.2), U3.4 (QE)
LED22: RN6.6 (R3.2), U3.5 (QF)
LED23: RN6.7 (R2.2), U3.6 (QG)
LED24: RN6.8 (R1.2), U3.7 (QH)
LED25: RN7.8 (R1.2), U4.15 (QA)
LED26: RN7.5 (R4.2), U4.1 (QB)
LED27: RN7.6 (R3.2), U4.2 (QC)
LED28: RN7.7 (R2.2), U4.3 (QD)
LED29: RN8.8 (R1.2), U4.4 (QE)
LED30: RN8.7 (R2.2), U4.5 (QF)
LED31: RN8.6 (R3.2), U4.6 (QG)
LED32: RN8.5 (R4.2), U4.7 (QH)
LED33: RN9.5 (R4.2), U5.15 (QA)
LED34: RN9.8 (R1.2), U5.1 (QB)
LED35: RN9.7 (R2.2), U5.2 (QC)
LED36: RN9.6 (R3.2), U5.3 (QD)
LED37: RN10.8 (R1.2), U5.4 (QE)
LED38: RN10.7 (R2.2), U5.5 (QF)
LED39: RN10.6 (R3.2), U5.6 (QG)
LED40: RN10.5 (R4.2), U5.7 (QH)
LED41: RN11.5 (R4.2), U6.15 (QA)
LED42: RN11.8 (R1.2), U6.1 (QB)
LED43: RN11.7 (R2.2), U6.2 (QC)
LED44: RN11.6 (R3.2), U6.3 (QD)
LED45: RN12.5 (R4.2), U6.4 (QE)
LED46: RN12.6 (R3.2), U6.5 (QF)
LED47: RN12.7 (R2.2), U6.6 (QG)
LED48: RN12.8 (R1.2), U6.7 (QH)
Latch: J0.5, J2.3, J3.3, U1.12 (RCLK), U2.12 (RCLK), U3.12 (RCLK), U4.12 (RCLK), U5.12 (RCLK), U6.12 (RCLK)
unnamed: LED1.2 (A), RN1.1 (R1.1)
unnamed: LED2.2 (A), RN1.4 (R4.1)
unnamed: LED3.2 (A), RN1.3 (R3.1)
unnamed: LED4.2 (A), RN1.2 (R2.1)
unnamed: LED5.2 (A), RN2.1 (R1.1)
unnamed: LED6.2 (A), RN2.2 (R2.1)
unnamed: LED7.2 (A), RN2.3 (R3.1)
unnamed: LED8.2 (A), RN2.4 (R4.1)
unnamed: LED9.2 (A), RN3.4 (R4.1)
unnamed: LED10.2 (A), RN3.1 (R1.1)
unnamed: LED11.2 (A), RN3.2 (R2.1)
unnamed: LED12.2 (A), RN3.3 (R3.1)
unnamed: LED13.2 (A), RN4.1 (R1.1)
unnamed: LED14.2 (A), RN4.2 (R2.1)
unnamed: LED15.2 (A), RN4.3 (R3.1)
unnamed: LED16.2 (A), RN4.4 (R4.1)
unnamed: LED17.2 (A), RN5.4 (R4.1)
unnamed: LED18.2 (A), RN5.1 (R1.1)
unnamed: LED19.2 (A), RN5.2 (R2.1)
unnamed: LED20.2 (A), RN5.3 (R3.1)
unnamed: LED21.2 (A), RN6.4 (R4.1)
unnamed: LED22.2 (A), RN6.3 (R3.1)
unnamed: LED23.2 (A), RN6.2 (R2.1)
unnamed: LED24.2 (A), RN6.1 (R1.1)
unnamed: LED25.2 (A), RN7.1 (R1.1)
unnamed: LED26.2 (A), RN7.4 (R4.1)
unnamed: LED27.2 (A), RN7.3 (R3.1)
unnamed: LED28.2 (A), RN7.2 (R2.1)
unnamed: LED29.2 (A), RN8.1 (R1.1)
unnamed: LED30.2 (A), RN8.2 (R2.1)
unnamed: LED31.2 (A), RN8.3 (R3.1)
unnamed: LED32.2 (A), RN8.4 (R4.1)
unnamed: LED33.2 (A), RN9.4 (R4.1)
unnamed: LED34.2 (A), RN9.1 (R1.1)
unnamed: LED35.2 (A), RN9.2 (R2.1)
unnamed: LED36.2 (A), RN9.3 (R3.1)
unnamed: LED37.2 (A), RN10.1 (R1.1)
unnamed: LED38.2 (A), RN10.2 (R2.1)
unnamed: LED39.2 (A), RN10.3 (R3.1)
unnamed: LED40.2 (A), RN10.4 (R4.1)
unnamed: LED41.2 (A), RN11.4 (R4.1)
unnamed: LED42.2 (A), RN11.1 (R1.1)
unnamed: LED43.2 (A), RN11.2 (R2.1)
unnamed: LED44.2 (A), RN11.3 (R3.1)
unnamed: LED45.2 (A), RN12.4 (R4.1)
unnamed: LED46.2 (A), RN12.3 (R3.1)
unnamed: LED47.2 (A), RN12.2 (R2.1)
unnamed: LED48.2 (A), RN12.1 (R1.1)
OE: J0.6, J2.4, J3.4, R2.2, U1.13 (~OE), U2.13 (~OE), U3.13 (~OE), U4.13 (~OE), U5.13 (~OE), U6.13 (~OE)
VCC: J0.1, J1.1, J2.5, J3.5, R1.1, R2.1, U1.16 (VCC), U2.16 (VCC), U3.16 (VCC), U4.16 (VCC), U5.16 (VCC), U6.16 (VCC)

Notes on the sheet:
CERN-OHL-P v2
