smkent/pcb/pcb/esphome/garage-door-control/garage-door-control.kicad_sch

## KiCad design pcb/esphome/garage-door-control/garage-door-control.kicad_sch (2024-12-18)

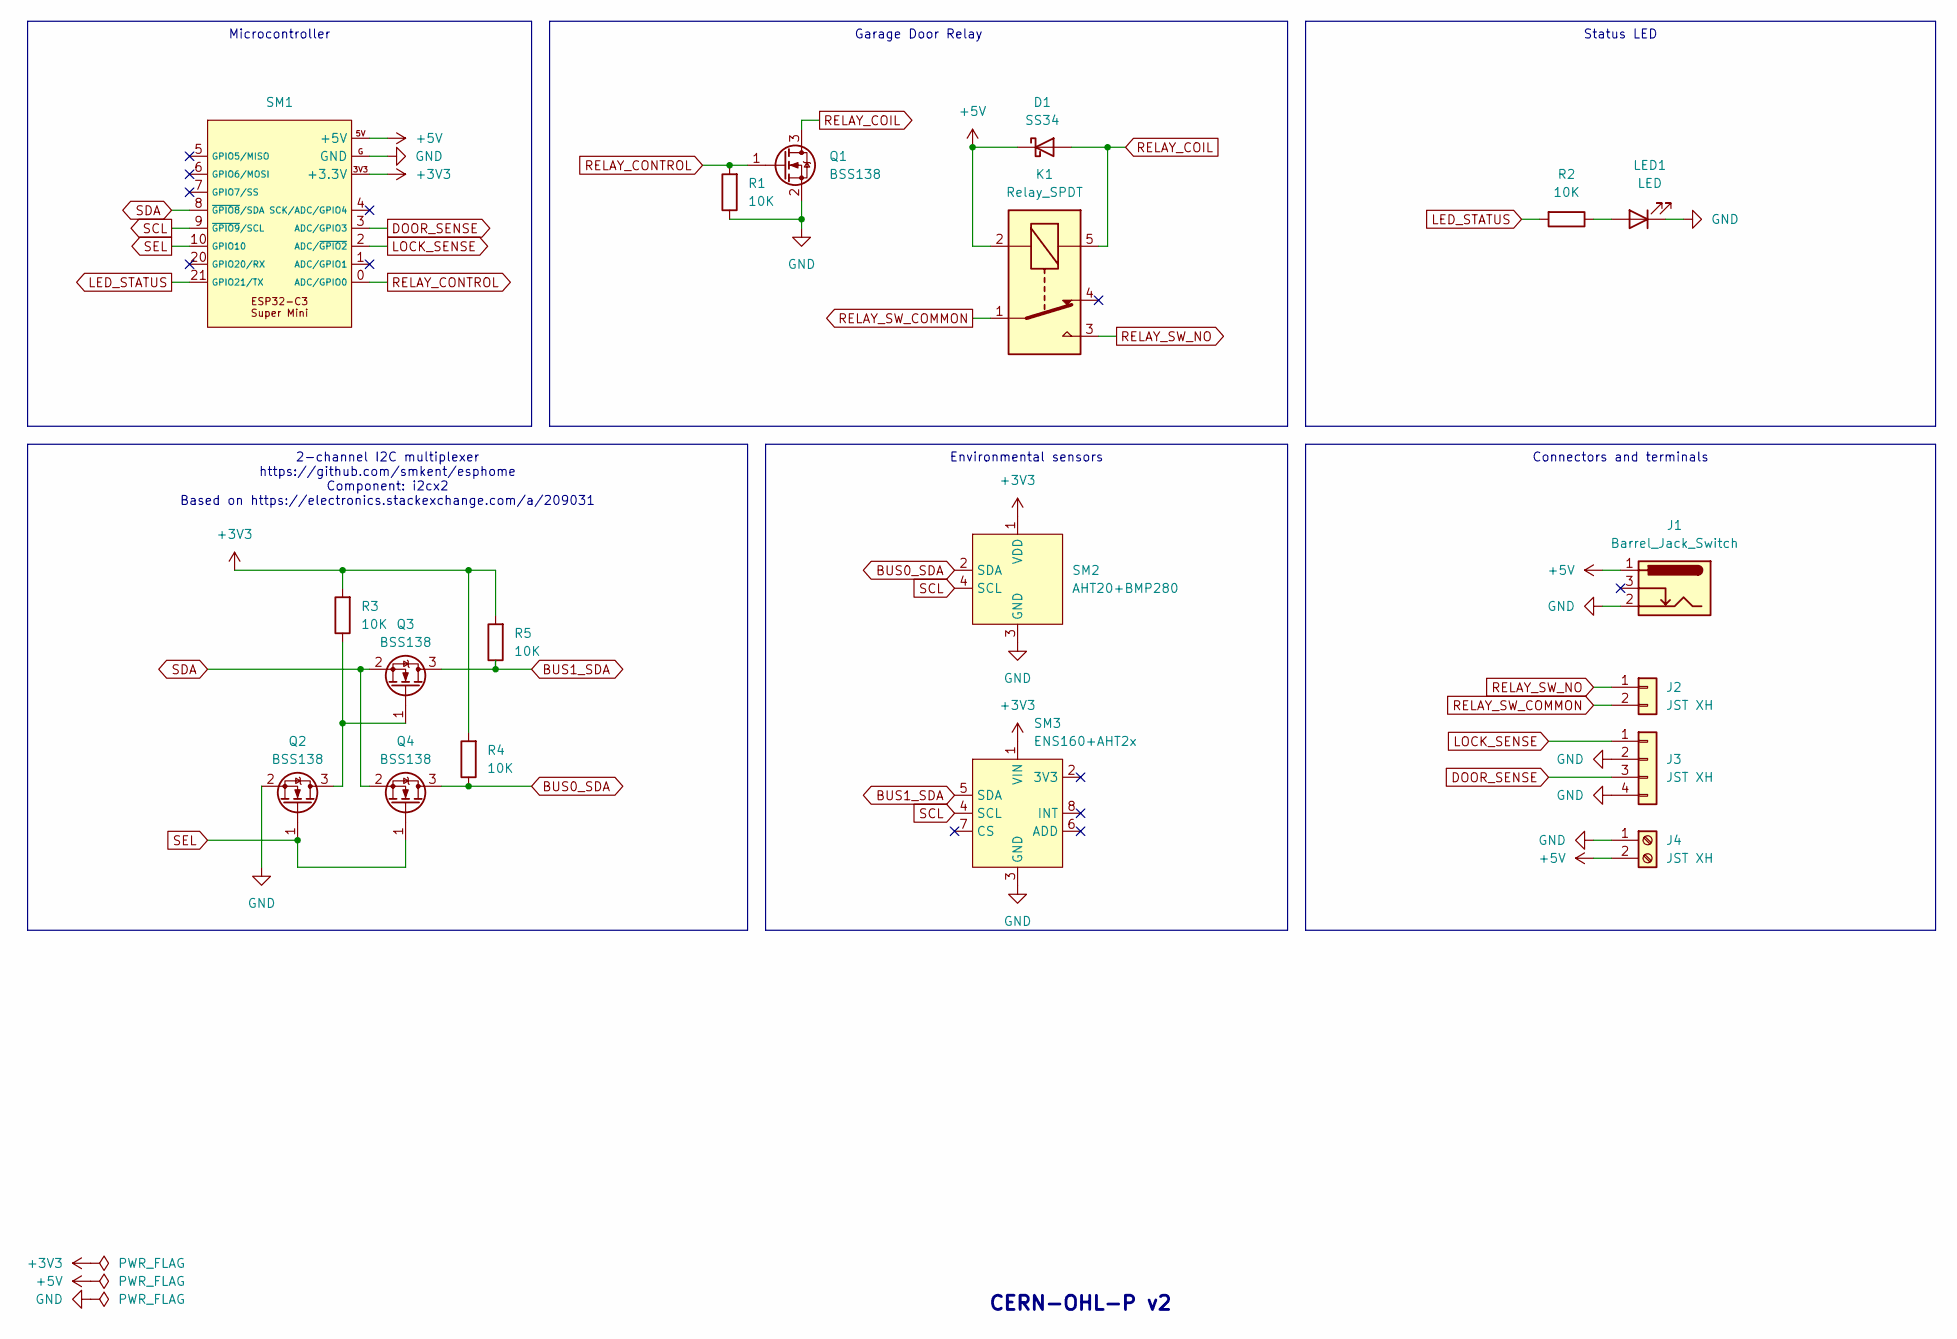
[picture p217: schematic garage-door-control.kicad_sch]

Parts:
D1: SS34; D_SMA
J1: Barrel_Jack_Switch; BarrelJack_DC-050_SMT_Horizontal
J2: JST XH; JST_XH_B2B-XH-A_1x02_P2.50mm_Vertical
J3: JST XH; JST_XH_B4B-XH-A_1x04_P2.50mm_Vertical
J4: JST XH; TerminalBlock_Phoenix_MKDS-1,5-2-5.08_1x02_P5.08mm_Horizont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
K1: Relay_SPDT; Relay_SPDT_SANYOU_SRD_Series_Form_C
LED1: LED; LED_0805_2012Metric_Pad1.15x1.40mm_HandSolder_simple
Q1, Q2, Q3, Q4: BSS138; SOT-23
R1, R2, R3, R4, R5: 10K; R_0805_2012Metric_Pad1.20x1.40mm_HandSolder
SM1: ESP32-C3-Super-Mini-Pins
SM2: AHT20+BMP280; AHT20+BMP280-noholes
SM3: ENS160+AHT2x; ENS160+AHT2x-noholes

Connections:
+3V3: R3.2, R4.2, R5.2, SM1.3V3 (+3.3V), SM2.1 (VDD), SM3.1 (VIN)
+5V: D1.1 (K), J1.1, J4.2, K1.2, SM1.5V (+5V)
BUS0_SDA: Q4.3 (D), R4.1, SM2.2 (SDA)
BUS1_SDA: Q3.3 (D), R5.1, SM3.5 (SDA)
DOOR_SENSE: J3.3, SM1.3 (ADC/GPIO3)
GND: J1.2, J3.2, J3.4, J4.1, LED1.1 (K), Q1.2 (S), Q2.2 (S), R1.1, SM1.G (GND), SM2.3 (GND), SM3.3 (GND)
LED_STATUS: R2.2, SM1.21 (GPIO21/TX)
LOCK_SENSE: J3.1, SM1.2 (ADC/~GPIO2)
unnamed: LED1.2 (A), R2.1
unnamed: Q2.3 (D), Q3.1 (G), R3.1
RELAY_COIL: D1.2 (A), K1.5, Q1.3 (D)
RELAY_CONTROL: Q1.1 (G), R1.2, SM1.0 (ADC/GPIO0)
RELAY_SW_COMMON: J2.2, K1.1
RELAY_SW_NO: J2.1, K1.3
SCL: SM1.9 (~GPIO9/SCL), SM2.4 (SCL), SM3.4 (SCL)
SDA: Q3.2 (S), Q4.2 (S), SM1.8 (~GPIO8/SDA)
SEL: Q2.1 (G), Q4.1 (G), SM1.10 (GPIO10)

Notes on the sheet:
Garage Door Relay
2-channel I2C multiplexer https://github.com/smkent/esphome Component: i2cx2 Based on https://electronics.stackexchange.com/a/209031
Environmental sensors
Microcontroller
Status LED
Connectors and terminals
CERN-OHL-P v2
