smkent/pcb/pcb/stackable3/_template/{{ cookiecutter.project_name }}/{{ cookiecutter.project_name }}.kicad_sch

## KiCad design pcb/stackable3/_template/{{ cookiecutter.project_name }}/{{ cookiecutter.project_name }}.kicad_sch (2025-03-19)

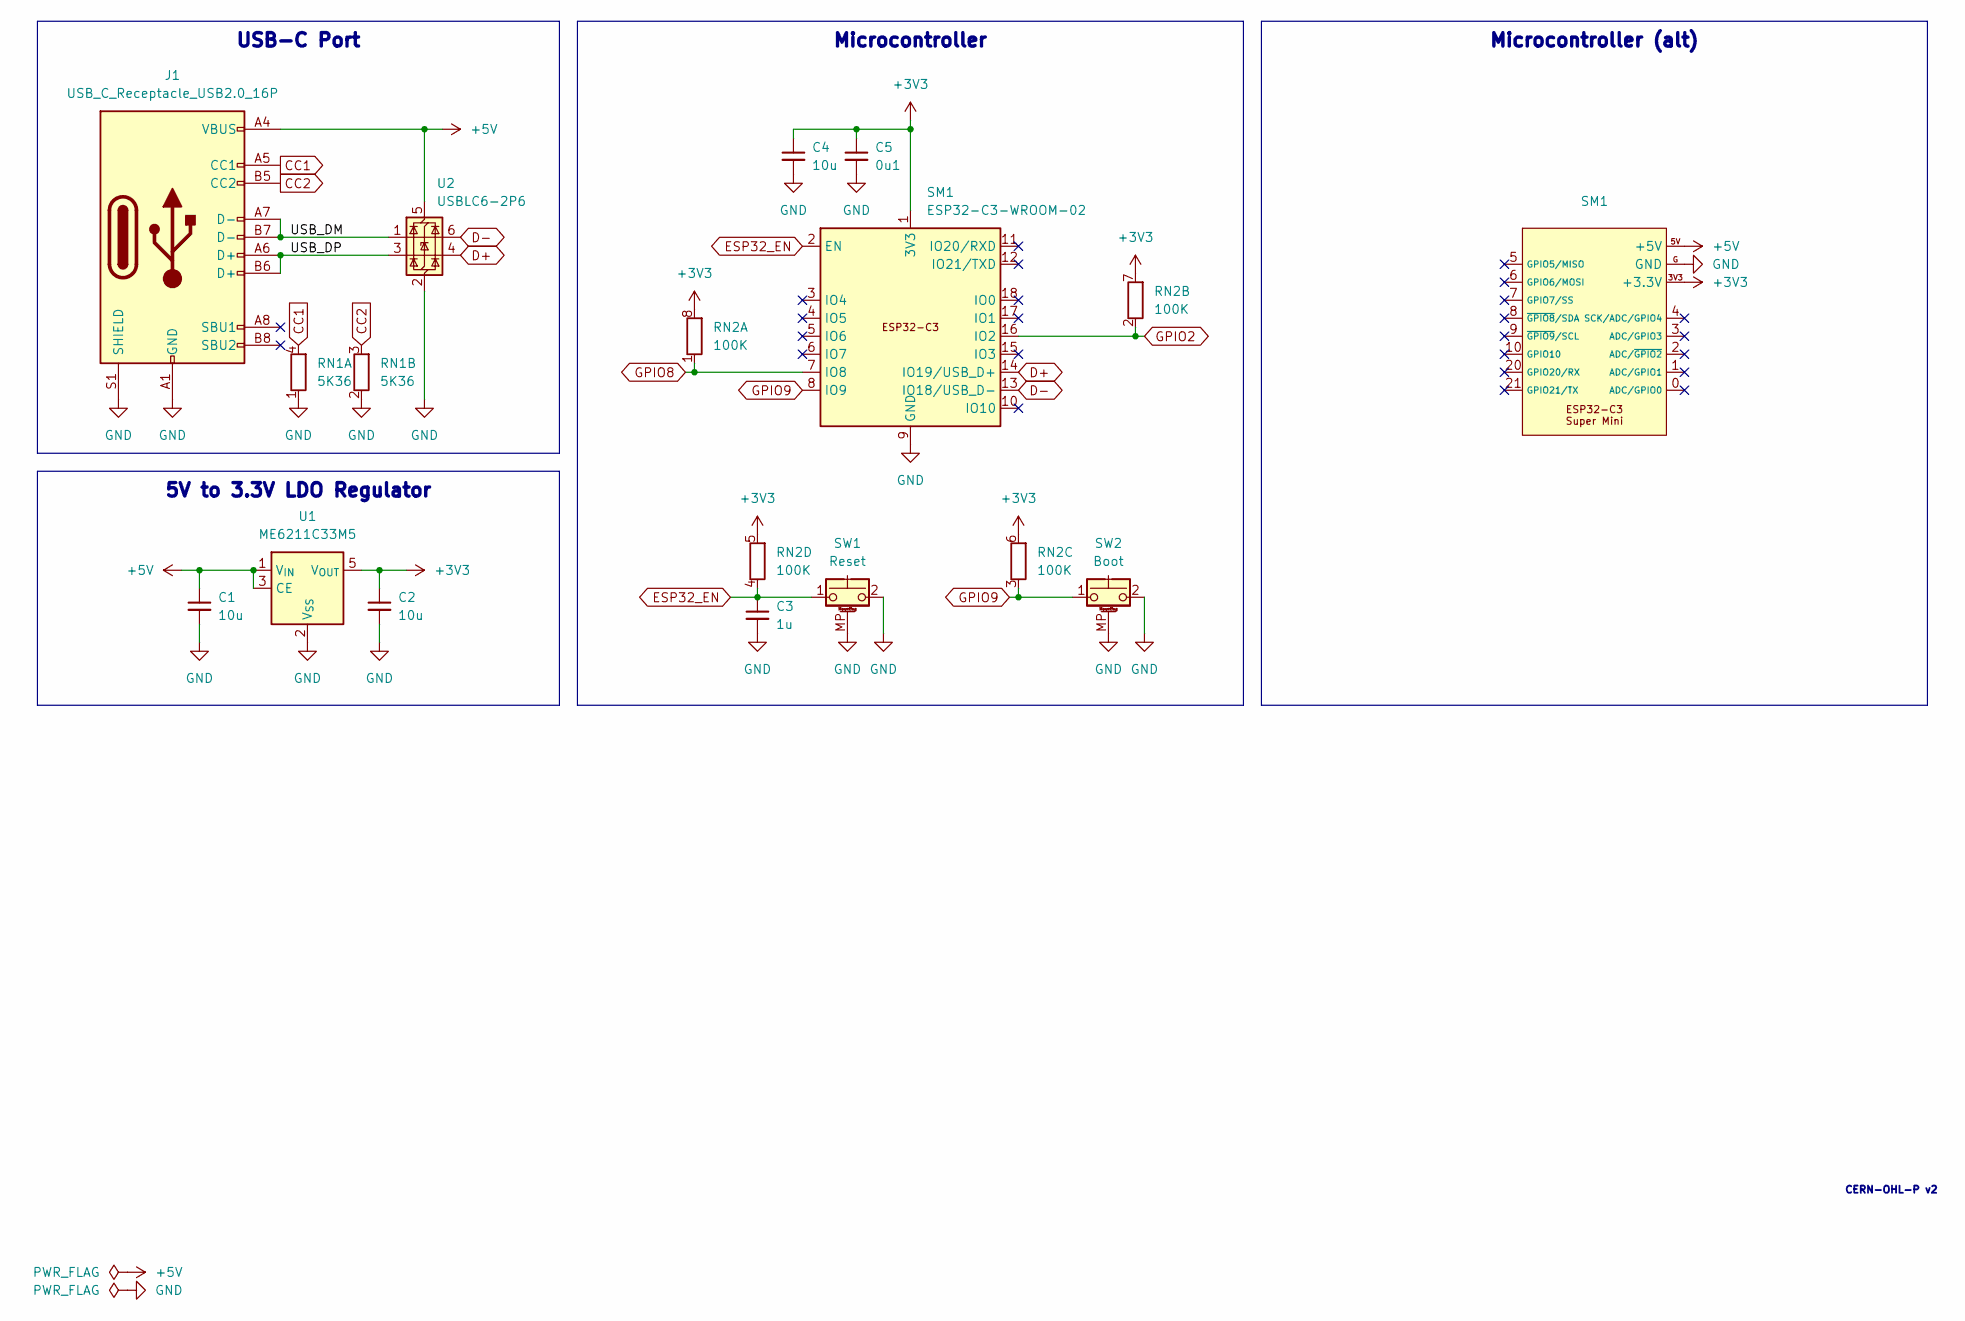
[picture p218: schematic {{ cookiecutter.project_name }}.kicad_sch]

Parts:
C1, C2, C4: 10u; C_0402_1005Metric
C3: 1u; C_0402_1005Metric
C5: 0u1; C_0402_1005Metric
J1: USB_C_Receptacle_USB2.0_16P; USB_C_Receptacle_GCT_USB4105-xx-A_16P_TopMnt_Horizontal; LCSC Part C2765186
RN1: 5K36; R_Array_Convex_2x0402
RN2: 100K; R_Array_Convex_4x0402
SM1: ESP32-C3-Super-Mini-Pins
SW1: Reset; SW_Push_1P1T-MP_NO_4.6x3mm_Horizontal
SW2: Boot; SW_Push_1P1T_NO_3.3x3.3mm_MP
U1: ME6211C33M5; SOT-23-5
U2: USBLC6-2P6; SOT-666

Connections:
+3V3: C2.1, C4.1, C5.1, RN2.5 (R4.2), RN2.6 (R3.2), RN2.7 (R2.2), RN2.8 (R1.2), SM1.1 (3V3), SM1.3V3 (+3.3V), U1.5 (V_{OUT})
+5V: C1.1, J1.A4 (VBUS), J1.A9 (VBUS), J1.B4 (VBUS), J1.B9 (VBUS), SM1.5V (+5V), U1.1 (V_{IN}), U1.3 (CE), U2.5 (VBUS)
CC1: J1.A5 (CC1), RN1.4 (R1.2)
CC2: J1.B5 (CC2), RN1.3 (R2.2)
D+: SM1.14 (IO19/USB_D+), U2.4 (I/O2)
D-: SM1.13 (IO18/USB_D-), U2.6 (I/O1)
ESP32_EN: C3.1, RN2.4 (R4.1), SM1.2 (EN), SW1.1
GND: C1.2, C2.2, C3.2, C4.2, C5.2, J1.A1 (GND), J1.A12 (GND), J1.B1 (GND), J1.B12 (GND), J1.S1 (SHIELD), RN1.1 (R1.1), RN1.2 (R2.1), SM1.9 (GND), SM1.19 (GND), SM1.G (GND), SW1.2, SW1.MP (MountPin), SW2.2, SW2.MP (MountPin), U1.2 (V_{SS}), U2.2 (GND)
GPIO2: RN2.2 (R2.1), SM1.16 (IO2)
GPIO8: RN2.1 (R1.1), SM1.7 (IO8)
GPIO9: RN2.3 (R3.1), SM1.8 (IO9), SW2.1
USB_DM: J1.A7 (D-), J1.B7 (D-), U2.1 (I/O1)
USB_DP: J1.A6 (D+), J1.B6 (D+), U2.3 (I/O2)

Notes on the sheet:
5V to 3.3V LDO Regulator
USB-C Port
Microcontroller
Microcontroller (alt)
CERN-OHL-P v2
